herasymyuks/PLFM_RADAR-aeris/9_Firmware/9_2_FPGA/reconstructed/PIN_MAP_FROM_SCHEMATIC.md

# FPGA pin map derived from schematic (XC7A50T-2FTG256I, part U42)

Source: `4_Schematics and Boards Layout/4_6_Schematics/MainBoard/RADAR_Main_Board.sch`. Generated by `tools/gen_xdc_from_schematic.py`. Confidence refers to the net-name-to-RTL-port interpretation only; the pad is exact.

| RTL port | Schematic net | Pad | FPGA pin name | Confidence | Notes |
|---|---|---|---|---|---|
| `clk_100m` | `FPGA_SYS_CLOCK` | `E12` | `IO_L13P_T2_MRCC_15` | MEDIUM | MRCC clock-capable pin; 100 MHz supported by firmware AD9523 OUT6 'FPGA_SYSTEM_CLOCK' /36 (main.cpp:995-996), not by schematic alone; bank 15 VCCO=+3V3_FPGA |
| `clk_120m_dac` | `FPGA_DAC_CLOCK` | `C13` | `IO_L12N_T1_MRCC_15` | MEDIUM | MRCC clock-input pin; 120 MHz supported by firmware AD9523 OUT11 'FPGA_DAC' /30 (main.cpp:1025-1026). RTL output dac_clk has NO board pin (DAC clocked by AD9523 OUT10) — designer to confirm; bank 15 VCCO=+3V3_FPGA |
| `adc_dco_p` | `ADC_DCO_P` | `N14` | `IO_L12P_T1_MRCC_14` | HIGH | bank 14 VCCO=+3V3_FPGA: LVDS_25 input with DIFF_TERM requires 2.5 V VCCO (UG471) — REQUIRES VERIFICATION |
| `adc_dco_n` | `ADC_DCO_N` | `P14` | `IO_L12N_T1_MRCC_14` | HIGH | bank 14 VCCO=+3V3_FPGA: LVDS_25 input with DIFF_TERM requires 2.5 V VCCO (UG471) — REQUIRES VERIFICATION |
| `adc_pwdn` | `ADC_PWRD` | `T5` | `IO_L23N_T3_A02_D18_14` | HIGH | bank 14 VCCO=+3V3_FPGA |
| `dac_sleep` | `DAC_SLEEP` | `A15` | `IO_L9N_T1_DQS_AD3N_15` | HIGH | bank 15 VCCO=+3V3_FPGA |
| `tx_mixer_en` | `MIX_TX_EN` | `C11` | `IO_L11P_T1_SRCC_15` | HIGH | bank 15 VCCO=+3V3_FPGA |
| `rx_mixer_en` | `MIX_RX_EN` | `D11` | `IO_L14N_T2_SRCC_15` | HIGH | bank 15 VCCO=+3V3_FPGA |
| `fpga_rf_switch` | `M3S_VCTRL` | `G15` | `IO_L24N_T3_RS0_15` | MEDIUM | M3SWA2-34DR+ RF switch control net; bank 15 VCCO=+3V3_FPGA |
| `stm32_new_chirp` | `DIG_0` | `F13` | `IO_L16N_T2_A27_15` | MEDIUM | STM32 PD8 toggled as 'New chirp signal to FPGA' (main.cpp:448,459); schematic net DIG_0 = U2.PD8; bank 15 VCCO=+3V3_FPGA |
| `stm32_new_elevation` | `DIG_1` | `E16` | `IO_L17P_T2_A26_15` | MEDIUM | STM32 PD9 toggled 'Notify FPGA of elevation change' (main.cpp:484); DIG_1 = U2.PD9; bank 15 VCCO=+3V3_FPGA |
| `stm32_new_azimuth` | `DIG_2` | `D16` | `IO_L17N_T2_A25_15` | MEDIUM | STM32 PD10 toggled 'new azimuth' (main.cpp:514); DIG_2 = U2.PD10; bank 15 VCCO=+3V3_FPGA |
| `stm32_mixers_enable` | `DIG_3` | `F15` | `IO_L18P_T2_A24_15` | MEDIUM | STM32 PD11 'enable Mixers' (main.cpp:1483,1667,1714); DIG_3 = U2.PD11; bank 15 VCCO=+3V3_FPGA |
| `reset_n` | `DIG_4` | `E15` | `IO_L18N_T2_A23_15` | MEDIUM | STM32 PD12 pulsed low 10 ms as 'RESET FPGA' (main.cpp:1659-1662), active-low matches RTL reset_n; DIG_4 = U2.PD12; bank 15 VCCO=+3V3_FPGA |
| `stm32_sclk_3v3` | `STM32_SCLK1` | `J16` | `IO_L23N_T3_FWE_B_15` | HIGH | shared with STM32 PA5 (SPI1_SCK); bank 15 VCCO=+3V3_FPGA |
| `stm32_mosi_3v3` | `STM32_MOSI1` | `H13` | `IO_L20N_T3_A19_15` | HIGH | shared with STM32 PA7 (SPI1_MOSI); bank 15 VCCO=+3V3_FPGA |
| `stm32_miso_3v3` | `STM32_MISO1` | `G14` | `IO_L21P_T3_DQS_15` | HIGH | shared with STM32 PA6 (SPI1_MISO); bank 15 VCCO=+3V3_FPGA |
| `stm32_sclk_1v8` | `STM32_SCLK_1V8` | `P5` | `IO_L10P_T1_34` | HIGH | bank 34 VCCO=+1V8_FPGA |
| `stm32_mosi_1v8` | `STM32_MOSI_1V8` | `M1` | `IO_L2N_T0_34` | HIGH | bank 34 VCCO=+1V8_FPGA |
| `stm32_miso_1v8` | `STM32_MISO_1V8` | `N3` | `IO_L3P_T0_DQS_34` | HIGH | bank 34 VCCO=+1V8_FPGA |
| `adc_d_p[0]` | `ADC_D0_P` | `P15` | `IO_L8P_T1_D11_14` | HIGH | bank 14 VCCO=+3V3_FPGA: LVDS_25 input with DIFF_TERM requires 2.5 V VCCO (UG471) — REQUIRES VERIFICATION |
| `adc_d_p[1]` | `ADC_D1_P` | `R15` | `IO_L9P_T1_DQS_14` | HIGH | bank 14 VCCO=+3V3_FPGA: LVDS_25 input with DIFF_TERM requires 2.5 V VCCO (UG471) — REQUIRES VERIFICATION |
| `adc_d_p[2]` | `ADC_D2_P` | `T14` | `IO_L10P_T1_D14_14` | HIGH | bank 14 VCCO=+3V3_FPGA: LVDS_25 input with DIFF_TERM requires 2.5 V VCCO (UG471) — REQUIRES VERIFICATION |
| `adc_d_p[3]` | `ADC_D3_P` | `R13` | `IO_L16P_T2_CSI_B_14` | HIGH | bank 14 VCCO=+3V3_FPGA: LVDS_25 input with DIFF_TERM requires 2.5 V VCCO (UG471) — REQUIRES VERIFICATION |
| `adc_d_p[4]` | `ADC_D4_P` | `R10` | `IO_L17P_T2_A14_D30_14` | HIGH | bank 14 VCCO=+3V3_FPGA: LVDS_25 input with DIFF_TERM requires 2.5 V VCCO (UG471) — REQUIRES VERIFICATION |
| `adc_d_p[5]` | `ADC_D5_P` | `T9` | `IO_L22P_T3_A05_D21_14` | HIGH | bank 14 VCCO=+3V3_FPGA: LVDS_25 input with DIFF_TERM requires 2.5 V VCCO (UG471) — REQUIRES VERIFICATION |
| `adc_d_p[6]` | `ADC_D6_P` | `T7` | `IO_L21P_T3_DQS_14` | HIGH | bank 14 VCCO=+3V3_FPGA: LVDS_25 input with DIFF_TERM requires 2.5 V VCCO (UG471) — REQUIRES VERIFICATION |
| `adc_d_p[7]` | `ADC_D7_P` | `R6` | `IO_L24P_T3_A01_D17_14` | HIGH | bank 14 VCCO=+3V3_FPGA: LVDS_25 input with DIFF_TERM requires 2.5 V VCCO (UG471) — REQUIRES VERIFICATION |
| `adc_d_n[0]` | `ADC_D0_N` | `P16` | `IO_L8N_T1_D12_14` | HIGH | bank 14 VCCO=+3V3_FPGA: LVDS_25 input with DIFF_TERM requires 2.5 V VCCO (UG471) — REQUIRES VERIFICATION |
| `adc_d_n[1]` | `ADC_D1_N` | `R16` | `IO_L9N_T1_DQS_D13_14` | HIGH | bank 14 VCCO=+3V3_FPGA: LVDS_25 input with DIFF_TERM requires 2.5 V VCCO (UG471) — REQUIRES VERIFICATION |
| `adc_d_n[2]` | `ADC_D2_N` | `T15` | `IO_L10N_T1_D15_14` | HIGH | bank 14 VCCO=+3V3_FPGA: LVDS_25 input with DIFF_TERM requires 2.5 V VCCO (UG471) — REQUIRES VERIFICATION |
| `adc_d_n[3]` | `ADC_D3_N` | `T13` | `IO_L16N_T2_A15_D31_14` | HIGH | bank 14 VCCO=+3V3_FPGA: LVDS_25 input with DIFF_TERM requires 2.5 V VCCO (UG471) — REQUIRES VERIFICATION |
| `adc_d_n[4]` | `ADC_D4_N` | `R11` | `IO_L17N_T2_A13_D29_14` | HIGH | bank 14 VCCO=+3V3_FPGA: LVDS_25 input with DIFF_TERM requires 2.5 V VCCO (UG471) — REQUIRES VERIFICATION |
| `adc_d_n[5]` | `ADC_D5_N` | `T10` | `IO_L22N_T3_A04_D20_14` | HIGH | bank 14 VCCO=+3V3_FPGA: LVDS_25 input with DIFF_TERM requires 2.5 V VCCO (UG471) — REQUIRES VERIFICATION |
| `adc_d_n[6]` | `ADC_D6_N` | `T8` | `IO_L21N_T3_DQS_A06_D22_14` | HIGH | bank 14 VCCO=+3V3_FPGA: LVDS_25 input with DIFF_TERM requires 2.5 V VCCO (UG471) — REQUIRES VERIFICATION |
| `adc_d_n[7]` | `ADC_D7_N` | `R7` | `IO_L24N_T3_A00_D16_14` | HIGH | bank 14 VCCO=+3V3_FPGA: LVDS_25 input with DIFF_TERM requires 2.5 V VCCO (UG471) — REQUIRES VERIFICATION |
| `dac_data[0]` | `DAC_0` | `A14` | `IO_L7N_T1_AD2N_15` | HIGH | bank 15 VCCO=+3V3_FPGA |
| `dac_data[1]` | `DAC_1` | `A13` | `IO_L7P_T1_AD2P_15` | HIGH | bank 15 VCCO=+3V3_FPGA |
| `dac_data[2]` | `DAC_2` | `A12` | `IO_L5N_T0_AD9N_15` | HIGH | bank 15 VCCO=+3V3_FPGA |
| `dac_data[3]` | `DAC_3` | `B11` | `IO_L4N_T0_15` | HIGH | bank 15 VCCO=+3V3_FPGA |
| `dac_data[4]` | `DAC_4` | `B10` | `IO_L4P_T0_15` | HIGH | bank 15 VCCO=+3V3_FPGA |
| `dac_data[5]` | `DAC_5` | `A10` | `IO_L3N_T0_DQS_AD1N_15` | HIGH | bank 15 VCCO=+3V3_FPGA |
| `dac_data[6]` | `DAC_6` | `A9` | `IO_L2N_T0_AD8N_15` | HIGH | bank 15 VCCO=+3V3_FPGA |
| `dac_data[7]` | `DAC_7` | `A8` | `IO_L2P_T0_AD8P_15` | HIGH | bank 15 VCCO=+3V3_FPGA |
| `stm32_cs_adar1_3v3` | `ADAR_1_CS_3V3` | `F14` | `IO_L21N_T3_DQS_A18_15` | HIGH | shared with STM32 PA0; bank 15 VCCO=+3V3_FPGA |
| `stm32_cs_adar2_3v3` | `ADAR_2_CS_3V3` | `H16` | `IO_L22P_T3_A17_15` | HIGH | shared with STM32 PA1; bank 15 VCCO=+3V3_FPGA |
| `stm32_cs_adar3_3v3` | `ADAR_3_CS_3V3` | `G16` | `IO_L22N_T3_A16_15` | HIGH | shared with STM32 PA2; bank 15 VCCO=+3V3_FPGA |
| `stm32_cs_adar4_3v3` | `ADAR_4_CS_3V3` | `J15` | `IO_L23P_T3_FOE_B_15` | HIGH | shared with STM32 PA3; bank 15 VCCO=+3V3_FPGA |
| `stm32_cs_adar1_1v8` | `ADAR_1_CS_1V8` | `L5` | `IO_0_34` | HIGH | bank 34 VCCO=+1V8_FPGA |
| `stm32_cs_adar2_1v8` | `ADAR_2_CS_1V8` | `L4` | `IO_L1P_T0_34` | HIGH | bank 34 VCCO=+1V8_FPGA |
| `stm32_cs_adar3_1v8` | `ADAR_3_CS_1V8` | `M4` | `IO_L1N_T0_34` | HIGH | bank 34 VCCO=+1V8_FPGA |
| `stm32_cs_adar4_1v8` | `ADAR_4_CS_1V8` | `M2` | `IO_L2P_T0_34` | HIGH | bank 34 VCCO=+1V8_FPGA |
| `adar_tx_load_1` | `ADAR_TX_LOAD_1` | `P3` | `IO_L5N_T0_34` | HIGH | bank 34 VCCO=+1V8_FPGA |
| `adar_tx_load_2` | `ADAR_TX_LOAD_2` | `T4` | `IO_L9P_T1_DQS_34` | HIGH | bank 34 VCCO=+1V8_FPGA |
| `adar_tx_load_3` | `ADAR_TX_LOAD_3` | `R3` | `IO_L8P_T1_34` | HIGH | bank 34 VCCO=+1V8_FPGA |
| `adar_tx_load_4` | `ADAR_TX_LOAD_4` | `R2` | `IO_L7P_T1_34` | HIGH | bank 34 VCCO=+1V8_FPGA |
| `adar_rx_load_1` | `ADAR_RX_LOAD_1` | `M5` | `IO_L6P_T0_34` | HIGH | bank 34 VCCO=+1V8_FPGA |
| `adar_rx_load_2` | `ADAR_RX_LOAD_2` | `T2` | `IO_L8N_T1_34` | HIGH | bank 34 VCCO=+1V8_FPGA |
| `adar_rx_load_3` | `ADAR_RX_LOAD_3` | `R1` | `IO_L7N_T1_34` | HIGH | bank 34 VCCO=+1V8_FPGA |
| `adar_rx_load_4` | `ADAR_RX_LOAD_4` | `N4` | `IO_L6N_T0_VREF_34` | HIGH | bank 34 VCCO=+1V8_FPGA |
| `adar_tr_1` | `ADAR_TR_1` | `N2` | `IO_L3N_T0_DQS_34` | HIGH | bank 34 VCCO=+1V8_FPGA |
| `adar_tr_2` | `ADAR_TR_2` | `N1` | `IO_L4P_T0_34` | HIGH | bank 34 VCCO=+1V8_FPGA |
| `adar_tr_3` | `ADAR_TR_3` | `P1` | `IO_L4N_T0_34` | HIGH | bank 34 VCCO=+1V8_FPGA |
| `adar_tr_4` | `ADAR_TR_4` | `P4` | `IO_L5P_T0_34` | HIGH | bank 34 VCCO=+1V8_FPGA |

## Unresolved RTL ports

| Ports | Reason |
|---|---|
| `dac_clk` | RTL drives a DAC clock output, but the board clocks the AD9708 from AD9523 OUT10 (main.cpp:1019-1020); no FPGA net — **UNRESOLVED — REQUIRES BOARD DESIGN VERIFICATION** |
| `ft601_clk_in` | FT601Q-B-T (U6) is placed in the schematic but has 0 of 77 pins connected; its decoupling parts are parked outside the board outline — **UNRESOLVED — REQUIRES BOARD DESIGN VERIFICATION** |
| `ft601_data[*], ft601_be[*], ft601_txe_n, ft601_rxf_n, ft601_txe, ft601_rxf, ft601_wr_n, ft601_rd_n, ft601_oe_n, ft601_siwu_n, ft601_srb[*], ft601_swb[*], ft601_clk_out` | FT601 not wired on Main Board — **UNRESOLVED — REQUIRES BOARD DESIGN VERIFICATION** |
| `(DIG_5..DIG_7)` | schematic nets DIG_5/6/7 (STM32 PD13/14/15 configured as INPUTS in main.cpp:2313-2317) reach FPGA H11/G12/H12 but no RTL port uses them — **UNRESOLVED — REQUIRES BOARD DESIGN VERIFICATION** |
| `current_elevation[*], current_azimuth[*], current_chirp[*], new_chirp_frame` | no status outputs on the schematic — **UNRESOLVED — REQUIRES BOARD DESIGN VERIFICATION** |
| `dbg_doppler_data[*], dbg_doppler_valid, dbg_doppler_bin[*], dbg_range_bin[*], system_status[*]` | debug outputs; no schematic nets (internal-only in a real build; remove from top or leave unconstrained with -quiet) — **UNRESOLVED — REQUIRES BOARD DESIGN VERIFICATION** |
