herasymyuks/PLFM_RADAR-aeris/engineering/ELECTRICAL/connection_diagrams/FREQUENCY_SYNTHESIZER_connection_report.md

# FREQUENCY_SYNTHESIZER — Component-to-net connection report

Project AERIS-10 · Drawing ID ELEC-CON-FREQUENCY_SYNTHESIZER · Rev A · 2026-10-09 · Status: SOURCE-DERIVED  
Source: `4_Schematics and Boards Layout/4_6_Schematics/FrequencySynthesizerBoard/Clocks_Freq_Synth_board.sch` (EAGLE 9.6.2), `4_Schematics and Boards Layout/4_6_Schematics/FrequencySynthesizerBoard/Clocks_Freq_Synth_board.brd`; generated by `tools/gen_schematic_reports.py`.

## 1. Summary

| Item | Count |
|---|---|
| Sheets | 1 |
| Parts (all) / physical | 318 / 184 |
| Nets | 139 |
| Pin connections | 752 |
| Single-pin nets | 5 |
| Unconnected pins on placed gates | 34 |
| Physical parts without value | 47 |
| Board airwires (unrouted connections, layer 19) | 0 |
| Missing symbol/footprint records | 0 |

## 2. Connector pin-outs

Parts whose package name or prefix identifies a connector (header, SMA, terminal block, USB).

### J1 — 142-0731-211 (1420731211)

| Pad | Pin name | Net | Sheet |
|---|---|---|---|
| 1 | 1 | `N$35` | 1 |
| 2 | 2 | `GND` | 1 |
| 3 | 3 | `GND` | 1 |
| 4 | 4 | `GND` | 1 |
| 5 | 5 | `GND` | 1 |

### J2 — 142-0731-211 (1420731211)

| Pad | Pin name | Net | Sheet |
|---|---|---|---|
| 1 | 1 | `N$51` | 1 |
| 2 | 2 | `GND` | 1 |
| 3 | 3 | `GND` | 1 |
| 4 | 4 | `GND` | 1 |
| 5 | 5 | `GND` | 1 |

### J3 — CJT-T-P-HH-ST-TH1 (CONN_CJT-T-P-XX-ST-TH1_SAI)

| Pad | Pin name | Net | Sheet |
|---|---|---|---|
| 1 | 1 | `AD9523_OUT4_P` | 1 |
| 2 | 2 | `AD9523_OUT4_N` | 1 |

### J4 — CJT-T-P-HH-ST-TH1 (CONN_CJT-T-P-XX-ST-TH1_SAI)

| Pad | Pin name | Net | Sheet |
|---|---|---|---|
| 1 | 1 | `AD9523_OUT5_P` | 1 |
| 2 | 2 | `AD9523_OUT5_N` | 1 |

### J5 — 142-0731-211 (1420731211)

| Pad | Pin name | Net | Sheet |
|---|---|---|---|
| 1 | 1 | `N$64` | 1 |
| 2 | 2 | `GND` | 1 |
| 3 | 3 | `GND` | 1 |
| 4 | 4 | `GND` | 1 |
| 5 | 5 | `GND` | 1 |

### J6 — 142-0731-211 (1420731211)

| Pad | Pin name | Net | Sheet |
|---|---|---|---|
| 1 | 1 | `N$67` | 1 |
| 2 | 2 | `GND` | 1 |
| 3 | 3 | `GND` | 1 |
| 4 | 4 | `GND` | 1 |
| 5 | 5 | `GND` | 1 |

### J7 — 142-0731-211 (1420731211)

| Pad | Pin name | Net | Sheet |
|---|---|---|---|
| 1 | 1 | `AD9523_OUT6+` | 1 |
| 2 | 2 | `GND` | 1 |
| 3 | 3 | `GND` | 1 |
| 4 | 4 | `GND` | 1 |
| 5 | 5 | `GND` | 1 |

### J8 — 142-0731-211 (1420731211)

| Pad | Pin name | Net | Sheet |
|---|---|---|---|
| 1 | 1 | `AD9523_OUT7+` | 1 |
| 2 | 2 | `GND` | 1 |
| 3 | 3 | `GND` | 1 |
| 4 | 4 | `GND` | 1 |
| 5 | 5 | `GND` | 1 |

### J9 — 142-0731-211 (1420731211)

| Pad | Pin name | Net | Sheet |
|---|---|---|---|
| 1 | 1 | `N$37` | 1 |
| 2 | 2 | `GND` | 1 |
| 3 | 3 | `GND` | 1 |
| 4 | 4 | `GND` | 1 |
| 5 | 5 | `GND` | 1 |

### J10 — 142-0731-211 (1420731211)

| Pad | Pin name | Net | Sheet |
|---|---|---|---|
| 1 | 1 | `N$30` | 1 |
| 2 | 2 | `GND` | 1 |
| 3 | 3 | `GND` | 1 |
| 4 | 4 | `GND` | 1 |
| 5 | 5 | `GND` | 1 |

### J11 — 142-0731-211 (1420731211)

| Pad | Pin name | Net | Sheet |
|---|---|---|---|
| 1 | 1 | `N$55` | 1 |
| 2 | 2 | `GND` | 1 |
| 3 | 3 | `GND` | 1 |
| 4 | 4 | `GND` | 1 |
| 5 | 5 | `GND` | 1 |

### J12 — 142-0731-211 (1420731211)

| Pad | Pin name | Net | Sheet |
|---|---|---|---|
| 1 | 1 | `N$59` | 1 |
| 2 | 2 | `GND` | 1 |
| 3 | 3 | `GND` | 1 |
| 4 | 4 | `GND` | 1 |
| 5 | 5 | `GND` | 1 |

### J13 — 142-0731-211 (1420731211)

| Pad | Pin name | Net | Sheet |
|---|---|---|---|
| 1 | 1 | `N$61` | 1 |
| 2 | 2 | `GND` | 1 |
| 3 | 3 | `GND` | 1 |
| 4 | 4 | `GND` | 1 |
| 5 | 5 | `GND` | 1 |

### JP1 — PINHD-2X6 (2X06)

| Pad | Pin name | Net | Sheet |
|---|---|---|---|
| 1 | 1 | `AD9523_PD` | 1 |
| 2 | 2 | `AD9523_REF_SEL` | 1 |
| 3 | 3 | `AD9523_SYNC` | 1 |
| 4 | 4 | `AD9523_RESET` | 1 |
| 5 | 5 | `AD9523_CS` | 1 |
| 6 | 6 | `AD9523_SCLK` | 1 |
| 7 | 7 | `AD9523_SDIO` | 1 |
| 8 | 8 | `AD9523_SDO` | 1 |
| 9 | 9 | `AD9523_STATUS0` | 1 |
| 10 | 10 | `AD9523_STATUS1` | 1 |
| 11 | 11 | `AD9523_EEPROM_SEL` | 1 |
| 12 | 12 | `GND` | 1 |

### JP2 — PINHD-2X7 (2X07)

| Pad | Pin name | Net | Sheet |
|---|---|---|---|
| 1 | 1 | `ADF4382_SDO` | 1 |
| 2 | 2 | `ADF4382_SCLK` | 1 |
| 3 | 3 | `ADF4382_SDIO` | 1 |
| 4 | 4 | `ADF4382_TX_CS` | 1 |
| 5 | 5 | `ADF4382_TX_CE` | 1 |
| 6 | 6 | `ADF4382_TX_DELSTR` | 1 |
| 7 | 7 | `ADF4382_TX_DELADJ` | 1 |
| 8 | 8 | `ADF4382_TX_LKDET` | 1 |
| 9 | 9 | `ADF4382_RX_CS` | 1 |
| 10 | 10 | `ADF4382_RX_CE` | 1 |
| 11 | 11 | `ADF4382_RX_DELSTR` | 1 |
| 12 | 12 | `ADF4382_RX_DELADJ` | 1 |
| 13 | 13 | `ADF4382_RX_LKDET` | 1 |
| 14 | 14 | `GND` | 1 |

### X4 — ECOC-2522-100.000-3HC (SMD5_ECOC-2522_25P4X22_ECS)

| Pad | Pin name | Net | Sheet |
|---|---|---|---|
| 1 | VOLTAGE_CONTROL | `N$1` | 1 |
| 3 | SUPPLY_VOLTAGE | `+3V3_XO` | 1 |
| 4 | OUTPUT | `10MHZ_OUT` | 1 |
| 5 | GROUND | `GND` | 1 |

### X5 — CVHD-950-50.000 (SMD4_CVHD-950_CRX)

| Pad | Pin name | Net | Sheet |
|---|---|---|---|
| 2 | GND | `GND` | 1 |
| 3 | OUT | `100MHZ_OUT` | 1 |
| 4 | VDD | `+3V3_XO` | 1 |

### X6 — CVHD-950-50.000 (SMD4_CVHD-950_CRX)

| Pad | Pin name | Net | Sheet |
|---|---|---|---|
| 1 | VOLT_CONTROL | `N$2` | 1 |
| 2 | GND | `GND` | 1 |
| 3 | OUT | `VCXO_OUT` | 1 |
| 4 | VDD | `+3V3_XO` | 1 |

### X10 — 22-23-2021 (22-23-2021)

| Pad | Pin name | Net | Sheet |
|---|---|---|---|
| 1 | S | `N$69` | 1 |
| 2 | S | `GND` | 1 |

### X11 — 22-23-2021 (22-23-2021)

| Pad | Pin name | Net | Sheet |
|---|---|---|---|
| 1 | S | `N$71` | 1 |
| 2 | S | `GND` | 1 |

### X12 — 22-23-2021 (22-23-2021)

| Pad | Pin name | Net | Sheet |
|---|---|---|---|
| 1 | S | `N$73` | 1 |
| 2 | S | `GND` | 1 |

### X13 — 22-23-2021 (22-23-2021)

| Pad | Pin name | Net | Sheet |
|---|---|---|---|
| 1 | S | `N$75` | 1 |
| 2 | S | `GND` | 1 |

### X14 — 22-23-2021 (22-23-2021)

| Pad | Pin name | Net | Sheet |
|---|---|---|---|
| 1 | S | `N$77` | 1 |
| 2 | S | `GND` | 1 |

### X15 — 22-23-2021 (22-23-2021)

| Pad | Pin name | Net | Sheet |
|---|---|---|---|
| 1 | S | `+5V0_LO` | 1 |
| 2 | S | `GND` | 1 |

## 3. Net fan-out (nets with ≥ 8 connections)

| Net | Connections | Class |
|---|---|---|
| `GND` | 333 | 0 |
| `+3V3_LO_1` | 30 | 0 |
| `+3V3_LO_2` | 30 | 0 |
| `+3V3_CLOCK` | 22 | 0 |
| `+1V8_CLOCK` | 16 | 0 |

## 4. Component-to-net table

Full machine-readable form: `netlists/FREQUENCY_SYNTHESIZER_netlist_by_part.csv`. Physical parts only; pads shown when the device defines a package connection.

| Part | Value | Device / package | Connections (pad:net) |
|---|---|---|---|
| C1 | 10pF | C-EUC0201 / C0201 | 1:`+3V3_LO_2`, 2:`GND` |
| C2 | 0.33µF | C-EUC0201 / C0201 | 1:`N$2`, 2:`GND` |
| C3 | 0.47µf | C-EUC0201 / C0201 | 1:`GND`, 2:`N$3` |
| C4 |  | C-EUC0201 / C0201 | 1:`GND`, 2:`N$5` |
| C5 |  | C-EUC0201 / C0201 | 1:`GND`, 2:`N$6` |
| C6 | 0.33µF | C-EUC0201 / C0201 | 1:`GND`, 2:`N$4` |
| C7 |  | C-EUC0201 / C0201 | 1:`GND`, 2:`N$7` |
| C8 | 1000pF | C-EUC0201 / C0201 | 1:`N$9`, 2:`N$8` |
| C9 | 0.47µF | C-EUC0201 / C0201 | 1:`GND`, 2:`N$10` |
| C10 | 0.47µF | C-EUC0201 / C0201 | 1:`GND`, 2:`N$11` |
| C11 | 1µF | C-EUC0201 / C0201 | 1:`N$15`, 2:`AD9523_OUT0_N` |
| C12 | 1µF | C-EUC0201 / C0201 | 1:`N$16`, 2:`AD9523_OUT0_P` |
| C13 | 1µF | C-EUC0201 / C0201 | 1:`ADF4382_TX_SYNC_N`, 2:`AD9523_OUT9_N` |
| C14 | 1µF | C-EUC0201 / C0201 | 1:`ADF4382_TX_SYNC_P`, 2:`AD9523_OUT9_P` |
| C15 | 10nF | C-EUC0402 / C0402 | 1:`N$63`, 2:`AD9523_OUT6+` |
| C16 | 0.1µF | C-EUC0201 / C0201 | 1:`+3V3_CLOCK`, 2:`GND` |
| C17 | 10nF | C-EUC0402 / C0402 | 1:`N$65`, 2:`N$64` |
| C18 | 0.1µF | C-EUC0201 / C0201 | 1:`+3V3_CLOCK`, 2:`GND` |
| C19 | 10nF | C-EUC0402 / C0402 | 1:`N$68`, 2:`N$67` |
| C20 | 0.1µF | C-EUC0201 / C0201 | 1:`+3V3_CLOCK`, 2:`GND` |
| C21 | 22µF | C-EUC1210 / C1210 | 1:`N$69`, 2:`GND` |
| C22 | 0.1µF | C-EUC0201 / C0201 | 1:`+3V3_CLOCK`, 2:`GND` |
| C23 | 10µF | C-EUC1210 / C1210 | 1:`+3V3_XO`, 2:`GND` |
| C24 | 0.1µF | C-EUC0201 / C0201 | 1:`+3V3_CLOCK`, 2:`GND` |
| C25 | 22µF | C-EUC1210 / C1210 | 1:`N$71`, 2:`GND` |
| C26 | 0.1µF | C-EUC0201 / C0201 | 1:`+3V3_CLOCK`, 2:`GND` |
| C27 | 10µF | C-EUC1210 / C1210 | 1:`+3V3_CLOCK`, 2:`GND` |
| C28 | 0.1µF | C-EUC0201 / C0201 | 1:`+3V3_CLOCK`, 2:`GND` |
| C29 | 22µF | C-EUC1210 / C1210 | 1:`N$73`, 2:`GND` |
| C30 | 0.1µF | C-EUC0201 / C0201 | 1:`+3V3_CLOCK`, 2:`GND` |
| C31 | 10µF | C-EUC1210 / C1210 | 1:`+1V8_CLOCK`, 2:`GND` |
| C32 | 0.1µF | C-EUC0201 / C0201 | 1:`+3V3_CLOCK`, 2:`GND` |
| C33 | 22µF | C-EUC1210 / C1210 | 1:`N$75`, 2:`GND` |
| C34 | 0.1µF | C-EUC0201 / C0201 | 1:`+3V3_CLOCK`, 2:`GND` |
| C35 | 0.1µF | C-EUC0201 / C0201 | 1:`+1V8_CLOCK`, 2:`GND` |
| C36 | 0.1µF | C-EUC0201 / C0201 | 1:`+1V8_CLOCK`, 2:`GND` |
| C37 | 0.1µF | C-EUC0201 / C0201 | 1:`+1V8_CLOCK`, 2:`GND` |
| C38 | 4.7µF | C-EUC0201 / C0201 | 1:`+3V3_LO_1`, 2:`GND` |
| C39 | 4.7µF | C-EUC0201 / C0201 | 1:`+3V3_LO_1`, 2:`GND` |
| C40 | 4.7µF | C-EUC0201 / C0201 | 1:`+3V3_LO_1`, 2:`GND` |
| C41 | 0.1µF | C-EUC0201 / C0201 | 1:`+1V8_CLOCK`, 2:`GND` |
| C42 | 0.1µF | C-EUC0201 / C0201 | 1:`+1V8_CLOCK`, 2:`GND` |
| C43 | 0.1µF | C-EUC0201 / C0201 | 1:`+1V8_CLOCK`, 2:`GND` |
| C44 | 0.1µF | C-EUC0201 / C0201 | 1:`+1V8_CLOCK`, 2:`GND` |
| C45 | 10µF | C-EUC1210 / C1210 | 1:`+3V3_LO_1`, 2:`GND` |
| C46 | 22µF | C-EUC1210 / C1210 | 1:`N$77`, 2:`GND` |
| C47 | 10µF | C-EUC1210 / C1210 | 1:`+3V3_LO_2`, 2:`GND` |
| C48 | 4.7µF | C-EUC0201 / C0201 | 1:`+3V3_LO_1`, 2:`GND` |
| C49 | 4.7µF | C-EUC0201 / C0201 | 1:`+3V3_LO_1`, 2:`GND` |
| C50 | 4.7µF | C-EUC0201 / C0201 | 1:`+3V3_LO_1`, 2:`GND` |
| C51 | 22µF | C-EUC1210 / C1210 | 1:`+5V0_LO`, 2:`GND` |
| C55 | 4.7µF | C-EUC0201 / C0201 | 1:`+3V3_LO_2`, 2:`GND` |
| C56 | 4.7µF | C-EUC0201 / C0201 | 1:`+3V3_LO_2`, 2:`GND` |
| C57 | 4.7µF | C-EUC0201 / C0201 | 1:`+3V3_LO_2`, 2:`GND` |
| C58 | 4.7µF | C-EUC0201 / C0201 | 1:`+3V3_LO_2`, 2:`GND` |
| C59 | 1µF | C-EUC0201 / C0201 | 1:`GND`, 2:`N$20` |
| C60 | 31pF | C-EUC0201 / C0201 | 1:`N$24`, 2:`GND` |
| C61 | 10nF | C-EUC0201 / C0201 | 1:`N$17`, 2:`GND` |
| C62 | 10pF | C-EUC0201 / C0201 | 1:`N$26`, 2:`GND` |
| C63 | 10pF | C-EUC0201 / C0201 | 1:`+3V3_LO_2`, 2:`GND` |
| C64 | 0.1µF | C-EUC0201 / C0201 | 1:`TX_RFOUT_1_N`, 2:`N$31` |
| C65 | 0.1µF | C-EUC0201 / C0201 | 1:`TX_RFOUT_1_P`, 2:`N$28` |
| C66 | 0.1µF | C-EUC0201 / C0201 | 1:`TX_RFOUT_2_N`, 2:`N$33` |
| C67 | 0.1µF | C-EUC0201 / C0201 | 1:`TX_RFOUT_2_P`, 2:`N$32` |
| C68 | 1µF | C-EUC0201 / C0201 | 1:`N$38`, 2:`AD9523_OUT1_N` |
| C69 | 1µF | C-EUC0201 / C0201 | 1:`N$39`, 2:`AD9523_OUT1_P` |
| C70 | 1µF | C-EUC0201 / C0201 | 1:`ADF4382_RX_SYNC_N`, 2:`AD9523_OUT8_N` |
| C71 | 1µF | C-EUC0201 / C0201 | 1:`ADF4382_RX_SYNC_P`, 2:`AD9523_OUT8_P` |
| C72 | 4.7µF | C-EUC0201 / C0201 | 1:`+3V3_LO_1`, 2:`GND` |
| C73 | 4.7µF | C-EUC0201 / C0201 | 1:`+3V3_LO_2`, 2:`GND` |
| C74 | 4.7µF | C-EUC0201 / C0201 | 1:`+3V3_LO_2`, 2:`GND` |
| C75 | 4.7µF | C-EUC0201 / C0201 | 1:`+3V3_LO_2`, 2:`GND` |
| C76 | 4.7µF | C-EUC0201 / C0201 | 1:`+3V3_LO_2`, 2:`GND` |
| C77 | 4.7µF | C-EUC0201 / C0201 | 1:`+3V3_LO_1`, 2:`GND` |
| C78 | 4.7µF | C-EUC0201 / C0201 | 1:`+3V3_LO_1`, 2:`GND` |
| C79 | 4.7µF | C-EUC0201 / C0201 | 1:`+3V3_LO_1`, 2:`GND` |
| C80 | 4.7µF | C-EUC0201 / C0201 | 1:`+3V3_LO_1`, 2:`GND` |
| C81 | 4.7µF | C-EUC0201 / C0201 | 1:`+3V3_LO_1`, 2:`GND` |
| C82 | 1µF | C-EUC0201 / C0201 | 1:`GND`, 2:`N$42` |
| C83 | 31pF | C-EUC0201 / C0201 | 1:`N$47`, 2:`GND` |
| C84 | 10nF | C-EUC0201 / C0201 | 1:`N$43`, 2:`GND` |
| C85 | 10pF | C-EUC0201 / C0201 | 1:`N$49`, 2:`GND` |
| C86 | 10pF | C-EUC0201 / C0201 | 1:`+3V3_LO_2`, 2:`GND` |
| C87 | 0.1µF | C-EUC0201 / C0201 | 1:`RX_RFOUT_1_N`, 2:`N$53` |
| C88 | 0.1µF | C-EUC0201 / C0201 | 1:`RX_RFOUT_1_P`, 2:`N$52` |
| C89 | 10pF | C-EUC0201 / C0201 | 1:`+3V3_LO_2`, 2:`GND` |
| C90 | 0.1µF | C-EUC0201 / C0201 | 1:`RX_RFOUT_2_N`, 2:`N$57` |
| C91 | 0.1µF | C-EUC0201 / C0201 | 1:`RX_RFOUT_2_P`, 2:`N$56` |
| C92 | 0.1µf | C-EUC0201 / C0201 | 1:`N$60`, 2:`N$61` |
| D1 | Green | LED-GREEN-0603-WE / LED-0603 | A:`N$36`, C:`GND` |
| D2 | Green | LED-GREEN-0603-WE / LED-0603 | A:`N$50`, C:`GND` |
| FB1 |  | FBMH1608HL601-T / BEADC1608X90N | 1:`+5V0_LO`, 2:`N$41` |
| FB2 |  | FBMH1608HL601-T / BEADC1608X90N | 1:`+5V0_LO`, 2:`N$19` |
| FB3 |  | FBMH1608HL601-T / BEADC1608X90N | 1:`N$20`, 2:`+5V0_LO` |
| FB4 |  | FBMH1608HL601-T / BEADC1608X90N | 1:`N$42`, 2:`+5V0_LO` |
| IC1 |  | AD9523BCPZ / QFN50P1000X1000X100-73N | 1:`N$3`, 2:`+3V3_CLOCK`, 3:`10MHZ_OUT`, 4:`N$5`, 5:`100MHZ_OUT`, 6:`N$6`, 7:`N$4`, 8:`OSC_CTRL`, 9:`VCXO_OUT`, 10:`N$7`, 11:`N$8`, 12:`N$11`, 13:`+3V3_CLOCK`, 14:`N$10`, 15:`AD9523_PD`, 16:`AD9523_REF_SEL`, 17:`AD9523_SYNC`, 18:`+3V3_CLOCK`, 19:`AD9523_RESET`, 20:`N$14`, 21:`N$12`, 22:`N$13`, 23:`AD9523_SDO`, 24:`N$29`, 27:`+3V3_CLOCK`, 30:`+1V8_CLOCK`, 32:`AD9523_OUT11+`, 33:`+3V3_CLOCK`, 35:`AD9523_OUT10+`, 36:`+1V8_CLOCK`, 37:`AD9523_OUT9_N`, 38:`AD9523_OUT9_P`, 39:`+3V3_CLOCK`, 40:`AD9523_OUT8_N`, 41:`AD9523_OUT8_P`, 42:`+1V8_CLOCK`, 44:`AD9523_OUT7+`, 45:`+3V3_CLOCK`, 47:`N$62`, 48:`+1V8_ … (63 pins, see CSV) |
| J1 |  | 142-0731-211 / 1420731211 | 1:`N$35`, 2:`GND`, 3:`GND`, 4:`GND`, 5:`GND` |
| J2 |  | 142-0731-211 / 1420731211 | 1:`N$51`, 2:`GND`, 3:`GND`, 4:`GND`, 5:`GND` |
| J3 |  | CJT-T-P-HH-ST-TH1 / CONN_CJT-T-P-XX-ST-TH1_SAI | 1:`AD9523_OUT4_P`, 2:`AD9523_OUT4_N` |
| J4 |  | CJT-T-P-HH-ST-TH1 / CONN_CJT-T-P-XX-ST-TH1_SAI | 1:`AD9523_OUT5_P`, 2:`AD9523_OUT5_N` |
| J5 |  | 142-0731-211 / 1420731211 | 1:`N$64`, 2:`GND`, 3:`GND`, 4:`GND`, 5:`GND` |
| J6 |  | 142-0731-211 / 1420731211 | 1:`N$67`, 2:`GND`, 3:`GND`, 4:`GND`, 5:`GND` |
| J7 |  | 142-0731-211 / 1420731211 | 1:`AD9523_OUT6+`, 2:`GND`, 3:`GND`, 4:`GND`, 5:`GND` |
| J8 |  | 142-0731-211 / 1420731211 | 1:`AD9523_OUT7+`, 2:`GND`, 3:`GND`, 4:`GND`, 5:`GND` |
| J9 |  | 142-0731-211 / 1420731211 | 1:`N$37`, 2:`GND`, 3:`GND`, 4:`GND`, 5:`GND` |
| J10 |  | 142-0731-211 / 1420731211 | 1:`N$30`, 2:`GND`, 3:`GND`, 4:`GND`, 5:`GND` |
| J11 |  | 142-0731-211 / 1420731211 | 1:`N$55`, 2:`GND`, 3:`GND`, 4:`GND`, 5:`GND` |
| J12 |  | 142-0731-211 / 1420731211 | 1:`N$59`, 2:`GND`, 3:`GND`, 4:`GND`, 5:`GND` |
| J13 |  | 142-0731-211 / 1420731211 | 1:`N$61`, 2:`GND`, 3:`GND`, 4:`GND`, 5:`GND` |
| JP1 |  | PINHD-2X6 / 2X06 | 1:`AD9523_PD`, 2:`AD9523_REF_SEL`, 3:`AD9523_SYNC`, 4:`AD9523_RESET`, 5:`AD9523_CS`, 6:`AD9523_SCLK`, 7:`AD9523_SDIO`, 8:`AD9523_SDO`, 9:`AD9523_STATUS0`, 10:`AD9523_STATUS1`, 11:`AD9523_EEPROM_SEL`, 12:`GND` |
| JP2 |  | PINHD-2X7 / 2X07 | 1:`ADF4382_SDO`, 2:`ADF4382_SCLK`, 3:`ADF4382_SDIO`, 4:`ADF4382_TX_CS`, 5:`ADF4382_TX_CE`, 6:`ADF4382_TX_DELSTR`, 7:`ADF4382_TX_DELADJ`, 8:`ADF4382_TX_LKDET`, 9:`ADF4382_RX_CS`, 10:`ADF4382_RX_CE`, 11:`ADF4382_RX_DELSTR`, 12:`ADF4382_RX_DELADJ`, 13:`ADF4382_RX_LKDET`, 14:`GND` |
| L1 | 1.3nH | L-USL0201 / L0201 | 1:`+3V3_LO_2`, 2:`TX_RFOUT_2_N` |
| L2 | 1.3nH | L-USL0201 / L0201 | 1:`+3V3_LO_2`, 2:`TX_RFOUT_1_N` |
| L3 | 1.3nH | L-USL0201 / L0201 | 1:`TX_RFOUT_1_P`, 2:`+3V3_LO_2` |
| L4 | 1.3nH | L-USL0201 / L0201 | 1:`TX_RFOUT_2_P`, 2:`+3V3_LO_2` |
| L5 | 1.3nH | L-USL0201 / L0201 | 1:`+3V3_LO_2`, 2:`RX_RFOUT_1_N` |
| L6 | 1.3nH | L-USL0201 / L0201 | 1:`RX_RFOUT_1_P`, 2:`+3V3_LO_2` |
| L7 | 1.3nH | L-USL0201 / L0201 | 1:`+3V3_LO_2`, 2:`RX_RFOUT_2_N` |
| L8 | 1.3nH | L-USL0201 / L0201 | 1:`RX_RFOUT_2_P`, 2:`+3V3_LO_2` |
| L9 |  | L-EUL5650M / L5650M | 1:`+3V3_XO`, 2:`N$69` |
| L10 |  | L-EUL5650M / L5650M | 1:`+3V3_CLOCK`, 2:`N$71` |
| L11 |  | L-EUL5650M / L5650M | 1:`+1V8_CLOCK`, 2:`N$73` |
| L12 |  | L-EUL5650M / L5650M | 1:`+3V3_LO_1`, 2:`N$75` |
| L13 |  | L-EUL5650M / L5650M | 1:`+3V3_LO_2`, 2:`N$77` |
| R1 | 100R | R-EU_R0201 / R0201 | 1:`N$39`, 2:`N$38` |
| R2 | 1k | R-EU_R0201 / R0201 | 1:`N$1`, 2:`+3V3_XO` |
| R3 | 1k | R-EU_R0201 / R0201 | 1:`GND`, 2:`N$1` |
| R4 | 1k | R-EU_R0201 / R0201 | 1:`N$2`, 2:`OSC_CTRL` |
| R5 | 0R | R-EU_R0201 / R0201 | 1:`N$9`, 2:`N$10` |
| R6 | 0.65k | R-EU_R0201 / R0201 | 1:`AD9523_SCLK`, 2:`N$12` |
| R7 | 1k | R-EU_R0201 / R0201 | 1:`N$12`, 2:`GND` |
| R8 | 0.65k | R-EU_R0201 / R0201 | 1:`AD9523_SDIO`, 2:`N$13` |
| R9 | 1k | R-EU_R0201 / R0201 | 1:`N$13`, 2:`GND` |
| R10 | 0.65k | R-EU_R0201 / R0201 | 1:`AD9523_CS`, 2:`N$14` |
| R11 | 1k | R-EU_R0201 / R0201 | 1:`N$14`, 2:`GND` |
| R12 | 100R | R-EU_R0201 / R0201 | 1:`N$16`, 2:`N$15` |
| R13 | 100R | R-EU_R0201 / R0201 | 1:`ADF4382_TX_SYNC_P`, 2:`ADF4382_TX_SYNC_N` |
| R14 | 0R | R-EU_R0201 / R0201 | 1:`N$18`, 2:`N$19` |
| R15 | 0R | R-EU_R0201 / R0201 | 1:`N$22`, 2:`N$23` |
| R16 | 931R | R-EU_R0201 / R0201 | 1:`N$24`, 2:`N$23` |
| R17 | 30R | R-EU_R0201 / R0201 | 1:`N$25`, 2:`N$24` |
| R18 | 330R | R-EU_R0201 / R0201 | 1:`N$25`, 2:`N$17` |
| R19 | 0R | R-EU_R0201 / R0201 | 1:`N$21`, 2:`N$25` |
| R20 | 0R | R-EU_R0201 / R0201 | 1:`N$26`, 2:`N$21` |
| R21 | 500R | R-EU_R0201 / R0201 | 1:`N$36`, 2:`ADF4382_TX_LKDET` |
| R22 | 200k | R-EU_R0201 / R0201 | 1:`GND`, 2:`ADF4382_TX_DELADJ` |
| R23 | 200k | R-EU_R0201 / R0201 | 1:`GND`, 2:`ADF4382_TX_DELSTR` |
| R24 | 200k | R-EU_R0201 / R0201 | 1:`ADF4382_TX_CS`, 2:`+3V3_LO_1` |
| R25 | 200k | R-EU_R0201 / R0201 | 1:`ADF4382_TX_CE`, 2:`+3V3_LO_1` |
| R26 | 100R | R-EU_R0201 / R0201 | 1:`ADF4382_RX_SYNC_P`, 2:`ADF4382_RX_SYNC_N` |
| R27 | 0R | R-EU_R0201 / R0201 | 1:`N$40`, 2:`N$41` |
| R28 | 0R | R-EU_R0201 / R0201 | 1:`N$45`, 2:`N$46` |
| R29 | 931R | R-EU_R0201 / R0201 | 1:`N$47`, 2:`N$46` |
| R30 | 30R | R-EU_R0201 / R0201 | 1:`N$48`, 2:`N$47` |
| R31 | 330R | R-EU_R0201 / R0201 | 1:`N$48`, 2:`N$43` |
| R32 | 0R | R-EU_R0201 / R0201 | 1:`N$44`, 2:`N$48` |
| R33 | 0R | R-EU_R0201 / R0201 | 1:`N$49`, 2:`N$44` |
| R34 | 500R | R-EU_R0201 / R0201 | 1:`N$50`, 2:`ADF4382_RX_LKDET` |
| R35 | 200k | R-EU_R0201 / R0201 | 1:`GND`, 2:`ADF4382_RX_DELADJ` |
| R36 | 200k | R-EU_R0201 / R0201 | 1:`GND`, 2:`ADF4382_RX_DELSTR` |
| R37 | 200k | R-EU_R0201 / R0201 | 1:`ADF4382_RX_CS`, 2:`+3V3_LO_1` |
| R38 | 200k | R-EU_R0201 / R0201 | 1:`ADF4382_RX_CE`, 2:`+3V3_LO_1` |
| R39 | 22R | R-EU_R0201 / R0201 | 1:`N$62`, 2:`N$63` |
| R40 | 22R | R-EU_R0201 / R0201 | 1:`AD9523_OUT10+`, 2:`N$65` |
| R41 | 22R | R-EU_R0201 / R0201 | 1:`AD9523_OUT11+`, 2:`N$68` |
| U1 |  | ADF4382ABCCZ / CC-48-10_ADI | 1:`GND`, 2:`GND`, 3:`+3V3_LO_1`, 4:`GND`, 5:`+3V3_LO_2`, 7:`N$22`, 8:`N$19`, 9:`N$18`, 10:`GND`, 11:`+3V3_LO_2`, 12:`GND`, 13:`+3V3_LO_2`, 14:`GND`, 15:`TX_RFOUT_2_N`, 16:`GND`, 17:`TX_RFOUT_2_P`, 18:`GND`, 19:`GND`, 20:`TX_RFOUT_1_N`, 21:`GND`, 22:`TX_RFOUT_1_P`, 23:`GND`, 24:`+3V3_LO_2`, 25:`GND`, 26:`GND`, 27:`ADF4382_TX_LKDET`, 28:`ADF4382_TX_DELADJ`, 29:`ADF4382_TX_DELSTR`, 30:`+3V3_LO_1`, 31:`ADF4382_TX_CE`, 32:`ADF4382_TX_CS`, 33:`ADF4382_SDIO`, 34:`ADF4382_SCLK`, 35:`ADF4382_SDO`, 36:`+3V3_LO_1`, 37:`N$37`, 38:`ADF4382_TX_SYNC_P`, 39:`ADF4382_TX_SYNC_N`, 40:`+3V3_LO_1`, 41:`GND`, 42:`N … (51 pins, see CSV) |
| U2 |  | MTX2-143+ / DQ1225_MNC | 1:`GND`, 2:`N$27`, 3:`GND`, 6:`GND`, 7:`N$28`, 9:`N$31`, 10:`GND`, 13:`GND` |
| U3 |  | MTX2-143+ / DQ1225_MNC | 1:`GND`, 2:`N$34`, 3:`GND`, 6:`GND`, 7:`N$32`, 9:`N$33`, 10:`GND`, 13:`GND` |
| U4 |  | ATS1005-3DB-FD-T05 / SMT_DB-FD-T05_SUS | 1:`N$27`, 2:`N$30`, 3:`GND`, 4:`GND` |
| U5 |  | ATS1005-3DB-FD-T05 / SMT_DB-FD-T05_SUS | 1:`N$34`, 2:`N$35`, 3:`GND`, 4:`GND` |
| U6 |  | ADF4382ABCCZ / CC-48-10_ADI | 1:`GND`, 2:`GND`, 3:`+3V3_LO_1`, 4:`GND`, 5:`+3V3_LO_2`, 7:`N$45`, 8:`N$41`, 9:`N$40`, 10:`GND`, 11:`+3V3_LO_2`, 12:`GND`, 13:`+3V3_LO_2`, 14:`GND`, 15:`RX_RFOUT_2_N`, 16:`GND`, 17:`RX_RFOUT_2_P`, 18:`GND`, 19:`GND`, 20:`RX_RFOUT_1_N`, 21:`GND`, 22:`RX_RFOUT_1_P`, 23:`GND`, 24:`+3V3_LO_2`, 25:`GND`, 26:`GND`, 27:`ADF4382_RX_LKDET`, 28:`ADF4382_RX_DELADJ`, 29:`ADF4382_RX_DELSTR`, 30:`+3V3_LO_1`, 31:`ADF4382_RX_CE`, 32:`ADF4382_RX_CS`, 33:`ADF4382_SDIO`, 34:`ADF4382_SCLK`, 35:`ADF4382_SDO`, 36:`+3V3_LO_1`, 37:`N$51`, 38:`ADF4382_RX_SYNC_P`, 39:`ADF4382_RX_SYNC_N`, 40:`+3V3_LO_1`, 41:`GND`, 42:`N … (51 pins, see CSV) |
| U7 |  | MTX2-143+ / DQ1225_MNC | 1:`GND`, 2:`N$54`, 3:`GND`, 6:`GND`, 7:`N$52`, 9:`N$53`, 10:`GND`, 13:`GND` |
| U8 |  | ATS1005-3DB-FD-T05 / SMT_DB-FD-T05_SUS | 1:`N$54`, 2:`N$55`, 3:`GND`, 4:`GND` |
| U9 |  | MTX2-143+ / DQ1225_MNC | 1:`GND`, 2:`N$58`, 3:`GND`, 6:`GND`, 7:`N$56`, 9:`N$57`, 10:`GND`, 13:`GND` |
| U10 |  | ATS1005-3DB-FD-T05 / SMT_DB-FD-T05_SUS | 1:`N$58`, 2:`N$59`, 3:`GND`, 4:`GND` |
| X4 |  | ECOC-2522-100.000-3HC / SMD5_ECOC-2522_25P4X22_ECS | 1:`N$1`, 3:`+3V3_XO`, 4:`10MHZ_OUT`, 5:`GND` |
| X5 |  | CVHD-950-50.000 / SMD4_CVHD-950_CRX | 2:`GND`, 3:`100MHZ_OUT`, 4:`+3V3_XO` |
| X6 |  | CVHD-950-50.000 / SMD4_CVHD-950_CRX | 1:`N$2`, 2:`GND`, 3:`VCXO_OUT`, 4:`+3V3_XO` |
| X10 |  | 22-23-2021 / 22-23-2021 | 1:`N$69`, 2:`GND` |
| X11 |  | 22-23-2021 / 22-23-2021 | 1:`N$71`, 2:`GND` |
| X12 |  | 22-23-2021 / 22-23-2021 | 1:`N$73`, 2:`GND` |
| X13 |  | 22-23-2021 / 22-23-2021 | 1:`N$75`, 2:`GND` |
| X14 |  | 22-23-2021 / 22-23-2021 | 1:`N$77`, 2:`GND` |
| X15 |  | 22-23-2021 / 22-23-2021 | 1:`+5V0_LO`, 2:`GND` |
