herasymyuks/PLFM_RADAR-aeris/engineering/ELECTRICAL/connection_diagrams/MAIN_BOARD_connection_report.md

# MAIN_BOARD — Component-to-net connection report

Project AERIS-10 · Drawing ID ELEC-CON-MAIN_BOARD · Rev A · 2026-10-09 · Status: SOURCE-DERIVED  
Source: `4_Schematics and Boards Layout/4_6_Schematics/MainBoard/RADAR_Main_Board.sch` (EAGLE 7.4.0), `4_Schematics and Boards Layout/4_6_Schematics/MainBoard/RADAR_Main_Board.brd`; generated by `tools/gen_schematic_reports.py`.

## 1. Summary

| Item | Count |
|---|---|
| Sheets | 4 |
| Parts (all) / physical | 1955 / 776 |
| Nets | 625 |
| Pin connections | 4456 |
| Single-pin nets | 3 |
| Unconnected pins on placed gates | 280 |
| Physical parts without value | 244 |
| Board airwires (unrouted connections, layer 19) | 2390 |
| Missing symbol/footprint records | 0 |

## 2. Connector pin-outs

Parts whose package name or prefix identifies a connector (header, SMA, terminal block, USB).

### J1 — 142-0731-211 (1420731211)

| Pad | Pin name | Net | Sheet |
|---|---|---|---|
| 1 | 1 | `FPGA_SYS_CLOCK` | 2 |
| 2 | 2 | `GND` | 2 |
| 3 | 3 | `GND` | 2 |
| 4 | 4 | `GND` | 2 |
| 5 | 5 | `GND` | 2 |

### J18 — 142-0731-211 (1420731211)

| Pad | Pin name | Net | Sheet |
|---|---|---|---|
| 1 | 1 | `FPGA_DAC_CLOCK` | 2 |
| 2 | 2 | `GND` | 2 |
| 3 | 3 | `GND` | 2 |
| 4 | 4 | `GND` | 2 |
| 5 | 5 | `GND` | 2 |

### J19 — CJT-T-P-HH-ST-TH1 (CJTTPHHSTTH1)

| Pad | Pin name | Net | Sheet |
|---|---|---|---|
| 1 | 1 | `FPGA_ADC_CLOCK_P` | 2 |
| 2 | 2 | `FPGA_ADC_CLOCK_N` | 2 |
| MH1 | MH1 | `GND` | 2 |
| MH2 | MH2 | `GND` | 2 |
| MH3 | MH3 | `GND` | 2 |
| MH4 | MH4 | `GND` | 2 |

### J20 — 142-0731-211 (1420731211)

| Pad | Pin name | Net | Sheet |
|---|---|---|---|
| 1 | 1 | `DAC_CLOCK` | 3 |
| 2 | 2 | `GND` | 3 |
| 3 | 3 | `GND` | 3 |
| 4 | 4 | `GND` | 3 |
| 5 | 5 | `GND` | 3 |

### J21 — CJT-T-P-HH-ST-TH1 (CJTTPHHSTTH1)

| Pad | Pin name | Net | Sheet |
|---|---|---|---|
| 1 | 1 | `N$2_P` | 3 |
| 2 | 2 | `N$2_N` | 3 |
| MH1 | MH1 | `GND` | 3 |
| MH2 | MH2 | `GND` | 3 |
| MH3 | MH3 | `GND` | 3 |
| MH4 | MH4 | `GND` | 3 |

### J22 — 142-0731-211 (1420731211)

| Pad | Pin name | Net | Sheet |
|---|---|---|---|
| 1 | 1 | `N$24` | 3 |
| 2 | 2 | `GND` | 3 |
| 3 | 3 | `GND` | 3 |
| 4 | 4 | `GND` | 3 |
| 5 | 5 | `GND` | 3 |

### J23 — 142-0731-211 (1420731211)

| Pad | Pin name | Net | Sheet |
|---|---|---|---|
| 1 | 1 | `N$23` | 3 |
| 2 | 2 | `GND` | 3 |
| 3 | 3 | `GND` | 3 |
| 4 | 4 | `GND` | 3 |
| 5 | 5 | `GND` | 3 |

### J24 — 142-0731-211 (1420731211)

| Pad | Pin name | Net | Sheet |
|---|---|---|---|
| 1 | 1 | `N$129` | 3 |
| 2 | 2 | `GND` | 3 |
| 3 | 3 | `GND` | 3 |
| 4 | 4 | `GND` | 3 |
| 5 | 5 | `GND` | 3 |

### J25 — 142-0731-211 (1420731211)

| Pad | Pin name | Net | Sheet |
|---|---|---|---|
| 1 | 1 | `N$128` | 3 |
| 2 | 2 | `GND` | 3 |
| 3 | 3 | `GND` | 3 |
| 4 | 4 | `GND` | 3 |
| 5 | 5 | `GND` | 3 |

### J26 — 142-0731-211 (1420731211)

| Pad | Pin name | Net | Sheet |
|---|---|---|---|
| 1 | 1 | `N$134` | 3 |
| 2 | 2 | `GND` | 3 |
| 3 | 3 | `GND` | 3 |
| 4 | 4 | `GND` | 3 |
| 5 | 5 | `GND` | 3 |

### J27 — 142-0731-211 (1420731211)

| Pad | Pin name | Net | Sheet |
|---|---|---|---|
| 1 | 1 | `N$133` | 3 |
| 2 | 2 | `GND` | 3 |
| 3 | 3 | `GND` | 3 |
| 4 | 4 | `GND` | 3 |
| 5 | 5 | `GND` | 3 |

### J28 — 142-0731-211 (1420731211)

| Pad | Pin name | Net | Sheet |
|---|---|---|---|
| 1 | 1 | `N$139` | 3 |
| 2 | 2 | `GND` | 3 |
| 3 | 3 | `GND` | 3 |
| 4 | 4 | `GND` | 3 |
| 5 | 5 | `GND` | 3 |

### J29 — 142-0731-211 (1420731211)

| Pad | Pin name | Net | Sheet |
|---|---|---|---|
| 1 | 1 | `N$138` | 3 |
| 2 | 2 | `GND` | 3 |
| 3 | 3 | `GND` | 3 |
| 4 | 4 | `GND` | 3 |
| 5 | 5 | `GND` | 3 |

### J30 — 142-0731-211 (1420731211)

| Pad | Pin name | Net | Sheet |
|---|---|---|---|
| 1 | 1 | `N$144` | 3 |
| 2 | 2 | `GND` | 3 |
| 3 | 3 | `GND` | 3 |
| 4 | 4 | `GND` | 3 |
| 5 | 5 | `GND` | 3 |

### J31 — 142-0731-211 (1420731211)

| Pad | Pin name | Net | Sheet |
|---|---|---|---|
| 1 | 1 | `N$143` | 3 |
| 2 | 2 | `GND` | 3 |
| 3 | 3 | `GND` | 3 |
| 4 | 4 | `GND` | 3 |
| 5 | 5 | `GND` | 3 |

### J32 — 142-0731-211 (1420731211)

| Pad | Pin name | Net | Sheet |
|---|---|---|---|
| 1 | 1 | `N$149` | 3 |
| 2 | 2 | `GND` | 3 |
| 3 | 3 | `GND` | 3 |
| 4 | 4 | `GND` | 3 |
| 5 | 5 | `GND` | 3 |

### J33 — 142-0731-211 (1420731211)

| Pad | Pin name | Net | Sheet |
|---|---|---|---|
| 1 | 1 | `N$148` | 3 |
| 2 | 2 | `GND` | 3 |
| 3 | 3 | `GND` | 3 |
| 4 | 4 | `GND` | 3 |
| 5 | 5 | `GND` | 3 |

### J34 — 142-0731-211 (1420731211)

| Pad | Pin name | Net | Sheet |
|---|---|---|---|
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
| 2 | 2 | `GND` | 3 |
| 3 | 3 | `GND` | 3 |
| 4 | 4 | `GND` | 3 |
| 5 | 5 | `GND` | 3 |

### J55 — 142-0731-211 (1420731211)

| Pad | Pin name | Net | Sheet |
|---|---|---|---|
| 1 | 1 | `N$203` | 3 |
| 2 | 2 | `GND` | 3 |
| 3 | 3 | `GND` | 3 |
| 4 | 4 | `GND` | 3 |
| 5 | 5 | `GND` | 3 |

### JP1 — PINHD-2X6 (2X06)

| Pad | Pin name | Net | Sheet |
|---|---|---|---|
| 1 | 1 | `AD9523_PD` | 2 |
| 2 | 2 | `AD9523_REF_SEL` | 2 |
| 3 | 3 | `AD9523_SYNC` | 2 |
| 4 | 4 | `AD9523_RESET` | 2 |
| 5 | 5 | `AD9523_CS` | 2 |
| 6 | 6 | `STM32_SCLK4` | 2 |
| 7 | 7 | `STM32_MOSI4` | 2 |
| 8 | 8 | `STM32_MISO4` | 2 |
| 9 | 9 | `AD9523_STATUS0` | 2 |
| 10 | 10 | `AD9523_STATUS1` | 2 |
| 11 | 11 | `AD9523_EEPROM_SEL` | 2 |
| 12 | 12 | `GND` | 2 |

### JP2 — PINHD-1X6 (1X06)

| Pad | Pin name | Net | Sheet |
|---|---|---|---|
| 1 | 1 | `+3V3` | 2 |
| 2 | 2 | `STM32_SWCLK` | 2 |
| 3 | 3 | `GND` | 2 |
| 4 | 4 | `STM32_SWDIO` | 2 |
| 5 | 5 | `STM32_NRST` | 2 |
| 6 | 6 | `STM32_SWO` | 2 |

### JP3 — PINHD-2X4 (2X04)

| Pad | Pin name | Net | Sheet |
|---|---|---|---|
| 1 | 1 | `N$32` | 2 |
| 2 | 2 | `+3V3_FPGA` | 2 |
| 3 | 3 | `N$33` | 2 |
| 5 | 5 | `N$34` | 2 |
| 7 | 7 | `N$36` | 2 |
| 8 | 8 | `GND` | 2 |

### JP4 — PINHD-1X3 (1X03)

| Pad | Pin name | Net | Sheet |
|---|---|---|---|
| 1 | 1 | `EN/DIS_COOLING` | 2 |
| 3 | 3 | `GND` | 2 |

### JP5 — PINHD-1X3 (1X03)

| Pad | Pin name | Net | Sheet |
|---|---|---|---|
| 1 | 1 | `+3V3_AN4_F` | 4 |
| 2 | 2 | `N$295` | 4 |
| 3 | 3 | `GND` | 4 |

### JP6 — PINHD-1X3 (1X03)

| Pad | Pin name | Net | Sheet |
|---|---|---|---|
| 1 | 1 | `+3V3_AN4_F` | 4 |
| 2 | 2 | `N$296` | 4 |
| 3 | 3 | `GND` | 4 |

### JP7 — PINHD-1X8 (1X08)

| Pad | Pin name | Net | Sheet |
|---|---|---|---|
| 2 | 2 | `+3V3` | 2 |
| 3 | 3 | `GND` | 2 |
| 4 | 4 | `STM32_SCL3` | 2 |
| 5 | 5 | `STM32_SDA3` | 2 |
| 6 | 6 | `MAG_DRDY` | 2 |
| 7 | 7 | `ACC_INT` | 2 |
| 8 | 8 | `GYR_INT` | 2 |

### JP8 — PINHD-1X4 (1X04)

| Pad | Pin name | Net | Sheet |
|---|---|---|---|
| 1 | 1 | `+3V3` | 2 |
| 2 | 2 | `STM32_TX5` | 2 |
| 3 | 3 | `STM32_RX5` | 2 |
| 4 | 4 | `GND` | 2 |

### JP9 — PINHD-1X4 (1X04)

| Pad | Pin name | Net | Sheet |
|---|---|---|---|
| 1 | 1 | `GND` | 2 |
| 2 | 2 | `STEPPER_CW+` | 2 |
| 3 | 3 | `GND` | 2 |
| 4 | 4 | `STEPPER_CLK+` | 2 |

### JP10 — PINHD-1X3 (1X03)

| Pad | Pin name | Net | Sheet |
|---|---|---|---|
| 1 | 1 | `EN/DIS_RFPA_VDD` | 2 |
| 3 | 3 | `GND` | 2 |

### JP11 — PINHD-1X3 (1X03)

| Pad | Pin name | Net | Sheet |
|---|---|---|---|
| 1 | 1 | `+3V3_AN4_F` | 4 |
| 2 | 2 | `N$306` | 4 |
| 3 | 3 | `GND` | 4 |

### JP12 — PINHD-1X3 (1X03)

| Pad | Pin name | Net | Sheet |
|---|---|---|---|
| 1 | 1 | `+3V3_AN4_F` | 4 |
| 2 | 2 | `N$298` | 4 |
| 3 | 3 | `GND` | 4 |

### JP13 — PINHD-2X7 (2X07)

| Pad | Pin name | Net | Sheet |
|---|---|---|---|
| 1 | 1 | `STM32_MISO4` | 2 |
| 2 | 2 | `STM32_SCLK4` | 2 |
| 3 | 3 | `STM32_MOSI4` | 2 |
| 4 | 4 | `ADF4382_TX_CS` | 2 |
| 5 | 5 | `ADF4382_TX_CE` | 2 |
| 6 | 6 | `ADF4382_TX_DELSTR` | 2 |
| 7 | 7 | `ADF4382_TX_DELADJ` | 2 |
| 8 | 8 | `ADF4382_TX_LKDET` | 2 |
| 9 | 9 | `ADF4382_RX_CS` | 2 |
| 10 | 10 | `ADF4382_RX_CE` | 2 |
| 11 | 11 | `ADF4382_RX_DELSTR` | 2 |
| 12 | 12 | `ADF4382_RX_DELADJ` | 2 |
| 13 | 13 | `ADF4382_RX_LKDET` | 2 |
| 14 | 14 | `GND` | 2 |

### JP14 — PINHD-1X3 (1X03)

| Pad | Pin name | Net | Sheet |
|---|---|---|---|
| 1 | 1 | `+3V3_AN4_F` | 4 |
| 2 | 2 | `N$299` | 4 |
| 3 | 3 | `GND` | 4 |

### JP15 — PINHD-1X3 (1X03)

| Pad | Pin name | Net | Sheet |
|---|---|---|---|
| 1 | 1 | `+3V3_AN4_F` | 4 |
| 2 | 2 | `N$307` | 4 |
| 3 | 3 | `GND` | 4 |

### JP16 — PINHD-1X3 (1X03)

| Pad | Pin name | Net | Sheet |
|---|---|---|---|
| 1 | 1 | `+3V3_AN4_F` | 4 |
| 2 | 2 | `N$301` | 4 |
| 3 | 3 | `GND` | 4 |

### JP17 — PINHD-1X3 (1X03)

| Pad | Pin name | Net | Sheet |
|---|---|---|---|
| 1 | 1 | `STM32_TX3` | 2 |
| 2 | 2 | `STM32_RX3` | 2 |
| 3 | 3 | `GND` | 2 |

### JP18 — PINHD-1X4 (1X04)

| Pad | Pin name | Net | Sheet |
|---|---|---|---|
| 1 | 1 | `STM32_SDA3` | 2 |
| 2 | 2 | `STM32_SCL3` | 2 |
| 3 | 3 | `GND` | 2 |
| 4 | 4 | `+3V3` | 2 |

### JP19 — PINHD-1X3 (1X03)

| Pad | Pin name | Net | Sheet |
|---|---|---|---|
| 1 | 1 | `+3V3_AN4_F` | 4 |
| 2 | 2 | `N$297` | 4 |
| 3 | 3 | `GND` | 4 |

### JP20 — PINHD-1X2 (1X02)

| Pad | Pin name | Net | Sheet |
|---|---|---|---|
| 1 | 1 | `FPGA_CLOCK_TEST` | 2 |
| 2 | 2 | `GND` | 2 |

### SV1 — MA10-2 (MA10-2)

| Pad | Pin name | Net | Sheet |
|---|---|---|---|
| 1 | 1 | `EN_+1V0_FPGA` | 2 |
| 2 | 2 | `EN_+5V0_PA2` | 2 |
| 3 | 3 | `EN_+1V8_FPGA` | 2 |
| 4 | 4 | `EN_+5V0_PA3` | 2 |
| 5 | 5 | `EN_+3V3_FPGA` | 2 |
| 6 | 6 | `EN_+5V5_PA` | 2 |
| 7 | 7 | `EN_+5V0_ADAR` | 2 |
| 8 | 8 | `EN_+1V8_CLOCK` | 2 |
| 9 | 9 | `EN_+3V3_ADAR12` | 2 |
| 10 | 10 | `EN_+3V3_CLOCK` | 2 |
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
### X_7 — 22-23-2021 (22-23-2021)

| Pad | Pin name | Net | Sheet |
|---|---|---|---|
| 1 | S | `VG_1` | 4 |
| 2 | S | `GND` | 4 |

### X_8 — 22-23-2021 (22-23-2021)

| Pad | Pin name | Net | Sheet |
|---|---|---|---|
| 1 | S | `VG_3` | 4 |
| 2 | S | `GND` | 4 |

### X_9 — 22-23-2021 (22-23-2021)

| Pad | Pin name | Net | Sheet |
|---|---|---|---|
| 1 | S | `VG_14` | 4 |
| 2 | S | `GND` | 4 |

### X_10 — 22-23-2021 (22-23-2021)

| Pad | Pin name | Net | Sheet |
|---|---|---|---|
| 1 | S | `VG_16` | 4 |
| 2 | S | `GND` | 4 |

### X_11 — 22-23-2021 (22-23-2021)

| Pad | Pin name | Net | Sheet |
|---|---|---|---|
| 1 | S | `VG_6` | 4 |
| 2 | S | `GND` | 4 |

### X_12 — 22-23-2021 (22-23-2021)

| Pad | Pin name | Net | Sheet |
|---|---|---|---|
| 1 | S | `VG_8` | 4 |
| 2 | S | `GND` | 4 |

### X_13 — 22-23-2021 (22-23-2021)

| Pad | Pin name | Net | Sheet |
|---|---|---|---|
| 1 | S | `VG_12` | 4 |
| 2 | S | `GND` | 4 |

### X_14 — 22-23-2021 (22-23-2021)

| Pad | Pin name | Net | Sheet |
|---|---|---|---|
| 1 | S | `VG_10` | 4 |
| 2 | S | `GND` | 4 |

### X_15 — 22-23-2021 (22-23-2021)

| Pad | Pin name | Net | Sheet |
|---|---|---|---|
| 1 | S | `VG_4` | 4 |
| 2 | S | `GND` | 4 |

### X_16 — 22-23-2021 (22-23-2021)

| Pad | Pin name | Net | Sheet |
|---|---|---|---|
| 1 | S | `VG_2` | 4 |
| 2 | S | `GND` | 4 |

## 3. Net fan-out (nets with ≥ 8 connections)

| Net | Connections | Class |
|---|---|---|
| `GND` | 2517 | 0 |
| `+3V4` | 70 | 0 |
| `-3V4` | 70 | 0 |
| `+3V3_FPGA` | 49 | 0 |
| `+3V3` | 40 | 0 |
| `+1V8_CLOCK_F` | 29 | 0 |
| `+3V3_AN4_F` | 26 | 0 |
| `+1V8_FPGA` | 19 | 0 |
| `+3V3_AN3_F` | 18 | 0 |
| `M3S_VCTRL` | 18 | 0 |
| `+3V3_ADTR` | 17 | 0 |
| `+3V3_AN5_F` | 17 | 0 |
| `+3V3_AN6_F` | 17 | 0 |
| `+3V3_VDD_SW` | 17 | 0 |
| `-3V3_SW` | 17 | 0 |
| `+3V3_AN` | 13 | 0 |
| `+3V3_ADAR4_F` | 9 | 0 |
| `+3V3_ADAR2_F` | 8 | 0 |
| `+3V3_ADAR3_F` | 8 | 0 |

## 4. Component-to-net table

Full machine-readable form: `netlists/MAIN_BOARD_netlist_by_part.csv`. Physical parts only; pads shown when the device defines a package connection.

| Part | Value | Device / package | Connections (pad:net) |
|---|---|---|---|
| ADAR1_ |  | ADAR1000ACCZN / CC-88-1_ADI | 89:`GND`, A1:`DET3_1`, A2:`GND`, A4:`PA_BIAS4_1`, A5:`PA_BIAS3_1`, A6:`GND`, A7:`RF_IO_1`, A8:`GND`, A9:`PA_BIAS2_1`, A10:`PA_BIAS1_1`, A11:`LNA_BIAS_1`, A12:`GND`, A13:`GND`, B1:`GND`, B2:`GND`, B3:`N$39`, B5:`TR_SW_POS_1`, B6:`GND`, B7:`GND`, B8:`GND`, B9:`GND`, B10:`GND`, B11:`-5V0_ADAR12`, B12:`GND`, B13:`GND`, C1:`TX3_1`, C2:`GND`, C12:`GND`, C13:`RX2_1`, D1:`GND`, D2:`GND`, D12:`GND`, D13:`GND`, E1:`RX3_1`, E2:`GND`, E12:`GND`, E13:`TX2_1`, F1:`GND`, F2:`GND`, F12:`GND`, F13:`GND`, G1:`DET4_1`, G2:`GND`, G12:`GND`, G13:`DET2_1`, H1:`GND`, H2:`GND`, H12:`GND`, H13:`GND`, J1:`TX4_1`, J2:`G … (87 pins, see CSV) |
| ADAR2_ |  | ADAR1000ACCZN / CC-88-1_ADI | 89:`GND`, A1:`DET3_2`, A2:`GND`, A4:`PA_BIAS4_2`, A5:`PA_BIAS3_2`, A6:`GND`, A7:`RF_IO_2`, A8:`GND`, A9:`PA_BIAS2_2`, A10:`PA_BIAS1_2`, A11:`LNA_BIAS_2`, A12:`GND`, A13:`GND`, B1:`GND`, B2:`GND`, B3:`N$40`, B5:`TR_SW_POS_2`, B6:`GND`, B7:`GND`, B8:`GND`, B9:`GND`, B10:`GND`, B11:`-5V0_ADAR12`, B12:`GND`, B13:`GND`, C1:`TX3_2`, C2:`GND`, C12:`GND`, C13:`RX2_2`, D1:`GND`, D2:`GND`, D12:`GND`, D13:`GND`, E1:`RX3_2`, E2:`GND`, E12:`GND`, E13:`TX2_2`, F1:`GND`, F2:`GND`, F12:`GND`, F13:`GND`, G1:`DET4_2`, G2:`GND`, G12:`GND`, G13:`DET2_2`, H1:`GND`, H2:`GND`, H12:`GND`, H13:`GND`, J1:`TX4_2`, J2:`G … (87 pins, see CSV) |
| ADAR3_ |  | ADAR1000ACCZN / CC-88-1_ADI | 89:`GND`, A1:`DET3_3`, A2:`GND`, A4:`PA_BIAS4_3`, A5:`PA_BIAS3_3`, A6:`GND`, A7:`RF_IO_3`, A8:`GND`, A9:`PA_BIAS2_3`, A10:`PA_BIAS1_3`, A11:`LNA_BIAS_3`, A12:`GND`, A13:`GND`, B1:`GND`, B2:`GND`, B3:`N$57`, B5:`TR_SW_POS_3`, B6:`GND`, B7:`GND`, B8:`GND`, B9:`GND`, B10:`GND`, B11:`-5V0_ADAR34`, B12:`GND`, B13:`GND`, C1:`TX3_3`, C2:`GND`, C12:`GND`, C13:`RX2_3`, D1:`GND`, D2:`GND`, D12:`GND`, D13:`GND`, E1:`RX3_3`, E2:`GND`, E12:`GND`, E13:`TX2_3`, F1:`GND`, F2:`GND`, F12:`GND`, F13:`GND`, G1:`DET4_3`, G2:`GND`, G12:`GND`, G13:`DET2_3`, H1:`GND`, H2:`GND`, H12:`GND`, H13:`GND`, J1:`TX4_3`, J2:`G … (87 pins, see CSV) |
| ADAR4_ |  | ADAR1000ACCZN / CC-88-1_ADI | 89:`GND`, A1:`DET3_4`, A2:`GND`, A4:`PA_BIAS4_4`, A5:`PA_BIAS3_4`, A6:`GND`, A7:`RF_IO_4`, A8:`GND`, A9:`PA_BIAS2_4`, A10:`PA_BIAS1_4`, A11:`LNA_BIAS_4`, A12:`GND`, A13:`GND`, B1:`GND`, B2:`GND`, B3:`N$64`, B5:`TR_SW_POS_4`, B6:`GND`, B7:`GND`, B8:`GND`, B9:`GND`, B10:`GND`, B11:`-5V0_ADAR34`, B12:`GND`, B13:`GND`, C1:`TX3_4`, C2:`GND`, C12:`GND`, C13:`RX2_4`, D1:`GND`, D2:`GND`, D12:`GND`, D13:`GND`, E1:`RX3_4`, E2:`GND`, E12:`GND`, E13:`TX2_4`, F1:`GND`, F2:`GND`, F12:`GND`, F13:`GND`, G1:`DET4_4`, G2:`GND`, G12:`GND`, G13:`DET2_4`, H1:`GND`, H2:`GND`, H12:`GND`, H13:`GND`, J1:`TX4_4`, J2:`G … (87 pins, see CSV) |
| ADTR1107_1 |  | ADTR1107ACCZ / CC-24-8_ADI | 1:`GND`, 2:`RX2_1`, 3:`GND`, 4:`GND`, 5:`TX2_1`, 6:`GND`, 7:`PA_BIAS2_1`, 8:`+5V0_PA_1`, 9:`GND`, 10:`GND`, 11:`GND`, 12:`DET2_1`, 13:`GND`, 14:`GND`, 15:`GND`, 16:`GND`, 17:`ANT2_1`, 18:`GND`, 19:`+3V3_VDD_SW`, 20:`TR_SW_POS_1`, 21:`-3V3_SW`, 22:`GND`, 23:`LNA_BIAS_1`, 24:`+3V3_ADTR`, 25:`GND` |
| ADTR1107_2 |  | ADTR1107ACCZ / CC-24-8_ADI | 1:`GND`, 2:`RX3_1`, 3:`GND`, 4:`GND`, 5:`TX3_1`, 6:`GND`, 7:`PA_BIAS3_1`, 8:`+5V0_PA_1`, 9:`GND`, 10:`GND`, 11:`GND`, 12:`DET3_1`, 13:`GND`, 14:`GND`, 15:`GND`, 16:`GND`, 17:`ANT3_1`, 18:`GND`, 19:`+3V3_VDD_SW`, 20:`TR_SW_POS_1`, 21:`-3V3_SW`, 22:`GND`, 23:`LNA_BIAS_1`, 24:`+3V3_ADTR`, 25:`GND` |
| ADTR1107_3 |  | ADTR1107ACCZ / CC-24-8_ADI | 1:`GND`, 2:`RX1_1`, 3:`GND`, 4:`GND`, 5:`TX1_1`, 6:`GND`, 7:`PA_BIAS1_1`, 8:`+5V0_PA_1`, 9:`GND`, 10:`GND`, 11:`GND`, 12:`DET1_1`, 13:`GND`, 14:`GND`, 15:`GND`, 16:`GND`, 17:`ANT1_1`, 18:`GND`, 19:`+3V3_VDD_SW`, 20:`TR_SW_POS_1`, 21:`-3V3_SW`, 22:`GND`, 23:`LNA_BIAS_1`, 24:`+3V3_ADTR`, 25:`GND` |
| ADTR1107_4 |  | ADTR1107ACCZ / CC-24-8_ADI | 1:`GND`, 2:`RX4_1`, 3:`GND`, 4:`GND`, 5:`TX4_1`, 6:`GND`, 7:`PA_BIAS4_1`, 8:`+5V0_PA_1`, 9:`GND`, 10:`GND`, 11:`GND`, 12:`DET4_1`, 13:`GND`, 14:`GND`, 15:`GND`, 16:`GND`, 17:`ANT4_1`, 18:`GND`, 19:`+3V3_VDD_SW`, 20:`TR_SW_POS_1`, 21:`-3V3_SW`, 22:`GND`, 23:`LNA_BIAS_1`, 24:`+3V3_ADTR`, 25:`GND` |
| ADTR1107_5 |  | ADTR1107ACCZ / CC-24-8_ADI | 1:`GND`, 2:`RX2_2`, 3:`GND`, 4:`GND`, 5:`TX2_2`, 6:`GND`, 7:`PA_BIAS2_2`, 8:`+5V0_PA_2`, 9:`GND`, 10:`GND`, 11:`GND`, 12:`DET2_2`, 13:`GND`, 14:`GND`, 15:`GND`, 16:`GND`, 17:`ANT2_2`, 18:`GND`, 19:`+3V3_VDD_SW`, 20:`TR_SW_POS_2`, 21:`-3V3_SW`, 22:`GND`, 23:`LNA_BIAS_2`, 24:`+3V3_ADTR`, 25:`GND` |
| ADTR1107_6 |  | ADTR1107ACCZ / CC-24-8_ADI | 1:`GND`, 2:`RX3_2`, 3:`GND`, 4:`GND`, 5:`TX3_2`, 6:`GND`, 7:`PA_BIAS3_2`, 8:`+5V0_PA_2`, 9:`GND`, 10:`GND`, 11:`GND`, 12:`DET3_2`, 13:`GND`, 14:`GND`, 15:`GND`, 16:`GND`, 17:`ANT3_2`, 18:`GND`, 19:`+3V3_VDD_SW`, 20:`TR_SW_POS_2`, 21:`-3V3_SW`, 22:`GND`, 23:`LNA_BIAS_2`, 24:`+3V3_ADTR`, 25:`GND` |
| ADTR1107_7 |  | ADTR1107ACCZ / CC-24-8_ADI | 1:`GND`, 2:`RX1_2`, 3:`GND`, 4:`GND`, 5:`TX1_2`, 6:`GND`, 7:`PA_BIAS1_2`, 8:`+5V0_PA_1`, 9:`GND`, 10:`GND`, 11:`GND`, 12:`DET1_2`, 13:`GND`, 14:`GND`, 15:`GND`, 16:`GND`, 17:`ANT1_2`, 18:`GND`, 19:`+3V3_VDD_SW`, 20:`TR_SW_POS_2`, 21:`-3V3_SW`, 22:`GND`, 23:`LNA_BIAS_2`, 24:`+3V3_ADTR`, 25:`GND` |
| ADTR1107_8 |  | ADTR1107ACCZ / CC-24-8_ADI | 1:`GND`, 2:`RX4_2`, 3:`GND`, 4:`GND`, 5:`TX4_2`, 6:`GND`, 7:`PA_BIAS4_2`, 8:`+5V0_PA_2`, 9:`GND`, 10:`GND`, 11:`GND`, 12:`DET4_2`, 13:`GND`, 14:`GND`, 15:`GND`, 16:`GND`, 17:`ANT4_2`, 18:`GND`, 19:`+3V3_VDD_SW`, 20:`TR_SW_POS_2`, 21:`-3V3_SW`, 22:`GND`, 23:`LNA_BIAS_2`, 24:`+3V3_ADTR`, 25:`GND` |
| ADTR1107_9 |  | ADTR1107ACCZ / CC-24-8_ADI | 1:`GND`, 2:`RX4_3`, 3:`GND`, 4:`GND`, 5:`TX4_3`, 6:`GND`, 7:`PA_BIAS4_3`, 8:`+5V0_PA_3`, 9:`GND`, 10:`GND`, 11:`GND`, 12:`DET4_3`, 13:`GND`, 14:`GND`, 15:`GND`, 16:`GND`, 17:`ANT4_3`, 18:`GND`, 19:`+3V3_VDD_SW`, 20:`TR_SW_POS_3`, 21:`-3V3_SW`, 22:`GND`, 23:`LNA_BIAS_3`, 24:`+3V3_ADTR`, 25:`GND` |
| ADTR1107_10 |  | ADTR1107ACCZ / CC-24-8_ADI | 1:`GND`, 2:`RX1_3`, 3:`GND`, 4:`GND`, 5:`TX1_3`, 6:`GND`, 7:`PA_BIAS1_3`, 8:`+5V0_PA_2`, 9:`GND`, 10:`GND`, 11:`GND`, 12:`DET1_3`, 13:`GND`, 14:`GND`, 15:`GND`, 16:`GND`, 17:`ANT1_3`, 18:`GND`, 19:`+3V3_VDD_SW`, 20:`TR_SW_POS_3`, 21:`-3V3_SW`, 22:`GND`, 23:`LNA_BIAS_3`, 24:`+3V3_ADTR`, 25:`GND` |
| ADTR1107_11 |  | ADTR1107ACCZ / CC-24-8_ADI | 1:`GND`, 2:`RX3_3`, 3:`GND`, 4:`GND`, 5:`TX3_3`, 6:`GND`, 7:`PA_BIAS3_3`, 8:`+5V0_PA_3`, 9:`GND`, 10:`GND`, 11:`GND`, 12:`DET3_3`, 13:`GND`, 14:`GND`, 15:`GND`, 16:`GND`, 17:`ANT3_3`, 18:`GND`, 19:`+3V3_VDD_SW`, 20:`TR_SW_POS_3`, 21:`-3V3_SW`, 22:`GND`, 23:`LNA_BIAS_3`, 24:`+3V3_ADTR`, 25:`GND` |
| ADTR1107_12 |  | ADTR1107ACCZ / CC-24-8_ADI | 1:`GND`, 2:`RX2_3`, 3:`GND`, 4:`GND`, 5:`TX2_3`, 6:`GND`, 7:`PA_BIAS2_3`, 8:`+5V0_PA_2`, 9:`GND`, 10:`GND`, 11:`GND`, 12:`DET2_3`, 13:`GND`, 14:`GND`, 15:`GND`, 16:`GND`, 17:`ANT2_3`, 18:`GND`, 19:`+3V3_VDD_SW`, 20:`TR_SW_POS_3`, 21:`-3V3_SW`, 22:`GND`, 23:`LNA_BIAS_3`, 24:`+3V3_ADTR`, 25:`GND` |
| ADTR1107_13 |  | ADTR1107ACCZ / CC-24-8_ADI | 1:`GND`, 2:`RX4_4`, 3:`GND`, 4:`GND`, 5:`TX4_4`, 6:`GND`, 7:`PA_BIAS4_4`, 8:`+5V0_PA_3`, 9:`GND`, 10:`GND`, 11:`GND`, 12:`DET4_4`, 13:`GND`, 14:`GND`, 15:`GND`, 16:`GND`, 17:`ANT4_4`, 18:`GND`, 19:`+3V3_VDD_SW`, 20:`TR_SW_POS_4`, 21:`-3V3_SW`, 22:`GND`, 23:`LNA_BIAS_4`, 24:`+3V3_ADTR`, 25:`GND` |
| ADTR1107_14 |  | ADTR1107ACCZ / CC-24-8_ADI | 1:`GND`, 2:`RX1_4`, 3:`GND`, 4:`GND`, 5:`TX1_4`, 6:`GND`, 7:`PA_BIAS1_4`, 8:`+5V0_PA_3`, 9:`GND`, 10:`GND`, 11:`GND`, 12:`DET1_4`, 13:`GND`, 14:`GND`, 15:`GND`, 16:`GND`, 17:`ANT1_4`, 18:`GND`, 19:`+3V3_VDD_SW`, 20:`TR_SW_POS_4`, 21:`-3V3_SW`, 22:`GND`, 23:`LNA_BIAS_4`, 24:`+3V3_ADTR`, 25:`GND` |
| ADTR1107_15 |  | ADTR1107ACCZ / CC-24-8_ADI | 1:`GND`, 2:`RX3_4`, 3:`GND`, 4:`GND`, 5:`TX3_4`, 6:`GND`, 7:`PA_BIAS3_4`, 8:`+5V0_PA_3`, 9:`GND`, 10:`GND`, 11:`GND`, 12:`DET3_4`, 13:`GND`, 14:`GND`, 15:`GND`, 16:`GND`, 17:`ANT3_4`, 18:`GND`, 19:`+3V3_VDD_SW`, 20:`TR_SW_POS_4`, 21:`-3V3_SW`, 22:`GND`, 23:`LNA_BIAS_4`, 24:`+3V3_ADTR`, 25:`GND` |
| ADTR1107_16 |  | ADTR1107ACCZ / CC-24-8_ADI | 1:`GND`, 2:`RX2_4`, 3:`GND`, 4:`GND`, 5:`TX2_4`, 6:`GND`, 7:`PA_BIAS2_4`, 8:`+5V0_PA_3`, 9:`GND`, 10:`GND`, 11:`GND`, 12:`DET2_4`, 13:`GND`, 14:`GND`, 15:`GND`, 16:`GND`, 17:`ANT2_4`, 18:`GND`, 19:`+3V3_VDD_SW`, 20:`TR_SW_POS_4`, 21:`-3V3_SW`, 22:`GND`, 23:`LNA_BIAS_4`, 24:`+3V3_ADTR`, 25:`GND` |
| C1 | 0.1uF | CC0201 / C0201 | 1:`ADC_CLK_IN_P`, 2:`N$2_P` |
| C2 | 0.1uF | CC0201 / C0201 | 1:`ADC_CLK_IN_N`, 2:`N$2_N` |
| C3 | 2.7pF | C-EUC0402 / C0402 | 1:`N$4`, 2:`N$43` |
| C4 | 0.1uF | CC0201 / C0201 | 1:`GND`, 2:`+1V8_CLOCK_F` |
| C5 | 0.1uF | CC0201 / C0201 | 1:`GND`, 2:`+1V8_CLOCK_F` |
| C6 | 0.1uF | CC0201 / C0201 | 1:`GND`, 2:`+1V8_CLOCK_F` |
| C7 | 0.1uF | CC0201 / C0201 | 1:`GND`, 2:`+1V8_CLOCK_F` |
| C8 | 0.1uF | CC0201 / C0201 | 1:`GND`, 2:`+1V8_CLOCK_F` |
| C9 | 0.1uF | CC0201 / C0201 | 1:`GND`, 2:`+1V8_CLOCK_F` |
| C10 | 0.1uF | CC0201 / C0201 | 1:`GND`, 2:`+1V8_CLOCK_F` |
| C11 | 0.1uF | CC0201 / C0201 | 1:`GND`, 2:`+1V8_CLOCK_F` |
| C12 | 0.1uF | CC0201 / C0201 | 1:`GND`, 2:`+1V8_CLOCK_F` |
| C13 | 0.1uF | CC0201 / C0201 | 1:`GND`, 2:`+1V8_CLOCK_F` |
| C14 | 0.1uF | CC0201 / C0201 | 1:`GND`, 2:`+1V8_CLOCK_F` |
| C15 | 0.1uF | CC0201 / C0201 | 1:`GND`, 2:`+1V8_FPGA` |
| C16 | 0.1uF | CC0201 / C0201 | 1:`GND`, 2:`+1V8_FPGA` |
| C17 | 47uF | CC0201 / C0201 | 1:`GND`, 2:`+3V3_FPGA` |
| C18 | 2.7pF | CC0201 / C0201 | 1:`STM32_OSC_32_N`, 2:`GND` |
| C19 | 2.7pF | CC0201 / C0201 | 1:`STM32_OSC_32_P`, 2:`GND` |
| C20 | 4.3pF | CC0201 / C0201 | 1:`STM32_OSC_N`, 2:`GND` |
| C21 | 4.3pF | CC0201 / C0201 | 1:`STM32_OSC_P`, 2:`GND` |
| C22 | 2.2uF | CC0201 / C0201 | 1:`N$8`, 2:`GND` |
| C23 | 2.2uF | CC0201 / C0201 | 1:`N$7`, 2:`GND` |
| C24 | 100nF | CC0201 / C0201 | 1:`N$9`, 2:`GND` |
| C25 | 100nF | CC0201 / C0201 | 1:`+3V3`, 2:`GND` |
| C26 | 100nF | CC0201 / C0201 | 1:`+3V3`, 2:`GND` |
| C27 | 100nF | CC0201 / C0201 | 1:`+3V3`, 2:`GND` |
| C28 | 100nF | CC0201 / C0201 | 1:`+3V3`, 2:`GND` |
| C29 | 100nF | CC0201 / C0201 | 1:`+3V3`, 2:`GND` |
| C30 | 100nF | CC0201 / C0201 | 1:`+3V3`, 2:`GND` |
| C31 | 47nF | CC0201 / C0201 | 1:`+3V3`, 2:`GND` |
| C32 | 100nF | CC0201 / C0201 | 1:`+3V3`, 2:`GND` |
| C33 | 100nF | CC0201 / C0201 | 1:`+3V3`, 2:`GND` |
| C34 | 100nF | CC0201 / C0201 | 1:`+3V3`, 2:`GND` |
| C35 | 100nF | CC0201 / C0201 | 1:`+3V3`, 2:`GND` |
| C36 | 0.1uF | CC0201 / C0201 | 1:`GND`, 2:`+1V8_FPGA` |
| C37 | 10uF | CC0201 / C0201 | 1:`+3V3_FPGA`, 2:`GND` |
| C38 | 0.1uF | CC0201 / C0201 | 1:`N$37`, 2:`GND` |
| C39 | 0.1uF | CC0201 / C0201 | 1:`N$96`, 2:`DAC_AVDD` |
| C40 | 10uF | CC0201 / C0201 | 1:`+3V3_AN`, 2:`GND` |
| C41 | 0.1uF | CC0201 / C0201 | 1:`+3V3_FPGA`, 2:`GND` |
| C42 | 0.1uF | CC0201 / C0201 | 1:`+3V3_AN`, 2:`GND` |
| C43 | 0.2pF | C-EUC0201 / C0201 | 1:`N$15`, 2:`N$5` |
| C44 | 0.1uF | CC0201 / C0201 | 1:`N$56`, 2:`ADC_IF_IN_P` |
| C45 | 0.1uF | CC0201 / C0201 | 1:`N$65`, 2:`ADC_IF_IN_N` |
| C46 | 0.1uF | CC0201 / C0201 | 1:`GND`, 2:`N$67` |
| C47 | 0.1uF | CC0201 / C0201 | 1:`GND`, 2:`N$51` |
| C48 | 0.1µF | C-EUC0402 / C0402 | 1:`AMP_IF_IN_N`, 2:`N$73` |
| C49 | 0.1µF | C-EUC0402 / C0402 | 1:`N$78`, 2:`AMP_IF_IN_P` |
| C50 | 100nF | CC0201 / C0201 | 1:`GND`, 2:`+3V3_FPGA` |
| C51 | 0.1uF | CC0201 / C0201 | 1:`N$104`, 2:`AMP_IF_IN_P` |
| C52 | 0.1uF | CC0201 / C0201 | 1:`N$105`, 2:`AMP_IF_IN_N` |
| C53 | 0.1uF | CC0201 / C0201 | 1:`GND`, 2:`N$110` |
| C54 | 0.6pF | C-EUC0201 / C0201 | 1:`N$86`, 2:`N$85` |
| C55 | 47uF | CC0201 / C0201 | 1:`GND`, 2:`+3V3_FPGA` |
| C56 | 0.1uF | CC0201 / C0201 | 1:`GND`, 2:`N$102` |
| C57 | 0.1µF | C-EUC0402 / C0402 | 1:`AMP_IN_N`, 2:`N$111` |
| C58 | 0.1µF | C-EUC0402 / C0402 | 1:`N$112`, 2:`AMP_IN_P` |
| C59 | 32.8pF | CC0201 / C0201 | 1:`DAC_IOUT_F_P`, 2:`DAC_IOUT_F_N` |
| C60 | 103pF | CC0201 / C0201 | 1:`N$300`, 2:`N$305` |
| C61 | 7.8pF | CC0201 / C0201 | 1:`N$58`, 2:`N$300` |
| C62 | 7.8pF | CC0201 / C0201 | 1:`N$62`, 2:`N$305` |
| C63 | 103pF | CC0201 / C0201 | 1:`N$113`, 2:`N$125` |
| C64 | 25pF | CC0201 / C0201 | 1:`N$71`, 2:`N$113` |
| C65 | 25pF | CC0201 / C0201 | 1:`N$82`, 2:`N$125` |
| C66 | 100pF | CC0201 / C0201 | 1:`-3V4`, 2:`GND` |
| C67 | 0.1uF | CC0201 / C0201 | 1:`-3V4`, 2:`GND` |
| C68 | 100pF | CC0201 / C0201 | 1:`+3V4`, 2:`GND` |
| C69 | 0.1uF | CC0201 / C0201 | 1:`+3V4`, 2:`GND` |
| C70 | 1pF | CC0201 / C0201 | 1:`N$128`, 2:`N$74` |
| C71 | 1pF | CC0201 / C0201 | 1:`N$127`, 2:`N$129` |
| C72 | 1pF | CC0201 / C0201 | 1:`N$100`, 2:`ANT1_1` |
| C73 | 100pF | CC0201 / C0201 | 1:`-3V4`, 2:`GND` |
| C74 | 0.1uF | CC0201 / C0201 | 1:`-3V4`, 2:`GND` |
| C75 | 10µF | C-EUC0805 / C0805 | 1:`+3V3_AN3_F`, 2:`GND` |
| C76 | 100nF | C-EUC0402 / C0402 | 1:`+3V3_AN3_F`, 2:`GND` |
| C77 | 10µF | C-EUC0805 / C0805 | 1:`+3V3_AN4_F`, 2:`GND` |
| C78 | 100nF | C-EUC0402 / C0402 | 1:`+3V3_AN4_F`, 2:`GND` |
| C79 | 100pF | CC0201 / C0201 | 1:`-3V4`, 2:`GND` |
| C80 | 0.1uF | CC0201 / C0201 | 1:`-3V4`, 2:`GND` |
| C81 | 100pF | CC0201 / C0201 | 1:`+3V4`, 2:`GND` |
| C82 | 0.1uF | CC0201 / C0201 | 1:`+3V4`, 2:`GND` |
| C83 | 1pF | CC0201 / C0201 | 1:`RF_TX_FIL`, 2:`N$21` |
| C84 | 1pF | CC0201 / C0201 | 1:`N$38`, 2:`RF_RX_FIL` |
| C85 | 1pF | CC0201 / C0201 | 1:`N$26`, 2:`RF_IO` |
| C86 | 1uF | CC0201 / C0201 | 1:`N$45`, 2:`GND` |
| C87 | 1uF | CC0201 / C0201 | 1:`N$42`, 2:`GND` |
| C88 | 1uF | CC0201 / C0201 | 1:`N$77`, 2:`GND` |
| C89 | 1uF | CC0201 / C0201 | 1:`N$76`, 2:`GND` |
| C90 | 1uF | CC0201 / C0201 | 1:`N$79`, 2:`GND` |
| C91 | 1uF | CC0201 / C0201 | 1:`N$66`, 2:`GND` |
| C92 | 1uF | CC0201 / C0201 | 1:`N$46`, 2:`GND` |
| C93 | 1uF | CC0201 / C0201 | 1:`N$53`, 2:`GND` |
| C94 | 1uF | CC0201 / C0201 | 1:`N$60`, 2:`GND` |
| C95 | 1uF | CC0201 / C0201 | 1:`N$59`, 2:`GND` |
| C96 | 1uF | CC0201 / C0201 | 1:`N$61`, 2:`GND` |
| C97 | 1uF | CC0201 / C0201 | 1:`N$63`, 2:`GND` |
| C98 | 1uF | CC0201 / C0201 | 1:`N$69`, 2:`GND` |
| C99 | 1uF | CC0201 / C0201 | 1:`N$68`, 2:`GND` |
| C100 | 1uF | CC0201 / C0201 | 1:`N$70`, 2:`GND` |
| C101 | 1uF | CC0201 / C0201 | 1:`N$75`, 2:`GND` |
| C102 | 10nF | CC0201 / C0201 | 1:`PA_BIAS2_1`, 2:`GND` |
| C103 | 10nF | CC0201 / C0201 | 1:`PA_BIAS1_1`, 2:`GND` |
| C104 | 10nF | CC0201 / C0201 | 1:`PA_BIAS4_1`, 2:`GND` |
| C105 | 10nF | CC0201 / C0201 | 1:`PA_BIAS3_1`, 2:`GND` |
| C106 | 10nF | CC0201 / C0201 | 1:`PA_BIAS2_2`, 2:`GND` |
| C107 | 10nF | CC0201 / C0201 | 1:`PA_BIAS1_2`, 2:`GND` |
| C108 | 4.7uF | CC0201 / C0201 | 1:`GND`, 2:`+3V3_FPGA` |
| C109 | 4.7uF | CC0201 / C0201 | 1:`GND`, 2:`+3V3_FPGA` |
| C110 | 0.47uF | CC0201 / C0201 | 1:`GND`, 2:`+3V3_FPGA` |
| C111 | 0.47uF | CC0201 / C0201 | 1:`GND`, 2:`+3V3_FPGA` |
| C112 | 0.47uF | CC0201 / C0201 | 1:`GND`, 2:`+3V3_FPGA` |
| C113 | 0.47uF | CC0201 / C0201 | 1:`GND`, 2:`+3V3_FPGA` |
| C114 | 10nF | CC0201 / C0201 | 1:`PA_BIAS3_2`, 2:`GND` |
| C115 | 10nF | CC0201 / C0201 | 1:`PA_BIAS4_2`, 2:`GND` |
| C116 | 10nF | CC0201 / C0201 | 1:`PA_BIAS1_3`, 2:`GND` |
| C117 | 10nF | CC0201 / C0201 | 1:`PA_BIAS2_3`, 2:`GND` |
| C118 | 10nF | CC0201 / C0201 | 1:`PA_BIAS3_3`, 2:`GND` |
| C119 | 10nF | CC0201 / C0201 | 1:`PA_BIAS4_3`, 2:`GND` |
| C120 | 10nF | CC0201 / C0201 | 1:`PA_BIAS1_4`, 2:`GND` |
| C121 | 10nF | CC0201 / C0201 | 1:`PA_BIAS2_4`, 2:`GND` |
| C122 | 10nF | CC0201 / C0201 | 1:`PA_BIAS3_4`, 2:`GND` |
| C123 | 10nF | CC0201 / C0201 | 1:`PA_BIAS4_4`, 2:`GND` |
| C124 | 100pF | CC0201 / C0201 | 1:`+3V4`, 2:`GND` |
| C125 | 0.1uF | CC0201 / C0201 | 1:`+3V4`, 2:`GND` |
| C126 | 1pF | CC0201 / C0201 | 1:`N$133`, 2:`N$130` |
| C127 | 32.8pF | CC0201 / C0201 | 1:`DAC_IOUT_P`, 2:`DAC_IOUT_N` |
| C128 | 1pF | CC0201 / C0201 | 1:`N$132`, 2:`N$134` |
| C129 | 1pF | CC0201 / C0201 | 1:`N$131`, 2:`ANT2_1` |
| C130 | 100pF | CC0201 / C0201 | 1:`-3V4`, 2:`GND` |
| C131 | 0.1uF | CC0201 / C0201 | 1:`-3V4`, 2:`GND` |
| C132 | 100pF | CC0201 / C0201 | 1:`+3V4`, 2:`GND` |
| C133 | 0.1uF | CC0201 / C0201 | 1:`+3V4`, 2:`GND` |
| C134 | 1pF | CC0201 / C0201 | 1:`N$138`, 2:`N$135` |
| C135 | 1pF | CC0201 / C0201 | 1:`N$137`, 2:`N$139` |
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
| C273 | 4.7nF | CC0201 / C0201 | 1:`GND`, 2:`N$245` |
| C274 | 18pF | CC0201 / C0201 | 1:`N$72`, 2:`N$24` |
| C275 | 4.7nF | CC0201 / C0201 | 1:`GND`, 2:`N$250` |
| C276 | 1µF | CC0201 / C0201 | 1:`N$252`, 2:`GND` |
| C277 | 0.1µF | CC0201 / C0201 | 1:`N$251`, 2:`GND` |
| C278 | 0.1µF | CC0201 / C0201 | 1:`N$253`, 2:`GND` |
| C279 | 100nF | CC0201 / C0201 | 1:`+3V3`, 2:`GND` |
| C280 | 4.7nF | CC0201 / C0201 | 1:`GND`, 2:`N$259` |
| C281 | 100nF | CC0201 / C0201 | 1:`+3V3`, 2:`GND` |
| C282 | 4.7nF | CC0201 / C0201 | 1:`GND`, 2:`N$265` |
| C283 | 22µF | C-EUC1206 / C1206 | 1:`+3V3_AN`, 2:`GND` |
| C284 | 4.7nF | CC0201 / C0201 | 1:`GND`, 2:`N$269` |
| C285 | 47uF | CC0201 / C0201 | 1:`GND`, 2:`+1V8_FPGA` |
| C286 | 4.7nF | CC0201 / C0201 | 1:`GND`, 2:`N$273` |
| C287 | 4.7uF | CC0201 / C0201 | 1:`GND`, 2:`+1V8_FPGA` |
| C288 | 4.7nF | CC0201 / C0201 | 1:`GND`, 2:`N$277` |
| C289 | 4.7uF | CC0201 / C0201 | 1:`GND`, 2:`+1V8_FPGA` |
| C290 | 4.7nF | CC0201 / C0201 | 1:`GND`, 2:`N$281` |
| C291 | 0.47uF | CC0201 / C0201 | 1:`GND`, 2:`+1V8_FPGA` |
| C292 | 4.7nF | CC0201 / C0201 | 1:`GND`, 2:`N$285` |
| C293 | 0.1uF | CC0201 / C0201 | 1:`GND`, 2:`+1V8_CLOCK_F` |
| C294 | 4.7nF | CC0201 / C0201 | 1:`GND`, 2:`N$289` |
| C295 | 0.1µF | CC0201 / C0201 | 1:`N$290`, 2:`GND` |
| C296 | 1µF | CC0201 / C0201 | 1:`N$291`, 2:`GND` |
| C297 | 0.1µF | CC0201 / C0201 | 1:`N$292`, 2:`GND` |
| C298 | 100nF | CC0201 / C0201 | 1:`+3V3_AN4_F`, 2:`GND` |
| C299 | 0.1µF | CC0201 / C0201 | 1:`N$302`, 2:`GND` |
| C300 | 1µF | CC0201 / C0201 | 1:`N$303`, 2:`GND` |
| C301 | 0.1µF | CC0201 / C0201 | 1:`N$304`, 2:`GND` |
| C302 | 100nF | CC0201 / C0201 | 1:`+3V3_AN4_F`, 2:`GND` |
| C303 | 100nF | CC0201 / C0201 | 1:`+3V3_AN4_F`, 2:`GND` |
| C304 | 100nF | CC0201 / C0201 | 1:`+3V3_AN4_F`, 2:`GND` |
| C305 | 100nF | CC0201 / C0201 | 1:`+3V3_AN4_F`, 2:`GND` |
| C306 | 100nF | CC0201 / C0201 | 1:`+3V3_AN4_F`, 2:`GND` |
| C307 | 100nF | CC0201 / C0201 | 1:`+3V3_AN4_F`, 2:`GND` |
| C308 | 22pF | CC0201 / C0201 | 1:`DAC_IOUT_N`, 2:`GND` |
| C309 | 22pF | CC0201 / C0201 | 1:`DAC_IOUT_P`, 2:`GND` |
| C310 | 100nF | CC0201 / C0201 | 1:`+3V3_AN4_F`, 2:`GND` |
| C311 | 22µF | C-EUC1206 / C1206 | 1:`+1V8_CLOCK`, 2:`GND` |
| C312 | 10µF | C-EUC0805 / C0805 | 1:`+1V8_CLOCK_F`, 2:`GND` |
| C313 | 100nF | C-EUC0402 / C0402 | 1:`+1V8_CLOCK_F`, 2:`GND` |
| C314 | 1nF | C-EUC0402 / C0402 | 1:`+1V8_CLOCK_F`, 2:`GND` |
| C315 | 22µF | C-EUC1206 / C1206 | 1:`+3V3_ADAR12`, 2:`GND` |
| C316 | 10µF | C-EUC0805 / C0805 | 1:`+3V3_ADAR1_F`, 2:`GND` |
| C317 | 100nF | C-EUC0402 / C0402 | 1:`+3V3_ADAR1_F`, 2:`GND` |
| C318 | 1nF | C-EUC0402 / C0402 | 1:`+3V3_ADAR1_F`, 2:`GND` |
| C319 | 10µF | C-EUC0805 / C0805 | 1:`+3V3_ADAR2_F`, 2:`GND` |
| C320 | 100nF | C-EUC0402 / C0402 | 1:`+3V3_ADAR2_F`, 2:`GND` |
| C321 | 1nF | C-EUC0402 / C0402 | 1:`+3V3_ADAR2_F`, 2:`GND` |
| C322 | 22µF | C-EUC1206 / C1206 | 1:`+3V3_ADAR34`, 2:`GND` |
| C323 | 10µF | C-EUC0805 / C0805 | 1:`+3V3_ADAR3_F`, 2:`GND` |
| C324 | 100nF | C-EUC0402 / C0402 | 1:`+3V3_ADAR3_F`, 2:`GND` |
| C325 | 1nF | C-EUC0402 / C0402 | 1:`+3V3_ADAR3_F`, 2:`GND` |
| C326 | 10µF | C-EUC0805 / C0805 | 1:`+3V3_ADAR4_F`, 2:`GND` |
| C327 | 100nF | C-EUC0402 / C0402 | 1:`+3V3_ADAR4_F`, 2:`GND` |
| C328 | 1nF | C-EUC0402 / C0402 | 1:`+3V3_ADAR4_F`, 2:`GND` |
| C329 | 22µF | C-EUC1206 / C1206 | 1:`+3V3_AN`, 2:`GND` |
| C330 | 10µF | C-EUC0805 / C0805 | 1:`+3V3_AN1_F`, 2:`GND` |
| C331 | 100nF | C-EUC0402 / C0402 | 1:`+3V3_AN1_F`, 2:`GND` |
| C332 | 1nF | C-EUC0402 / C0402 | 1:`+3V3_AN1_F`, 2:`GND` |
| C333 | 10µF | C-EUC0805 / C0805 | 1:`+3V3_AN2_F`, 2:`GND` |
| C334 | 100nF | C-EUC0402 / C0402 | 1:`+3V3_AN2_F`, 2:`GND` |
| C335 | 1nF | C-EUC0402 / C0402 | 1:`+3V3_AN2_F`, 2:`GND` |
| C336 | 10µF | C-EUC0805 / C0805 | 1:`+3V3_AN3_F`, 2:`GND` |
| C337 | 100nF | C-EUC0402 / C0402 | 1:`+3V3_AN3_F`, 2:`GND` |
| C338 | 10µF | C-EUC0805 / C0805 | 1:`+3V3_AN4_F`, 2:`GND` |
| C339 | 100nF | C-EUC0402 / C0402 | 1:`+3V3_AN4_F`, 2:`GND` |
| C340 | 10µF | C-EUC0805 / C0805 | 1:`+3V3_AN4_F`, 2:`GND` |
| C341 | 100nF | C-EUC0402 / C0402 | 1:`+3V3_AN4_F`, 2:`GND` |
| C342 | 100nF | C-EUC0402 / C0402 | 1:`+3V3_AN5_F`, 2:`GND` |
| C343 | 100nF | C-EUC0402 / C0402 | 1:`+3V3_AN5_F`, 2:`GND` |
| C344 | 100nF | C-EUC0402 / C0402 | 1:`+3V3_AN5_F`, 2:`GND` |
| C345 | 100nF | C-EUC0402 / C0402 | 1:`+3V3_AN5_F`, 2:`GND` |
| C346 | 100nF | C-EUC0402 / C0402 | 1:`+3V3_AN6_F`, 2:`GND` |
| C347 | 100nF | C-EUC0402 / C0402 | 1:`+3V3_AN6_F`, 2:`GND` |
| C348 | 100nF | C-EUC0402 / C0402 | 1:`+3V3_AN6_F`, 2:`GND` |
| C349 | 100nF | C-EUC0402 / C0402 | 1:`+3V3_AN6_F`, 2:`GND` |
| C350 | 100nF | C-EUC0402 / C0402 | 1:`+3V3_AN6_F`, 2:`GND` |
| C351 | 100nF | C-EUC0402 / C0402 | 1:`+3V3_AN6_F`, 2:`GND` |
| D2 | Blue | LED-BLUE0603 / LED-0603 | A:`N$95`, C:`GND` |
| D3 | Blue | LED-BLUE0603 / LED-0603 | A:`N$92`, C:`GND` |
| D4 | Blue | LED-BLUE0603 / LED-0603 | A:`N$97`, C:`GND` |
| D5 | Blue | LED-BLUE0603 / LED-0603 | A:`N$98`, C:`GND` |
| J1 |  | 142-0731-211 / 1420731211 | 1:`FPGA_SYS_CLOCK`, 2:`GND`, 3:`GND`, 4:`GND`, 5:`GND` |
| J18 |  | 142-0731-211 / 1420731211 | 1:`FPGA_DAC_CLOCK`, 2:`GND`, 3:`GND`, 4:`GND`, 5:`GND` |
| J19 |  | CJT-T-P-HH-ST-TH1 / CJTTPHHSTTH1 | 1:`FPGA_ADC_CLOCK_P`, 2:`FPGA_ADC_CLOCK_N`, MH1:`GND`, MH2:`GND`, MH3:`GND`, MH4:`GND` |
| J20 |  | 142-0731-211 / 1420731211 | 1:`DAC_CLOCK`, 2:`GND`, 3:`GND`, 4:`GND`, 5:`GND` |
| J21 |  | CJT-T-P-HH-ST-TH1 / CJTTPHHSTTH1 | 1:`N$2_P`, 2:`N$2_N`, MH1:`GND`, MH2:`GND`, MH3:`GND`, MH4:`GND` |
| J22 |  | 142-0731-211 / 1420731211 | 1:`N$24`, 2:`GND`, 3:`GND`, 4:`GND`, 5:`GND` |
| J23 |  | 142-0731-211 / 1420731211 | 1:`N$23`, 2:`GND`, 3:`GND`, 4:`GND`, 5:`GND` |
| J24 |  | 142-0731-211 / 1420731211 | 1:`N$129`, 2:`GND`, 3:`GND`, 4:`GND`, 5:`GND` |
| J25 |  | 142-0731-211 / 1420731211 | 1:`N$128`, 2:`GND`, 3:`GND`, 4:`GND`, 5:`GND` |
| J26 |  | 142-0731-211 / 1420731211 | 1:`N$134`, 2:`GND`, 3:`GND`, 4:`GND`, 5:`GND` |
| J27 |  | 142-0731-211 / 1420731211 | 1:`N$133`, 2:`GND`, 3:`GND`, 4:`GND`, 5:`GND` |
| J28 |  | 142-0731-211 / 1420731211 | 1:`N$139`, 2:`GND`, 3:`GND`, 4:`GND`, 5:`GND` |
| J29 |  | 142-0731-211 / 1420731211 | 1:`N$138`, 2:`GND`, 3:`GND`, 4:`GND`, 5:`GND` |
| J30 |  | 142-0731-211 / 1420731211 | 1:`N$144`, 2:`GND`, 3:`GND`, 4:`GND`, 5:`GND` |
| J31 |  | 142-0731-211 / 1420731211 | 1:`N$143`, 2:`GND`, 3:`GND`, 4:`GND`, 5:`GND` |
| J32 |  | 142-0731-211 / 1420731211 | 1:`N$149`, 2:`GND`, 3:`GND`, 4:`GND`, 5:`GND` |
| J33 |  | 142-0731-211 / 1420731211 | 1:`N$148`, 2:`GND`, 3:`GND`, 4:`GND`, 5:`GND` |
| J34 |  | 142-0731-211 / 1420731211 | 1:`N$154`, 2:`GND`, 3:`GND`, 4:`GND`, 5:`GND` |
| J35 |  | 142-0731-211 / 1420731211 | 1:`N$153`, 2:`GND`, 3:`GND`, 4:`GND`, 5:`GND` |
| J36 |  | 142-0731-211 / 1420731211 | 1:`N$159`, 2:`GND`, 3:`GND`, 4:`GND`, 5:`GND` |
| J37 |  | 142-0731-211 / 1420731211 | 1:`N$158`, 2:`GND`, 3:`GND`, 4:`GND`, 5:`GND` |
| J38 |  | 142-0731-211 / 1420731211 | 1:`N$164`, 2:`GND`, 3:`GND`, 4:`GND`, 5:`GND` |
| J39 |  | 142-0731-211 / 1420731211 | 1:`N$163`, 2:`GND`, 3:`GND`, 4:`GND`, 5:`GND` |
| J40 |  | 142-0731-211 / 1420731211 | 1:`N$169`, 2:`GND`, 3:`GND`, 4:`GND`, 5:`GND` |
| J41 |  | 142-0731-211 / 1420731211 | 1:`N$168`, 2:`GND`, 3:`GND`, 4:`GND`, 5:`GND` |
| J42 |  | 142-0731-211 / 1420731211 | 1:`N$174`, 2:`GND`, 3:`GND`, 4:`GND`, 5:`GND` |
| J43 |  | 142-0731-211 / 1420731211 | 1:`N$173`, 2:`GND`, 3:`GND`, 4:`GND`, 5:`GND` |
| J44 |  | 142-0731-211 / 1420731211 | 1:`N$179`, 2:`GND`, 3:`GND`, 4:`GND`, 5:`GND` |
| J45 |  | 142-0731-211 / 1420731211 | 1:`N$178`, 2:`GND`, 3:`GND`, 4:`GND`, 5:`GND` |
| J46 |  | 142-0731-211 / 1420731211 | 1:`N$184`, 2:`GND`, 3:`GND`, 4:`GND`, 5:`GND` |
| J47 |  | 142-0731-211 / 1420731211 | 1:`N$183`, 2:`GND`, 3:`GND`, 4:`GND`, 5:`GND` |
| J48 |  | 142-0731-211 / 1420731211 | 1:`N$189`, 2:`GND`, 3:`GND`, 4:`GND`, 5:`GND` |
| J49 |  | 142-0731-211 / 1420731211 | 1:`N$188`, 2:`GND`, 3:`GND`, 4:`GND`, 5:`GND` |
| J50 |  | 142-0731-211 / 1420731211 | 1:`N$194`, 2:`GND`, 3:`GND`, 4:`GND`, 5:`GND` |
| J51 |  | 142-0731-211 / 1420731211 | 1:`N$193`, 2:`GND`, 3:`GND`, 4:`GND`, 5:`GND` |
| J52 |  | 142-0731-211 / 1420731211 | 1:`N$199`, 2:`GND`, 3:`GND`, 4:`GND`, 5:`GND` |
| J53 |  | 142-0731-211 / 1420731211 | 1:`N$198`, 2:`GND`, 3:`GND`, 4:`GND`, 5:`GND` |
| J54 |  | 142-0731-211 / 1420731211 | 1:`N$204`, 2:`GND`, 3:`GND`, 4:`GND`, 5:`GND` |
| J55 |  | 142-0731-211 / 1420731211 | 1:`N$203`, 2:`GND`, 3:`GND`, 4:`GND`, 5:`GND` |
| JP1 |  | PINHD-2X6 / 2X06 | 1:`AD9523_PD`, 2:`AD9523_REF_SEL`, 3:`AD9523_SYNC`, 4:`AD9523_RESET`, 5:`AD9523_CS`, 6:`STM32_SCLK4`, 7:`STM32_MOSI4`, 8:`STM32_MISO4`, 9:`AD9523_STATUS0`, 10:`AD9523_STATUS1`, 11:`AD9523_EEPROM_SEL`, 12:`GND` |
| JP2 |  | PINHD-1X6 / 1X06 | 1:`+3V3`, 2:`STM32_SWCLK`, 3:`GND`, 4:`STM32_SWDIO`, 5:`STM32_NRST`, 6:`STM32_SWO` |
| JP3 |  | PINHD-2X4 / 2X04 | 1:`N$32`, 2:`+3V3_FPGA`, 3:`N$33`, 5:`N$34`, 7:`N$36`, 8:`GND` |
| JP4 |  | PINHD-1X3 / 1X03 | 1:`EN/DIS_COOLING`, 3:`GND` |
| JP5 |  | PINHD-1X3 / 1X03 | 1:`+3V3_AN4_F`, 2:`N$295`, 3:`GND` |
| JP6 |  | PINHD-1X3 / 1X03 | 1:`+3V3_AN4_F`, 2:`N$296`, 3:`GND` |
| JP7 |  | PINHD-1X8 / 1X08 | 2:`+3V3`, 3:`GND`, 4:`STM32_SCL3`, 5:`STM32_SDA3`, 6:`MAG_DRDY`, 7:`ACC_INT`, 8:`GYR_INT` |
| JP8 |  | PINHD-1X4 / 1X04 | 1:`+3V3`, 2:`STM32_TX5`, 3:`STM32_RX5`, 4:`GND` |
| JP9 |  | PINHD-1X4 / 1X04 | 1:`GND`, 2:`STEPPER_CW+`, 3:`GND`, 4:`STEPPER_CLK+` |
| JP10 |  | PINHD-1X3 / 1X03 | 1:`EN/DIS_RFPA_VDD`, 3:`GND` |
| JP11 |  | PINHD-1X3 / 1X03 | 1:`+3V3_AN4_F`, 2:`N$306`, 3:`GND` |
| JP12 |  | PINHD-1X3 / 1X03 | 1:`+3V3_AN4_F`, 2:`N$298`, 3:`GND` |
| JP13 |  | PINHD-2X7 / 2X07 | 1:`STM32_MISO4`, 2:`STM32_SCLK4`, 3:`STM32_MOSI4`, 4:`ADF4382_TX_CS`, 5:`ADF4382_TX_CE`, 6:`ADF4382_TX_DELSTR`, 7:`ADF4382_TX_DELADJ`, 8:`ADF4382_TX_LKDET`, 9:`ADF4382_RX_CS`, 10:`ADF4382_RX_CE`, 11:`ADF4382_RX_DELSTR`, 12:`ADF4382_RX_DELADJ`, 13:`ADF4382_RX_LKDET`, 14:`GND` |
| JP14 |  | PINHD-1X3 / 1X03 | 1:`+3V3_AN4_F`, 2:`N$299`, 3:`GND` |
| JP15 |  | PINHD-1X3 / 1X03 | 1:`+3V3_AN4_F`, 2:`N$307`, 3:`GND` |
| JP16 |  | PINHD-1X3 / 1X03 | 1:`+3V3_AN4_F`, 2:`N$301`, 3:`GND` |
| JP17 |  | PINHD-1X3 / 1X03 | 1:`STM32_TX3`, 2:`STM32_RX3`, 3:`GND` |
| JP18 |  | PINHD-1X4 / 1X04 | 1:`STM32_SDA3`, 2:`STM32_SCL3`, 3:`GND`, 4:`+3V3` |
| JP19 |  | PINHD-1X3 / 1X03 | 1:`+3V3_AN4_F`, 2:`N$297`, 3:`GND` |
| JP20 |  | PINHD-1X2 / 1X02 | 1:`FPGA_CLOCK_TEST`, 2:`GND` |
| L1 |  | L-EUL5650M / L5650M | 1:`+1V8_CLOCK`, 2:`+1V8_CLOCK_F` |
| L2 | 12nH | LL0201 / L0201 | 1:`N$305`, 2:`N$300` |
| L3 | 159nH | LL0201 / L0201 | 1:`N$113`, 2:`N$58` |
| L4 | 159nH | LL0201 / L0201 | 1:`N$125`, 2:`N$62` |
| L5 |  | BLM15H / 0402 | 1:`N$9`, 2:`+3V3` |
| L6 |  | BLM15H / 0402 | 1:`DAC_AVDD`, 2:`+3V3_AN` |
| L7 |  | BLM15H / 0402 | 1:`DAC_ACOM`, 2:`GND` |
| L8 | 12nH | LL0201 / L0201 | 1:`N$125`, 2:`N$113` |
| L9 | 50nH | LL0201 / L0201 | 1:`AMP_IN_P`, 2:`N$71` |
| L10 | 50nH | LL0201 / L0201 | 1:`AMP_IN_N`, 2:`N$82` |
| L11 |  | L-EUL5650M / L5650M | 1:`+3V3_ADAR12`, 2:`+3V3_ADAR1_F` |
| L12 |  | L-EUL5650M / L5650M | 1:`+3V3_ADAR12`, 2:`+3V3_ADAR2_F` |
| L13 |  | L-EUL5650M / L5650M | 1:`+3V3_ADAR34`, 2:`+3V3_ADAR3_F` |
| L14 |  | L-EUL5650M / L5650M | 1:`+3V3_ADAR34`, 2:`+3V3_ADAR4_F` |
| L15 |  | L-EUL5650M / L5650M | 1:`+3V3_AN`, 2:`+3V3_AN1_F` |
| L16 |  | L-EUL5650M / L5650M | 1:`+3V3_AN`, 2:`+3V3_AN2_F` |
| L17 |  | L-EUL5650M / L5650M | 1:`+3V3_AN`, 2:`+3V3_AN3_F` |
| L18 |  | L-EUL5650M / L5650M | 1:`+3V3_AN`, 2:`+3V3_AN4_F` |
| L19 |  | L-EUL5650M / L5650M | 1:`+3V3_FPGA`, 2:`+3V3_FT` |
| L21 |  | L-EUL5650M / L5650M | 1:`+3V3_AN`, 2:`+3V3_AN5_F` |
| L22 | 107.3nH | LL0201 / L0201 | 1:`DAC_IOUT_P`, 2:`N$99` |
| L23 |  | L-EUL5650M / L5650M | 1:`+3V3_AN`, 2:`+3V3_AN6_F` |
| L24 | 50nH | LL0201 / L0201 | 1:`N$300`, 2:`N$308` |
| L25 | 107.3nH | LL0201 / L0201 | 1:`DAC_IOUT_N`, 2:`N$101` |
| L26 | 107.3nH | LL0201 / L0201 | 1:`N$99`, 2:`DAC_IOUT_F_P` |
| L27 | 107.3nH | LL0201 / L0201 | 1:`N$101`, 2:`DAC_IOUT_F_N` |
| L28 | 50nH | LL0201 / L0201 | 1:`N$305`, 2:`N$309` |
| OPA_1 |  | OPA4703EA/250 / PW14 | 1:`VG_15`, 2:`N$254`, 3:`GND`, 4:`+5V5_PA`, 5:`GND`, 6:`N$256`, 7:`VG_13`, 8:`VG_11`, 9:`N$260`, 10:`GND`, 11:`-5V5_PA`, 12:`GND`, 13:`N$263`, 14:`VG_9` |
| OPA_2 |  | OPA4703EA/250 / PW14 | 1:`VG_7`, 2:`N$222`, 3:`GND`, 4:`+5V5_PA`, 5:`GND`, 6:`N$224`, 7:`VG_5`, 8:`VG_3`, 9:`N$228`, 10:`GND`, 11:`-5V5_PA`, 12:`GND`, 13:`N$231`, 14:`VG_1` |
| OPA_3 |  | OPA4703EA/250 / PW14 | 1:`VG_14`, 2:`N$238`, 3:`GND`, 4:`+5V5_PA`, 5:`GND`, 6:`N$240`, 7:`VG_16`, 8:`VG_10`, 9:`N$244`, 10:`GND`, 11:`-5V5_PA`, 12:`GND`, 13:`N$247`, 14:`VG_12` |
| OPA_4 |  | OPA4703EA/250 / PW14 | 1:`VG_6`, 2:`N$206`, 3:`GND`, 4:`+5V5_PA`, 5:`GND`, 6:`N$208`, 7:`VG_8`, 8:`VG_2`, 9:`N$213`, 10:`GND`, 11:`-5V5_PA`, 12:`GND`, 13:`N$216`, 14:`VG_4` |
| R1 | 24R | R-EU_R0402 / R0402 | 1:`N$4`, 2:`ADC_IF_IN_N` |
| R2 | 100R | RR0201 / R0201 | 1:`ADC_D0_N`, 2:`ADC_D0_P` |
| R3 | 100R | RR0201 / R0201 | 1:`ADC_D1_N`, 2:`ADC_D1_P` |
| R4 | 100R | RR0201 / R0201 | 1:`FPGA_ADC_CLOCK_N`, 2:`FPGA_ADC_CLOCK_P` |
| R5 | 100R | RR0201 / R0201 | 1:`ADC_D3_N`, 2:`ADC_D3_P` |
| R6 | 100R | RR0201 / R0201 | 1:`ADC_D2_N`, 2:`ADC_D2_P` |
| R7 | 100R | RR0201 / R0201 | 1:`ADC_D4_N`, 2:`ADC_D4_P` |
| R8 | 100R | RR0201 / R0201 | 1:`ADC_D6_N`, 2:`ADC_D6_P` |
| R9 | 100R | RR0201 / R0201 | 1:`ADC_D5_N`, 2:`ADC_D5_P` |
| R10 | 100R | RR0201 / R0201 | 1:`ADC_D7_N`, 2:`ADC_D7_P` |
| R11 | 100R | RR0201 / R0201 | 1:`ADC_OR_N`, 2:`ADC_OR_P` |
| R12 | 100R | RR0201 / R0201 | 1:`ADC_DCO_N`, 2:`ADC_DCO_P` |
| R13 | 24R | R-EU_R0402 / R0402 | 1:`N$43`, 2:`ADC_IF_IN_P` |
| R14 | 115R | R-EU_R0201 / R0201 | 1:`N$35`, 2:`N$48` |
| R15 | 4.3k | R-EU_R0201 / R0201 | 1:`N$15`, 2:`N$5` |
| R16 | 200R | RR0201 / R0201 | 1:`N$67`, 2:`ADC_IF_IN_P` |
| R17 | 200R | RR0201 / R0201 | 1:`ADC_IF_IN_N`, 2:`N$67` |
| R18 | 0R | RR0201 / R0201 | 1:`N$78`, 2:`N$50` |
| R19 | 0R | RR0201 / R0201 | 1:`N$49`, 2:`N$73` |
| R20 | 200R | RR0201 / R0201 | 1:`N$110`, 2:`AMP_IF_IN_P` |
| R21 | 200R | RR0201 / R0201 | 1:`AMP_IF_IN_N`, 2:`N$110` |
| R22 | 56R | R-EU_R0201 / R0201 | 1:`N$87`, 2:`N$88` |
| R23 | 22R | RR0201 / R0201 | 1:`DAC_7`, 2:`N$10` |
| R24 | 22R | RR0201 / R0201 | 1:`DAC_6`, 2:`N$11` |
| R25 | 22R | RR0201 / R0201 | 1:`DAC_5`, 2:`N$12` |
| R26 | 22R | RR0201 / R0201 | 1:`DAC_4`, 2:`N$13` |
| R27 | 22R | RR0201 / R0201 | 1:`DAC_3`, 2:`N$14` |
| R28 | 22R | RR0201 / R0201 | 1:`DAC_2`, 2:`N$16` |
| R29 | 22R | RR0201 / R0201 | 1:`DAC_1`, 2:`N$18` |
| R30 | 22R | RR0201 / R0201 | 1:`DAC_0`, 2:`N$19` |
| R31 | 50R | RR0201 / R0201 | 1:`GND`, 2:`DAC_CLOCK` |
| R32 | 4.3k | R-EU_R0201 / R0201 | 1:`N$86`, 2:`N$85` |
| R33 | 3k2 | RR0201 / R0201 | 1:`N$22`, 2:`GND` |
| R34 | 0R | RR0201 / R0201 | 1:`N$112`, 2:`N$103` |
| R35 | 0R | RR0201 / R0201 | 1:`N$89`, 2:`N$111` |
| R36 | 830R | R-EU_R0402 / R0402 | 1:`N$41`, 2:`ADC_PWRD` |
| R37 | 1k | R-EU_R0402 / R0402 | 1:`GND`, 2:`N$41` |
| R38 | 20k | R-EU_R0402 / R0402 | 1:`GND`, 2:`N$17` |
| R39 | 10k | RR0201 / R0201 | 1:`DAC_2_VG_CLR`, 2:`+3V3_AN3_F` |
| R40 | 10k | RR0201 / R0201 | 1:`DAC_1_VG_CLR`, 2:`+3V3_AN3_F` |
| R41 | 1k | RR0201 / R0201 | 1:`GND`, 2:`N$221` |
| R42 | 4.7k | RR0201 / R0201 | 1:`+3V3_AN3_F`, 2:`DAC_1_VG_LDAC` |
| R43 | 1k | RR0201 / R0201 | 1:`GND`, 2:`N$205` |
| R44 | 4.7k | RR0201 / R0201 | 1:`+3V3_AN3_F`, 2:`DAC_2_VG_LDAC` |
| R45 | 4.7k | RR0201 / R0201 | 1:`N$39`, 2:`GND` |
| R46 | 4.7k | RR0201 / R0201 | 1:`GND`, 2:`ADAR_TX_LOAD_1` |
| R47 | 4.7k | RR0201 / R0201 | 1:`GND`, 2:`ADAR_RX_LOAD_1` |
| R48 | 4.7k | RR0201 / R0201 | 1:`N$40`, 2:`GND` |
| R49 | 22R | RR0201 / R0201 | 1:`FPGA_TMS`, 2:`N$32` |
| R50 | 4.7k | RR0201 / R0201 | 1:`FPGA_FLASH_NRST`, 2:`+3V3_FPGA` |
| R51 | 22R | RR0201 / R0201 | 1:`N$25`, 2:`FPGA_FLASH_CLK` |
| R52 | 4.7k | RR0201 / R0201 | 1:`FPGA_FLASH_NCS`, 2:`+3V3_FPGA` |
| R53 | 4.7k | RR0201 / R0201 | 1:`FPGA_FLASH_DQ2`, 2:`+3V3_FPGA` |
| R54 | 4.7k | RR0201 / R0201 | 1:`+3V3_FPGA`, 2:`FPGA_FLASH_DQ3` |
| R55 | 1k | RR0201 / R0201 | 1:`N$80`, 2:`GND` |
| R56 | 1k | RR0201 / R0201 | 1:`N$81`, 2:`GND` |
| R57 | 1k | RR0201 / R0201 | 1:`N$84`, 2:`GND` |
| R58 | 1k | RR0201 / R0201 | 1:`N$83`, 2:`GND` |
| R59 | 1k | RR0201 / R0201 | 1:`N$222`, 2:`DAC_VOUT_VG_7` |
| R60 | 33R | RR0201 / R0201 |  |
| R61 | 33R | RR0201 / R0201 |  |
| R62 | 22R | RR0201 / R0201 | 1:`FPGA_TCK`, 2:`N$33` |
| R63 | 22R | RR0201 / R0201 | 1:`FPGA_TDO`, 2:`N$34` |
| R64 | 22R | RR0201 / R0201 | 1:`FPGA_TDI`, 2:`N$36` |
| R65 | 4.7k | RR0201 / R0201 | 1:`FPGA_TDI`, 2:`+3V3_FPGA` |
| R66 | 4.7k | RR0201 / R0201 | 1:`FPGA_TDO`, 2:`+3V3_FPGA` |
| R67 | 4.7k | RR0201 / R0201 | 1:`FPGA_TCK`, 2:`+3V3_FPGA` |
| R68 | 4.7k | RR0201 / R0201 | 1:`FPGA_TMS`, 2:`+3V3_FPGA` |
| R69 | 4.7k | RR0201 / R0201 | 1:`FPGA_PUDC_B`, 2:`+3V3_FPGA` |
| R70 | 4.7k | RR0201 / R0201 | 1:`GND`, 2:`ADAR_TX_LOAD_2` |
| R71 | 4.7k | RR0201 / R0201 | 1:`GND`, 2:`ADAR_RX_LOAD_2` |
| R72 | 4.7k | RR0201 / R0201 | 1:`N$57`, 2:`GND` |
| R73 | 4.7k | RR0201 / R0201 | 1:`GND`, 2:`ADAR_TX_LOAD_3` |
| R74 | 4.7k | RR0201 / R0201 | 1:`GND`, 2:`ADAR_RX_LOAD_3` |
| R75 | 4.7k | RR0201 / R0201 | 1:`N$64`, 2:`GND` |
| R76 | 4.7k | RR0201 / R0201 | 1:`GND`, 2:`ADAR_TX_LOAD_4` |
| R77 | 4.7k | RR0201 / R0201 | 1:`GND`, 2:`ADAR_RX_LOAD_4` |
| R78 | 840R | RR0201 / R0201 | 1:`+3V3_ADAR2_F`, 2:`N$80` |
| R79 | 840R | RR0201 / R0201 | 1:`+3V3_ADAR3_F`, 2:`N$81` |
| R80 | 840R | RR0201 / R0201 | 1:`+3V3_ADAR4_F`, 2:`N$84` |
| R81 | 840R | RR0201 / R0201 | 1:`+3V3_ADAR4_F`, 2:`N$83` |
| R82 | 1k | RR0201 / R0201 | 1:`N$224`, 2:`DAC_VOUT_VG_5` |
| R83 | 33R | RR0201 / R0201 |  |
| R84 | 33R | RR0201 / R0201 |  |
| R85 | 1k | RR0201 / R0201 | 1:`N$206`, 2:`DAC_VOUT_VG_6` |
| R86 | 1k | RR0201 / R0201 | 1:`N$208`, 2:`DAC_VOUT_VG_8` |
| R87 | 1k | RR0201 / R0201 | 1:`DAC_VOUT_VG_2`, 2:`N$213` |
| R88 | 1k | RR0201 / R0201 | 1:`DAC_VOUT_VG_4`, 2:`N$216` |
| R89 | 2.443k | RR0201 / R0201 | 1:`N$206`, 2:`VG_6` |
| R90 | 2.443k | RR0201 / R0201 | 1:`N$208`, 2:`VG_8` |
| R91 | 2.443k | RR0201 / R0201 | 1:`VG_2`, 2:`N$213` |
| R92 | 2.443k | RR0201 / R0201 | 1:`VG_4`, 2:`N$216` |
| R93 | 1k | RR0201 / R0201 | 1:`DAC_VOUT_VG_3`, 2:`N$228` |
| R94 | 1k | RR0201 / R0201 | 1:`DAC_VOUT_VG_1`, 2:`N$231` |
| R95 | 2.443k | RR0201 / R0201 | 1:`N$222`, 2:`VG_7` |
| R96 | 2.443k | RR0201 / R0201 | 1:`N$224`, 2:`VG_5` |
| R97 | 2.443k | RR0201 / R0201 | 1:`VG_3`, 2:`N$228` |
| R98 | 2.443k | RR0201 / R0201 | 1:`VG_1`, 2:`N$231` |
| R99 | 1k | RR0201 / R0201 | 1:`N$238`, 2:`DAC_VOUT_VG_14` |
| R100 | 1k | RR0201 / R0201 | 1:`N$240`, 2:`DAC_VOUT_VG_16` |
| R101 | 1k | RR0201 / R0201 | 1:`DAC_VOUT_VG_10`, 2:`N$244` |
| R102 | 1k | RR0201 / R0201 | 1:`DAC_VOUT_VG_12`, 2:`N$247` |
| R103 | 2.443k | RR0201 / R0201 | 1:`N$238`, 2:`VG_14` |
| R104 | 2.443k | RR0201 / R0201 | 1:`N$240`, 2:`VG_16` |
| R105 | 2.443k | RR0201 / R0201 | 1:`VG_10`, 2:`N$244` |
| R106 | 2.443k | RR0201 / R0201 | 1:`VG_12`, 2:`N$247` |
| R107 | 1k | RR0201 / R0201 | 1:`N$254`, 2:`DAC_VOUT_VG_15` |
| R108 | 1k | RR0201 / R0201 | 1:`N$256`, 2:`DAC_VOUT_VG_13` |
| R109 | 1k | RR0201 / R0201 | 1:`DAC_VOUT_VG_11`, 2:`N$260` |
| R110 | 500R | RR0201 / R0201 | 1:`N$98`, 2:`N$52` |
| R111 | 10k | RR0201 / R0201 | 1:`STM32_NRST`, 2:`+3V3` |
| R112 | 500R | RR0201 / R0201 | 1:`N$97`, 2:`N$91` |
| R113 | 500R | RR0201 / R0201 | 1:`N$95`, 2:`N$93` |
| R114 | 500R | RR0201 / R0201 | 1:`N$92`, 2:`N$94` |
| R115 | 50R | RR0201 / R0201 | 1:`GND`, 2:`DAC_IOUT_N` |
| R116 | 50R | RR0201 / R0201 | 1:`GND`, 2:`DAC_IOUT_P` |
| R117 | 4.7k | RR0201 / R0201 | 1:`GND`, 2:`DAC_SLEEP` |
| R118 | 1k | RR0201 / R0201 | 1:`DAC_VOUT_VG_9`, 2:`N$263` |
| R119 | 2.443k | RR0201 / R0201 | 1:`N$254`, 2:`VG_15` |
| R120 | 2.443k | RR0201 / R0201 | 1:`N$256`, 2:`VG_13` |
| R121 | 2.443k | RR0201 / R0201 | 1:`VG_11`, 2:`N$260` |
| R122 | 2.443k | RR0201 / R0201 | 1:`VG_9`, 2:`N$263` |
| R123 | 10k | RR0201 / R0201 | 1:`N$1`, 2:`+3V3_AN3_F` |
| R124 | 1k | RR0201 / R0201 | 1:`N$211`, 2:`N$210` |
| R125 | 1k | RR0201 / R0201 | 1:`N$217`, 2:`N$215` |
| R126 | 1k | RR0201 / R0201 | 1:`N$223`, 2:`N$220` |
| R127 | 1k | RR0201 / R0201 | 1:`N$229`, 2:`N$227` |
| R128 | 1k | RR0201 / R0201 | 1:`N$234`, 2:`N$233` |
| R129 | 1k | RR0201 / R0201 | 1:`N$239`, 2:`N$237` |
| R130 | 1k | RR0201 / R0201 | 1:`N$245`, 2:`N$243` |
| R131 | 1k | RR0201 / R0201 | 1:`N$250`, 2:`N$249` |
| R132 | 5R | RR0201 / R0201 | 1:`+3V3_AN4_F`, 2:`N$252` |
| R133 | 1k | RR0201 / R0201 | 1:`N$259`, 2:`N$258` |
| R134 | 1k | RR0201 / R0201 | 1:`N$265`, 2:`N$264` |
| R135 | 1k | RR0201 / R0201 | 1:`N$269`, 2:`N$268` |
| R136 | 1k | RR0201 / R0201 | 1:`N$273`, 2:`N$272` |
| R137 | 1k | RR0201 / R0201 | 1:`N$277`, 2:`N$276` |
| R138 | 1k | RR0201 / R0201 | 1:`+3V3_FPGA`, 2:`N$106` |
| R139 | 1k | RR0201 / R0201 | 1:`GND`, 2:`N$107` |
| R140 | 1k | RR0201 / R0201 | 1:`GND`, 2:`N$108` |
| R141 | 4.7k | RR0201 / R0201 | 1:`+3V3_FPGA`, 2:`N$109` |
| R142 | 4.7k | RR0201 / R0201 | 1:`+3V3_FPGA`, 2:`N$114` |
| R143 | 4.7k | RR0201 / R0201 | 1:`N$116`, 2:`+3V3_FPGA` |
| R144 | 1k | RR0201 / R0201 | 1:`N$115`, 2:`+3V3_FPGA` |
| R145 | 33R | RR0201 / R0201 |  |
| R146 | 33R | RR0201 / R0201 |  |
| R147 | 1k | RR0201 / R0201 | 1:`N$281`, 2:`N$280` |
| R148 | 1k | RR0201 / R0201 | 1:`N$285`, 2:`N$284` |
| R149 | 1k | RR0201 / R0201 | 1:`N$289`, 2:`N$288` |
| R150 | 5R | RR0201 / R0201 | 1:`+3V3_AN4_F`, 2:`N$291` |
| R151 | 10k | RR0201 / R0201 | 1:`N$293`, 2:`N$291` |
| R152 | 5R | RR0201 / R0201 | 1:`+3V3_AN4_F`, 2:`N$303` |
| R153 | 10k | RR0201 / R0201 | 1:`N$294`, 2:`N$303` |
| R154 | 22.1k | RR0201 / R0201 | 1:`+1V8_FPGA`, 2:`ADAR_1_CS_1V8` |
| R155 | 22.1k | RR0201 / R0201 | 1:`+1V8_FPGA`, 2:`ADAR_2_CS_1V8` |
| R156 | 22.1k | RR0201 / R0201 | 1:`+1V8_FPGA`, 2:`ADAR_3_CS_1V8` |
| R157 | 22.1k | RR0201 / R0201 | 1:`+1V8_FPGA`, 2:`ADAR_4_CS_1V8` |
| R158 | 22.1k | RR0201 / R0201 | 1:`GND`, 2:`ADAR_TR_1` |
| R159 | 22.1k | RR0201 / R0201 | 1:`GND`, 2:`ADAR_TR_2` |
| R160 | 22.1k | RR0201 / R0201 | 1:`GND`, 2:`ADAR_TR_3` |
| R161 | 22.1k | RR0201 / R0201 | 1:`GND`, 2:`ADAR_TR_4` |
| R162 | 22.1k | RR0201 / R0201 | 1:`GND`, 2:`STM32_SCLK_1V8` |
| R163 | 22.1k | RR0201 / R0201 | 1:`GND`, 2:`STM32_MOSI_1V8` |
| R164 | 22.1k | RR0201 / R0201 | 1:`GND`, 2:`STM32_MISO_1V8` |
| R165 | 25R | RR0201 / R0201 | 1:`AMP_IN_N`, 2:`GND` |
| R166 | 25R | RR0201 / R0201 | 1:`AMP_IN_P`, 2:`GND` |
| R167 | 1k | RR0201 / R0201 | 1:`+3V3`, 2:`STM32_SCL3` |
| R168 | 1k | RR0201 / R0201 | 1:`+3V3`, 2:`STM32_SDA3` |
| R169 | 1k | RR0201 / R0201 | 1:`+3V3`, 2:`STM32_SDA1` |
| R170 | 1k | RR0201 / R0201 | 1:`+3V3`, 2:`STM32_SCL1` |
| R171 | 1k | RR0201 / R0201 | 1:`+3V3`, 2:`STM32_SDA2` |
| R172 | 1k | RR0201 / R0201 | 1:`+3V3`, 2:`STM32_SCL2` |
| R173 | 100R | RR0201 / R0201 | 1:`ADC_CLK_IN_P`, 2:`ADC_CLK_IN_N` |
| RF_SW_1 |  | M3SWA2-34DR+ / 16_QFN | 1:`GND`, 2:`GND`, 3:`N$130`, 4:`GND`, 5:`-3V4`, 6:`M3S_VCTRL`, 7:`GND`, 8:`+3V4`, 9:`GND`, 10:`N$132`, 11:`GND`, 12:`GND`, 13:`GND`, 14:`GND`, 15:`N$131`, 16:`GND`, 17:`GND` |
| RF_SW_2 |  | M3SWA2-34DR+ / 16_QFN | 1:`GND`, 2:`GND`, 3:`N$135`, 4:`GND`, 5:`-3V4`, 6:`M3S_VCTRL`, 7:`GND`, 8:`+3V4`, 9:`GND`, 10:`N$137`, 11:`GND`, 12:`GND`, 13:`GND`, 14:`GND`, 15:`N$136`, 16:`GND`, 17:`GND` |
| RF_SW_3 |  | M3SWA2-34DR+ / 16_QFN | 1:`GND`, 2:`GND`, 3:`N$74`, 4:`GND`, 5:`-3V4`, 6:`M3S_VCTRL`, 7:`GND`, 8:`+3V4`, 9:`GND`, 10:`N$127`, 11:`GND`, 12:`GND`, 13:`GND`, 14:`GND`, 15:`N$100`, 16:`GND`, 17:`GND` |
| RF_SW_4 |  | M3SWA2-34DR+ / 16_QFN | 1:`GND`, 2:`GND`, 3:`N$140`, 4:`GND`, 5:`-3V4`, 6:`M3S_VCTRL`, 7:`GND`, 8:`+3V4`, 9:`GND`, 10:`N$142`, 11:`GND`, 12:`GND`, 13:`GND`, 14:`GND`, 15:`N$141`, 16:`GND`, 17:`GND` |
| RF_SW_5 |  | M3SWA2-34DR+ / 16_QFN | 1:`GND`, 2:`GND`, 3:`N$150`, 4:`GND`, 5:`-3V4`, 6:`M3S_VCTRL`, 7:`GND`, 8:`+3V4`, 9:`GND`, 10:`N$152`, 11:`GND`, 12:`GND`, 13:`GND`, 14:`GND`, 15:`N$151`, 16:`GND`, 17:`GND` |
| RF_SW_6 |  | M3SWA2-34DR+ / 16_QFN | 1:`GND`, 2:`GND`, 3:`N$155`, 4:`GND`, 5:`-3V4`, 6:`M3S_VCTRL`, 7:`GND`, 8:`+3V4`, 9:`GND`, 10:`N$157`, 11:`GND`, 12:`GND`, 13:`GND`, 14:`GND`, 15:`N$156`, 16:`GND`, 17:`GND` |
| RF_SW_7 |  | M3SWA2-34DR+ / 16_QFN | 1:`GND`, 2:`GND`, 3:`N$145`, 4:`GND`, 5:`-3V4`, 6:`M3S_VCTRL`, 7:`GND`, 8:`+3V4`, 9:`GND`, 10:`N$147`, 11:`GND`, 12:`GND`, 13:`GND`, 14:`GND`, 15:`N$146`, 16:`GND`, 17:`GND` |
| RF_SW_8 |  | M3SWA2-34DR+ / 16_QFN | 1:`GND`, 2:`GND`, 3:`N$160`, 4:`GND`, 5:`-3V4`, 6:`M3S_VCTRL`, 7:`GND`, 8:`+3V4`, 9:`GND`, 10:`N$162`, 11:`GND`, 12:`GND`, 13:`GND`, 14:`GND`, 15:`N$161`, 16:`GND`, 17:`GND` |
| RF_SW_9 |  | M3SWA2-34DR+ / 16_QFN | 1:`GND`, 2:`GND`, 3:`N$180`, 4:`GND`, 5:`-3V4`, 6:`M3S_VCTRL`, 7:`GND`, 8:`+3V4`, 9:`GND`, 10:`N$182`, 11:`GND`, 12:`GND`, 13:`GND`, 14:`GND`, 15:`N$181`, 16:`GND`, 17:`GND` |
| RF_SW_10 |  | M3SWA2-34DR+ / 16_QFN | 1:`GND`, 2:`GND`, 3:`N$165`, 4:`GND`, 5:`-3V4`, 6:`M3S_VCTRL`, 7:`GND`, 8:`+3V4`, 9:`GND`, 10:`N$167`, 11:`GND`, 12:`GND`, 13:`GND`, 14:`GND`, 15:`N$166`, 16:`GND`, 17:`GND` |
| RF_SW_11 |  | M3SWA2-34DR+ / 16_QFN | 1:`GND`, 2:`GND`, 3:`N$175`, 4:`GND`, 5:`-3V4`, 6:`M3S_VCTRL`, 7:`GND`, 8:`+3V4`, 9:`GND`, 10:`N$177`, 11:`GND`, 12:`GND`, 13:`GND`, 14:`GND`, 15:`N$176`, 16:`GND`, 17:`GND` |
| RF_SW_12 |  | M3SWA2-34DR+ / 16_QFN | 1:`GND`, 2:`GND`, 3:`N$170`, 4:`GND`, 5:`-3V4`, 6:`M3S_VCTRL`, 7:`GND`, 8:`+3V4`, 9:`GND`, 10:`N$172`, 11:`GND`, 12:`GND`, 13:`GND`, 14:`GND`, 15:`N$171`, 16:`GND`, 17:`GND` |
| RF_SW_13 |  | M3SWA2-34DR+ / 16_QFN | 1:`GND`, 2:`GND`, 3:`N$200`, 4:`GND`, 5:`-3V4`, 6:`M3S_VCTRL`, 7:`GND`, 8:`+3V4`, 9:`GND`, 10:`N$202`, 11:`GND`, 12:`GND`, 13:`GND`, 14:`GND`, 15:`N$201`, 16:`GND`, 17:`GND` |
| RF_SW_14 |  | M3SWA2-34DR+ / 16_QFN | 1:`GND`, 2:`GND`, 3:`N$185`, 4:`GND`, 5:`-3V4`, 6:`M3S_VCTRL`, 7:`GND`, 8:`+3V4`, 9:`GND`, 10:`N$187`, 11:`GND`, 12:`GND`, 13:`GND`, 14:`GND`, 15:`N$186`, 16:`GND`, 17:`GND` |
| RF_SW_15 |  | M3SWA2-34DR+ / 16_QFN | 1:`GND`, 2:`GND`, 3:`N$195`, 4:`GND`, 5:`-3V4`, 6:`M3S_VCTRL`, 7:`GND`, 8:`+3V4`, 9:`GND`, 10:`N$197`, 11:`GND`, 12:`GND`, 13:`GND`, 14:`GND`, 15:`N$196`, 16:`GND`, 17:`GND` |
| RF_SW_16 |  | M3SWA2-34DR+ / 16_QFN | 1:`GND`, 2:`GND`, 3:`N$190`, 4:`GND`, 5:`-3V4`, 6:`M3S_VCTRL`, 7:`GND`, 8:`+3V4`, 9:`GND`, 10:`N$192`, 11:`GND`, 12:`GND`, 13:`GND`, 14:`GND`, 15:`N$191`, 16:`GND`, 17:`GND` |
| S1 |  | MOMENTARY-SWITCH-SPST-SMD-4.6X2.8MM / TACTILE_SWITCH_SMD_4.6X2.8MM | 1 2:`GND`, 3 4:`STM32_NRST` |
| SJ1 |  | SJ2W / SJ_2 | 1:`GND`, 2:`N$6`, 3:`+1V8_CLOCK_F` |
| SV1 |  | MA10-2 / MA10-2 | 1:`EN_+1V0_FPGA`, 2:`EN_+5V0_PA2`, 3:`EN_+1V8_FPGA`, 4:`EN_+5V0_PA3`, 5:`EN_+3V3_FPGA`, 6:`EN_+5V5_PA`, 7:`EN_+5V0_ADAR`, 8:`EN_+1V8_CLOCK`, 9:`EN_+3V3_ADAR12`, 10:`EN_+3V3_CLOCK`, 11:`EN_+3V3_ADAR34`, 12:`GND`, 13:`EN_+3V3_ADTR`, 14:`GND`, 15:`EN_+3V3_SW`, 16:`GND`, 17:`EN_+3V3_VDD_SW`, 18:`GND`, 19:`EN_+5V0_PA1`, 20:`GND` |
| U1 |  | AD9484BCPZ-500 / CP_56_5_ADI | 3:`ADC_D0_N`, 4:`ADC_D0_P`, 5:`ADC_D1_N`, 6:`ADC_D1_P`, 7:`+1V8_FPGA`, 8:`GND`, 9:`ADC_D2_N`, 10:`ADC_D2_P`, 11:`ADC_D3_N`, 12:`ADC_D3_P`, 13:`ADC_D4_N`, 14:`ADC_D4_P`, 15:`ADC_D5_N`, 16:`ADC_D5_P`, 17:`ADC_D6_N`, 18:`ADC_D6_P`, 19:`ADC_D7_N`, 20:`ADC_D7_P`, 21:`ADC_OR_N`, 22:`ADC_OR_P`, 23:`GND`, 24:`+1V8_FPGA`, 26:`N$6`, 27:`+1V8_CLOCK_F`, 29:`N$41`, 30:`+1V8_CLOCK_F`, 31:`N$17`, 32:`+1V8_CLOCK_F`, 33:`+1V8_CLOCK_F`, 34:`+1V8_CLOCK_F`, 35:`N$43`, 36:`N$4`, 37:`+1V8_CLOCK_F`, 38:`+1V8_CLOCK_F`, 39:`+1V8_CLOCK_F`, 40:`N$44`, 41:`+1V8_CLOCK_F`, 42:`+1V8_CLOCK_F`, 43:`+1V8_CLOCK_F`, 44:`ADC_CLK_ … (47 pins, see CSV) |
| U2 |  | STM32F746ZGT7 / LQFP-144_STM | 1:`STM32_SCLK4`, 4:`STM32_MISO4`, 5:`STM32_MOSI4`, 6:`+3V3`, 8:`STM32_OSC_32_N`, 9:`STM32_OSC_32_P`, 10:`STM32_SDA2`, 11:`STM32_SCL2`, 13:`AD9523_PD`, 14:`AD9523_REF_SEL`, 15:`AD9523_SYNC`, 16:`GND`, 17:`+3V3`, 18:`AD9523_RESET`, 19:`AD9523_CS`, 20:`AD9523_STATUS0`, 21:`AD9523_STATUS1`, 22:`AD9523_EEPROM_SEL`, 23:`STM32_OSC_N`, 24:`STM32_OSC_P`, 25:`STM32_NRST`, 30:`+3V3`, 31:`GND`, 32:`N$9`, 33:`N$9`, 34:`ADAR_1_CS_3V3`, 35:`ADAR_2_CS_3V3`, 36:`ADAR_3_CS_3V3`, 37:`ADAR_4_CS_3V3`, 38:`GND`, 39:`+3V3`, 41:`STM32_SCLK1`, 42:`STM32_MISO1`, 43:`STM32_MOSI1`, 50:`N$52`, 51:`GND`, 52:`+3V3`, 53:`N$9 … (116 pins, see CSV) |
| U3 |  | AD9708AR / RW_28_ADI | 1:`N$10`, 2:`N$11`, 3:`N$12`, 4:`N$13`, 5:`N$14`, 6:`N$16`, 7:`N$18`, 8:`N$19`, 15:`DAC_SLEEP`, 16:`DAC_AVDD`, 17:`+3V3_FPGA`, 18:`N$22`, 19:`N$96`, 20:`DAC_ACOM`, 21:`DAC_IOUT_N`, 22:`DAC_IOUT_P`, 23:`N$37`, 24:`DAC_AVDD`, 26:`GND`, 27:`+3V3_FPGA`, 28:`DAC_CLOCK` |
| U4 |  | AD8352ACPZ-R7 / CP_16_3_ADI | 1:`N$5`, 2:`N$48`, 3:`N$35`, 4:`N$15`, 5:`N$49`, 6:`GND`, 7:`GND`, 8:`+5V0_0`, 9:`GND`, 10:`N$65`, 11:`N$56`, 12:`GND`, 13:`+5V0_0`, 14:`N$51`, 15:`EN_OPAMP_IF_2`, 16:`N$50`, 17:`GND` |
| U5 |  | LTC5552IUDBTRMPBF / UDB_12_ADI | 1:`GND`, 2:`DAC_IOUT_F_P`, 3:`DAC_IOUT_F_N`, 4:`GND`, 5:`RF_TX`, 6:`GND`, 7:`MIX_TX_EN`, 8:`GND`, 9:`+3V3_AN1_F`, 10:`GND`, 11:`N$20`, 12:`GND` |
| U6 |  | FT601Q-B-T / QFN76_FTD |  |
| U7 |  | DAC5578SRGET / RGE24_2P7X2P7 | 2:`+3V3_AN3_F`, 3:`DAC_VOUT_VG_1`, 4:`DAC_VOUT_VG_3`, 5:`DAC_VOUT_VG_5`, 6:`DAC_VOUT_VG_7`, 8:`+3V3_AN3_F`, 9:`+3V3_AN3_F`, 10:`GND`, 11:`GND`, 12:`DAC_1_VG_CLR`, 13:`DAC_VOUT_VG_8`, 14:`DAC_VOUT_VG_6`, 15:`DAC_VOUT_VG_4`, 16:`DAC_VOUT_VG_2`, 17:`GND`, 19:`STM32_SDA1`, 20:`STM32_SCL1`, 21:`N$221`, 22:`DAC_1_VG_LDAC`, 25:`GND` |
| U8 |  | AD8352ACPZ-R7 / CP_16_3_ADI | 1:`N$85`, 2:`N$88`, 3:`N$87`, 4:`N$86`, 5:`N$89`, 6:`GND`, 7:`GND`, 8:`+5V0_0`, 9:`GND`, 10:`N$105`, 11:`N$104`, 12:`GND`, 13:`+5V0_0`, 14:`N$102`, 15:`EN_OPAMP_IF_1`, 16:`N$103`, 17:`GND` |
| U9 |  | MT25QL01GBBB8E12-0AUT / BGA24_MT25QL_MRN | A4:`FPGA_FLASH_NRST`, B2:`N$25`, B3:`GND`, B4:`+3V3_FPGA`, C2:`FPGA_FLASH_NCS`, C4:`FPGA_FLASH_DQ2`, D2:`FPGA_FLASH_DQ1`, D3:`FPGA_FLASH_DQ0`, D4:`FPGA_FLASH_DQ3` |
| U10 |  | ADS7830IPWR / PW16 | 1:`N$211`, 2:`N$217`, 3:`N$223`, 4:`N$229`, 5:`N$234`, 6:`N$239`, 7:`N$245`, 8:`N$250`, 9:`GND`, 10:`N$251`, 11:`N$253`, 12:`GND`, 13:`GND`, 14:`STM32_SCL2`, 15:`STM32_SDA2`, 16:`N$252` |
| U11 |  | INA241A3IDGKRDGK0008A-MFG / DGK0008A-MFG | 1:`N$209`, 2:`GND`, 3:`GND`, 5:`N$210`, 6:`+3V3_AN5_F`, 7:`GND`, 8:`N$207` |
| U13 |  | LTC5552IUDBTRMPBF / UDB_12_ADI | 1:`GND`, 2:`MIX_RX_P`, 3:`MIX_RX_N`, 4:`GND`, 5:`RF_RX`, 6:`GND`, 7:`MIX_RX_EN`, 8:`GND`, 9:`+3V3_AN2_F`, 10:`GND`, 11:`N$72`, 12:`GND` |
| U14 |  | SZMMSZ5232BT1G / SOD-123_ONS | 1:`+3V4`, 2:`GND` |
| U15 |  | SZMMSZ5232BT1G / SOD-123_ONS | 1:`GND`, 2:`-3V4` |
| U16 |  | EP4RKU+ / DG1677-2_MNC | 1:`GND`, 2:`GND`, 3:`GND`, 4:`GND`, 5:`GND`, 6:`GND`, 7:`GND`, 8:`GND`, 9:`GND`, 10:`RF_IO_2`, 11:`GND`, 12:`GND`, 13:`GND`, 14:`RF_IO_1`, 15:`GND`, 16:`GND`, 17:`GND`, 18:`GND`, 19:`GND`, 20:`GND`, 21:`RF_IO`, 22:`GND`, 23:`GND`, 24:`GND`, 25:`GND`, 26:`GND`, 27:`RF_IO_4`, 28:`GND`, 29:`GND`, 30:`GND`, 31:`RF_IO_3`, 32:`GND`, 33:`GND` |
| U17 |  | SZMMSZ5232BT1G / SOD-123_ONS | 1:`+3V4`, 2:`GND` |
| U37 |  | SZMMSZ5232BT1G / SOD-123_ONS | 1:`GND`, 2:`-3V4` |
| U38 |  | SZMMSZ5232BT1G / SOD-123_ONS | 1:`+3V4`, 2:`GND` |
| U39 |  | SZMMSZ5232BT1G / SOD-123_ONS | 1:`GND`, 2:`-3V4` |
| U40 |  | SZMMSZ5232BT1G / SOD-123_ONS | 1:`+3V4`, 2:`GND` |
| U41 |  | SZMMSZ5232BT1G / SOD-123_ONS | 1:`GND`, 2:`-3V4` |
| U42 |  | XC7A50T-2FTG256I / BGA256C100P16X16_1700X1700X155 | A1 A11 B8 C5 C15 D2 D12 E9 F6 F10 F16 G3 G9 G13 H6 J9 J11 K4 K6 K14 L1 L11 M8 N5 N15 P2 P12 R9 T6 T16:`GND`, A6 B3 D7 E4 F1 J2:`+3V3_FPGA`, A8:`DAC_7`, A9:`DAC_6`, A10:`DAC_5`, A12:`DAC_2`, A13:`DAC_1`, A14:`DAC_0`, A15:`DAC_SLEEP`, A16 B13 C10 E14 H15 J12:`+3V3_FPGA`, B10:`DAC_4`, B11:`DAC_3`, C11:`MIX_TX_EN`, C13:`FPGA_DAC_CLOCK`, D11:`MIX_RX_EN`, D16:`DIG_2`, E7:`N$114`, E8:`FPGA_FLASH_CLK`, E10 F11:`+1V0_FPGA`, E12:`FPGA_SYS_CLOCK`, E15:`DIG_4`, E16:`DIG_1`, F7 F9 G6 H9 J6 K9 L8:`+1V0_FPGA`, F8:`+1V8_FPGA`, F13:`DIG_0`, F14:`ADAR_1_CS_3V3`, F15:`DIG_3`, G7:`GND`, G8:`+1V8_FPGA`, G10 J10 K1 … (109 pins, see CSV) |
| U43 |  | SZMMSZ5232BT1G / SOD-123_ONS | 1:`+3V4`, 2:`GND` |
| U44 |  | SZMMSZ5232BT1G / SOD-123_ONS | 1:`GND`, 2:`-3V4` |
| U45 |  | SZMMSZ5232BT1G / SOD-123_ONS | 1:`+3V4`, 2:`GND` |
| U46 |  | SZMMSZ5232BT1G / SOD-123_ONS | 1:`GND`, 2:`-3V4` |
| U47 |  | SZMMSZ5232BT1G / SOD-123_ONS | 1:`+3V4`, 2:`GND` |
| U48 |  | SZMMSZ5232BT1G / SOD-123_ONS | 1:`GND`, 2:`-3V4` |
| U49 |  | SZMMSZ5232BT1G / SOD-123_ONS | 1:`+3V4`, 2:`GND` |
| U50 |  | SZMMSZ5232BT1G / SOD-123_ONS | 1:`GND`, 2:`-3V4` |
| U51 |  | SZMMSZ5232BT1G / SOD-123_ONS | 1:`+3V4`, 2:`GND` |
| U52 |  | SZMMSZ5232BT1G / SOD-123_ONS | 1:`GND`, 2:`-3V4` |
| U53 |  | SZMMSZ5232BT1G / SOD-123_ONS | 1:`+3V4`, 2:`GND` |
| U54 |  | SZMMSZ5232BT1G / SOD-123_ONS | 1:`GND`, 2:`-3V4` |
| U55 |  | SZMMSZ5232BT1G / SOD-123_ONS | 1:`+3V4`, 2:`GND` |
| U56 |  | SZMMSZ5232BT1G / SOD-123_ONS | 1:`GND`, 2:`-3V4` |
| U57 |  | SZMMSZ5232BT1G / SOD-123_ONS | 1:`+3V4`, 2:`GND` |
| U58 |  | SZMMSZ5232BT1G / SOD-123_ONS | 1:`GND`, 2:`-3V4` |
| U59 |  | SZMMSZ5232BT1G / SOD-123_ONS | 1:`+3V4`, 2:`GND` |
| U60 |  | SZMMSZ5232BT1G / SOD-123_ONS | 1:`GND`, 2:`-3V4` |
| U61 |  | SZMMSZ5232BT1G / SOD-123_ONS | 1:`+3V4`, 2:`GND` |
| U62 |  | SZMMSZ5232BT1G / SOD-123_ONS | 1:`GND`, 2:`-3V4` |
| U63 |  | SZMMSZ5232BT1G / SOD-123_ONS | 1:`+3V4`, 2:`GND` |
| U64 |  | SZMMSZ5232BT1G / SOD-123_ONS | 1:`GND`, 2:`-3V4` |
| U65 |  | SZMMSZ5232BT1G / SOD-123_ONS | 1:`+3V4`, 2:`GND` |
| U66 |  | SZMMSZ5232BT1G / SOD-123_ONS | 1:`GND`, 2:`-3V4` |
| U67 |  | SZMMSZ5232BT1G / SOD-123_ONS | 1:`+3V4`, 2:`GND` |
| U68 |  | SZMMSZ5232BT1G / SOD-123_ONS | 1:`GND`, 2:`-3V4` |
| U69 |  | DAC5578SRGET / RGE24_2P7X2P7 | 2:`+3V3_AN3_F`, 3:`DAC_VOUT_VG_9`, 4:`DAC_VOUT_VG_11`, 5:`DAC_VOUT_VG_13`, 6:`DAC_VOUT_VG_15`, 8:`+3V3_AN3_F`, 9:`+3V3_AN3_F`, 10:`GND`, 11:`N$1`, 12:`DAC_2_VG_CLR`, 13:`DAC_VOUT_VG_16`, 14:`DAC_VOUT_VG_14`, 15:`DAC_VOUT_VG_12`, 16:`DAC_VOUT_VG_10`, 17:`GND`, 19:`STM32_SDA1`, 20:`STM32_SCL1`, 21:`N$205`, 22:`DAC_2_VG_LDAC`, 25:`GND` |
| U73 |  | INA241A3IDGKRDGK0008A-MFG / DGK0008A-MFG | 1:`N$214`, 2:`GND`, 3:`GND`, 5:`N$215`, 6:`+3V3_AN5_F`, 7:`GND`, 8:`N$212` |
| U74 |  | INA241A3IDGKRDGK0008A-MFG / DGK0008A-MFG | 1:`N$219`, 2:`GND`, 3:`GND`, 5:`N$220`, 6:`+3V3_AN5_F`, 7:`GND`, 8:`N$218` |
| U75 |  | INA241A3IDGKRDGK0008A-MFG / DGK0008A-MFG | 1:`N$226`, 2:`GND`, 3:`GND`, 5:`N$227`, 6:`+3V3_AN5_F`, 7:`GND`, 8:`N$225` |
| U76 |  | INA241A3IDGKRDGK0008A-MFG / DGK0008A-MFG | 1:`N$232`, 2:`GND`, 3:`GND`, 5:`N$233`, 6:`+3V3_AN5_F`, 7:`GND`, 8:`N$230` |
| U77 |  | INA241A3IDGKRDGK0008A-MFG / DGK0008A-MFG | 1:`N$236`, 2:`GND`, 3:`GND`, 5:`N$237`, 6:`+3V3_AN5_F`, 7:`GND`, 8:`N$235` |
| U78 |  | INA241A3IDGKRDGK0008A-MFG / DGK0008A-MFG | 1:`N$242`, 2:`GND`, 3:`GND`, 5:`N$243`, 6:`+3V3_AN5_F`, 7:`GND`, 8:`N$241` |
| U79 |  | INA241A3IDGKRDGK0008A-MFG / DGK0008A-MFG | 1:`N$248`, 2:`GND`, 3:`GND`, 5:`N$249`, 6:`+3V3_AN5_F`, 7:`GND`, 8:`N$246` |
| U80 |  | INA241A3IDGKRDGK0008A-MFG / DGK0008A-MFG | 1:`N$257`, 2:`GND`, 3:`GND`, 5:`N$258`, 6:`+3V3_AN6_F`, 7:`GND`, 8:`N$255` |
| U81 |  | INA241A3IDGKRDGK0008A-MFG / DGK0008A-MFG | 1:`N$262`, 2:`GND`, 3:`GND`, 5:`N$264`, 6:`+3V3_AN6_F`, 7:`GND`, 8:`N$261` |
| U82 |  | INA241A3IDGKRDGK0008A-MFG / DGK0008A-MFG | 1:`N$267`, 2:`GND`, 3:`GND`, 5:`N$268`, 6:`+3V3_AN6_F`, 7:`GND`, 8:`N$266` |
| U83 |  | INA241A3IDGKRDGK0008A-MFG / DGK0008A-MFG | 1:`N$271`, 2:`GND`, 3:`GND`, 5:`N$272`, 6:`+3V3_AN6_F`, 7:`GND`, 8:`N$270` |
| U84 |  | INA241A3IDGKRDGK0008A-MFG / DGK0008A-MFG | 1:`N$275`, 2:`GND`, 3:`GND`, 5:`N$276`, 6:`+3V3_AN6_F`, 7:`GND`, 8:`N$274` |
| U85 |  | INA241A3IDGKRDGK0008A-MFG / DGK0008A-MFG | 1:`N$279`, 2:`GND`, 3:`GND`, 5:`N$280`, 6:`+3V3_AN6_F`, 7:`GND`, 8:`N$278` |
| U86 |  | INA241A3IDGKRDGK0008A-MFG / DGK0008A-MFG | 1:`N$283`, 2:`GND`, 3:`GND`, 5:`N$284`, 6:`+3V3_AN6_F`, 7:`GND`, 8:`N$282` |
| U87 |  | INA241A3IDGKRDGK0008A-MFG / DGK0008A-MFG | 1:`N$287`, 2:`GND`, 3:`GND`, 5:`N$288`, 6:`+3V3_AN6_F`, 7:`GND`, 8:`N$286` |
| U88 |  | ADS7830IPWR / PW16 | 1:`N$259`, 2:`N$265`, 3:`N$269`, 4:`N$273`, 5:`N$277`, 6:`N$281`, 7:`N$285`, 8:`N$289`, 9:`GND`, 10:`N$290`, 11:`N$292`, 12:`GND`, 13:`N$293`, 14:`STM32_SCL2`, 15:`STM32_SDA2`, 16:`N$291` |
| U89 |  | ADS7830IPWR / PW16 | 1:`N$297`, 2:`N$299`, 3:`N$307`, 4:`N$295`, 5:`N$296`, 6:`N$306`, 7:`N$298`, 8:`N$301`, 9:`GND`, 10:`N$302`, 11:`N$304`, 12:`N$294`, 13:`GND`, 14:`STM32_SCL2`, 15:`STM32_SDA2`, 16:`N$303` |
| U$1 |  | M3SWA2-34DR+ / 16_QFN | 1:`GND`, 2:`GND`, 3:`N$21`, 4:`GND`, 5:`-3V4`, 6:`M3S_VCTRL`, 7:`GND`, 8:`+3V4`, 9:`GND`, 10:`N$38`, 11:`GND`, 12:`GND`, 13:`GND`, 14:`GND`, 15:`N$26`, 16:`GND`, 17:`GND` |
| U$2 |  | BPF2 / BPF2 | P$1:`RF_TX_FIL`, P$2:`RF_TX` |
| U$3 |  | BPF2 / BPF2 | P$1:`RF_RX`, P$2:`RF_RX_FIL` |
| X1 |  | 22-23-2021 / 22-23-2021 | 1:`+3V4`, 2:`GND` |
| X3 |  | 22-23-2031 / 22-23-2031 | 1:`N$207`, 2:`N$209`, 3:`GND` |
| X4 |  | 22-23-2021 / 22-23-2021 | 1:`+3V3_ADTR`, 2:`GND` |
| X5 |  | 22-23-2021 / 22-23-2021 | 1:`+5V0_PA_2`, 2:`GND` |
| X6 |  | 22-23-2021 / 22-23-2021 | 1:`-3V3_SW`, 2:`GND` |
| X7 |  | 22-23-2021 / 22-23-2021 | 1:`+5V0_PA_3`, 2:`GND` |
| X8 |  | 22-23-2021 / 22-23-2021 | 1:`+1V0_FPGA`, 2:`GND` |
| X9 |  | 22-23-2021 / 22-23-2021 | 1:`+3V3_AN`, 2:`GND` |
| X10 |  | 22-23-2021 / 22-23-2021 | 1:`+1V8_FPGA`, 2:`GND` |
| X11 |  | 22-23-2021 / 22-23-2021 | 1:`-3V4`, 2:`GND` |
| X12 |  | 22-23-2021 / 22-23-2021 | 1:`+3V3_VDD_SW`, 2:`GND` |
| X13 |  | 22-23-2021 / 22-23-2021 | 1:`-5V0_ADAR12`, 2:`GND` |
| X14 |  | 22-23-2021 / 22-23-2021 | 1:`+5V0_PA_1`, 2:`GND` |
| X15 |  | 22-23-2021 / 22-23-2021 | 1:`-5V0_ADAR34`, 2:`GND` |
| X16 |  | 22-23-2021 / 22-23-2021 | 1:`+3V3_FPGA`, 2:`GND` |
| X17 |  | 22-23-2021 / 22-23-2021 | 1:`+1V8_CLOCK`, 2:`GND` |
| X18 |  | 22-23-2021 / 22-23-2021 | 1:`+5V0_0`, 2:`GND` |
| X19 |  | 22-23-2021 / 22-23-2021 | 1:`-5V5_PA`, 2:`GND` |
| X20 |  | 22-23-2021 / 22-23-2021 | 1:`+3V3_ADAR12`, 2:`GND` |
| X21 |  | 22-23-2021 / 22-23-2021 | 1:`+3V3_ADAR34`, 2:`GND` |
| X22 |  | 22-23-2021 / 22-23-2021 | 1:`-3V4`, 2:`GND` |
| X24 |  | 22-23-2021 / 22-23-2021 | 1:`+3V3`, 2:`GND` |
| X38 |  | 22-23-2031 / 22-23-2031 | 1:`N$212`, 2:`N$214`, 3:`GND` |
| X39 |  | 22-23-2031 / 22-23-2031 | 1:`N$218`, 2:`N$219`, 3:`GND` |
| X40 |  | 22-23-2031 / 22-23-2031 | 1:`N$225`, 2:`N$226`, 3:`GND` |
| X41 |  | 22-23-2031 / 22-23-2031 | 1:`N$230`, 2:`N$232`, 3:`GND` |
| X42 |  | 22-23-2031 / 22-23-2031 | 1:`N$235`, 2:`N$236`, 3:`GND` |
| X43 |  | 22-23-2031 / 22-23-2031 | 1:`N$241`, 2:`N$242`, 3:`GND` |
| X44 |  | 22-23-2031 / 22-23-2031 | 1:`N$246`, 2:`N$248`, 3:`GND` |
| X45 |  | 22-23-2031 / 22-23-2031 | 1:`N$255`, 2:`N$257`, 3:`GND` |
| X46 |  | 22-23-2031 / 22-23-2031 | 1:`N$261`, 2:`N$262`, 3:`GND` |
| X47 |  | 22-23-2031 / 22-23-2031 | 1:`N$266`, 2:`N$267`, 3:`GND` |
| X48 |  | 22-23-2031 / 22-23-2031 | 1:`N$270`, 2:`N$271`, 3:`GND` |
| X49 |  | 22-23-2031 / 22-23-2031 | 1:`N$274`, 2:`N$275`, 3:`GND` |
| X50 |  | 22-23-2031 / 22-23-2031 | 1:`N$278`, 2:`N$279`, 3:`GND` |
| X51 |  | 22-23-2031 / 22-23-2031 | 1:`N$282`, 2:`N$283`, 3:`GND` |
| X52 |  | 22-23-2031 / 22-23-2031 | 1:`N$286`, 2:`N$287`, 3:`GND` |
| X53 |  | MINI-USB-32005-201 / 32005-201 | 2:`STM32_USB_FS_D_N`, 3:`STM32_USB_FS_D_P`, 4:`STM32_USB_FS_ID`, 5:`GND` |
| X54 |  | 22-23-2021 / 22-23-2021 | 1:`+3V4`, 2:`GND` |
| X55 |  | 22-23-2021 / 22-23-2021 | 1:`+5V5_PA`, 2:`GND` |
| X56 |  | 22-23-2021 / 22-23-2021 | 1:`+3V3_AN`, 2:`GND` |
| XTAL1 |  | NX3225GD-8MHZ-STD-CRA-3 / XTAL_NX3225GD-8MHZ-STD-CRA-3_N | 1:`STM32_OSC_P`, 2:`STM32_OSC_N` |
| XTAL3 | NX3215SA-32.768KHz | NX3225GD-8MHZ-STD-CRA-3 / XTAL_NX3225GD-8MHZ-STD-CRA-3_N | 1:`STM32_OSC_32_P`, 2:`STM32_OSC_32_N` |
| X_1 |  | 22-23-2021 / 22-23-2021 | 1:`VG_15`, 2:`GND` |
| X_2 |  | 22-23-2021 / 22-23-2021 | 1:`VG_13`, 2:`GND` |
| X_3 |  | 22-23-2021 / 22-23-2021 | 1:`VG_7`, 2:`GND` |
| X_4 |  | 22-23-2021 / 22-23-2021 | 1:`VG_5`, 2:`GND` |
| X_5 |  | 22-23-2021 / 22-23-2021 | 1:`VG_9`, 2:`GND` |
| X_6 |  | 22-23-2021 / 22-23-2021 | 1:`VG_11`, 2:`GND` |
| X_7 |  | 22-23-2021 / 22-23-2021 | 1:`VG_1`, 2:`GND` |
| X_8 |  | 22-23-2021 / 22-23-2021 | 1:`VG_3`, 2:`GND` |
| X_9 |  | 22-23-2021 / 22-23-2021 | 1:`VG_14`, 2:`GND` |
| X_10 |  | 22-23-2021 / 22-23-2021 | 1:`VG_16`, 2:`GND` |
| X_11 |  | 22-23-2021 / 22-23-2021 | 1:`VG_6`, 2:`GND` |
| X_12 |  | 22-23-2021 / 22-23-2021 | 1:`VG_8`, 2:`GND` |
| X_13 |  | 22-23-2021 / 22-23-2021 | 1:`VG_12`, 2:`GND` |
| X_14 |  | 22-23-2021 / 22-23-2021 | 1:`VG_10`, 2:`GND` |
| X_15 |  | 22-23-2021 / 22-23-2021 | 1:`VG_4`, 2:`GND` |
| X_16 |  | 22-23-2021 / 22-23-2021 | 1:`VG_2`, 2:`GND` |
