herasymyuks/PLFM_RADAR-aeris/engineering/ELECTRICAL/connection_diagrams/POWER_SUPPLY_connection_report.md

# POWER_SUPPLY — Component-to-net connection report

Project AERIS-10 · Drawing ID ELEC-CON-POWER_SUPPLY · Rev A · 2026-10-09 · Status: SOURCE-DERIVED  
Source: `4_Schematics and Boards Layout/4_6_Schematics/PowerBoard/PowerBoard.sch` (EAGLE 9.6.2), `4_Schematics and Boards Layout/4_6_Schematics/PowerBoard/PowerBoard.brd`; generated by `tools/gen_schematic_reports.py`.

## 1. Summary

| Item | Count |
|---|---|
| Sheets | 1 |
| Parts (all) / physical | 562 / 312 |
| Nets | 156 |
| Pin connections | 1061 |
| Single-pin nets | 0 |
| Unconnected pins on placed gates | 24 |
| Physical parts without value | 80 |
| Board airwires (unrouted connections, layer 19) | 309 |
| Missing symbol/footprint records | 0 |

## 2. Connector pin-outs

Parts whose package name or prefix identifies a connector (header, SMA, terminal block, USB).

### SV1 — MA10-2 (MA10-2)

| Pad | Pin name | Net | Sheet |
|---|---|---|---|
| 1 | 1 | `EN_+1V0_FPGA` | 1 |
| 2 | 2 | `EN_+5V0_PA2` | 1 |
| 3 | 3 | `EN_+1V8_FPGA` | 1 |
| 4 | 4 | `EN_+5V0_PA3` | 1 |
| 5 | 5 | `EN_+3V3_FPGA` | 1 |
| 6 | 6 | `EN_+5V5_PA` | 1 |
| 7 | 7 | `EN_+5V0_ADAR` | 1 |
| 8 | 8 | `EN_+1V8_CLOCK` | 1 |
| 9 | 9 | `EN_+3V3_ADAR12` | 1 |
| 10 | 10 | `EN_+3V3_CLOCK` | 1 |
| 11 | 11 | `EN_+3V3_ADAR34` | 1 |
| 12 | 12 | `GND` | 1 |
| 13 | 13 | `EN_+3V3_ADTR` | 1 |
| 14 | 14 | `GND` | 1 |
| 15 | 15 | `EN_+3V3_SW` | 1 |
| 16 | 16 | `GND` | 1 |
| 17 | 17 | `EN_+3V3_VDD_SW` | 1 |
| 18 | 18 | `GND` | 1 |
| 19 | 19 | `EN_+5V0_PA1` | 1 |
| 20 | 20 | `GND` | 1 |

### X1 — AK300/2 (AK300/2)

| Pad | Pin name | Net | Sheet |
|---|---|---|---|
| 1 | KL | `VIN` | 1 |
| 2 | KL | `GND` | 1 |

### X2 — 22-23-2021 (22-23-2021)

| Pad | Pin name | Net | Sheet |
|---|---|---|---|
| 1 | S | `+5V0_1` | 1 |
| 2 | S | `GND` | 1 |

### X3 — 22-23-2021 (22-23-2021)

| Pad | Pin name | Net | Sheet |
|---|---|---|---|
| 1 | S | `+5V5_PA` | 1 |
| 2 | S | `GND` | 1 |

### X4 — 22-23-2021 (22-23-2021)

| Pad | Pin name | Net | Sheet |
|---|---|---|---|
| 1 | S | `+1V0_FPGA` | 1 |
| 2 | S | `GND` | 1 |

### X5 — 22-23-2021 (22-23-2021)

| Pad | Pin name | Net | Sheet |
|---|---|---|---|
| 1 | S | `+1V8_FPGA` | 1 |
| 2 | S | `GND` | 1 |

### X6 — 22-23-2021 (22-23-2021)

| Pad | Pin name | Net | Sheet |
|---|---|---|---|
| 1 | S | `+5V0_LO` | 1 |
| 2 | S | `GND` | 1 |

### X7 — 22-23-2021 (22-23-2021)

| Pad | Pin name | Net | Sheet |
|---|---|---|---|
| 1 | S | `+3V3_LO_2` | 1 |
| 2 | S | `GND` | 1 |

### X8 — 22-23-2021 (22-23-2021)

| Pad | Pin name | Net | Sheet |
|---|---|---|---|
| 1 | S | `+3V3_LO_1` | 1 |
| 2 | S | `GND` | 1 |

### X9 — 22-23-2021 (22-23-2021)

| Pad | Pin name | Net | Sheet |
|---|---|---|---|
| 1 | S | `+5V0_2` | 1 |
| 2 | S | `GND` | 1 |

### X10 — 22-23-2021 (22-23-2021)

| Pad | Pin name | Net | Sheet |
|---|---|---|---|
| 1 | S | `+1V8_CLOCK` | 1 |
| 2 | S | `GND` | 1 |

### X11 — 22-23-2021 (22-23-2021)

| Pad | Pin name | Net | Sheet |
|---|---|---|---|
| 1 | S | `+3V3_CLOCK` | 1 |
| 2 | S | `GND` | 1 |

### X12 — 22-23-2021 (22-23-2021)

| Pad | Pin name | Net | Sheet |
|---|---|---|---|
| 1 | S | `+3V3_AN` | 1 |
| 2 | S | `GND` | 1 |

### X13 — 22-23-2021 (22-23-2021)

| Pad | Pin name | Net | Sheet |
|---|---|---|---|
| 1 | S | `+5V0_ADAR` | 1 |
| 2 | S | `GND` | 1 |

### X14 — 22-23-2021 (22-23-2021)

| Pad | Pin name | Net | Sheet |
|---|---|---|---|
| 1 | S | `+3V3_ADAR_12` | 1 |
| 2 | S | `GND` | 1 |

### X15 — 22-23-2021 (22-23-2021)

| Pad | Pin name | Net | Sheet |
|---|---|---|---|
| 1 | S | `+3V3_ADAR_34` | 1 |
| 2 | S | `GND` | 1 |

### X16 — 22-23-2021 (22-23-2021)

| Pad | Pin name | Net | Sheet |
|---|---|---|---|
| 1 | S | `+3V3` | 1 |
| 2 | S | `GND` | 1 |

### X17 — 22-23-2021 (22-23-2021)

| Pad | Pin name | Net | Sheet |
|---|---|---|---|
| 1 | S | `+5V0_3` | 1 |
| 2 | S | `GND` | 1 |

### X18 — 22-23-2021 (22-23-2021)

| Pad | Pin name | Net | Sheet |
|---|---|---|---|
| 1 | S | `-3V3_SW` | 1 |
| 2 | S | `GND` | 1 |

### X19 — 22-23-2021 (22-23-2021)

| Pad | Pin name | Net | Sheet |
|---|---|---|---|
| 1 | S | `-5V5_PA` | 1 |
| 2 | S | `GND` | 1 |

### X20 — 22-23-2021 (22-23-2021)

| Pad | Pin name | Net | Sheet |
|---|---|---|---|
| 1 | S | `-5V0_ADAR34` | 1 |
| 2 | S | `GND` | 1 |

### X21 — 22-23-2021 (22-23-2021)

| Pad | Pin name | Net | Sheet |
|---|---|---|---|
| 1 | S | `-5V0_ADAR12` | 1 |
| 2 | S | `GND` | 1 |

### X22 — 22-23-2021 (22-23-2021)

| Pad | Pin name | Net | Sheet |
|---|---|---|---|
| 1 | S | `+5V0_0` | 1 |
| 2 | S | `GND` | 1 |

### X23 — 22-23-2021 (22-23-2021)

| Pad | Pin name | Net | Sheet |
|---|---|---|---|
| 1 | S | `+3V4` | 1 |
| 2 | S | `GND` | 1 |

### X24 — 22-23-2021 (22-23-2021)

| Pad | Pin name | Net | Sheet |
|---|---|---|---|
| 1 | S | `-3V4` | 1 |
| 2 | S | `GND` | 1 |

### X25 — 22-23-2021 (22-23-2021)

| Pad | Pin name | Net | Sheet |
|---|---|---|---|
| 1 | S | `+5V0_4` | 1 |
| 2 | S | `GND` | 1 |

### X26 — 22-23-2021 (22-23-2021)

| Pad | Pin name | Net | Sheet |
|---|---|---|---|
| 1 | S | `+5V0_ADTR` | 1 |
| 2 | S | `GND` | 1 |

### X27 — 22-23-2021 (22-23-2021)

| Pad | Pin name | Net | Sheet |
|---|---|---|---|
| 1 | S | `+3V3_FPGA` | 1 |
| 2 | S | `GND` | 1 |

### X28 — 22-23-2021 (22-23-2021)

| Pad | Pin name | Net | Sheet |
|---|---|---|---|
| 1 | S | `+5V0_5` | 1 |
| 2 | S | `GND` | 1 |

### X29 — 22-23-2021 (22-23-2021)

| Pad | Pin name | Net | Sheet |
|---|---|---|---|
| 1 | S | `+3V3_SW` | 1 |
| 2 | S | `GND` | 1 |

### X30 — 22-23-2021 (22-23-2021)

| Pad | Pin name | Net | Sheet |
|---|---|---|---|
| 1 | S | `+3V3_VDD_SW` | 1 |
| 2 | S | `GND` | 1 |

### X31 — 22-23-2021 (22-23-2021)

| Pad | Pin name | Net | Sheet |
|---|---|---|---|
| 1 | S | `+5V0_PA_1` | 1 |
| 2 | S | `GND` | 1 |

### X32 — 22-23-2021 (22-23-2021)

| Pad | Pin name | Net | Sheet |
|---|---|---|---|
| 1 | S | `+5V0_PA_2` | 1 |
| 2 | S | `GND` | 1 |

### X33 — 22-23-2021 (22-23-2021)

| Pad | Pin name | Net | Sheet |
|---|---|---|---|
| 1 | S | `+5V0_PA_3` | 1 |
| 2 | S | `GND` | 1 |

### X34 — 22-23-2021 (22-23-2021)

| Pad | Pin name | Net | Sheet |
|---|---|---|---|
| 1 | S | `+3V3_ADTR` | 1 |
| 2 | S | `GND` | 1 |

### X35 — 22-23-2021 (22-23-2021)

| Pad | Pin name | Net | Sheet |
|---|---|---|---|
| 1 | S | `+3V3_XO` | 1 |
| 2 | S | `GND` | 1 |

## 3. Net fan-out (nets with ≥ 8 connections)

| Net | Connections | Class |
|---|---|---|
| `GND` | 502 | 0 |
| `VIN` | 76 | 0 |
| `+5V0_5` | 10 | 0 |
| `+5V0_ADTR` | 9 | 0 |
| `+5V0_0` | 8 | 0 |
| `+5V0_3` | 8 | 0 |
| `+5V0_4` | 8 | 0 |

## 4. Component-to-net table

Full machine-readable form: `netlists/POWER_SUPPLY_netlist_by_part.csv`. Physical parts only; pads shown when the device defines a package connection.

| Part | Value | Device / package | Connections (pad:net) |
|---|---|---|---|
| C1 | 0.1µF | C-EUC0805 / C0805 | 1:`N$2`, 2:`N$1` |
| C2 | 22µF | C-EUC0603 / C0603 | 1:`+1V0_FPGA`, 2:`GND` |
| C3 | 22µF | C-EUC0603 / C0603 | 1:`+1V0_FPGA`, 2:`GND` |
| C4 | 10µF | C-EUC0805 / C0805 | 1:`VIN`, 2:`GND` |
| C5 | 10µF | C-EUC0805 / C0805 | 1:`VIN`, 2:`GND` |
| C6 | 0.1µF | C-EUC0805 / C0805 | 1:`N$5`, 2:`N$3` |
| C7 | 22µF | C-EUC0603 / C0603 | 1:`+1V8_FPGA`, 2:`GND` |
| C8 | 22µF | C-EUC0603 / C0603 | 1:`+1V8_FPGA`, 2:`GND` |
| C9 | 10µF | C-EUC0805 / C0805 | 1:`VIN`, 2:`GND` |
| C10 | 10µF | C-EUC0805 / C0805 | 1:`VIN`, 2:`GND` |
| C11 | 22µF | C-EUC0603 / C0603 | 1:`+1V8_FPGA`, 2:`GND` |
| C12 | 0.1µF | C-EUC0805 / C0805 | 1:`N$8`, 2:`N$7` |
| C13 | 22µF | C-EUC0603 / C0603 | 1:`+3V3`, 2:`GND` |
| C14 | 22µF | C-EUC0603 / C0603 | 1:`+3V3`, 2:`GND` |
| C15 | 10µF | C-EUC0805 / C0805 | 1:`VIN`, 2:`GND` |
| C16 | 10µF | C-EUC0805 / C0805 | 1:`VIN`, 2:`GND` |
| C17 | 22µF | C-EUC0603 / C0603 | 1:`+3V3`, 2:`GND` |
| C18 | 0.1µF | C-EUC0805 / C0805 | 1:`N$11`, 2:`N$10` |
| C19 | 22µF | C-EUC0603 / C0603 | 1:`+3V3_FPGA`, 2:`GND` |
| C20 | 22µF | C-EUC0603 / C0603 | 1:`+3V3_FPGA`, 2:`GND` |
| C21 | 10µF | C-EUC0805 / C0805 | 1:`VIN`, 2:`GND` |
| C22 | 10µF | C-EUC0805 / C0805 | 1:`VIN`, 2:`GND` |
| C23 | 22µF | C-EUC0603 / C0603 | 1:`+3V3_FPGA`, 2:`GND` |
| C24 | 10µF | C-EUC0805 / C0805 | 1:`GND`, 2:`N$13` |
| C25 | 10µF | C-EUC0805 / C0805 | 1:`GND`, 2:`+3V3_AN` |
| C26 | 1µF | C-EUC0805 / C0805 | 1:`GND`, 2:`N$15` |
| C27 | 1µF | C-EUC0805 / C0805 | 1:`GND`, 2:`N$27` |
| C28 | 10µF | C-EUC0805 / C0805 | 1:`GND`, 2:`+5V0_0` |
| C29 | 0.1µF | C-EUC0805 / C0805 | 1:`N$64`, 2:`N$26` |
| C30 | 0.1µF | C-EUC0805 / C0805 | 1:`N$17`, 2:`N$16` |
| C31 | 22µF | C-EUC0603 / C0603 | 1:`+3V3_ADAR_12`, 2:`GND` |
| C32 | 22µF | C-EUC0603 / C0603 | 1:`+3V3_ADAR_12`, 2:`GND` |
| C33 | 10µF | C-EUC0805 / C0805 | 1:`VIN`, 2:`GND` |
| C34 | 10µF | C-EUC0805 / C0805 | 1:`VIN`, 2:`GND` |
| C35 | 22µF | C-EUC0603 / C0603 | 1:`+3V3_ADAR_12`, 2:`GND` |
| C36 | 0.1µF | C-EUC0805 / C0805 | 1:`N$20`, 2:`N$19` |
| C37 | 22µF | C-EUC0603 / C0603 | 1:`+3V3_ADAR_34`, 2:`GND` |
| C38 | 22µF | C-EUC0603 / C0603 | 1:`+3V3_ADAR_34`, 2:`GND` |
| C39 | 10µF | C-EUC0805 / C0805 | 1:`VIN`, 2:`GND` |
| C40 | 10µF | C-EUC0805 / C0805 | 1:`VIN`, 2:`GND` |
| C41 | 22µF | C-EUC0603 / C0603 | 1:`+3V3_ADAR_34`, 2:`GND` |
| C42 | 0.1µF | C-EUC0805 / C0805 | 1:`N$23`, 2:`N$22` |
| C43 | 22µF | C-EUC0603 / C0603 | 1:`+3V3_VDD_SW`, 2:`GND` |
| C44 | 22µF | C-EUC0603 / C0603 | 1:`+3V3_VDD_SW`, 2:`GND` |
| C45 | 10µF | C-EUC0805 / C0805 | 1:`VIN`, 2:`GND` |
| C46 | 10µF | C-EUC0805 / C0805 | 1:`VIN`, 2:`GND` |
| C47 | 22µF | C-EUC0603 / C0603 | 1:`+3V3_VDD_SW`, 2:`GND` |
| C48 | 22µF | C-EUC0603 / C0603 | 1:`+5V0_1`, 2:`GND` |
| C49 | 22µF | C-EUC0603 / C0603 | 1:`+5V0_1`, 2:`GND` |
| C50 | 10µF | C-EUC0805 / C0805 | 1:`VIN`, 2:`GND` |
| C51 | 10µF | C-EUC0805 / C0805 | 1:`VIN`, 2:`GND` |
| C52 | 10µF | C-EUC0805 / C0805 | 1:`GND`, 2:`N$66` |
| C53 | 10µF | C-EUC0805 / C0805 | 1:`GND`, 2:`+3V3_CLOCK` |
| C54 | 0.1µF | C-EUC0805 / C0805 | 1:`N$29`, 2:`N$28` |
| C55 | 22µF | C-EUC0603 / C0603 | 1:`+3V3_SW`, 2:`GND` |
| C56 | 22µF | C-EUC0603 / C0603 | 1:`+3V3_SW`, 2:`GND` |
| C57 | 10µF | C-EUC0805 / C0805 | 1:`VIN`, 2:`GND` |
| C58 | 10µF | C-EUC0805 / C0805 | 1:`VIN`, 2:`GND` |
| C59 | 22µF | C-EUC0603 / C0603 | 1:`+3V3_SW`, 2:`GND` |
| C60 | 0.1µF | C-EUC0805 / C0805 | 1:`N$32`, 2:`N$31` |
| C61 | 22µF | C-EUC0603 / C0603 | 1:`+3V4`, 2:`GND` |
| C62 | 22µF | C-EUC0603 / C0603 | 1:`+3V4`, 2:`GND` |
| C63 | 10µF | C-EUC0805 / C0805 | 1:`VIN`, 2:`GND` |
| C64 | 10µF | C-EUC0805 / C0805 | 1:`VIN`, 2:`GND` |
| C65 | 22µF | C-EUC0603 / C0603 | 1:`+3V4`, 2:`GND` |
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
| C138 | 10µF | C-EUC0805 / C0805 | 1:`GND`, 2:`+5V0_4` |
| C139 | 10µF | C-EUC0805 / C0805 | 1:`GND`, 2:`N$14` |
| C140 | 10µF | C-EUC0805 / C0805 | 1:`GND`, 2:`+5V0_LO` |
| C141 | 1µF | C-EUC0805 / C0805 | 1:`GND`, 2:`N$62` |
| C142 | 1µF | C-EUC0805 / C0805 | 1:`GND`, 2:`N$67` |
| C143 | 10µF | C-EUC0805 / C0805 | 1:`GND`, 2:`VIN` |
| C144 | 0.1µF | C-EUC0805 / C0805 | 1:`N$72`, 2:`N$71` |
| C145 | 22µF | C-EUC0603 / C0603 | 1:`+5V0_ADTR`, 2:`GND` |
| C146 | 22µF | C-EUC0603 / C0603 | 1:`+5V0_ADTR`, 2:`GND` |
| C147 | 10µF | C-EUC0805 / C0805 | 1:`VIN`, 2:`GND` |
| C148 | 10µF | C-EUC0805 / C0805 | 1:`VIN`, 2:`GND` |
| C149 | 22µF | C-EUC0603 / C0603 | 1:`+3V3_ADTR`, 2:`GND` |
| C150 | 10nF | C-EUC0603 / C0603 | 1:`N$82`, 2:`N$91` |
| C151 | 10µF | C-EUC0603 / C0603 | 1:`N$92`, 2:`GND` |
| C152 | 10nF | C-EUC0603 / C0603 | 1:`N$101`, 2:`GND` |
| C153 | 10µF | C-EUC0603 / C0603 | 1:`+5V0_ADTR`, 2:`GND` |
| C154 | 0.1µF | C-EUC0805 / C0805 | 1:`N$87`, 2:`N$81` |
| C155 | 22µF | C-EUC0603 / C0603 | 1:`+5V0_5`, 2:`GND` |
| C156 | 22µF | C-EUC0603 / C0603 | 1:`+5V0_5`, 2:`GND` |
| C157 | 10µF | C-EUC0805 / C0805 | 1:`VIN`, 2:`GND` |
| C158 | 10µF | C-EUC0805 / C0805 | 1:`VIN`, 2:`GND` |
| C159 | 22µF | C-EUC0603 / C0603 | 1:`+3V3_XO`, 2:`GND` |
| C160 | 10nF | C-EUC0603 / C0603 | 1:`N$102`, 2:`N$103` |
| C161 | 10µF | C-EUC0603 / C0603 | 1:`N$104`, 2:`GND` |
| C162 | 10nF | C-EUC0603 / C0603 | 1:`N$105`, 2:`GND` |
| C163 | 10µF | C-EUC0603 / C0603 | 1:`+5V0_5`, 2:`GND` |
| R1 | 3.09k | R-EU_M0805 / M0805 | 1:`N$4`, 2:`+1V0_FPGA` |
| R2 | 10k | R-EU_M0805 / M0805 | 1:`GND`, 2:`N$4` |
| R3 | 13.7k | R-EU_M0805 / M0805 | 1:`N$6`, 2:`+1V8_FPGA` |
| R4 | 10k | R-EU_M0805 / M0805 | 1:`GND`, 2:`N$6` |
| R5 | 32.2k | R-EU_M0805 / M0805 | 1:`N$9`, 2:`+3V3` |
| R6 | 10k | R-EU_M0805 / M0805 | 1:`GND`, 2:`N$9` |
| R7 | 32.2k | R-EU_M0805 / M0805 | 1:`N$12`, 2:`+3V3_FPGA` |
| R8 | 10k | R-EU_M0805 / M0805 | 1:`GND`, 2:`N$12` |
| R9 | 12k | R-EU_M0805 / M0805 | 1:`N$25`, 2:`N$27` |
| R10 | 10k | R-EU_M0805 / M0805 | 1:`GND`, 2:`N$25` |
| R11 | 32.2k | R-EU_M0805 / M0805 | 1:`N$18`, 2:`+3V3_ADAR_12` |
| R12 | 10k | R-EU_M0805 / M0805 | 1:`GND`, 2:`N$18` |
| R13 | 32.2k | R-EU_M0805 / M0805 | 1:`N$21`, 2:`+3V3_ADAR_34` |
| R14 | 10k | R-EU_M0805 / M0805 | 1:`GND`, 2:`N$21` |
| R15 | 32.2k | R-EU_M0805 / M0805 | 1:`N$24`, 2:`+3V3_VDD_SW` |
| R16 | 10k | R-EU_M0805 / M0805 | 1:`GND`, 2:`N$24` |
| R17 | 56.2k | R-EU_M0805 / M0805 | 1:`N$65`, 2:`+5V0_1` |
| R18 | 10k | R-EU_M0805 / M0805 | 1:`GND`, 2:`N$65` |
| R19 | 32.2k | R-EU_M0805 / M0805 | 1:`N$30`, 2:`+3V3_SW` |
| R20 | 10k | R-EU_M0805 / M0805 | 1:`GND`, 2:`N$30` |
| R21 | 34.8k | R-EU_M0805 / M0805 | 1:`N$33`, 2:`+3V4` |
| R22 | 10k | R-EU_M0805 / M0805 | 1:`GND`, 2:`N$33` |
| R23 | 56.2k | R-EU_M0805 / M0805 | 1:`N$36`, 2:`+5V0_0` |
| R24 | 10k | R-EU_M0805 / M0805 | 1:`GND`, 2:`N$36` |
| R25 | 56.2k | R-EU_M0805 / M0805 | 1:`N$39`, 2:`+5V0_ADAR` |
| R26 | 10k | R-EU_M0805 / M0805 | 1:`GND`, 2:`N$39` |
| R27 | 56.2k | R-EU_M0805 / M0805 | 1:`N$42`, 2:`+5V0_PA_1` |
| R28 | 10k | R-EU_M0805 / M0805 | 1:`GND`, 2:`N$42` |
| R29 | 56.2k | R-EU_M0805 / M0805 | 1:`N$45`, 2:`+5V0_PA_2` |
| R30 | 10k | R-EU_M0805 / M0805 | 1:`GND`, 2:`N$45` |
| R31 | 56.2k | R-EU_M0805 / M0805 | 1:`N$48`, 2:`+5V0_PA_3` |
| R32 | 10k | R-EU_M0805 / M0805 | 1:`GND`, 2:`N$48` |
| R33 | 61.9k | R-EU_M0805 / M0805 | 1:`N$51`, 2:`+5V5_PA` |
| R34 | 10k | R-EU_M0805 / M0805 | 1:`GND`, 2:`N$51` |
| R35 | 12k | R-EU_M0805 / M0805 | 1:`N$69`, 2:`N$70` |
| R36 | 10k | R-EU_M0805 / M0805 | 1:`GND`, 2:`N$69` |
| R37 | 56.2k | R-EU_M0805 / M0805 | 1:`N$75`, 2:`+5V0_2` |
| R38 | 10k | R-EU_M0805 / M0805 | 1:`GND`, 2:`N$75` |
| R39 | 2k | R-EU_M0805 / M0805 | 1:`N$79`, 2:`N$80` |
| R40 | 10k | R-EU_M0805 / M0805 | 1:`GND`, 2:`N$79` |
| R41 | 56.2k | R-EU_M0805 / M0805 | 1:`N$85`, 2:`+5V0_3` |
| R42 | 10k | R-EU_M0805 / M0805 | 1:`GND`, 2:`N$85` |
| R43 | 12k | R-EU_M0805 / M0805 | 1:`N$89`, 2:`N$90` |
| R44 | 10k | R-EU_M0805 / M0805 | 1:`GND`, 2:`N$89` |
| R45 | 56.2k | R-EU_M0805 / M0805 | 1:`N$95`, 2:`+5V0_4` |
| R46 | 10k | R-EU_M0805 / M0805 | 1:`GND`, 2:`N$95` |
| R47 | 12k | R-EU_M0805 / M0805 | 1:`N$99`, 2:`N$100` |
| R48 | 10k | R-EU_M0805 / M0805 | 1:`GND`, 2:`N$99` |
| R49 | 23.4k | R-EU_M0805 / M0805 | 1:`N$63`, 2:`N$67` |
| R50 | 10k | R-EU_M0805 / M0805 | 1:`GND`, 2:`N$63` |
| R51 | 56.2k | R-EU_M0805 / M0805 | 1:`N$77`, 2:`+5V0_ADTR` |
| R52 | 10k | R-EU_M0805 / M0805 | 1:`GND`, 2:`N$77` |
| R53 | 35.7k | R-EU_M0805 / M0805 | 1:`N$91`, 2:`+3V3_ADTR` |
| R54 | 11.5k | R-EU_M0805 / M0805 | 1:`GND`, 2:`N$91` |
| R55 | 56.2k | R-EU_M0805 / M0805 | 1:`N$97`, 2:`+5V0_5` |
| R56 | 10k | R-EU_M0805 / M0805 | 1:`GND`, 2:`N$97` |
| R57 | 35.7k | R-EU_M0805 / M0805 | 1:`N$103`, 2:`+3V3_XO` |
| R58 | 11.5k | R-EU_M0805 / M0805 | 1:`GND`, 2:`N$103` |
| SV1 |  | MA10-2 / MA10-2 | 1:`EN_+1V0_FPGA`, 2:`EN_+5V0_PA2`, 3:`EN_+1V8_FPGA`, 4:`EN_+5V0_PA3`, 5:`EN_+3V3_FPGA`, 6:`EN_+5V5_PA`, 7:`EN_+5V0_ADAR`, 8:`EN_+1V8_CLOCK`, 9:`EN_+3V3_ADAR12`, 10:`EN_+3V3_CLOCK`, 11:`EN_+3V3_ADAR34`, 12:`GND`, 13:`EN_+3V3_ADTR`, 14:`GND`, 15:`EN_+3V3_SW`, 16:`GND`, 17:`EN_+3V3_VDD_SW`, 18:`GND`, 19:`EN_+5V0_PA1`, 20:`GND` |
| U1 |  | TPS562208DDCT / DDC0006A_N | 1:`GND`, 2:`N$1`, 3:`VIN`, 4:`N$4`, 5:`EN_+1V0_FPGA`, 6:`N$2` |
| U2 |  | TPS562208DDCT / DDC0006A_N | 1:`GND`, 2:`N$3`, 3:`VIN`, 4:`N$6`, 5:`EN_+1V8_FPGA`, 6:`N$5` |
| U3 |  | TPS562208DDCT / DDC0006A_N | 1:`GND`, 2:`N$7`, 3:`VIN`, 4:`N$9`, 5:`VIN`, 6:`N$8` |
| U4 |  | TPS562208DDCT / DDC0006A_N | 1:`GND`, 2:`N$10`, 3:`VIN`, 4:`N$12`, 5:`EN_+3V3_FPGA`, 6:`N$11` |
| U5 |  | ADM7151ACPZ-04-R7 / CP_8_11_ADI | 1:`N$13`, 2:`+3V3_AN`, 3:`N$15`, 4:`GND`, 5:`N$25`, 6:`N$27`, 7:`+5V0_0`, 8:`+5V0_0`, 9:`GND` |
| U6 |  | TPS562208DDCT / DDC0006A_N | 1:`GND`, 2:`N$16`, 3:`VIN`, 4:`N$18`, 5:`EN_+3V3_ADAR12`, 6:`N$17` |
| U7 |  | TPS562208DDCT / DDC0006A_N | 1:`GND`, 2:`N$19`, 3:`VIN`, 4:`N$21`, 5:`EN_+3V3_ADAR34`, 6:`N$20` |
| U8 |  | TPS562208DDCT / DDC0006A_N | 1:`GND`, 2:`N$22`, 3:`VIN`, 4:`N$24`, 5:`EN_+3V3_VDD_SW`, 6:`N$23` |
| U9 |  | TPS562208DDCT / DDC0006A_N | 1:`GND`, 2:`N$26`, 3:`VIN`, 4:`N$65`, 5:`VIN`, 6:`N$64` |
| U10 |  | TPS562208DDCT / DDC0006A_N | 1:`GND`, 2:`N$28`, 3:`VIN`, 4:`N$30`, 5:`EN_+3V3_SW`, 6:`N$29` |
| U11 |  | TPS562208DDCT / DDC0006A_N | 1:`GND`, 2:`N$31`, 3:`VIN`, 4:`N$33`, 5:`VIN`, 6:`N$32` |
| U12 |  | TPS562208DDCT / DDC0006A_N | 1:`GND`, 2:`N$34`, 3:`VIN`, 4:`N$36`, 5:`VIN`, 6:`N$35` |
| U13 |  | TPS562208DDCT / DDC0006A_N | 1:`GND`, 2:`N$37`, 3:`VIN`, 4:`N$39`, 5:`EN_+5V0_ADAR`, 6:`N$38` |
| U14 |  | TPS562208DDCT / DDC0006A_N | 1:`GND`, 2:`N$40`, 3:`VIN`, 4:`N$42`, 5:`EN_+5V0_PA1`, 6:`N$41` |
| U15 |  | TPS562208DDCT / DDC0006A_N | 1:`GND`, 2:`N$43`, 3:`VIN`, 4:`N$45`, 5:`EN_+5V0_PA2`, 6:`N$44` |
| U16 |  | TPS562208DDCT / DDC0006A_N | 1:`GND`, 2:`N$46`, 3:`VIN`, 4:`N$48`, 5:`EN_+5V0_PA3`, 6:`N$47` |
| U17 |  | TPS562208DDCT / DDC0006A_N | 1:`GND`, 2:`N$49`, 3:`VIN`, 4:`N$51`, 5:`EN_+5V5_PA`, 6:`N$50` |
| U18 |  | LM2662MX/NOPB / M08A | 2:`N$54`, 3:`GND`, 4:`N$55`, 5:`-3V3_SW`, 6:`GND`, 8:`+3V3_SW` |
| U19 |  | LM2662MX/NOPB / M08A | 2:`N$52`, 3:`GND`, 4:`N$53`, 5:`-3V4`, 6:`GND`, 8:`+3V4` |
| U20 |  | LM2662MX/NOPB / M08A | 2:`N$56`, 3:`GND`, 4:`N$57`, 5:`-5V0_ADAR12`, 6:`GND`, 8:`+5V0_ADAR` |
| U21 |  | LM2662MX/NOPB / M08A | 2:`N$58`, 3:`GND`, 4:`N$59`, 5:`-5V0_ADAR34`, 6:`GND`, 8:`+5V0_ADAR` |
| U22 |  | LM2662MX/NOPB / M08A | 2:`N$60`, 3:`GND`, 4:`N$61`, 5:`-5V5_PA`, 6:`GND`, 8:`+5V5_PA` |
| U23 |  | ADM7151ACPZ-04-R7 / CP_8_11_ADI | 1:`N$66`, 2:`+3V3_CLOCK`, 3:`N$68`, 4:`GND`, 5:`N$69`, 6:`N$70`, 7:`EN_+3V3_CLOCK`, 8:`+5V0_1`, 9:`GND` |
| U24 |  | TPS562208DDCT / DDC0006A_N | 1:`GND`, 2:`N$73`, 3:`VIN`, 4:`N$75`, 5:`VIN`, 6:`N$74` |
| U25 |  | ADM7151ACPZ-04-R7 / CP_8_11_ADI | 1:`N$76`, 2:`+1V8_CLOCK`, 3:`N$78`, 4:`GND`, 5:`N$79`, 6:`N$80`, 7:`EN_+1V8_CLOCK`, 8:`+5V0_2`, 9:`GND` |
| U26 |  | TPS562208DDCT / DDC0006A_N | 1:`GND`, 2:`N$83`, 3:`VIN`, 4:`N$85`, 5:`VIN`, 6:`N$84` |
| U27 |  | ADM7151ACPZ-04-R7 / CP_8_11_ADI | 1:`N$86`, 2:`+3V3_LO_1`, 3:`N$88`, 4:`GND`, 5:`N$89`, 6:`N$90`, 7:`+5V0_3`, 8:`+5V0_3`, 9:`GND` |
| U28 |  | TPS562208DDCT / DDC0006A_N | 1:`GND`, 2:`N$93`, 3:`VIN`, 4:`N$95`, 5:`VIN`, 6:`N$94` |
| U29 |  | ADM7151ACPZ-04-R7 / CP_8_11_ADI | 1:`N$96`, 2:`+3V3_LO_2`, 3:`N$98`, 4:`GND`, 5:`N$99`, 6:`N$100`, 7:`+5V0_4`, 8:`+5V0_4`, 9:`GND` |
| U30 |  | ADM7151ACPZ-04-R7 / CP_8_11_ADI | 1:`N$14`, 2:`+5V0_LO`, 3:`N$62`, 4:`GND`, 5:`N$63`, 6:`N$67`, 7:`VIN`, 8:`VIN`, 9:`GND` |
| U31 |  | TPS562208DDCT / DDC0006A_N | 1:`GND`, 2:`N$71`, 3:`VIN`, 4:`N$77`, 5:`VIN`, 6:`N$72` |
| U32 |  | TPS7A8300RGRR / RGR20_2P05X2P05_TEX | 1:`+3V3_ADTR`, 2:`N$82`, 3:`N$91`, 8:`GND`, 12:`N$92`, 13:`N$101`, 14:`EN_+3V3_ADTR`, 15:`+5V0_ADTR`, 16:`+5V0_ADTR`, 17:`+5V0_ADTR`, 18:`GND`, 19:`+3V3_ADTR`, 20:`+3V3_ADTR`, 21:`GND` |
| U33 |  | TPS562208DDCT / DDC0006A_N | 1:`GND`, 2:`N$81`, 3:`VIN`, 4:`N$97`, 5:`VIN`, 6:`N$87` |
| U34 |  | TPS7A8300RGRR / RGR20_2P05X2P05_TEX | 1:`+3V3_XO`, 2:`N$102`, 3:`N$103`, 8:`GND`, 12:`N$104`, 13:`N$105`, 14:`+5V0_5`, 15:`+5V0_5`, 16:`+5V0_5`, 17:`+5V0_5`, 18:`GND`, 19:`+3V3_XO`, 20:`+3V3_XO`, 21:`GND` |
| U$1 | 2.2µH | POWER_INDUCTOR / IND_VLP8040T-1R0N_TDK | 1:`+1V0_FPGA`, 2:`N$1` |
| U$2 | 2.2µH | POWER_INDUCTOR / IND_VLP8040T-1R0N_TDK | 1:`+1V8_FPGA`, 2:`N$3` |
| U$3 | 3.3µH | POWER_INDUCTOR / IND_VLP8040T-1R0N_TDK | 1:`+3V3`, 2:`N$7` |
| U$4 | 3.3µH | POWER_INDUCTOR / IND_VLP8040T-1R0N_TDK | 1:`+3V3_FPGA`, 2:`N$10` |
| U$5 | 3.3µH | POWER_INDUCTOR / IND_VLP8040T-1R0N_TDK | 1:`+5V0_1`, 2:`N$26` |
| U$6 | 3.3µH | POWER_INDUCTOR / IND_VLP8040T-1R0N_TDK | 1:`+3V3_ADAR_12`, 2:`N$16` |
| U$7 | 3.3µH | POWER_INDUCTOR / IND_VLP8040T-1R0N_TDK | 1:`+3V3_ADAR_34`, 2:`N$19` |
| U$8 | 3.3µH | POWER_INDUCTOR / IND_VLP8040T-1R0N_TDK | 1:`+3V3_VDD_SW`, 2:`N$22` |
| U$9 | 3.3µH | POWER_INDUCTOR / IND_VLP8040T-1R0N_TDK | 1:`+5V0_2`, 2:`N$73` |
| U$10 | 3.3µH | POWER_INDUCTOR / IND_VLP8040T-1R0N_TDK | 1:`+3V3_SW`, 2:`N$28` |
| U$11 | 3.3µH | POWER_INDUCTOR / IND_VLP8040T-1R0N_TDK | 1:`+3V4`, 2:`N$31` |
| U$12 | 3.3µH | POWER_INDUCTOR / IND_VLP8040T-1R0N_TDK | 1:`+5V0_0`, 2:`N$34` |
| U$13 | 3.3µH | POWER_INDUCTOR / IND_VLP8040T-1R0N_TDK | 1:`+5V0_ADAR`, 2:`N$37` |
| U$14 | 3.3µH | POWER_INDUCTOR / IND_VLP8040T-1R0N_TDK | 1:`+5V0_PA_1`, 2:`N$40` |
| U$15 | 3.3µH | POWER_INDUCTOR / IND_VLP8040T-1R0N_TDK | 1:`+5V0_PA_2`, 2:`N$43` |
| U$16 | 3.3µH | POWER_INDUCTOR / IND_VLP8040T-1R0N_TDK | 1:`+5V0_PA_3`, 2:`N$46` |
| U$17 | 3.3µH | POWER_INDUCTOR / IND_VLP8040T-1R0N_TDK | 1:`+5V5_PA`, 2:`N$49` |
| U$18 | 3.3µH | POWER_INDUCTOR / IND_VLP8040T-1R0N_TDK | 1:`+5V0_3`, 2:`N$83` |
| U$19 | 3.3µH | POWER_INDUCTOR / IND_VLP8040T-1R0N_TDK | 1:`+5V0_4`, 2:`N$93` |
| U$20 | 3.3µH | POWER_INDUCTOR / IND_VLP8040T-1R0N_TDK | 1:`+5V0_ADTR`, 2:`N$71` |
| U$21 | 3.3µH | POWER_INDUCTOR / IND_VLP8040T-1R0N_TDK | 1:`+5V0_5`, 2:`N$81` |
| X1 |  | AK300/2 / AK300/2 | 1:`VIN`, 2:`GND` |
| X2 |  | 22-23-2021 / 22-23-2021 | 1:`+5V0_1`, 2:`GND` |
| X3 |  | 22-23-2021 / 22-23-2021 | 1:`+5V5_PA`, 2:`GND` |
| X4 |  | 22-23-2021 / 22-23-2021 | 1:`+1V0_FPGA`, 2:`GND` |
| X5 |  | 22-23-2021 / 22-23-2021 | 1:`+1V8_FPGA`, 2:`GND` |
| X6 |  | 22-23-2021 / 22-23-2021 | 1:`+5V0_LO`, 2:`GND` |
| X7 |  | 22-23-2021 / 22-23-2021 | 1:`+3V3_LO_2`, 2:`GND` |
| X8 |  | 22-23-2021 / 22-23-2021 | 1:`+3V3_LO_1`, 2:`GND` |
| X9 |  | 22-23-2021 / 22-23-2021 | 1:`+5V0_2`, 2:`GND` |
| X10 |  | 22-23-2021 / 22-23-2021 | 1:`+1V8_CLOCK`, 2:`GND` |
| X11 |  | 22-23-2021 / 22-23-2021 | 1:`+3V3_CLOCK`, 2:`GND` |
| X12 |  | 22-23-2021 / 22-23-2021 | 1:`+3V3_AN`, 2:`GND` |
| X13 |  | 22-23-2021 / 22-23-2021 | 1:`+5V0_ADAR`, 2:`GND` |
| X14 |  | 22-23-2021 / 22-23-2021 | 1:`+3V3_ADAR_12`, 2:`GND` |
| X15 |  | 22-23-2021 / 22-23-2021 | 1:`+3V3_ADAR_34`, 2:`GND` |
| X16 |  | 22-23-2021 / 22-23-2021 | 1:`+3V3`, 2:`GND` |
| X17 |  | 22-23-2021 / 22-23-2021 | 1:`+5V0_3`, 2:`GND` |
| X18 |  | 22-23-2021 / 22-23-2021 | 1:`-3V3_SW`, 2:`GND` |
| X19 |  | 22-23-2021 / 22-23-2021 | 1:`-5V5_PA`, 2:`GND` |
| X20 |  | 22-23-2021 / 22-23-2021 | 1:`-5V0_ADAR34`, 2:`GND` |
| X21 |  | 22-23-2021 / 22-23-2021 | 1:`-5V0_ADAR12`, 2:`GND` |
| X22 |  | 22-23-2021 / 22-23-2021 | 1:`+5V0_0`, 2:`GND` |
| X23 |  | 22-23-2021 / 22-23-2021 | 1:`+3V4`, 2:`GND` |
| X24 |  | 22-23-2021 / 22-23-2021 | 1:`-3V4`, 2:`GND` |
| X25 |  | 22-23-2021 / 22-23-2021 | 1:`+5V0_4`, 2:`GND` |
| X26 |  | 22-23-2021 / 22-23-2021 | 1:`+5V0_ADTR`, 2:`GND` |
| X27 |  | 22-23-2021 / 22-23-2021 | 1:`+3V3_FPGA`, 2:`GND` |
| X28 |  | 22-23-2021 / 22-23-2021 | 1:`+5V0_5`, 2:`GND` |
| X29 |  | 22-23-2021 / 22-23-2021 | 1:`+3V3_SW`, 2:`GND` |
| X30 |  | 22-23-2021 / 22-23-2021 | 1:`+3V3_VDD_SW`, 2:`GND` |
| X31 |  | 22-23-2021 / 22-23-2021 | 1:`+5V0_PA_1`, 2:`GND` |
| X32 |  | 22-23-2021 / 22-23-2021 | 1:`+5V0_PA_2`, 2:`GND` |
| X33 |  | 22-23-2021 / 22-23-2021 | 1:`+5V0_PA_3`, 2:`GND` |
| X34 |  | 22-23-2021 / 22-23-2021 | 1:`+3V3_ADTR`, 2:`GND` |
| X35 |  | 22-23-2021 / 22-23-2021 | 1:`+3V3_XO`, 2:`GND` |
