herasymyuks/PLFM_RADAR-aeris/engineering/ELECTRICAL/connection_diagrams/RF_PA_connection_report.md

# RF_PA — Component-to-net connection report

Project AERIS-10 · Drawing ID ELEC-CON-RF_PA · Rev A · 2026-10-09 · Status: SOURCE-DERIVED  
Source: `4_Schematics and Boards Layout/4_6_Schematics/PowerAmplifierBoard/RF_PA.sch` (EAGLE 9.6.2), `4_Schematics and Boards Layout/4_6_Schematics/PowerAmplifierBoard/RF_PA.brd`; generated by `tools/gen_schematic_reports.py`.

## 1. Summary

| Item | Count |
|---|---|
| Sheets | 1 |
| Parts (all) / physical | 43 / 25 |
| Nets | 15 |
| Pin connections | 78 |
| Single-pin nets | 0 |
| Unconnected pins on placed gates | 0 |
| Physical parts without value | 6 |
| Board airwires (unrouted connections, layer 19) | 0 |
| Missing symbol/footprint records | 0 |

## 2. Connector pin-outs

Parts whose package name or prefix identifies a connector (header, SMA, terminal block, USB).

### J1 — 142-0731-211 (1420731211)

| Pad | Pin name | Net | Sheet |
|---|---|---|---|
| 1 | 1 | `N$2` | 1 |
| 2 | 2 | `GND` | 1 |
| 3 | 3 | `GND` | 1 |
| 4 | 4 | `GND` | 1 |
| 5 | 5 | `GND` | 1 |

### J2 — 142-0731-211 (1420731211)

| Pad | Pin name | Net | Sheet |
|---|---|---|---|
| 1 | 1 | `N$8` | 1 |
| 2 | 2 | `GND` | 1 |
| 3 | 3 | `GND` | 1 |
| 4 | 4 | `GND` | 1 |
| 5 | 5 | `GND` | 1 |

### X2 — 22-23-2021 (22-23-2021)

| Pad | Pin name | Net | Sheet |
|---|---|---|---|
| 1 | S | `VG` | 1 |
| 2 | S | `GND` | 1 |

### X3 — 22-23-2031 (22-23-2031)

| Pad | Pin name | Net | Sheet |
|---|---|---|---|
| 1 | S | `VD` | 1 |
| 2 | S | `VIN_M` | 1 |
| 3 | S | `GND` | 1 |

## 3. Net fan-out (nets with ≥ 8 connections)

| Net | Connections | Class |
|---|---|---|
| `GND` | 38 | 0 |
| `VIN_M` | 10 | 0 |

## 4. Component-to-net table

Full machine-readable form: `netlists/RF_PA_netlist_by_part.csv`. Physical parts only; pads shown when the device defines a package connection.

| Part | Value | Device / package | Connections (pad:net) |
|---|---|---|---|
| 22V |  | AK300/2 / AK300/2 | 1:`VD`, 2:`GND` |
| C1 | 10µF | C-EUC1206 / C1206 | 1:`GND`, 2:`N$3` |
| C2 | 0.1µF | C-EUC0402 / C0402 | 1:`GND`, 2:`N$4` |
| C3 | 0.1µF | C-EUC0402 / C0402 | 1:`GND`, 2:`N$1` |
| C4 | 10µF | C-EUC1206 / C1206 | 1:`GND`, 2:`N$5` |
| C5 | 10µF | C-EUC1206 / C1206 | 1:`N$10`, 2:`GND` |
| C6 | 0.1µF | C-EUC0402 / C0402 | 1:`GND`, 2:`N$6` |
| C7 | 0.1µF | C-EUC0402 / C0402 | 1:`GND`, 2:`N$7` |
| C8 | 0.1µF | C-EUC0402 / C0402 | 1:`N$11`, 2:`GND` |
| C9 | 0.1µF | C-EUC0402 / C0402 | 1:`N$12`, 2:`GND` |
| J1 |  | 142-0731-211 / 1420731211 | 1:`N$2`, 2:`GND`, 3:`GND`, 4:`GND`, 5:`GND` |
| J2 |  | 142-0731-211 / 1420731211 | 1:`N$8`, 2:`GND`, 3:`GND`, 4:`GND`, 5:`GND` |
| R1 | 10R | R-EU_R0402 / R0402 | 1:`N$3`, 2:`VG` |
| R2 | 0R | R-EU_R0402 / R0402 | 1:`N$4`, 2:`VG` |
| R3 | 0R | R-EU_R0402 / R0402 | 1:`N$1`, 2:`VG` |
| R4 | 10R | R-EU_R0402 / R0402 | 1:`N$5`, 2:`VIN_M` |
| R5 | 0R | R-EU_R0402 / R0402 | 1:`N$7`, 2:`VIN_M` |
| R6 | 0R | R-EU_R0603 / R0603 | 1:`N$6`, 2:`VIN_M` |
| R7 | 0R | R-EU_R0402 / R0402 | 1:`VIN_M`, 2:`N$10` |
| R8 | 0R | R-EU_R0402 / R0402 | 1:`VIN_M`, 2:`N$11` |
| R9 | 0R | R-EU_R0402 / R0402 | 1:`VIN_M`, 2:`N$12` |
| R10 | 5mR | WSL2816R1000FEH / WSL2816_VIS | 1:`VIN_M`, 2:`VD` |
| U$1 |  | QPA2962_B / QPA2962_B | GND:`GND`, RFIN:`N$2`, RFOUT:`N$8`, VD1:`VIN_M`, VD2:`VIN_M`, VG:`VG` |
| X2 |  | 22-23-2021 / 22-23-2021 | 1:`VG`, 2:`GND` |
| X3 |  | 22-23-2031 / 22-23-2031 | 1:`VD`, 2:`VIN_M`, 3:`GND` |
