herasymyuks/PLFM_RADAR-aeris/beta/pcb/MAIN_BOARD_REVB/reports/DRC_report.txt

** Drc report for MAIN_BOARD_REVB.kicad_pcb **
** Created on 2026-10-09T16:15:37 **
** Report includes: Errors, Warnings, Exclusions **

** Found 1071 DRC violations **
[shorting_items]: Items shorting two nets (nets GND and )
    Local override; error
    @(47.6000 mm, -20.4500 mm): Track [GND] on F.Cu, length 0.2500 mm
    @(47.5626 mm, -20.6526 mm): PTH pad V [<no net>] of U69
[hole_clearance]: Hole clearance violation (board setup constraints hole clearance 0 mm; actual < 0)
    Rule: board setup constraints hole; error
    @(47.6000 mm, -20.4500 mm): Track [GND] on F.Cu, length 0.2500 mm
    @(47.5626 mm, -20.6526 mm): PTH pad V [<no net>] of U69
[shorting_items]: Items shorting two nets (nets  and GND)
    Local override; error
    @(48.3500 mm, -21.4400 mm): PTH pad V_4 [<no net>] of U69
    @(48.3500 mm, -21.4400 mm): Track [GND] on F.Cu, length 0.7534 mm
[hole_clearance]: Hole clearance violation (board setup constraints hole clearance 0 mm; actual < 0)
    Rule: board setup constraints hole; error
    @(48.3500 mm, -21.4400 mm): Track [GND] on F.Cu, length 0.7534 mm
    @(48.3500 mm, -21.4400 mm): PTH pad V_4 [<no net>] of U69
[shorting_items]: Items shorting two nets (nets  and GND)
    Local override; error
    @(49.1374 mm, -21.4400 mm): PTH pad V_7 [<no net>] of U69
    @(48.3500 mm, -21.4400 mm): Track [GND] on F.Cu, length 0.7534 mm
[hole_clearance]: Hole clearance violation (board setup constraints hole clearance 0 mm; actual < 0)
    Rule: board setup constraints hole; error
    @(48.3500 mm, -21.4400 mm): Track [GND] on F.Cu, length 0.7534 mm
    @(49.1374 mm, -21.4400 mm): PTH pad V_7 [<no net>] of U69
[shorting_items]: Items shorting two nets (nets  and GND)
    Local override; error
    @(47.8726 mm, -49.7526 mm): PTH pad V [<no net>] of U7
    @(47.9331 mm, -49.9831 mm): Track (arc) [GND] on F.Cu, length 0.0367 mm
[hole_clearance]: Hole clearance violation (board setup constraints hole clearance 0 mm; actual < 0)
    Rule: board setup constraints hole; error
    @(47.9331 mm, -49.9831 mm): Track (arc) [GND] on F.Cu, length 0.0367 mm
    @(47.8726 mm, -49.7526 mm): PTH pad V [<no net>] of U7
[hole_clearance]: Hole clearance violation (board setup constraints hole clearance 0 mm; actual < 0)
    Rule: board setup constraints hole; error
    @(47.6000 mm, -20.7241 mm): Track (arc) [GND] on F.Cu, length 0.0190 mm
    @(47.5626 mm, -20.6526 mm): PTH pad V [<no net>] of U69
[shorting_items]: Items shorting two nets (nets STM32_SCLK_1V8 and GND)
    Local override; error
    @(148.7500 mm, -213.0000 mm): Track [STM32_SCLK_1V8] on B.Cu, length 34.0000 mm
    @(148.0321 mm, -197.2400 mm): PTH pad 3 [GND] of J26
[shorting_items]: Items shorting two nets (nets GND and STEPPER_CLK+)
    Local override; error
    @(58.7200 mm, -75.9100 mm): PTH pad 3 [GND] of JP9
    @(59.7500 mm, -74.5000 mm): Track [STEPPER_CLK+] on In7.Cu, length 2.7500 mm
[shorting_items]: Items shorting two nets (nets STEPPER_CLK+ and EN/DIS_RFPA_VDD)
    Local override; error
    @(59.7500 mm, -77.2500 mm): Track [STEPPER_CLK+] on In7.Cu, length 14.4957 mm
    @(64.9200 mm, -80.9500 mm): PTH pad 1 [EN/DIS_RFPA_VDD] of JP10
[clearance]: Clearance violation ( clearance 0.1000 mm; actual 0.0775 mm)
    Local override; error
    @(58.7200 mm, -80.9900 mm): PTH pad 1 [GND] of JP9
    @(58.7500 mm, -79.0000 mm): Track [STEPPER_CW+] on In7.Cu, length 15.9099 mm
[clearance]: Clearance violation ( clearance 0.1000 mm; actual 0.0994 mm)
    Local override; error
    @(226.0000 mm, -142.0000 mm): Pad 89 [GND] of ADAR3_0 on F.Cu
    @(227.2500 mm, -140.1000 mm): Via [N$59] on F.Cu - B.Cu
[shorting_items]: Items shorting two nets (nets VG_4 and STM32_SCL1)
    Local override; error
    @(54.2300 mm, -59.5000 mm): PTH pad 1 [VG_4] of X_15
    @(50.5000 mm, -57.2500 mm): Track [STM32_SCL1] on In7.Cu, length 21.9203 mm
[shorting_items]: Items shorting two nets (nets STM32_SCL1 and )
    Local override; error
    @(66.0000 mm, -78.0000 mm): Track [STM32_SCL1] on In7.Cu, length 13.0815 mm
    @(64.9200 mm, -78.4100 mm): PTH pad 2 [<no net>] of JP10
[shorting_items]: Items shorting two nets (nets STM32_SCL1 and EN/DIS_COOLING)
    Local override; error
    @(66.0000 mm, -78.0000 mm): Track [STM32_SCL1] on In7.Cu, length 13.0815 mm
    @(70.4700 mm, -80.8800 mm): PTH pad 1 [EN/DIS_COOLING] of JP4
[shorting_items]: Items shorting two nets (nets STM32_SCL1 and )
    Local override; error
    @(66.0000 mm, -72.7500 mm): Track [STM32_SCL1] on In7.Cu, length 5.2500 mm
    @(64.9200 mm, -78.4100 mm): PTH pad 2 [<no net>] of JP10
[shorting_items]: Items shorting two nets (nets GND and STM32_SCL1)
    Local override; error
    @(64.9200 mm, -75.8700 mm): PTH pad 3 [GND] of JP10
    @(66.0000 mm, -72.7500 mm): Track [STM32_SCL1] on In7.Cu, length 5.2500 mm
[shorting_items]: Items shorting two nets (nets <no net> and RF_TX)
    Local override; error
    @(82.9585 mm, -211.9254 mm): Polygon [<no net>] of U$2 on F.Cu
    @(82.4900 mm, -213.0575 mm): Track [RF_TX] on F.Cu, length 1.0389 mm
[clearance]: Clearance violation ( clearance 0.1000 mm; actual 0.0000 mm)
    Local override; error
    @(82.3364 mm, -212.0186 mm): Track (arc) [RF_TX] on F.Cu, length 0.1207 mm
    @(82.9585 mm, -211.9254 mm): Polygon [<no net>] of U$2 on F.Cu
[shorting_items]: Items shorting two nets (nets STM32_RX5 and STM32_TX5)
    Local override; error
    @(49.7200 mm, -87.0200 mm): PTH pad 3 [STM32_RX5] of JP8
    @(48.2500 mm, -88.2500 mm): Track [STM32_TX5] on In5.Cu, length 17.2500 mm
[shorting_items]: Items shorting two nets (nets GND and STM32_TX5)
    Local override; error
    @(52.2600 mm, -87.0200 mm): PTH pad 4 [GND] of JP8
    @(48.2500 mm, -88.2500 mm): Track [STM32_TX5] on In5.Cu, length 17.2500 mm
[shorting_items]: Items shorting two nets (nets GND and STM32_RX5)
    Local override; error
    @(52.2600 mm, -87.0200 mm): PTH pad 4 [GND] of JP8
    @(50.5000 mm, -88.0000 mm): Track [STM32_RX5] on In5.Cu, length 16.2500 mm
[shorting_items]: Items shorting two nets (nets <no net> and RF_TX_FIL)
    Local override; error
    @(101.3735 mm, -211.9254 mm): Polygon [<no net>] of U$2 on F.Cu
    @(101.1000 mm, -211.9100 mm): Track (arc) [RF_TX_FIL] on F.Cu, length 0.3770 mm
[shorting_items]: Items shorting two nets (nets STM32_SDA3 and GYR_INT)
    Local override; error
    @(46.0000 mm, -95.2500 mm): Track [STM32_SDA3] on In5.Cu, length 16.2500 mm
    @(52.4100 mm, -94.1200 mm): PTH pad 8 [GYR_INT] of JP7
[shorting_items]: Items shorting two nets (nets MAG_DRDY and STM32_SDA3)
    Local override; error
    @(47.3300 mm, -94.1200 mm): PTH pad 6 [MAG_DRDY] of JP7
    @(46.0000 mm, -95.2500 mm): Track [STM32_SDA3] on In5.Cu, length 16.2500 mm
[shorting_items]: Items shorting two nets (nets ACC_INT and STM32_SDA3)
    Local override; error
    @(49.8700 mm, -94.1200 mm): PTH pad 7 [ACC_INT] of JP7
    @(46.0000 mm, -95.2500 mm): Track [STM32_SDA3] on In5.Cu, length 16.2500 mm
[shorting_items]: Items shorting two nets (nets GND and STM32_SCLK_1V8)
    Local override; error
    @(142.7501 mm, -233.4278 mm): PTH pad 3 [GND] of J25
    @(149.5000 mm, -227.7500 mm): Track [STM32_SCLK_1V8] on In7.Cu, length 9.1924 mm
[shorting_items]: Items shorting two nets (nets GND and STM32_SCLK_1V8)
    Local override; error
    @(142.7501 mm, -233.4278 mm): PTH pad 3 [GND] of J25
    @(143.0000 mm, -234.2500 mm): Track [STM32_SCLK_1V8] on In7.Cu, length 19.0000 mm
[shorting_items]: Items shorting two nets (nets GND and STM32_MISO_1V8)
    Local override; error
    @(218.6500 mm, -233.4179 mm): PTH pad 3 [GND] of J33
    @(218.5000 mm, -234.2500 mm): Track [STM32_MISO_1V8] on In7.Cu, length 5.3033 mm
[hole_clearance]: Hole clearance violation (board setup constraints hole clearance 0 mm; actual < 0)
    Rule: board setup constraints hole; error
    @(218.5000 mm, -234.2500 mm): Track [STM32_MISO_1V8] on In7.Cu, length 5.3033 mm
    @(218.6500 mm, -233.4179 mm): PTH pad 3 [GND] of J33
[shorting_items]: Items shorting two nets (nets STM32_MISO_1V8 and GND)
    Local override; error
    @(162.2500 mm, -234.2500 mm): Track [STM32_MISO_1V8] on In7.Cu, length 56.2500 mm
    @(218.6500 mm, -233.4179 mm): PTH pad 3 [GND] of J33
[clearance]: Clearance violation ( clearance 0.1000 mm; actual 0.0994 mm)
    Local override; error
    @(150.0000 mm, -218.0000 mm): Pad 89 [GND] of ADAR1_0 on F.Cu
    @(151.5500 mm, -219.9000 mm): Via [STM32_MISO_1V8] on F.Cu - B.Cu
[shorting_items]: Items shorting two nets (nets STM32_MOSI_1V8 and GND)
    Local override; error
    @(140.5000 mm, -185.0000 mm): Track [STM32_MOSI_1V8] on B.Cu, length 22.2500 mm
    @(140.8479 mm, -197.2400 mm): PTH pad 5 [GND] of J26
[hole_clearance]: Hole clearance violation (board setup constraints hole clearance 0 mm; actual < 0)
    Rule: board setup constraints hole; error
    @(140.5000 mm, -185.0000 mm): Track [STM32_MOSI_1V8] on B.Cu, length 22.2500 mm
    @(140.8479 mm, -197.2400 mm): PTH pad 5 [GND] of J26
[clearance]: Clearance violation ( clearance 0.1000 mm; actual 0.0994 mm)
    Local override; error
    @(150.0000 mm, -218.0000 mm): Pad 89 [GND] of ADAR1_0 on F.Cu
    @(151.0500 mm, -219.9000 mm): Via [STM32_MOSI_1V8] on F.Cu - B.Cu
[shorting_items]: Items shorting two nets (nets GND and FPGA_FLASH_NRST)
    Local override; error
    @(63.4100 mm, -125.3800 mm): PTH pad 3 [GND] of JP17
    @(72.2000 mm, -114.8500 mm): Track [FPGA_FLASH_NRST] on In7.Cu, length 12.8693 mm
[shorting_items]: Items shorting two nets (nets GND and FPGA_FLASH_NRST)
    Local override; error
    @(63.4100 mm, -125.3800 mm): PTH pad 3 [GND] of JP17
    @(63.1000 mm, -123.9500 mm): Track [FPGA_FLASH_NRST] on In7.Cu, length 0.3000 mm
[clearance]: Clearance violation ( clearance 0.1000 mm; actual 0.0917 mm)
    Local override; error
    @(63.4100 mm, -125.3800 mm): PTH pad 3 [GND] of JP17
    @(62.8000 mm, -123.9500 mm): Track [FPGA_FLASH_NRST] on In7.Cu, length 0.6364 mm
[clearance]: Clearance violation ( clearance 0.1000 mm; actual 0.0994 mm)
    Local override; error
    @(150.0000 mm, -218.0000 mm): Pad 89 [GND] of ADAR1_0 on F.Cu
    @(152.0500 mm, -219.9000 mm): Via [ADAR_1_CS_1V8] on F.Cu - B.Cu
[shorting_items]: Items shorting two nets (nets GND and ADAR_3_CS_3V3)
    Local override; error
    @(63.4100 mm, -125.3800 mm): PTH pad 3 [GND] of JP17
    @(72.2500 mm, -126.5000 mm): Track [ADAR_3_CS_3V3] on In7.Cu, length 10.0000 mm
[shorting_items]: Items shorting two nets (nets ADAR_3_CS_3V3 and STM32_TX3)
    Local override; error
    @(72.2500 mm, -126.5000 mm): Track [ADAR_3_CS_3V3] on In7.Cu, length 10.0000 mm
    @(68.4900 mm, -125.3800 mm): PTH pad 1 [STM32_TX3] of JP17
[shorting_items]: Items shorting two nets (nets ADAR_3_CS_3V3 and STM32_RX3)
    Local override; error
    @(72.2500 mm, -126.5000 mm): Track [ADAR_3_CS_3V3] on In7.Cu, length 10.0000 mm
    @(65.9500 mm, -125.3800 mm): PTH pad 2 [STM32_RX3] of JP17
[shorting_items]: Items shorting two nets (nets +1V0_FPGA and ADAR_1_CS_3V3)
    Local override; error
    @(5.9700 mm, -173.6100 mm): PTH pad 1 [+1V0_FPGA] of X8
    @(7.5000 mm, -190.0000 mm): Track [ADAR_1_CS_3V3] on In5.Cu, length 39.5000 mm
[shorting_items]: Items shorting two nets (nets GND and ADAR_1_CS_3V3)
    Local override; error
    @(5.9700 mm, -171.0700 mm): PTH pad 2 [GND] of X8
    @(7.5000 mm, -190.0000 mm): Track [ADAR_1_CS_3V3] on In5.Cu, length 39.5000 mm
[clearance]: Clearance violation ( clearance 0.1000 mm; actual 0.0000 mm)
    Local override; error
    @(101.1350 mm, -147.0700 mm): Track [RF_RX_FIL] on F.Cu, length 0.2334 mm
    @(100.6215 mm, -147.0547 mm): Polygon [<no net>] of U$3 on F.Cu
[clearance]: Clearance violation ( clearance 0.1000 mm; actual 0.0000 mm)
    Local override; error
    @(101.6350 mm, -147.0700 mm): Track (arc) [RF_RX_FIL] on F.Cu, length 0.7854 mm
    @(100.6215 mm, -147.0547 mm): Polygon [<no net>] of U$3 on F.Cu
[shorting_items]: Items shorting two nets (nets <no net> and RF_RX)
    Local override; error
    @(82.2065 mm, -147.0547 mm): Polygon [<no net>] of U$3 on F.Cu
    @(82.7600 mm, -145.5025 mm): Track [RF_RX] on F.Cu, length 1.5328 mm
[shorting_items]: Items shorting two nets (nets <no net> and RF_RX)
    Local override; error
    @(82.2065 mm, -147.0547 mm): Polygon [<no net>] of U$3 on F.Cu
    @(82.7200 mm, -147.0700 mm): Track [RF_RX] on F.Cu, length 0.0491 mm
[clearance]: Clearance violation ( clearance 0.1000 mm; actual 0.0671 mm)
    Local override; error
    @(222.5000 mm, -231.0000 mm): Track [ADAR_2_CS_1V8] on In7.Cu, length 15.9099 mm
    @(215.0579 mm, -237.0100 mm): PTH pad 2 [GND] of J33
[shorting_items]: Items shorting two nets (nets ADAR_2_CS_1V8 and GND)
    Local override; error
    @(211.2500 mm, -242.2500 mm): Track [ADAR_2_CS_1V8] on In7.Cu, length 111.7500 mm
    @(155.5300 mm, -242.2321 mm): PTH pad 4 [GND] of J30
[hole_clearance]: Hole clearance violation (board setup constraints hole clearance 0 mm; actual < 0)
    Rule: board setup constraints hole; error
    @(211.2500 mm, -242.2500 mm): Track [ADAR_2_CS_1V8] on In7.Cu, length 111.7500 mm
    @(155.5300 mm, -242.2321 mm): PTH pad 4 [GND] of J30
[clearance]: Clearance violation ( clearance 0.1000 mm; actual 0.0671 mm)
    Local override; error
    @(222.5000 mm, -231.0000 mm): Track [ADAR_2_CS_1V8] on In7.Cu, length 15.9099 mm
    @(218.6500 mm, -233.4179 mm): PTH pad 3 [GND] of J33
[shorting_items]: Items shorting two nets (nets GND and EN_+5V0_PA2)
    Local override; error
    @(63.4100 mm, -125.3800 mm): PTH pad 3 [GND] of JP17
    @(60.0000 mm, -127.2500 mm): Track [EN_+5V0_PA2] on In5.Cu, length 18.3848 mm
[shorting_items]: Items shorting two nets (nets GND and M3S_VCTRL)
    Local override; error
    @(232.0000 mm, -235.5179 mm): PTH pad 3 [GND] of J38
    @(230.4419 mm, -236.2804 mm): Track [M3S_VCTRL] on In5.Cu, length 6.2777 mm
[shorting_items]: Items shorting two nets (nets M3S_VCTRL and GND)
    Local override; error
    @(161.2500 mm, -235.2500 mm): Track [M3S_VCTRL] on In5.Cu, length 26.7500 mm
    @(155.5300 mm, -235.0479 mm): PTH pad 2 [GND] of J30
[hole_clearance]: Hole clearance violation (board setup constraints hole clearance 0 mm; actual < 0)
    Rule: board setup constraints hole; error
    @(161.2500 mm, -235.2500 mm): Track [M3S_VCTRL] on In5.Cu, length 26.7500 mm
    @(155.5300 mm, -235.0479 mm): PTH pad 2 [GND] of J30
[shorting_items]: Items shorting two nets (nets GND and M3S_VCTRL)
    Local override; error
    @(208.7421 mm, -223.4100 mm): PTH pad 4 [GND] of J32
    @(209.0000 mm, -229.7500 mm): Track [M3S_VCTRL] on B.Cu, length 27.7500 mm
[hole_clearance]: Hole clearance violation (board setup constraints hole clearance 0 mm; actual < 0)
    Rule: board setup constraints hole; error
    @(209.0000 mm, -229.7500 mm): Track [M3S_VCTRL] on B.Cu, length 27.7500 mm
    @(208.7421 mm, -223.4100 mm): PTH pad 4 [GND] of J32
[shorting_items]: Items shorting two nets (nets  and GND)
    Local override; error
    @(48.3500 mm, -22.2274 mm): PTH pad V_5 [<no net>] of U69
    @(49.4605 mm, -21.4400 mm): Track (arc) [GND] on F.Cu, length 0.8722 mm
[clearance]: Clearance violation ( clearance 0.1000 mm; actual 0.0831 mm)
    Local override; error
    @(49.1374 mm, -22.2274 mm): PTH pad V_8 [<no net>] of U69
    @(49.4605 mm, -21.4400 mm): Track (arc) [GND] on F.Cu, length 0.8722 mm
[clearance]: Clearance violation ( clearance 0.1000 mm; actual 0.0443 mm)
    Local override; error
    @(48.3500 mm, -21.4400 mm): PTH pad V_4 [<no net>] of U69
    @(48.2293 mm, -21.3193 mm): Track (arc) [GND] on F.Cu, length 0.1341 mm
[shorting_items]: Items shorting two nets (nets  and GND)
    Local override; error
    @(48.3500 mm, -21.4400 mm): PTH pad V_4 [<no net>] of U69
    @(49.4605 mm, -21.4400 mm): Track (arc) [GND] on F.Cu, length 0.8722 mm
[hole_clearance]: Hole clearance violation (board setup constraints hole clearance 0 mm; actual < 0)
    Rule: board setup constraints hole; error
    @(48.2293 mm, -21.3193 mm): Track (arc) [GND] on F.Cu, length 0.1341 mm
    @(48.3500 mm, -21.4400 mm): PTH pad V_4 [<no net>] of U69
[hole_clearance]: Hole clearance violation (board setup constraints hole clearance 0 mm; actual < 0)
    Rule: board setup constraints hole; error
    @(49.4605 mm, -21.4400 mm): Track (arc) [GND] on F.Cu, length 0.8722 mm
    @(48.3500 mm, -21.4400 mm): PTH pad V_4 [<no net>] of U69
[shorting_items]: Items shorting two nets (nets  and GND)
    Local override; error
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
    @(89.6140 mm, -146.9990 mm): Polygon [<no net>] of U$3 on F.Cu
[clearance]: Clearance violation ( clearance 0.1000 mm; actual 0.0000 mm)
    Local override; error
    @(82.7200 mm, -147.0700 mm): Pad P$1 [RF_RX] of U$3 on F.Cu
    @(82.2065 mm, -147.0547 mm): Polygon [<no net>] of U$3 on F.Cu
[clearance]: Clearance violation ( clearance 0.1000 mm; actual 0.0000 mm)
    Local override; error
    @(101.1350 mm, -147.0700 mm): Pad P$2 [RF_RX_FIL] of U$3 on F.Cu
    @(100.6215 mm, -147.0547 mm): Polygon [<no net>] of U$3 on F.Cu
[clearance]: Clearance violation ( clearance 0.1000 mm; actual 0.0000 mm)
    Local override; error
    @(82.4450 mm, -211.9100 mm): Pad P$2 [RF_TX] of U$2 on F.Cu
    @(82.9585 mm, -211.9254 mm): Polygon [<no net>] of U$2 on F.Cu
[shorting_items]: Items shorting two nets (nets <no net> and RF_TX_FIL)
    Local override; error
    @(101.3735 mm, -211.9254 mm): Polygon [<no net>] of U$2 on F.Cu
    @(100.8600 mm, -211.9100 mm): Pad P$1 [RF_TX_FIL] of U$2 on F.Cu
[courtyards_overlap]: Courtyards overlap
    Rule: board setup constraints courtyard; error
    @(22.5000 mm, -199.6000 mm): Footprint Y_FT
    @(25.2000 mm, -199.2000 mm): Footprint C_XO
[courtyards_overlap]: Courtyards overlap
    Rule: board setup constraints courtyard; error
    @(22.5000 mm, -199.6000 mm): Footprint Y_FT
    @(19.6000 mm, -198.7500 mm): Footprint C_XI
[copper_edge_clearance]: Board edge clearance violation (board setup constraints edge clearance 0.2000 mm; actual 0.1196 mm)
    Rule: board setup constraints edge; error
    @(8.3600 mm, -204.4000 mm): NPTH pad of J_USB3
    @(8.4024 mm, -205.2070 mm): Track [USB_CC2] on In1.Cu, length 2.1695 mm
[track_width]: Track width (board setup constraints min width 0.1000 mm; actual 0.0750 mm)
    Rule: netclass 'Default'; error
    @(26.2482 mm, -205.2488 mm): Track [GND] on F.Cu, length 0.2096 mm
[track_width]: Track width (board setup constraints min width 0.1000 mm; actual 0.0750 mm)
    Rule: netclass 'Default'; error
    @(11.9155 mm, -205.8005 mm): Track [GND] on F.Cu, length 0.2821 mm
[track_width]: Track width (board setup constraints min width 0.1000 mm; actual 0.0750 mm)
    Rule: netclass 'Default'; error
    @(11.1157 mm, -205.8005 mm): Track [GND] on F.Cu, length 0.7998 mm
[track_width]: Track width (board setup constraints min width 0.1000 mm; actual 0.0750 mm)
    Rule: netclass 'Default'; error
    @(26.2482 mm, -205.9204 mm): Track [GND] on F.Cu, length 0.6716 mm
[track_width]: Track width (board setup constraints min width 0.1000 mm; actual 0.0750 mm)
    Rule: netclass 'Default'; error
    @(26.1000 mm, -204.5550 mm): Track [GND] on F.Cu, length 0.5456 mm
[track_width]: Track width (board setup constraints min width 0.1000 mm; actual 0.0750 mm)
    Rule: netclass 'Default'; error
    @(30.5044 mm, -211.3132 mm): Track [+3V3_FT] on F.Cu, length 0.1348 mm
[track_width]: Track width (board setup constraints min width 0.1000 mm; actual 0.0750 mm)
    Rule: netclass 'Default'; error
    @(30.9635 mm, -209.4982 mm): Track [+3V3_FT] on F.Cu, length 0.1377 mm
[track_width]: Track width (board setup constraints min width 0.1000 mm; actual 0.0750 mm)
    Rule: netclass 'Default'; error
    @(30.5044 mm, -211.4549 mm): Track [+3V3_FT] on F.Cu, length 0.1417 mm
[track_width]: Track width (board setup constraints min width 0.1000 mm; actual 0.0750 mm)
    Rule: netclass 'Default'; error
    @(31.1012 mm, -209.4982 mm): Track [+3V3_FT] on F.Cu, length 0.1389 mm
[track_width]: Track width (board setup constraints min width 0.1000 mm; actual 0.0750 mm)
    Rule: netclass 'Default'; error
    @(31.7450 mm, -209.4000 mm): Track [+3V3_FT] on F.Cu, length 0.5456 mm
[track_width]: Track width (board setup constraints min width 0.1000 mm; actual 0.0750 mm)
    Rule: netclass 'Default'; error
    @(9.6548 mm, -208.8995 mm): Track [USB_CC1] on F.Cu, length 0.4853 mm
[track_width]: Track width (board setup constraints min width 0.1000 mm; actual 0.0750 mm)
    Rule: netclass 'Default'; error
    @(9.1695 mm, -208.8995 mm): Track [USB_CC1] on F.Cu, length 0.2114 mm
[track_width]: Track width (board setup constraints min width 0.1000 mm; actual 0.0750 mm)
    Rule: netclass 'Default'; error
    @(7.1705 mm, -207.3505 mm): Track [USB_CC2] on F.Cu, length 0.2114 mm
[track_width]: Track width (board setup constraints min width 0.1000 mm; actual 0.0750 mm)
    Rule: netclass 'Default'; error
    @(6.7510 mm, -207.3505 mm): Track [USB_CC2] on F.Cu, length 0.4195 mm
[solder_mask_bridge]: Front solder mask aperture bridges items with different nets
    Rule: board setup solder mask min width; error
    @(48.6128 mm, -21.7872 mm): Track [GND] on F.Cu, length 0.5696 mm
    @(49.1374 mm, -22.2274 mm): PTH pad V_8 [<no net>] of U69
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
[silk_over_copper]: Silkscreen clipped by solder mask
    Local override; warning
    @(79.0850 mm, -89.4350 mm): Reference field of R169
    @(77.6600 mm, -91.5112 mm): Pad 133 [STM32_SWO] of U2 on F.Cu
[silk_over_copper]: Silkscreen clipped by solder mask
    Local override; warning
    @(79.0850 mm, -89.4350 mm): Reference field of R169
    @(78.1600 mm, -91.5112 mm): Pad 134 [DAC_1_VG_CLR] of U2 on F.Cu
[silk_over_copper]: Silkscreen clipped by solder mask
    Local override; warning
    @(79.0850 mm, -89.4350 mm): Reference field of R169
    @(78.6600 mm, -91.5112 mm): Pad 135 [DAC_1_VG_LDAC] of U2 on F.Cu
[silk_over_copper]: Silkscreen clipped by solder mask
    Local override; warning
    @(69.8350 mm, -82.1500 mm): Segment of JP4 on F.Silkscreen
    @(70.4700 mm, -80.8800 mm): PTH pad 1 [EN/DIS_COOLING] of JP4
[silk_over_copper]: Silkscreen clipped by solder mask
    Local override; warning
    @(64.2850 mm, -82.2200 mm): Segment of JP10 on F.Silkscreen
    @(64.9200 mm, -80.9500 mm): PTH pad 1 [EN/DIS_RFPA_VDD] of JP10
[silk_over_copper]: Silkscreen clipped by solder mask
    Local override; warning
    @(66.1900 mm, -81.5850 mm): Segment of JP10 on F.Silkscreen
    @(64.9200 mm, -80.9500 mm): PTH pad 1 [EN/DIS_RFPA_VDD] of JP10
[silk_over_copper]: Silkscreen clipped by solder mask
    Local override; warning
    @(62.7150 mm, -93.9350 mm): Reference field of C22
    @(61.3537 mm, -93.4941 mm): Pad 1 [+3V3] of C34 on F.Cu
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
