herasymyuks/PLFM_RADAR-aeris/beta/pcb/FREQUENCY_SYNTHESIZER/exports/3d/FREQUENCY_SYNTHESIZER_render_bottom.png

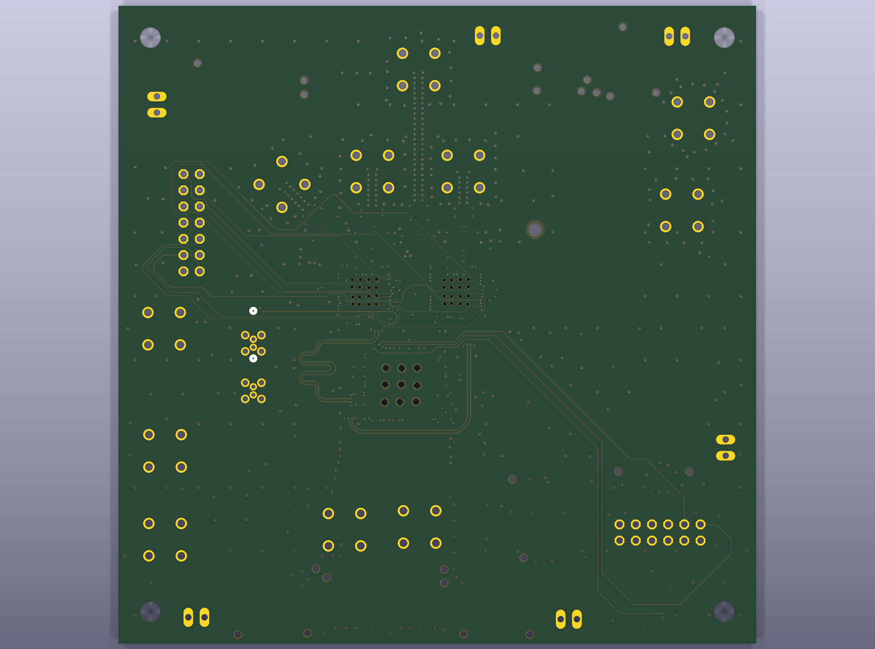
beta/pcb/FREQUENCY_SYNTHESIZER/exports/3d/FREQUENCY_SYNTHESIZER_render_bottom.png
