herasymyuks/PLFM_RADAR-aeris/beta/pcb/FREQUENCY_SYNTHESIZER/exports/3d/FREQUENCY_SYNTHESIZER_render_top.png

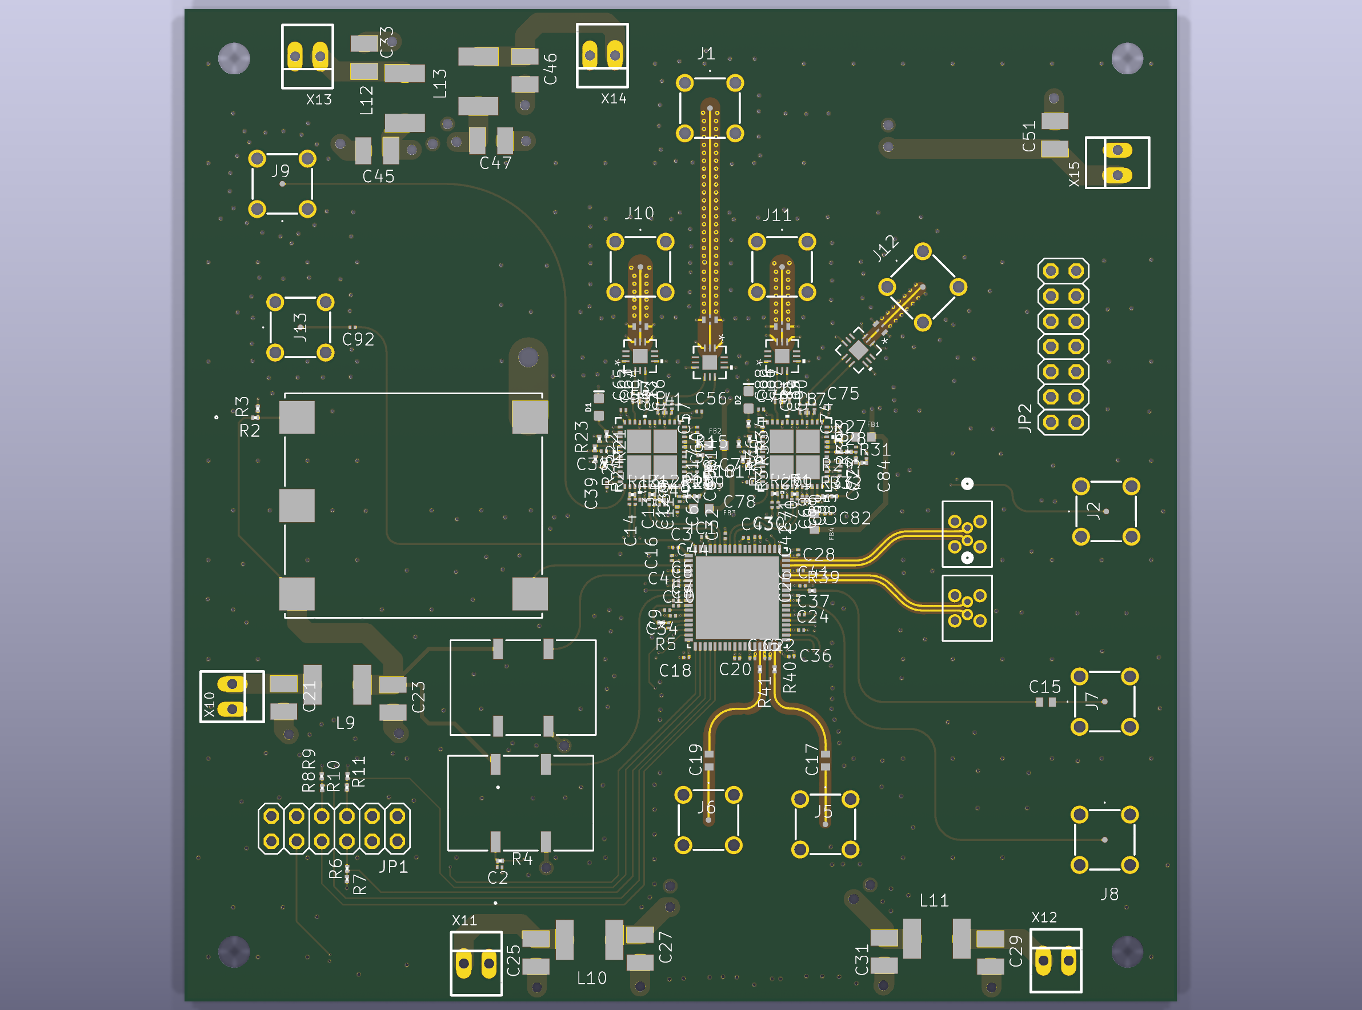
beta/pcb/FREQUENCY_SYNTHESIZER/exports/3d/FREQUENCY_SYNTHESIZER_render_top.png
