herasymyuks/PLFM_RADAR-aeris/beta/pcb/MAIN_BOARD_REVB/exports/3d/MAIN_BOARD_REVB_render_bottom.png

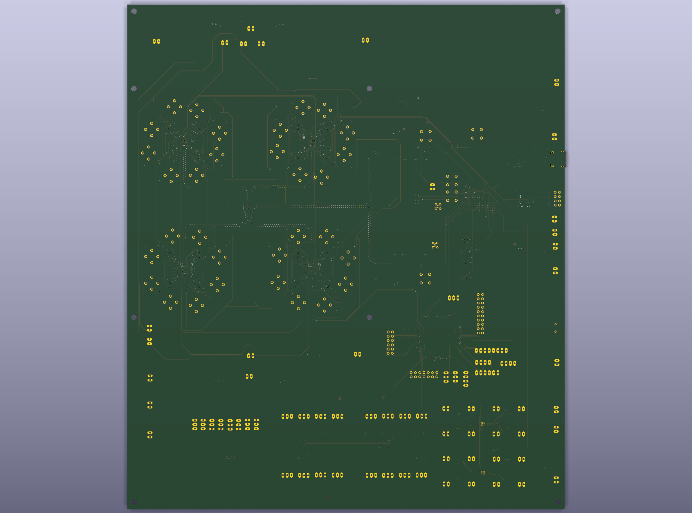
beta/pcb/MAIN_BOARD_REVB/exports/3d/MAIN_BOARD_REVB_render_bottom.png
