herasymyuks/PLFM_RADAR-aeris/beta/pcb/POWER_SUPPLY/exports/3d/POWER_SUPPLY_render_bottom.png

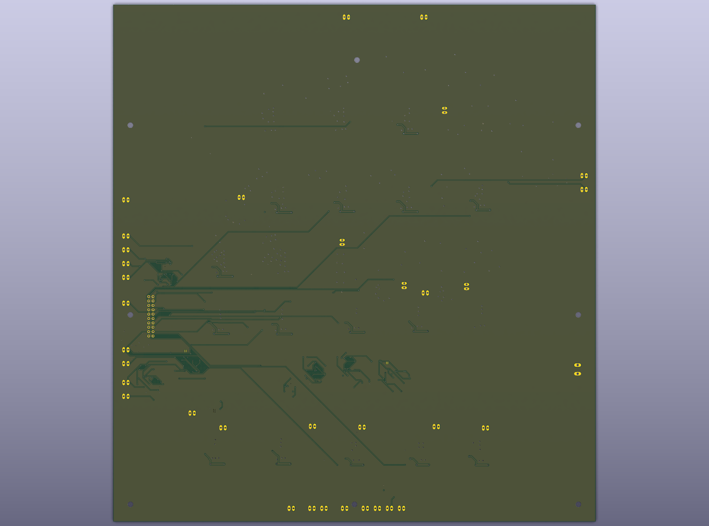
beta/pcb/POWER_SUPPLY/exports/3d/POWER_SUPPLY_render_bottom.png
