herasymyuks/PLFM_RADAR-aeris/beta/pcb/RF_PA/exports/3d/RF_PA_render_bottom.png

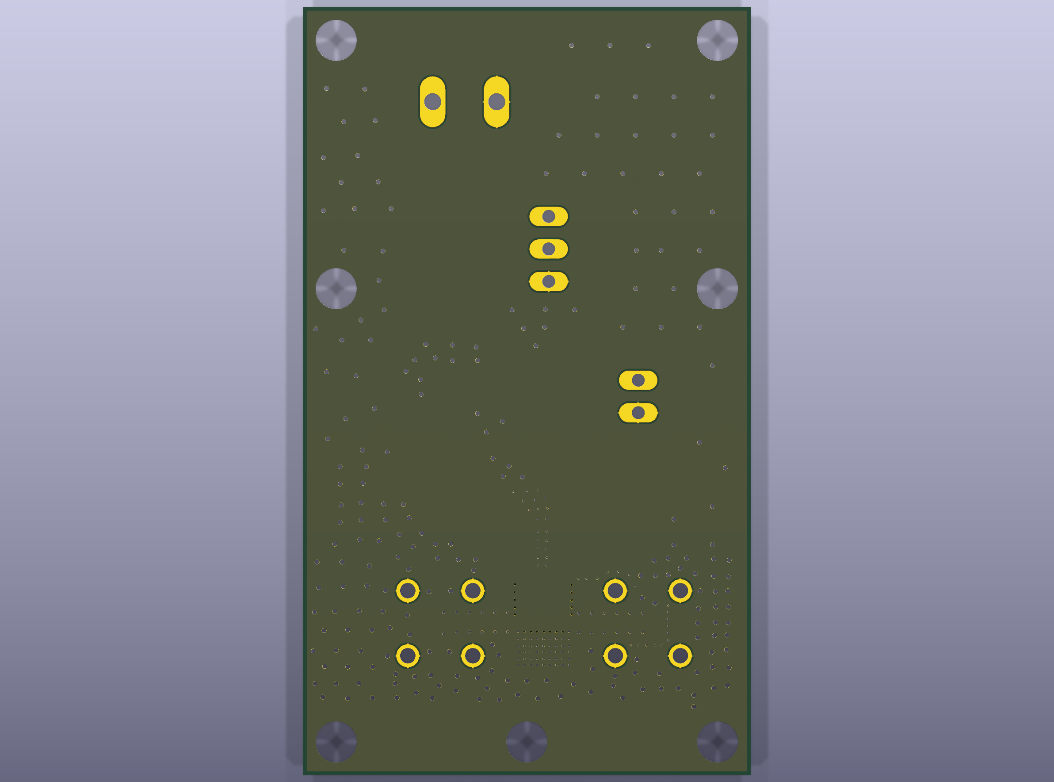
beta/pcb/RF_PA/exports/3d/RF_PA_render_bottom.png
