herasymyuks/PLFM_RADAR-aeris/engineering/ASSEMBLY/EXPLODED_VIEWS/aeris10_exploded_conceptual.png

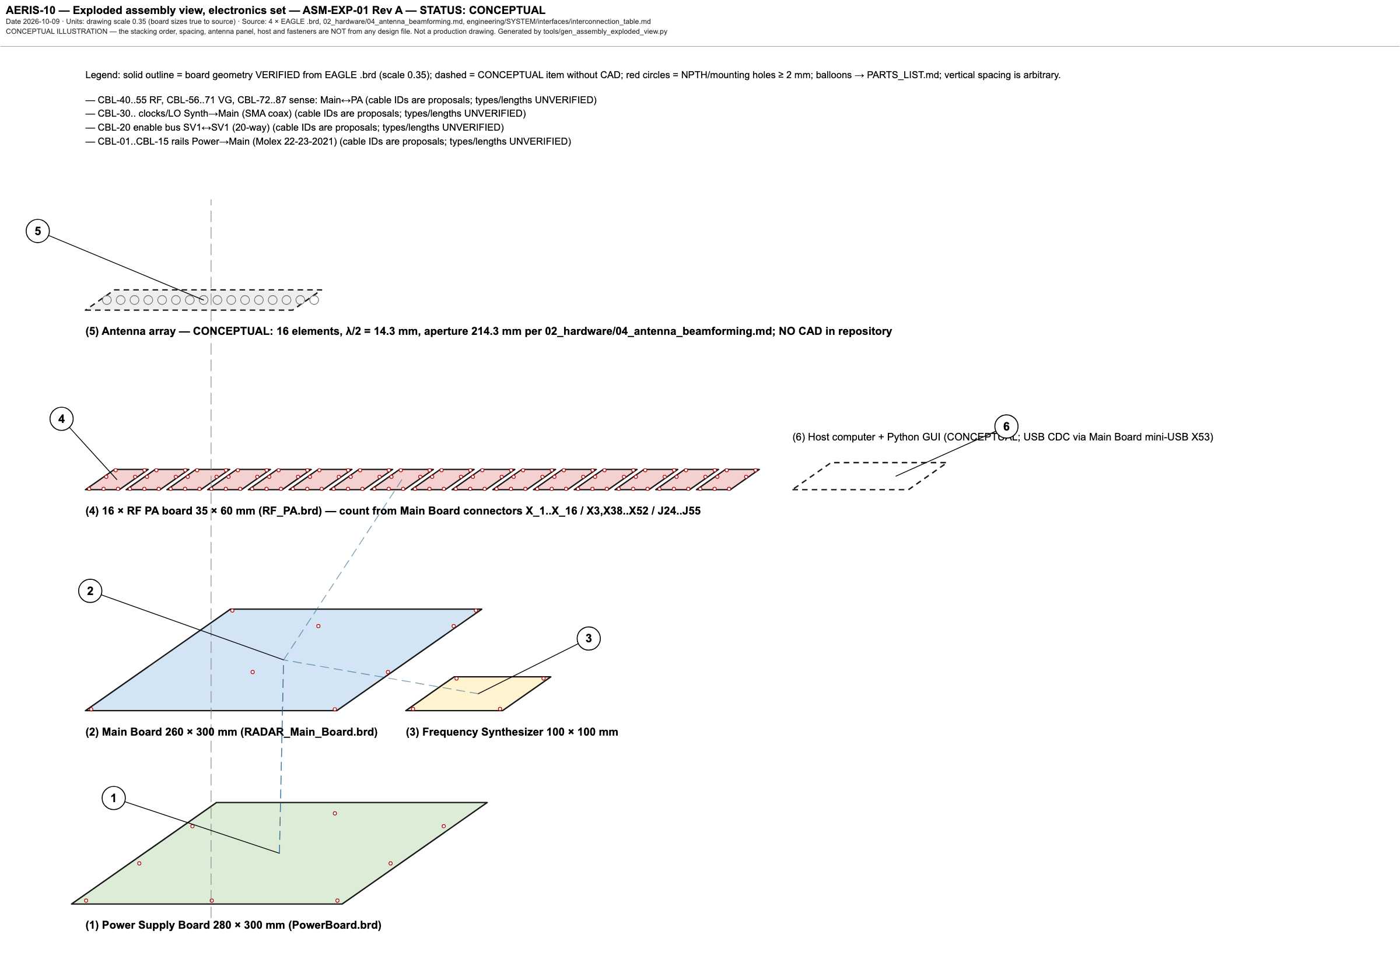
engineering/ASSEMBLY/EXPLODED_VIEWS/aeris10_exploded_conceptual.png
