herasymyuks/PLFM_RADAR-aeris/engineering/DESIGN/ANTENNA/aeris10_patch_array_layout.png

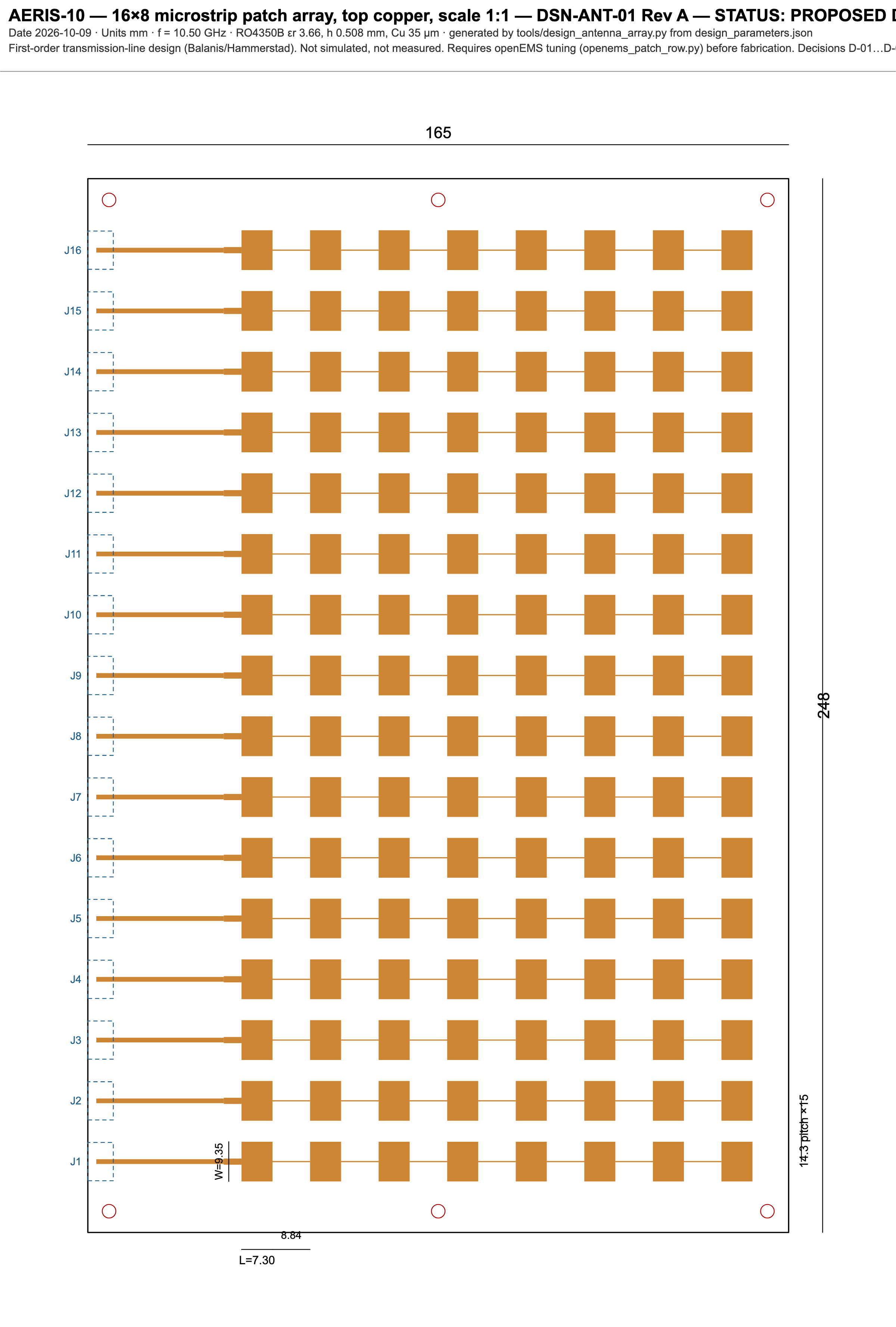
engineering/DESIGN/ANTENNA/aeris10_patch_array_layout.png
