herasymyuks/PLFM_RADAR-aeris/engineering/DESIGN/ANTENNA/kicad_exports/aeris10_patch_array_render_top.png

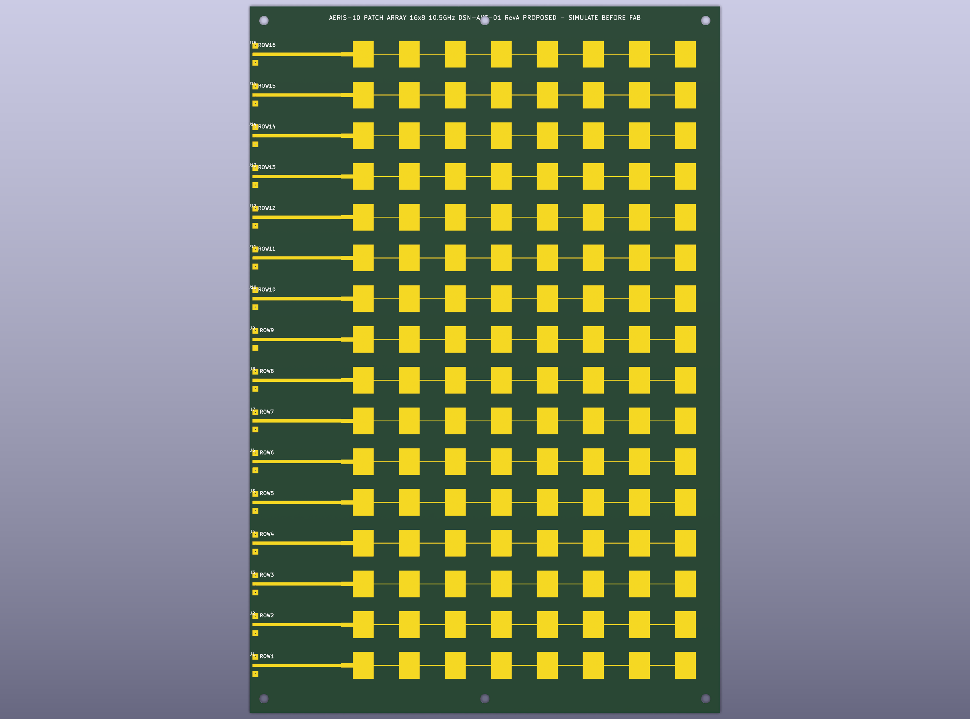
engineering/DESIGN/ANTENNA/kicad_exports/aeris10_patch_array_render_top.png
