herasymyuks/PLFM_RADAR-aeris/engineering/DESIGN/ANTENNA/simulation/s11_row.png

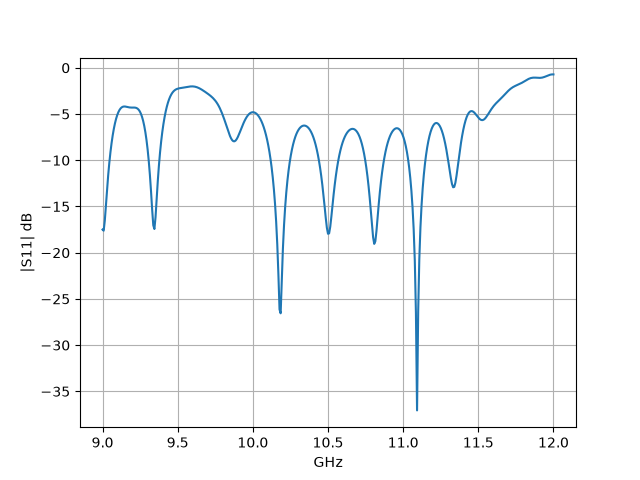
engineering/DESIGN/ANTENNA/simulation/s11_row.png
