herasymyuks/PLFM_RADAR-aeris/engineering/DESIGN/ELECTRICAL/PA_SUPPLY_22V/DSN-PSU-01_block_schematic.png

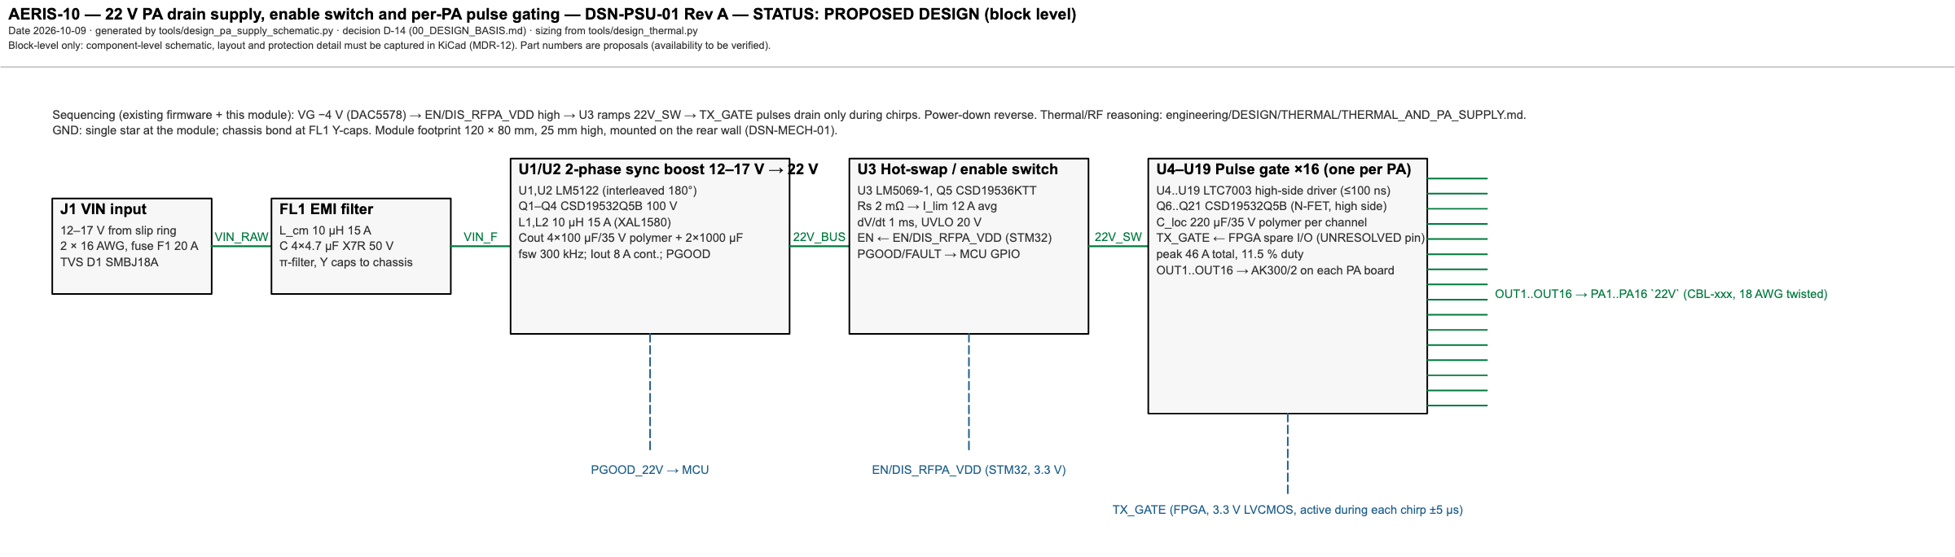
engineering/DESIGN/ELECTRICAL/PA_SUPPLY_22V/DSN-PSU-01_block_schematic.png
