herasymyuks/PLFM_RADAR-aeris/engineering/DESIGN/MECHANICAL/CAD/aeris10_head_xray_iso.png

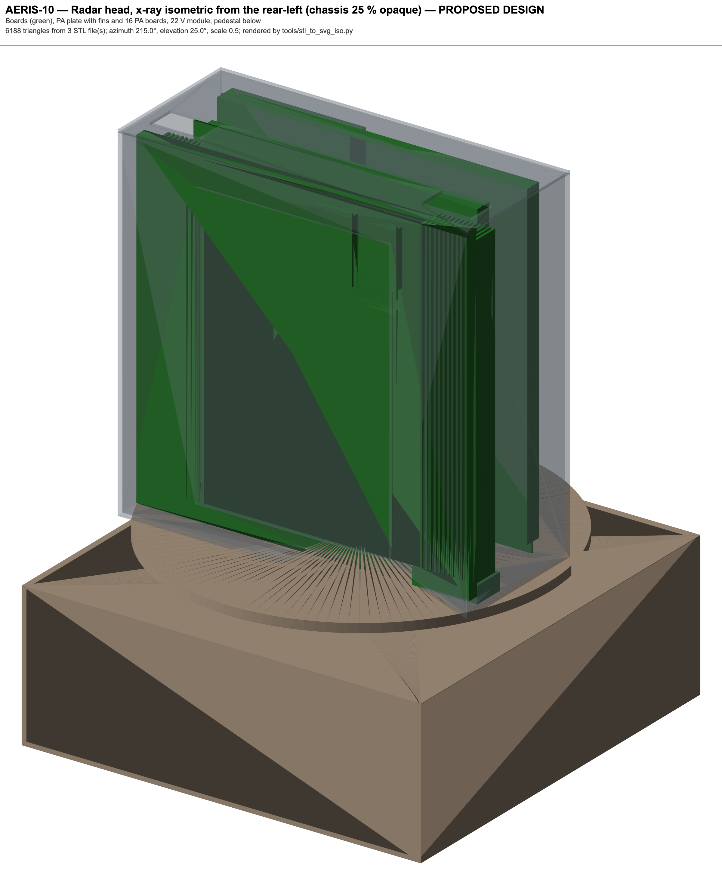
engineering/DESIGN/MECHANICAL/CAD/aeris10_head_xray_iso.png
