herasymyuks/PLFM_RADAR-aeris/engineering/DESIGN/MECHANICAL/CAD/detail/aeris10_detail_iso_rear.png

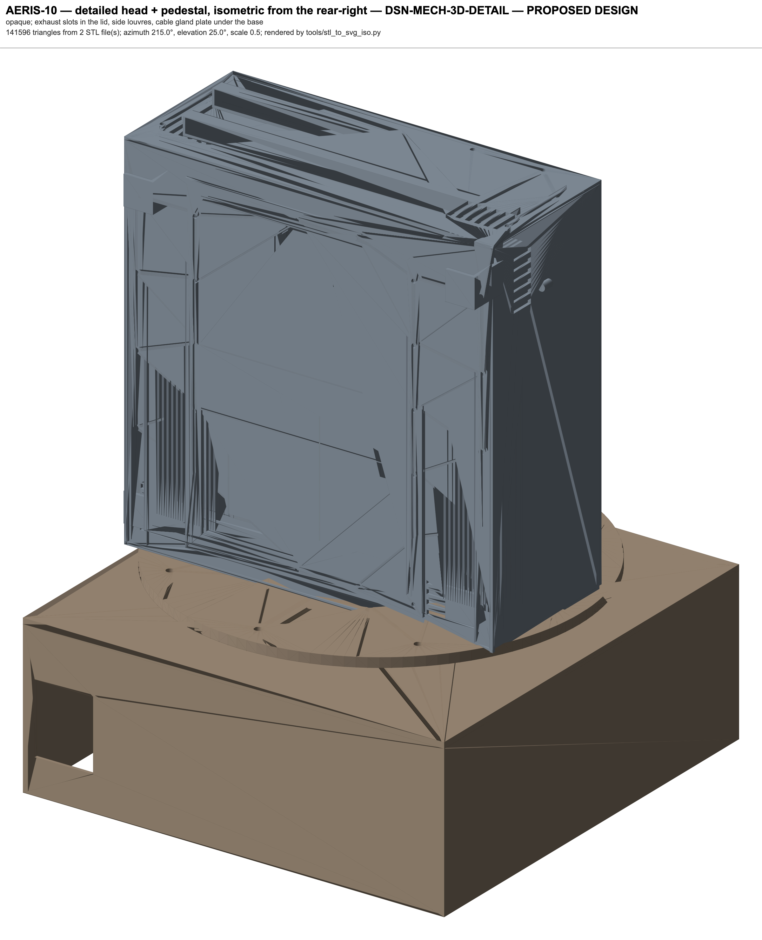
engineering/DESIGN/MECHANICAL/CAD/detail/aeris10_detail_iso_rear.png
