herasymyuks/PLFM_RADAR-aeris/engineering/DESIGN/MECHANICAL/CAD/detail/aeris10_detail_xray_front_iso.png

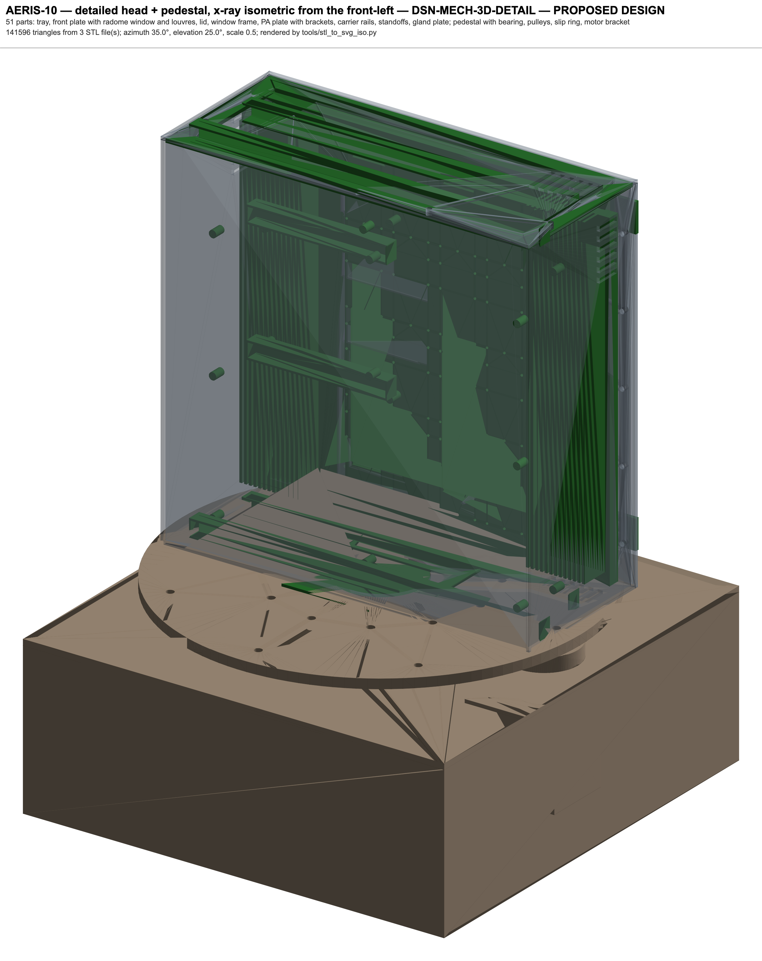
engineering/DESIGN/MECHANICAL/CAD/detail/aeris10_detail_xray_front_iso.png
