herasymyuks/PLFM_RADAR-aeris/engineering/DESIGN/MECHANICAL/drawings/png/DSN-MECH-01_head_plan_section.png

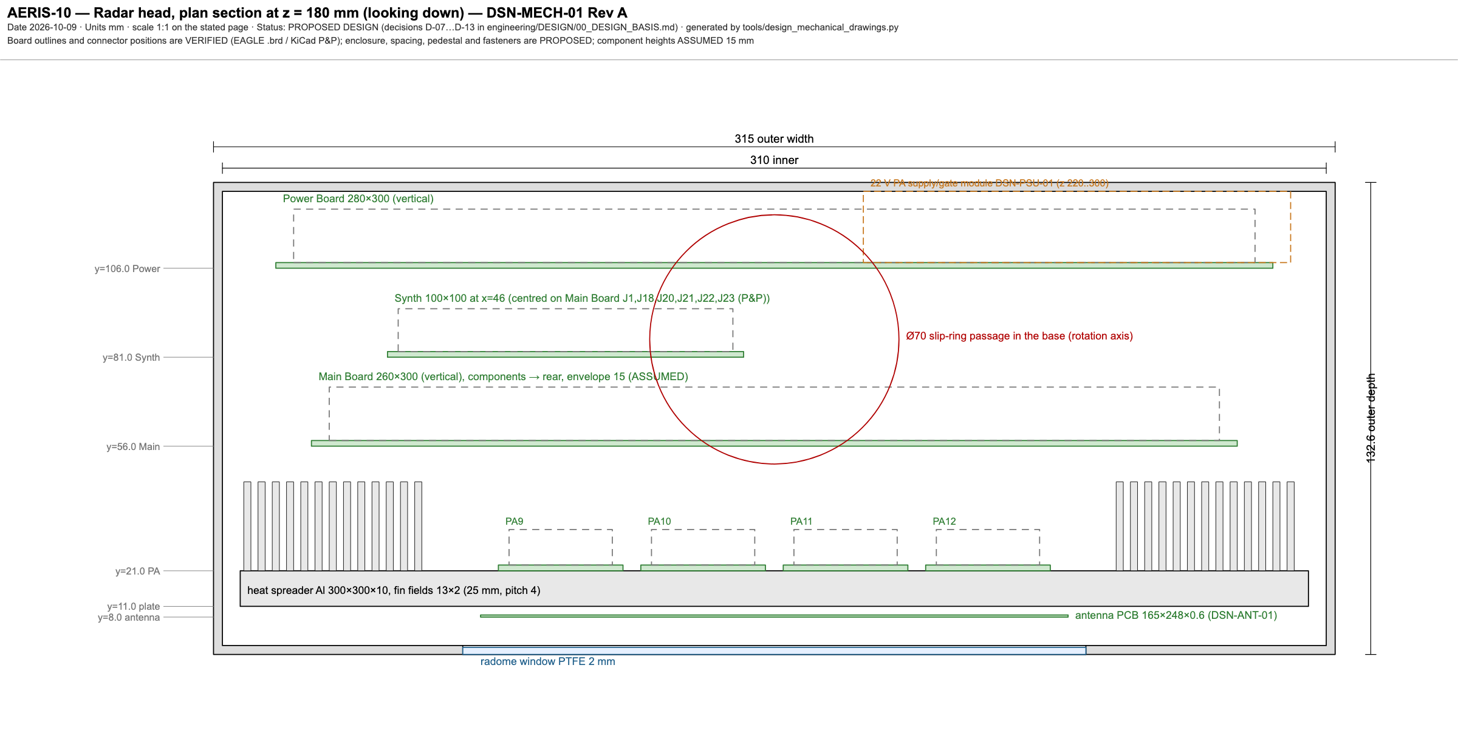
engineering/DESIGN/MECHANICAL/drawings/png/DSN-MECH-01_head_plan_section.png
