herasymyuks/PLFM_RADAR-aeris/engineering/DESIGN/MECHANICAL/drawings/png/DSN-MECH-02_head_front_elevation.png

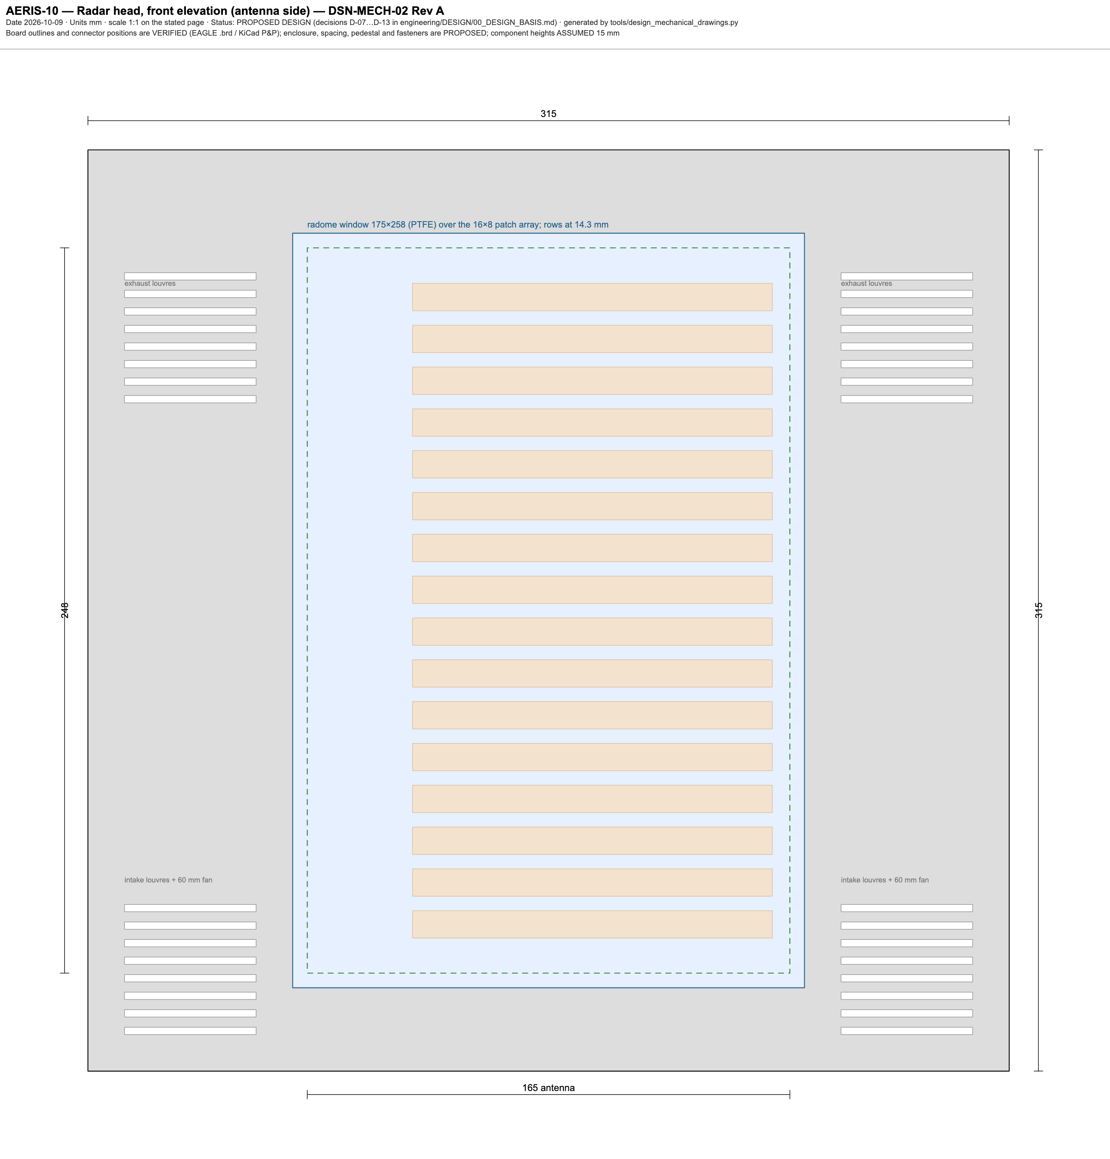
engineering/DESIGN/MECHANICAL/drawings/png/DSN-MECH-02_head_front_elevation.png
