herasymyuks/PLFM_RADAR-aeris/engineering/DESIGN/MECHANICAL/drawings/png/DSN-MECH-03_head_side_section.png

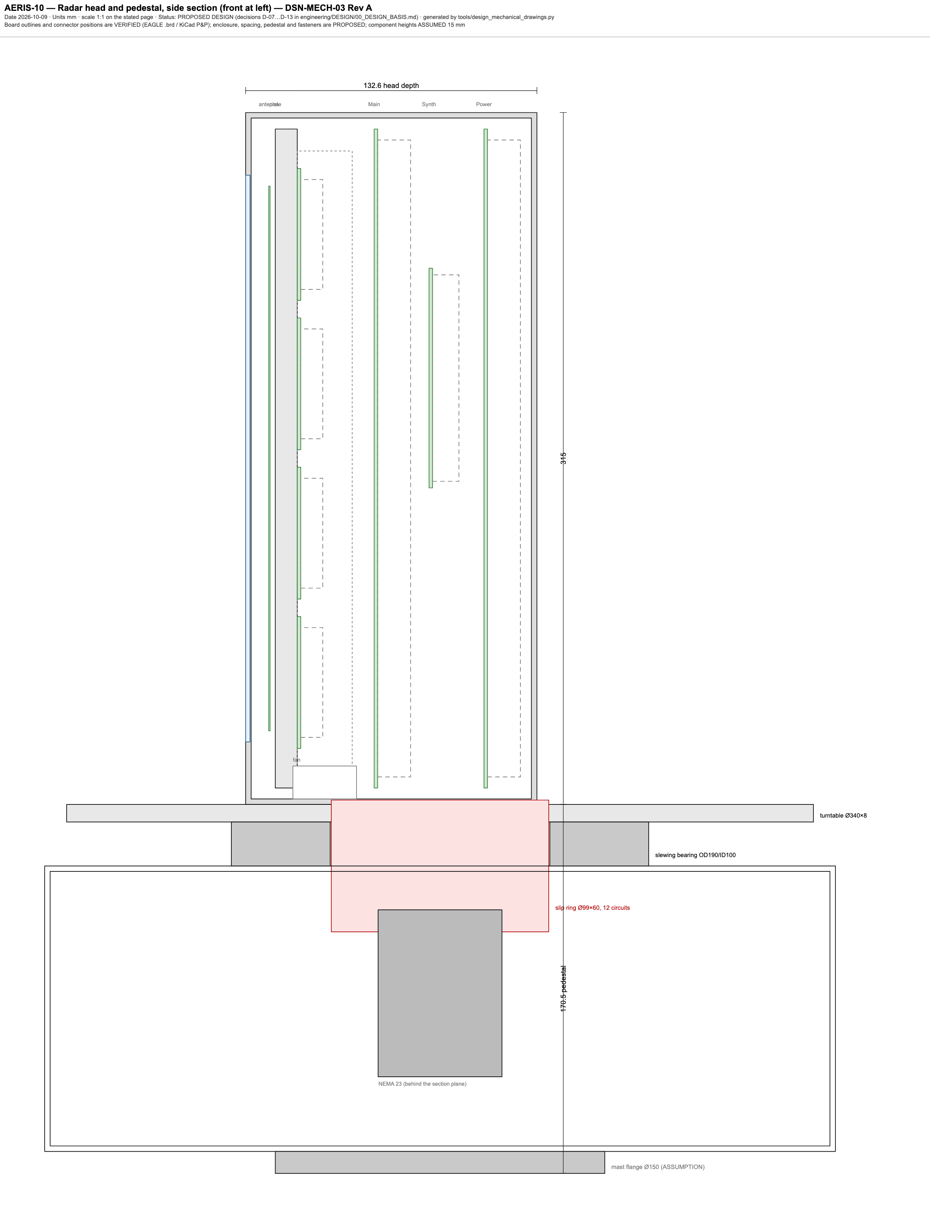
engineering/DESIGN/MECHANICAL/drawings/png/DSN-MECH-03_head_side_section.png
