herasymyuks/PLFM_RADAR-aeris/engineering/DESIGN/MECHANICAL/drawings/png/DSN-MECH-04_internal_layout_rear.png

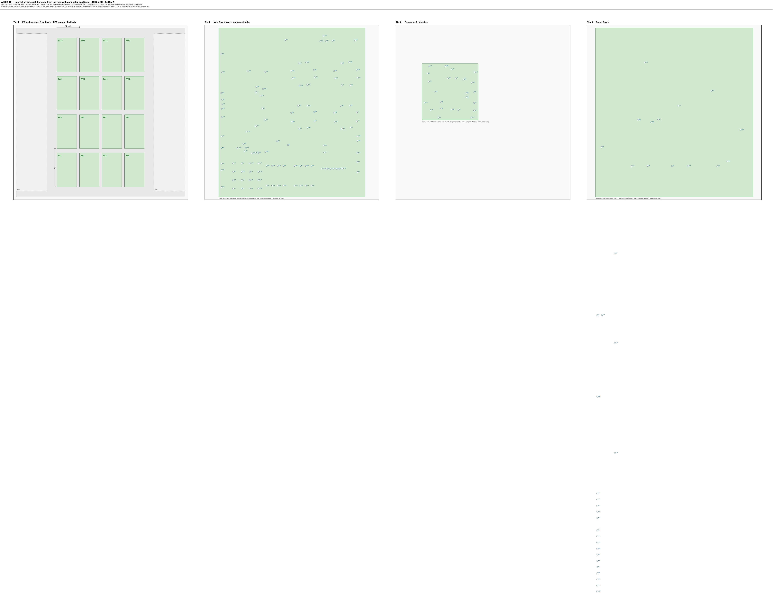
engineering/DESIGN/MECHANICAL/drawings/png/DSN-MECH-04_internal_layout_rear.png
