herasymyuks/PLFM_RADAR-aeris/engineering/DESIGN/MECHANICAL/drawings/png/DSN-MECH-05_pedestal_plan.png

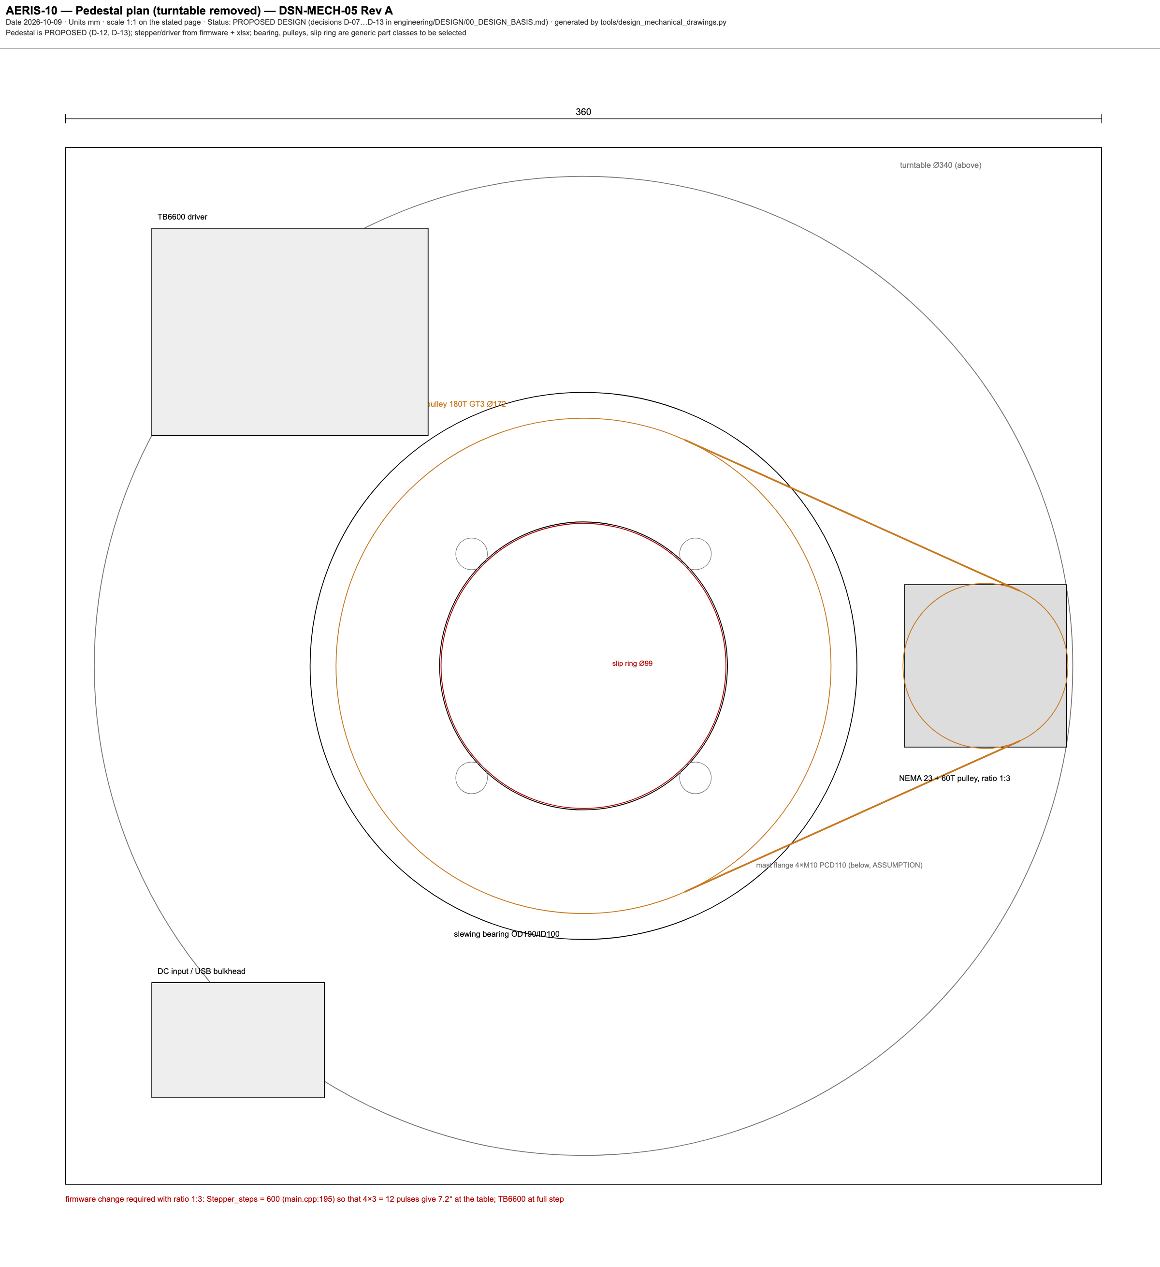
engineering/DESIGN/MECHANICAL/drawings/png/DSN-MECH-05_pedestal_plan.png
