herasymyuks/PLFM_RADAR-aeris/engineering/DESIGN/MECHANICAL/drawings/png/DSN-MECH-06_sheet_metal_flat_patterns.png

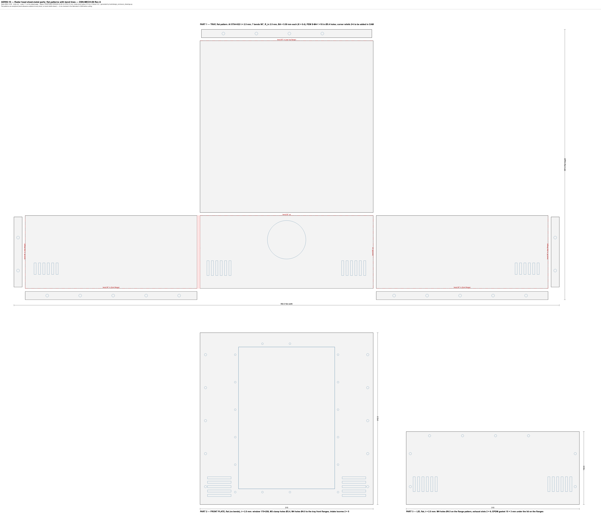
engineering/DESIGN/MECHANICAL/drawings/png/DSN-MECH-06_sheet_metal_flat_patterns.png
