herasymyuks/PLFM_RADAR-aeris/engineering/ELECTRICAL/power_distribution/power_distribution.png

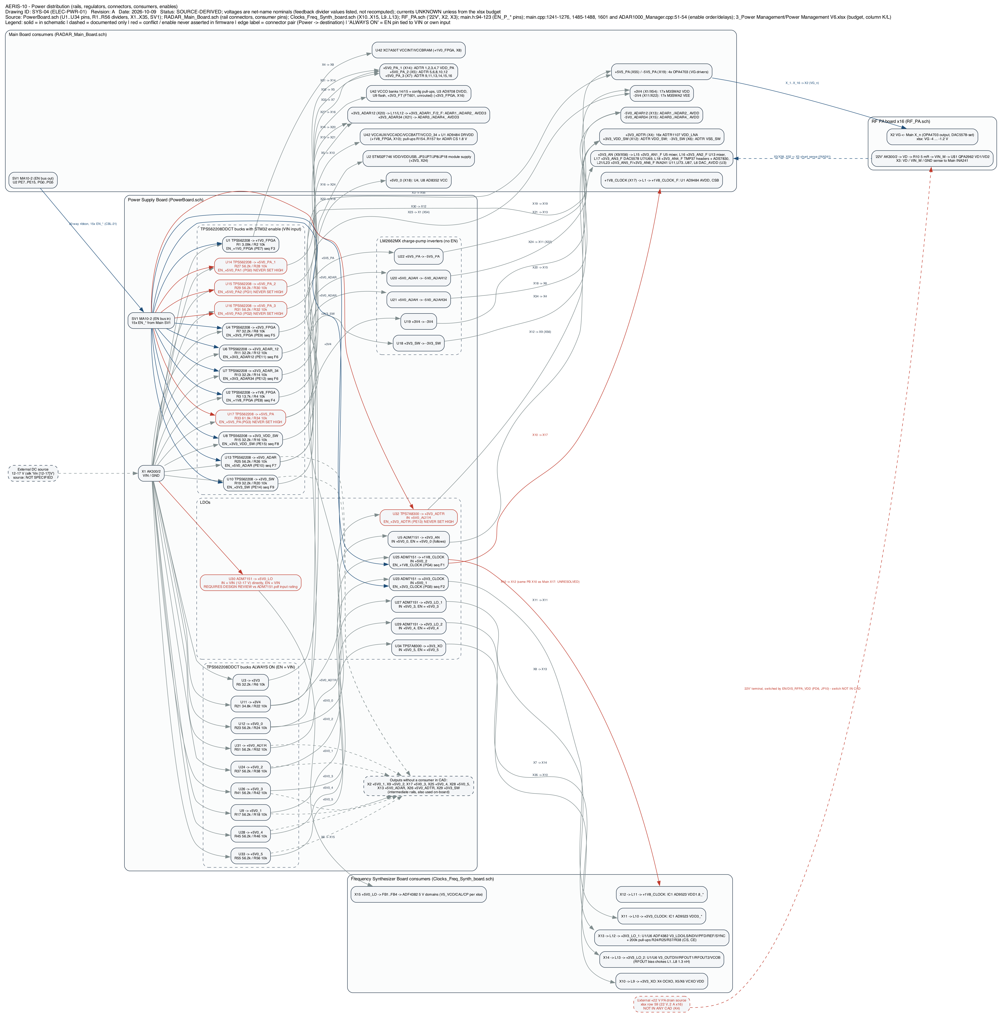
engineering/ELECTRICAL/power_distribution/power_distribution.png
