herasymyuks/PLFM_RADAR-aeris/engineering/ELECTRICAL/schematics/FREQUENCY_SYNTHESIZER/png/FREQUENCY_SYNTHESIZER_schematic_sheet1.png

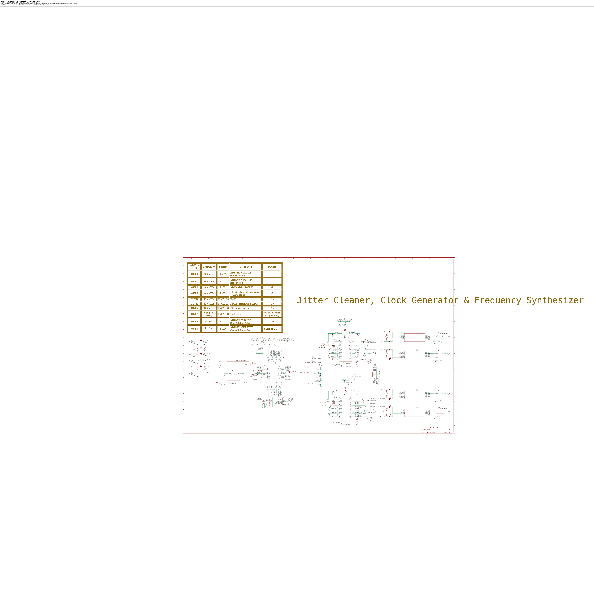
engineering/ELECTRICAL/schematics/FREQUENCY_SYNTHESIZER/png/FREQUENCY_SYNTHESIZER_schematic_sheet1.png
