herasymyuks/PLFM_RADAR-aeris/engineering/ELECTRICAL/schematics/MAIN_BOARD/png/MAIN_BOARD_schematic_sheet3.png

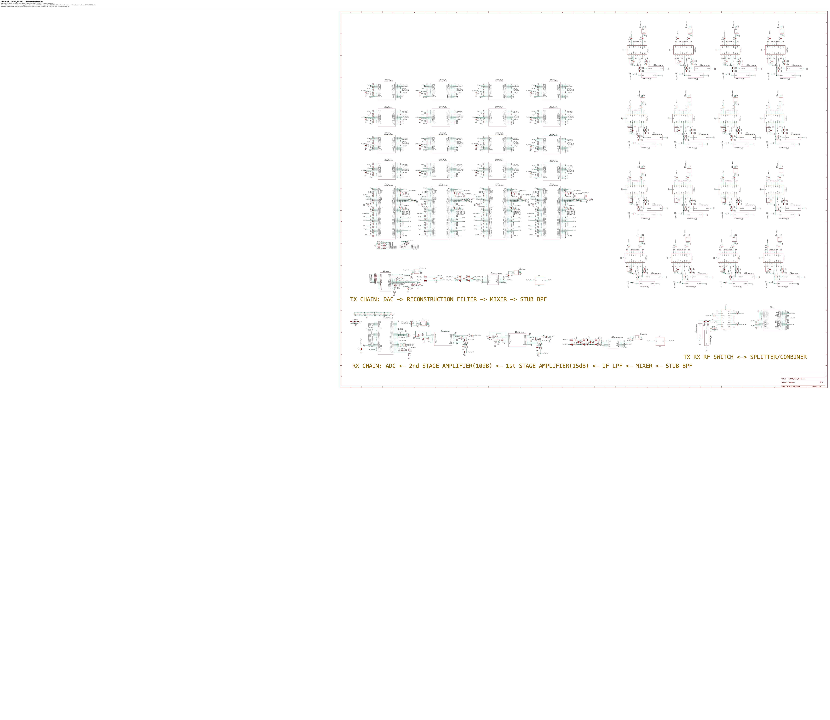
engineering/ELECTRICAL/schematics/MAIN_BOARD/png/MAIN_BOARD_schematic_sheet3.png
