herasymyuks/PLFM_RADAR-aeris/engineering/ELECTRICAL/schematics/POWER_SUPPLY/png/POWER_SUPPLY_schematic_sheet1.png

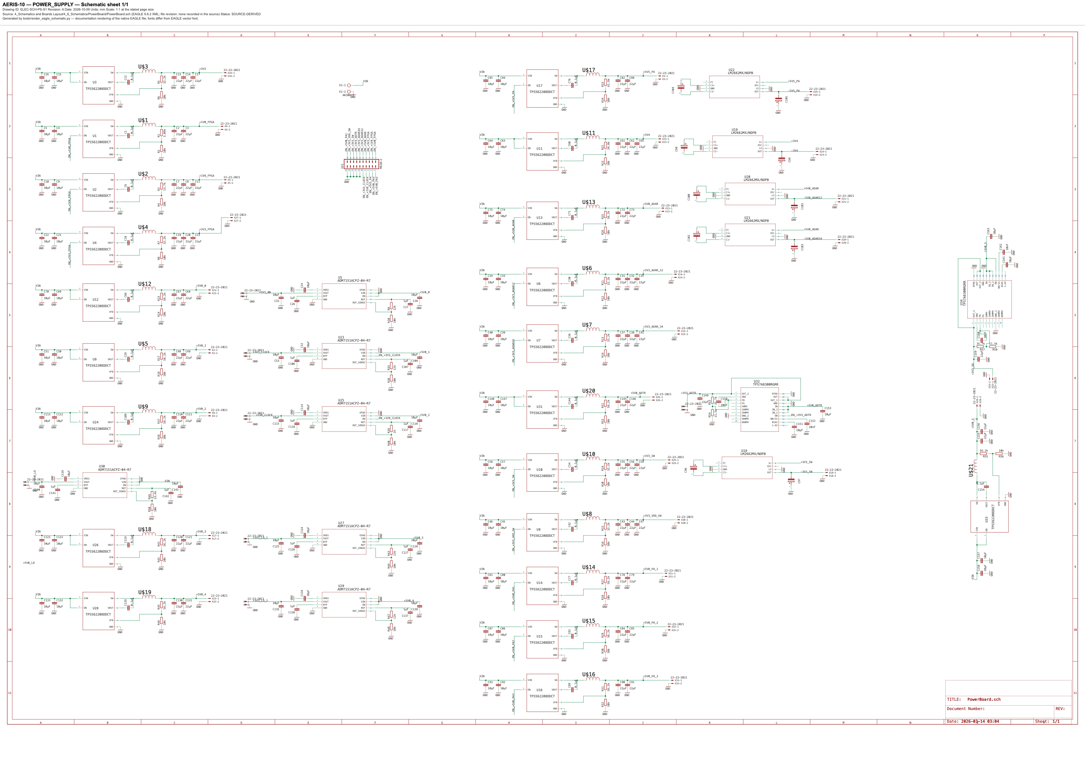
engineering/ELECTRICAL/schematics/POWER_SUPPLY/png/POWER_SUPPLY_schematic_sheet1.png
