herasymyuks/PLFM_RADAR-aeris/engineering/ELECTRICAL/schematics/RF_PA/png/RF_PA_schematic_sheet1.png

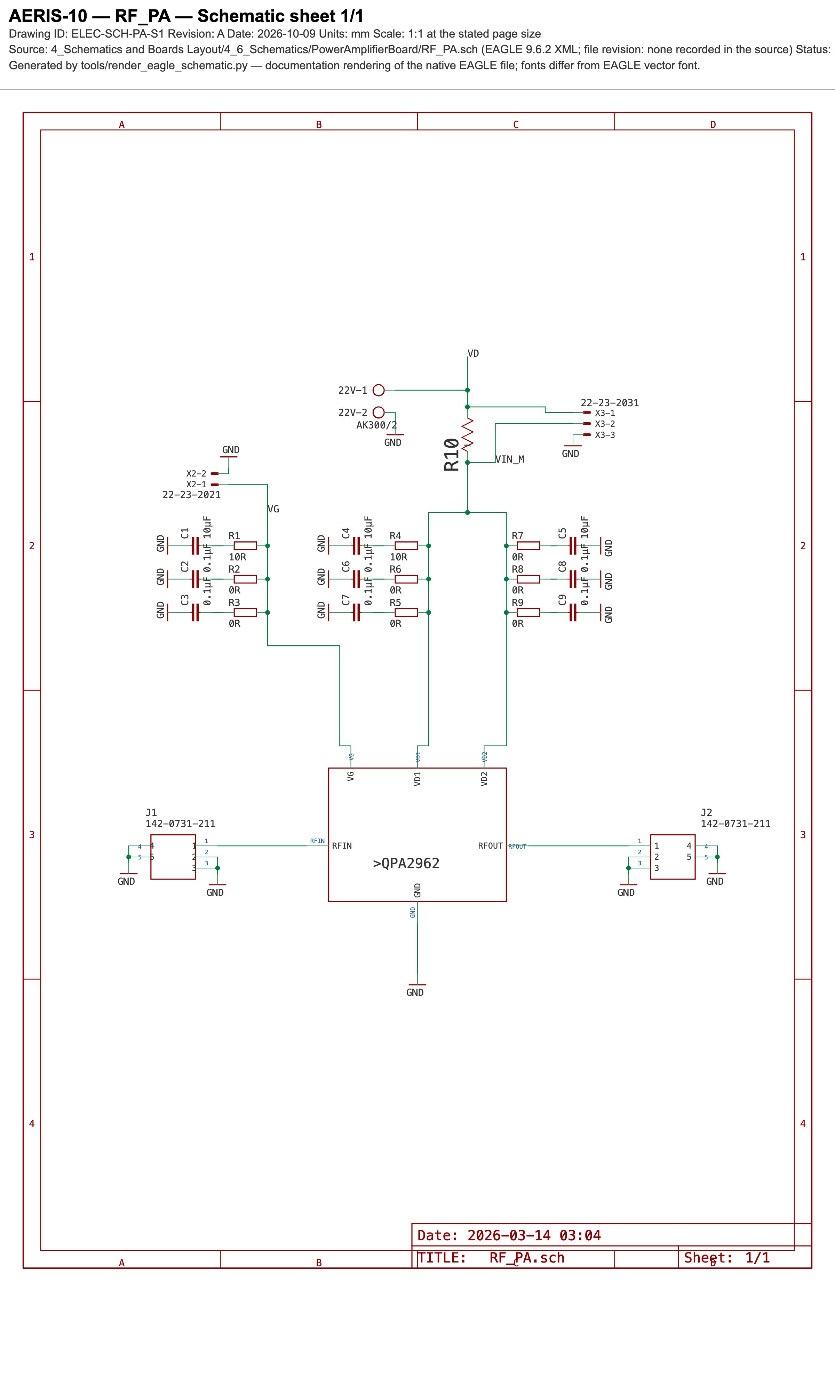
engineering/ELECTRICAL/schematics/RF_PA/png/RF_PA_schematic_sheet1.png
