herasymyuks/PLFM_RADAR-aeris/engineering/MECHANICAL/CAD/pcb_set_plan_view.png

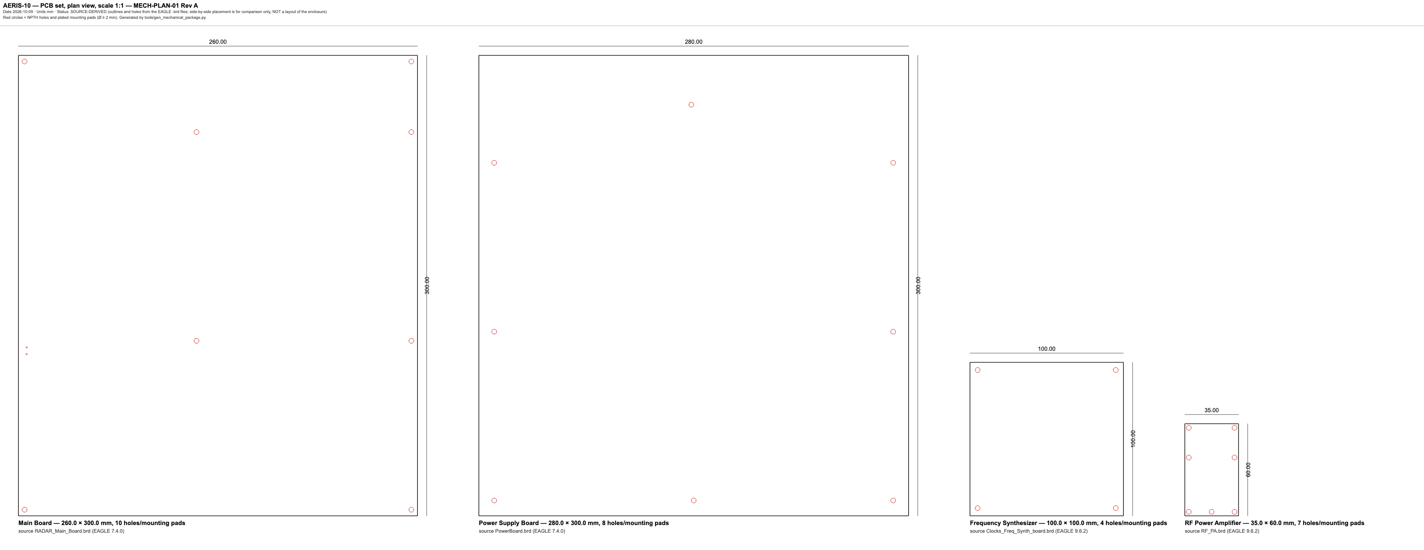
engineering/MECHANICAL/CAD/pcb_set_plan_view.png
