herasymyuks/PLFM_RADAR-aeris/engineering/SOFTWARE_DIAGRAMS/DATA_FLOW/end_to_end_data_flow.png

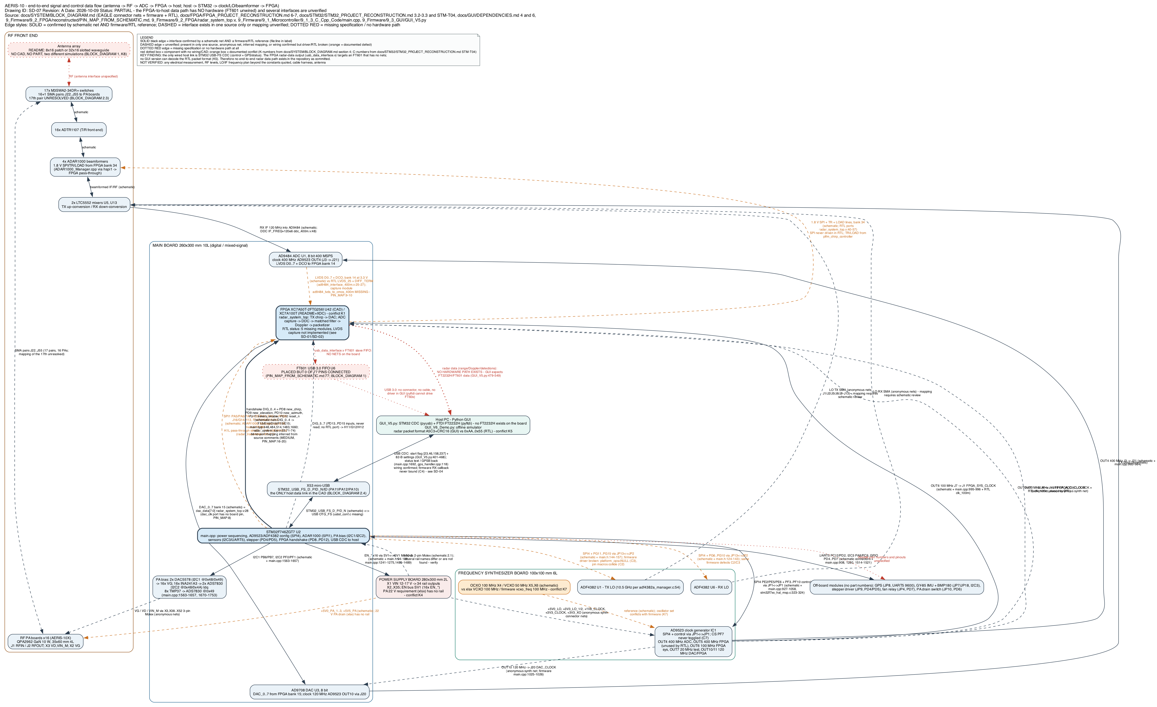
engineering/SOFTWARE_DIAGRAMS/DATA_FLOW/end_to_end_data_flow.png
