herasymyuks/PLFM_RADAR-aeris/engineering/SOFTWARE_DIAGRAMS/FPGA/fpga_data_pipeline.png

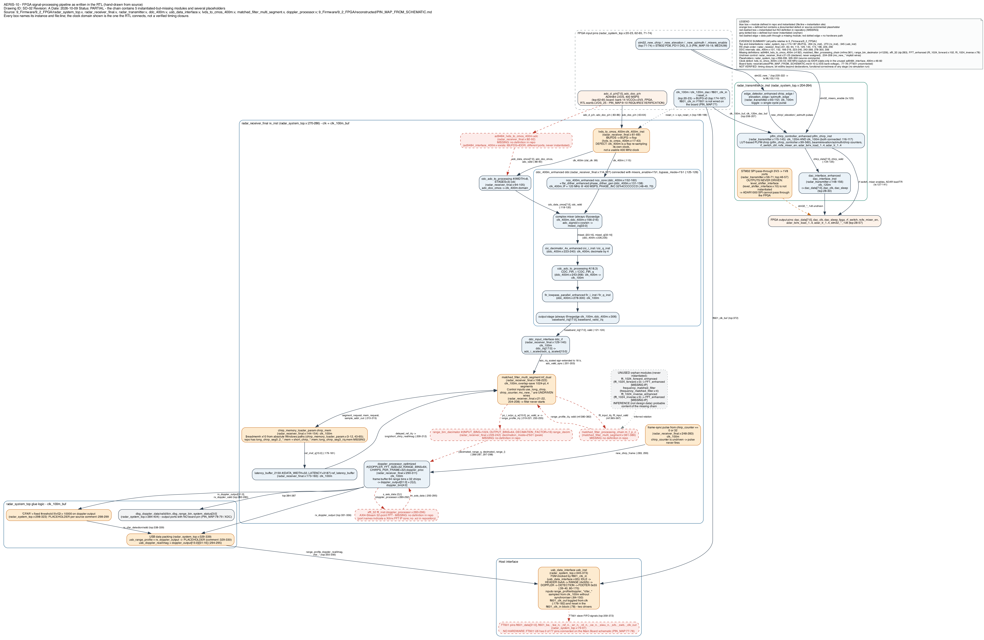
engineering/SOFTWARE_DIAGRAMS/FPGA/fpga_data_pipeline.png
