herasymyuks/PLFM_RADAR-aeris/engineering/SOFTWARE_DIAGRAMS/FPGA/fpga_module_hierarchy.png

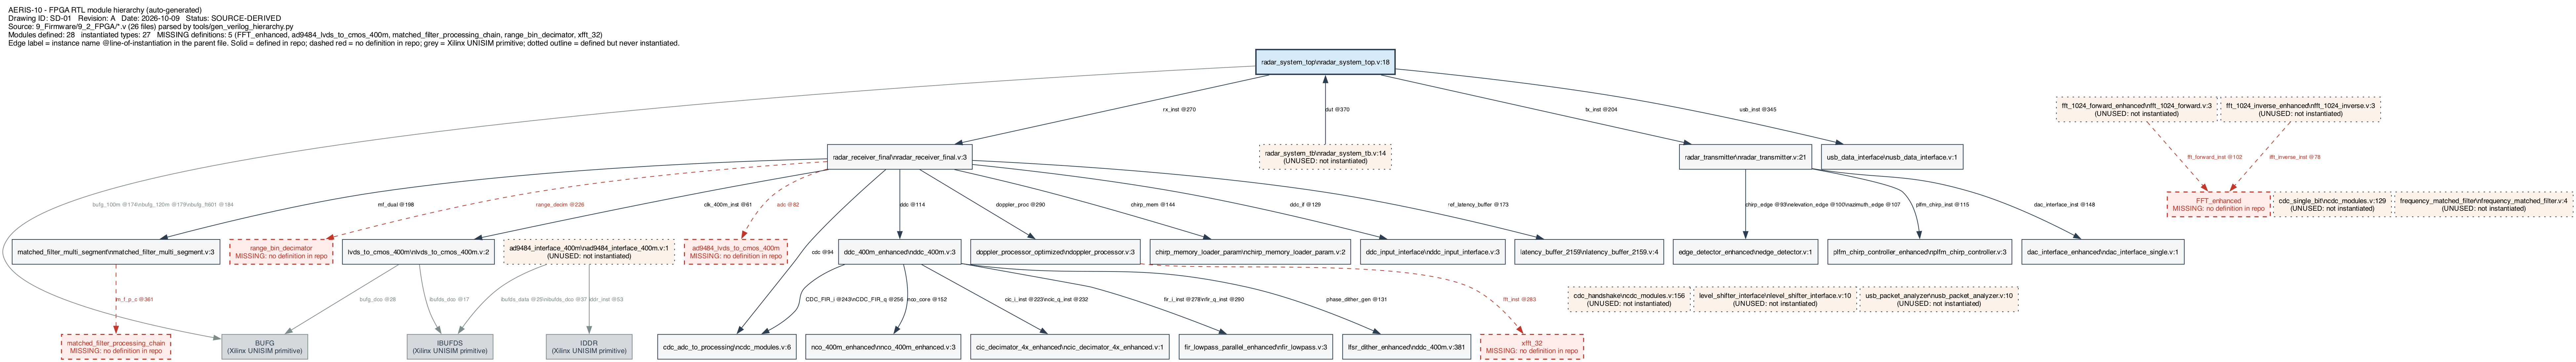
engineering/SOFTWARE_DIAGRAMS/FPGA/fpga_module_hierarchy.png
