herasymyuks/PLFM_RADAR-aeris/engineering/SOFTWARE_DIAGRAMS/PYTHON/python_gui_architecture.png

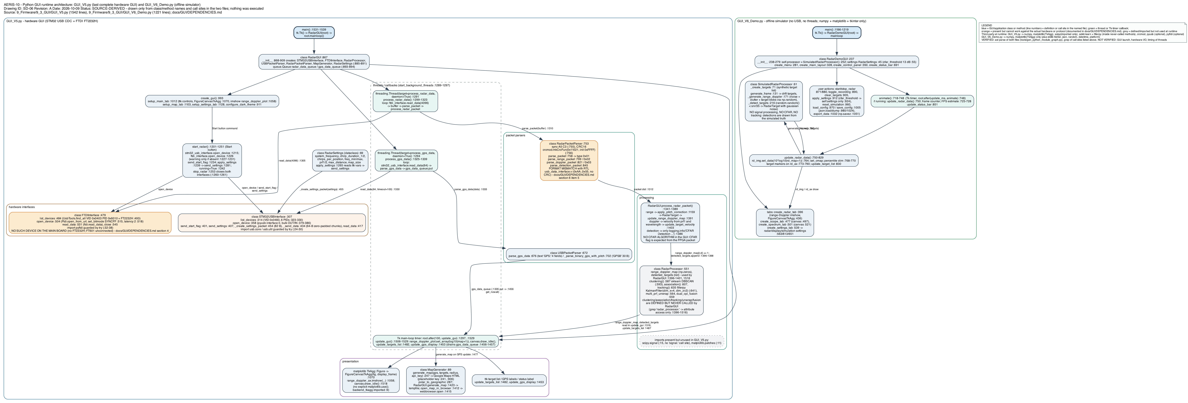
engineering/SOFTWARE_DIAGRAMS/PYTHON/python_gui_architecture.png
