herasymyuks/PLFM_RADAR-aeris/engineering/SOFTWARE_DIAGRAMS/STM32/stm32_firmware_architecture.png

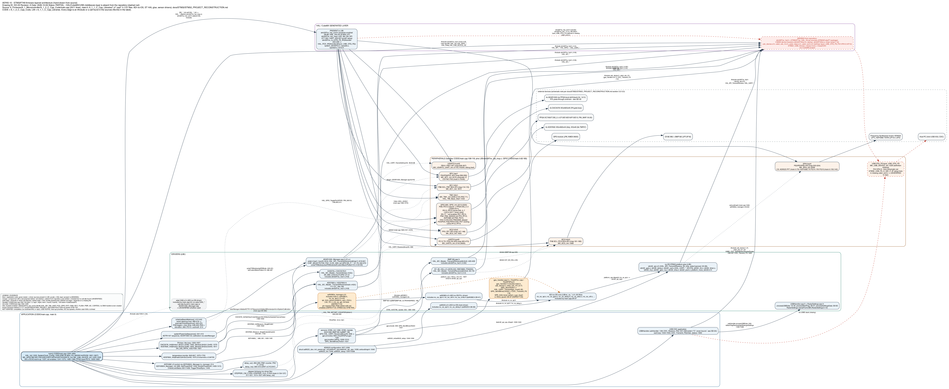
engineering/SOFTWARE_DIAGRAMS/STM32/stm32_firmware_architecture.png
