herasymyuks/PLFM_RADAR-aeris/engineering/SOFTWARE_DIAGRAMS/STM32/stm32_usb_cdc_flow.png

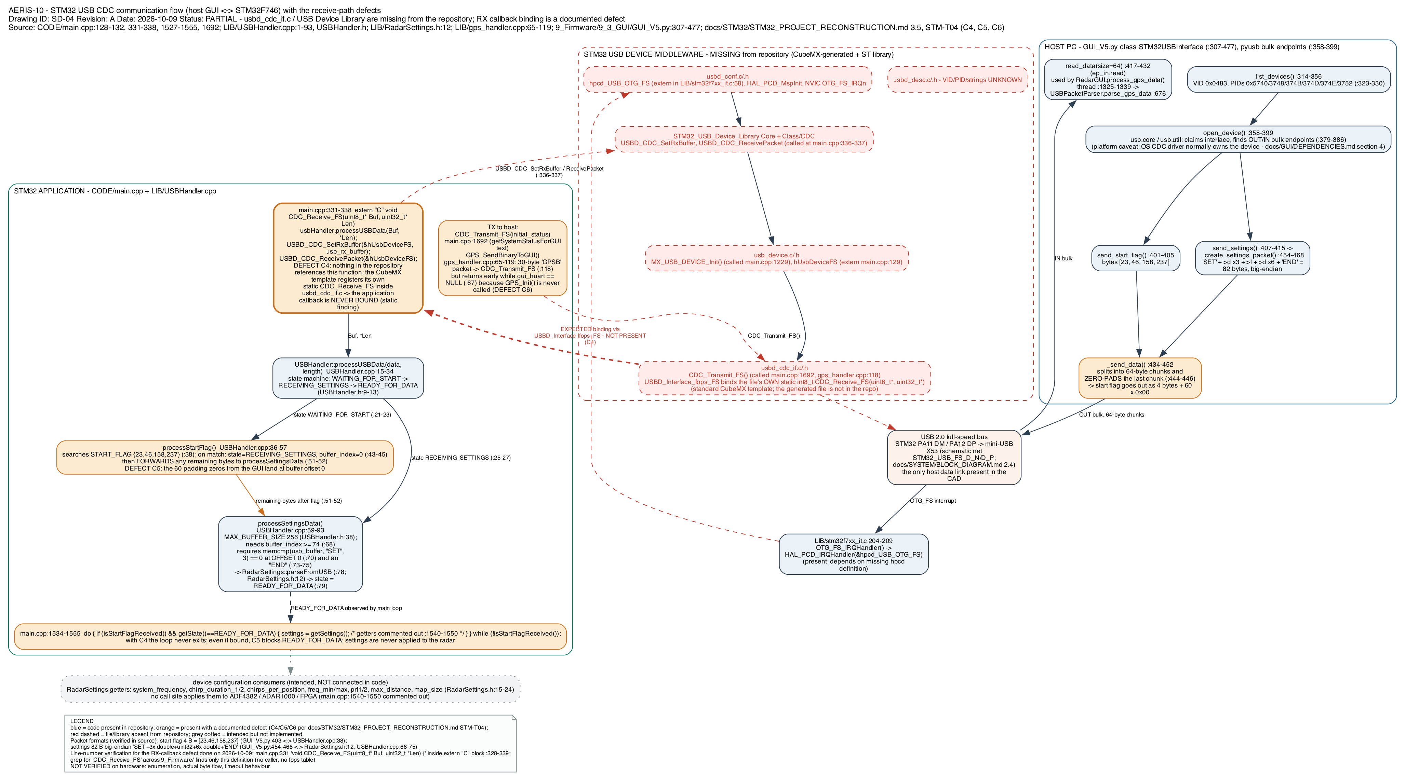
engineering/SOFTWARE_DIAGRAMS/STM32/stm32_usb_cdc_flow.png
