herasymyuks/PLFM_RADAR-aeris/engineering/SYSTEM/block_diagrams/system_block_diagram.png

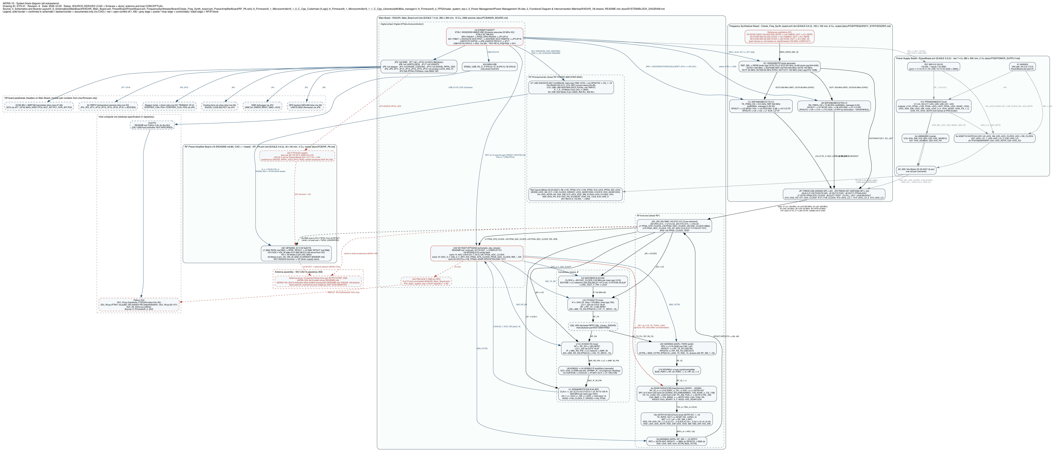
engineering/SYSTEM/block_diagrams/system_block_diagram.png
