herasymyuks/PLFM_RADAR-aeris/engineering/SYSTEM/data_flow/signal_and_data_flow.png

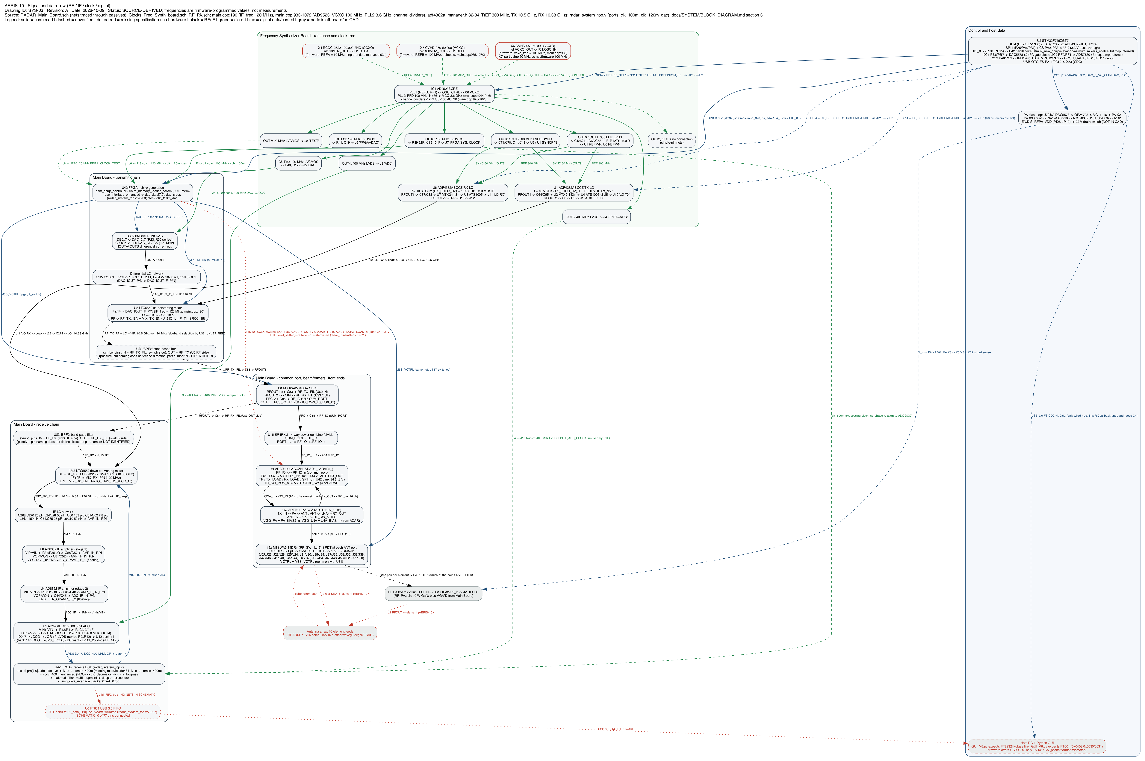
engineering/SYSTEM/data_flow/signal_and_data_flow.png
