herasymyuks/PLFM_RADAR-aeris/engineering/SYSTEM/interfaces/hardware_interconnection.png

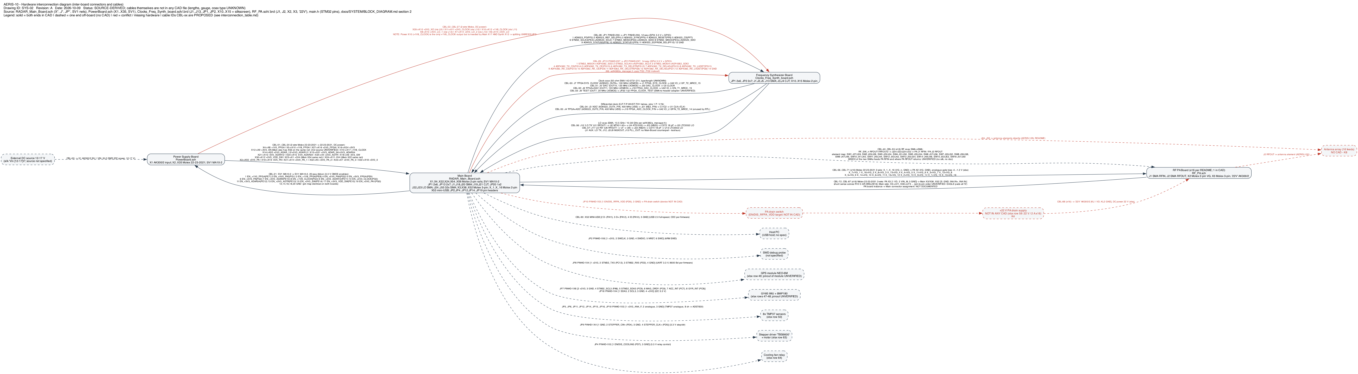
engineering/SYSTEM/interfaces/hardware_interconnection.png
