herasymyuks/PLFM_RADAR-aeris/docs/BOM/BOM_POWER_SUPPLY.md

# BOM extracted from `PowerBoard.sch`

Physical parts: **312** references in **28** line items. Lines with an explicit MPN attribute: **0**. Every other `mpn_candidate` is the EAGLE deviceset name and is **UNVERIFIED**. Values missing in the schematic appear empty.

| # | Qty | Value | Deviceset | Package | MPN candidate | Status | References |
|---|---:|---|---|---|---|---|---|
| 1 | 34 |  | 22-23-2021 | 22-23-2021 | 22-23-2021 | UNVERIFIED | X10 X11 X12 X13 X14 X15 X16 X17 X18 X19 X2 X20 X21 X22 X23 X24 X25 X26 X27 X28 X29 X3 X... |
| 2 | 6 |  | ADM7151ACPZ-04-R7 | CP_8_11_ADI | ADM7151ACPZ-04-R7 | UNVERIFIED | U23 U25 U27 U29 U30 U5 |
| 3 | 1 |  | AK300/2 | AK300/2 | AK300/2 | UNVERIFIED | X1 |
| 4 | 21 | 0.1µF | C-EU | C0805 | C-EU | generic | C1 C109 C119 C12 C129 C144 C154 C18 C29 C30 C36 C42 C54 C6 C60 C66 C71 C76 C77 C83 C89 |
| 5 | 4 | 10nF | C-EU | C0603 | C-EU | generic | C150 C152 C160 C162 |
| 6 | 60 | 10µF | C-EU | C0805 | C-EU | generic | C10 C108 C112 C113 C114 C115 C118 C122 C123 C124 C125 C128 C132 C133 C134 C135 C138 C13... |
| 7 | 4 | 10µF | C-EU | C0603 | C-EU | generic | C151 C153 C161 C163 |
| 8 | 12 | 1µF | C-EU | C0805 | C-EU | generic | C106 C107 C116 C117 C126 C127 C136 C137 C141 C142 C26 C27 |
| 9 | 52 | 22µF | C-EU | C0603 | C-EU | generic | C11 C110 C111 C120 C121 C13 C130 C131 C14 C145 C146 C149 C155 C156 C159 C17 C19 C2 C20 ... |
| 10 | 5 |  | LM2662MX/NOPB | M08A | LM2662MX/NOPB | UNVERIFIED | U18 U19 U20 U21 U22 |
| 11 | 1 |  | MA10-2 | MA10-2 | MA10-2 | UNVERIFIED | SV1 |
| 12 | 2 | 2.2µH | POWER_INDUCTOR | IND_VLP8040T-1R0N_TDK | POWER_INDUCTOR | UNVERIFIED | U$1 U$2 |
| 13 | 19 | 3.3µH | POWER_INDUCTOR | IND_VLP8040T-1R0N_TDK | POWER_INDUCTOR | UNVERIFIED | U$10 U$11 U$12 U$13 U$14 U$15 U$16 U$17 U$18 U$19 U$20 U$21 U$3 U$4 U$5 U$6 U$7 U$8 U$9 |
| 14 | 27 | 10k | R-EU_ | M0805 | R-EU_ | generic | R10 R12 R14 R16 R18 R2 R20 R22 R24 R26 R28 R30 R32 R34 R36 R38 R4 R40 R42 R44 R46 R48 R... |
| 15 | 2 | 11.5k | R-EU_ | M0805 | R-EU_ | generic | R54 R58 |
| 16 | 4 | 12k | R-EU_ | M0805 | R-EU_ | generic | R35 R43 R47 R9 |
| 17 | 1 | 13.7k | R-EU_ | M0805 | R-EU_ | generic | R3 |
| 18 | 1 | 23.4k | R-EU_ | M0805 | R-EU_ | generic | R49 |
| 19 | 1 | 2k | R-EU_ | M0805 | R-EU_ | generic | R39 |
| 20 | 1 | 3.09k | R-EU_ | M0805 | R-EU_ | generic | R1 |
| 21 | 6 | 32.2k | R-EU_ | M0805 | R-EU_ | generic | R11 R13 R15 R19 R5 R7 |
| 22 | 1 | 34.8k | R-EU_ | M0805 | R-EU_ | generic | R21 |
| 23 | 2 | 35.7k | R-EU_ | M0805 | R-EU_ | generic | R53 R57 |
| 24 | 11 | 56.2k | R-EU_ | M0805 | R-EU_ | generic | R17 R23 R25 R27 R29 R31 R37 R41 R45 R51 R55 |
| 25 | 1 | 61.9k | R-EU_ | M0805 | R-EU_ | generic | R33 |
| 26 | 10 |  | T521W476M020ATE045 | T521W | T521W476M020ATE045 | UNVERIFIED | C100 C101 C102 C103 C104 C105 C96 C97 C98 C99 |
| 27 | 21 |  | TPS562208DDCT | DDC0006A_N | TPS562208DDCT | UNVERIFIED | U1 U10 U11 U12 U13 U14 U15 U16 U17 U2 U24 U26 U28 U3 U31 U33 U4 U6 U7 U8 U9 |
| 28 | 2 |  | TPS7A8300RGRR | RGR20_2P05X2P05_TEX | TPS7A8300RGRR | UNVERIFIED | U32 U34 |
