herasymyuks/PLFM_RADAR-aeris/docs/BOM/BOM_RF_PA.md

# BOM extracted from `RF_PA.sch`

Physical parts: **25** references in **11** line items. Lines with an explicit MPN attribute: **0**. Every other `mpn_candidate` is the EAGLE deviceset name and is **UNVERIFIED**. Values missing in the schematic appear empty.

| # | Qty | Value | Deviceset | Package | MPN candidate | Status | References |
|---|---:|---|---|---|---|---|---|
| 1 | 2 |  | 142-0731-211 | 1420731211 | 142-0731-211 | UNVERIFIED | J1 J2 |
| 2 | 1 |  | 22-23-2021 | 22-23-2021 | 22-23-2021 | UNVERIFIED | X2 |
| 3 | 1 |  | 22-23-2031 | 22-23-2031 | 22-23-2031 | UNVERIFIED | X3 |
| 4 | 1 |  | AK300/2 | AK300/2 | AK300/2 | UNVERIFIED | 22V |
| 5 | 6 | 0.1µF | C-EU | C0402 | C-EU | generic | C2 C3 C6 C7 C8 C9 |
| 6 | 3 | 10µF | C-EU | C1206 | C-EU | generic | C1 C4 C5 |
| 7 | 1 |  | QPA2962_B | QPA2962_B | QPA2962_B | UNVERIFIED | U$1 |
| 8 | 6 | 0R | R-EU_ | R0402 | R-EU_ | generic | R2 R3 R5 R7 R8 R9 |
| 9 | 1 | 0R | R-EU_ | R0603 | R-EU_ | generic | R6 |
| 10 | 2 | 10R | R-EU_ | R0402 | R-EU_ | generic | R1 R4 |
| 11 | 1 | 5mR | WSL2816R1000FEH | WSL2816_VIS | WSL2816R1000FEH | UNVERIFIED | R10 |
