herasymyuks/PLFM_RADAR-aeris/docs/BOM/BOM_RF_PA.csv

item | qty | value | deviceset | device | package | library | mpn_attribute | manufacturer_attribute | mpn_candidate | mpn_status | references
1 | 2 |  | 142-0731-211 |  | 1420731211 | 142-0731-211 |  |  | 142-0731-211 | UNVERIFIED (deviceset name) | J1 J2
2 | 1 |  | 22-23-2021 |  | 22-23-2021 | con-molex |  |  | 22-23-2021 | UNVERIFIED (deviceset name) | X2
3 | 1 |  | 22-23-2031 |  | 22-23-2031 | con-molex |  |  | 22-23-2031 | UNVERIFIED (deviceset name) | X3
4 | 1 |  | AK300/2 |  | AK300/2 | con-ptr500 |  |  | AK300/2 | UNVERIFIED (deviceset name) | 22V
5 | 6 | 0.1µF | C-EU | C0402 | C0402 | rcl |  |  | C-EU | GENERIC — value/package only | C2 C3 C6 C7 C8 C9
6 | 3 | 10µF | C-EU | C1206 | C1206 | rcl |  |  | C-EU | GENERIC — value/package only | C1 C4 C5
7 | 1 |  | QPA2962_B |  | QPA2962_B | My_Library_RADAR |  |  | QPA2962_B | UNVERIFIED (deviceset name) | U$1
8 | 6 | 0R | R-EU_ | R0402 | R0402 | rcl |  |  | R-EU_ | GENERIC — value/package only | R2 R3 R5 R7 R8 R9
9 | 1 | 0R | R-EU_ | R0603 | R0603 | rcl |  |  | R-EU_ | GENERIC — value/package only | R6
10 | 2 | 10R | R-EU_ | R0402 | R0402 | rcl |  |  | R-EU_ | GENERIC — value/package only | R1 R4
11 | 1 | 5mR | WSL2816R1000FEH |  | WSL2816_VIS | My_Library_RADAR |  |  | WSL2816R1000FEH | UNVERIFIED (deviceset name) | R10
