herasymyuks/PLFM_RADAR-aeris/docs/BOM/BOM_FREQUENCY_SYNTHESIZER.md

# BOM extracted from `Clocks_Freq_Synth_board.sch`

Physical parts: **184** references in **40** line items. Lines with an explicit MPN attribute: **0**. Every other `mpn_candidate` is the EAGLE deviceset name and is **UNVERIFIED**. Values missing in the schematic appear empty.

| # | Qty | Value | Deviceset | Package | MPN candidate | Status | References |
|---|---:|---|---|---|---|---|---|
| 1 | 11 |  | 142-0731-211 | 1420731211 | 142-0731-211 | UNVERIFIED | J1 J10 J11 J12 J13 J2 J5 J6 J7 J8 J9 |
| 2 | 6 |  | 22-23-2021 | 22-23-2021 | 22-23-2021 | UNVERIFIED | X10 X11 X12 X13 X14 X15 |
| 3 | 1 |  | AD9523BCPZ | QFN50P1000X1000X100-73N | AD9523BCPZ | UNVERIFIED | IC1 |
| 4 | 2 |  | ADF4382ABCCZ | CC-48-10_ADI | ADF4382ABCCZ | UNVERIFIED | U1 U6 |
| 5 | 4 |  | ATS1005-3DB-FD-T05 | SMT_DB-FD-T05_SUS | ATS1005-3DB-FD-T05 | UNVERIFIED | U10 U4 U5 U8 |
| 6 | 3 |  | C-EU | C0201 | C-EU | generic | C4 C5 C7 |
| 7 | 25 | 0.1µF | C-EU | C0201 | C-EU | generic | C16 C18 C20 C22 C24 C26 C28 C30 C32 C34 C35 C36 C37 C41 C42 C43 C44 C64 C65 C66 C67 C87... |
| 8 | 1 | 0.1µf | C-EU | C0201 | C-EU | generic | C92 |
| 9 | 2 | 0.33µF | C-EU | C0201 | C-EU | generic | C2 C6 |
| 10 | 2 | 0.47µF | C-EU | C0201 | C-EU | generic | C10 C9 |
| 11 | 1 | 0.47µf | C-EU | C0201 | C-EU | generic | C3 |
| 12 | 1 | 1000pF | C-EU | C0201 | C-EU | generic | C8 |
| 13 | 3 | 10nF | C-EU | C0402 | C-EU | generic | C15 C17 C19 |
| 14 | 2 | 10nF | C-EU | C0201 | C-EU | generic | C61 C84 |
| 15 | 6 | 10pF | C-EU | C0201 | C-EU | generic | C1 C62 C63 C85 C86 C89 |
| 16 | 5 | 10µF | C-EU | C1210 | C-EU | generic | C23 C27 C31 C45 C47 |
| 17 | 10 | 1µF | C-EU | C0201 | C-EU | generic | C11 C12 C13 C14 C59 C68 C69 C70 C71 C82 |
| 18 | 6 | 22µF | C-EU | C1210 | C-EU | generic | C21 C25 C29 C33 C46 C51 |
| 19 | 2 | 31pF | C-EU | C0201 | C-EU | generic | C60 C83 |
| 20 | 20 | 4.7µF | C-EU | C0201 | C-EU | generic | C38 C39 C40 C48 C49 C50 C55 C56 C57 C58 C72 C73 C74 C75 C76 C77 C78 C79 C80 C81 |
| 21 | 2 |  | CJT-T-P-HH-ST-TH1 | CONN_CJT-T-P-XX-ST-TH1_SAI | CJT-T-P-HH-ST-TH1 | UNVERIFIED | J3 J4 |
| 22 | 2 |  | CVHD-950-50.000 | SMD4_CVHD-950_CRX | CVHD-950-50.000 | UNVERIFIED | X5 X6 |
| 23 | 1 |  | ECOC-2522-100.000-3HC | SMD5_ECOC-2522_25P4X22_ECS | ECOC-2522-100.000-3HC | UNVERIFIED | X4 |
| 24 | 4 |  | FBMH1608HL601-T | BEADC1608X90N | FBMH1608HL601-T | UNVERIFIED | FB1 FB2 FB3 FB4 |
| 25 | 5 |  | L-EU | L5650M | L-EU | generic | L10 L11 L12 L13 L9 |
| 26 | 8 | 1.3nH | L-US | L0201 | L-US | UNVERIFIED | L1 L2 L3 L4 L5 L6 L7 L8 |
| 27 | 2 | Green | LED-GREEN | LED-0603 | LED-GREEN | UNVERIFIED | D1 D2 |
| 28 | 4 |  | MTX2-143+ | DQ1225_MNC | MTX2-143+ | UNVERIFIED | U2 U3 U7 U9 |
| 29 | 1 |  | PINHD-2X6 | 2X06 | PINHD-2X6 | UNVERIFIED | JP1 |
| 30 | 1 |  | PINHD-2X7 | 2X07 | PINHD-2X7 | UNVERIFIED | JP2 |
| 31 | 3 | 0.65k | R-EU_ | R0201 | R-EU_ | generic | R10 R6 R8 |
| 32 | 9 | 0R | R-EU_ | R0201 | R-EU_ | generic | R14 R15 R19 R20 R27 R28 R32 R33 R5 |
| 33 | 4 | 100R | R-EU_ | R0201 | R-EU_ | generic | R1 R12 R13 R26 |
| 34 | 6 | 1k | R-EU_ | R0201 | R-EU_ | generic | R11 R2 R3 R4 R7 R9 |
| 35 | 8 | 200k | R-EU_ | R0201 | R-EU_ | generic | R22 R23 R24 R25 R35 R36 R37 R38 |
| 36 | 3 | 22R | R-EU_ | R0201 | R-EU_ | generic | R39 R40 R41 |
| 37 | 2 | 30R | R-EU_ | R0201 | R-EU_ | generic | R17 R30 |
| 38 | 2 | 330R | R-EU_ | R0201 | R-EU_ | generic | R18 R31 |
| 39 | 2 | 500R | R-EU_ | R0201 | R-EU_ | generic | R21 R34 |
| 40 | 2 | 931R | R-EU_ | R0201 | R-EU_ | generic | R16 R29 |
