herasymyuks/PLFM_RADAR-aeris/engineering/DESIGN/ANTENNA/kicad_exports/aeris10_patch_array.step

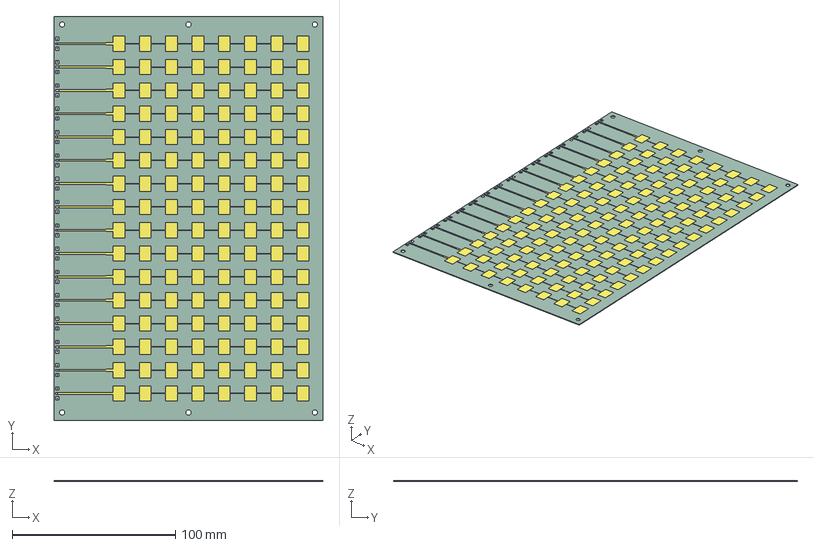
[picture p56: CAD file, 2026-10-09]
engineering/DESIGN/ANTENNA/kicad_exports/aeris10_patch_array.step
165.0 x 248.0 x 0.588 mm
aeris10_patch_array_copper
aeris10_patch_array_pad
aeris10_patch_array_PCB
