herasymyuks/PLFM_RADAR-aeris/engineering/DESIGN/MECHANICAL/CAD/aeris10_head_shell.stl

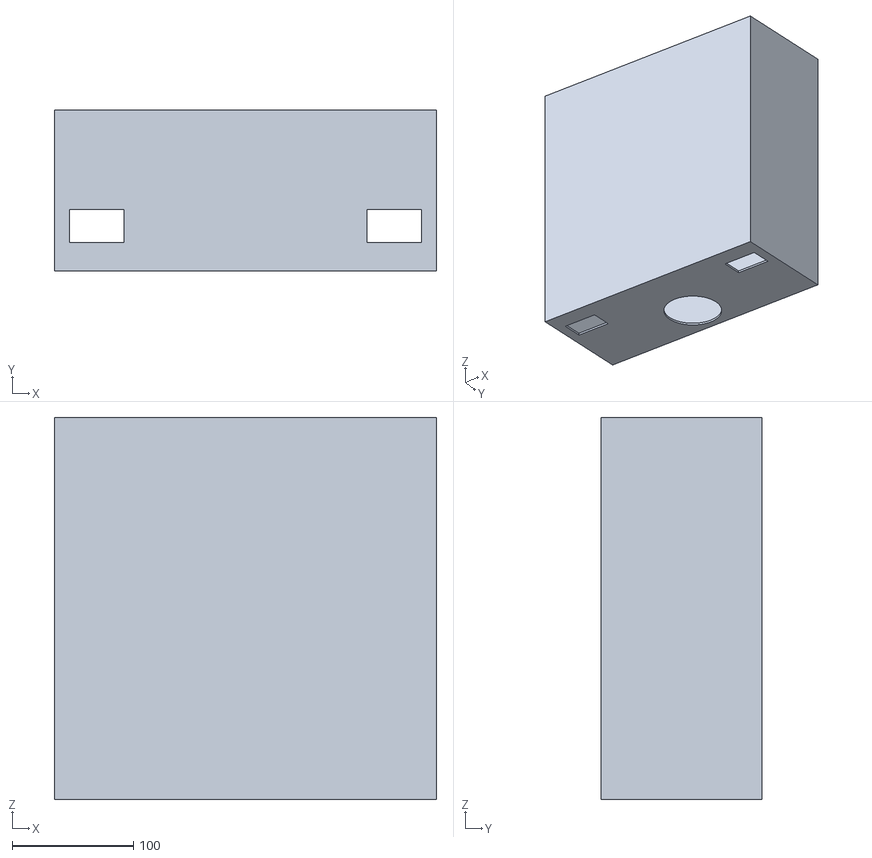
[picture p57: CAD file, 2026-10-09]
engineering/DESIGN/MECHANICAL/CAD/aeris10_head_shell.stl
315.0 x 132.6 x 315.0
