herasymyuks/PLFM_RADAR-aeris/engineering/DESIGN/MECHANICAL/CAD/detail/aeris10_pedestal_detail.step

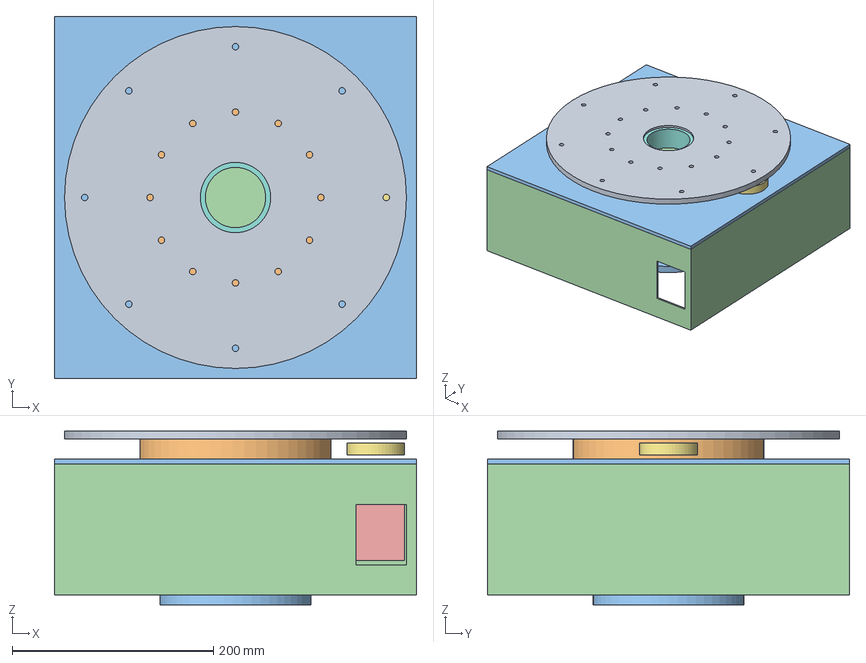
[picture p58: CAD file, 2026-10-09]
engineering/DESIGN/MECHANICAL/CAD/detail/aeris10_pedestal_detail.step
360.0 x 360.0 x 173.0 mm
Turntable plate Ø340×8 Al, 8×M6 to the head base, 12×M6 to the bearing outer ring
Slewing bearing OD190/ID100×20 (4-point contact, e.g. igus PRT-04-100 class)
Ring pulley GT3 180T Ø172 Al (machined/3D-printed), clamped under the turntable
Pedestal top plate 360×360×5 Al, 12×M6 to the bearing inner ring, bore Ø90
Pedestal housing 360×360×125 folded 2.5 mm Al (4 bends), open top, connector panel cut-out
Stepper NEMA 23 76 mm
Motor bracket 80×80×3 Al with slotted belt-tension holes
Motor pulley GT3 60T Ø57, bore 6.35
Through-bore slip ring Ø99×60, bore 60, 12 circuits (4×10 A, 4×10 A, 4 signal)
Slip-ring stator bracket 140×140×3 Al
Stepper driver TB6600 on DIN rail
Mast flange Ø150×10 steel, 4×M10 PCD 110 (ASSUMPTION — mast interface undefined)
