herasymyuks/PLFM_RADAR-aeris/engineering/MECHANICAL/DXF/POWER_SUPPLY_outline_holes_eagle.dxf

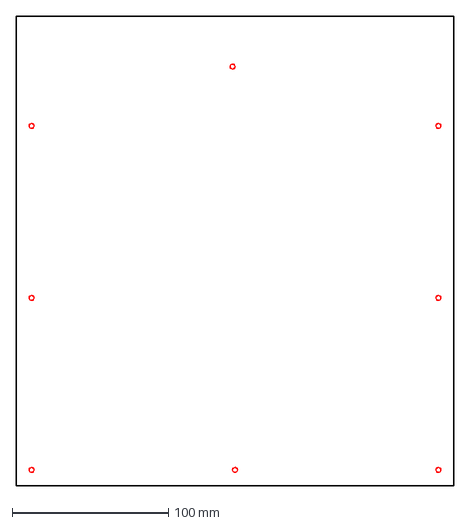
[picture p59: CAD file, 2026-10-09]
engineering/MECHANICAL/DXF/POWER_SUPPLY_outline_holes_eagle.dxf
280.0 x 300.0 mm
