herasymyuks/PLFM_RADAR-aeris/beta/pcb/FREQUENCY_SYNTHESIZER/exports/mechanical/FREQUENCY_SYNTHESIZER_top_fab.dxf

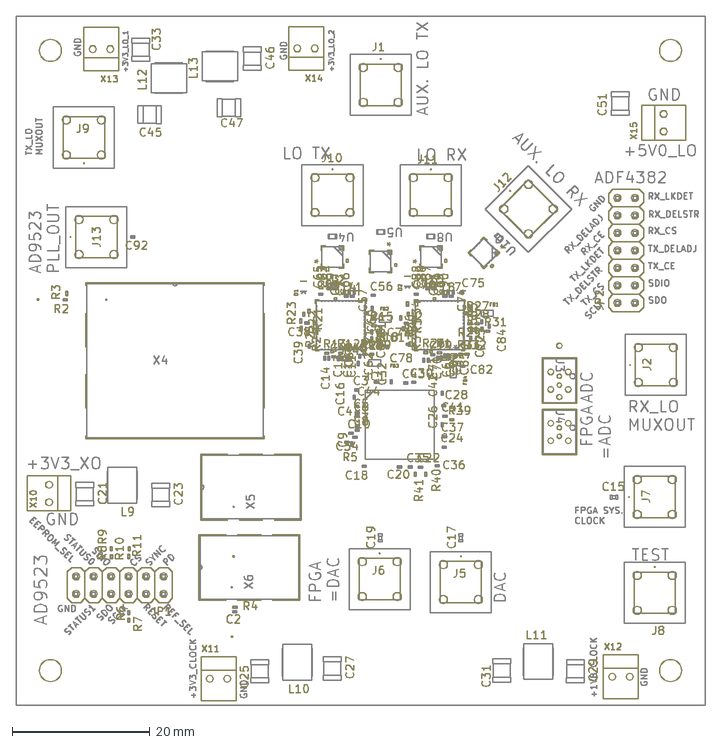
[picture p60: CAD file, 2026-10-09]
beta/pcb/FREQUENCY_SYNTHESIZER/exports/mechanical/FREQUENCY_SYNTHESIZER_top_fab.dxf
100.0 x 100.0 mm
