herasymyuks/PLFM_RADAR-aeris/beta/pcb/RF_PA/exports/mechanical/RF_PA_outline.dxf

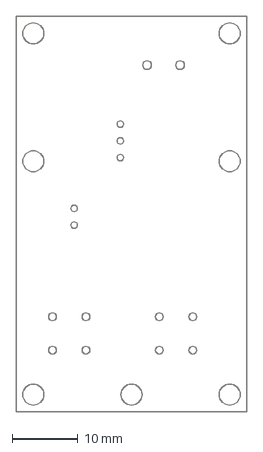
[picture p62: CAD file, 2026-10-09]
beta/pcb/RF_PA/exports/mechanical/RF_PA_outline.dxf
35.0 x 60.0 mm
