herasymyuks/PLFM_RADAR-aeris/engineering/DESIGN/MECHANICAL/CAD/aeris10_pedestal_only.step

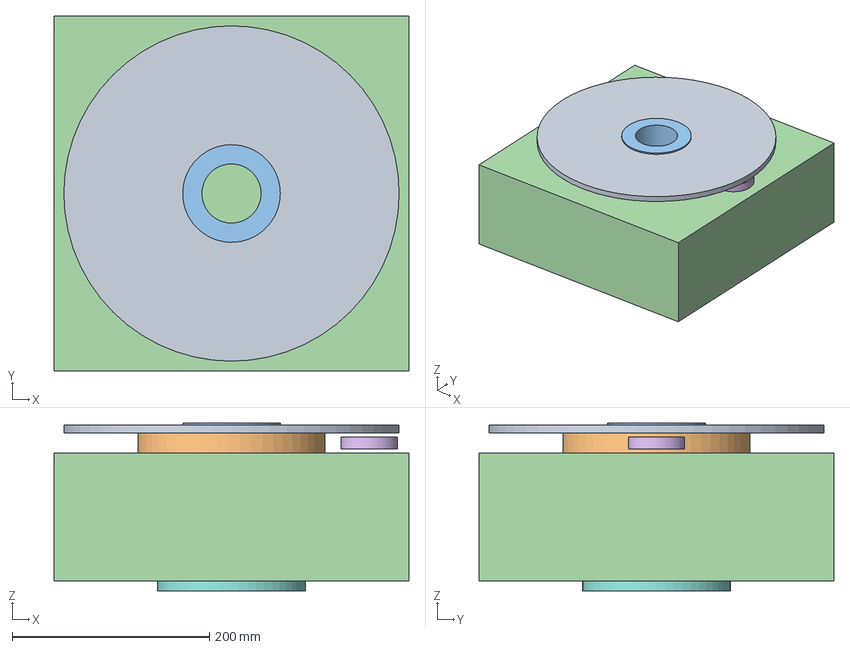
[picture p63: CAD file, 2026-10-09]
engineering/DESIGN/MECHANICAL/CAD/aeris10_pedestal_only.step
360.0 x 360.0 x 170.0 mm
Turntable plate Ø340x8 Al (bolted to the head base)
Slewing bearing OD190/ID100x20 (steel)
Ring pulley GT3 180T Ø172.0 (Al, on the turntable)
Through-bore slip ring Ø99x60, 12 circuits
Pedestal housing 360x360x130 (2.5 mm Al)
Stepper NEMA 23 (56.4x56.4x76)
Motor pulley GT3 60T
Stepper driver TB6600 (96x72x36)
Mast flange Ø150x10, 4xM10 PCD110 (ASSUMPTION)
