herasymyuks/PLFM_RADAR-aeris/engineering/DESIGN/MECHANICAL/CAD/detail/aeris10_enclosure_detail.step

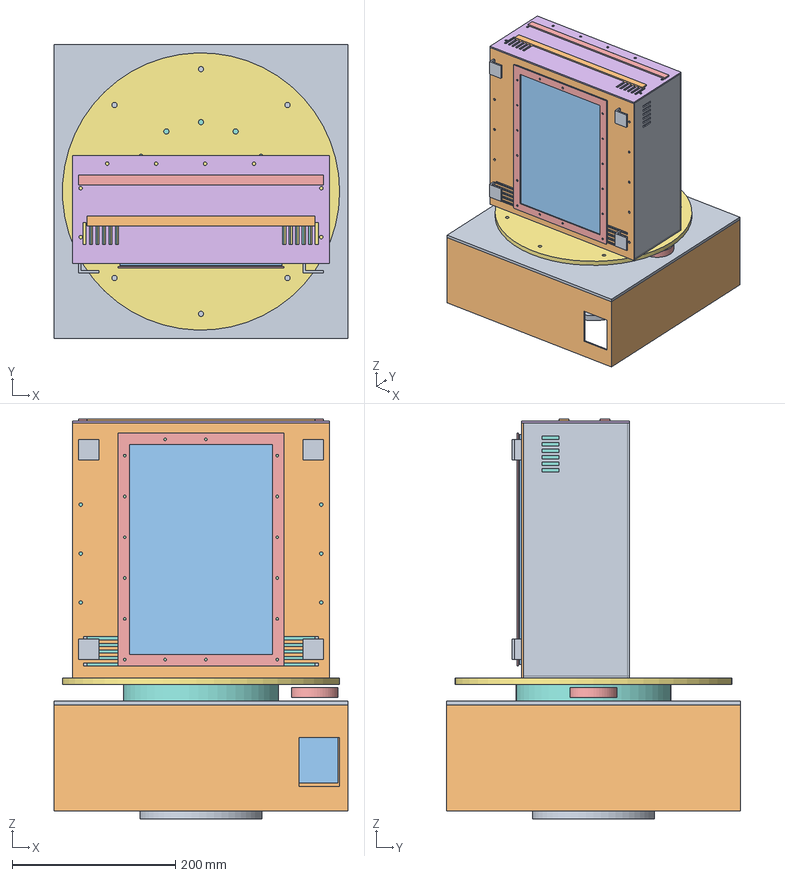
[picture p64: CAD file, 2026-10-09]
engineering/DESIGN/MECHANICAL/CAD/detail/aeris10_enclosure_detail.step
360.0 x 360.0 x 490.5 mm
Tray — base + sides + rear, 2.5 mm Al 5754, 3 bends R2.5, flanges 15 mm with M4 PEM nuts
Front plate 2.5 mm Al with radome window opening and intake louvres
Radome window PTFE 2 mm (outside the front plate)
Window gasket EPDM 1.5 mm (ring 10 mm)
Window clamp frame 2 mm Al, 14 mm wide
Lid 2.5 mm Al with exhaust slots
Lid gasket EPDM 3 mm self-adhesive, 15 mm wide on the flanges
PA heat spreader 300×300×10 Al 6061, machined fin fields, M3 tapped (16×7 PA + 6 antenna)
Plate bracket L 25×25×3 Al at x=5 z=20
Plate bracket L 25×25×3 Al at x=5 z=265.0
Plate bracket L 25×25×3 Al at x=280 z=20
Plate bracket L 25×25×3 Al at x=280 z=265.0
Main Board carrier rail bottom U15×12×1.5 Al, 280 mm
Main Board carrier rail top U15×12×1.5 Al, 280 mm
Main Board standoff M3×10 hex at (4,4)
Main Board standoff M3×10 hex at (256,4)
Main Board standoff M3×10 hex at (116,114)
Main Board standoff M3×10 hex at (256,114)
Main Board standoff M3×10 hex at (116,250)
Main Board standoff M3×10 hex at (256,250)
Main Board standoff M3×10 hex at (4,296)
Main Board standoff M3×10 hex at (256,296)
Synth carrier rail bottom U15×12×1.5 Al, 120 mm
Synth carrier rail top U15×12×1.5 Al, 120 mm
Synth standoff M3×10 hex at (5,5)
Synth standoff M3×10 hex at (95,5)
Synth standoff M3×10 hex at (5,95)
Synth standoff M3×10 hex at (95,95)
Power Board carrier rail bottom U15×12×1.5 Al, 300 mm
Power Board carrier rail top U15×12×1.5 Al, 300 mm
Power Board standoff M3×10 hex at (10,10)
Power Board standoff M3×10 hex at (140,10)
Power Board standoff M3×10 hex at (270,10)
Power Board standoff M3×10 hex at (10,120)
Power Board standoff M3×10 hex at (270,120)
Power Board standoff M3×10 hex at (10,230)
Power Board standoff M3×10 hex at (270,230)
Power Board standoff M3×10 hex at (138,268)
Cable-entry gland plate 100×100×2 Al under the base (M32 + M20 glands)
Turntable plate Ø340×8 Al, 8×M6 to the head base, 12×M6 to the bearing outer ring
Slewing bearing OD190/ID100×20 (4-point contact, e.g. igus PRT-04-100 class)
Ring pulley GT3 180T Ø172 Al (machined/3D-printed), clamped under the turntable
Pedestal top plate 360×360×5 Al, 12×M6 to the bearing inner ring, bore Ø90
Pedestal housing 360×360×125 folded 2.5 mm Al (4 bends), open top, connector panel cut-out
Stepper NEMA 23 76 mm
Motor bracket 80×80×3 Al with slotted belt-tension holes
Motor pulley GT3 60T Ø57, bore 6.35
Through-bore slip ring Ø99×60, bore 60, 12 circuits (4×10 A, 4×10 A, 4 signal)
Slip-ring stator bracket 140×140×3 Al
Stepper driver TB6600 on DIN rail
Mast flange Ø150×10 steel, 4×M10 PCD 110 (ASSUMPTION — mast interface undefined)
