herasymyuks/PLFM_RADAR-aeris/engineering/MECHANICAL/DXF/FREQUENCY_SYNTHESIZER_outline_holes_eagle.dxf

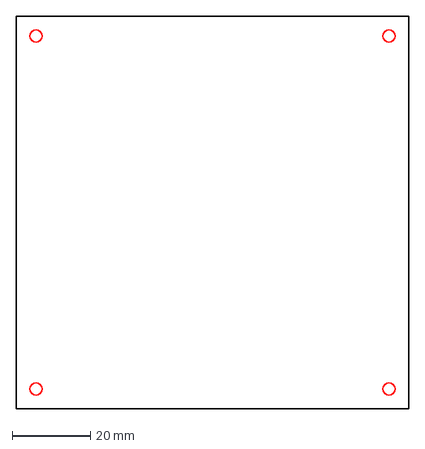
[picture p65: CAD file, 2026-10-09]
engineering/MECHANICAL/DXF/FREQUENCY_SYNTHESIZER_outline_holes_eagle.dxf
100.0 x 100.0 mm
