herasymyuks/PLFM_RADAR-aeris/beta/pcb/POWER_SUPPLY/exports/mechanical/POWER_SUPPLY_top_fab.dxf

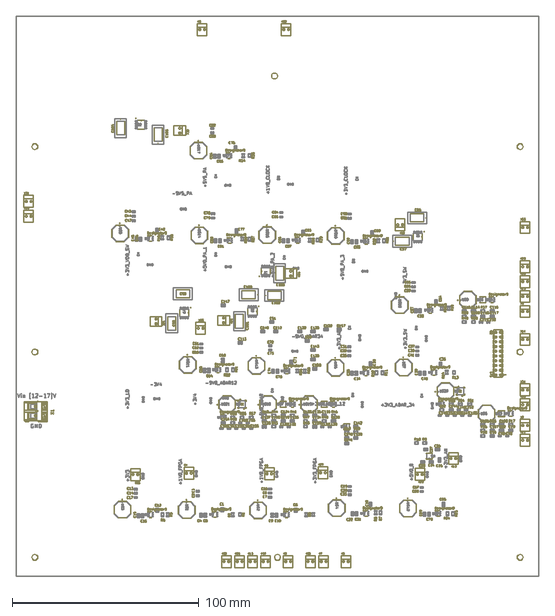
[picture p67: CAD file, 2026-10-09]
beta/pcb/POWER_SUPPLY/exports/mechanical/POWER_SUPPLY_top_fab.dxf
280.0 x 300.0 mm
