herasymyuks/PLFM_RADAR-aeris/beta/pcb/RF_PA/exports/mechanical/RF_PA_top_fab.dxf

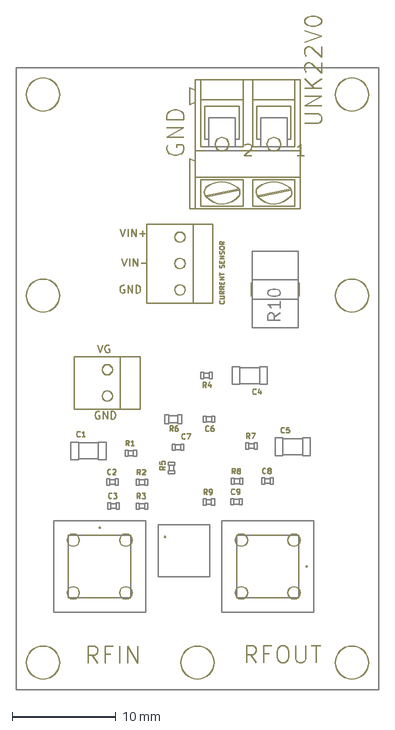
[picture p68: CAD file, 2026-10-09]
beta/pcb/RF_PA/exports/mechanical/RF_PA_top_fab.dxf
35.0 x 64.9 mm
