herasymyuks/PLFM_RADAR-aeris/engineering/DESIGN/MECHANICAL/CAD/aeris10_head_only.step

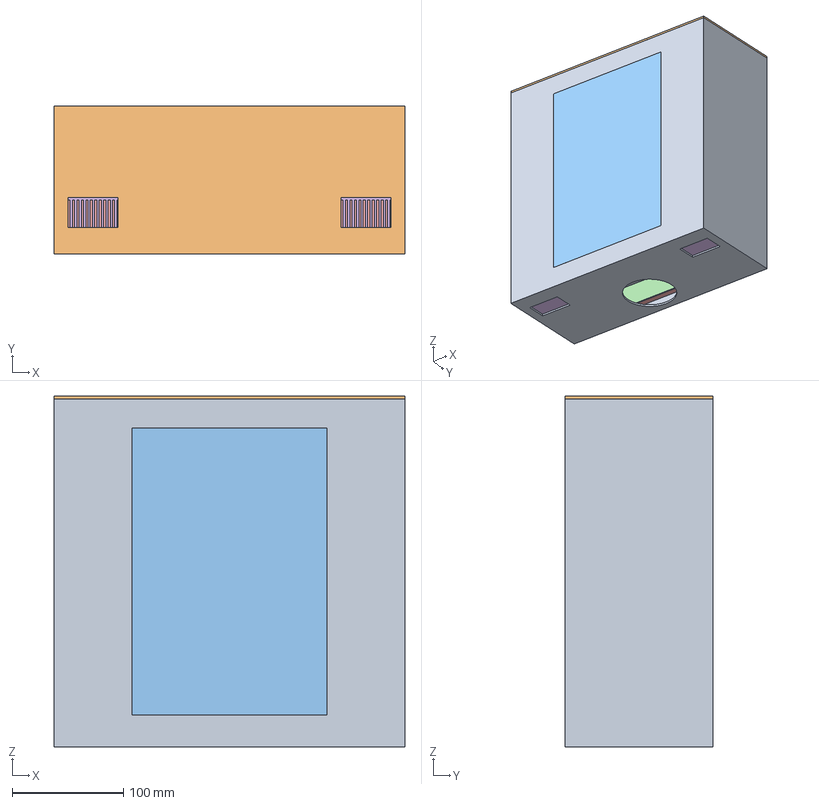
[picture p69: CAD file, 2026-10-09]
engineering/DESIGN/MECHANICAL/CAD/aeris10_head_only.step
315.0 x 132.6 x 315.0 mm
Chassis (2.5 mm Al, folded)
Lid (2.5 mm Al)
Radome window (PTFE 2 mm)
Antenna panel PCB 16x8 patches (RO4350B 0.508 + Cu)
PA heat spreader 300x300x10 Al with 2 fin fields
RF PA board PA1 (35x60)
PA1 component envelope
RF PA board PA2 (35x60)
PA2 component envelope
RF PA board PA3 (35x60)
PA3 component envelope
RF PA board PA4 (35x60)
PA4 component envelope
RF PA board PA5 (35x60)
PA5 component envelope
RF PA board PA6 (35x60)
PA6 component envelope
RF PA board PA7 (35x60)
PA7 component envelope
RF PA board PA8 (35x60)
PA8 component envelope
RF PA board PA9 (35x60)
PA9 component envelope
RF PA board PA10 (35x60)
PA10 component envelope
RF PA board PA11 (35x60)
PA11 component envelope
RF PA board PA12 (35x60)
PA12 component envelope
RF PA board PA13 (35x60)
PA13 component envelope
RF PA board PA14 (35x60)
PA14 component envelope
RF PA board PA15 (35x60)
PA15 component envelope
RF PA board PA16 (35x60)
PA16 component envelope
Main Board (260x300, vertical)
Main Board component envelope (15 mm, ASSUMED)
Frequency Synthesizer (100x100, vertical)
Synth component envelope
Power Board (280x300, vertical)
Power Board component envelope (15 mm, ASSUMED)
Fan 60x60x15 (duct intake)
Fan 60x60x15 (duct intake)001
22 V PA supply + gate module (DSN-PSU-01, 120x80)
