herasymyuks/PLFM_RADAR-aeris/engineering/DESIGN/MECHANICAL/CAD/aeris10_orthographic.dxf

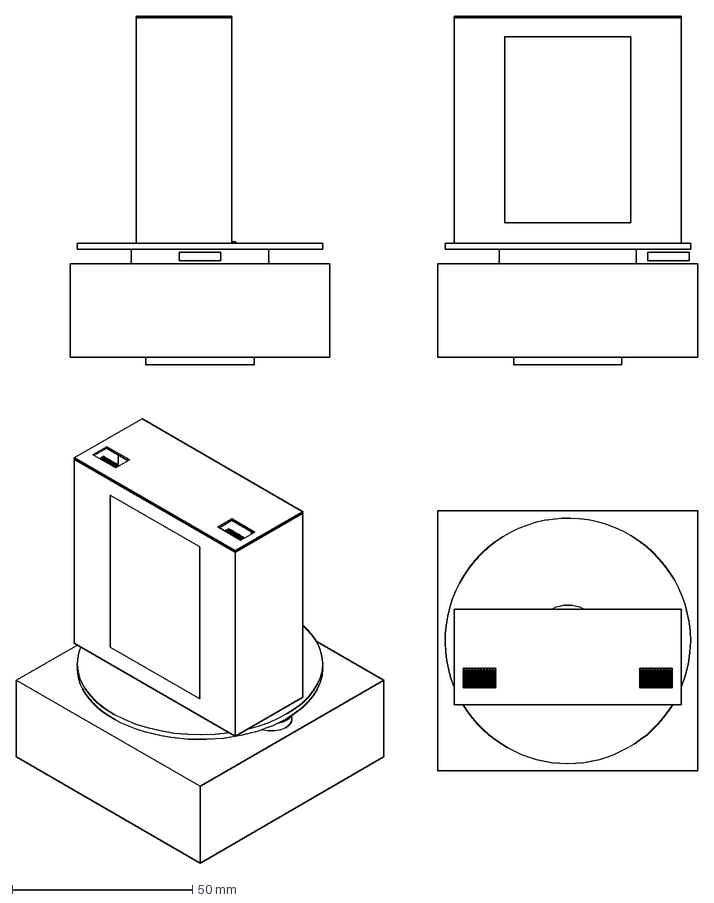
[picture p71: CAD file, 2026-10-09]
engineering/DESIGN/MECHANICAL/CAD/aeris10_orthographic.dxf
188.8 x 234.7 mm
