herasymyuks/PLFM_RADAR-aeris/engineering/DESIGN/MECHANICAL/CAD/detail/aeris10_head_shell_detail.stl

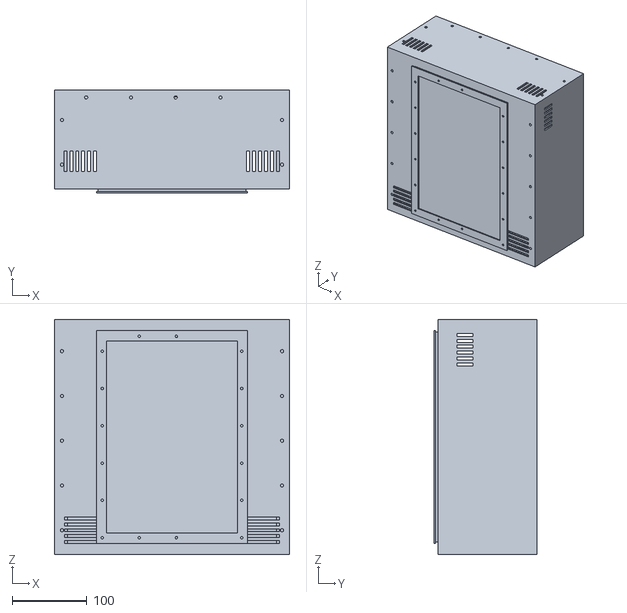
[picture p72: CAD file, 2026-10-09]
engineering/DESIGN/MECHANICAL/CAD/detail/aeris10_head_shell_detail.stl
315.0 x 138.1 x 315.0
