herasymyuks/PLFM_RADAR-aeris/engineering/MECHANICAL/DXF/POWER_SUPPLY_outline_kicad.dxf

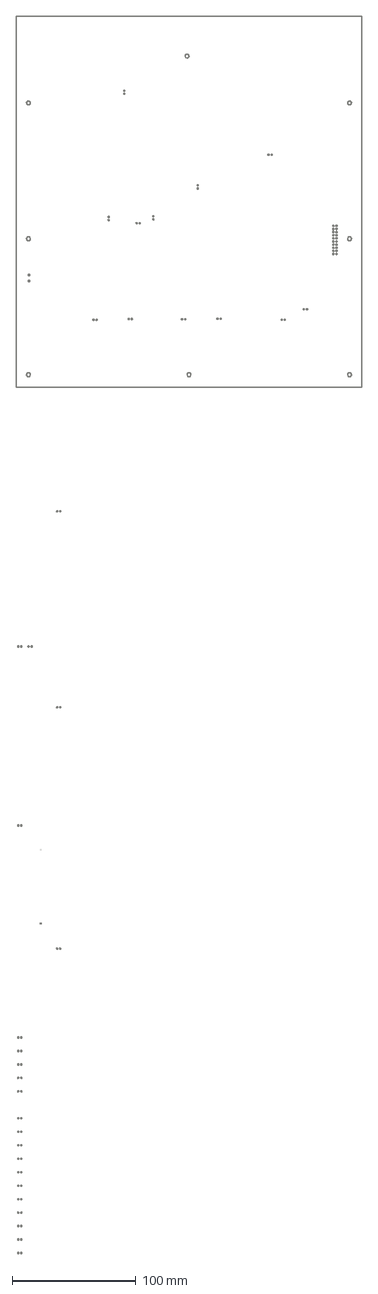
[picture p73: CAD file, 2026-10-09]
engineering/MECHANICAL/DXF/POWER_SUPPLY_outline_kicad.dxf
280.0 x 1001.5 mm
