herasymyuks/PLFM_RADAR-aeris/engineering/DESIGN/MECHANICAL/CAD/detail/aeris10_head_internals_detail.stl

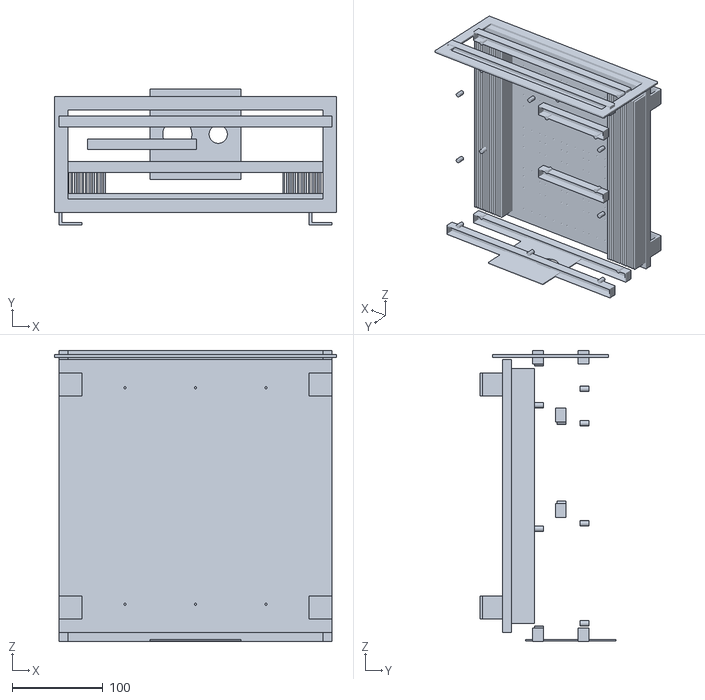
[picture p74: CAD file, 2026-10-09]
engineering/DESIGN/MECHANICAL/CAD/detail/aeris10_head_internals_detail.stl
310.0 x 150.0 x 320.0
