herasymyuks/PLFM_RADAR-aeris/engineering/DESIGN/MECHANICAL/CAD/detail/parts/Power_Board_carrier_rail_top_U15_12_1_5_.step

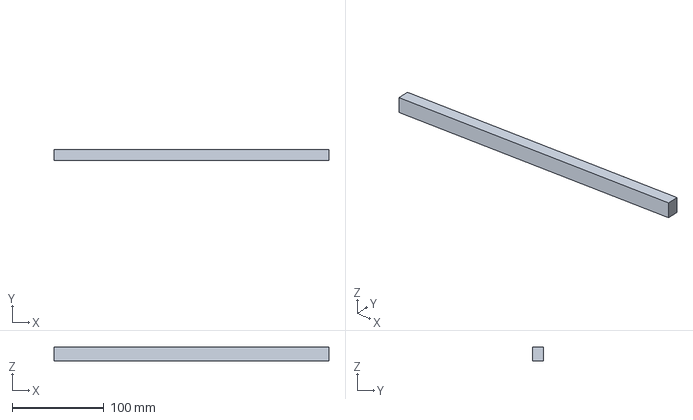
[picture p75: CAD file, 2026-10-09]
engineering/DESIGN/MECHANICAL/CAD/detail/parts/Power_Board_carrier_rail_top_U15_12_1_5_.step
300.0 x 12.0 x 15.0 mm
