herasymyuks/PLFM_RADAR-aeris/engineering/MECHANICAL/DXF/RF_PA_outline_holes_eagle.dxf

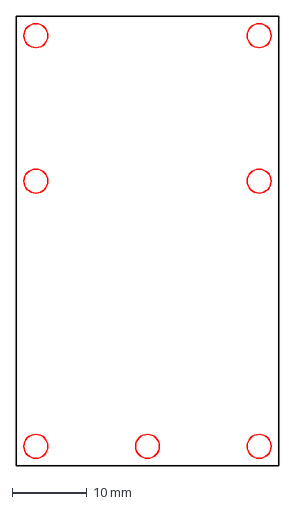
[picture p76: CAD file, 2026-10-09]
engineering/MECHANICAL/DXF/RF_PA_outline_holes_eagle.dxf
35.0 x 60.0 mm
