herasymyuks/PLFM_RADAR-aeris/engineering/DESIGN/MECHANICAL/CAD/detail/parts/Pedestal_top_plate_360_360_5_Al__12_M6_t.step

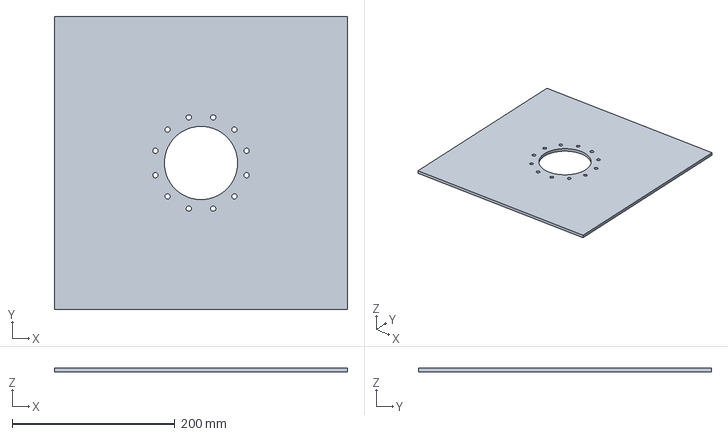
[picture p78: CAD file, 2026-10-09]
engineering/DESIGN/MECHANICAL/CAD/detail/parts/Pedestal_top_plate_360_360_5_Al__12_M6_t.step
360.0 x 360.0 x 5.00 mm
