herasymyuks/PLFM_RADAR-aeris/engineering/DESIGN/MECHANICAL/CAD/aeris10_head_internals.stl

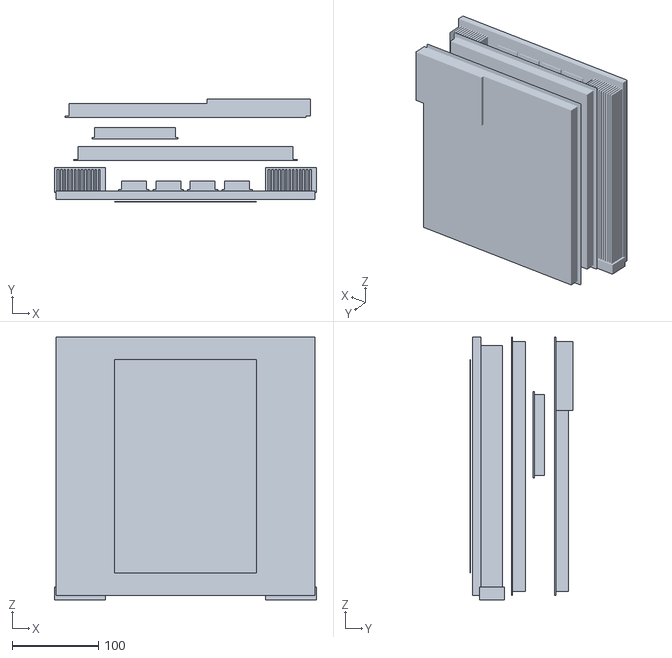
[picture p79: CAD file, 2026-10-09]
engineering/DESIGN/MECHANICAL/CAD/aeris10_head_internals.stl
304.0 x 119.6 x 305.0
