herasymyuks/PLFM_RADAR-aeris/engineering/DESIGN/MECHANICAL/CAD/detail/parts/Mast_flange_Ø150_10_steel__4_M10_PCD_110.step

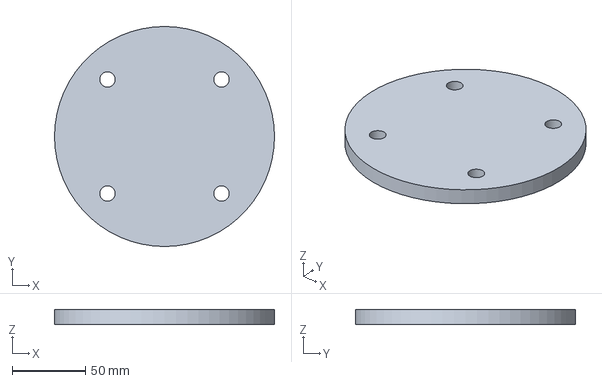
[picture p80: CAD file, 2026-10-09]
engineering/DESIGN/MECHANICAL/CAD/detail/parts/Mast_flange_Ø150_10_steel__4_M10_PCD_110.step
150.0 x 150.0 x 10.0 mm
