herasymyuks/PLFM_RADAR-aeris/engineering/DESIGN/MECHANICAL/CAD/detail/parts/Slip_ring_stator_bracket_140_140_3_Al.step

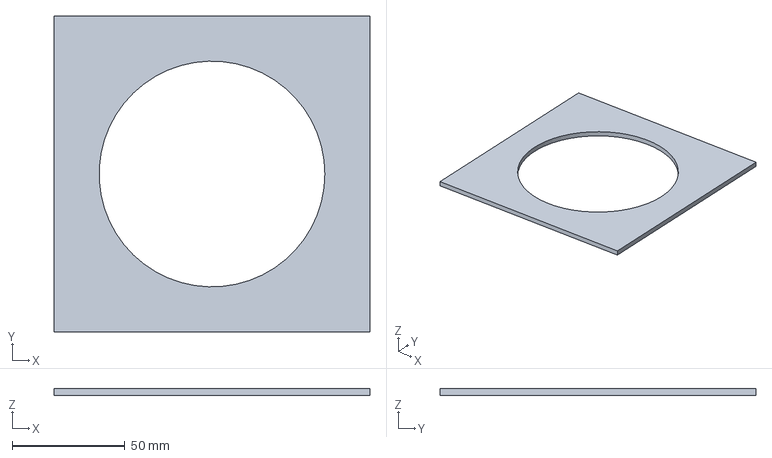
[picture p81: CAD file, 2026-10-09]
engineering/DESIGN/MECHANICAL/CAD/detail/parts/Slip_ring_stator_bracket_140_140_3_Al.step
140.0 x 140.0 x 3.00 mm
