herasymyuks/PLFM_RADAR-aeris/engineering/DESIGN/MECHANICAL/CAD/detail/parts/Stepper_NEMA_23_76_mm.step

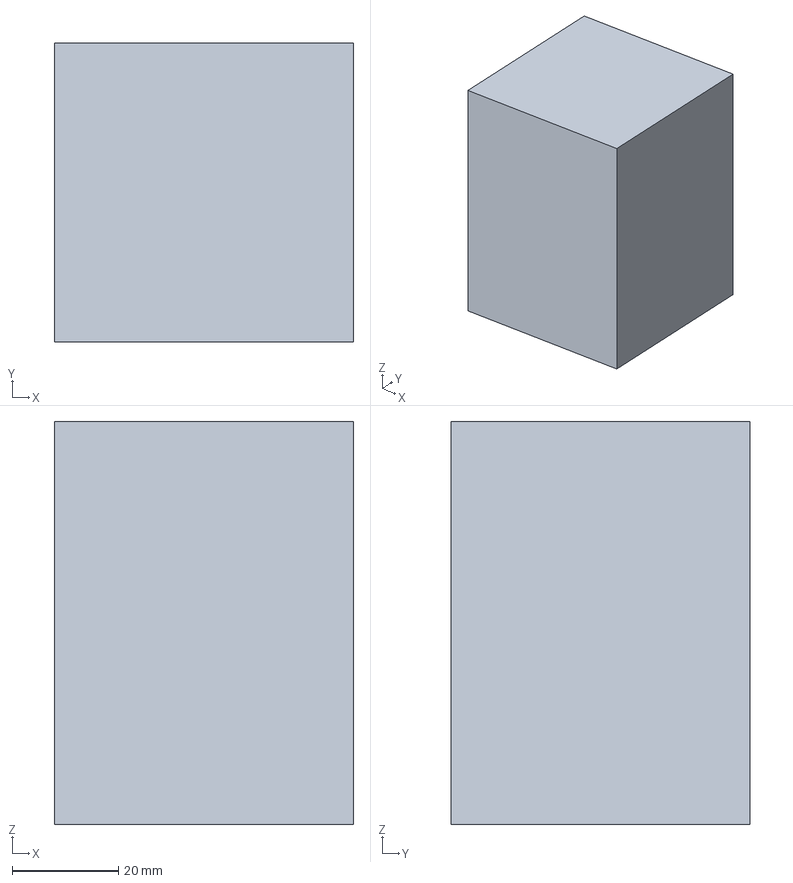
[picture p82: CAD file, 2026-10-09]
engineering/DESIGN/MECHANICAL/CAD/detail/parts/Stepper_NEMA_23_76_mm.step
56.4 x 56.4 x 76.0 mm
