herasymyuks/PLFM_RADAR-aeris/engineering/DESIGN/MECHANICAL/CAD/detail/parts/Motor_pulley_GT3_60T_Ø57__bore_6_35.step

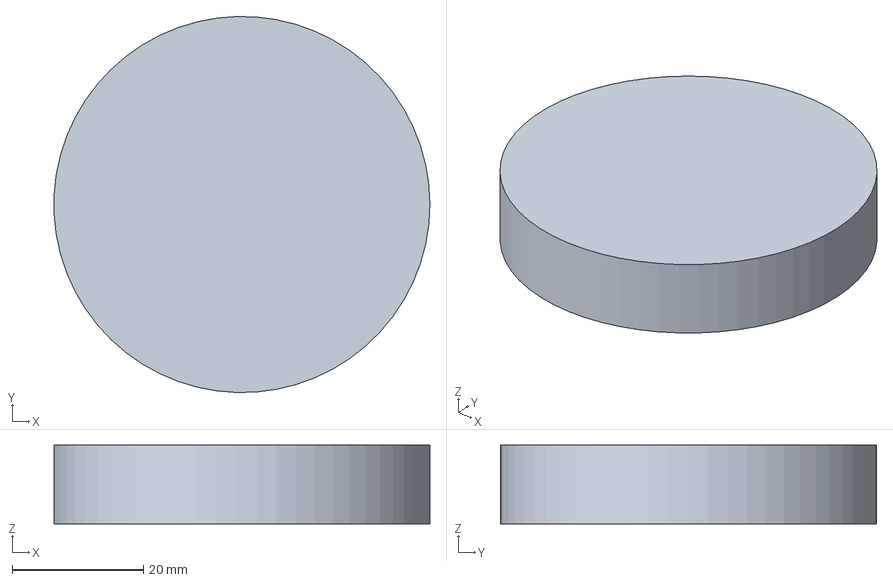
[picture p83: CAD file, 2026-10-09]
engineering/DESIGN/MECHANICAL/CAD/detail/parts/Motor_pulley_GT3_60T_Ø57__bore_6_35.step
57.3 x 57.3 x 12.0 mm
