herasymyuks/PLFM_RADAR-aeris/engineering/DESIGN/MECHANICAL/CAD/detail/parts/Plate_bracket_L_25_25_3_Al_at_x_280_z_20.step

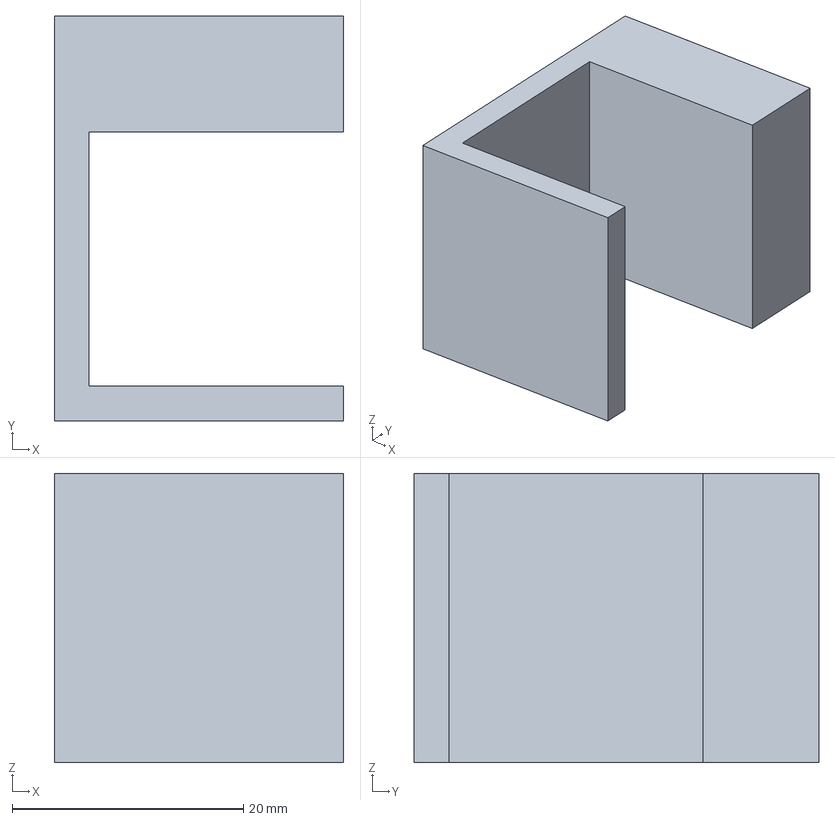
[picture p84: CAD file, 2026-10-09]
engineering/DESIGN/MECHANICAL/CAD/detail/parts/Plate_bracket_L_25_25_3_Al_at_x_280_z_20.step
25.0 x 35.0 x 25.0 mm
