herasymyuks/PLFM_RADAR-aeris/engineering/DESIGN/MECHANICAL/CAD/detail/parts/Through_bore_slip_ring_Ø99_60__bore_60__.step

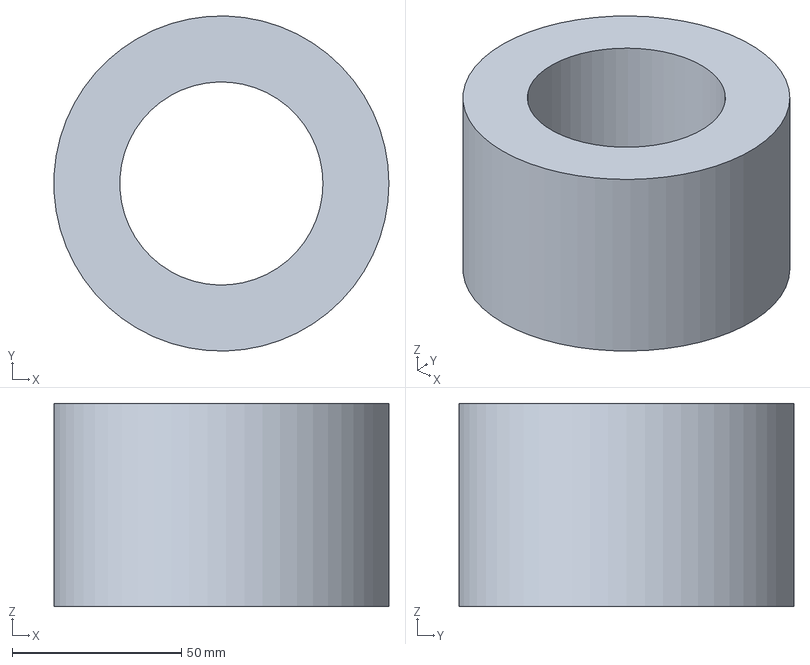
[picture p85: CAD file, 2026-10-09]
engineering/DESIGN/MECHANICAL/CAD/detail/parts/Through_bore_slip_ring_Ø99_60__bore_60__.step
98.9 x 99.0 x 60.0 mm
