herasymyuks/PLFM_RADAR-aeris/engineering/DESIGN/MECHANICAL/CAD/detail/parts/Slewing_bearing_OD190_ID100_20__4_point_.step

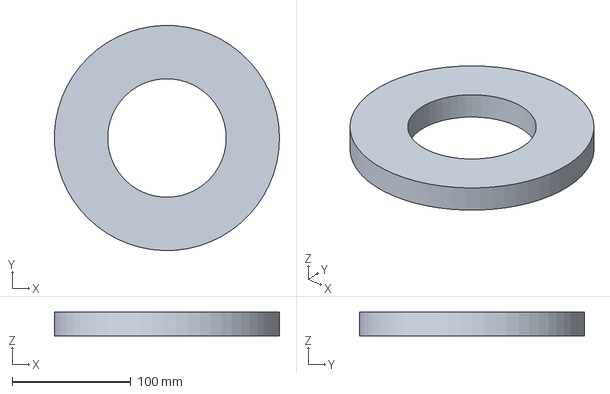
[picture p86: CAD file, 2026-10-09]
engineering/DESIGN/MECHANICAL/CAD/detail/parts/Slewing_bearing_OD190_ID100_20__4_point_.step
189.9 x 189.9 x 20.0 mm
