herasymyuks/PLFM_RADAR-aeris/engineering/DESIGN/MECHANICAL/CAD/detail/parts/Lid_gasket_EPDM_3_mm_self_adhesive__15_m.step

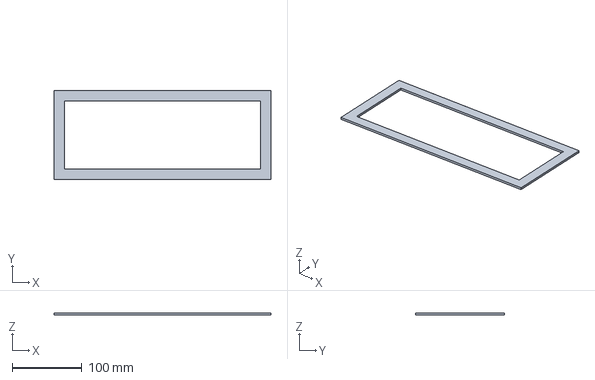
[picture p87: CAD file, 2026-10-09]
engineering/DESIGN/MECHANICAL/CAD/detail/parts/Lid_gasket_EPDM_3_mm_self_adhesive__15_m.step
310.0 x 127.6 x 3.00 mm
