herasymyuks/PLFM_RADAR-aeris/engineering/DESIGN/MECHANICAL/CAD/detail/parts/PA_heat_spreader_300_300_10_Al_6061__mac.step

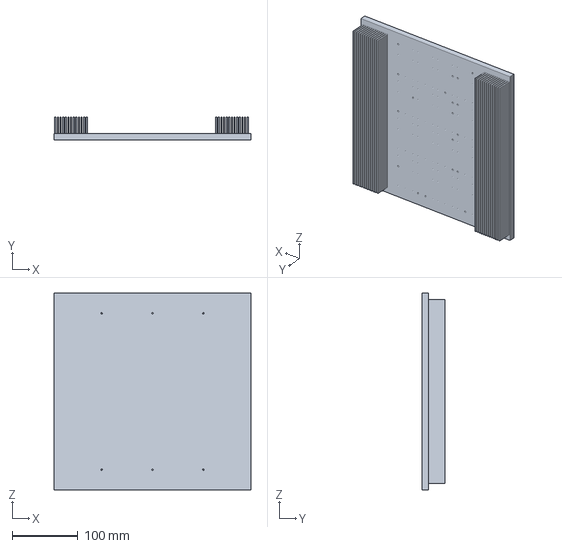
[picture p88: CAD file, 2026-10-09]
engineering/DESIGN/MECHANICAL/CAD/detail/parts/PA_heat_spreader_300_300_10_Al_6061__mac.step
300.0 x 35.0 x 300.0 mm
