herasymyuks/PLFM_RADAR-aeris/engineering/DESIGN/MECHANICAL/CAD/detail/parts/Window_gasket_EPDM_1_5_mm__ring_10_mm_.step

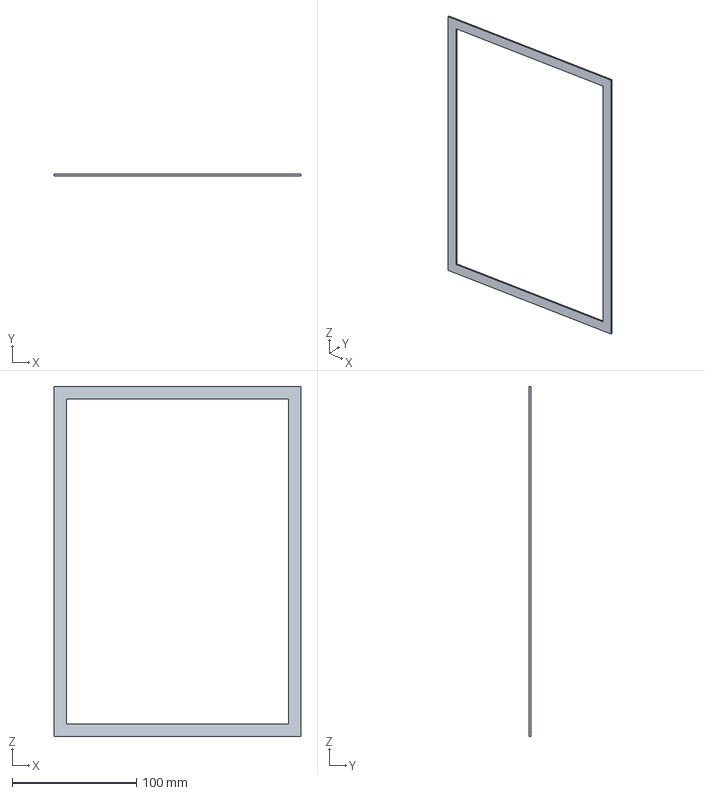
[picture p89: CAD file, 2026-10-09]
engineering/DESIGN/MECHANICAL/CAD/detail/parts/Window_gasket_EPDM_1_5_mm__ring_10_mm_.step
199.0 x 1.50 x 282.0 mm
