herasymyuks/PLFM_RADAR-aeris/engineering/DESIGN/MECHANICAL/CAD/detail/parts/Front_plate_2_5_mm_Al_with_radome_window.step

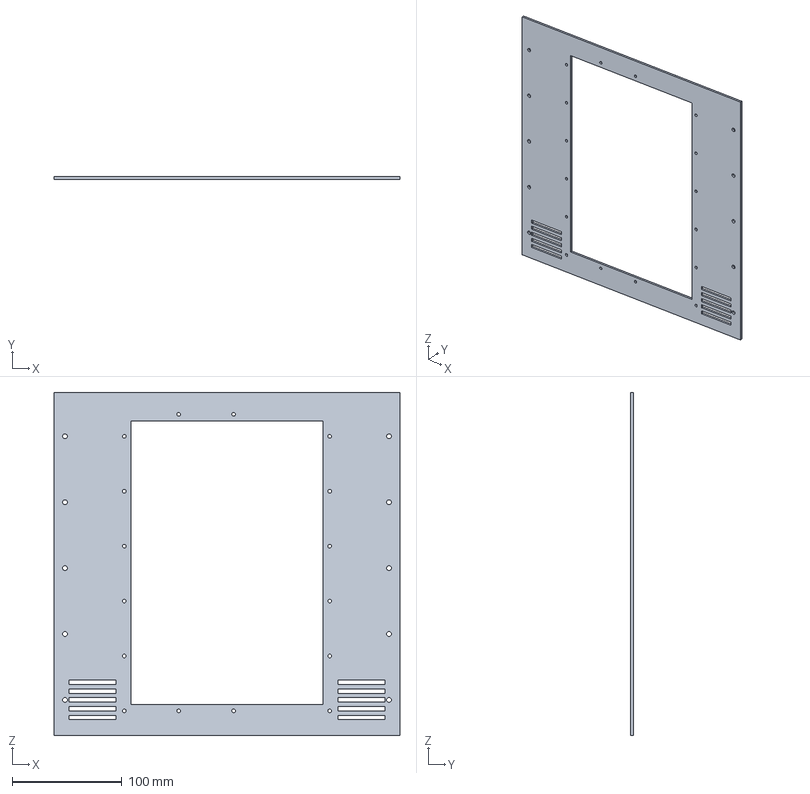
[picture p90: CAD file, 2026-10-09]
engineering/DESIGN/MECHANICAL/CAD/detail/parts/Front_plate_2_5_mm_Al_with_radome_window.step
315.0 x 2.50 x 312.5 mm
