herasymyuks/PLFM_RADAR-aeris/engineering/DESIGN/MECHANICAL/CAD/detail/parts/Window_clamp_frame_2_mm_Al__14_mm_wide.step

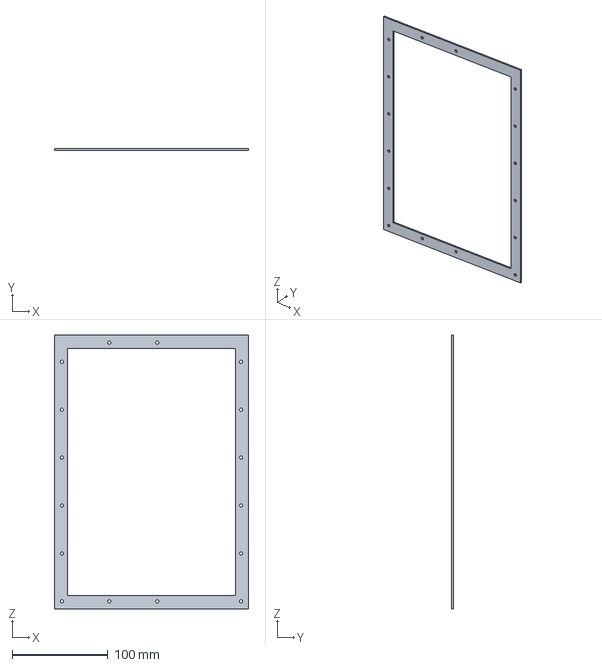
[picture p91: CAD file, 2026-10-09]
engineering/DESIGN/MECHANICAL/CAD/detail/parts/Window_clamp_frame_2_mm_Al__14_mm_wide.step
203.0 x 2.00 x 286.0 mm
