herasymyuks/PLFM_RADAR-aeris/engineering/DESIGN/MECHANICAL/CAD/detail/parts/Turntable_plate_Ø340_8_Al__8_M6_to_the_h.step

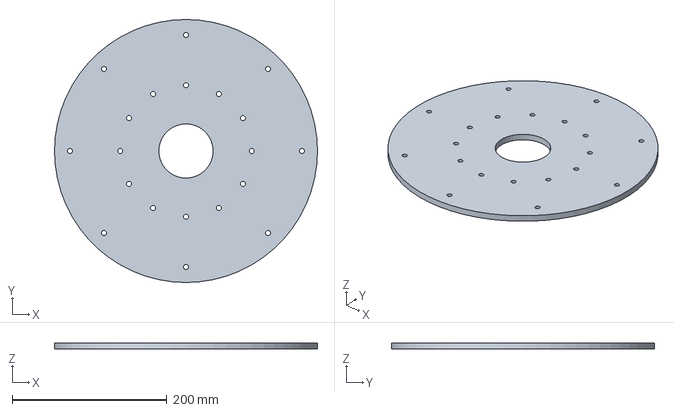
[picture p92: CAD file, 2026-10-09]
engineering/DESIGN/MECHANICAL/CAD/detail/parts/Turntable_plate_Ø340_8_Al__8_M6_to_the_h.step
340.0 x 340.0 x 8.00 mm
