herasymyuks/PLFM_RADAR-aeris/engineering/DESIGN/MECHANICAL/CAD/detail/parts/Synth_carrier_rail_bottom_U15_12_1_5_Al_.step

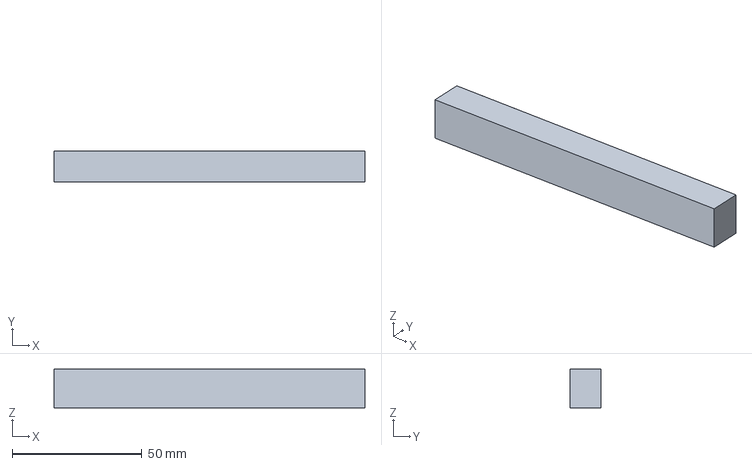
[picture p93: CAD file, 2026-10-09]
engineering/DESIGN/MECHANICAL/CAD/detail/parts/Synth_carrier_rail_bottom_U15_12_1_5_Al_.step
120.0 x 12.0 x 15.0 mm
