herasymyuks/PLFM_RADAR-aeris/engineering/DESIGN/MECHANICAL/CAD/detail/parts/Radome_window_PTFE_2_mm__outside_the_fro.step

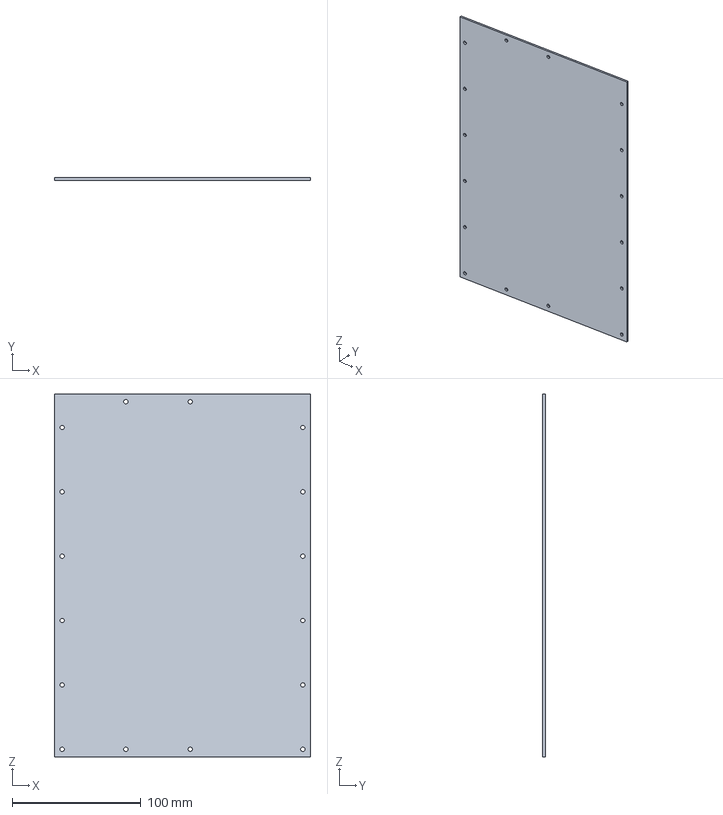
[picture p94: CAD file, 2026-10-09]
engineering/DESIGN/MECHANICAL/CAD/detail/parts/Radome_window_PTFE_2_mm__outside_the_fro.step
199.0 x 2.00 x 282.0 mm
