herasymyuks/PLFM_RADAR-aeris/engineering/DESIGN/MECHANICAL/CAD/detail/parts/Tray___base___sides___rear__2_5_mm_Al_57.step

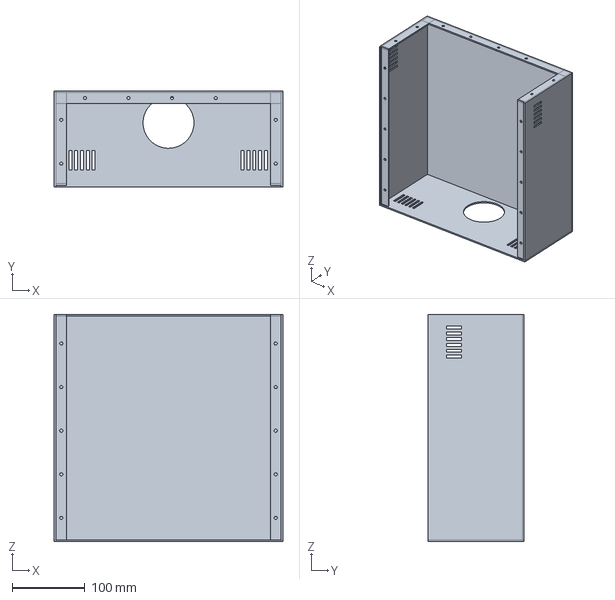
[picture p95: CAD file, 2026-10-09]
engineering/DESIGN/MECHANICAL/CAD/detail/parts/Tray___base___sides___rear__2_5_mm_Al_57.step
315.0 x 132.6 x 312.5 mm
