herasymyuks/PLFM_RADAR-aeris/engineering/DESIGN/MECHANICAL/CAD/detail/parts/Motor_bracket_80_80_3_Al_with_slotted_be.step

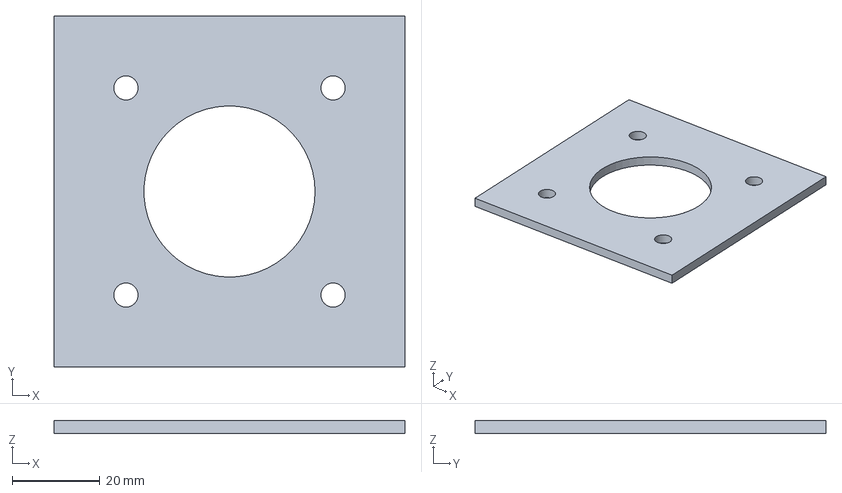
[picture p96: CAD file, 2026-10-09]
engineering/DESIGN/MECHANICAL/CAD/detail/parts/Motor_bracket_80_80_3_Al_with_slotted_be.step
80.0 x 80.0 x 3.00 mm
