herasymyuks/PLFM_RADAR-aeris/engineering/DESIGN/MECHANICAL/CAD/detail/parts/Lid_2_5_mm_Al_with_exhaust_slots.step

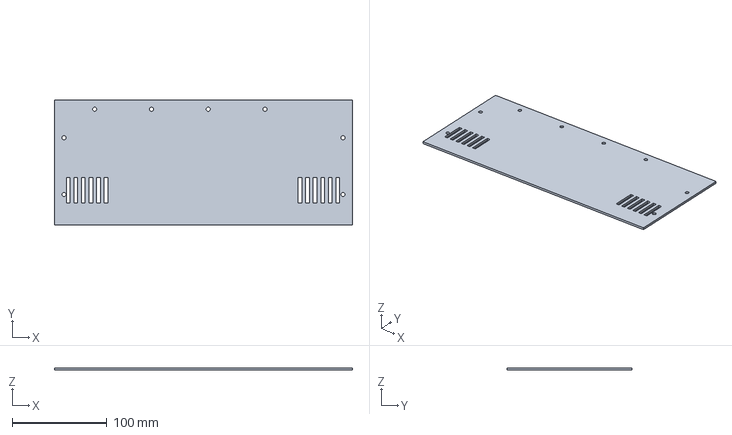
[picture p97: CAD file, 2026-10-09]
engineering/DESIGN/MECHANICAL/CAD/detail/parts/Lid_2_5_mm_Al_with_exhaust_slots.step
315.0 x 132.6 x 2.50 mm
