herasymyuks/PLFM_RADAR-aeris/engineering/DESIGN/MECHANICAL/CAD/detail/parts/Pedestal_housing_360_360_125_folded_2_5_.step

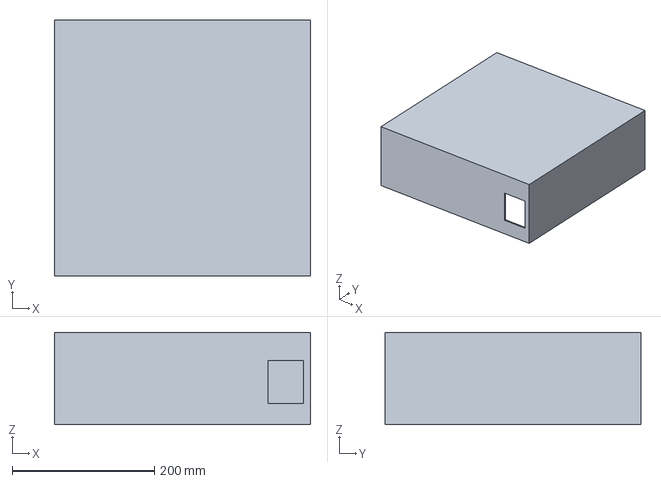
[picture p98: CAD file, 2026-10-09]
engineering/DESIGN/MECHANICAL/CAD/detail/parts/Pedestal_housing_360_360_125_folded_2_5_.step
360.0 x 360.0 x 130.0 mm
