herasymyuks/PLFM_RADAR-aeris/engineering/DESIGN/MECHANICAL/CAD/detail/parts/Stepper_driver_TB6600_on_DIN_rail.step

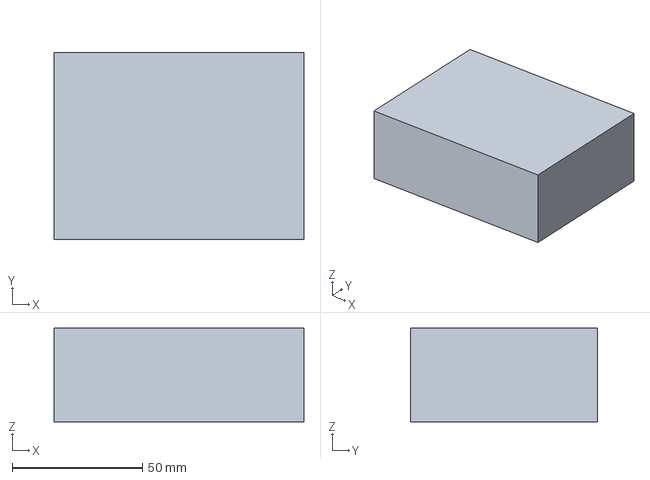
[picture p99: CAD file, 2026-10-09]
engineering/DESIGN/MECHANICAL/CAD/detail/parts/Stepper_driver_TB6600_on_DIN_rail.step
96.0 x 72.0 x 36.0 mm
