herasymyuks/PLFM_RADAR-aeris/engineering/DESIGN/MECHANICAL/CAD/detail/parts/Cable_entry_gland_plate_100_100_2_Al_und.step

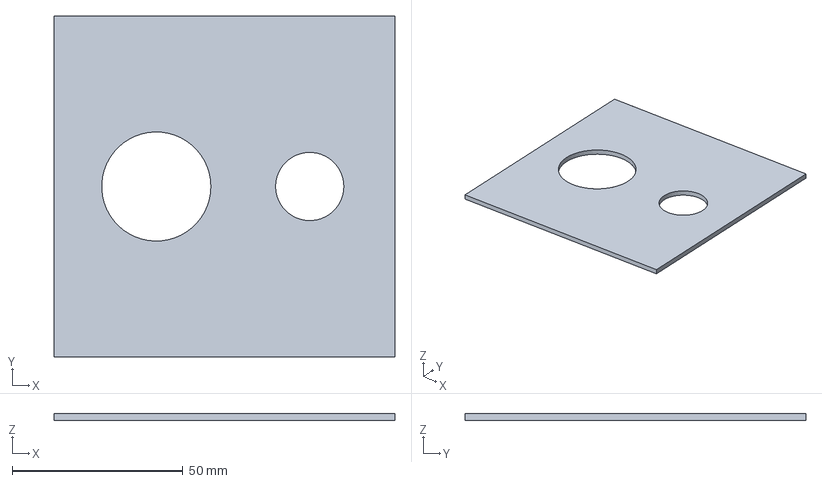
[picture p100: CAD file, 2026-10-09]
engineering/DESIGN/MECHANICAL/CAD/detail/parts/Cable_entry_gland_plate_100_100_2_Al_und.step
100.0 x 100.0 x 2.00 mm
