herasymyuks/PLFM_RADAR-aeris/manual/FIGURE_LOG.md

# Figure log

Generated 2026-10-09 by `tools/gen_figure_log.py` — 69 figures, 0 missing files. Status is taken from the caption text; origin from the drawing register / path.

| # | Ch. | Caption (start) | Path | kB | Status | Origin |
|---|---|---|---|---|---|---|
| 1 | 01 | F1.1 — System block diagram SYS-01, all subsystems with status legend — SOURCE-DERIVED; antenna, host PC, 22 V supply and off-board modules  | `engineering/SYSTEM/block_diagrams/system_block_diagram.png` | 2290 | SOURCE-DERIVED | SYS-01 |
| 2 | 01 | F1.2 — Original functional block diagram RADAR_V6, draw.io 29.6.1 export — ORIGINAL PROJECT FILE, upstream authorship, not dimensioned (sour | `2_Functional Diagram & Interconnection Matrices/RADAR_V6.jpg` | 182 | ORIGINAL PROJECT FILE | original project file |
| 3 | 01 | F1.3 — Prototype antenna array photograph — ORIGINAL PROJECT FILE, undimensioned, not used for any dimension in this manual (source: 8_Utils | `8_Utils/Antenna_Array.jpg` | 88 | ORIGINAL PROJECT FILE | original project file |
| 4 | 01 | F1.3b — Prototype electronics photograph — ORIGINAL PROJECT FILE, undimensioned, not used for any dimension in this manual (source: 8_Utils/ | `8_Utils/0044.jpg` | 122 | ORIGINAL PROJECT FILE | original project file |
| 5 | 02 | F2.1 — Signal and data flow SYS-03: reference and clock tree, TX chain, RX chain, control paths; solid = confirmed, dashed = unverified, dot | `engineering/SYSTEM/data_flow/signal_and_data_flow.png` | 1699 | SOURCE-DERIVED | SYS-03 |
| 6 | 02 | F2.2 — FPGA signal-processing pipeline as written in the original RTL (SD-02): blue = defined and instantiated, orange = documented defect o | `engineering/SOFTWARE_DIAGRAMS/FPGA/fpga_data_pipeline.png` | 1475 | PARTIAL | SD-02 |
| 7 | 02 | F2.3 — End-to-end signal and control data flow SD-07: antenna → RF → ADC → FPGA → host and host → STM32 → clock/LO/beamformer → FPGA; solid  | `engineering/SOFTWARE_DIAGRAMS/DATA_FLOW/end_to_end_data_flow.png` | 1476 | PARTIAL | SD-07 |
| 8 | 03 | F3.1 — Hardware interconnection diagram SYS-02: one node per board/module, one edge per connector/cable with connector IDs, pin numbers wher | `engineering/SYSTEM/interfaces/hardware_interconnection.png` | 1084 | SOURCE-DERIVED | SYS-02 |
| 9 | 03 | F3.2 — Power distribution diagram ELEC-PWR-01 / SYS-04: every Power Board rail with regulator, feedback divider, source rail, enable net and | `engineering/ELECTRICAL/power_distribution/power_distribution.png` | 2159 | SOURCE-DERIVED | ELEC-PWR-01 |
| 10 | 04 | F4.1 — Main Board schematic sheet 1 "POWER SUPPLIES": 189 parts, 33 nets (status: SOURCE-DERIVED; source: engineering/ELECTRICAL/schematics/ | `engineering/ELECTRICAL/schematics/MAIN_BOARD/png/MAIN_BOARD_schematic_sheet1.png` | 278 | SOURCE-DERIVED | generated (unregistered) |
| 11 | 04 | F4.2 — Main Board schematic sheet 2 "Digital (FPGA+microcontroller)": 196 parts, 181 nets (status: SOURCE-DERIVED; source: engineering/ELECT | `engineering/ELECTRICAL/schematics/MAIN_BOARD/png/MAIN_BOARD_schematic_sheet2.png` | 815 | SOURCE-DERIVED | generated (unregistered) |
| 12 | 04 | F4.3 — Main Board schematic sheet 3 "RF": 1 304 parts, 356 nets — ADAR1000 ×4, ADTR1107 ×16, mixers, switches, 32 element SMAs (status: SOUR | `engineering/ELECTRICAL/schematics/MAIN_BOARD/png/MAIN_BOARD_schematic_sheet3.png` | 1627 | SOURCE-DERIVED | generated (unregistered) |
| 13 | 04 | F4.4 — Main Board schematic sheet 4 "RF POWER AMPLIFIER BIAS": DAC5578 ×2, OPA4703 ×4, INA241A3 ×16, VG outputs X_1…X_16, sense inputs X3/X3 | `engineering/ELECTRICAL/schematics/MAIN_BOARD/png/MAIN_BOARD_schematic_sheet4.png` | 659 | SOURCE-DERIVED | generated (unregistered) |
| 14 | 04 | F4.5a — Main Board top composite (F.Cu + F.SilkS + Edge.Cuts) of the KiCad conversion of RADAR_Main_Board.brd, 260 × 300 mm (status: SOURCE- | `manual/figures/MAIN_BOARD_top_composite.png` | 1286 | SOURCE-DERIVED | rendered for the manual |
| 15 | 04 | F4.5b — Main Board bottom composite, mirrored (B.Cu + B.SilkS + Edge.Cuts) (status: SOURCE-DERIVED; source: engineering/PCB/MAIN_BOARD/svg/M | `manual/figures/MAIN_BOARD_bottom_composite_mirrored.png` | 517 | SOURCE-DERIVED | rendered for the manual |
| 16 | 04 | F4.6a — Main Board 3-D render, top, KiCad conversion; no component models (STEP is board-only) (status: SOURCE-DERIVED; source: engineering/ | `engineering/PCB/MAIN_BOARD/3d/MAIN_BOARD_render_top.png` | 843 | SOURCE-DERIVED | generated (unregistered) |
| 17 | 04 | F4.6b — Main Board BETA board, isometric render after the +3V3_FT cluster placement and routing (status: BETA; source: beta/pcb/MAIN_BOARD/e | `beta/pcb/MAIN_BOARD/exports/3d/MAIN_BOARD_render_isometric.png` | 1873 | BETA | generated (unregistered) |
| 18 | 04 | F4.7 — Main Board rev. B proposal, isometric render: USB-C receptacle J_USB3 on the left edge next to U6 (FT601), ESD arrays, crystal and de | `beta/pcb/MAIN_BOARD_REVB/exports/3d/MAIN_BOARD_REVB_render_isometric.png` | 1883 | BETA | generated (unregistered) |
| 19 | 05 | F5.1 — Power Board schematic, single sheet: 21 × TPS562208 buck stages, 6 × ADM7151 and 2 × TPS7A8300 LDOs, 5 × LM2662 inverters, 34 rail ou | `engineering/ELECTRICAL/schematics/POWER_SUPPLY/png/POWER_SUPPLY_schematic_sheet1.png` | 682 | SOURCE-DERIVED | generated (unregistered) |
| 20 | 05 | F5.2a — Power Board top composite (F.Cu + F.SilkS + Edge.Cuts) of the KiCad conversion of PowerBoard.brd, 280 × 300 mm; 132 parts parked out | `manual/figures/POWER_SUPPLY_top_composite.png` | 337 | SOURCE-DERIVED | rendered for the manual |
| 21 | 05 | F5.2b — Power Board bottom composite, mirrored (B.Cu + B.SilkS + Edge.Cuts) (status: SOURCE-DERIVED; source: engineering/PCB/POWER_SUPPLY/sv | `manual/figures/POWER_SUPPLY_bottom_composite_mirrored.png` | 123 | SOURCE-DERIVED | rendered for the manual |
| 22 | 05 | F5.3a — Power Board 3-D render, top, KiCad conversion of the source layout (unplaced parts outside the outline) (status: SOURCE-DERIVED; sou | `engineering/PCB/POWER_SUPPLY/3d/POWER_SUPPLY_render_top.png` | 334 | SOURCE-DERIVED | generated (unregistered) |
| 23 | 05 | F5.3b — Power Board BETA board after scripted placement, two Freerouting passes, bridges and GND stitching; 89 connections still open (statu | `beta/pcb/POWER_SUPPLY/exports/3d/POWER_SUPPLY_render_isometric.png` | 1607 | BETA | generated (unregistered) |
| 24 | 06 | F6.1 — Frequency Synthesizer schematic, single sheet: AD9523 clock generator, 2 × ADF4382 LO synthesizers, OCXO/VCXO, 11 SMA outputs, contro | `engineering/ELECTRICAL/schematics/FREQUENCY_SYNTHESIZER/png/FREQUENCY_SYNTHESIZER_schematic_sheet1.png` | 1074 | SOURCE-DERIVED | generated (unregistered) |
| 25 | 06 | F6.2a — Frequency Synthesizer top composite (F.Cu + F.SilkS + Edge.Cuts), 100 × 100 mm (status: SOURCE-DERIVED; source: engineering/PCB/FREQ | `manual/figures/FREQUENCY_SYNTHESIZER_top_composite.png` | 726 | SOURCE-DERIVED | rendered for the manual |
| 26 | 06 | F6.2b — Frequency Synthesizer bottom composite, mirrored (B.Cu + B.SilkS + Edge.Cuts); the AD9523_OUT8/9 pairs run on B.Cu (status: SOURCE-D | `manual/figures/FREQUENCY_SYNTHESIZER_bottom_composite_mirrored.png` | 444 | SOURCE-DERIVED | rendered for the manual |
| 27 | 06 | F6.3a — Frequency Synthesizer 3-D render, top, KiCad conversion; no component models (status: SOURCE-DERIVED; source: engineering/PCB/FREQUE | `engineering/PCB/FREQUENCY_SYNTHESIZER/3d/FREQUENCY_SYNTHESIZER_render_top.png` | 744 | SOURCE-DERIVED | generated (unregistered) |
| 28 | 06 | F6.3b — Frequency Synthesizer BETA board, isometric render (silkscreen nudged, copper identical to the source) (status: BETA; source: beta/p | `beta/pcb/FREQUENCY_SYNTHESIZER/exports/3d/FREQUENCY_SYNTHESIZER_render_isometric.png` | 1884 | BETA | generated (unregistered) |
| 29 | 07 | F7.1 — RF PA schematic, single sheet: QPA2962, SMA in/out, VG and VD/VIN_M decoupling, 5 mΩ sense shunt, 22 V terminal (status: SOURCE-DERIV | `engineering/ELECTRICAL/schematics/RF_PA/png/RF_PA_schematic_sheet1.png` | 244 | SOURCE-DERIVED | generated (unregistered) |
| 30 | 07 | F7.2a — RF PA top composite (F.Cu + F.SilkS + Edge.Cuts), 35 × 60 mm: 0.204 mm RF microstrips J1 → U$1 → J2 and the thermal-via field under  | `manual/figures/RF_PA_top_composite.png` | 482 | SOURCE-DERIVED | rendered for the manual |
| 31 | 07 | F7.2b — RF PA bottom composite, mirrored (B.Cu + B.SilkS + Edge.Cuts) (status: SOURCE-DERIVED; source: engineering/PCB/RF_PA/svg/RF_PA_botto | `manual/figures/RF_PA_bottom_composite_mirrored.png` | 299 | SOURCE-DERIVED | rendered for the manual |
| 32 | 07 | F7.3a — RF PA 3-D render, top, KiCad conversion; no component models (status: SOURCE-DERIVED; source: engineering/PCB/RF_PA/3d/RF_PA_render_ | `engineering/PCB/RF_PA/3d/RF_PA_render_top.png` | 415 | SOURCE-DERIVED | generated (unregistered) |
| 33 | 07 | F7.3b — RF PA BETA board, isometric render (GND strap and paddle polygon net added, RF copper unchanged) (status: BETA; source: beta/pcb/RF_ | `beta/pcb/RF_PA/exports/3d/RF_PA_render_isometric.png` | 1275 | BETA | generated (unregistered) |
| 34 | 08 | F8.1 — DSN-ANT-01 panel layout drawing: 16 rows × 8 patches, feed network, 2.92 mm connector positions, 165 × 248 mm outline with title bloc | `engineering/DESIGN/ANTENNA/aeris10_patch_array_layout.png` | 167 | PROPOSED DESIGN | generated (unregistered) |
| 35 | 08 | F8.2 — DSN-ANT-01 KiCad 3-D render of the patch panel, top side (status: PROPOSED DESIGN; source: engineering/DESIGN/ANTENNA/kicad_exports/a | `engineering/DESIGN/ANTENNA/kicad_exports/aeris10_patch_array_render_top.png` | 292 | PROPOSED DESIGN | DSN-ANT-01 |
| 36 | 08 | F8.3 — One-row |S11| vs frequency from openEMS (L_SCALE 1.0): comb of narrow resonances, −18.0 dB at 10.5 GHz, ≈ 128 MHz contiguous −10 dB b | `engineering/DESIGN/ANTENNA/simulation/s11_row.png` | 30 | PROPOSED DESIGN | DSN-ANT-01-SIM |
| 37 | 08 | F8.4 — Three-row mutual coupling S12/S32 and centre-row S22 vs frequency, 9–12 GHz, from openEMS (status: PROPOSED DESIGN (simulated); sourc | `manual/figures/antenna_coupling_3rows.png` | 224 | PROPOSED DESIGN | rendered for the manual |
| 38 | 09 | F9.2 — Main Board rev. B isometric render with the FT601 cluster and USB-C receptacle placed at the left board edge; the 32-bit FIFO bus is  | `beta/pcb/MAIN_BOARD_REVB/exports/3d/MAIN_BOARD_REVB_render_isometric.png` | 1883 | BETA | generated (unregistered) |
| 39 | 09 | F9.1 — DSN-PSU-01 block schematic: 2-phase synchronous boost 12–17 V → 22 V, LM5069 hot-swap enable from EN/DIS_RFPA_VDD, 16 high-side pulse | `engineering/DESIGN/ELECTRICAL/PA_SUPPLY_22V/DSN-PSU-01_block_schematic.png` | 160 | PROPOSED DESIGN | generated (unregistered) |
| 40 | 10 | F10.10a — Plan view of the four PCB outlines with holes, scale 1:1 on the native SVG, placement for comparison only (MECH-PLAN-01) — SOURCE- | `engineering/MECHANICAL/CAD/pcb_set_plan_view.png` | 87 | SOURCE-DERIVED | MECH-PLAN-01 |
| 41 | 10 | F10.10b — Conceptual exploded view of the electronics set; board outlines are verified, the vertical arrangement, spacing, antenna panel and | `engineering/ASSEMBLY/EXPLODED_VIEWS/aeris10_exploded_conceptual.png` | 242 | CONCEPTUAL | ASM-EXP-01 |
| 42 | 10 | F10.1 — Head plan section at mid height (X–Y), DSN-MECH-01 Rev A, scale 1:1 on the native SVG — PROPOSED DESIGN, D-07…D-13 (source: engineer | `engineering/DESIGN/MECHANICAL/drawings/png/DSN-MECH-01_head_plan_section.png` | 165 | PROPOSED DESIGN | DSN-MECH-01 |
| 43 | 10 | F10.2 — Head front elevation (X–Z) with radome window and intake ducts, DSN-MECH-02 Rev A — PROPOSED DESIGN, D-07…D-13 (source: engineering/ | `engineering/DESIGN/MECHANICAL/drawings/png/DSN-MECH-02_head_front_elevation.png` | 102 | PROPOSED DESIGN | DSN-MECH-02 |
| 44 | 10 | F10.3 — Head side section including the pedestal, DSN-MECH-03 Rev A — PROPOSED DESIGN, D-07…D-13 (source: engineering/DESIGN/MECHANICAL/draw | `engineering/DESIGN/MECHANICAL/drawings/png/DSN-MECH-03_head_side_section.png` | 126 | PROPOSED DESIGN | DSN-MECH-03 |
| 45 | 10 | F10.4 — Internal layout, each tier seen from the rear, with connector positions: tier 1 PA heat spreader with PA1…PA16 and fin fields, tier  | `engineering/DESIGN/MECHANICAL/drawings/png/DSN-MECH-04_internal_layout_rear.png` | 252 | PROPOSED DESIGN | DSN-MECH-04 |
| 46 | 10 | F10.5 — Pedestal plan: turntable, slewing bearing, ring pulley, NEMA 23 with motor bracket, slip ring, DSN-MECH-05 Rev A — PROPOSED DESIGN,  | `engineering/DESIGN/MECHANICAL/drawings/png/DSN-MECH-05_pedestal_plan.png` | 297 | PROPOSED DESIGN | DSN-MECH-05 |
| 47 | 10 | F10.6 — Sheet-metal flat patterns with bend lines for the tray, front plate and lid (2.5 mm Al 5754), DSN-MECH-06 Rev A; bend allowance per  | `engineering/DESIGN/MECHANICAL/drawings/png/DSN-MECH-06_sheet_metal_flat_patterns.png` | 184 | PROPOSED DESIGN | DSN-MECH-06 |
| 48 | 10 | F10.7 — Assembly section with fastener balloons (balloon numbers = part # of the mechanical parts list), DSN-MECH-07 Rev A — PROPOSED DESIGN | `engineering/DESIGN/MECHANICAL/drawings/png/DSN-MECH-07_assembly_section_fasteners.png` | 393 | PROPOSED DESIGN | DSN-MECH-07 |
| 49 | 10 | F10.8a — Detail model, X-ray front isometric: tray, front plate with window, PA plate, carrier rails, boards — PROPOSED DESIGN, DSN-MECH-3D- | `engineering/DESIGN/MECHANICAL/CAD/detail/aeris10_detail_xray_front_iso.png` | 1383 | PROPOSED DESIGN | DSN-MECH-3D-DETAIL |
| 50 | 10 | F10.8b — Detail model, rear isometric: lid, rear wall, pedestal housing, motor bracket — PROPOSED DESIGN, DSN-MECH-3D-DETAIL (source: engine | `engineering/DESIGN/MECHANICAL/CAD/detail/aeris10_detail_iso_rear.png` | 1092 | PROPOSED DESIGN | DSN-MECH-3D-DETAIL |
| 51 | 10 | F10.8c — Parametric head model, X-ray isometric with board envelopes (component heights ASSUMED 15 mm top / 4 mm bottom, D-07) — PROPOSED DE | `engineering/DESIGN/MECHANICAL/CAD/aeris10_head_xray_iso.png` | 770 | PROPOSED DESIGN | DSN-MECH-3D |
| 52 | 10 | F10.9a — PA heat-spreader temperature map, case B (drain gated per chirp, 4.24 W per PA): T min 55.3 °C … max 64.3 °C at 45 °C ambient; whit | `manual/figures/thermal_map_B-gated-drain.png` | 141 | PROPOSED DESIGN | rendered for the manual |
| 53 | 10 | F10.9b — PA heat-spreader temperature map, case A (continuous drain bias, 37.0 W per PA): plate max 213 °C, PA base > 287 °C — shown only to | `manual/figures/thermal_map_A-continuous-bias.png` | 143 | PROPOSED DESIGN | rendered for the manual |
| 54 | 11 | F11.1 — FPGA RTL module hierarchy of the original 9_Firmware/9_2_FPGA (SD-01): 19 defined, 5 missing, 3 primitives, 9 unused — SOURCE-DERIVE | `engineering/SOFTWARE_DIAGRAMS/FPGA/fpga_module_hierarchy.png` | 552 | SOURCE-DERIVED | SD-01 |
| 55 | 11 | F11.2 — FPGA signal-processing pipeline as written in the original RTL (SD-02) — PARTIAL; 5 instantiated-but-missing modules, placeholders a | `engineering/SOFTWARE_DIAGRAMS/FPGA/fpga_data_pipeline.png` | 1475 | PARTIAL | SD-02 |
| 56 | 11 | F11.1b — FPGA RTL module hierarchy of beta/fpga/rtl: 43 defined, 2 missing (the deliberate FFT IP placeholders), 0 primitives (UNISIM stand- | `manual/figures/fpga_beta/fpga_module_hierarchy.png` | 646 | SOURCE-DERIVED | SD-01 |
| 57 | 12 | F12.1 — STM32 firmware architecture: main.cpp application sequence, driver families, peripheral handles; dashed red = HAL/CMSIS/startup/link | `engineering/SOFTWARE_DIAGRAMS/STM32/stm32_firmware_architecture.png` | 2750 | PARTIAL | SD-03 |
| 58 | 12 | F12.2 — USB CDC flow host ↔ STM32 as found in the original sources: start flag, zero-padding defect C5, settings packet, unbound receive cal | `engineering/SOFTWARE_DIAGRAMS/STM32/stm32_usb_cdc_flow.png` | 873 | PARTIAL | SD-04 |
| 59 | 13 | F13.1 — Python GUI modules: imports and definitions of the nine upstream scripts, classified stdlib / third-party / local (SD-05; auto-gener | `engineering/SOFTWARE_DIAGRAMS/PYTHON/python_gui_modules.png` | 1566 | SOURCE-DERIVED | SD-05 |
| 60 | 13 | F13.2 — Python GUI runtime architecture as found in GUI_V5.py / GUI_V6_Demo.py: threads, queues, parsers, processor, Tk timer; clustering/tr | `engineering/SOFTWARE_DIAGRAMS/PYTHON/python_gui_architecture.png` | 1269 | SOURCE-DERIVED | SD-06 |
| 61 | 13 | F13.3 — Demo-mode plot area of the beta GUI after 5 simulated bridge frames: left range-Doppler map (dB) with CFAR detections (red circles), | `manual/figures/gui_demo_plots.png` | 78 | BETA | rendered for the manual |
| 62 | 15 | F15.1 — Conceptual exploded view of the electronics set used as the orientation reference for phases A–C; board outlines verified from the . | `engineering/ASSEMBLY/EXPLODED_VIEWS/aeris10_exploded_conceptual.png` | 242 | CONCEPTUAL | ASM-EXP-01 |
| 63 | 15 | F15.2 — Main Board, top assembly drawing (component placement, references), page 1 of engineering/PCB/MAIN_BOARD/drawings/MAIN_BOARD_assembl | `manual/figures/MAIN_BOARD_assembly_top-1.png` | 158 | PARTIAL | rendered for the manual |
| 64 | 15 | F15.3 — Power Supply Board, top assembly drawing, page 1; layout state PARTIAL (309 airwires in the EAGLE source) — SOURCE-DERIVED / PARTIAL | `manual/figures/POWER_SUPPLY_assembly_top-1.png` | 35 | PARTIAL | rendered for the manual |
| 65 | 15 | F15.4 — Frequency Synthesizer Board, top assembly drawing, page 1 — SOURCE-DERIVED (source: engineering/PCB/FREQUENCY_SYNTHESIZER/drawings/F | `manual/figures/FREQUENCY_SYNTHESIZER_assembly_top-1.png` | 173 | SOURCE-DERIVED | rendered for the manual |
| 66 | 15 | F15.5 — RF PA board, top assembly drawing, page 1 (one of 16 identical boards) — SOURCE-DERIVED (source: engineering/PCB/RF_PA/drawings/RF_P | `manual/figures/RF_PA_assembly_top-1.png` | 58 | SOURCE-DERIVED | rendered for the manual |
| 67 | 15 | F15.6 — Assembly section with fastener balloons: balloon number = part # of the mechanical parts list; defines which fastener goes where in  | `engineering/DESIGN/MECHANICAL/drawings/png/DSN-MECH-07_assembly_section_fasteners.png` | 393 | PROPOSED DESIGN | DSN-MECH-07 |
| 68 | 15 | F15.7 — Sheet-metal flat patterns (tray, front plate, lid) that the fabricator folds before Step 15.5; bend lines and allowance per the gene | `engineering/DESIGN/MECHANICAL/drawings/png/DSN-MECH-06_sheet_metal_flat_patterns.png` | 184 | PROPOSED DESIGN | DSN-MECH-06 |
| 69 | 15 | F15.8 — Internal layout per tier, rear view, with every connector reference (J, X, JP, SV) at its P&P position — the routing reference for S | `engineering/DESIGN/MECHANICAL/drawings/png/DSN-MECH-04_internal_layout_rear.png` | 252 | PROPOSED DESIGN | DSN-MECH-04 |

## By status

| Status | Figures |
|---|---|
| BETA | 7 |
| CONCEPTUAL | 2 |
| ORIGINAL PROJECT FILE | 3 |
| PARTIAL | 7 |
| PROPOSED DESIGN | 20 |
| SOURCE-DERIVED | 30 |
