herasymyuks/PLFM_RADAR-aeris/manual/ASSET_INDEX.md

# Manual asset index

Generated 2026-10-09 by `tools/gen_manual_asset_index.py` — 225 candidate figures. Use the register ID/status to caption each figure honestly (SOURCE-DERIVED / PARTIAL / CONCEPTUAL / PROPOSED DESIGN / BETA / original project file). Per-layer PCB plots, drill maps and thermal maps are omitted here but exist under `engineering/PCB/<BOARD>/svg|drawings|drill` and `engineering/DESIGN/CALCS`.

| Path | Type | kB | Register ID | Status | Proposed caption |
|---|---|---|---|---|---|
| `4_Schematics and Boards Layout/4_4_Board Stack-up/Stack_Hybrid.png` | png | 58 | — | source file | Stack Hybrid |
| `5_Simulations/E_plane_Kaiser25dB_like.png` | png | 56 | — | source file | E plane Kaiser25dB like |
| `5_Simulations/E_plane_cut.png` | png | 63 | — | source file | E plane cut |
| `5_Simulations/Fencing/via_fence_setup_pitch.png` | png | 87 | — | source file | via fence setup pitch |
| `5_Simulations/Fencing/via_fence_setup_pitch_offset.png` | png | 93 | — | source file | via fence setup pitch offset |
| `5_Simulations/H_plane_Kaiser25dB_like.png` | png | 60 | — | source file | H plane Kaiser25dB like |
| `5_Simulations/H_plane_cut.png` | png | 60 | — | source file | H plane cut |
| `5_Simulations/Heatmap_Kaiser25dB_like.png` | png | 78 | — | source file | Heatmap Kaiser25dB like |
| `5_Simulations/Sim_BPF_Te_100um/Sim_BPF_Te_100um.pdf` | pdf | 2 | — | source file | Sim BPF Te 100um |
| `5_Simulations/array_pattern_heatmap.png` | png | 77 | — | source file | array pattern heatmap |
| `8_Utils/0044.jpg` | jpg | 122 | — | source file | 0044 |
| `8_Utils/3fb1dabf-2c6d-4b5d-b471-48bc461ce914.jpg` | jpg | 262 | — | source file | 3fb1dabf 2c6d 4b5d b471 48bc461ce914 |
| `8_Utils/Antenna_Array.jpg` | jpg | 88 | — | source file | Antenna Array |
| `8_Utils/GUI.jpg` | jpg | 99 | — | source file | GUI |
| `8_Utils/RADAR_V6.jpg` | jpg | 182 | — | source file | RADAR V6 |
| `8_Utils/b79a6fe3-5abf-473d-b3e2-178e6a9cf4da - Copie.jpg` | jpg | 149 | — | source file | b79a6fe3 5abf 473d b3e2 178e6a9cf4da Copie |
| `beta/pcb/FREQUENCY_SYNTHESIZER/exports/3d/FREQUENCY_SYNTHESIZER_render_bottom.png` | png | 464 | — | GENERATED (unregistered) | FREQUENCY SYNTHESIZER render bottom |
| `beta/pcb/FREQUENCY_SYNTHESIZER/exports/3d/FREQUENCY_SYNTHESIZER_render_isometric.png` | png | 1881 | — | GENERATED (unregistered) | FREQUENCY SYNTHESIZER render isometric |
| `beta/pcb/FREQUENCY_SYNTHESIZER/exports/3d/FREQUENCY_SYNTHESIZER_render_top.png` | png | 751 | — | GENERATED (unregistered) | FREQUENCY SYNTHESIZER render top |
| `beta/pcb/FREQUENCY_SYNTHESIZER/exports/drawings/FREQUENCY_SYNTHESIZER_assembly_bottom_mirrored.pdf` | pdf | 135 | — | GENERATED (unregistered) | FREQUENCY SYNTHESIZER assembly bottom mirrored |
| `beta/pcb/FREQUENCY_SYNTHESIZER/exports/drawings/FREQUENCY_SYNTHESIZER_assembly_top.pdf` | pdf | 301 | — | GENERATED (unregistered) | FREQUENCY SYNTHESIZER assembly top |
| `beta/pcb/FREQUENCY_SYNTHESIZER/exports/drawings/FREQUENCY_SYNTHESIZER_bottom_layer_mirrored.pdf` | pdf | 214 | — | GENERATED (unregistered) | FREQUENCY SYNTHESIZER bottom layer mirrored |
| `beta/pcb/FREQUENCY_SYNTHESIZER/exports/drawings/FREQUENCY_SYNTHESIZER_outline.pdf` | pdf | 145 | — | GENERATED (unregistered) | FREQUENCY SYNTHESIZER outline |
| `beta/pcb/FREQUENCY_SYNTHESIZER/exports/drawings/FREQUENCY_SYNTHESIZER_top_layer.pdf` | pdf | 280 | — | GENERATED (unregistered) | FREQUENCY SYNTHESIZER top layer |
| `beta/pcb/FREQUENCY_SYNTHESIZER/exports/svg/FREQUENCY_SYNTHESIZER-B_Cu.svg` | svg | 157 | — | GENERATED (unregistered) | FREQUENCY SYNTHESIZER B Cu |
| `beta/pcb/FREQUENCY_SYNTHESIZER/exports/svg/FREQUENCY_SYNTHESIZER-F_Cu.svg` | svg | 324 | — | GENERATED (unregistered) | FREQUENCY SYNTHESIZER F Cu |
| `beta/pcb/FREQUENCY_SYNTHESIZER/exports/svg/FREQUENCY_SYNTHESIZER_bottom_composite_mirrored.svg` | svg | 156 | — | GENERATED (unregistered) | FREQUENCY SYNTHESIZER bottom composite mirrored |
| `beta/pcb/FREQUENCY_SYNTHESIZER/exports/svg/FREQUENCY_SYNTHESIZER_top_composite.svg` | svg | 667 | — | GENERATED (unregistered) | FREQUENCY SYNTHESIZER top composite |
| `beta/pcb/MAIN_BOARD/exports/3d/MAIN_BOARD_render_bottom.png` | png | 431 | — | GENERATED (unregistered) | MAIN BOARD render bottom |
| `beta/pcb/MAIN_BOARD/exports/3d/MAIN_BOARD_render_isometric.png` | png | 1874 | — | GENERATED (unregistered) | MAIN BOARD render isometric |
| `beta/pcb/MAIN_BOARD/exports/3d/MAIN_BOARD_render_top.png` | png | 845 | — | GENERATED (unregistered) | MAIN BOARD render top |
| `beta/pcb/MAIN_BOARD/exports/drawings/MAIN_BOARD_assembly_bottom_mirrored.pdf` | pdf | 503 | — | GENERATED (unregistered) | MAIN BOARD assembly bottom mirrored |
| `beta/pcb/MAIN_BOARD/exports/drawings/MAIN_BOARD_assembly_top.pdf` | pdf | 1020 | — | GENERATED (unregistered) | MAIN BOARD assembly top |
| `beta/pcb/MAIN_BOARD/exports/drawings/MAIN_BOARD_bottom_layer_mirrored.pdf` | pdf | 785 | — | GENERATED (unregistered) | MAIN BOARD bottom layer mirrored |
| `beta/pcb/MAIN_BOARD/exports/drawings/MAIN_BOARD_outline.pdf` | pdf | 495 | — | GENERATED (unregistered) | MAIN BOARD outline |
| `beta/pcb/MAIN_BOARD/exports/drawings/MAIN_BOARD_top_layer.pdf` | pdf | 1175 | — | GENERATED (unregistered) | MAIN BOARD top layer |
| `beta/pcb/MAIN_BOARD/exports/svg/MAIN_BOARD-B_Cu.svg` | svg | 514 | — | GENERATED (unregistered) | MAIN BOARD B Cu |
| `beta/pcb/MAIN_BOARD/exports/svg/MAIN_BOARD-F_Cu.svg` | svg | 1815 | — | GENERATED (unregistered) | MAIN BOARD F Cu |
| `beta/pcb/MAIN_BOARD/exports/svg/MAIN_BOARD_bottom_composite_mirrored.svg` | svg | 526 | — | GENERATED (unregistered) | MAIN BOARD bottom composite mirrored |
| `beta/pcb/MAIN_BOARD/exports/svg/MAIN_BOARD_top_composite.svg` | svg | 3772 | — | GENERATED (unregistered) | MAIN BOARD top composite |
| `beta/pcb/POWER_SUPPLY/exports/3d/POWER_SUPPLY_render_bottom.png` | png | 292 | — | GENERATED (unregistered) | POWER SUPPLY render bottom |
| `beta/pcb/POWER_SUPPLY/exports/3d/POWER_SUPPLY_render_isometric.png` | png | 1608 | — | GENERATED (unregistered) | POWER SUPPLY render isometric |
| `beta/pcb/POWER_SUPPLY/exports/3d/POWER_SUPPLY_render_top.png` | png | 489 | — | GENERATED (unregistered) | POWER SUPPLY render top |
| `beta/pcb/POWER_SUPPLY/exports/drawings/POWER_SUPPLY_assembly_bottom_mirrored.pdf` | pdf | 211 | — | GENERATED (unregistered) | POWER SUPPLY assembly bottom mirrored |
| `beta/pcb/POWER_SUPPLY/exports/drawings/POWER_SUPPLY_assembly_top.pdf` | pdf | 379 | — | GENERATED (unregistered) | POWER SUPPLY assembly top |
| `beta/pcb/POWER_SUPPLY/exports/drawings/POWER_SUPPLY_bottom_layer_mirrored.pdf` | pdf | 416 | — | GENERATED (unregistered) | POWER SUPPLY bottom layer mirrored |
| `beta/pcb/POWER_SUPPLY/exports/drawings/POWER_SUPPLY_outline.pdf` | pdf | 209 | — | GENERATED (unregistered) | POWER SUPPLY outline |
| `beta/pcb/POWER_SUPPLY/exports/drawings/POWER_SUPPLY_top_layer.pdf` | pdf | 536 | — | GENERATED (unregistered) | POWER SUPPLY top layer |
| `beta/pcb/POWER_SUPPLY/exports/svg/POWER_SUPPLY-B_Cu.svg` | svg | 843 | — | GENERATED (unregistered) | POWER SUPPLY B Cu |
| `beta/pcb/POWER_SUPPLY/exports/svg/POWER_SUPPLY-F_Cu.svg` | svg | 1384 | — | GENERATED (unregistered) | POWER SUPPLY F Cu |
| `beta/pcb/POWER_SUPPLY/exports/svg/POWER_SUPPLY_bottom_composite_mirrored.svg` | svg | 826 | — | GENERATED (unregistered) | POWER SUPPLY bottom composite mirrored |
| `beta/pcb/POWER_SUPPLY/exports/svg/POWER_SUPPLY_top_composite.svg` | svg | 2156 | — | GENERATED (unregistered) | POWER SUPPLY top composite |
| `beta/pcb/RF_PA/exports/3d/RF_PA_render_bottom.png` | png | 280 | — | GENERATED (unregistered) | RF PA render bottom |
| `beta/pcb/RF_PA/exports/3d/RF_PA_render_isometric.png` | png | 1274 | — | GENERATED (unregistered) | RF PA render isometric |
| `beta/pcb/RF_PA/exports/3d/RF_PA_render_top.png` | png | 413 | — | GENERATED (unregistered) | RF PA render top |
| `beta/pcb/RF_PA/exports/drawings/RF_PA_assembly_bottom_mirrored.pdf` | pdf | 46 | — | GENERATED (unregistered) | RF PA assembly bottom mirrored |
| `beta/pcb/RF_PA/exports/drawings/RF_PA_assembly_top.pdf` | pdf | 103 | — | GENERATED (unregistered) | RF PA assembly top |
| `beta/pcb/RF_PA/exports/drawings/RF_PA_bottom_layer_mirrored.pdf` | pdf | 82 | — | GENERATED (unregistered) | RF PA bottom layer mirrored |
| `beta/pcb/RF_PA/exports/drawings/RF_PA_outline.pdf` | pdf | 53 | — | GENERATED (unregistered) | RF PA outline |
| `beta/pcb/RF_PA/exports/drawings/RF_PA_top_layer.pdf` | pdf | 115 | — | GENERATED (unregistered) | RF PA top layer |
| `beta/pcb/RF_PA/exports/svg/RF_PA-B_Cu.svg` | svg | 98 | — | GENERATED (unregistered) | RF PA B Cu |
| `beta/pcb/RF_PA/exports/svg/RF_PA-F_Cu.svg` | svg | 119 | — | GENERATED (unregistered) | RF PA F Cu |
| `beta/pcb/RF_PA/exports/svg/RF_PA_bottom_composite_mirrored.svg` | svg | 99 | — | GENERATED (unregistered) | RF PA bottom composite mirrored |
| `beta/pcb/RF_PA/exports/svg/RF_PA_top_composite.svg` | svg | 173 | — | GENERATED (unregistered) | RF PA top composite |
| `docs/MECHANICAL/drawings/FREQUENCY_SYNTHESIZER_outline.svg` | svg | 2 | — | GENERATED (unregistered) | FREQUENCY SYNTHESIZER outline |
| `docs/MECHANICAL/drawings/MAIN_BOARD_outline.svg` | svg | 4 | — | GENERATED (unregistered) | MAIN BOARD outline |
| `docs/MECHANICAL/drawings/POWER_SUPPLY_outline.svg` | svg | 2 | — | GENERATED (unregistered) | POWER SUPPLY outline |
| `docs/MECHANICAL/drawings/RF_PA_outline.svg` | svg | 3 | — | GENERATED (unregistered) | RF PA outline |
| `engineering/ASSEMBLY/EXPLODED_VIEWS/aeris10_exploded_conceptual.pdf` | pdf | 191 | ASM-EXP-01 | CONCEPTUAL | aeris10 exploded conceptual |
| `engineering/ASSEMBLY/EXPLODED_VIEWS/aeris10_exploded_conceptual.png` | png | 242 | ASM-EXP-01 | CONCEPTUAL | aeris10 exploded conceptual |
| `engineering/ASSEMBLY/EXPLODED_VIEWS/aeris10_exploded_conceptual.svg` | svg | 26 | ASM-EXP-01 | CONCEPTUAL | aeris10 exploded conceptual |
| `engineering/DESIGN/ANTENNA/aeris10_patch_array_layout.pdf` | pdf | 90 | DSN-ANT-01 | PROPOSED DESIGN | aeris10 patch array layout |
| `engineering/DESIGN/ANTENNA/aeris10_patch_array_layout.png` | png | 167 | — | GENERATED (unregistered) | aeris10 patch array layout |
| `engineering/DESIGN/ANTENNA/aeris10_patch_array_layout.svg` | svg | 55 | DSN-ANT-01 | PROPOSED DESIGN | aeris10 patch array layout |
| `engineering/DESIGN/ANTENNA/kicad_exports/aeris10_patch_array_render_top.png` | png | 292 | DSN-ANT-01 | PROPOSED DESIGN | aeris10 patch array render top |
| `engineering/DESIGN/ANTENNA/kicad_exports/aeris10_patch_array_top.pdf` | pdf | 82 | DSN-ANT-01 | PROPOSED DESIGN | aeris10 patch array top |
| `engineering/DESIGN/ANTENNA/simulation/s11_row.png` | png | 30 | DSN-ANT-01-SIM | PROPOSED DESIGN | s11 row |
| `engineering/DESIGN/ELECTRICAL/PA_SUPPLY_22V/DSN-PSU-01_block_schematic.pdf` | pdf | 103 | DSN-PSU-01 | PROPOSED DESIGN | DSN PSU 01 block schematic |
| `engineering/DESIGN/ELECTRICAL/PA_SUPPLY_22V/DSN-PSU-01_block_schematic.png` | png | 160 | — | GENERATED (unregistered) | DSN PSU 01 block schematic |
| `engineering/DESIGN/ELECTRICAL/PA_SUPPLY_22V/DSN-PSU-01_block_schematic.svg` | svg | 13 | DSN-PSU-01 | PROPOSED DESIGN | DSN PSU 01 block schematic |
| `engineering/DESIGN/MECHANICAL/CAD/aeris10_head_pedestal_iso.pdf` | pdf | 202 | — | GENERATED (unregistered) | aeris10 head pedestal iso |
| `engineering/DESIGN/MECHANICAL/CAD/aeris10_head_pedestal_iso.png` | png | 659 | — | GENERATED (unregistered) | aeris10 head pedestal iso |
| `engineering/DESIGN/MECHANICAL/CAD/aeris10_head_pedestal_iso.svg` | svg | 954 | DSN-MECH-3D | PROPOSED DESIGN | aeris10 head pedestal iso |
| `engineering/DESIGN/MECHANICAL/CAD/aeris10_head_xray_iso.pdf` | pdf | 465 | — | GENERATED (unregistered) | aeris10 head xray iso |
| `engineering/DESIGN/MECHANICAL/CAD/aeris10_head_xray_iso.png` | png | 770 | DSN-MECH-3D | PROPOSED DESIGN | aeris10 head xray iso |
| `engineering/DESIGN/MECHANICAL/CAD/aeris10_head_xray_iso.svg` | svg | 959 | DSN-MECH-3D | PROPOSED DESIGN | aeris10 head xray iso |
| `engineering/DESIGN/MECHANICAL/CAD/detail/aeris10_detail_iso_rear.png` | png | 1092 | DSN-MECH-3D-DETAIL | PROPOSED DESIGN | aeris10 detail iso rear |
| `engineering/DESIGN/MECHANICAL/CAD/detail/aeris10_detail_iso_rear.svg` | svg | 22045 | — | GENERATED (unregistered) | aeris10 detail iso rear |
| `engineering/DESIGN/MECHANICAL/CAD/detail/aeris10_detail_isometrics.pdf` | pdf | 26228 | DSN-MECH-3D-DETAIL | PROPOSED DESIGN | aeris10 detail isometrics |
| `engineering/DESIGN/MECHANICAL/CAD/detail/aeris10_detail_xray_front_iso.png` | png | 1383 | DSN-MECH-3D-DETAIL | PROPOSED DESIGN | aeris10 detail xray front iso |
| `engineering/DESIGN/MECHANICAL/CAD/detail/aeris10_detail_xray_front_iso.svg` | svg | 21752 | — | GENERATED (unregistered) | aeris10 detail xray front iso |
| `engineering/DESIGN/MECHANICAL/drawings/DSN-MECH-01-05_head_pedestal_drawings.pdf` | pdf | 328 | DSN-MECH-05 | PROPOSED DESIGN | DSN MECH 01 05 head pedestal drawings |
| `engineering/DESIGN/MECHANICAL/drawings/DSN-MECH-01_head_plan_section.svg` | svg | 14 | DSN-MECH-01 | PROPOSED DESIGN | DSN MECH 01 head plan section |
| `engineering/DESIGN/MECHANICAL/drawings/DSN-MECH-02_head_front_elevation.svg` | svg | 11 | DSN-MECH-02 | PROPOSED DESIGN | DSN MECH 02 head front elevation |
| `engineering/DESIGN/MECHANICAL/drawings/DSN-MECH-03_head_side_section.svg` | svg | 9 | DSN-MECH-03 | PROPOSED DESIGN | DSN MECH 03 head side section |
| `engineering/DESIGN/MECHANICAL/drawings/DSN-MECH-04_internal_layout_rear.svg` | svg | 70 | DSN-MECH-04 | PROPOSED DESIGN | DSN MECH 04 internal layout rear |
| `engineering/DESIGN/MECHANICAL/drawings/DSN-MECH-05_pedestal_plan.svg` | svg | 5 | DSN-MECH-05 | PROPOSED DESIGN | DSN MECH 05 pedestal plan |
| `engineering/DESIGN/MECHANICAL/drawings/DSN-MECH-06-07_enclosure_detail.pdf` | pdf | 207 | DSN-MECH-06 | PROPOSED DESIGN | DSN MECH 06 07 enclosure detail |
| `engineering/DESIGN/MECHANICAL/drawings/DSN-MECH-06_sheet_metal_flat_patterns.svg` | svg | 23 | DSN-MECH-06 | PROPOSED DESIGN | DSN MECH 06 sheet metal flat patterns |
| `engineering/DESIGN/MECHANICAL/drawings/DSN-MECH-07_assembly_section_fasteners.svg` | svg | 22 | DSN-MECH-07 | PROPOSED DESIGN | DSN MECH 07 assembly section fasteners |
| `engineering/DESIGN/MECHANICAL/drawings/png/DSN-MECH-01_head_plan_section.png` | png | 165 | DSN-MECH-01 | PROPOSED DESIGN | DSN MECH 01 head plan section |
| `engineering/DESIGN/MECHANICAL/drawings/png/DSN-MECH-02_head_front_elevation.png` | png | 102 | DSN-MECH-02 | PROPOSED DESIGN | DSN MECH 02 head front elevation |
| `engineering/DESIGN/MECHANICAL/drawings/png/DSN-MECH-03_head_side_section.png` | png | 126 | DSN-MECH-03 | PROPOSED DESIGN | DSN MECH 03 head side section |
| `engineering/DESIGN/MECHANICAL/drawings/png/DSN-MECH-04_internal_layout_rear.png` | png | 252 | DSN-MECH-04 | PROPOSED DESIGN | DSN MECH 04 internal layout rear |
| `engineering/DESIGN/MECHANICAL/drawings/png/DSN-MECH-05_pedestal_plan.png` | png | 297 | DSN-MECH-05 | PROPOSED DESIGN | DSN MECH 05 pedestal plan |
| `engineering/DESIGN/MECHANICAL/drawings/png/DSN-MECH-06_sheet_metal_flat_patterns.png` | png | 184 | DSN-MECH-06 | PROPOSED DESIGN | DSN MECH 06 sheet metal flat patterns |
| `engineering/DESIGN/MECHANICAL/drawings/png/DSN-MECH-07_assembly_section_fasteners.png` | png | 393 | DSN-MECH-07 | PROPOSED DESIGN | DSN MECH 07 assembly section fasteners |
| `engineering/ELECTRICAL/power_distribution/power_distribution.dot` | dot | 11 | ELEC-PWR-01 | SOURCE-DERIVED | power distribution |
| `engineering/ELECTRICAL/power_distribution/power_distribution.pdf` | pdf | 107 | ELEC-PWR-01 | SOURCE-DERIVED | power distribution |
| `engineering/ELECTRICAL/power_distribution/power_distribution.png` | png | 2159 | ELEC-PWR-01 | SOURCE-DERIVED | power distribution |
| `engineering/ELECTRICAL/power_distribution/power_distribution.svg` | svg | 95 | ELEC-PWR-01 | SOURCE-DERIVED | power distribution |
| `engineering/ELECTRICAL/schematics/FREQUENCY_SYNTHESIZER/FREQUENCY_SYNTHESIZER_schematic.pdf` | pdf | 252 | — | GENERATED (unregistered) | FREQUENCY SYNTHESIZER schematic |
| `engineering/ELECTRICAL/schematics/FREQUENCY_SYNTHESIZER/png/FREQUENCY_SYNTHESIZER_schematic_sheet1.png` | png | 1074 | — | GENERATED (unregistered) | FREQUENCY SYNTHESIZER schematic sheet1 |
| `engineering/ELECTRICAL/schematics/FREQUENCY_SYNTHESIZER/svg/FREQUENCY_SYNTHESIZER_schematic_sheet1.svg` | svg | 2397 | — | GENERATED (unregistered) | FREQUENCY SYNTHESIZER schematic sheet1 |
| `engineering/ELECTRICAL/schematics/MAIN_BOARD/MAIN_BOARD_schematic.pdf` | pdf | 531 | — | GENERATED (unregistered) | MAIN BOARD schematic |
| `engineering/ELECTRICAL/schematics/MAIN_BOARD/png/MAIN_BOARD_schematic_sheet1.png` | png | 278 | — | GENERATED (unregistered) | MAIN BOARD schematic sheet1 |
| `engineering/ELECTRICAL/schematics/MAIN_BOARD/png/MAIN_BOARD_schematic_sheet2.png` | png | 815 | — | GENERATED (unregistered) | MAIN BOARD schematic sheet2 |
| `engineering/ELECTRICAL/schematics/MAIN_BOARD/png/MAIN_BOARD_schematic_sheet3.png` | png | 1627 | — | GENERATED (unregistered) | MAIN BOARD schematic sheet3 |
| `engineering/ELECTRICAL/schematics/MAIN_BOARD/png/MAIN_BOARD_schematic_sheet4.png` | png | 659 | — | GENERATED (unregistered) | MAIN BOARD schematic sheet4 |
| `engineering/ELECTRICAL/schematics/MAIN_BOARD/svg/MAIN_BOARD_schematic_sheet1.svg` | svg | 189 | — | GENERATED (unregistered) | MAIN BOARD schematic sheet1 |
| `engineering/ELECTRICAL/schematics/MAIN_BOARD/svg/MAIN_BOARD_schematic_sheet2.svg` | svg | 783 | — | GENERATED (unregistered) | MAIN BOARD schematic sheet2 |
| `engineering/ELECTRICAL/schematics/MAIN_BOARD/svg/MAIN_BOARD_schematic_sheet3.svg` | svg | 2391 | — | GENERATED (unregistered) | MAIN BOARD schematic sheet3 |
| `engineering/ELECTRICAL/schematics/MAIN_BOARD/svg/MAIN_BOARD_schematic_sheet4.svg` | svg | 644 | — | GENERATED (unregistered) | MAIN BOARD schematic sheet4 |
| `engineering/ELECTRICAL/schematics/POWER_SUPPLY/POWER_SUPPLY_schematic.pdf` | pdf | 213 | — | GENERATED (unregistered) | POWER SUPPLY schematic |
| `engineering/ELECTRICAL/schematics/POWER_SUPPLY/png/POWER_SUPPLY_schematic_sheet1.png` | png | 682 | — | GENERATED (unregistered) | POWER SUPPLY schematic sheet1 |
| `engineering/ELECTRICAL/schematics/POWER_SUPPLY/svg/POWER_SUPPLY_schematic_sheet1.svg` | svg | 941 | — | GENERATED (unregistered) | POWER SUPPLY schematic sheet1 |
| `engineering/ELECTRICAL/schematics/RF_PA/RF_PA_schematic.pdf` | pdf | 90 | — | GENERATED (unregistered) | RF PA schematic |
| `engineering/ELECTRICAL/schematics/RF_PA/png/RF_PA_schematic_sheet1.png` | png | 244 | — | GENERATED (unregistered) | RF PA schematic sheet1 |
| `engineering/ELECTRICAL/schematics/RF_PA/svg/RF_PA_schematic_sheet1.svg` | svg | 69 | — | GENERATED (unregistered) | RF PA schematic sheet1 |
| `engineering/MECHANICAL/CAD/pcb_set_plan_view.png` | png | 87 | MECH-PLAN-01 | SOURCE-DERIVED | pcb set plan view |
| `engineering/MECHANICAL/CAD/pcb_set_plan_view.svg` | svg | 10 | MECH-PLAN-01 | SOURCE-DERIVED | pcb set plan view |
| `engineering/MECHANICAL/PDF/FREQUENCY_SYNTHESIZER_outline.pdf` | pdf | 145 | — | GENERATED (unregistered) | FREQUENCY SYNTHESIZER outline |
| `engineering/MECHANICAL/PDF/MAIN_BOARD_outline.pdf` | pdf | 495 | — | GENERATED (unregistered) | MAIN BOARD outline |
| `engineering/MECHANICAL/PDF/POWER_SUPPLY_outline.pdf` | pdf | 209 | — | GENERATED (unregistered) | POWER SUPPLY outline |
| `engineering/MECHANICAL/PDF/RF_PA_outline.pdf` | pdf | 53 | — | GENERATED (unregistered) | RF PA outline |
| `engineering/MECHANICAL/PDF/pcb_set_plan_view.pdf` | pdf | 93 | MECH-PLAN-01 | SOURCE-DERIVED | pcb set plan view |
| `engineering/PCB/FREQUENCY_SYNTHESIZER/3d/FREQUENCY_SYNTHESIZER_render_bottom.png` | png | 464 | — | GENERATED (unregistered) | FREQUENCY SYNTHESIZER render bottom |
| `engineering/PCB/FREQUENCY_SYNTHESIZER/3d/FREQUENCY_SYNTHESIZER_render_isometric.png` | png | 1878 | — | GENERATED (unregistered) | FREQUENCY SYNTHESIZER render isometric |
| `engineering/PCB/FREQUENCY_SYNTHESIZER/3d/FREQUENCY_SYNTHESIZER_render_top.png` | png | 744 | — | GENERATED (unregistered) | FREQUENCY SYNTHESIZER render top |
| `engineering/PCB/FREQUENCY_SYNTHESIZER/drawings/FREQUENCY_SYNTHESIZER_assembly_bottom_mirrored.pdf` | pdf | 135 | — | GENERATED (unregistered) | FREQUENCY SYNTHESIZER assembly bottom mirrored |
| `engineering/PCB/FREQUENCY_SYNTHESIZER/drawings/FREQUENCY_SYNTHESIZER_assembly_top.pdf` | pdf | 301 | — | GENERATED (unregistered) | FREQUENCY SYNTHESIZER assembly top |
| `engineering/PCB/FREQUENCY_SYNTHESIZER/drawings/FREQUENCY_SYNTHESIZER_bottom_layer_mirrored.pdf` | pdf | 214 | — | GENERATED (unregistered) | FREQUENCY SYNTHESIZER bottom layer mirrored |
| `engineering/PCB/FREQUENCY_SYNTHESIZER/drawings/FREQUENCY_SYNTHESIZER_outline.pdf` | pdf | 145 | — | GENERATED (unregistered) | FREQUENCY SYNTHESIZER outline |
| `engineering/PCB/FREQUENCY_SYNTHESIZER/drawings/FREQUENCY_SYNTHESIZER_top_layer.pdf` | pdf | 280 | — | GENERATED (unregistered) | FREQUENCY SYNTHESIZER top layer |
| `engineering/PCB/FREQUENCY_SYNTHESIZER/svg/FREQUENCY_SYNTHESIZER-B_Cu.svg` | svg | 157 | — | GENERATED (unregistered) | FREQUENCY SYNTHESIZER B Cu |
| `engineering/PCB/FREQUENCY_SYNTHESIZER/svg/FREQUENCY_SYNTHESIZER-F_Cu.svg` | svg | 324 | — | GENERATED (unregistered) | FREQUENCY SYNTHESIZER F Cu |
| `engineering/PCB/FREQUENCY_SYNTHESIZER/svg/FREQUENCY_SYNTHESIZER_bottom_composite_mirrored.svg` | svg | 156 | — | GENERATED (unregistered) | FREQUENCY SYNTHESIZER bottom composite mirrored |
| `engineering/PCB/FREQUENCY_SYNTHESIZER/svg/FREQUENCY_SYNTHESIZER_top_composite.svg` | svg | 667 | — | GENERATED (unregistered) | FREQUENCY SYNTHESIZER top composite |
| `engineering/PCB/MAIN_BOARD/3d/MAIN_BOARD_render_bottom.png` | png | 430 | — | GENERATED (unregistered) | MAIN BOARD render bottom |
| `engineering/PCB/MAIN_BOARD/3d/MAIN_BOARD_render_isometric.png` | png | 1871 | — | GENERATED (unregistered) | MAIN BOARD render isometric |
| `engineering/PCB/MAIN_BOARD/3d/MAIN_BOARD_render_top.png` | png | 843 | — | GENERATED (unregistered) | MAIN BOARD render top |
| `engineering/PCB/MAIN_BOARD/drawings/MAIN_BOARD_assembly_bottom_mirrored.pdf` | pdf | 503 | — | GENERATED (unregistered) | MAIN BOARD assembly bottom mirrored |
| `engineering/PCB/MAIN_BOARD/drawings/MAIN_BOARD_assembly_top.pdf` | pdf | 1020 | — | GENERATED (unregistered) | MAIN BOARD assembly top |
| `engineering/PCB/MAIN_BOARD/drawings/MAIN_BOARD_bottom_layer_mirrored.pdf` | pdf | 785 | — | GENERATED (unregistered) | MAIN BOARD bottom layer mirrored |
| `engineering/PCB/MAIN_BOARD/drawings/MAIN_BOARD_outline.pdf` | pdf | 495 | — | GENERATED (unregistered) | MAIN BOARD outline |
| `engineering/PCB/MAIN_BOARD/drawings/MAIN_BOARD_top_layer.pdf` | pdf | 1175 | — | GENERATED (unregistered) | MAIN BOARD top layer |
| `engineering/PCB/MAIN_BOARD/svg/MAIN_BOARD-B_Cu.svg` | svg | 514 | — | GENERATED (unregistered) | MAIN BOARD B Cu |
| `engineering/PCB/MAIN_BOARD/svg/MAIN_BOARD-F_Cu.svg` | svg | 1812 | — | GENERATED (unregistered) | MAIN BOARD F Cu |
| `engineering/PCB/MAIN_BOARD/svg/MAIN_BOARD_bottom_composite_mirrored.svg` | svg | 525 | — | GENERATED (unregistered) | MAIN BOARD bottom composite mirrored |
| `engineering/PCB/MAIN_BOARD/svg/MAIN_BOARD_top_composite.svg` | svg | 3770 | — | GENERATED (unregistered) | MAIN BOARD top composite |
| `engineering/PCB/POWER_SUPPLY/3d/POWER_SUPPLY_render_bottom.png` | png | 218 | — | GENERATED (unregistered) | POWER SUPPLY render bottom |
| `engineering/PCB/POWER_SUPPLY/3d/POWER_SUPPLY_render_isometric.png` | png | 1408 | — | GENERATED (unregistered) | POWER SUPPLY render isometric |
| `engineering/PCB/POWER_SUPPLY/3d/POWER_SUPPLY_render_top.png` | png | 334 | — | GENERATED (unregistered) | POWER SUPPLY render top |
| `engineering/PCB/POWER_SUPPLY/drawings/POWER_SUPPLY_assembly_bottom_mirrored.pdf` | pdf | 209 | — | GENERATED (unregistered) | POWER SUPPLY assembly bottom mirrored |
| `engineering/PCB/POWER_SUPPLY/drawings/POWER_SUPPLY_assembly_top.pdf` | pdf | 382 | — | GENERATED (unregistered) | POWER SUPPLY assembly top |
| `engineering/PCB/POWER_SUPPLY/drawings/POWER_SUPPLY_bottom_layer_mirrored.pdf` | pdf | 245 | — | GENERATED (unregistered) | POWER SUPPLY bottom layer mirrored |
| `engineering/PCB/POWER_SUPPLY/drawings/POWER_SUPPLY_outline.pdf` | pdf | 209 | — | GENERATED (unregistered) | POWER SUPPLY outline |
| `engineering/PCB/POWER_SUPPLY/drawings/POWER_SUPPLY_top_layer.pdf` | pdf | 367 | — | GENERATED (unregistered) | POWER SUPPLY top layer |
| `engineering/PCB/POWER_SUPPLY/svg/POWER_SUPPLY-B_Cu.svg` | svg | 227 | — | GENERATED (unregistered) | POWER SUPPLY B Cu |
| `engineering/PCB/POWER_SUPPLY/svg/POWER_SUPPLY-F_Cu.svg` | svg | 671 | — | GENERATED (unregistered) | POWER SUPPLY F Cu |
| `engineering/PCB/POWER_SUPPLY/svg/POWER_SUPPLY_bottom_composite_mirrored.svg` | svg | 226 | — | GENERATED (unregistered) | POWER SUPPLY bottom composite mirrored |
| `engineering/PCB/POWER_SUPPLY/svg/POWER_SUPPLY_top_composite.svg` | svg | 1430 | — | GENERATED (unregistered) | POWER SUPPLY top composite |
| `engineering/PCB/RF_PA/3d/RF_PA_render_bottom.png` | png | 280 | — | GENERATED (unregistered) | RF PA render bottom |
| `engineering/PCB/RF_PA/3d/RF_PA_render_isometric.png` | png | 1278 | — | GENERATED (unregistered) | RF PA render isometric |
| `engineering/PCB/RF_PA/3d/RF_PA_render_top.png` | png | 415 | — | GENERATED (unregistered) | RF PA render top |
| `engineering/PCB/RF_PA/drawings/RF_PA_assembly_bottom_mirrored.pdf` | pdf | 46 | — | GENERATED (unregistered) | RF PA assembly bottom mirrored |
| `engineering/PCB/RF_PA/drawings/RF_PA_assembly_top.pdf` | pdf | 103 | — | GENERATED (unregistered) | RF PA assembly top |
| `engineering/PCB/RF_PA/drawings/RF_PA_bottom_layer_mirrored.pdf` | pdf | 82 | — | GENERATED (unregistered) | RF PA bottom layer mirrored |
| `engineering/PCB/RF_PA/drawings/RF_PA_outline.pdf` | pdf | 53 | — | GENERATED (unregistered) | RF PA outline |
| `engineering/PCB/RF_PA/drawings/RF_PA_top_layer.pdf` | pdf | 116 | — | GENERATED (unregistered) | RF PA top layer |
| `engineering/PCB/RF_PA/svg/RF_PA-B_Cu.svg` | svg | 98 | — | GENERATED (unregistered) | RF PA B Cu |
| `engineering/PCB/RF_PA/svg/RF_PA-F_Cu.svg` | svg | 119 | — | GENERATED (unregistered) | RF PA F Cu |
| `engineering/PCB/RF_PA/svg/RF_PA_bottom_composite_mirrored.svg` | svg | 99 | — | GENERATED (unregistered) | RF PA bottom composite mirrored |
| `engineering/PCB/RF_PA/svg/RF_PA_top_composite.svg` | svg | 173 | — | GENERATED (unregistered) | RF PA top composite |
| `engineering/SOFTWARE_DIAGRAMS/DATA_FLOW/end_to_end_data_flow.dot` | dot | 11 | SD-07 | PARTIAL | end to end data flow |
| `engineering/SOFTWARE_DIAGRAMS/DATA_FLOW/end_to_end_data_flow.pdf` | pdf | 95 | SD-07 | PARTIAL | end to end data flow |
| `engineering/SOFTWARE_DIAGRAMS/DATA_FLOW/end_to_end_data_flow.png` | png | 1476 | SD-07 | PARTIAL | end to end data flow |
| `engineering/SOFTWARE_DIAGRAMS/DATA_FLOW/end_to_end_data_flow.svg` | svg | 58 | SD-07 | PARTIAL | end to end data flow |
| `engineering/SOFTWARE_DIAGRAMS/FPGA/fpga_data_pipeline.dot` | dot | 13 | SD-02 | PARTIAL | fpga data pipeline |
| `engineering/SOFTWARE_DIAGRAMS/FPGA/fpga_data_pipeline.pdf` | pdf | 99 | SD-02 | PARTIAL | fpga data pipeline |
| `engineering/SOFTWARE_DIAGRAMS/FPGA/fpga_data_pipeline.png` | png | 1475 | SD-02 | PARTIAL | fpga data pipeline |
| `engineering/SOFTWARE_DIAGRAMS/FPGA/fpga_data_pipeline.svg` | svg | 71 | SD-02 | PARTIAL | fpga data pipeline |
| `engineering/SOFTWARE_DIAGRAMS/FPGA/fpga_module_hierarchy.dot` | dot | 8 | SD-01 | SOURCE-DERIVED | fpga module hierarchy |
| `engineering/SOFTWARE_DIAGRAMS/FPGA/fpga_module_hierarchy.pdf` | pdf | 63 | SD-01 | SOURCE-DERIVED | fpga module hierarchy |
| `engineering/SOFTWARE_DIAGRAMS/FPGA/fpga_module_hierarchy.png` | png | 552 | SD-01 | SOURCE-DERIVED | fpga module hierarchy |
| `engineering/SOFTWARE_DIAGRAMS/FPGA/fpga_module_hierarchy.svg` | svg | 35 | SD-01 | SOURCE-DERIVED | fpga module hierarchy |
| `engineering/SOFTWARE_DIAGRAMS/PYTHON/python_gui_architecture.dot` | dot | 10 | SD-06 | SOURCE-DERIVED | python gui architecture |
| `engineering/SOFTWARE_DIAGRAMS/PYTHON/python_gui_architecture.pdf` | pdf | 92 | SD-06 | SOURCE-DERIVED | python gui architecture |
| `engineering/SOFTWARE_DIAGRAMS/PYTHON/python_gui_architecture.png` | png | 1269 | SD-06 | SOURCE-DERIVED | python gui architecture |
| `engineering/SOFTWARE_DIAGRAMS/PYTHON/python_gui_architecture.svg` | svg | 56 | SD-06 | SOURCE-DERIVED | python gui architecture |
| `engineering/SOFTWARE_DIAGRAMS/PYTHON/python_gui_modules.dot` | dot | 9 | SD-05 | SOURCE-DERIVED | python gui modules |
| `engineering/SOFTWARE_DIAGRAMS/PYTHON/python_gui_modules.pdf` | pdf | 58 | SD-05 | SOURCE-DERIVED | python gui modules |
| `engineering/SOFTWARE_DIAGRAMS/PYTHON/python_gui_modules.png` | png | 1566 | SD-05 | SOURCE-DERIVED | python gui modules |
| `engineering/SOFTWARE_DIAGRAMS/PYTHON/python_gui_modules.svg` | svg | 51 | SD-05 | SOURCE-DERIVED | python gui modules |
| `engineering/SOFTWARE_DIAGRAMS/STM32/stm32_firmware_architecture.dot` | dot | 14 | SD-03 | PARTIAL | stm32 firmware architecture |
| `engineering/SOFTWARE_DIAGRAMS/STM32/stm32_firmware_architecture.pdf` | pdf | 106 | SD-03 | PARTIAL | stm32 firmware architecture |
| `engineering/SOFTWARE_DIAGRAMS/STM32/stm32_firmware_architecture.png` | png | 2750 | SD-03 | PARTIAL | stm32 firmware architecture |
| `engineering/SOFTWARE_DIAGRAMS/STM32/stm32_firmware_architecture.svg` | svg | 96 | SD-03 | PARTIAL | stm32 firmware architecture |
| `engineering/SOFTWARE_DIAGRAMS/STM32/stm32_usb_cdc_flow.dot` | dot | 7 | SD-04 | PARTIAL | stm32 usb cdc flow |
| `engineering/SOFTWARE_DIAGRAMS/STM32/stm32_usb_cdc_flow.pdf` | pdf | 92 | SD-04 | PARTIAL | stm32 usb cdc flow |
| `engineering/SOFTWARE_DIAGRAMS/STM32/stm32_usb_cdc_flow.png` | png | 873 | SD-04 | PARTIAL | stm32 usb cdc flow |
| `engineering/SOFTWARE_DIAGRAMS/STM32/stm32_usb_cdc_flow.svg` | svg | 40 | SD-04 | PARTIAL | stm32 usb cdc flow |
| `engineering/SYSTEM/block_diagrams/system_block_diagram.dot` | dot | 17 | SYS-01 | SOURCE-DERIVED | system block diagram |
| `engineering/SYSTEM/block_diagrams/system_block_diagram.mmd` | mmd | 7 | SYS-01 | SOURCE-DERIVED | system block diagram |
| `engineering/SYSTEM/block_diagrams/system_block_diagram.pdf` | pdf | 111 | SYS-01 | SOURCE-DERIVED | system block diagram |
| `engineering/SYSTEM/block_diagrams/system_block_diagram.png` | png | 2290 | SYS-01 | SOURCE-DERIVED | system block diagram |
| `engineering/SYSTEM/block_diagrams/system_block_diagram.svg` | svg | 93 | SYS-01 | SOURCE-DERIVED | system block diagram |
| `engineering/SYSTEM/data_flow/signal_and_data_flow.dot` | dot | 13 | SYS-03 | SOURCE-DERIVED | signal and data flow |
| `engineering/SYSTEM/data_flow/signal_and_data_flow.pdf` | pdf | 98 | SYS-03 | SOURCE-DERIVED | signal and data flow |
| `engineering/SYSTEM/data_flow/signal_and_data_flow.png` | png | 1699 | SYS-03 | SOURCE-DERIVED | signal and data flow |
| `engineering/SYSTEM/data_flow/signal_and_data_flow.svg` | svg | 77 | SYS-03 | SOURCE-DERIVED | signal and data flow |
| `engineering/SYSTEM/interfaces/hardware_interconnection.dot` | dot | 9 | SYS-02 | SOURCE-DERIVED | hardware interconnection |
| `engineering/SYSTEM/interfaces/hardware_interconnection.pdf` | pdf | 76 | SYS-02 | SOURCE-DERIVED | hardware interconnection |
| `engineering/SYSTEM/interfaces/hardware_interconnection.png` | png | 1084 | SYS-02 | SOURCE-DERIVED | hardware interconnection |
| `engineering/SYSTEM/interfaces/hardware_interconnection.svg` | svg | 38 | SYS-02 | SOURCE-DERIVED | hardware interconnection |
