herasymyuks/PLFM_RADAR-aeris/manual/chapters/05_power_supply_board.md

# 5. Power Supply Board (PowerBoard)

**Chapter status summary:** schematic — SOURCE-DERIVED (EAGLE 9.6.2 schematic rendered); connector inventory — SOURCE-DERIVED; layout — PARTIAL in the source (309 airwires, 132 of 312 parts parked outside the outline, sch/brd version mismatch) and BETA in `beta/pcb/POWER_SUPPLY/` (308 → 89 unconnected, placement by script not reviewed); layer plots and renders — SOURCE-DERIVED / BETA; stack-up — PARTIAL (2-layer, 1.5 mm core from the DRU) with a PROPOSED fabrication note; BOM — PARTIAL (0 MPN in the source). The 22 V PA drain supply does not exist on this board (K4) — see chapter 9. Nothing is hardware-verified. Compiled by Antidrone Ukraine · antidrone.cc.

**Sources:** `docs/PCB/POWER_SUPPLY.md`; `engineering/ELECTRICAL/connection_diagrams/POWER_SUPPLY_connection_report.md` §1–2; `engineering/ELECTRICAL/schematics/POWER_SUPPLY/`; `engineering/PCB/POWER_SUPPLY/README.md`, `STACKUP.md`; `beta/pcb/POWER_SUPPLY/README.md`, `UNROUTED.md`, `FAB_NOTES.md`, `BOM_POWER_SUPPLY_beta.csv`; `engineering/VALIDATION/UNRESOLVED_GEOMETRY.md` (G-10).

## 5.1 Role and key parts

The Power Board converts the single DC input `Vin [12-17] V` (silkscreen label; source: `docs/PCB/POWER_SUPPLY.md` §1) into the 24 rails consumed by the Main Board and the Frequency Synthesizer, each rail leaving the board on its own 2-pin Molex KK connector, and receives the 15-line enable bus from the STM32 on the 20-way header SV1. Board: **280 × 300 mm, 2 copper layers**, EAGLE schematic 9.6.2 / board 7.4.0 (version mismatch), 312 physical parts, 156 nets, 346 vias, DRU `PCBWay_2L_100um-Track` with a 1.5 mm core (source: `docs/PCB/POWER_SUPPLY.md` §1).

Key ICs (deviceset names, MPN UNVERIFIED; source: `docs/PCB/POWER_SUPPLY.md` §1):

| Function | Part | Qty | Note |
|---|---|---|---|
| Buck regulators | TPS562208DDCT | 21 | datasheet folder contains TPS562201 instead — datasheet to be added |
| LDO | ADM7151ACPZ-04-R7 | 6 | |
| LDO | TPS7A8300RGRR | 2 | feedback-select pins without net (24 unconnected pins, see §5.3) |
| Inverters | LM2662MX/NOPB | 5 | datasheet folder has LM2663 |
| Tantalum capacitors | T521W476M020ATE045 | 10 | |
| Rail outputs | Molex 22-23-2021 | 34 | |
| DC input | AK300/2 (X1) | 1 | `VIN`, `GND` |
| Not on the board | MAX20029 | — | datasheet present, part absent |

Rails present as silkscreen labels (layer 51; source: `docs/PCB/POWER_SUPPLY.md` §1): `+5V5_PA, -5V5_PA, +1V8_CLOCK, +3V3_CLOCK, +3V3_VDD_SW, +5V0_PA_1/2/3, -3V3_SW, +3V3_SW, +3V3_ADTR, -5V0_ADAR12, -5V0_ADAR34, +3V4, -3V4, +3V3_LO, +5V0_ADAR, +3V3_ADAR_12, +3V3_ADAR_34, +5V0_0, +1V8_FPGA, +1V0_FPGA, +3V3, +3V3_FPGA, +3V3_AN`, 12 × `EN`. The 16 `EN_*` nets match the STM32 enable GPIOs PE7…PE15, PG0…PG5 (same source). The design input for rail currents is `3_Power Management/Power Management V6.xlsx` (sheet `Feuil1`); it budgets 16 × QPA2962 at +22 V / 2 A, a rail this board does not have — K4 (source: `docs/PCB/POWER_SUPPLY.md` §2; `docs/SYSTEM/BLOCK_DIAGRAM.md`).

Schematic summary (source: `engineering/ELECTRICAL/connection_diagrams/POWER_SUPPLY_connection_report.md` §1):

| Item | Count |
|---|---|
| Sheets | 1 |
| Parts (all) / physical | 562 / 312 |
| Nets | 156 |
| Pin connections | 1061 |
| Single-pin nets | 0 |
| Unconnected pins on placed gates | 24 |
| Physical parts without value | 80 |
| Board airwires (unrouted connections, layer 19) | 309 |
| Missing symbol/footprint records | 0 |
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
