herasymyuks/PLFM_RADAR-aeris/manual/chapters/06_frequency_synthesizer.md

# 6. Frequency Synthesizer Board (Clocks_Freq_Synth_board)

**Chapter status summary:** schematic — SOURCE-DERIVED (EAGLE 9.6.2 rendered); connector inventory — SOURCE-DERIVED; layout — complete in the source (0 airwires, 0 approved DRC) and SOURCE-DERIVED in the KiCad conversion; BETA copy with silkscreen clean-up only (copper untouched); layer plots and renders — SOURCE-DERIVED / BETA; stack-up — PARTIAL with three contradictory sources (DRU, `Stack_Hybrid.png`, PCBWay impedance note) and a PROPOSED fabrication note; pick-and-place — ORIGINAL PROJECT FILE (the only production artefact the upstream project delivered); BOM — PARTIAL (0 MPN; oscillator part-number conflict K7). Nothing is hardware-verified. Compiled by Antidrone Ukraine · antidrone.cc.
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
