herasymyuks/PLFM_RADAR-aeris/engineering/DESIGN/MECHANICAL/drawings/png/DSN-MECH-07_assembly_section_fasteners.png

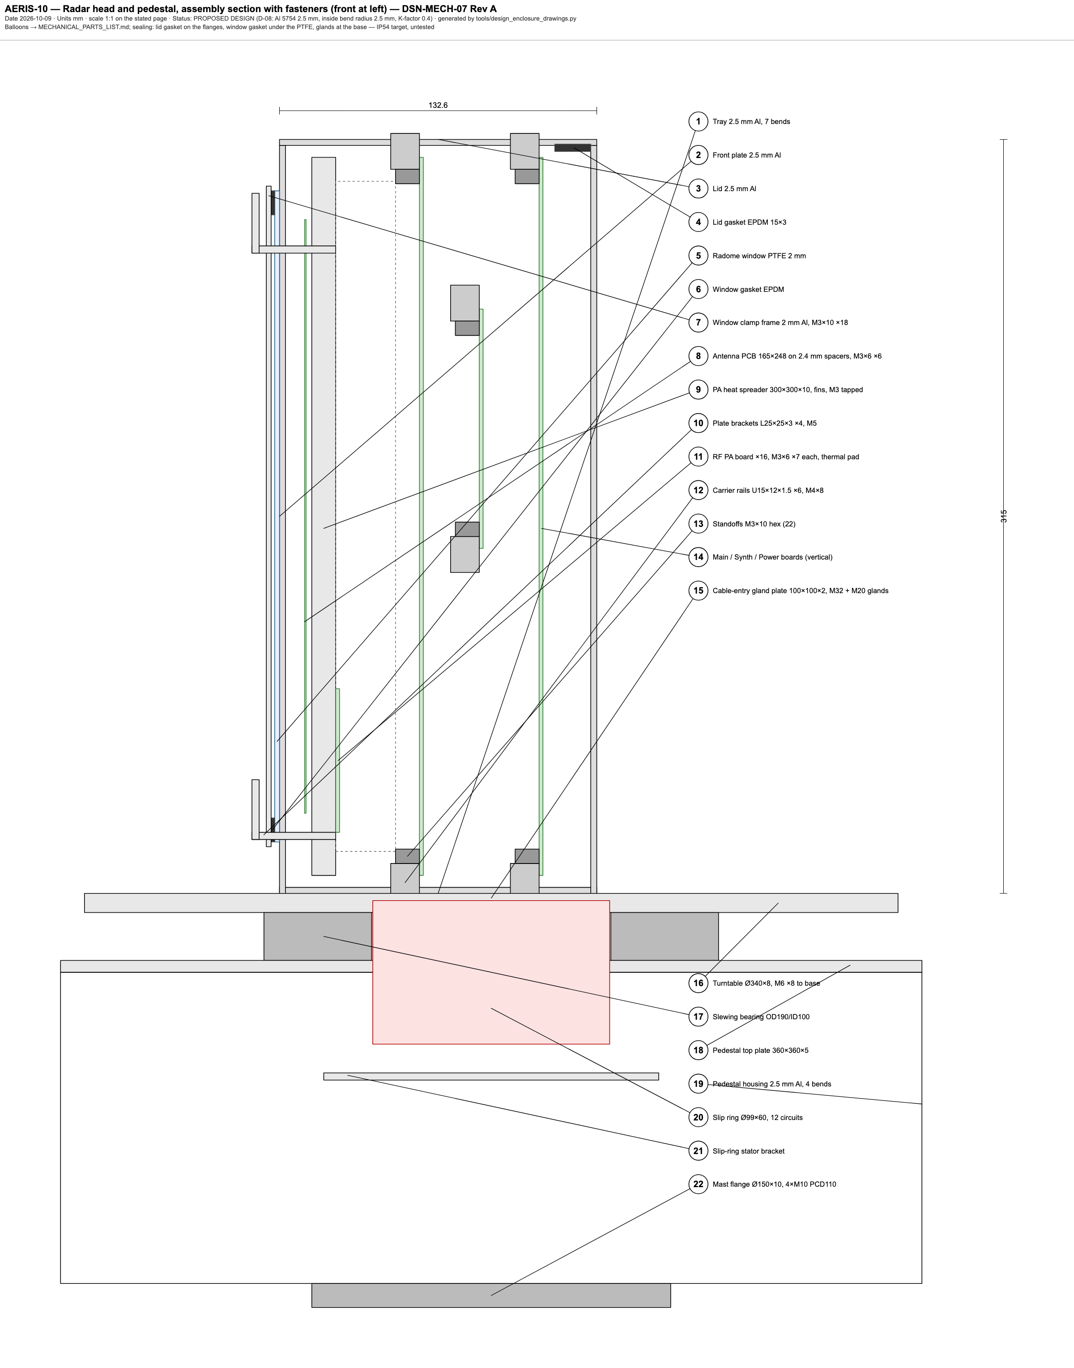
engineering/DESIGN/MECHANICAL/drawings/png/DSN-MECH-07_assembly_section_fasteners.png
