herasymyuks/PLFM_RADAR-aeris/manual/figures/POWER_SUPPLY_assembly_top-1.png

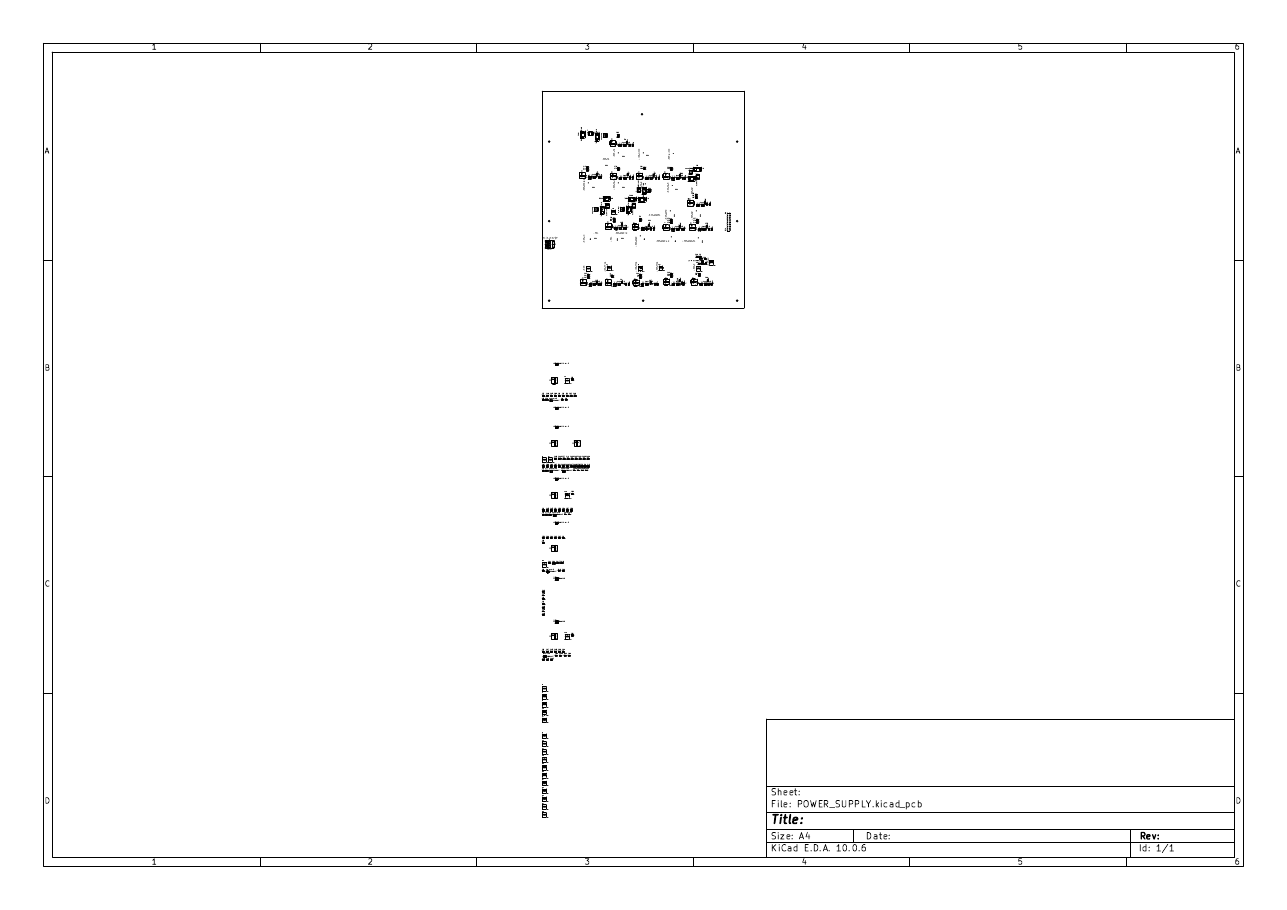
manual/figures/POWER_SUPPLY_assembly_top-1.png
