herasymyuks/PLFM_RADAR-aeris/manual/figures/RF_PA_assembly_top-1.png

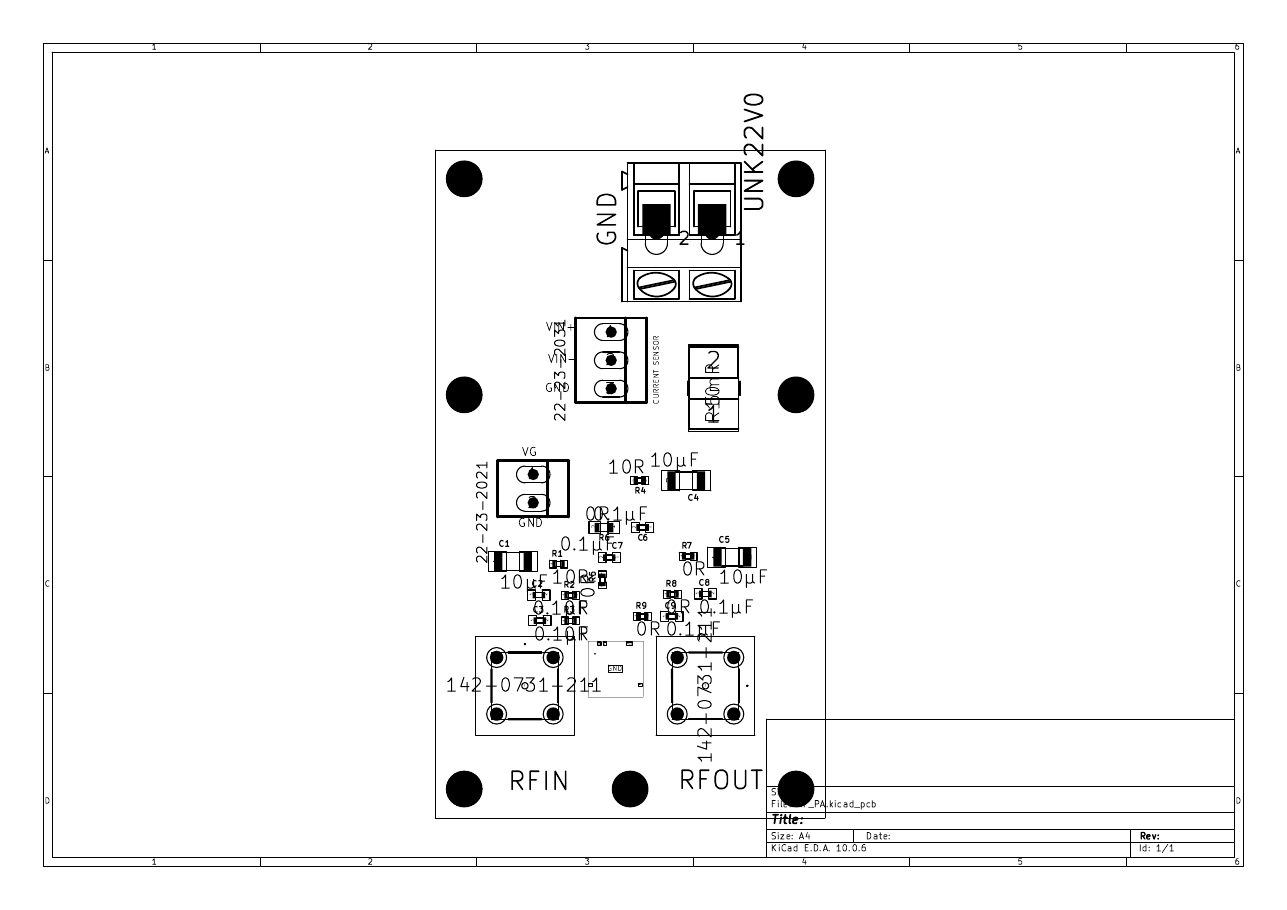
manual/figures/RF_PA_assembly_top-1.png
