herasymyuks/PLFM_RADAR-aeris/manual/figures/thermal_map_A-continuous-bias.png

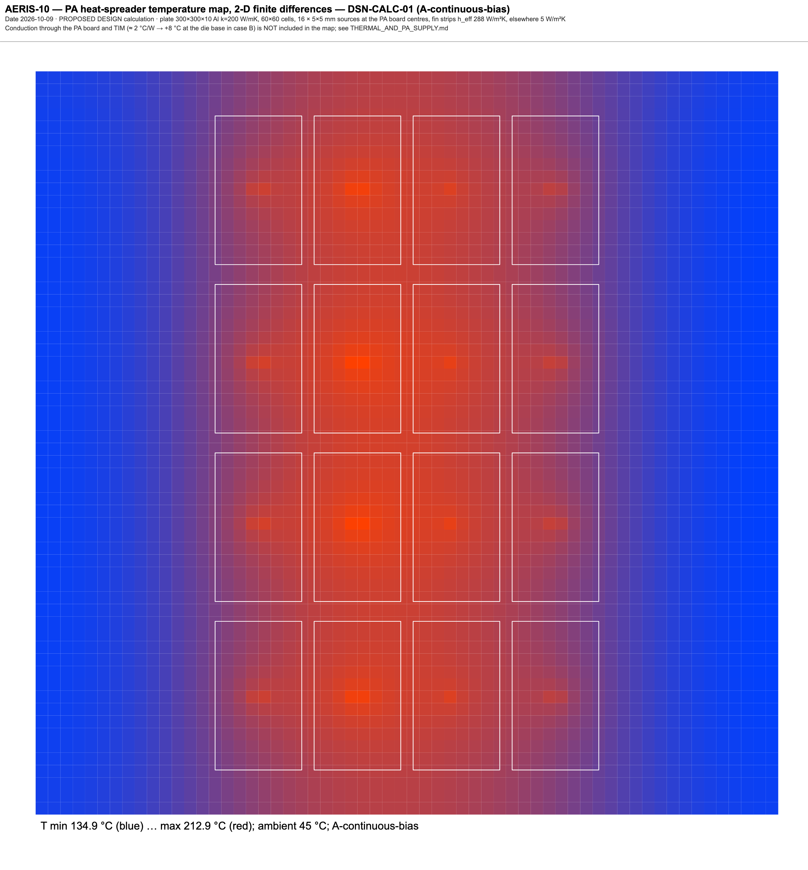
manual/figures/thermal_map_A-continuous-bias.png
