herasymyuks/PLFM_RADAR-aeris/engineering/DESIGN/MECHANICAL/drawings/DSN-MECH-06-07_enclosure_detail.pdf

AERIS-10 — Radar head sheet-metal parts: flat patterns with bend lines — DSN-MECH-06 Rev A
Date 2026-10-09 · Units mm · scale 1:1 on the stated page · Status: PROPOSED DESIGN (D-08: Al 5754 2.5 mm, inside bend radius 2.5 mm, K-factor 0.4) · generated by tools/design_enclosure_drawings.py Flat patterns are analytical (bend allowance added at every bend, no bend reliefs drawn) — to be checked in the fabricator's CAM before cutting

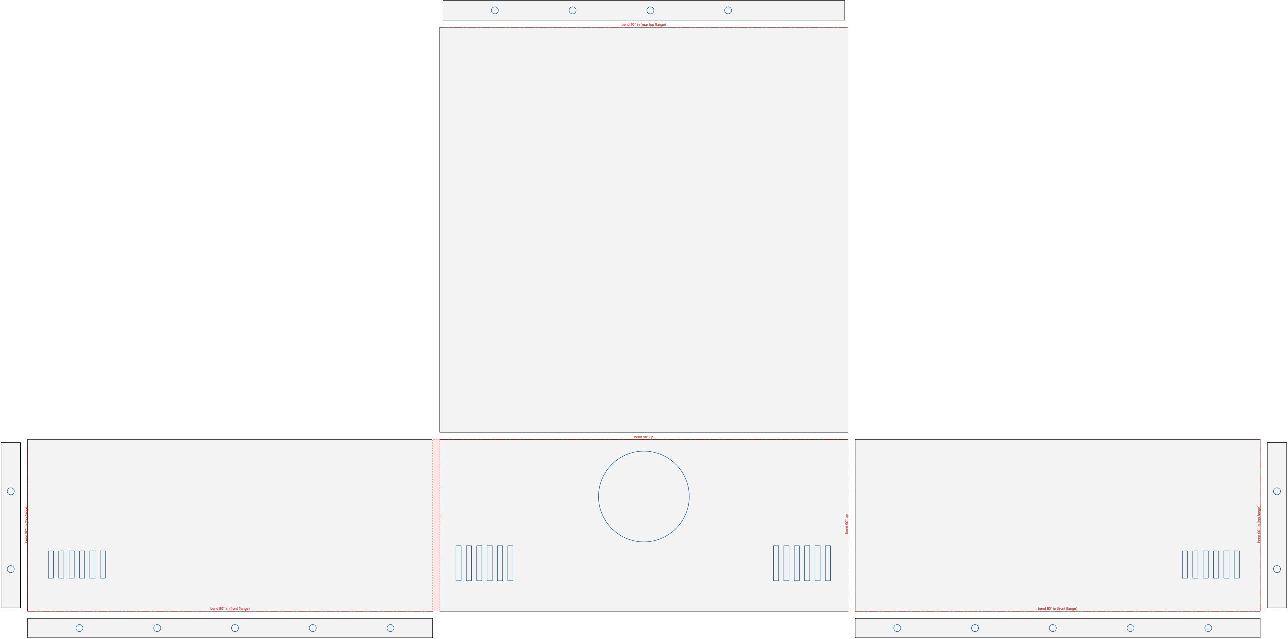
[picture p131: figure]
bend 90° up; bend 90° in (top flange); bend 90° in (rear top flange); bend 90° in (front flange)

992.0 flat width

491.6 flat height

PART 1 — TRAY, flat pattern. Al 5754-H22 t = 2.5 mm; 7 bends 90°, R_in 2.5 mm, BA = 5.50 mm each (K = 0.4); PEM S-M4-1 ×18 in Ø5.4 holes; corner reliefs 2×t to be added in CAM

312.5

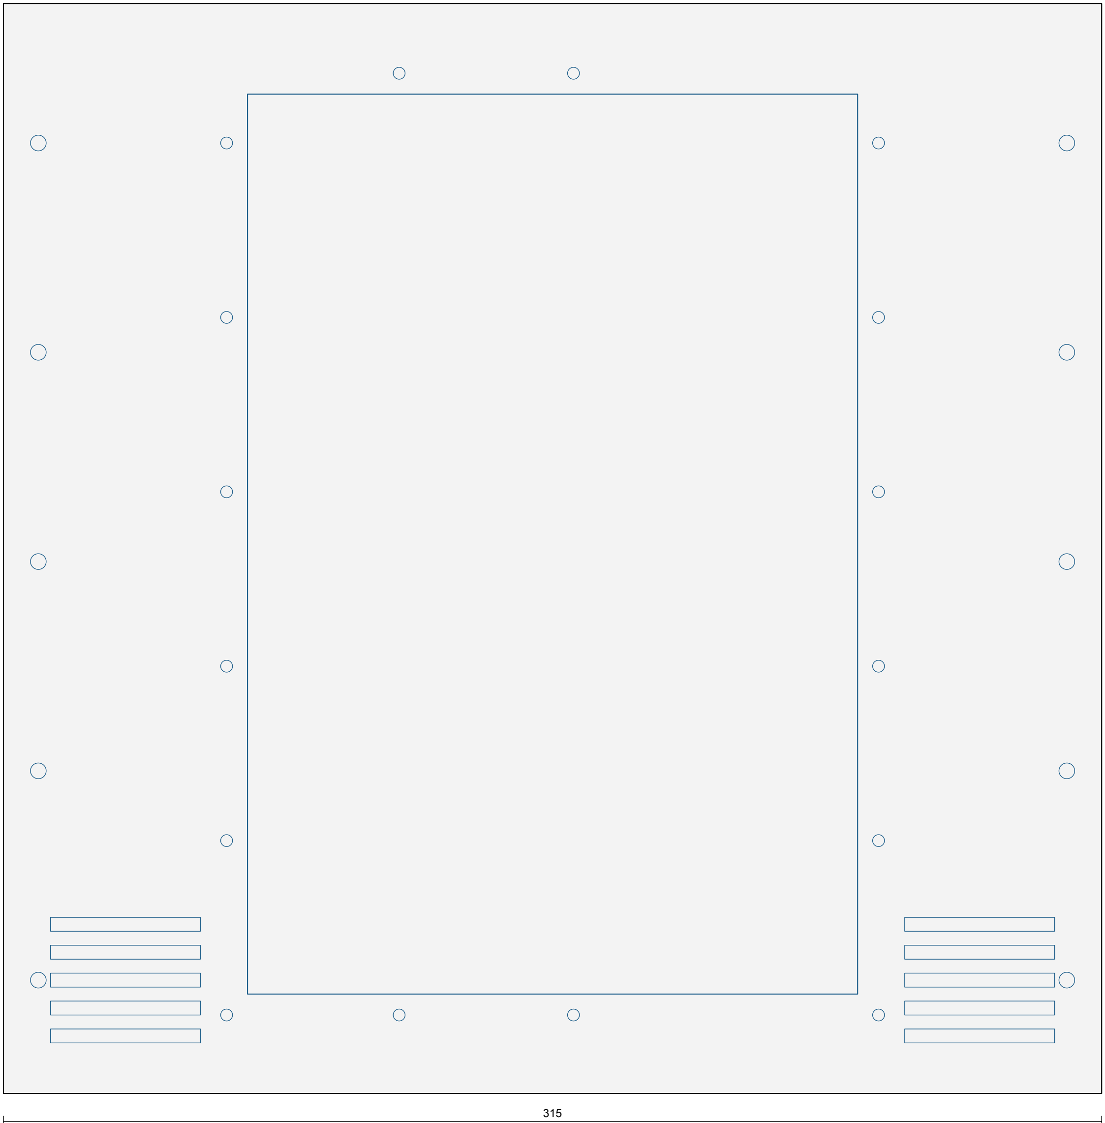
[picture p132: figure]

PART 2 — FRONT PLATE, flat (no bends), t = 2.5 mm: window 175×258, M3 clamp holes Ø3.4, M4 holes Ø4.5 to the tray front flanges, intake louvres 2 × 5

315

132.6

PART 3 — LID, flat, t = 2.5 mm: M4 holes Ø4.5 on the flange pattern, exhaust slots 2 × 6; EPDM gasket 15 × 3 mm under the lid on the flanges

AERIS-10 — Radar head and pedestal, assembly section with fasteners (front at left) — DSN-MECH-07 Rev A

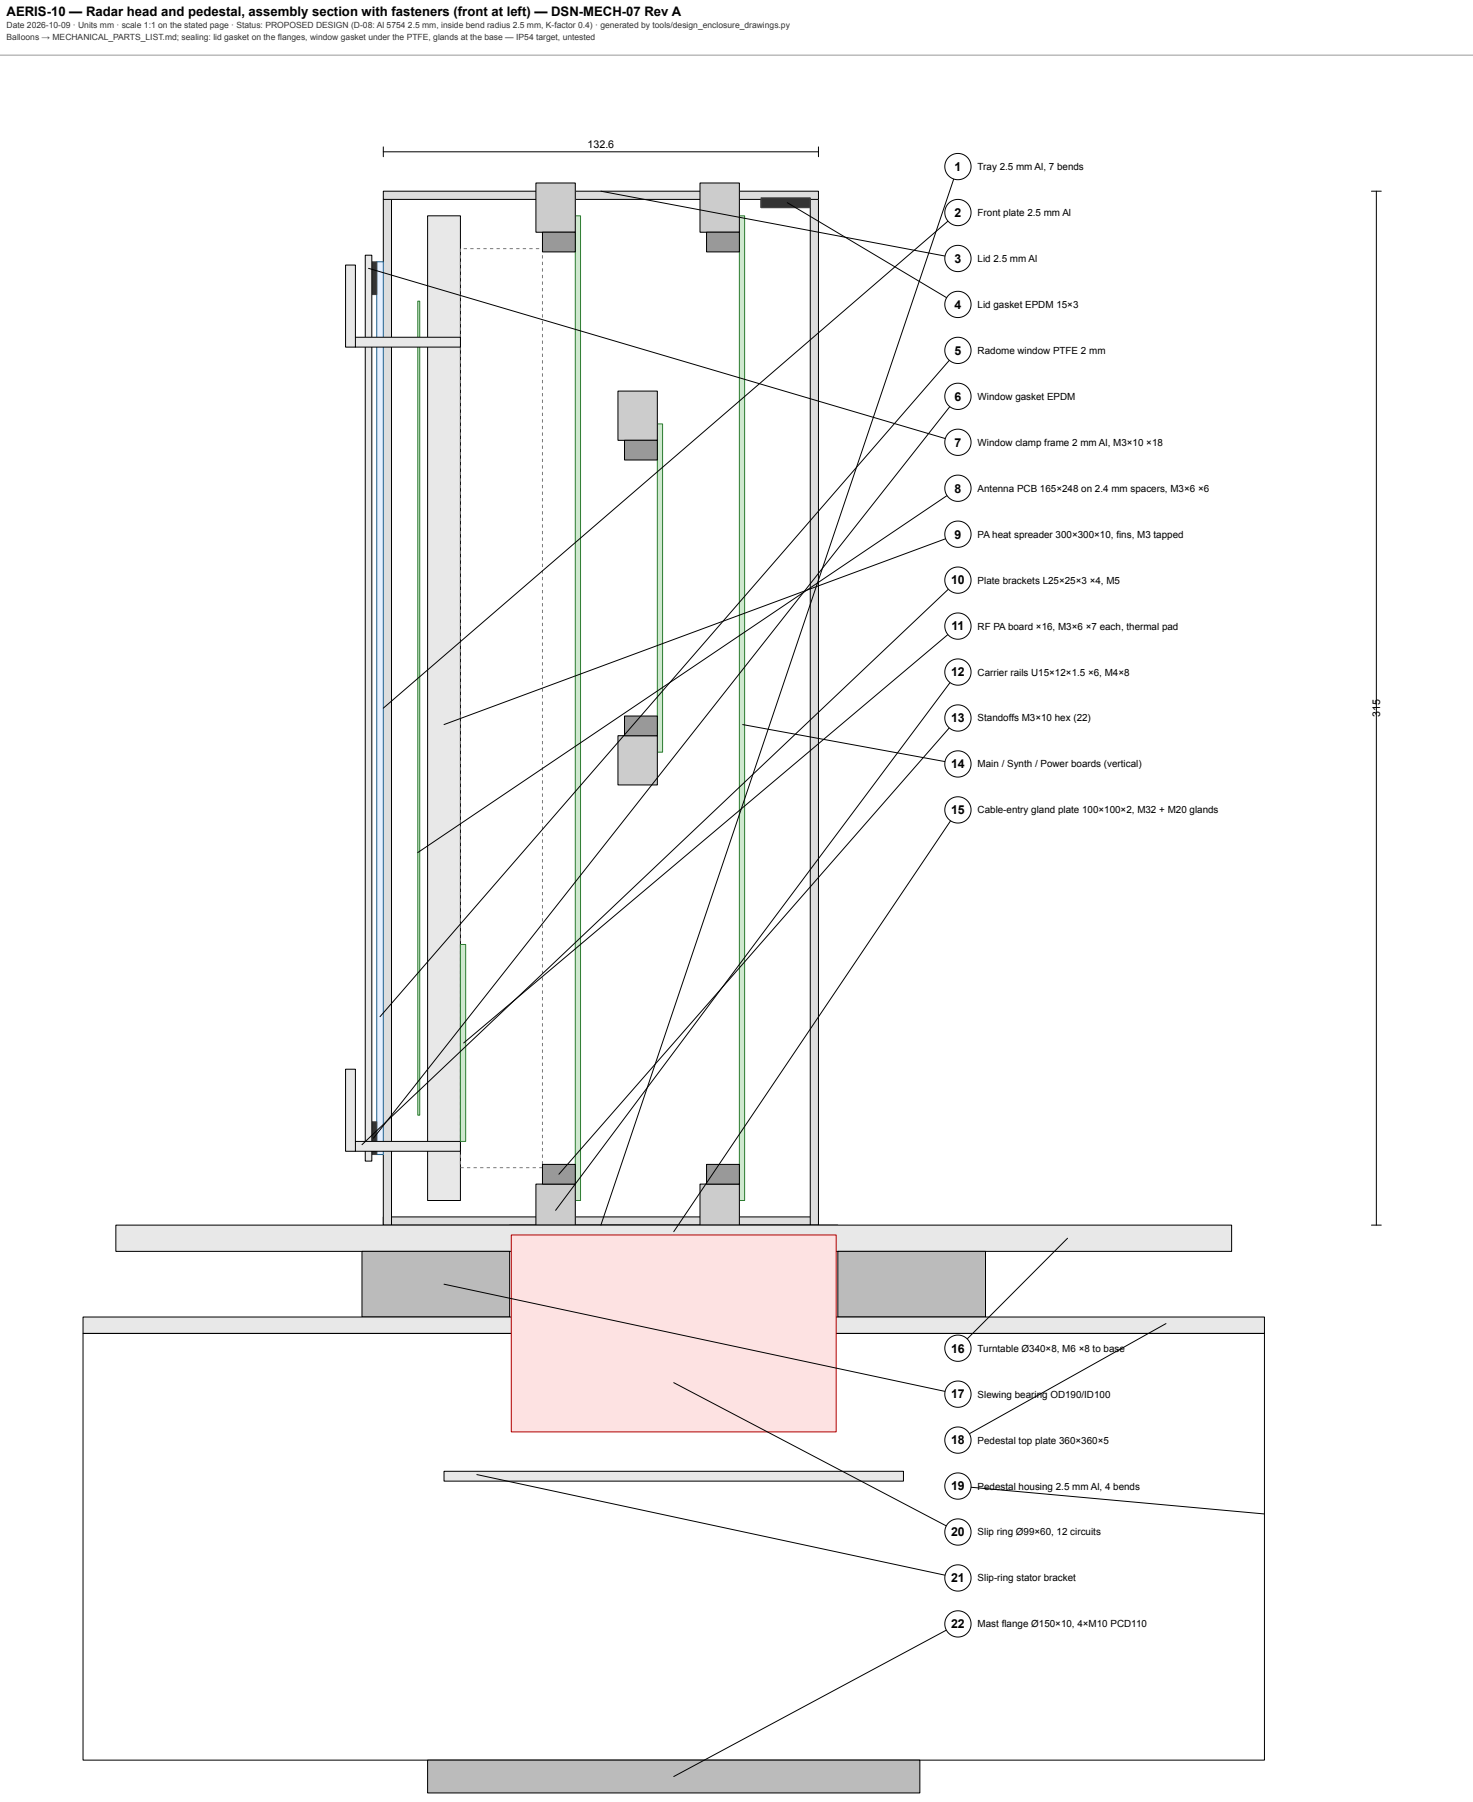
[picture p133: page 2]
10 Plate brackets L25×25×3 ×4, M5; 12 Carrier rails U15×12×1.5 ×6, M4×8; 13 Standoffs M3×10 hex (22); 17 Slewing bearing OD190/ID100; 22 Mast flange Ø150×10, 4×M10 PCD110

Date 2026-10-09 · Units mm · scale 1:1 on the stated page · Status: PROPOSED DESIGN (D-08: Al 5754 2.5 mm, inside bend radius 2.5 mm, K-factor 0.4) · generated by tools/design_enclosure_drawings.py
Balloons → MECHANICAL_PARTS_LIST.md; sealing: lid gasket on the flanges, window gasket under the PTFE, glands at the base — IP54 target, untested

1 Tray 2.5 mm Al, 7 bends

2 Front plate 2.5 mm Al

3 Lid 2.5 mm Al

4 Lid gasket EPDM 15×3

5 Radome window PTFE 2 mm

6 Window gasket EPDM

7 Window clamp frame 2 mm Al, M3×10 ×18

8 Antenna PCB 165×248 on 2.4 mm spacers, M3×6 ×6

9 PA heat spreader 300×300×10, fins, M3 tapped

11 RF PA board ×16, M3×6 ×7 each, thermal pad

14 Main / Synth / Power boards (vertical)

15 Cable-entry gland plate 100×100×2, M32 + M20 glands

16 Turntable Ø340×8, M6 ×8 to base

18 Pedestal top plate 360×360×5

19 Pedestal housing 2.5 mm Al, 4 bends

20 Slip ring Ø99×60, 12 circuits

21 Slip-ring stator bracket
