herasymyuks/PLFM_RADAR-aeris/engineering/DESIGN/ANTENNA/kicad_exports/aeris10_patch_array_top.pdf

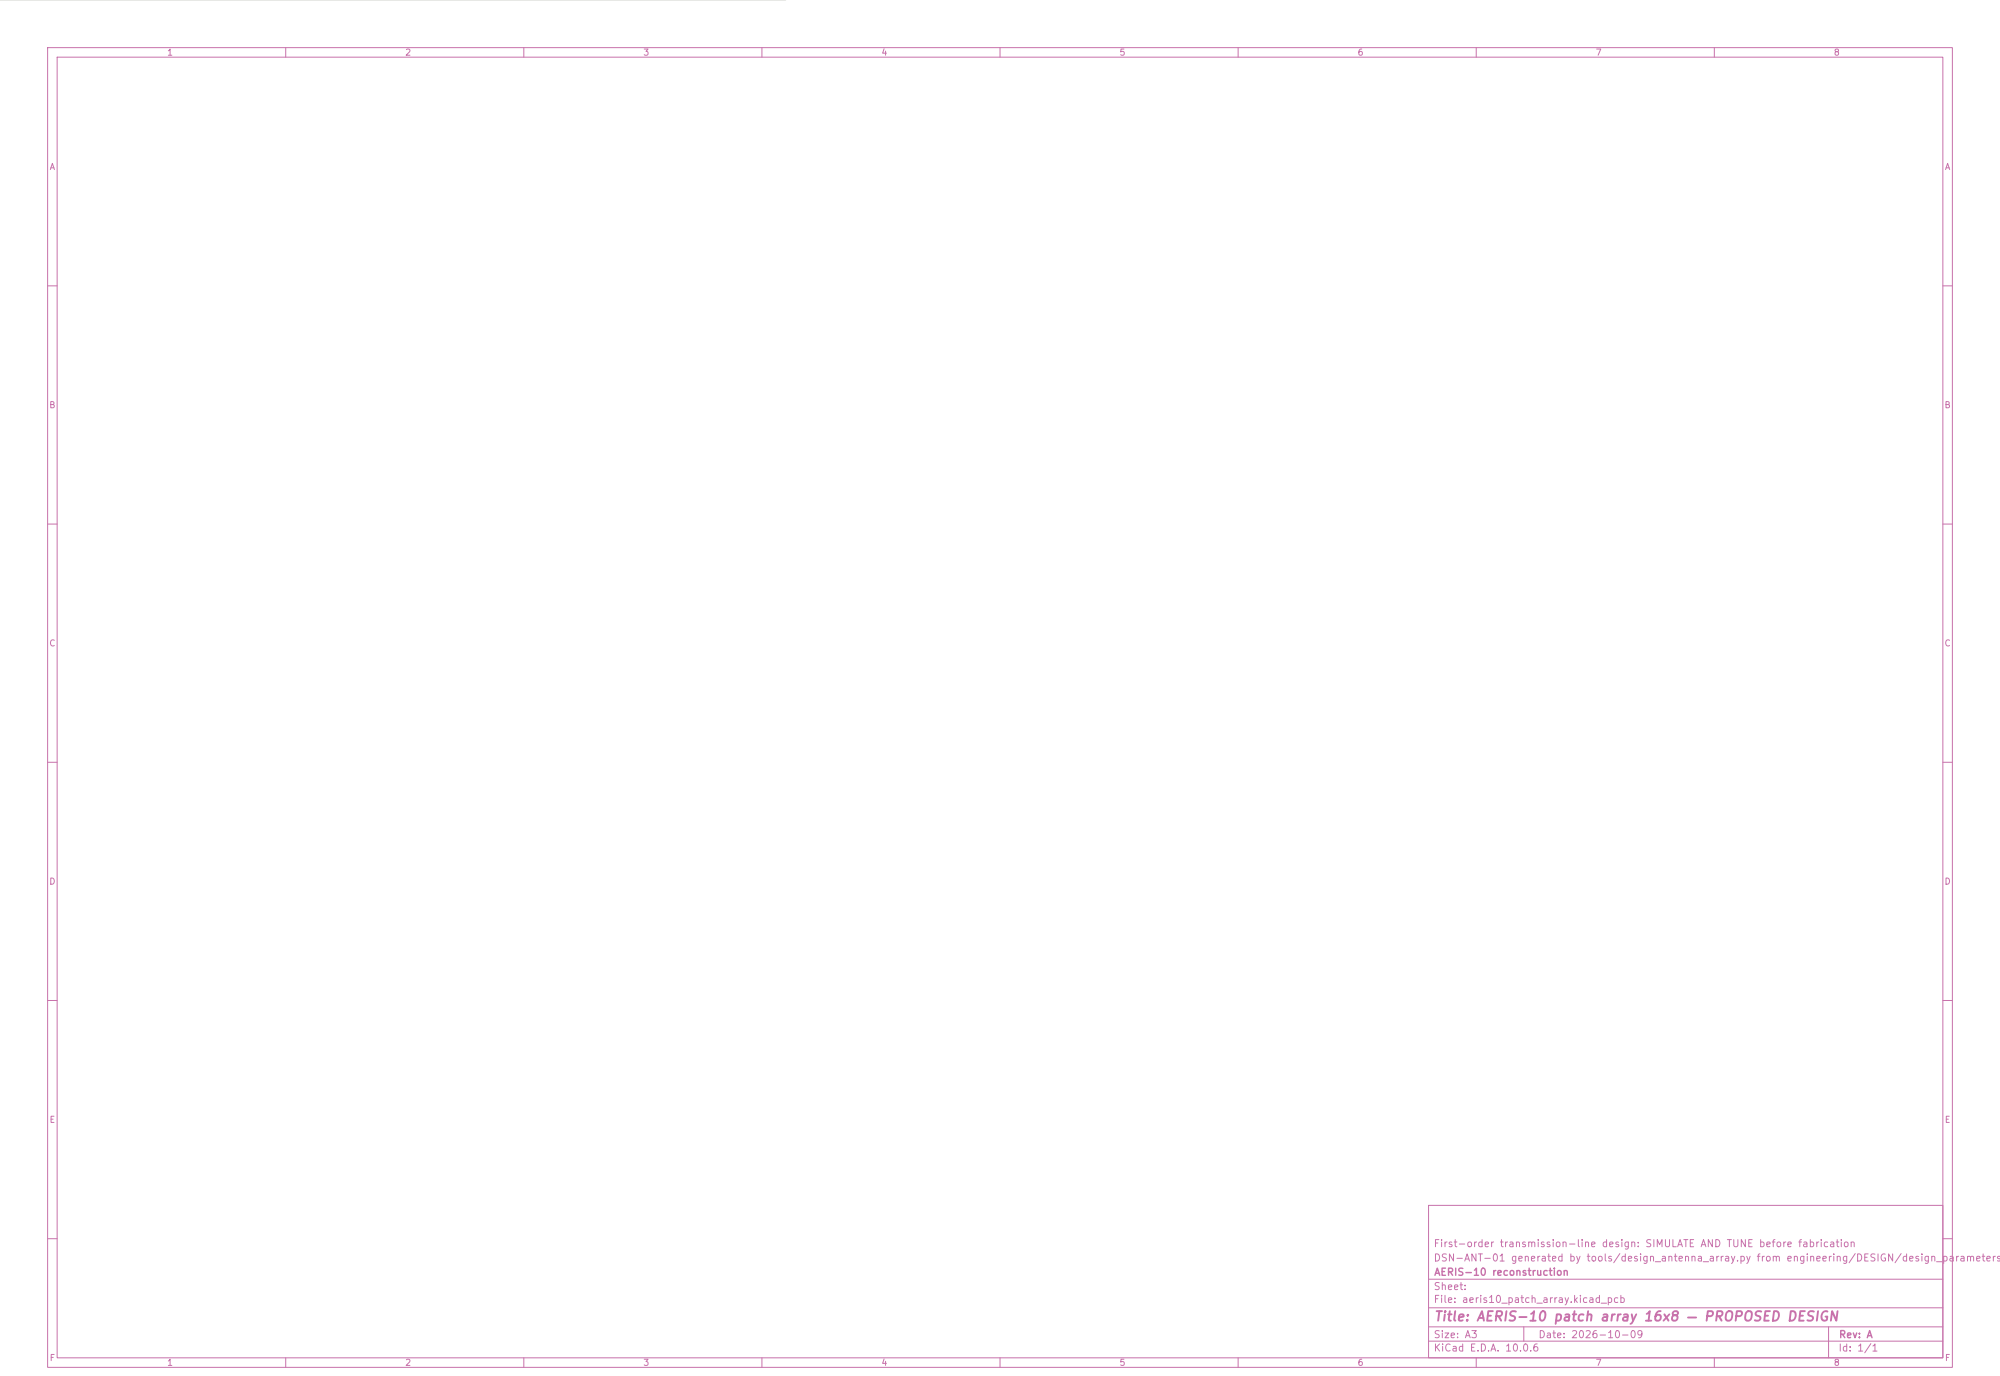
[picture p134: page 1]

First-order transmission-line design: SIMULATE AND TUNE before fabrication
DSN-ANT-01 generated by tools/design_antenna_array.py from engineering/DESIGN/design_parameters.json
AERIS-10 reconstruction
Sheet:
File: aeris10_patch_array.kicad_pcb
Title: AERIS-10 patch array 16x8 — PROPOSED DESIGN

Size: A3 | Rev: A | F Date: 2026-10-09
KiCad E.D.A. 10.0.6 | Id: 1/1
