herasymyuks/PLFM_RADAR-aeris/engineering/DESIGN/MECHANICAL/CAD/aeris10_head_pedestal_iso.pdf

AERIS-10 — Radar head on pedestal, isometric (FreeCAD model DSN-MECH-3D) — PROPOSED DESIGN

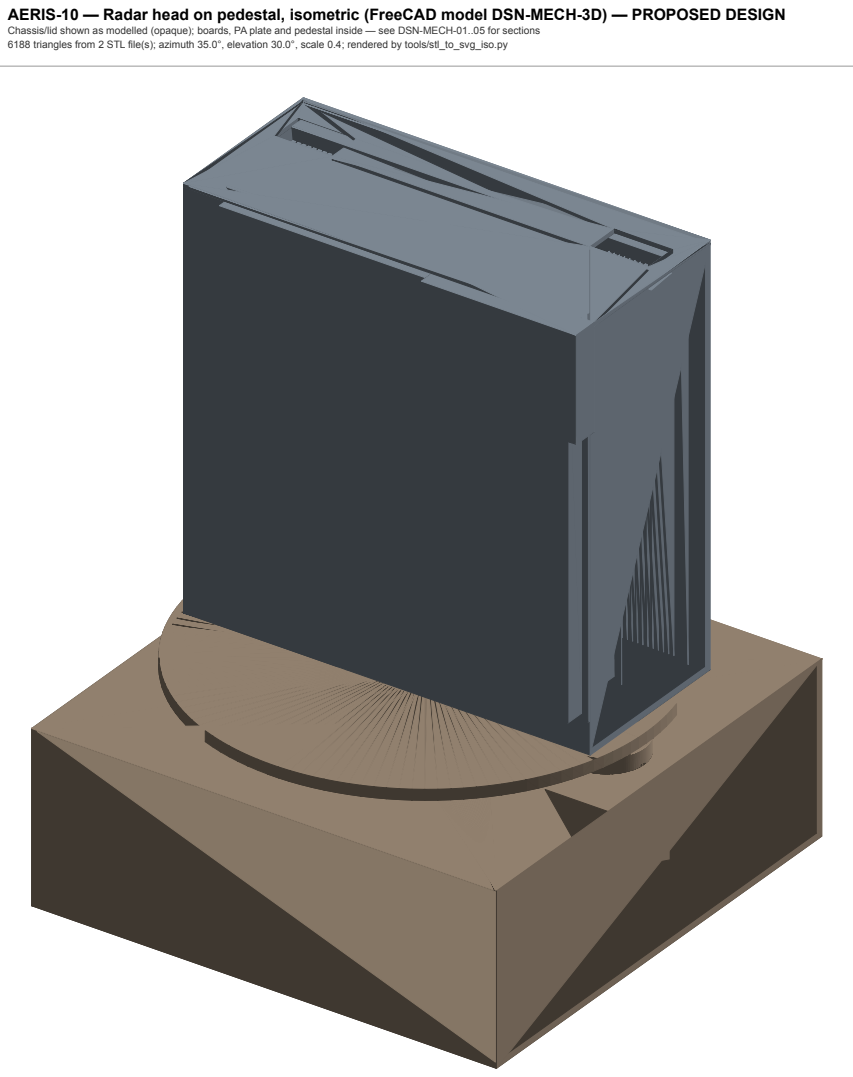
[picture p135: page 1]

Chassis/lid shown as modelled (opaque); boards, PA plate and pedestal inside — see DSN-MECH-01..05 for sections
6188 triangles from 2 STL file(s); azimuth 35.0°, elevation 30.0°, scale 0.4; rendered by tools/stl_to_svg_iso.py
