herasymyuks/PLFM_RADAR-aeris/engineering/DESIGN/MECHANICAL/CAD/aeris10_head_xray_iso.pdf

AERIS-10 — Radar head, x-ray isometric from the rear-left (chassis 25 % opaque) — PROPOSED DESIGN

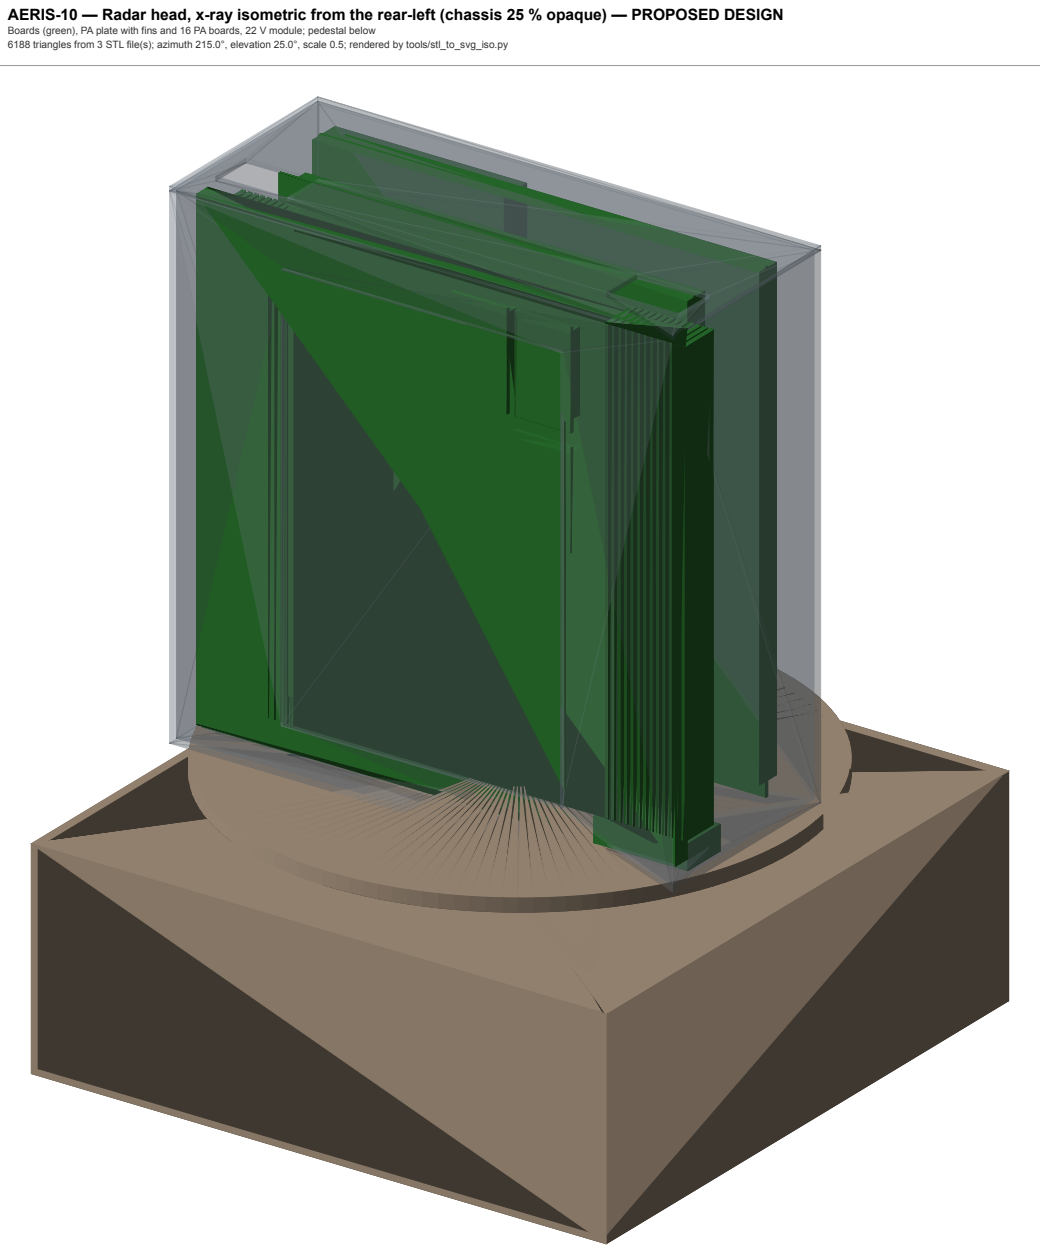
[picture p136: page 1]

Boards (green), PA plate with fins and 16 PA boards, 22 V module; pedestal below
6188 triangles from 3 STL file(s); azimuth 215.0°, elevation 25.0°, scale 0.5; rendered by tools/stl_to_svg_iso.py
