herasymyuks/PLFM_RADAR-aeris/engineering/DESIGN/MECHANICAL/drawings/DSN-MECH-01-05_head_pedestal_drawings.pdf

## AERIS-10 — Radar head, plan section at z = 180 mm (looking down) — DSN-MECH-01 Rev A

## 315 outer width

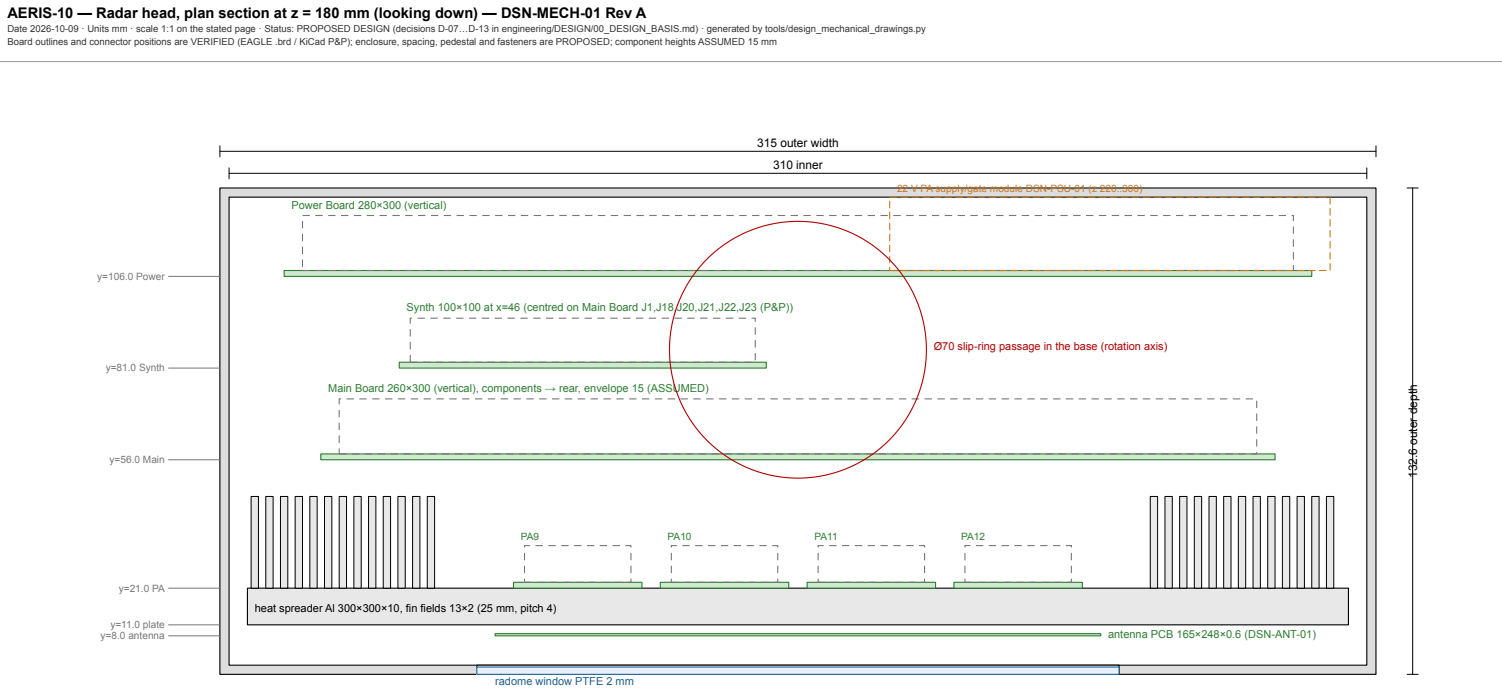
[picture p137: page 1]
310 inner; 132.6 outer depth; y=8.0 antenna; y=11.0 plate; y=56.0 Main; y=81.0 Synth; y=106.0 Power

Date 2026-10-09 · Units mm · scale 1:1 on the stated page · Status: PROPOSED DESIGN (decisions D-07…D-13 in engineering/DESIGN/00_DESIGN_BASIS.md) · generated by tools/design_mechanical_drawings.py
Board outlines and connector positions are VERIFIED (EAGLE .brd / KiCad P&P); enclosure, spacing, pedestal and fasteners are PROPOSED; component heights ASSUMED 15 mm

22 V PA supply/gate module DSN-PSU-01 (z 220..300)

Power Board 280×300 (vertical)

Synth 100×100 at x=46 (centred on Main Board J1,J18,J20,J21,J22,J23 (P&P))

Ø70 slip-ring passage in the base (rotation axis)

Main Board 260×300 (vertical), components → rear, envelope 15 (ASSUMED)

heat spreader Al 300×300×10, fin fields 13×2 (25 mm, pitch 4)

antenna PCB 165×248×0.6 (DSN-ANT-01)

radome window PTFE 2 mm

## AERIS-10 — Radar head, front elevation (antenna side) — DSN-MECH-02 Rev A

315

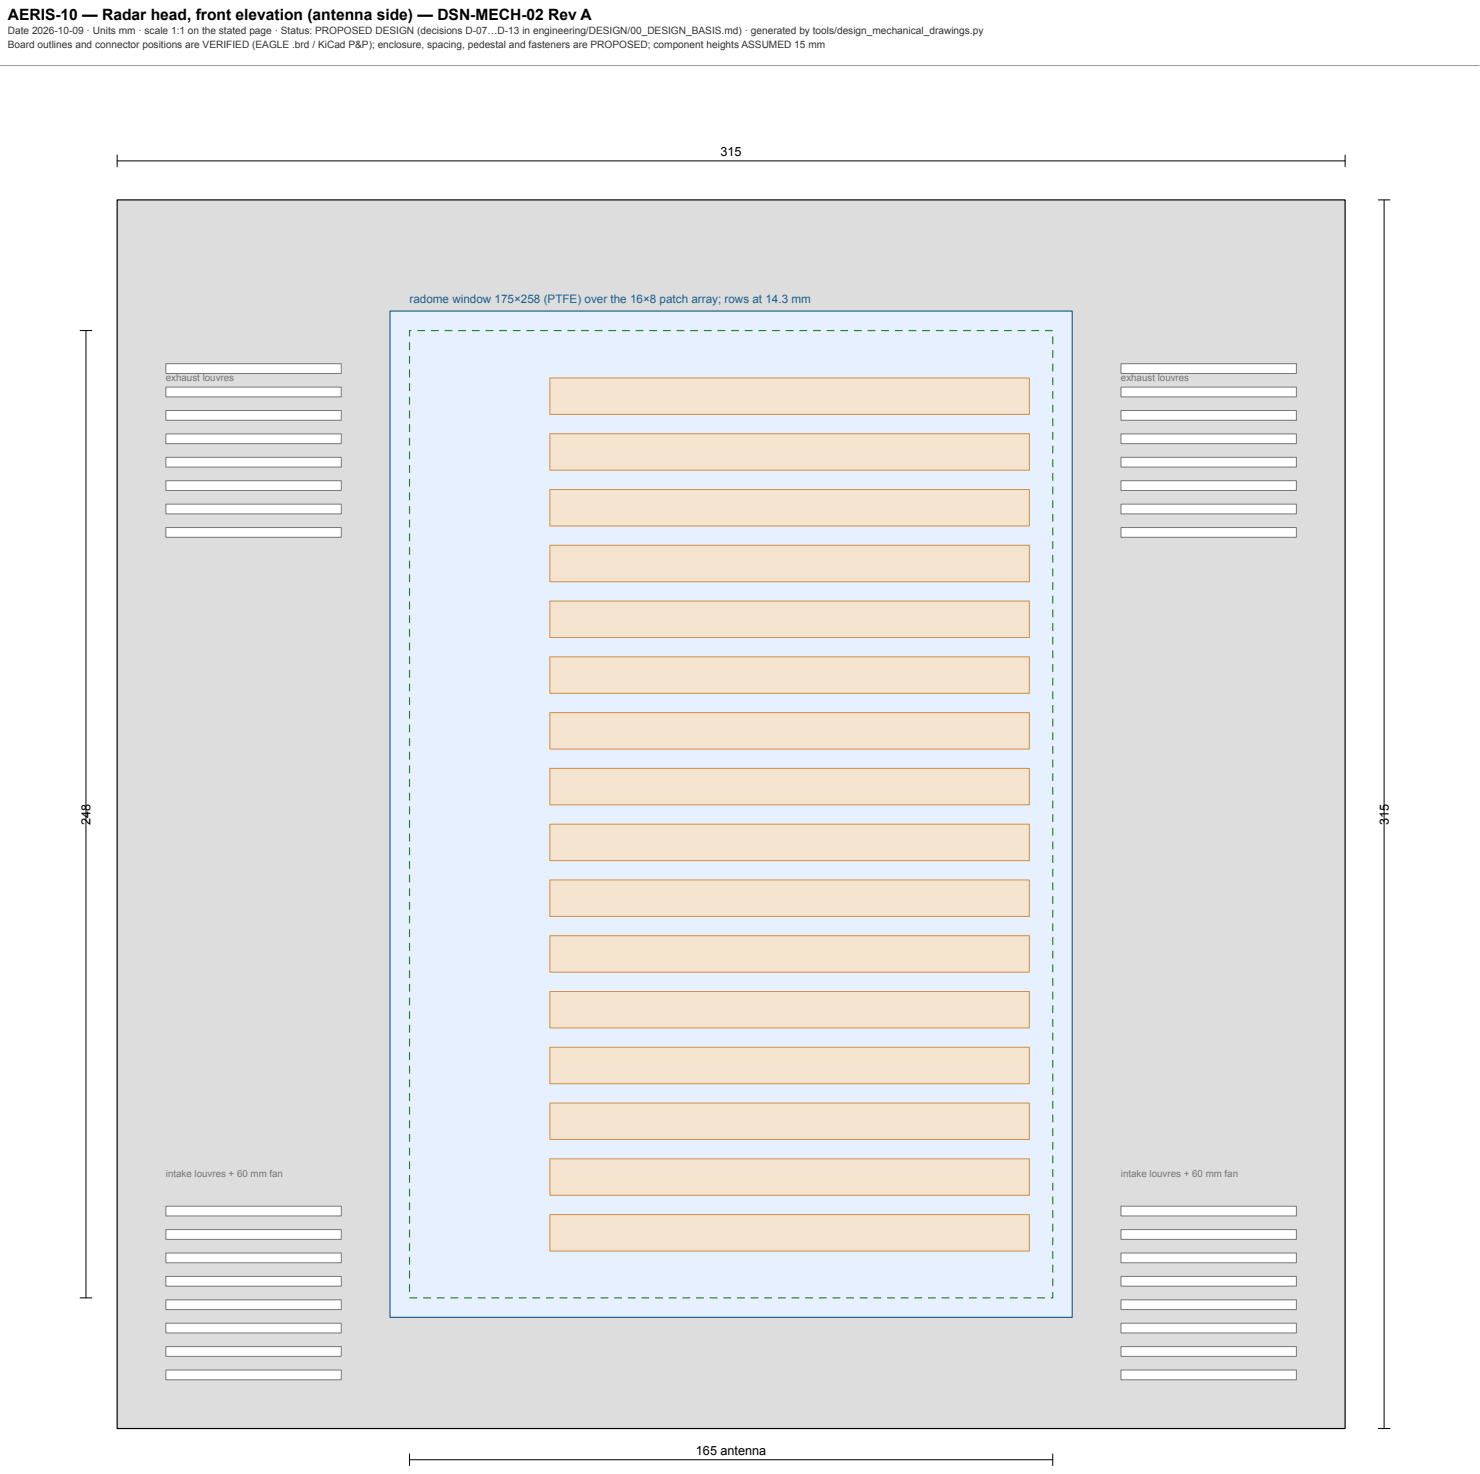
[picture p138: page 2]
exhaust louvres; 165 antenna

radome window 175×258 (PTFE) over the 16×8 patch array; rows at 14.3 mm

intake louvres + 60 mm fan

## AERIS-10 — Radar head and pedestal, side section (front at left) — DSN-MECH-03 Rev A

## 132.6 head depth

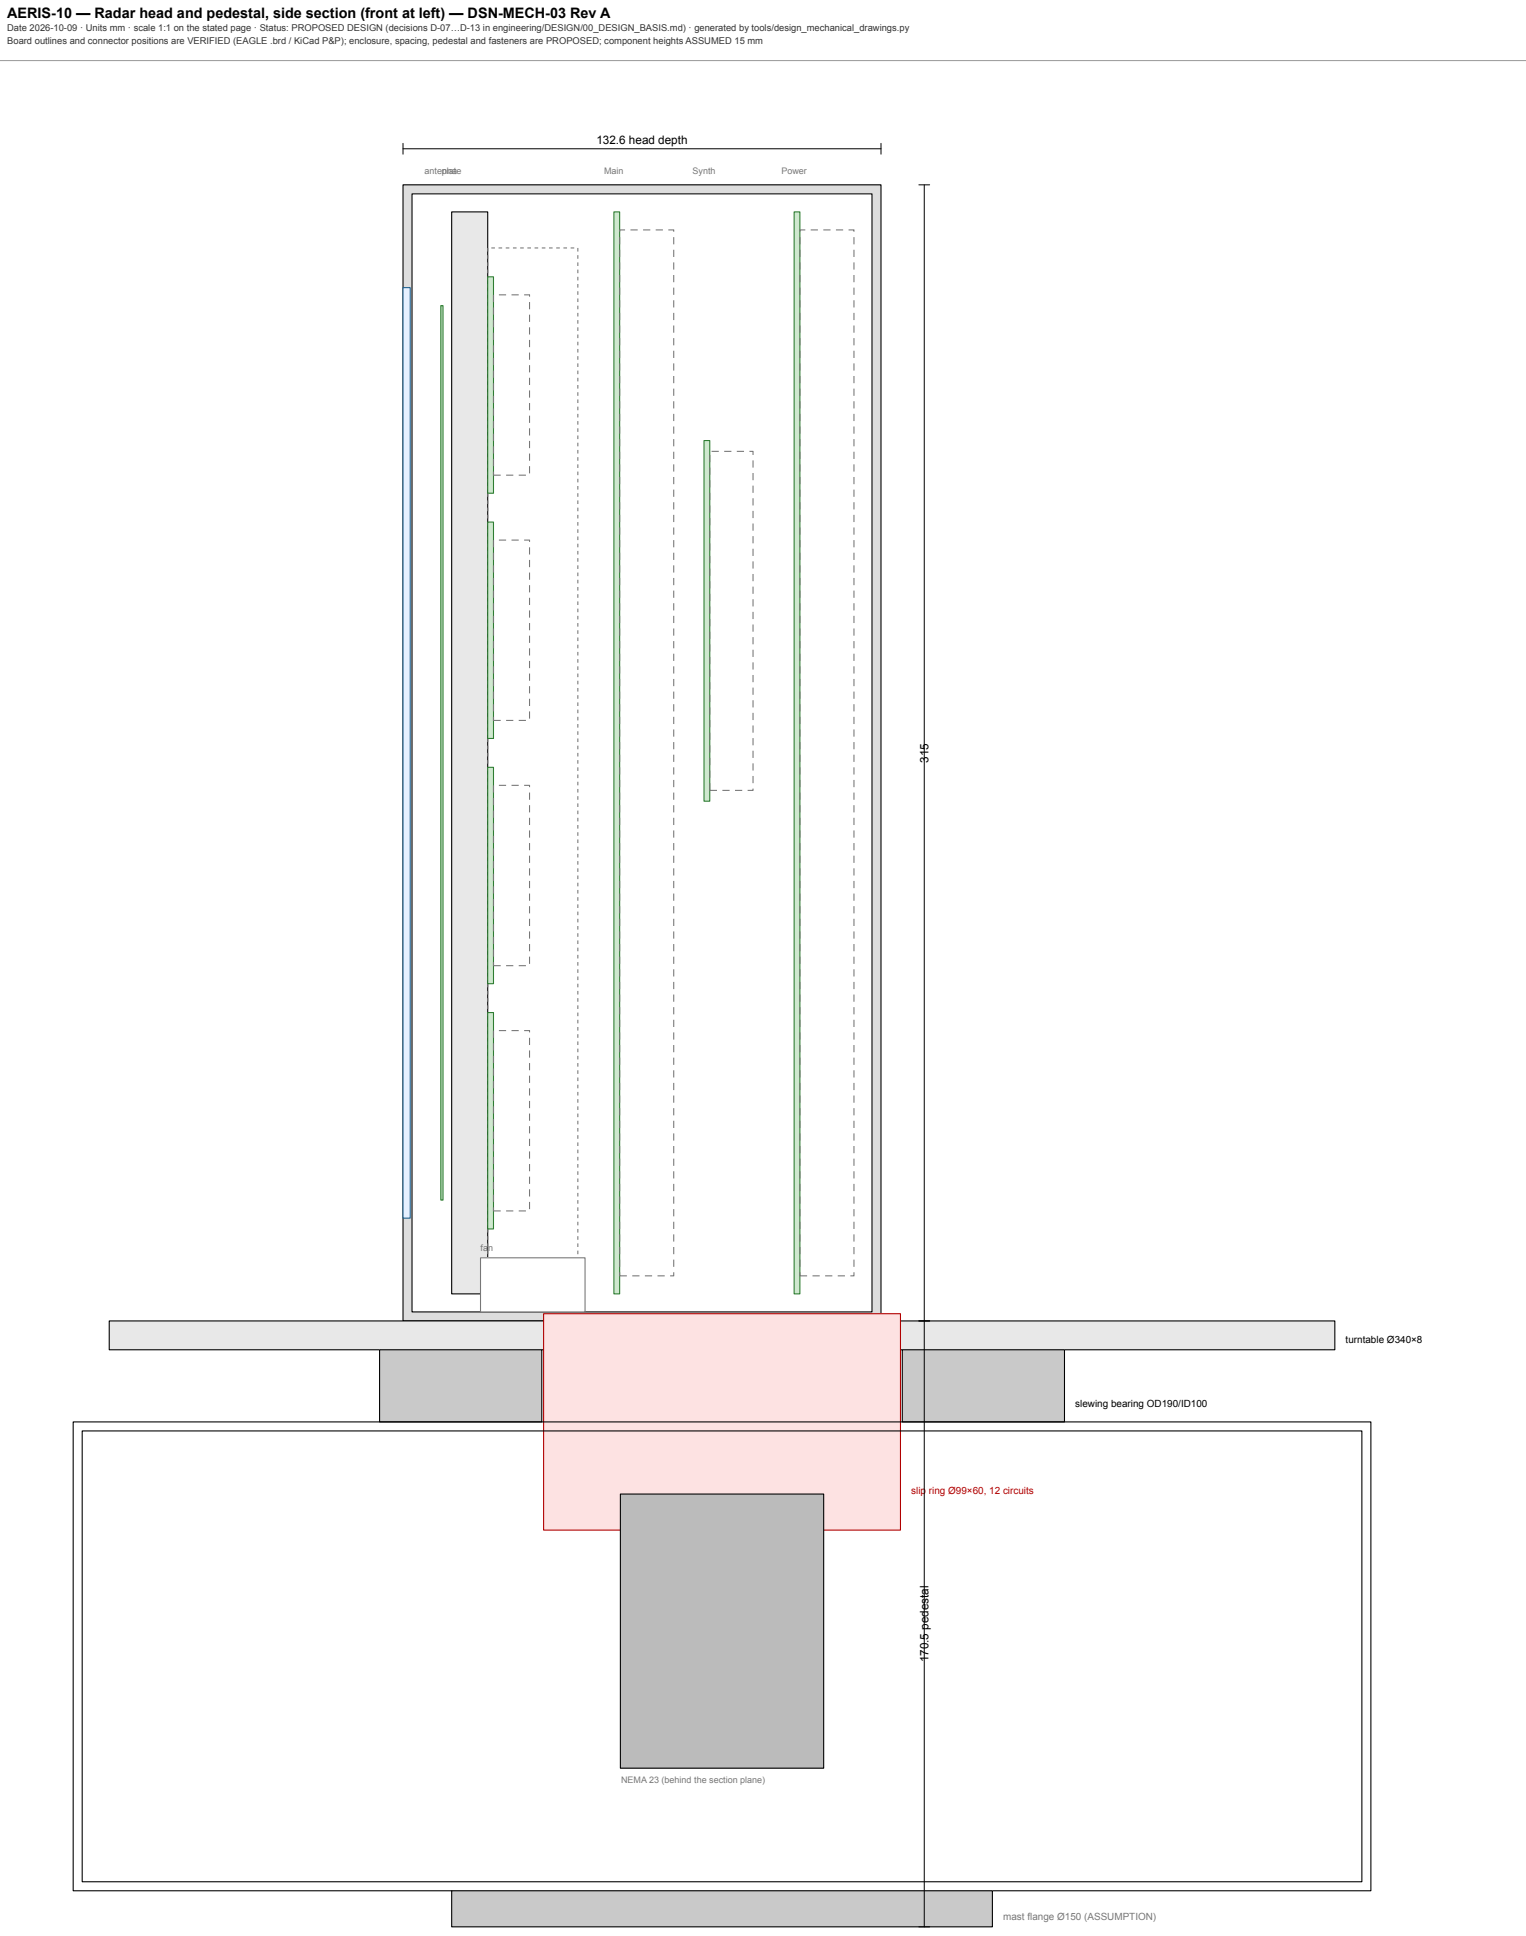
[picture p139: page 3]
fan; turntable Ø340×8; slewing bearing OD190/ID100; 315 170.5 pedestal; antepnlnaate; Main; Synth; Power

slip ring Ø99×60, 12 circuits

NEMA 23 (behind the section plane)

mast flange Ø150 (ASSUMPTION)

AERIS-10 — Internal layout, each tier seen from the rear, with connector positions — DSN-MECH-04 Rev A

Board outlines and connector positions are VERIFIED (EAGLE .brd / KiCad P&P); enclosure, spacing, pedestal and fasteners are PROPOSED; component heights ASSUMED 15 mm · connector refs: J/X/JP/SV from the P&P files

## Tier 1 — PA heat spreader (rear face): 16 PA boards + fin fields

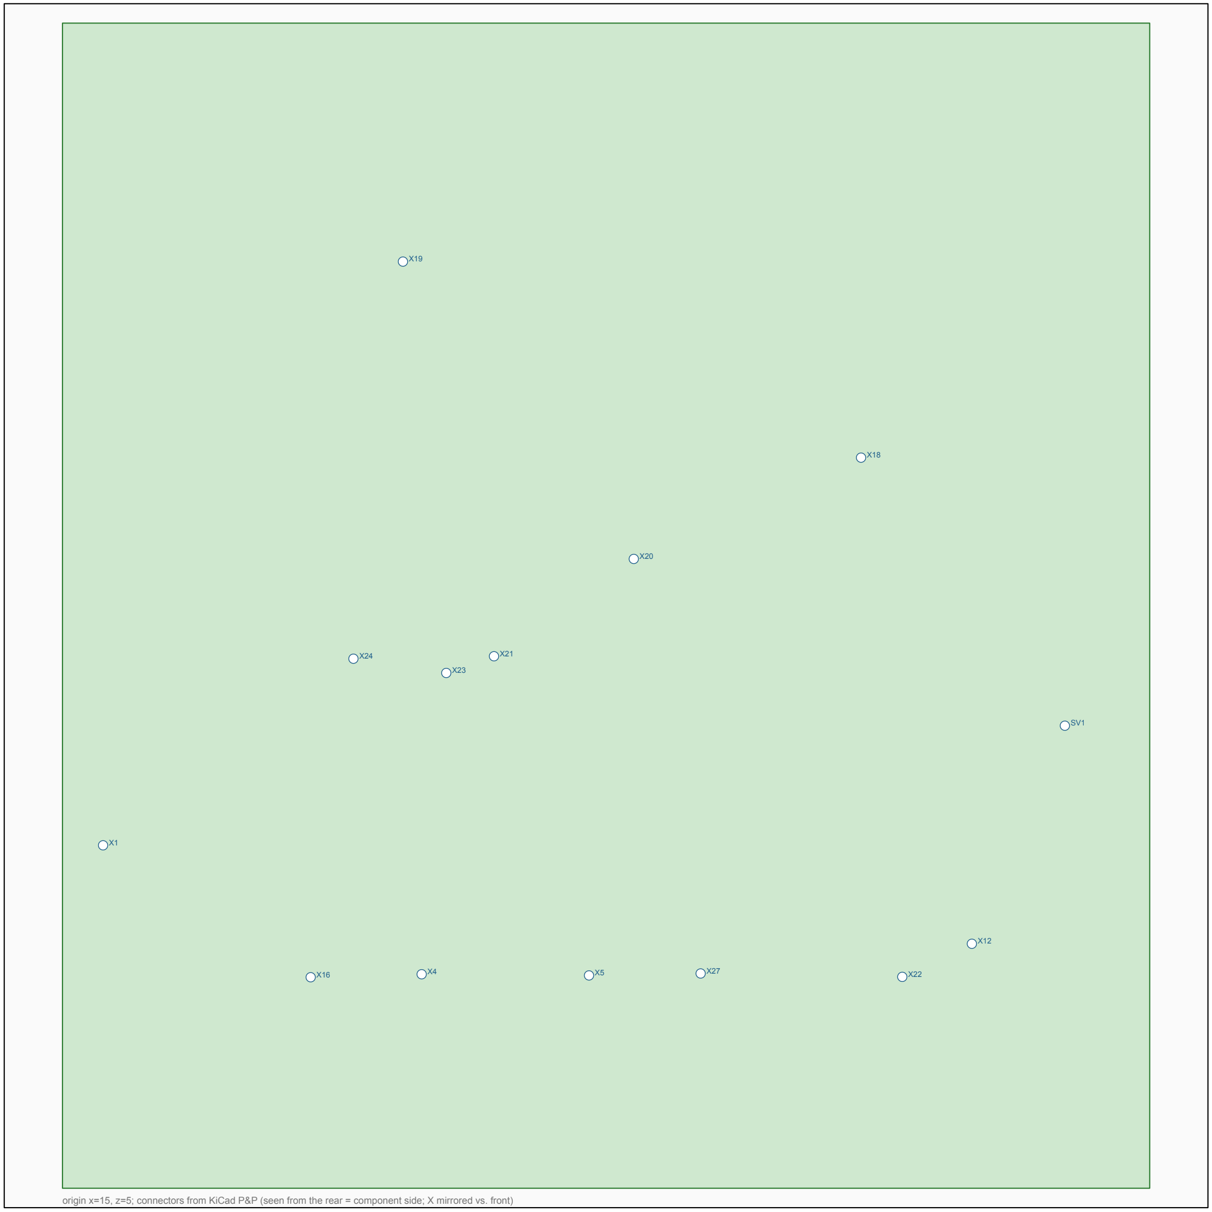
[picture p140: figure]

fins | fins
PA1 | PA2 | PA3 | PA4
PA5 | PA6 | PA7 | PA8
PA9 | PA10 | PA11 | PA12
PA13 | PA14 | PA15 | PA16

## 40 pitch

68

## Tier 2 — Main Board (rear = component side)

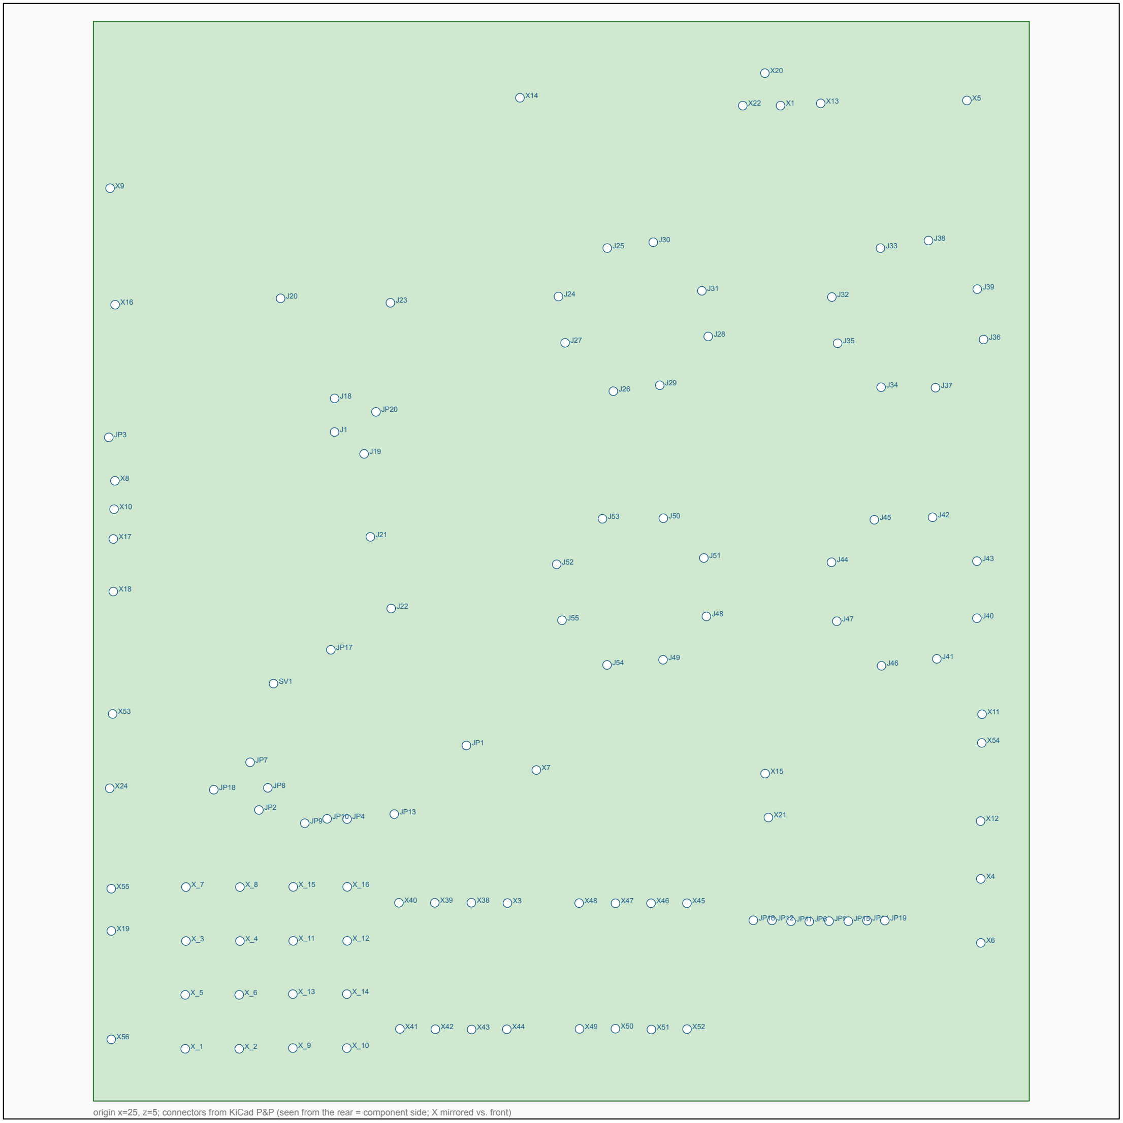
[picture p141: figure]

origin x=25, z=5; connectors from KiCad P&P (seen from the rear = component side; X mirrored vs. front)

## Tier 3 — Frequency Synthesizer

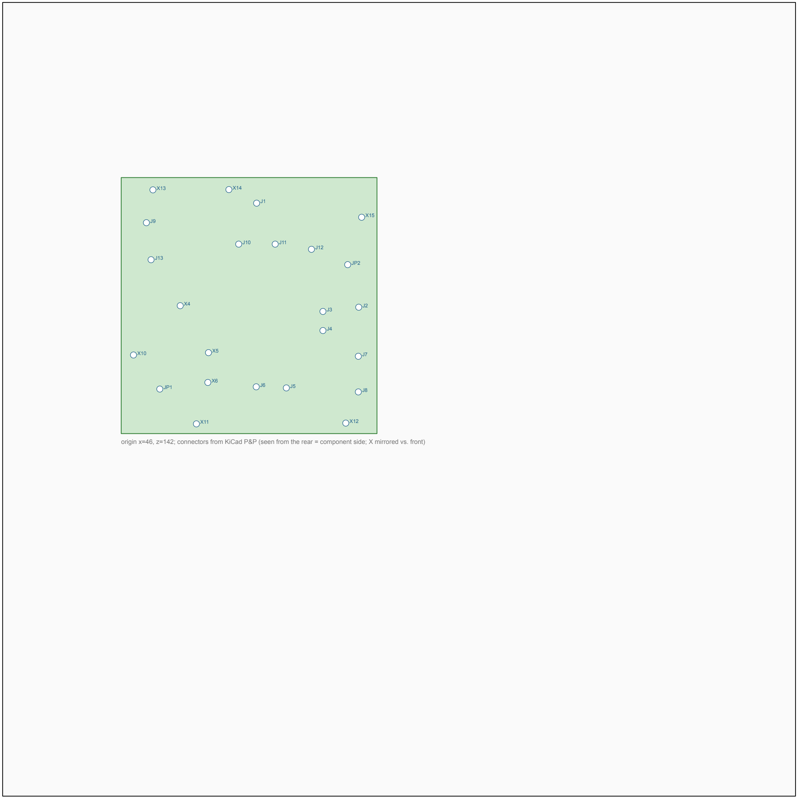
[picture p142: figure]

origin x=46, z=142; connectors from KiCad P&P (seen from the rear = component side; X mirrored vs. front)

## Tier 4 — Power Board

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
origin x=15, z=5; connectors from KiCad P&P (seen from the rear = component side; X mirrored vs. front)

## AERIS-10 — Pedestal plan (turntable removed) — DSN-MECH-05 Rev A

Pedestal is PROPOSED (D-12, D-13); stepper/driver from firmware + xlsx; bearing, pulleys, slip ring are generic part classes to be selected

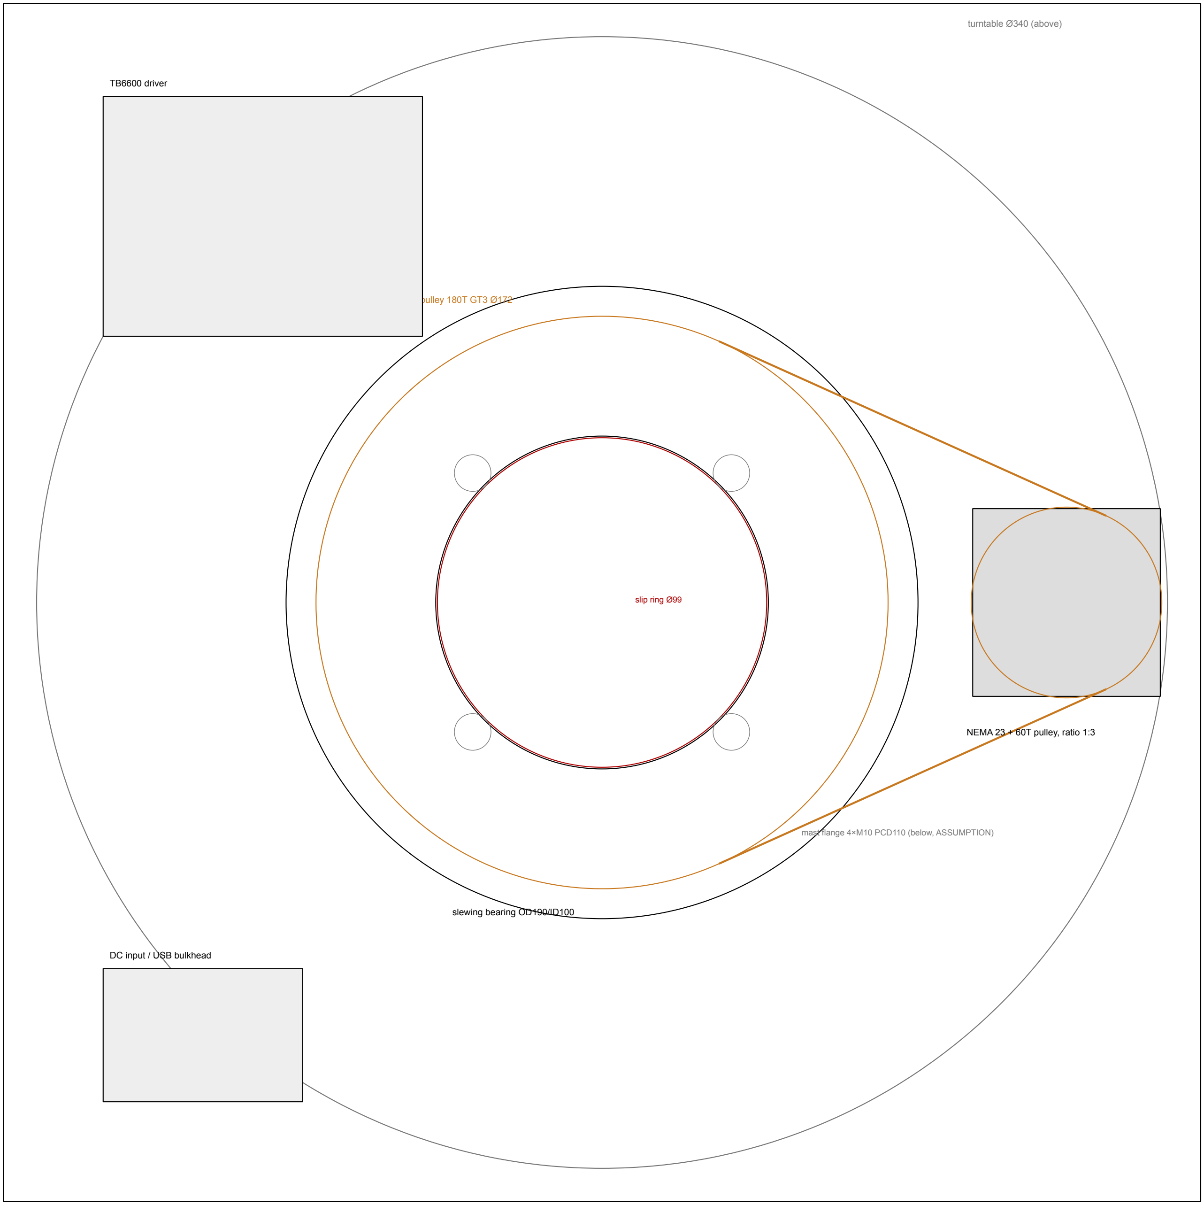
[picture p143: figure]
turntable Ø340 (above); ring pulley 180T GT3 Ø172; NEMA 23 + 60T pulley, ratio 1:3; slewing bearing OD190/ID100; slip ring Ø99; TB6600 driver; DC input / USB bulkhead

mast flange 4×M10 PCD110 (below, ASSUMPTION)

360

firmware change required with ratio 1:3: Stepper_steps = 600 (main.cpp:195) so that 4×3 = 12 pulses give 7.2° at the table; TB6600 at full step
