herasymyuks/PLFM_RADAR-aeris/engineering/ELECTRICAL/schematics/FREQUENCY_SYNTHESIZER/FREQUENCY_SYNTHESIZER_schematic.pdf

## AERIS-10 — FREQUENCY_SYNTHESIZER — Schematic sheet 1/1

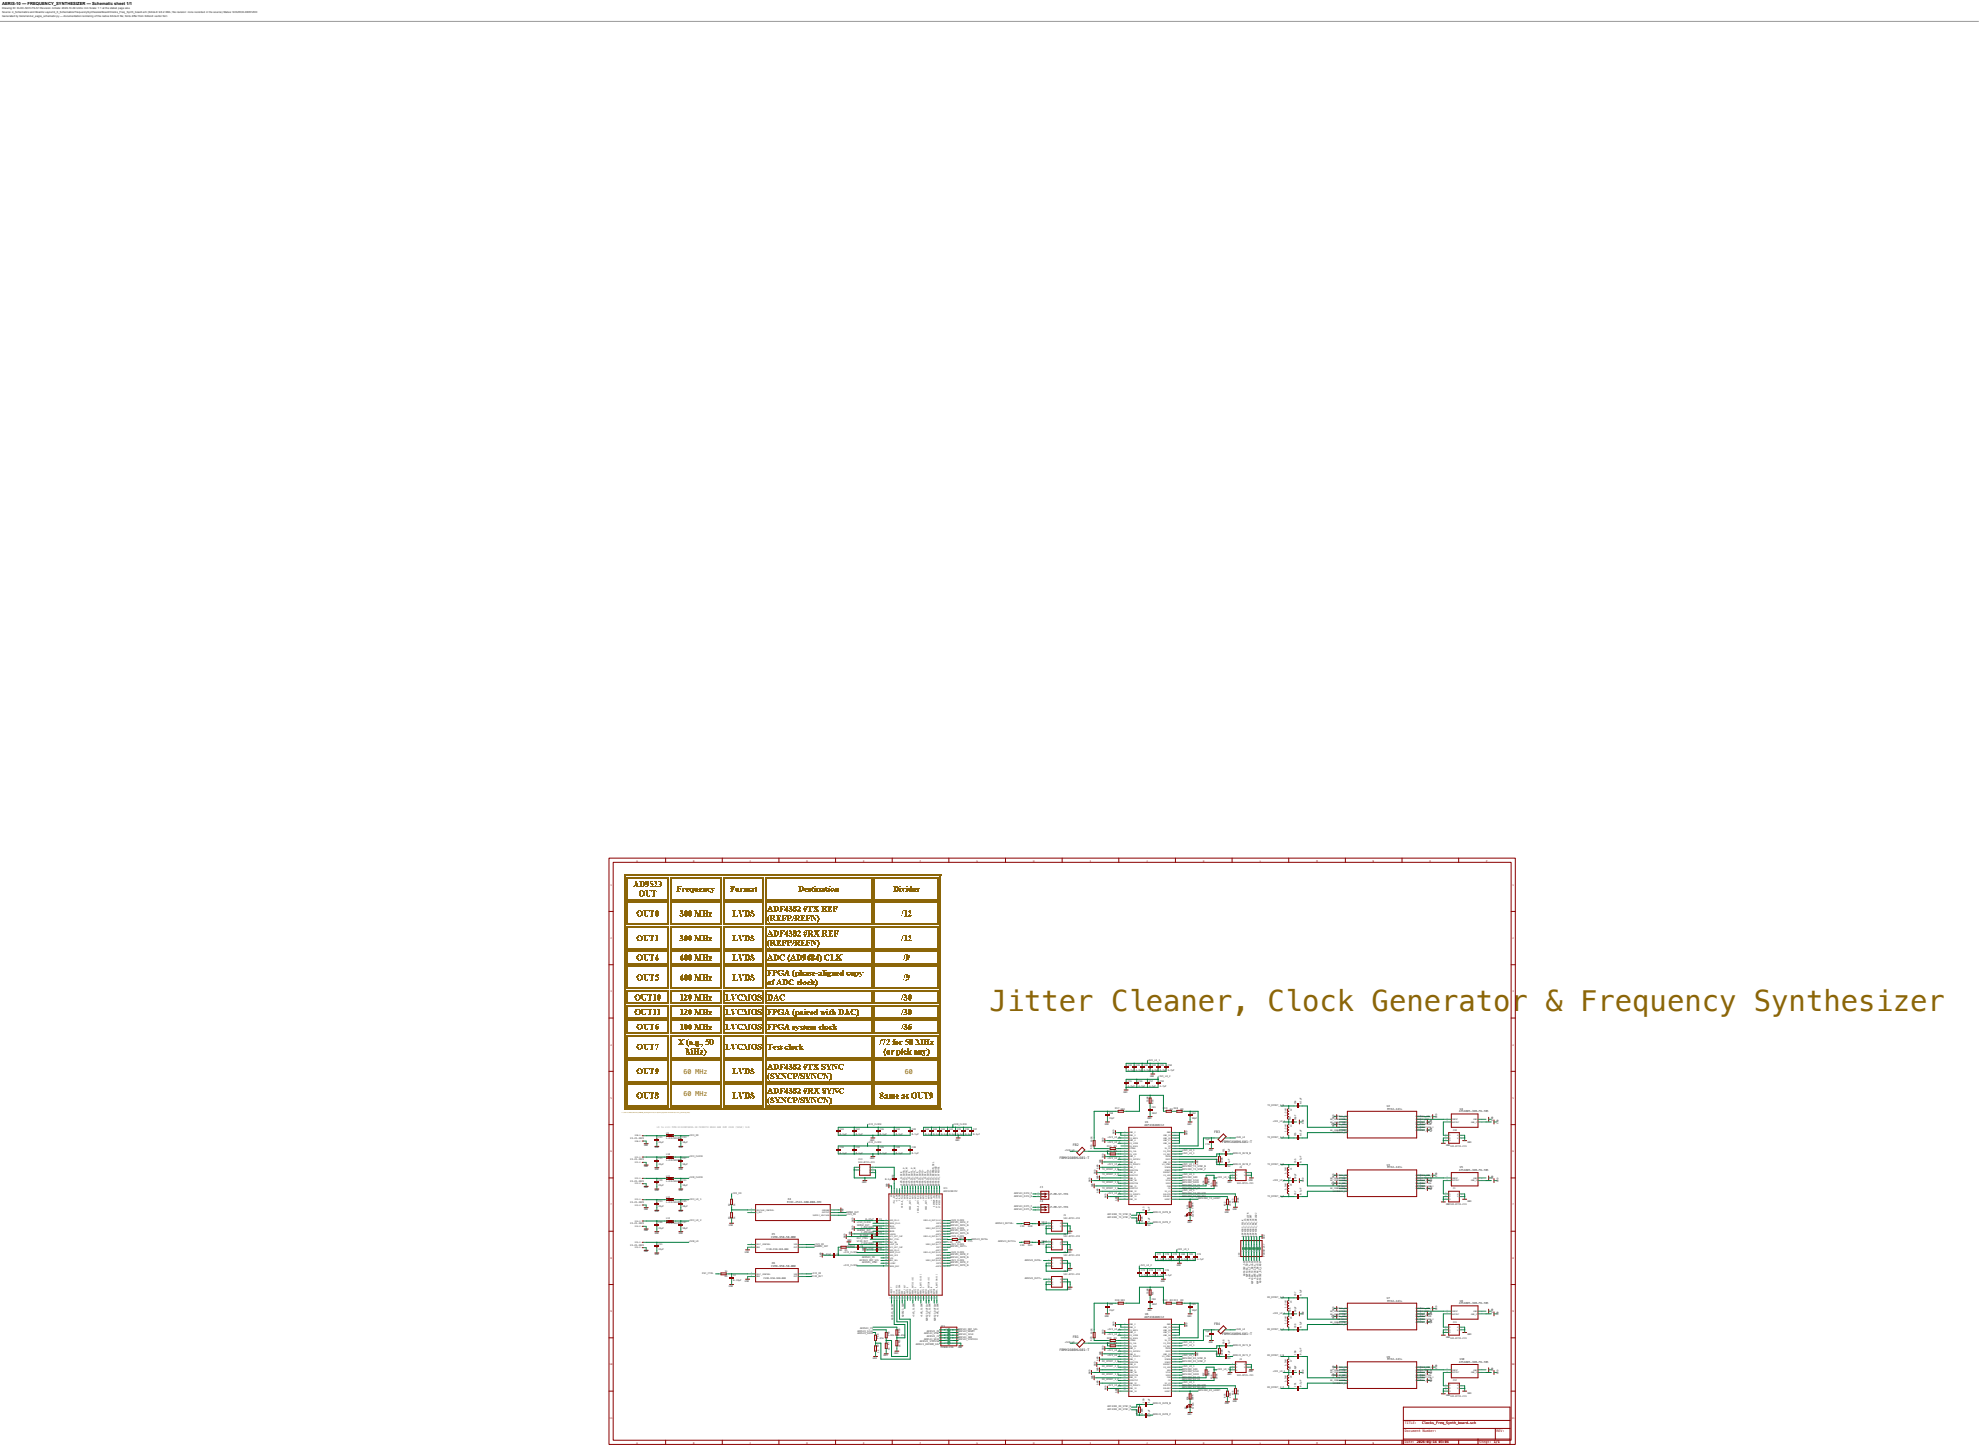
[picture p144: page 1]

Drawing ID: ELEC-SCH-FS-S1 Revision: A Date: 2026-10-09 Units: mm Scale: 1:1 at the stated page size
Source: 4_Schematics and Boards Layout/4_6_Schematics/FrequencySynthesizerBoard/Clocks_Freq_Synth_board.sch (EAGLE 9.6.2 XML; file revision: none recorded in the source) Status: SOURCE-DERIVED
Generated by tools/render_eagle_schematic.py — documentation rendering of the native EAGLE file; fonts differ from EAGLE vector font.

Jitter Cleaner, Clock Generator & Frequency Synthesizer

C:/Users/ASUS/Desktop/RADAR_V5/EagleFiles/FrequencySynthesizerBoard/clock_planning.bmp

L9 to L13: MPN HI2220P601R-10 FERRITE BEAD 600 OHM 2220 (5650) 1LN
