herasymyuks/PLFM_RADAR-aeris/engineering/ELECTRICAL/schematics/MAIN_BOARD/MAIN_BOARD_schematic.pdf

# AERIS-10 — MAIN_BOARD — Schematic sheet 1/4

Drawing ID: ELEC-SCH-MB-S1 Revision: A Date: 2026-10-09 Units: mm Scale: 1:1 at the stated page size

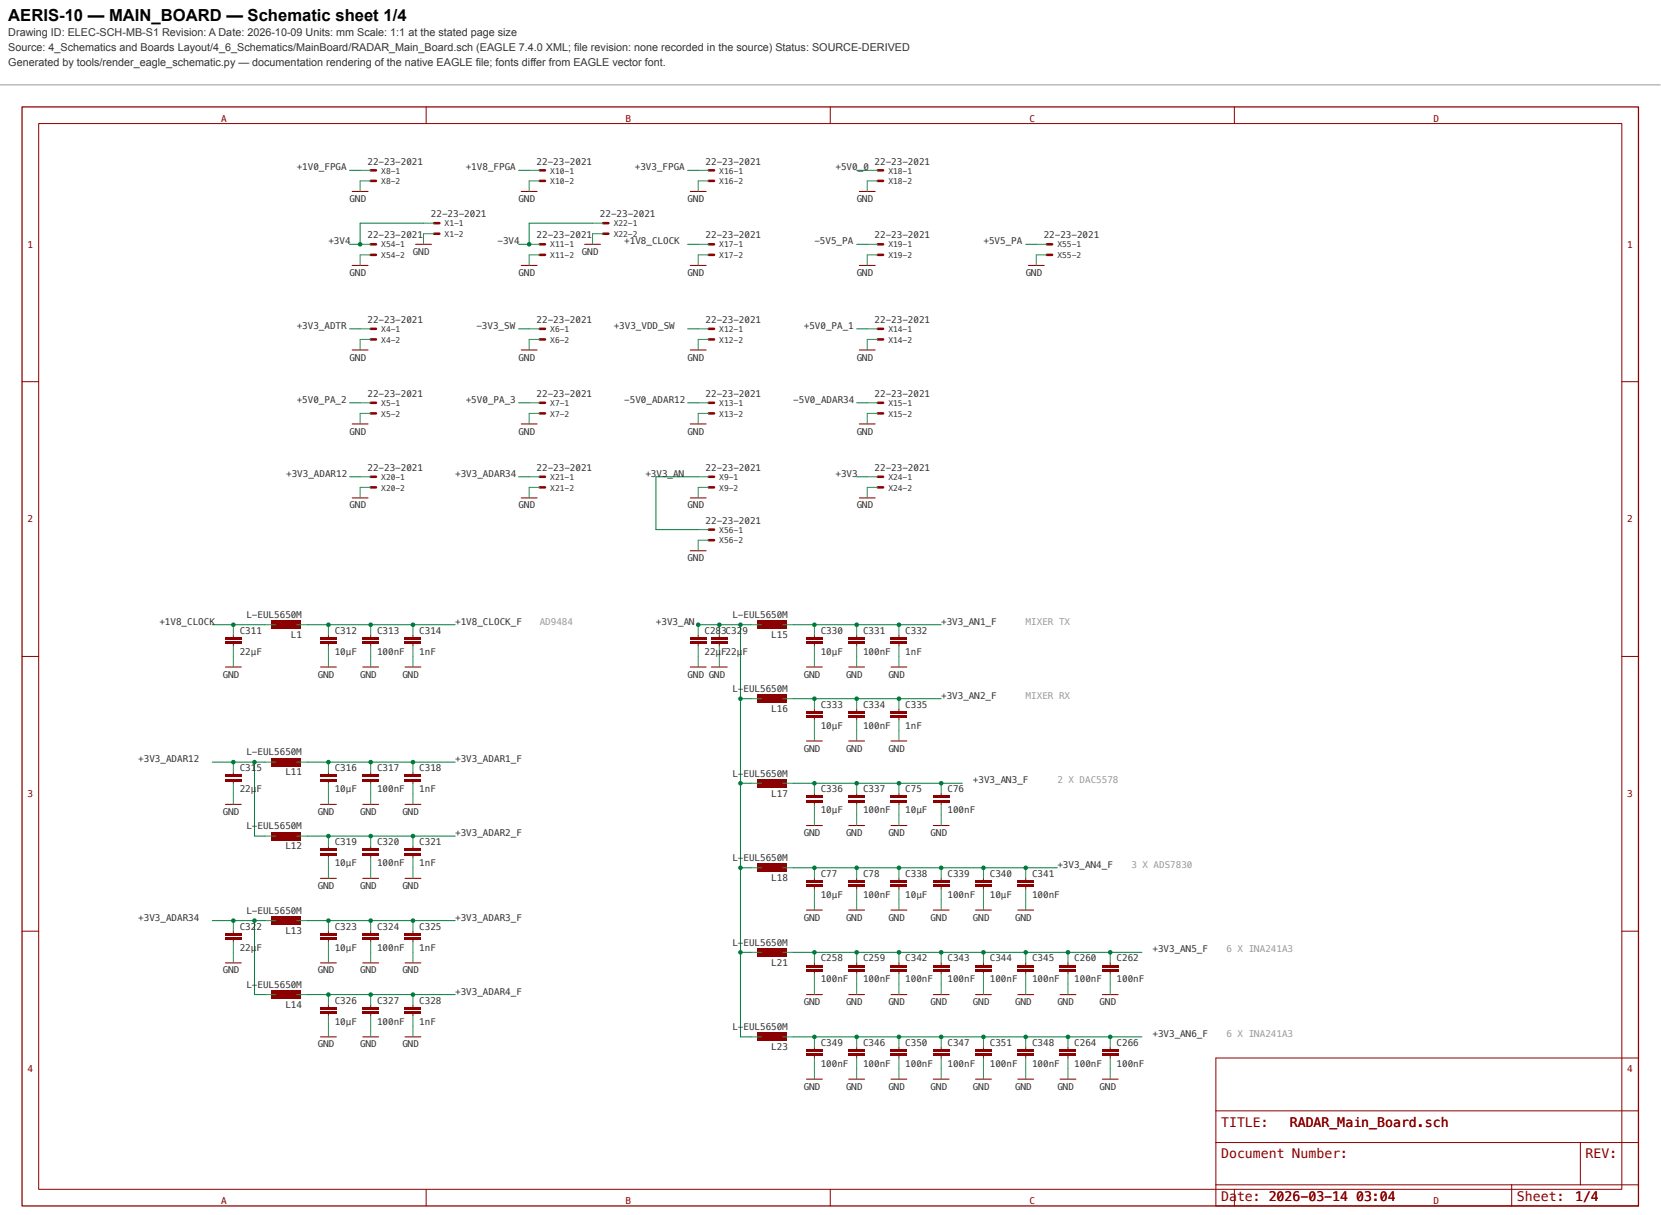
[picture p145: page 1]

Source: 4_Schematics and Boards Layout/4_6_Schematics/MainBoard/RADAR_Main_Board.sch (EAGLE 7.4.0 XML; file revision: none recorded in the source) Status: SOURCE-DERIVED
Generated by tools/render_eagle_schematic.py — documentation rendering of the native EAGLE file; fonts differ from EAGLE vector font.

Document Number: | REV:

Date: 2026-03-14 03:04 | | Sheet: 1/4

# AERIS-10 — MAIN_BOARD — Schematic sheet 2/4

Drawing ID: ELEC-SCH-MB-S2 Revision: A Date: 2026-10-09 Units: mm Scale: 1:1 at the stated page size

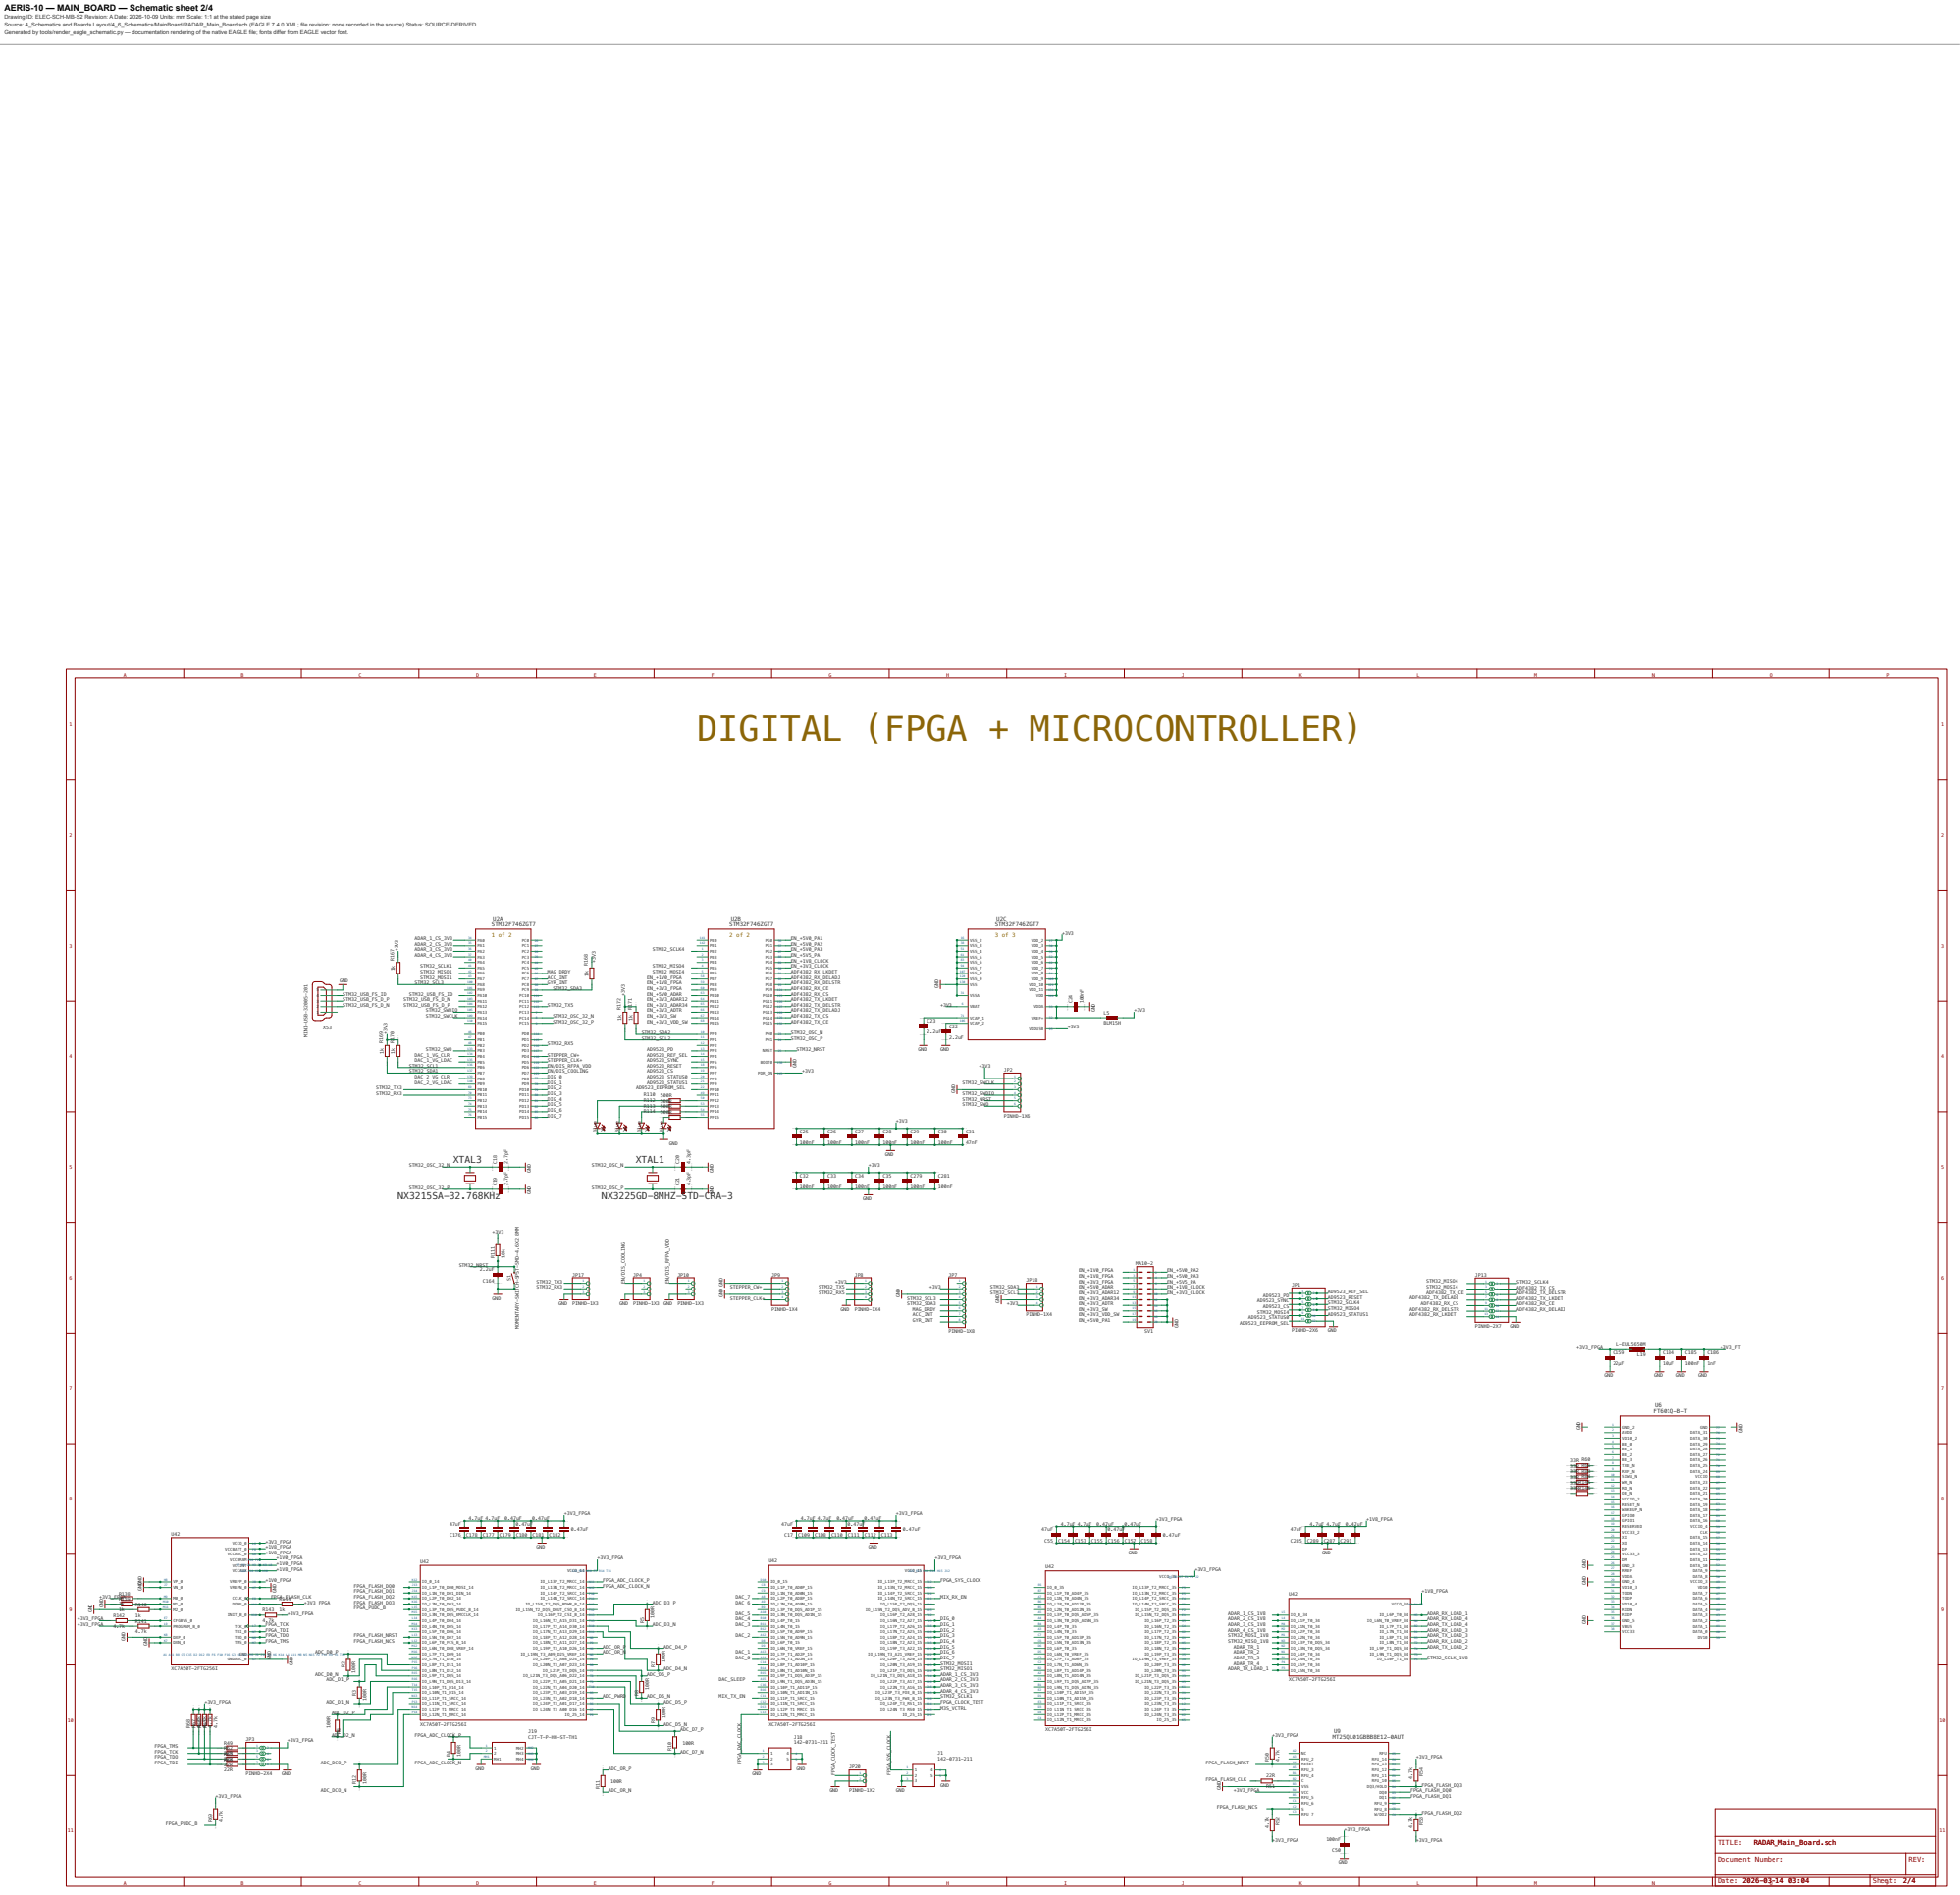
[picture p146: page 2]

MOMENTARY-SWITCH-SPST-SMD-4.6X2.8MM

SpiceOrder 1 SpiceOrder 2

Document Number: | REV:

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
## win

## g ID: E

S

S

3

R

e

## visio

n: A

a

t

e: 2

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
## nit

s: m

m

S

c

## ale: 1:1

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
## siz

e
S

o

u

r

c

e: 4

_

S

c

h

e

m

a

## tic

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
## tic

s

/

## ain

o

a

r

d

/

R

R_

## ain

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
7.4.0

X

## L; file

r

e

## visio

n: n

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
## d in

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
s: S

U

R

## RIV

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
## ols

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
## gle

_

s

c

h

e

m

a

## tic.p

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
## tio

n

r

e

n

d

e

## rin

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
## tiv

e

## file; fo

n

t

s

## diff

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
t. T

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
10 10

11 11

12 12

13 13

14 14

15 15

16 16

17 | 17 Date: 2026-03-14 03:04 | Sheet: 3/4REV: TITLE: Document Number: RADAR_Main_Board.sch 2026-03-14 03:04 | 3/4 RADAR_Main_Board.sch GND_2 ¹ | IF+ ² | IF ³ | GND_3 ⁴ | RF ⁵ | GND_4 ⁶ | EN | 7 GND_5 | 8 VCC | 9 GND_6 | 10 LO | 11 GND | 12 U5 | GND_2 ¹ | IF+ ² | IF ³ | GND_3 ⁴ | RF ⁵ | GND_4 ⁶ | EN | 7 GND_5 | 8 VCC | 9 GND_6 | 10 LO | 11 GND | 12 U13 | NC ¹ | GND ² | RFOUT1 ³ | GND2 ⁴ | VEE ⁵ | VCTRL ⁶ | GND3 ⁷ | VDD ⁸ | GND4 | 9 RFOUT2 | 10 GND5 | 11 NC2 | 12 NC3 | 13 GND6 | 14 RFC | 15 GND7 | 16 EP ¹⁷ U$1 CATHODE ¹ ANODE 2 | U14 CATHODE 1 ANODE ² U15 | C79 | C80 | C81 | C82 C83 | C84 C85 | NOT_USED ¹ | NOT_USED_2 ² | NOT_USED_3 ³ | NOT_USED_4 ⁴ | NOT_USED_5 ⁵ | NOT_USED_6 ⁶ | NOT_USED_7 ⁷ | NOT_USED_8 ⁸ | GROUND_2 ⁹ | PORT_2 ¹⁰ | GROUND_3 ¹¹ | NOT_USED_9 ¹² | GROUND_4 ¹³ | PORT_1 ¹⁴ | GROUND_5 ¹⁵ | NOT_USED_10 ¹⁶ | NOT_USED_11 | 17 NOT_USED_12 | 18 NOT_USED_13 | 19 GROUND_6 | 20 SUM_PORT | 21 GROUND_7 | 22 NOT_USED_14 | 23 NOT_USED_15 | 24 NOT_USED_16 | 25 GROUND_8 | 26 PORT_4 | 27 GROUND_9 | 28 NOT_USED_17 | 29 GROUND_10 | 30 PORT_3 | 31 GROUND_11 | 32 GROUND | 33 U16 DET3 A1 | GND_2 A2 | TR_SW_NEG A3 | PA_BIAS4 A4 | PA_BIAS3 A5 | GND_3 A6 | RF_IO A7 | GND_4 A8 | PA_BIAS2 A9 | PA_BIAS1 A10 | LNA_BIAS A11 | GND_5 A12 | GND_6 A13 | GND_7 B1 | GND_8 B2 | PA_ON B3 | TR_POL B4 | TR_SW_POS B5 | GND_9 B6 | GND_10 B7 | GND_11 B8 | GND_12 B9 | GND_13 B10 | AVDD B11 | GND_14 B12 | GND_15 B13 | TX3 C1 | GND_16 C2 | GND_17 C12 | RX2 C13 | GND_18 D1 | GND_19 D2 | GND_20 D12 | GND_21 D13 | RX3 E1 | GND_22 E2 | GND_23 E12 | TX2 E13 | GND_24 F1 | GND_25 F2 | GND_26 F12 | GND_27 F13 | DET4 G1 | GND_28 G2 | GND_29 | G12 DET2 | G13 GND_30 | H1 GND_31 | H2 GND_32 | H12 GND_33 | H13 TX4 | J1 GND_34 | J2 GND_35 | J12 RX1 | J13 GND_36 | K1 GND_37 | K2 GND_38 | K12 GND_39 | K13 RX4 | L1 GND_40 | L2 GND_41 | L12 TX1 | L13 GND_42 | M1 GND_43 | M2 CSB | M3 SDO | M4 SDIO | M5 SCLK | M6 GND_44 | M7 CREG1 | M8 CREG2 | M9 AVDD3_2 | M10 AVDD3_3 | M11 GND_45 | M12 GND_46 | M13 GND_47 | N1 RX_LOAD | N2 TX_LOAD | N3 ADDR0 | N4 ADDR1 | N5 TR | N6 GND_48 | N7 GND_49 | N8 CREG4 | N9 CREG3 | N10 AVDD3 | N11 GND_50 | N12 DET1 | N13 GND | 89 ADAR1_ R45 | C8C | 889 C90 | C91 | R46 | R47 | DET3 A1 | GND_2 A2 | TR_SW_NEG A3 | PA_BIAS4 A4 | PA_BIAS3 A5 | GND_3 A6 | RF_IO A7 | GND_4 A8 | PA_BIAS2 A9 | PA_BIAS1 A10 | LNA_BIAS A11 | GND_5 A12 | GND_6 A13 | GND_7 B1 | GND_8 B2 | PA_ON B3 | TR_POL B4 | TR_SW_POS B5 | GND_9 B6 | GND_10 B7 | GND_11 B8 | GND_12 B9 | GND_13 B10 | AVDD B11 | GND_14 B12 | GND_15 B13 | TX3 C1 | GND_16 C2 | GND_17 C12 | RX2 C13 | GND_18 D1 | GND_19 D2 | GND_20 D12 | GND_21 D13 | RX3 E1 | GND_22 E2 | GND_23 E12 | TX2 E13 | GND_24 F1 | GND_25 F2 | GND_26 F12 | GND_27 F13 | DET4 G1 | GND_28 G2 | GND_29 | G12 DET2 | G13 GND_30 | H1 GND_31 | H2 GND_32 | H12 GND_33 | H13 TX4 | J1 GND_34 | J2 GND_35 | J12 RX1 | J13 GND_36 | K1 GND_37 | K2 GND_38 | K12 GND_39 | K13 RX4 | L1 GND_40 | L2 GND_41 | L12 TX1 | L13 GND_42 | M1 GND_43 | M2 CSB | M3 SDO | M4 SDIO | M5 SCLK | M6 GND_44 | M7 CREG1 | M8 CREG2 | M9 AVDD3_2 | M10 AVDD3_3 | M11 GND_45 | M12 GND_46 | M13 GND_47 | N1 RX_LOAD | N2 TX_LOAD | N3 ADDR0 | N4 ADDR1 | N5 TR | N6 GND_48 | N7 GND_49 | N8 CREG4 | N9 CREG3 | N10 AVDD3 | N11 GND_50 | N12 DET1 | N13 GND | 89 ADAR2_ R48 | C8C | 687 C92 | C93 | R70 | R71 | DET3 A1 | GND_2 A2 | TR_SW_NEG A3 | PA_BIAS4 A4 | PA_BIAS3 A5 | GND_3 A6 | RF_IO A7 | GND_4 A8 | PA_BIAS2 A9 | PA_BIAS1 A10 | LNA_BIAS A11 | GND_5 A12 | GND_6 A13 | GND_7 B1 | GND_8 B2 | PA_ON B3 | TR_POL B4 | TR_SW_POS B5 | GND_9 B6 | GND_10 B7 | GND_11 B8 | GND_12 B9 | GND_13 B10 | AVDD B11 | GND_14 B12 | GND_15 B13 | TX3 C1 | GND_16 C2 | GND_17 C12 | RX2 C13 | GND_18 D1 | GND_19 D2 | GND_20 D12 | GND_21 D13 | RX3 E1 | GND_22 E2 | GND_23 E12 | TX2 E13 | GND_24 F1 | GND_25 F2 | GND_26 F12 | GND_27 F13 | DET4 G1 | GND_28 G2 | GND_29 | G12 DET2 | G13 GND_30 | H1 GND_31 | H2 GND_32 | H12 GND_33 | H13 TX4 | J1 GND_34 | J2 GND_35 | J12 RX1 | J13 GND_36 | K1 GND_37 | K2 GND_38 | K12 GND_39 | K13 RX4 | L1 GND_40 | L2 GND_41 | L12 TX1 | L13 GND_42 | M1 GND_43 | M2 CSB | M3 SDO | M4 SDIO | M5 SCLK | M6 GND_44 | M7 CREG1 | M8 CREG2 | M9 AVDD3_2 | M10 AVDD3_3 | M11 GND_45 | M12 GND_46 | M13 GND_47 | N1 RX_LOAD | N2 TX_LOAD | N3 ADDR0 | N4 ADDR1 | N5 TR | N6 GND_48 | N7 GND_49 | N8 CREG4 | N9 CREG3 | N10 AVDD3 | N11 GND_50 | N12 DET1 | N13 GND | 89 ADAR3_ R72 | C9C | 495 C96 | C97 | R73 | R74 | DET3 A1 | GND_2 A2 | TR_SW_NEG A3 | PA_BIAS4 A4 | PA_BIAS3 A5 | GND_3 A6 | RF_IO A7 | GND_4 A8 | PA_BIAS2 A9 | PA_BIAS1 A10 | LNA_BIAS A11 | GND_5 A12 | GND_6 A13 | GND_7 B1 | GND_8 B2 | PA_ON B3 | TR_POL B4 | TR_SW_POS B5 | GND_9 B6 | GND_10 B7 | GND_11 B8 | GND_12 B9 | GND_13 B10 | AVDD B11 | GND_14 B12 | GND_15 B13 | TX3 C1 | GND_16 C2 | GND_17 C12 | RX2 C13 | GND_18 D1 | GND_19 D2 | GND_20 D12 | GND_21 D13 | RX3 E1 | GND_22 E2 | GND_23 E12 | TX2 E13 | GND_24 F1 | GND_25 F2 | GND_26 F12 | GND_27 F13 | DET4 G1 | GND_28 G2 | GND_29 | G12 DET2 | G13 GND_30 | H1 GND_31 | H2 GND_32 | H12 GND_33 | H13 TX4 | J1 GND_34 | J2 GND_35 | J12 RX1 | J13 GND_36 | K1 GND_37 | K2 GND_38 | K12 GND_39 | K13 RX4 | L1 GND_40 | L2 GND_41 | L12 TX1 | L13 GND_42 | M1 GND_43 | M2 CSB | M3 SDO | M4 SDIO | M5 SCLK | M6 GND_44 | M7 CREG1 | M8 CREG2 | M9 AVDD3_2 | M10 AVDD3_3 | M11 GND_45 | M12 GND_46 | M13 GND_47 | N1 RX_LOAD | N2 TX_LOAD | N3 ADDR0 | N4 ADDR1 | N5 TR | N6 GND_48 | N7 GND_49 | N8 CREG4 | N9 CREG3 | N10 AVDD3 | N11 GND_50 | N12 DET1 | N13 GND | 89 ADAR4_ R75 | C9C | 899 C100 | C101 | R76 | R77 R78 | R79 | R80 R81 GND_2 ¹ | RX_OUT ² | GND_3 ³ | GND_4 ⁴ | TX_IN ⁵ | GND_5 ⁶ | VGG_PA ⁷ | VDD_PA ⁸ | NIC_2 ⁹ | NIC ¹⁰ | GND_6 ¹¹ | CPLR_OUT ¹² | GND_7 | 13 GND_8 | 14 GND_9 | 15 GND_10 | 16 ANT | 17 GND_11 | 18 VDD_SW | 19 CTRL_SW | 20 VSS_SW | 21 GND_12 | 22 VGG_LNA | 23 VDD_LNA | 24 GND | 25 ADTR1107_1 C102 | GND_2 ¹ | RX_OUT ² | GND_3 ³ | GND_4 ⁴ | TX_IN ⁵ | GND_5 ⁶ | VGG_PA ⁷ | VDD_PA ⁸ | NIC_2 ⁹ | NIC ¹⁰ | GND_6 ¹¹ | CPLR_OUT ¹² | GND_7 | 13 GND_8 | 14 GND_9 | 15 GND_10 | 16 ANT | 17 GND_11 | 18 VDD_SW | 19 CTRL_SW | 20 VSS_SW | 21 GND_12 | 22 VGG_LNA | 23 VDD_LNA | 24 GND | 25 ADTR1107_3 C103 | GND_2 ¹ | RX_OUT ² | GND_3 ³ | GND_4 ⁴ | TX_IN ⁵ | GND_5 ⁶ | VGG_PA ⁷ | VDD_PA ⁸ | NIC_2 ⁹ | NIC ¹⁰ | GND_6 ¹¹ | CPLR_OUT ¹² | GND_7 | 13 GND_8 | 14 GND_9 | 15 GND_10 | 16 ANT | 17 GND_11 | 18 VDD_SW | 19 CTRL_SW | 20 VSS_SW | 21 GND_12 | 22 VGG_LNA | 23 VDD_LNA | 24 GND | 25 ADTR1107_4 C104 | GND_2 ¹ | RX_OUT ² | GND_3 ³ | GND_4 ⁴ | TX_IN ⁵ | GND_5 ⁶ | VGG_PA ⁷ | VDD_PA ⁸ | NIC_2 ⁹ | NIC ¹⁰ | GND_6 ¹¹ | CPLR_OUT ¹² | GND_7 | 13 GND_8 | 14 GND_9 | 15 GND_10 | 16 ANT | 17 GND_11 | 18 VDD_SW | 19 CTRL_SW | 20 VSS_SW | 21 GND_12 | 22 VGG_LNA | 23 VDD_LNA | 24 GND | 25 ADTR1107_2 C105 | GND_2 ¹ | RX_OUT ² | GND_3 ³ | GND_4 ⁴ | TX_IN ⁵ | GND_5 ⁶ | VGG_PA ⁷ | VDD_PA ⁸ | NIC_2 ⁹ | NIC ¹⁰ | GND_6 ¹¹ | CPLR_OUT ¹² | GND_7 | 13 GND_8 | 14 GND_9 | 15 GND_10 | 16 ANT | 17 GND_11 | 18 VDD_SW | 19 CTRL_SW | 20 VSS_SW | 21 GND_12 | 22 VGG_LNA | 23 VDD_LNA | 24 GND | 25 ADTR1107_7 C107 | GND_2 ¹ | RX_OUT ² | GND_3 ³ | GND_4 ⁴ | TX_IN ⁵ | GND_5 ⁶ | VGG_PA ⁷ | VDD_PA ⁸ | NIC_2 ⁹ | NIC ¹⁰ | GND_6 ¹¹ | CPLR_OUT ¹² | GND_7 | 13 GND_8 | 14 GND_9 | 15 GND_10 | 16 ANT | 17 GND_11 | 18 VDD_SW | 19 CTRL_SW | 20 VSS_SW | 21 GND_12 | 22 VGG_LNA | 23 VDD_LNA | 24 GND | 25 ADTR1107_5 C106 | GND_2 ¹ | RX_OUT ² | GND_3 ³ | GND_4 ⁴ | TX_IN ⁵ | GND_5 ⁶ | VGG_PA ⁷ | VDD_PA ⁸ | NIC_2 ⁹ | NIC ¹⁰ | GND_6 ¹¹ | CPLR_OUT ¹² | GND_7 | 13 GND_8 | 14 GND_9 | 15 GND_10 | 16 ANT | 17 GND_11 | 18 VDD_SW | 19 CTRL_SW | 20 VSS_SW | 21 GND_12 | 22 VGG_LNA | 23 VDD_LNA | 24 GND | 25 ADTR1107_6 C114 | GND_2 ¹ | RX_OUT ² | GND_3 ³ | GND_4 ⁴ | TX_IN ⁵ | GND_5 ⁶ | VGG_PA ⁷ | VDD_PA ⁸ | NIC_2 ⁹ | NIC ¹⁰ | GND_6 ¹¹ | CPLR_OUT ¹² | GND_7 | 13 GND_8 | 14 GND_9 | 15 GND_10 | 16 ANT | 17 GND_11 | 18 VDD_SW | 19 CTRL_SW | 20 VSS_SW | 21 GND_12 | 22 VGG_LNA | 23 VDD_LNA | 24 GND | 25 ADTR1107_8 C115 | GND_2 ¹ | RX_OUT ² | GND_3 ³ | GND_4 ⁴ | TX_IN ⁵ | GND_5 ⁶ | VGG_PA ⁷ | VDD_PA ⁸ | NIC_2 ⁹ | NIC ¹⁰ | GND_6 ¹¹ | CPLR_OUT ¹² | GND_7 | 13 GND_8 | 14 GND_9 | 15 GND_10 | 16 ANT | 17 GND_11 | 18 VDD_SW | 19 CTRL_SW | 20 VSS_SW | 21 GND_12 | 22 VGG_LNA | 23 VDD_LNA | 24 GND | 25 ADTR1107_10 C116 | GND_2 ¹ | RX_OUT ² | GND_3 ³ | GND_4 ⁴ | TX_IN ⁵ | GND_5 ⁶ | VGG_PA ⁷ | VDD_PA ⁸ | NIC_2 ⁹ | NIC ¹⁰ | GND_6 ¹¹ | CPLR_OUT ¹² | GND_7 | 13 GND_8 | 14 GND_9 | 15 GND_10 | 16 ANT | 17 GND_11 | 18 VDD_SW | 19 CTRL_SW | 20 VSS_SW | 21 GND_12 | 22 VGG_LNA | 23 VDD_LNA | 24 GND | 25 ADTR1107_12 C117 | GND_2 ¹ | RX_OUT ² | GND_3 ³ | GND_4 ⁴ | TX_IN ⁵ | GND_5 ⁶ | VGG_PA ⁷ | VDD_PA ⁸ | NIC_2 ⁹ | NIC ¹⁰ | GND_6 ¹¹ | CPLR_OUT ¹² | GND_7 | 13 GND_8 | 14 GND_9 | 15 GND_10 | 16 ANT | 17 GND_11 | 18 VDD_SW | 19 CTRL_SW | 20 VSS_SW | 21 GND_12 | 22 VGG_LNA | 23 VDD_LNA | 24 GND | 25 ADTR1107_11 C118 | GND_2 ¹ | RX_OUT ² | GND_3 ³ | GND_4 ⁴ | TX_IN ⁵ | GND_5 ⁶ | VGG_PA ⁷ | VDD_PA ⁸ | NIC_2 ⁹ | NIC ¹⁰ | GND_6 ¹¹ | CPLR_OUT ¹² | GND_7 | 13 GND_8 | 14 GND_9 | 15 GND_10 | 16 ANT | 17 GND_11 | 18 VDD_SW | 19 CTRL_SW | 20 VSS_SW | 21 GND_12 | 22 VGG_LNA | 23 VDD_LNA | 24 GND | 25 ADTR1107_9 C119 | GND_2 ¹ | RX_OUT ² | GND_3 ³ | GND_4 ⁴ | TX_IN ⁵ | GND_5 ⁶ | VGG_PA ⁷ | VDD_PA ⁸ | NIC_2 ⁹ | NIC ¹⁰ | GND_6 ¹¹ | CPLR_OUT ¹² | GND_7 | 13 GND_8 | 14 GND_9 | 15 GND_10 | 16 ANT | 17 GND_11 | 18 VDD_SW | 19 CTRL_SW | 20 VSS_SW | 21 GND_12 | 22 VGG_LNA | 23 VDD_LNA | 24 GND | 25 ADTR1107_14 C120 | GND_2 ¹ | RX_OUT ² | GND_3 ³ | GND_4 ⁴ | TX_IN ⁵ | GND_5 ⁶ | VGG_PA ⁷ | VDD_PA ⁸ | NIC_2 ⁹ | NIC ¹⁰ | GND_6 ¹¹ | CPLR_OUT ¹² | GND_7 | 13 GND_8 | 14 GND_9 | 15 GND_10 | 16 ANT | 17 GND_11 | 18 VDD_SW | 19 CTRL_SW | 20 VSS_SW | 21 GND_12 | 22 VGG_LNA | 23 VDD_LNA | 24 GND | 25 ADTR1107_16 C121 | GND_2 ¹ | RX_OUT ² | GND_3 ³ | GND_4 ⁴ | TX_IN ⁵ | GND_5 ⁶ | VGG_PA ⁷ | VDD_PA ⁸ | NIC_2 ⁹ | NIC ¹⁰ | GND_6 ¹¹ | CPLR_OUT ¹² | GND_7 | 13 GND_8 | 14 GND_9 | 15 GND_10 | 16 ANT | 17 GND_11 | 18 VDD_SW | 19 CTRL_SW | 20 VSS_SW | 21 GND_12 | 22 VGG_LNA | 23 VDD_LNA | 24 GND | 25 ADTR1107_15 C122 | GND_2 ¹ | RX_OUT ² | GND_3 ³ | GND_4 ⁴ | TX_IN ⁵ | GND_5 ⁶ | VGG_PA ⁷ | VDD_PA ⁸ | NIC_2 ⁹ | NIC ¹⁰ | GND_6 ¹¹ | CPLR_OUT ¹² | GND_7 | 13 GND_8 | 14 GND_9 | 15 GND_10 | 16 ANT | 17 GND_11 | 18 VDD_SW | 19 CTRL_SW | 20 VSS_SW | 21 GND_12 | 22 VGG_LNA | 23 VDD_LNA | 24 GND | 25 ADTR1107_13 C123 R55 | R56 | R57 R58 IN P$1 | OUT | P$2 U$2 | IN P$1 | OUT | P$2 U$3 L22 C127 L25 | C141 L26 L27 DB7 ¹ | DB6 ² | DB5 ³ | DB4 ⁴ | DB3 ⁵ | DB2 ⁶ | DB1 ⁷ | DB0 ⁸ | NC_2 ⁹ | NC_3 ¹⁰ | NC_4 ¹¹ | NC_5 ¹² | NC_6 ¹³ | NC_7 ¹⁴ | SLEEP | 15 REFLO | 16 REFIO | 17 FSADJ | 18 COMP1 | 19 ACOM | 20 IOUTB | 21 IOUTA | 22 COMP2 | 23 AVDD | 24 NC | 25 DCOM | 26 DVDD | 27 CLOCK | 28 U3 R23 R24 R25 R26 R27 R28 R29 R30 | R33 | C37 C38 C39 | L6L7 | C40 | C42 C41 R115 | R116 R117 | R31 DNC_2 ¹ | DNC_3 ² | D0- ³ | D0+ ⁴ | D1- ⁵ | D1+ ⁶ | DRVDD_2 ⁷ | DRGND_2 ⁸ | D2- ⁹ | D2+ ¹⁰ | D3- ¹¹ | D3+ ¹² | D4- ¹³ | D4+ ¹⁴ | D5- ¹⁵ | D5+ ¹⁶ | D6- ¹⁷ | D6+ ¹⁸ | D7- ¹⁹ | D7+ ²⁰ | OR- ²¹ | OR+ ²² | DRGND_3 ²³ | DRVDD_3 ²⁴ | SDIO ²⁵ | SCLK/DFS ²⁶ | CSB ²⁷ | DNC_4 ²⁸ | PWDN | 29 AVDD_2 | 30 VREF | 31 AVDD_3 | 32 AVDD_4 | 33 AVDD_5 | 34 VIN+ | 35 VIN- | 36 AVDD_6 | 37 AVDD_7 | 38 AVDD_8 | 39 CML | 40 AVDD_9 | 41 AVDD_10 | 42 AVDD_11 | 43 CLK+ | 44 CLK- | 45 AVDD | 46 DRVDD | 47 DRGND | 48 DCO- | 49 DCO+ | 50 DNC_5 | 51 DNC_6 | 52 DNC_7 | 53 DNC_8 | 54 DNC_9 | 55 DNC | 56 EPAD | 57 U1 | 1 ¹ | 2 ² | 3 ³ | 4 | 4 5 | 5J201 ¹ | 2 ² | MH1 MH1 | MH2 | MH2 MH3 | MH3 MH4 | MH4 J21 | RDP ¹ | RGP ² | RGN ³ | RDN ⁴ | VIN ⁵ | GND_2 ⁶ | GND_3 ⁷ | VCC_2 ⁸ | GND_4 | 9 VON | 10 VOP | 11 GND | 12 VCC | 13 VCM | 14 ENB | 15 VIP | 16 EPAD | 17 U4 | 1 ¹ | 2 ² | 3 ³ | 4 | 4 5 | 5J22 ¹ ¹ | 2 ² | 3 ³ | 4 | 4 5 | 5J23 C1 C2 3 1 | 2 SJ1 | R1R13 C3 C14 | C4 | C5 | C6 | C7 | C8 | C9 | C10 | C11 | C12 | C13 C15 | C16 | C36 | R16 R17 C44 C45 C46 R14 R15 C43 | C47 | R18 C | R19 ⁴⁸ | C49 | RDP ¹ | RGP ² | RGN ³ | RDN ⁴ | VIN ⁵ | GND_2 ⁶ | GND_3 ⁷ | VCC_2 ⁸ | GND_4 | 9 VON | 10 VOP | 11 GND | 12 VCC | 13 VCM | 14 ENB | 15 VIP | 16 EPAD | 17 U8 | R20 R21 C51 C52 C53 R22 R32 C54 | C56 | R34 C | R35 ⁵⁷ | C58 | C60 L2 C61 C62 L3L4 C63 L8 C64 C65 L9 L10 C59 R36 R37 R38 | 1 1 | 2 2 | 3 3 4 ⁴ 5 ⁵J24 NC 1 | GND 2 | RFOUT1 3 | GND2 4 | VEE 5 | VCTRL 6 | GND3 7 | VDD 8 GND4 ⁹ RFOUT2 ¹⁰ GND5 ¹¹ NC2 ¹² NC3 ¹³ GND6 ¹⁴ RFC ¹⁵ GND7 ¹⁶ EP ¹⁷ | RF_SW_3 CATHODE ¹ | ANODE | 2 U17 ANODE | CATHODE | 1 2 | U37 C66 C67 | C68 C69 C70 C72 | C71 1 1 2 2 3 3 | 4 ⁴ 5 ⁵ J25 | 1 1 | 2 2 | 3 3 4 ⁴ 5 ⁵J26 NC 1 | GND 2 | RFOUT1 3 | GND2 4 | VEE 5 | VCTRL 6 | GND3 7 | VDD 8 GND4 ⁹ RFOUT2 ¹⁰ GND5 ¹¹ NC2 ¹² NC3 ¹³ GND6 ¹⁴ RFC ¹⁵ GND7 ¹⁶ EP ¹⁷ | RF_SW_1 CATHODE ¹ | ANODE | 2 U38 ANODE | CATHODE | 1 2 | U39 C73 C74 | C124 C125 C126 C129 | C128 1 1 2 2 3 3 | 4 ⁴ 5 ⁵ J27 | 1 1 | 2 2 | 3 3 4 ⁴ 5 ⁵J28 NC 1 | GND 2 | RFOUT1 3 | GND2 4 | VEE 5 | VCTRL 6 | GND3 7 | VDD 8 GND4 ⁹ RFOUT2 ¹⁰ GND5 ¹¹ NC2 ¹² NC3 ¹³ GND6 ¹⁴ RFC ¹⁵ GND7 ¹⁶ EP ¹⁷ | RF_SW_2 | CATHODE ¹ | ANODE | 2 U40 ANODE | CATHODE | 1 2 | U41 C130 C131 | C132 C133 C134 C136 | C135 1 1 2 2 3 3 | 4 ⁴ 5 ⁵ J29 | 1 1 | 2 2 | 3 3 4 ⁴ 5 ⁵J30 NC 1 | GND 2 | RFOUT1 3 | GND2 4 | VEE 5 | VCTRL 6 | GND3 7 | VDD 8 GND4 ⁹ RFOUT2 ¹⁰ GND5 ¹¹ NC2 ¹² NC3 ¹³ GND6 ¹⁴ RFC ¹⁵ GND7 ¹⁶ EP ¹⁷ | RF_SW_4 CATHODE ¹ | ANODE | 2 U43 ANODE | CATHODE | 1 2 | U44 C137 C138 | C139 C140 C142 C144 | C143 1 1 2 2 3 3 | 4 ⁴ 5 ⁵ J31 ¹ ¹ | 2 2 | 3 3 4 ⁴ 5 ⁵J32 NC 1 | GND 2 | RFOUT1 3 | GND2 4 | VEE 5 | VCTRL 6 | GND3 7 | VDD 8 GND4 ⁹ RFOUT2 ¹⁰ GND5 ¹¹ NC2 ¹² NC3 ¹³ GND6 ¹⁴ RFC ¹⁵ GND7 ¹⁶ EP ¹⁷ | RF_SW_7 CATHODE ¹ | ANODE | 2 U45 ANODE | CATHODE | 1 2 | U46 C145 C146 | C147 C148 C149 C151 | C150 1 1 2 2 3 3 | 4 ⁴ 5 ⁵ J33 | 1 1 | 2 2 | 3 3 4 ⁴ 5 ⁵J34 NC 1 | GND 2 | RFOUT1 3 | GND2 4 | VEE 5 | VCTRL 6 | GND3 7 | VDD 8 GND4 ⁹ RFOUT2 ¹⁰ GND5 ¹¹ NC2 ¹² NC3 ¹³ GND6 ¹⁴ RFC ¹⁵ GND7 ¹⁶ EP ¹⁷ | RF_SW_5 | CATHODE ¹ | ANODE | 2 U47 ANODE | CATHODE | 1 2 | U48 C152 C160 | C161 C162 C163 C166 | C165 1 1 2 2 3 3 | 4 ⁴ 5 ⁵ J35 | 1 1 | 2 2 | 3 3 4 ⁴ 5 ⁵J36 NC 1 | GND 2 | RFOUT1 3 | GND2 4 | VEE 5 | VCTRL 6 | GND3 7 | VDD 8 GND4 ⁹ RFOUT2 ¹⁰ GND5 ¹¹ NC2 ¹² NC3 ¹³ GND6 ¹⁴ RFC ¹⁵ GND7 ¹⁶ EP ¹⁷ | RF_SW_6 CATHODE ¹ | ANODE | 2 U49 ANODE | CATHODE | 1 2 | U50 C167 C168 | C169 C170 C171 C173 | C172 1 1 2 2 3 3 | 4 ⁴ 5 ⁵ J37 | 1 1 | 2 2 | 3 3 4 ⁴ 5 ⁵J38 NC 1 | GND 2 | RFOUT1 3 | GND2 4 | VEE 5 | VCTRL 6 | GND3 7 | VDD 8 GND4 ⁹ RFOUT2 ¹⁰ GND5 ¹¹ NC2 ¹² NC3 ¹³ GND6 ¹⁴ RFC ¹⁵ GND7 ¹⁶ EP ¹⁷ | RF_SW_8 CATHODE ¹ | ANODE | 2 U51 ANODE | CATHODE | 1 2 | U52 C174 C175 | C183 C196 C197 C199 | C198 1 1 2 2 3 3 | 4 ⁴ 5 ⁵ J39 ¹ ¹ | 2 2 | 3 3 4 ⁴ 5 ⁵J40 NC 1 | GND 2 | RFOUT1 3 | GND2 4 | VEE 5 | VCTRL 6 | GND3 7 | VDD 8 GND4 ⁹ RFOUT2 ¹⁰ GND5 ¹¹ NC2 ¹² NC3 ¹³ GND6 ¹⁴ RFC ¹⁵ GND7 ¹⁶ EP ¹⁷ | RF_SW_10 CATHODE ¹ | ANODE | 2 U53 ANODE | CATHODE | 1 2 | U54 C200 C201 | C202 C203 C204 C206 | C205 1 1 2 2 3 3 | 4 ⁴ 5 ⁵ J41 | 1 1 | 2 2 | 3 3 4 ⁴ 5 ⁵J42 NC 1 | GND 2 | RFOUT1 3 | GND2 4 | VEE 5 | VCTRL 6 | GND3 7 | VDD 8 GND4 ⁹ RFOUT2 ¹⁰ GND5 ¹¹ NC2 ¹² NC3 ¹³ GND6 ¹⁴ RFC ¹⁵ GND7 ¹⁶ EP ¹⁷ | RF_SW_12 | CATHODE ¹ | ANODE | 2 U55 ANODE | CATHODE | 1 2 | U56 C207 C208 | C209 C210 C211 C213 | C212 1 1 2 2 3 3 | 4 ⁴ 5 ⁵ J43 | 1 1 | 2 2 | 3 3 4 ⁴ 5 ⁵J44 NC 1 | GND 2 | RFOUT1 3 | GND2 4 | VEE 5 | VCTRL 6 | GND3 7 | VDD 8 GND4 ⁹ RFOUT2 ¹⁰ GND5 ¹¹ NC2 ¹² NC3 ¹³ GND6 ¹⁴ RFC ¹⁵ GND7 ¹⁶ EP ¹⁷ | RF_SW_11 CATHODE ¹ | ANODE | 2 U57 ANODE | CATHODE | 1 2 | U58 C214 C215 | C216 C217 C218 C220 | C219 1 1 2 2 3 3 | 4 ⁴ 5 ⁵ J45 | 1 1 | 2 2 | 3 3 4 ⁴ 5 ⁵J46 NC 1 | GND 2 | RFOUT1 3 | GND2 4 | VEE 5 | VCTRL 6 | GND3 7 | VDD 8 GND4 ⁹ RFOUT2 ¹⁰ GND5 ¹¹ NC2 ¹² NC3 ¹³ GND6 ¹⁴ RFC ¹⁵ GND7 ¹⁶ EP ¹⁷ | RF_SW_9 CATHODE ¹ | ANODE | 2 U59 ANODE | CATHODE | 1 2 | U60 C221 C222 | C223 C224 C225 C227 | C226 1 1 2 2 3 3 | 4 ⁴ 5 ⁵ J47 ¹ ¹ | 2 2 | 3 3 4 ⁴ 5 ⁵J48 NC 1 | GND 2 | RFOUT1 3 | GND2 4 | VEE 5 | VCTRL 6 | GND3 7 | VDD 8 GND4 ⁹ RFOUT2 ¹⁰ GND5 ¹¹ NC2 ¹² NC3 ¹³ GND6 ¹⁴ RFC ¹⁵ GND7 ¹⁶ EP ¹⁷ | RF_SW_14 CATHODE ¹ | ANODE | 2 U61 ANODE | CATHODE | 1 2 | U62 C228 C229 | C230 C231 C232 C234 | C233 1 1 2 2 3 3 | 4 ⁴ 5 ⁵ J49 | 1 1 | 2 2 | 3 3 4 ⁴ 5 ⁵J50 NC 1 | GND 2 | RFOUT1 3 | GND2 4 | VEE 5 | VCTRL 6 | GND3 7 | VDD 8 GND4 ⁹ RFOUT2 ¹⁰ GND5 ¹¹ NC2 ¹² NC3 ¹³ GND6 ¹⁴ RFC ¹⁵ GND7 ¹⁶ EP ¹⁷ | RF_SW_16 | CATHODE ¹ | ANODE | 2 U63 ANODE | CATHODE | 1 2 | U64 C235 C236 | C237 C238 C239 C241 | C240 1 1 2 2 3 3 | 4 ⁴ 5 ⁵ J51 | 1 1 | 2 2 | 3 3 4 ⁴ 5 ⁵J52 NC 1 | GND 2 | RFOUT1 3 | GND2 4 | VEE 5 | VCTRL 6 | GND3 7 | VDD 8 GND4 ⁹ RFOUT2 ¹⁰ GND5 ¹¹ NC2 ¹² NC3 ¹³ GND6 ¹⁴ RFC ¹⁵ GND7 ¹⁶ EP ¹⁷ | RF_SW_15 CATHODE ¹ | ANODE | 2 U65 ANODE | CATHODE | 1 2 | U66 C242 C243 | C244 C245 C246 C248 | C247 1 1 2 2 3 3 | 4 ⁴ 5 ⁵ J53 | 1 1 | 2 2 | 3 3 4 ⁴ 5 ⁵J54 NC 1 | GND 2 | RFOUT1 3 | GND2 4 | VEE 5 | VCTRL 6 | GND3 7 | VDD 8 GND4 ⁹ RFOUT2 ¹⁰ GND5 ¹¹ NC2 ¹² NC3 ¹³ GND6 ¹⁴ RFC ¹⁵ GND7 ¹⁶ EP ¹⁷ | RF_SW_13 CATHODE ¹ | ANODE | 2 U67 ANODE | CATHODE | 1 2 | U68 C249 C250 | C251 C252 C253 C255 | C254 1 1 2 2 3 3 | 4 ⁴ 5 ⁵ J55 R154 R155 R156 R157 R158 | R159 R160 | R161 R162 | R163 R164 | R165 | R166 C308 | C309 | C268 C270L24 L28 C272 | C274 R173 C293 +5V0_PA_1 +5V0_PA_1 | +5V0_PA_1 +5V0_PA_1 +5V0_PA_1 | RF_RX | RF_RX MIX_RX_EN DAC_IOUT_F_P DAC_IOUT_F_N RF_TX | RF_TX MIX_TX_EN -3V3_SW -3V3_SW -3V3_SW -3V3_SW | -3V3_SW -3V3_SW -3V3_SW -3V3_SW | -3V3_SW -3V3_SW -3V3_SW -3V3_SW | -3V3_SW -3V3_SW -3V3_SW -3V3_SW | RF_TX_FIL RF_TX_FIL | RF_IO RF_RX_FIL | RF_IO RF_RX_FIL | RF_IO_2 RF_IO_2 | RF_IO_1 RF_IO_1 | RF_IO_3 RF_IO_3 | RF_IO_4 RF_IO_4 TR_SW_POS_1 | TR_SW_POS_1 TR_SW_POS_1 TR_SW_POS_1 TR_SW_POS_1 TX3_1 TX3_1 -5V0_ADAR12 | -5V0_ADAR12 RX2_1 RX2_1 RX3_1 RX3_1 TX2_1 TX2_1 DET4_1 DET4_1 DET3_1 DET3_1 PA_BIAS4_1 PA_BIAS4_1 PA_BIAS3_1 PA_BIAS3_1 | DET2_1 DET2_1 | TX4_1 TX4_1 | RX1_1 RX1_1 | RX4_1 RX4_1 | TX1_1 TX1_1 | STM32_SCLK_1V8 | STM32_SCLK_1V8 | STM32_SCLK_1V8 | STM32_SCLK_1V8 STM32_SCLK_1V8 | STM32_MOSI_1V8 | STM32_MOSI_1V8 | STM32_MOSI_1V8 | STM32_MOSI_1V8 STM32_MOSI_1V8 | STM32_MISO_1V8 | STM32_MISO_1V8 | STM32_MISO_1V8 | STM32_MISO_1V8 STM32_MISO_1V8 | ADAR_1_CS_1V8 ADAR_1_CS_1V8 ADAR_RX_LOAD_1 | ADAR_TR_4 ADAR_TR_4 | ADAR_TX_LOAD_1 DET1_1 DET1_1 PA_BIAS2_1 PA_BIAS2_1 PA_BIAS1_1 PA_BIAS1_1 LNA_BIAS_1 | LNA_BIAS_1 LNA_BIAS_1 LNA_BIAS_1 LNA_BIAS_1 | ADAR_RX_LOAD_2 ADAR_TX_LOAD_2 | ADAR_RX_LOAD_3 ADAR_TX_LOAD_3 | ADAR_RX_LOAD_4 ADAR_TX_LOAD_4 DET3_2 DET3_2 PA_BIAS4_2 PA_BIAS4_2 PA_BIAS3_2 PA_BIAS3_2 PA_BIAS2_2 PA_BIAS2_2 PA_BIAS1_2 PA_BIAS1_2 LNA_BIAS_2 | LNA_BIAS_2 LNA_BIAS_2 LNA_BIAS_2 LNA_BIAS_2 TR_SW_POS_2 | TR_SW_POS_2 TR_SW_POS_2 TR_SW_POS_2 TR_SW_POS_2 TX3_2 TX3_2 RX2_2 RX2_2 RX3_2 RX3_2 TX2_2 TX2_2 DET4_2 DET4_2 | DET2_2 DET2_2 | TX4_2 TX4_2 | RX1_2 RX1_2 | RX4_2 RX4_2 | TX1_2 TX1_2 | ADAR_2_CS_1V8 ADAR_2_CS_1V8 | DET1_2 DET1_2 | DET3_3 DET3_3 PA_BIAS4_3 PA_BIAS4_3 PA_BIAS3_3 PA_BIAS3_3 PA_BIAS2_3 PA_BIAS2_3 PA_BIAS1_3 PA_BIAS1_3 LNA_BIAS_3 | LNA_BIAS_3 LNA_BIAS_3 LNA_BIAS_3 LNA_BIAS_3 TR_SW_POS_3 | TR_SW_POS_3 TR_SW_POS_3 TR_SW_POS_3 TR_SW_POS_3 TX3_3 TX3_3 RX2_3 RX2_3 RX3_3 RX3_3 TX2_3 TX2_3 DET4_3 DET4_3 | DET2_3 DET2_3 | TX4_3 TX4_3 | RX1_3 RX1_3 | RX4_3 RX4_3 | ADAR_3_CS_1V8 ADAR_3_CS_1V8 | DET1_3 DET1_3 | DET3_4 DET3_4 PA_BIAS4_4 PA_BIAS4_4 PA_BIAS3_4 PA_BIAS3_4 PA_BIAS2_4 PA_BIAS2_4 PA_BIAS1_4 PA_BIAS1_4 LNA_BIAS_4 | LNA_BIAS_4 LNA_BIAS_4 LNA_BIAS_4 LNA_BIAS_4 TR_SW_POS_4 | TR_SW_POS_4 TR_SW_POS_4 TR_SW_POS_4 TR_SW_POS_4 TX3_4 TX3_4 RX2_4 RX2_4 RX3_4 RX3_4 TX2_4 TX2_4 DET4_4 DET4_4 | DET2_4 DET2_4 | TX4_4 TX4_4 | RX1_4 RX1_4 | RX4_4 RX4_4 | TX1_4 TX1_4 | ADAR_4_CS_1V8 ADAR_4_CS_1V8 | DET1_4 DET1_4 ANT1_1 | ANT1_1 ANT2_1 | ANT2_1 ANT3_1 | ANT3_1 ANT4_1 | ANT4_1 ANT1_2 | ANT1_2 ANT2_2 | ANT2_2 ANT3_2 | ANT3_2 ANT4_2 | ANT4_2 TX1_3 | TX1_3 ANT1_3 | ANT1_3 ANT2_3 | ANT2_3 ANT3_3 | ANT3_3 ANT4_3 | ANT4_3 ANT1_4 | ANT1_4 ANT2_4 | ANT2_4 ANT3_4 | ANT3_4 ANT4_4 | ANT4_4 +3V3_ADTR +3V3_ADTR +3V3_ADTR +3V3_ADTR | +3V3_ADTR +3V3_ADTR +3V3_ADTR +3V3_ADTR | +3V3_ADTR +3V3_ADTR +3V3_ADTR +3V3_ADTR | +3V3_ADTR +3V3_ADTR +3V3_ADTR +3V3_ADTR ADAR_TR_1 ADAR_TR_1 | ADAR_TR_2 ADAR_TR_2 | ADAR_TR_3 ADAR_TR_3 DAC_7 DAC_6 DAC_5 DAC_4 DAC_3 DAC_2 DAC_1 DAC_0 | DAC_CLOCKDAC_CLOCK DAC_SLEEP DAC_AVDD | DAC_AVDD DAC_AVDD DAC_AVDD | DAC_ACOM DAC_ACOM +3V3_FPGA +3V3_FPGA +1V8_FPGA +1V8_FPGA +1V8_FPGA +1V8_FPGA | +1V8_FPGA | +5V0_0 +5V0_0 | +5V0_0 +5V0_0 | -3V4 ⁻³V4 | -3V4 | -3V4 | -3V4 -3V4 | -3V4 | -3V4 | -3V4 -3V4 | -3V4 | -3V4 | -3V4 -3V4 | -3V4 | -3V4 | -3V4 +3V4 ⁺³V4 | +3V4 | +3V4 | +3V4 +3V4 | +3V4 | +3V4 | +3V4 +3V4 | +3V4 | +3V4 | +3V4 +3V4 | +3V4 | +3V4 | +3V4 -5V0_ADAR34 | -5V0_ADAR34 +3V3_VDD_SW | +3V3_VDD_SW | +3V3_VDD_SW | +3V3_VDD_SW +3V3_VDD_SW | +3V3_VDD_SW | +3V3_VDD_SW | +3V3_VDD_SW +3V3_VDD_SW +3V3_VDD_SW | +3V3_VDD_SW | +3V3_VDD_SW | +3V3_VDD_SW +3V3_VDD_SW | +3V3_VDD_SW | +3V3_VDD_SW +5V0_PA_2 | +5V0_PA_2 +5V0_PA_2 +5V0_PA_2 | +5V0_PA_2 +5V0_PA_3 | +5V0_PA_3 +5V0_PA_3 | +5V0_PA_3 +5V0_PA_3 +5V0_PA_3 ADC_D0_N ADC_D0_P ADC_D1_N ADC_D1_P ADC_D2_N ADC_D2_P ADC_D3_N ADC_D3_P ADC_D4_N ADC_D4_P ADC_D5_N ADC_D5_P ADC_D6_N ADC_D6_P ADC_D7_N ADC_D7_P | ADC_DCO_N ADC_DCO_P | +3V3_AN ADC_CLK_IN_N ADC_CLK_IN_N ADC_CLK_IN_P ADC_CLK_IN_P ADC_OR_N ADC_OR_P +1V8_CLOCK_F | +1V8_CLOCK_F +1V8_CLOCK_F +1V8_CLOCK_F +1V8_CLOCK_F +1V8_CLOCK_F +1V8_CLOCK_F | +1V8_CLOCK_F | ADC_IF_IN_P | ADC_IF_IN_P ADC_IF_IN_N | ADC_IF_IN_N | EN_OPAMP_IF_1 AMP_IN_N | AMP_IN_N AMP_IN_P | AMP_IN_P AMP_IF_IN_P AMP_IF_IN_P | AMP_IF_IN_N AMP_IF_IN_N | EN_OPAMP_IF_2 ADC_PWRD | M3S_VCTRL M3S_VCTRL | M3S_VCTRL | M3S_VCTRL | M3S_VCTRL M3S_VCTRL | M3S_VCTRL | M3S_VCTRL | M3S_VCTRL M3S_VCTRL | M3S_VCTRL | M3S_VCTRL | M3S_VCTRL M3S_VCTRL | M3S_VCTRL | M3S_VCTRL | M3S_VCTRL DAC_IOUT_P | DAC_IOUT_P DAC_IOUT_N | DAC_IOUT_N +3V3_ADAR1_F +3V3_ADAR1_F | +3V3_ADAR2_F +3V3_ADAR2_F +3V3_ADAR2_F | +3V3_ADAR3_F +3V3_ADAR3_F +3V3_ADAR3_F | +3V3_ADAR4_F +3V3_ADAR4_F+3V3_ADAR4_F+3V3_ADAR4_F +3V3_AN1_F | +3V3_AN2_F LTC5552IUDBTRMPBF GND GND GND | GND GND GND | LTC5552IUDBTRMPBF GND GND GND | GND GND GND | M3SWA2-34DR+ GND GND GND GND GND | GND GND GND GND GND GND SZMMSZ5232BT1G SZMMSZ5232BT1G | 100pF 0.1uF GND | GND GND | GND | 100pF 0.1uF GND | GND ¹pF | 1pF 1pF | EP4RKU+ GND GND GND | GND GND | GND GND | GND | GND GND | GND GND | GNG | DND | GNG | DND GND | GNG | DND | GNG | DND ADAR1000ACCZN GND GND GND | GND GND | GND GND | GND GND | GND GND GND | GND GND | GND GND | GND GND | GND GND | GND GND | GND GND | GND | GND GND | GNG | DND | GND GND | GND GND | GNG | DND | GND GND | GND GND | GND GND | GND | GND GND | GNG | DND | GND GND GNG | DND | GND | GND GND GND 4.7k GND | GND | 1u1 | FuF 1uF | 1uF | 4.7k 4.7k GND | GND | GND | ADAR1000ACCZN GND GND GND | GND GND | GND GND | GND GND | GND GND GND | GND GND | GND GND | GND GND | GND GND | GND GND | GND GND | GND | GND GND | GNG | DND | GND GND | GND GND | GNG | DND | GND GND | GND GND | GND GND | GND | GND GND | GNG | DND | GND | GND GNGDND | GND | GND GND GND 4.7k GND | GND | 1u1 | FuF 1uF | 1uF | 4.7k | 4.7k GND | GND | ADAR1000ACCZN GND GND GND | GND GND | GND GND | GND GND | GND GND GND | GND GND | GND GND | GND GND | GND GND | GND GND | GND GND | GND | GND GND | GNG | DND | GND GND | GND GND | GNG | DND | GND GND | GND GND | GND GND | GND | GND GND | GNG | DND | GND | GND GNGDND | GND | GND GND GND 4.7k GND | GND | 1u1 | FuF 1uF | 1uF | 4.7k | 4.7k GND | GND | ADAR1000ACCZN GND GND GND | GND GND | GND GND | GND GND | GND GND GND | GND GND | GND GND | GND GND | GND GND | GND GND | GND GND | GND | GND GND | GNG | DND | GND GND | GND GND | GNG | DND | GND GND | GND GND | GND GND | GND | GND GND | GNG | DND | GND | GND GNGDND | GND | GND GND GND 4.7k GND | GND | 1u1 | FuF 1uF | 1uF | 4.7k | 4.7k GND 840R | 840R | 840R 840R ADTR1107ACCZ GND GND | GND GND GND GND | GND | GND | GNG | DND | GND GND GND GND 10nF GND | ADTR1107ACCZ GND GND | GND GND GND GND | GND | GND | GNG | DND | GND GND GND GND 10nF GND | ADTR1107ACCZ GND GND | GND GND GND GND | GND | GND | GNG | DND | GND GND GND GND 10nF GND | ADTR1107ACCZ GND GND | GND GND GND GND | GND | GND | GNG | DND | GND GND GND GND 10nF GND | ADTR1107ACCZ GND GND | GND GND GND GND | GND | GND | GNG | DND | GND GND GND GND 10nF GND | ADTR1107ACCZ GND GND | GND GND GND GND | GND | GND | GNG | DND | GND GND GND GND 10nF GND | ADTR1107ACCZ GND GND | GND GND GND GND | GND | GND | GNG | DND | GND GND GND GND 10nF GND | ADTR1107ACCZ GND GND | GND GND GND GND | GND | GND | GNG | DND | GND GND GND GND 10nF GND | ADTR1107ACCZ GND GND | GND GND GND GND | GND | GND | GNG | DND | GND GND GND GND 10nF GND | ADTR1107ACCZ GND GND | GND GND GND GND | GND | GND | GNG | DND | GND GND GND GND 10nF GND | ADTR1107ACCZ GND GND | GND GND GND GND | GND | GND | GNG | DND | GND GND GND GND 10nF GND | ADTR1107ACCZ GND GND | GND GND GND GND | GND | GND | GNG | DND | GND GND GND GND 10nF GND | ADTR1107ACCZ GND GND | GND GND GND GND | GND | GND | GNG | DND | GND GND GND GND 10nF GND | ADTR1107ACCZ GND GND | GND GND GND GND | GND | GND | GNG | DND | GND GND GND GND 10nF GND | ADTR1107ACCZ GND GND | GND GND GND GND | GND | GND | GNG | DND | GND GND GND GND 10nF GND | ADTR1107ACCZ GND GND | GND GND GND GND | GND | GND | GNG | DND | GND GND GND GND 10nF GND 1k | GND | 1k | GND | 1k 1k | GNG | DND BPF2 | BPF2 107.3nH 32.8pF 107.3nH | 106pF 107.3nH 107.3nH AD9708AR 22R 22R 22R 22R 22R 22R 22R 22R | 3k2 | 10uF GND ND0.1uF | GND 0.1uF | BLM15H BLM15H | 10uF | 0.1uF GND 0.1uF GND | 50R | 50R GND | GND 4.7k GND | 50R GND AD9484BCPZ-500 | 142-0731-211 CJT-T-P-HH-ST-TH1 | AD8352ACPZ-R7 | 142-0731-211 142-0731-211 GND | GND ⁰.1uF 0.1uF | GND GND GND GND | GND | GND SJ2WGND | 24R 24R 2.7pF 0.1uF 0.1uF 0.1uF 0.1uF 0.1uF 0.1uF 0.1uF 0.1uF 0.1uF 0.1uF 0.1uF 0.1uF 0.1uF 0.1uF | GND GND | GND | GND GND GND | 200R 200R 0.1uF 0.1uF 0.1uF GND ¹¹⁵R 4.30.2pF | k | 0.1uF | GND | 0R 0R 0.1µF | 0.1µF | AD8352ACPZ-R7 GND | GND GND GND | 200R 200R 0.1uF 0.1uF 0.1uF GND ⁵⁶R 4.30.6pF | k | 0.1uF | GND | 0R 0R 0.1µF | 0.1µF | 103pF ¹²nH 7.8pF 7.8pF 159nH 159nH 103pF ¹²nH 25pF 25pF 50nH 50nH 32.8pF | GND GND GND | GND 830R 1k GND 20k | GND | 142-0731-211 | M3SWA2-34DR+ GND | GND GND | GND | GND GND | GND GND GND GND | GND | SZMMSZ5232BT1G SZMMSZ5232BT1G ¹⁰⁰pF 0.1uF | GND GND | GND | GND 100pF 0.1uF | GND GN1pF | D 1pF | 1pF | GND GND 142-0731-211 | GND GND | 142-0731-211 | M3SWA2-34DR+ GND | GND GND | GND | GND GND | GND GND GND GND | GND | SZMMSZ5232BT1G SZMMSZ5232BT1G ¹⁰⁰pF 0.1uF | GND GND | GND | GND 100pF 0.1uF | GND GN1pF | D 1pF | 1pF | GND GND 142-0731-211 | GND GND | 142-0731-211 | M3SWA2-34DR+ GND | GND GND | GND | GND GND | GND GND GND GND | GND | SZMMSZ5232BT1G SZMMSZ5232BT1G ¹⁰⁰pF 0.1uF | GND GND | GND | GND 100pF 0.1uF | GND GN1pF | D 1pF | 1pF | GND GND 142-0731-211 | GND GND | 142-0731-211 | M3SWA2-34DR+ GND | GND GND | GND | GND GND | GND GND GND GND | GND | SZMMSZ5232BT1G SZMMSZ5232BT1G ¹⁰⁰pF 0.1uF | GND GND | GND | GND 100pF 0.1uF | GND GN1pF | D 1pF | 1pF | GND GND 142-0731-211 | GND GND 142-0731-211 | M3SWA2-34DR+ GND | GND GND | GND | GND GND | GND GND GND GND | GND | SZMMSZ5232BT1G SZMMSZ5232BT1G ¹⁰⁰pF 0.1uF | GND GND | GND | GND 100pF 0.1uF | GND GN1pF | D 1pF | 1pF | GND GND 142-0731-211 | GND GND | 142-0731-211 | M3SWA2-34DR+ GND | GND GND | GND | GND GND | GND GND GND GND | GND | SZMMSZ5232BT1G SZMMSZ5232BT1G ¹⁰⁰pF 0.1uF | GND GND | GND | GND 100pF 0.1uF | GND GN1pF | D 1pF | 1pF | GND GND 142-0731-211 | GND GND | 142-0731-211 | M3SWA2-34DR+ GND | GND GND | GND | GND GND | GND GND GND GND | GND | SZMMSZ5232BT1G SZMMSZ5232BT1G ¹⁰⁰pF 0.1uF | GND GND | GND | GND 100pF 0.1uF | GND GN1pF | D 1pF | 1pF | GND GND 142-0731-211 | GND GND | 142-0731-211 | M3SWA2-34DR+ GND | GND GND | GND | GND GND | GND GND GND GND | GND | SZMMSZ5232BT1G SZMMSZ5232BT1G ¹⁰⁰pF 0.1uF | GND GND | GND | GND 100pF 0.1uF | GND GN1pF | D 1pF | 1pF | GND GND 142-0731-211 | GND GND 142-0731-211 | M3SWA2-34DR+ GND | GND GND | GND | GND GND | GND GND GND GND | GND | SZMMSZ5232BT1G SZMMSZ5232BT1G ¹⁰⁰pF 0.1uF | GND GND | GND | GND
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
