herasymyuks/PLFM_RADAR-aeris/engineering/ELECTRICAL/schematics/RF_PA/RF_PA_schematic.pdf

## AERIS-10 — RF_PA — Schematic sheet 1/1

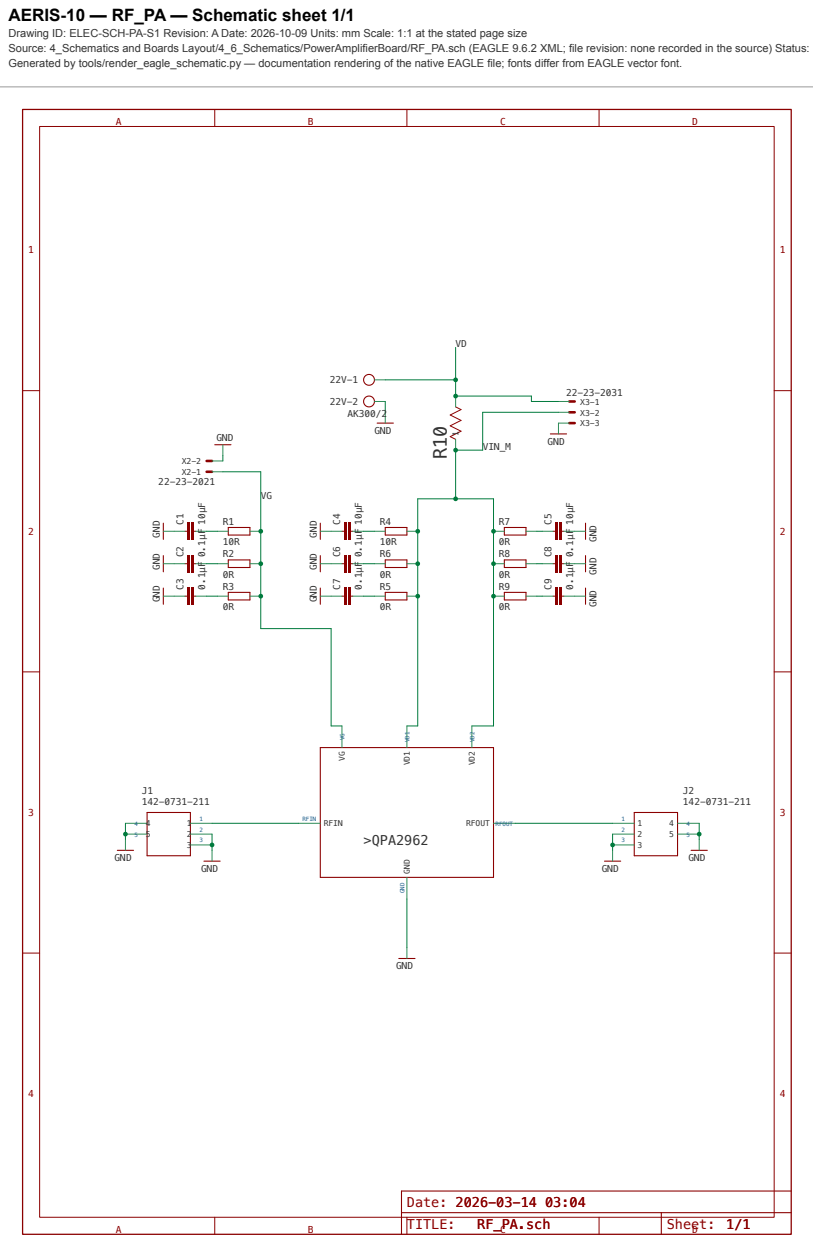
[picture p147: page 1]

Drawing ID: ELEC-SCH-PA-S1 Revision: A Date: 2026-10-09 Units: mm Scale: 1:1 at the stated page size
Source: 4_Schematics and Boards Layout/4_6_Schematics/PowerAmplifierBoard/RF_PA.sch (EAGLE 9.6.2 XML; file revision: none recorded in the source) Status:
Generated by tools/render_eagle_schematic.py — documentation rendering of the native EAGLE file; fonts differ from EAGLE vector font.
