herasymyuks/PLFM_RADAR-aeris/beta/pcb/MAIN_BOARD_REVB/exports/drawings/MAIN_BOARD_REVB_assembly_bottom_mirrored.pdf

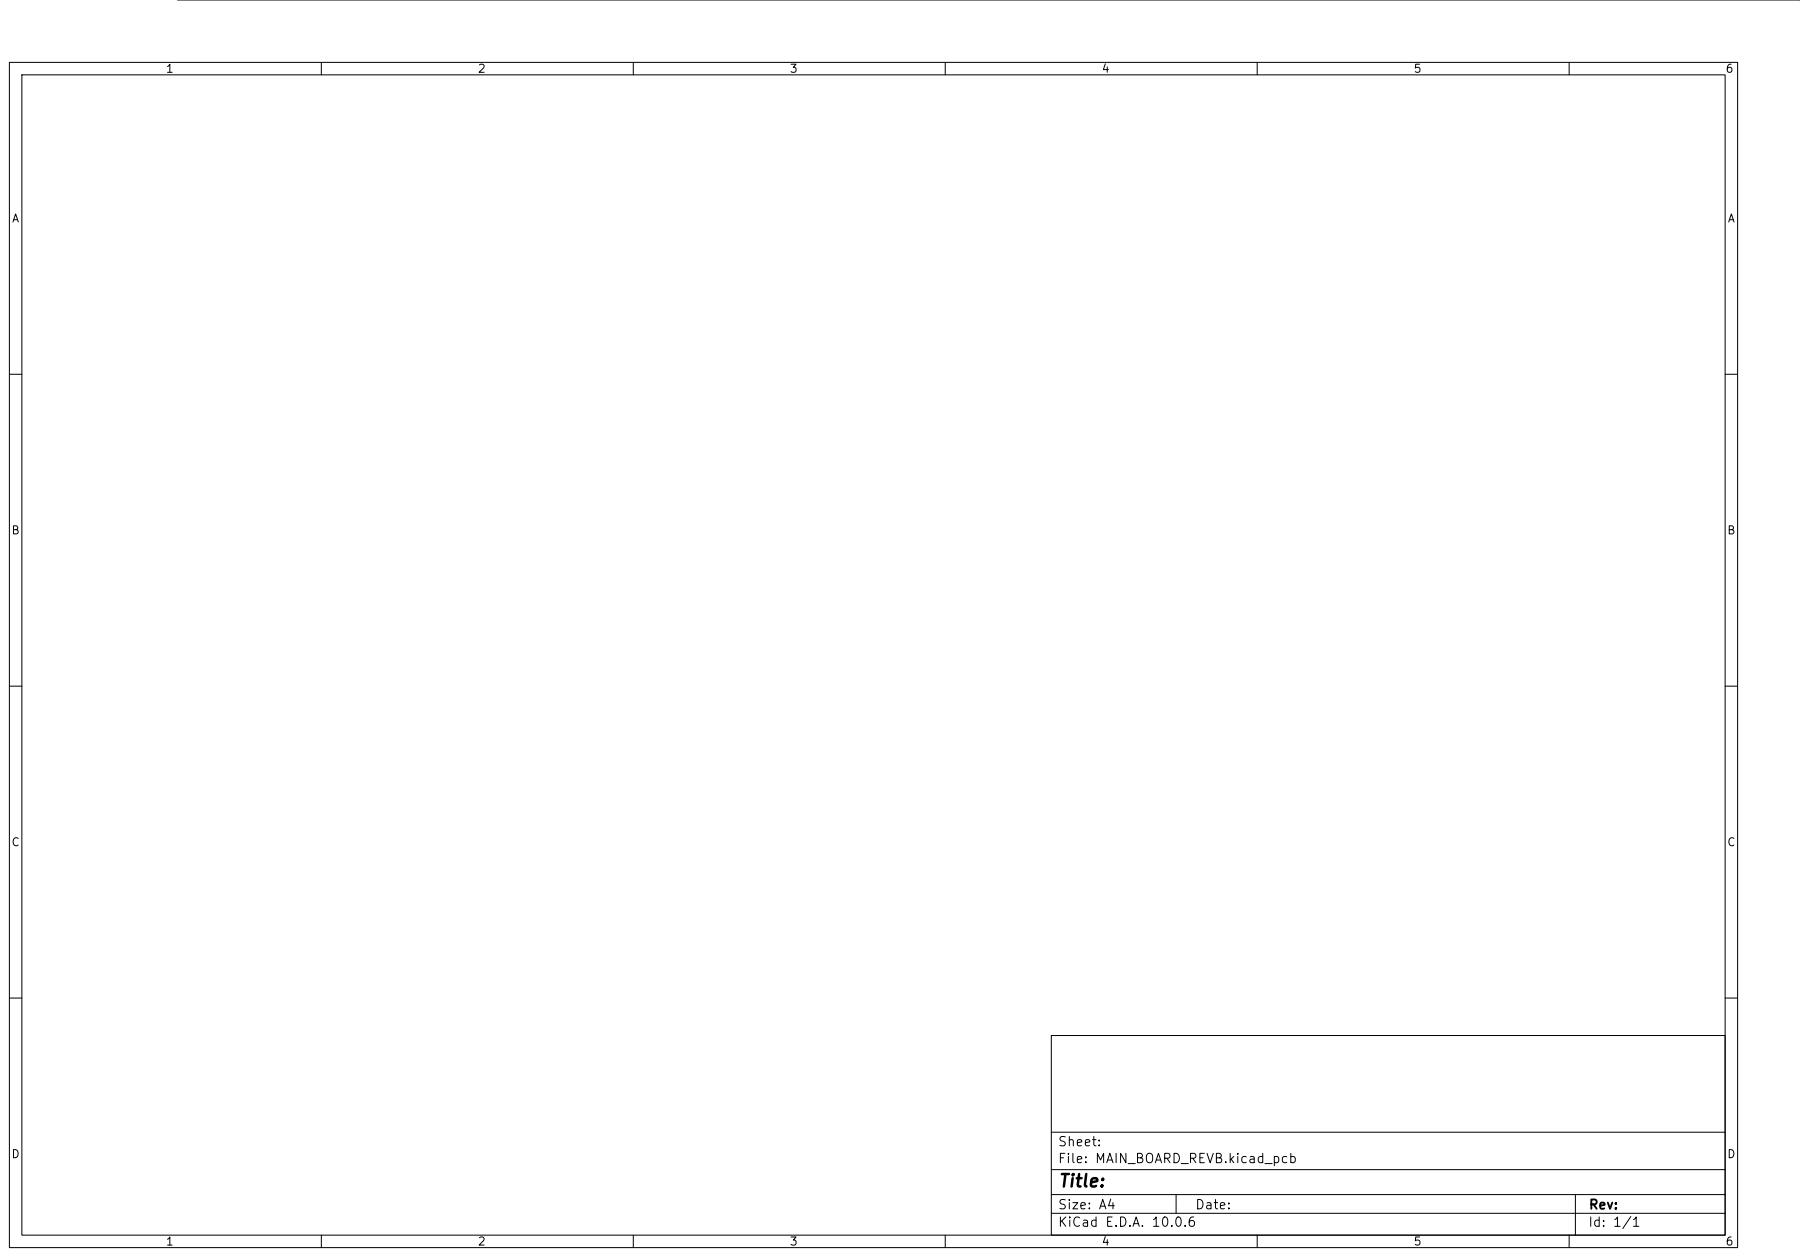
[picture p148: page 1]

Size: A4 | Rev:
KiCad E.D.A. 10.0.6 | Id: 1/1
