herasymyuks/PLFM_RADAR-aeris/beta/pcb/RF_PA/exports/drawings/RF_PA_assembly_bottom_mirrored.pdf

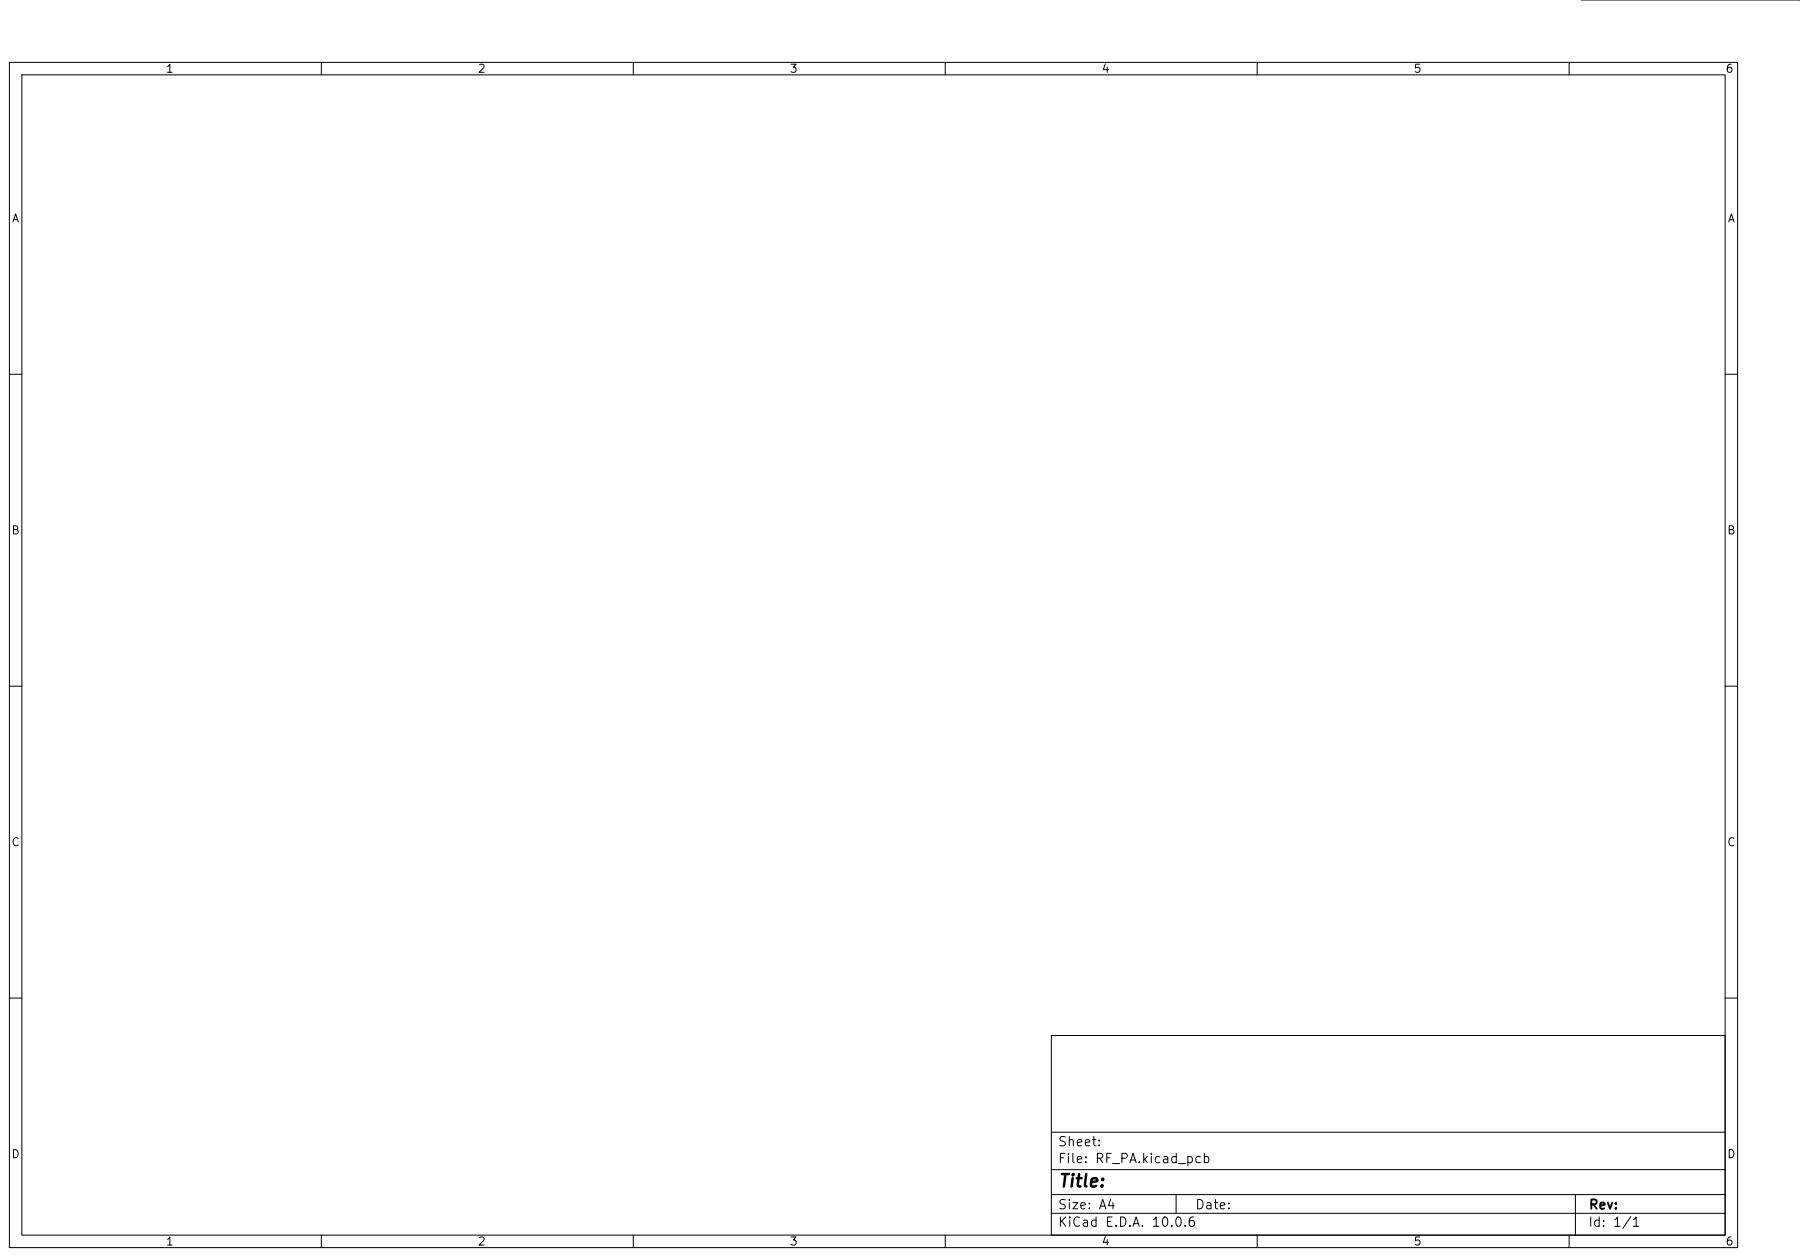
[picture p154: page 1]

Size: A4 | Rev:
KiCad E.D.A. 10.0.6 | Id: 1/1
