herasymyuks/PLFM_RADAR-aeris/beta/pcb/RF_PA/exports/drawings/RF_PA_assembly_top.pdf

Size: A4 | Rev:
KiCad E.D.A. 10.0.6 | Id: 1/1
