herasymyuks/PLFM_RADAR-aeris/engineering/PCB/FREQUENCY_SYNTHESIZER/drawings/FREQUENCY_SYNTHESIZER_bottom_layer_mirrored.pdf

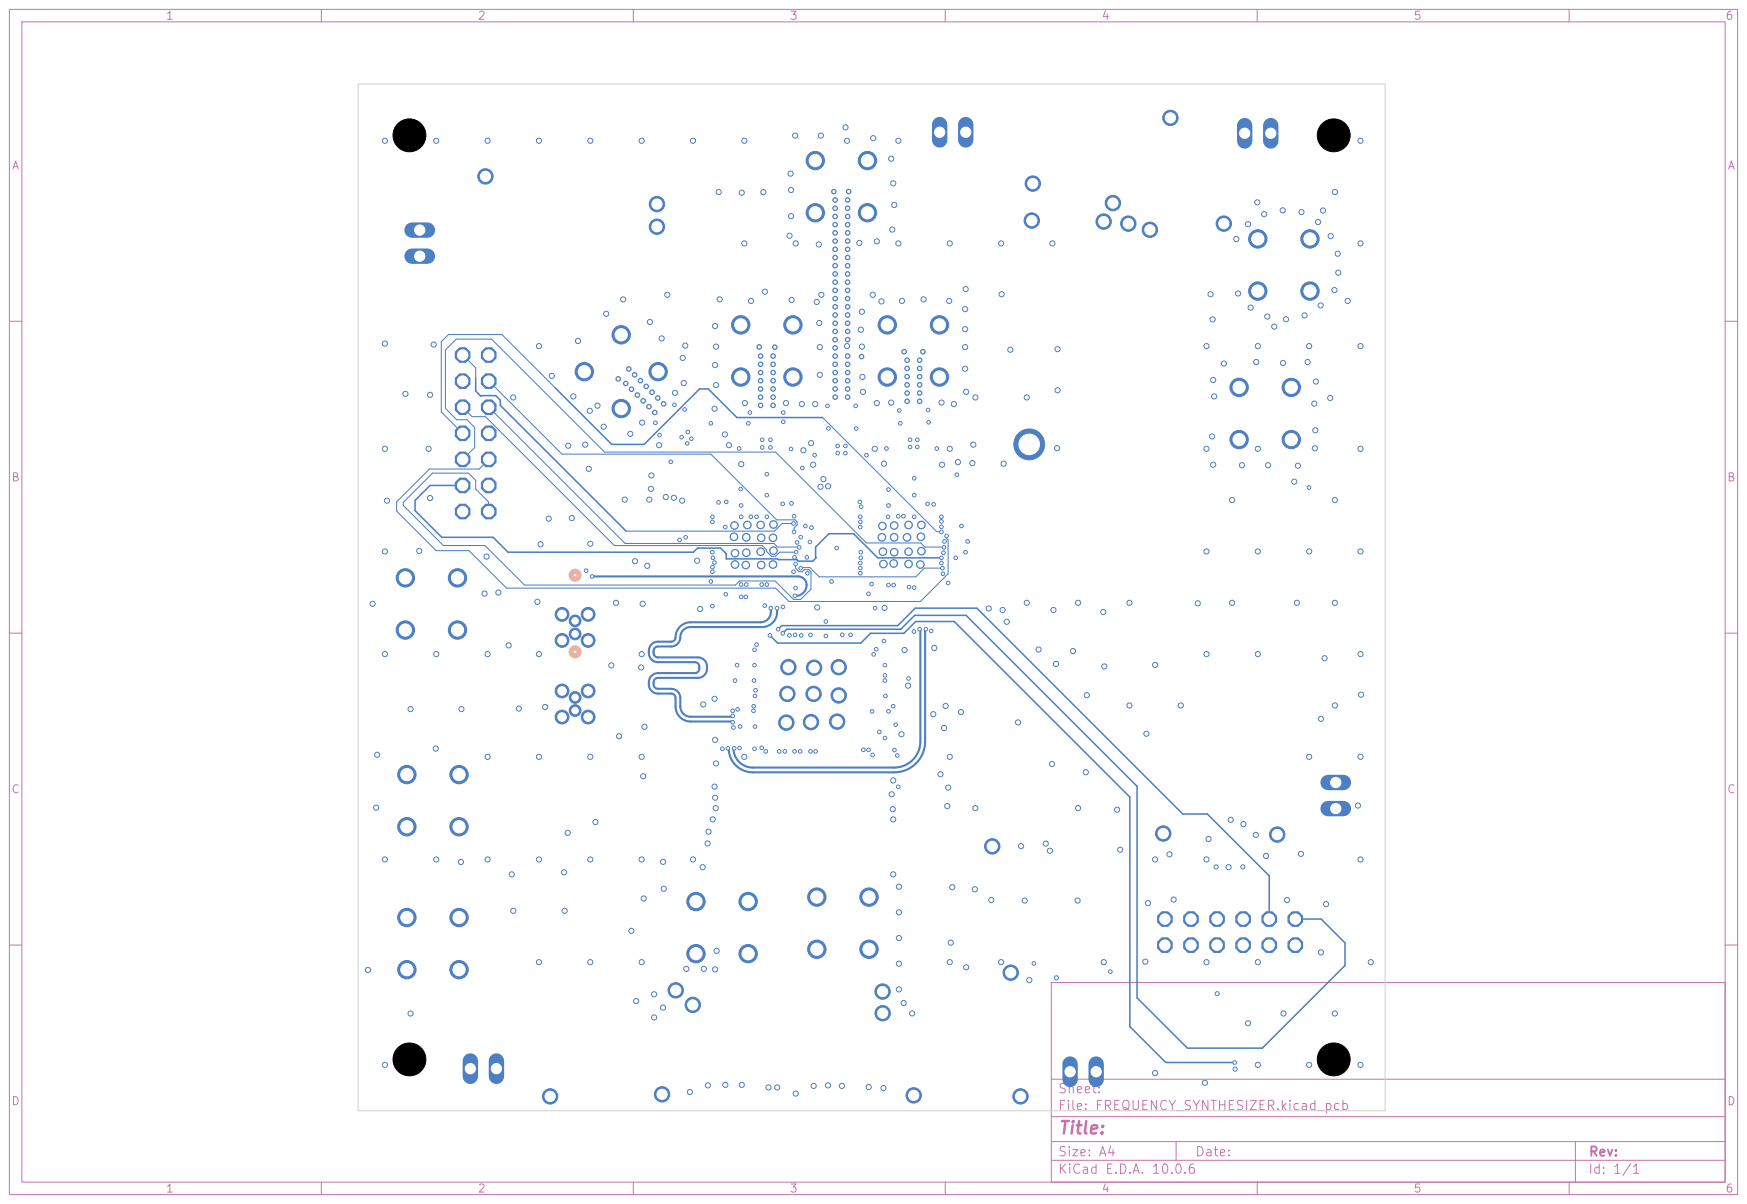
[picture p155: page 1]

Size: A4 | Rev:
KiCad E.D.A. 10.0.6 | Id: 1/1
