herasymyuks/PLFM_RADAR-aeris/engineering/PCB/FREQUENCY_SYNTHESIZER/drawings/FREQUENCY_SYNTHESIZER_copper_layers.pdf

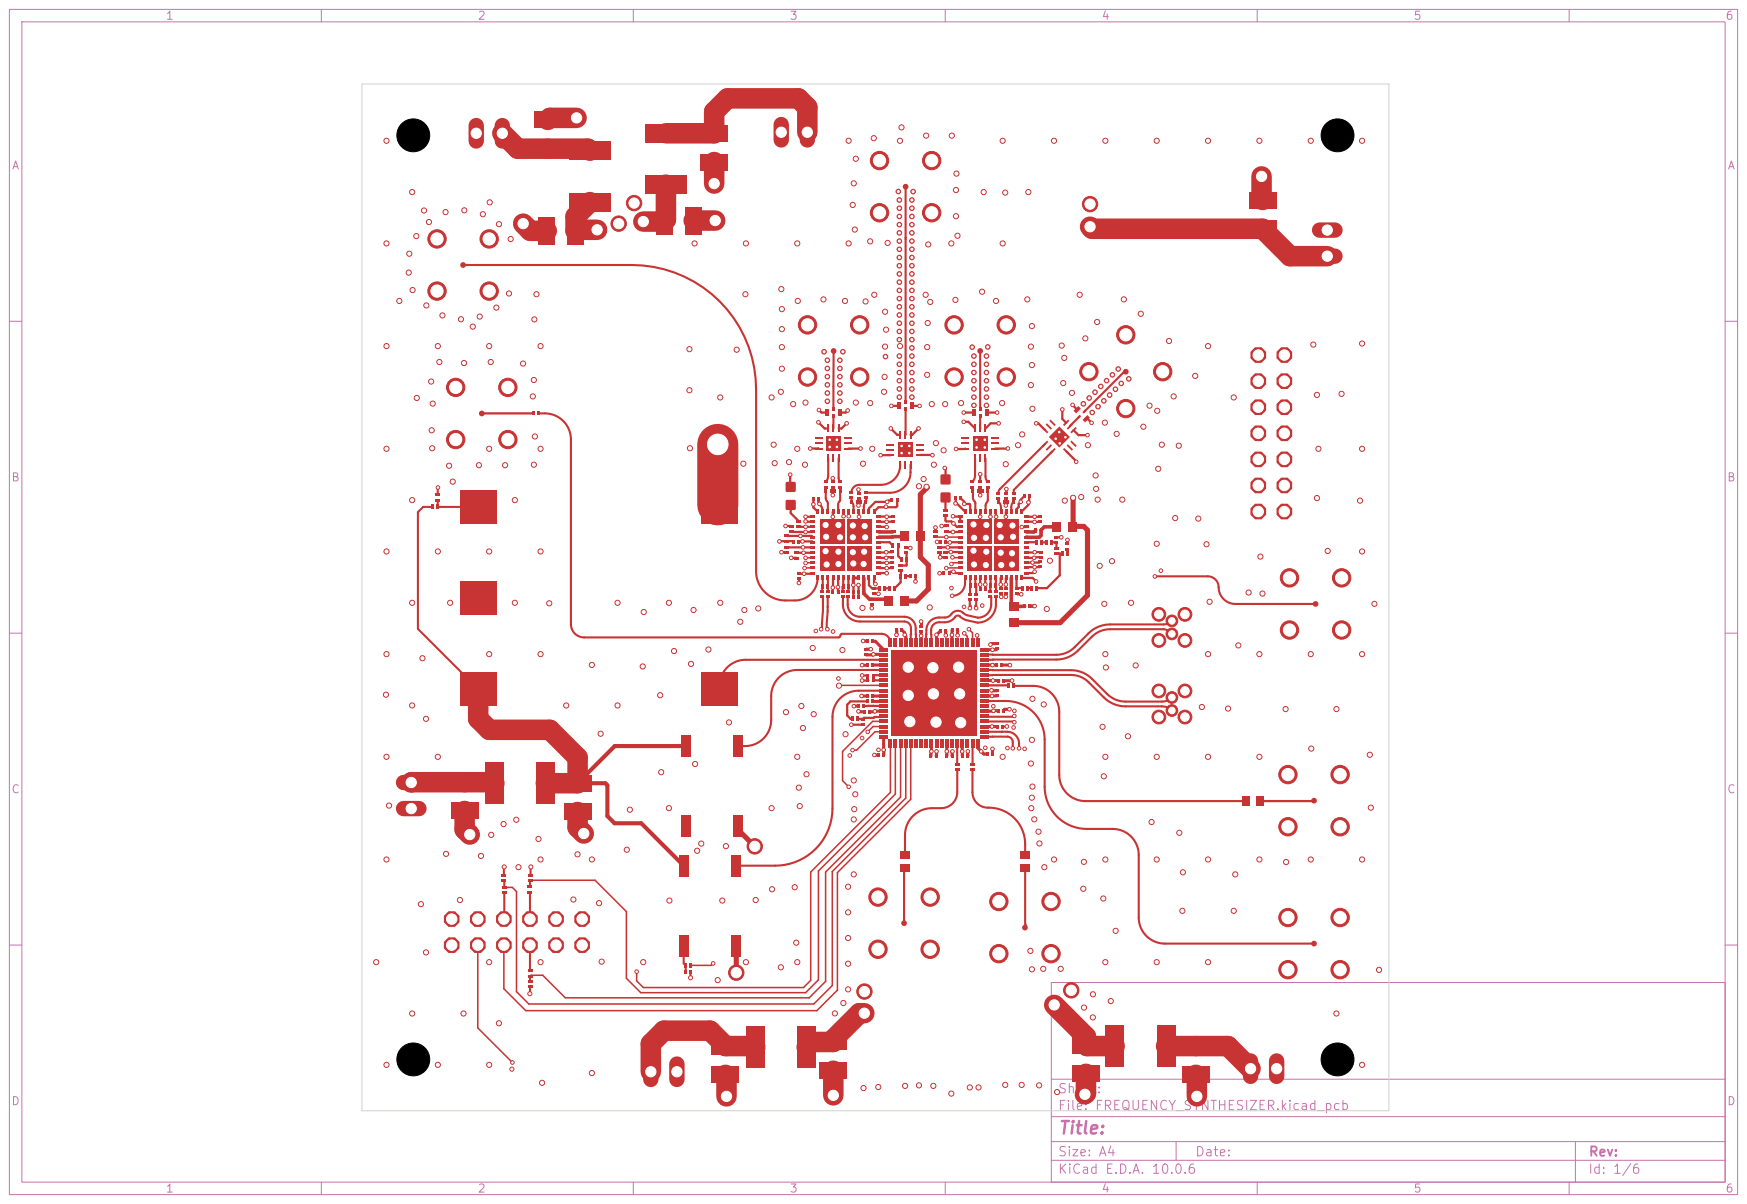
[picture p156: page 1]

Size: A4 | Rev:
KiCad E.D.A. 10.0.6 | Id: 1/6

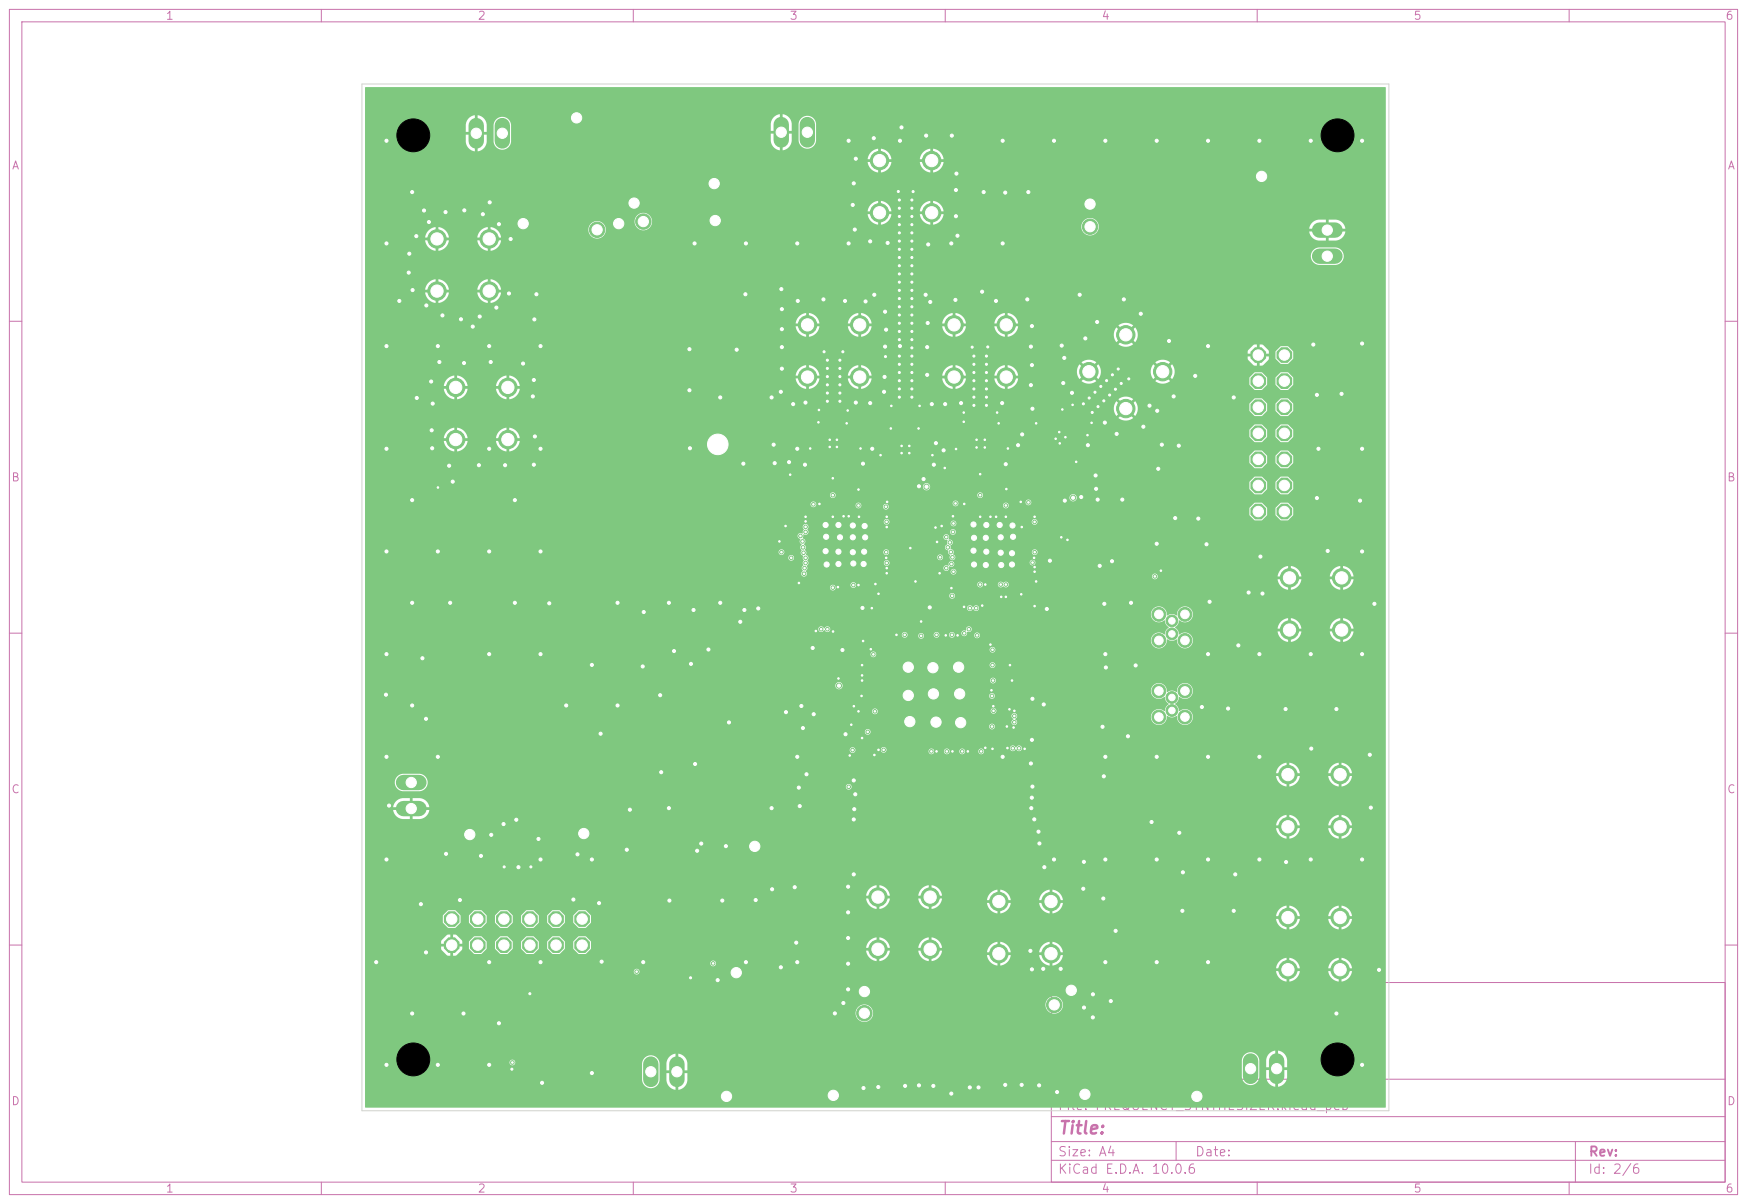
[picture p157: page 2]

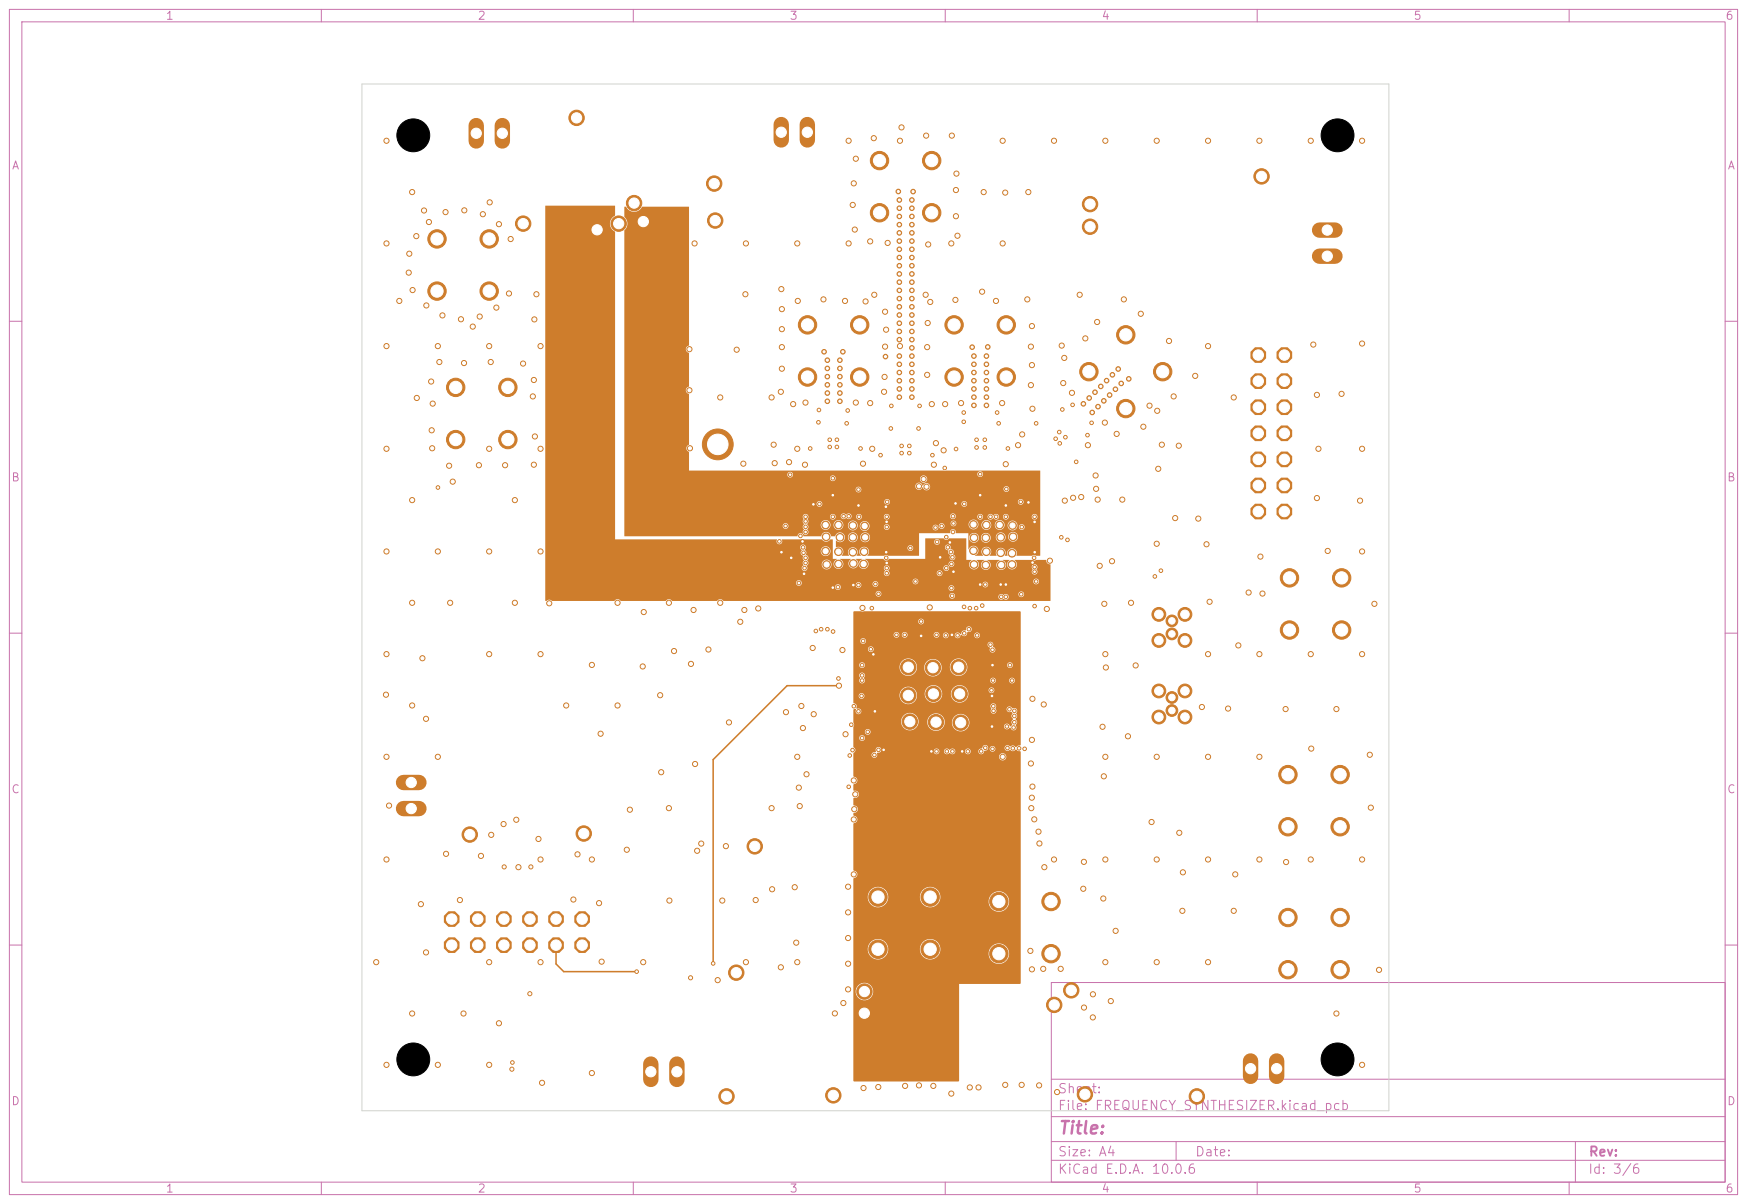
[picture p158: page 3]

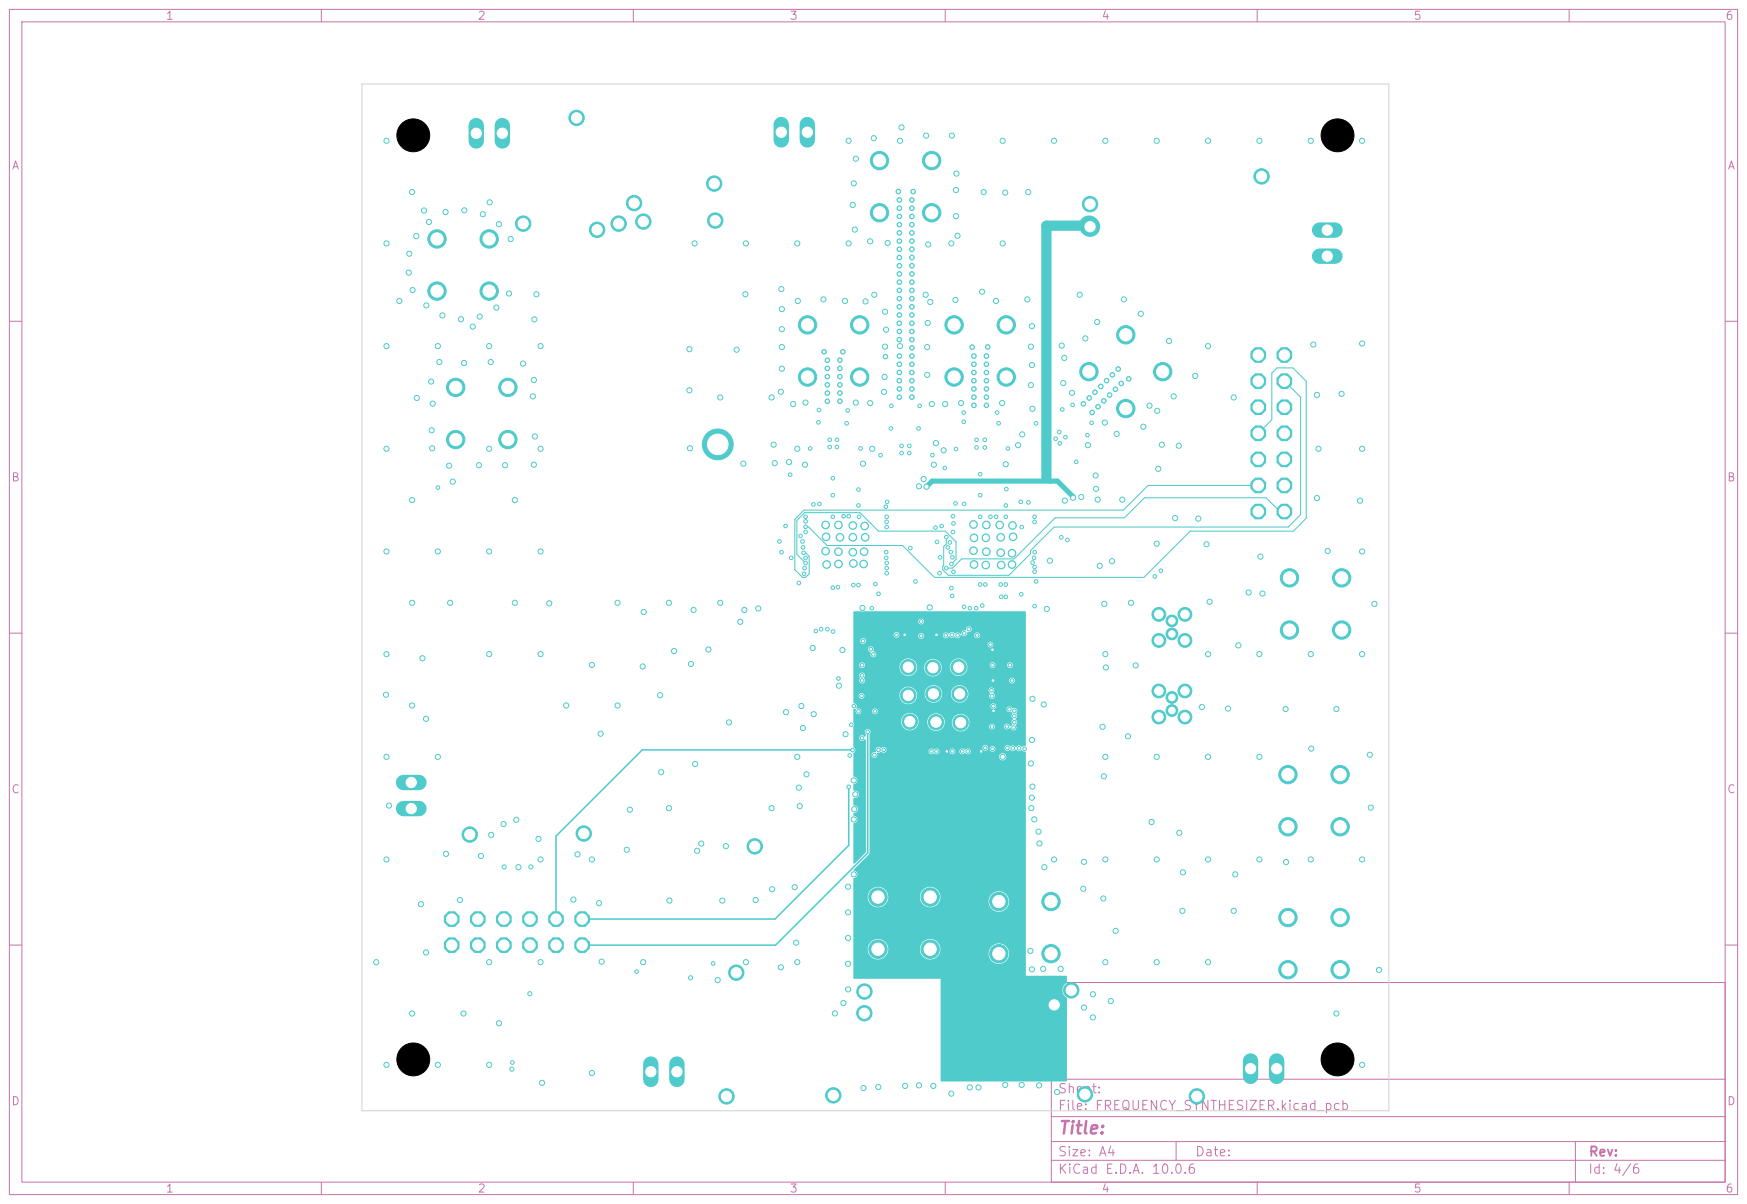
[picture p159: page 4]

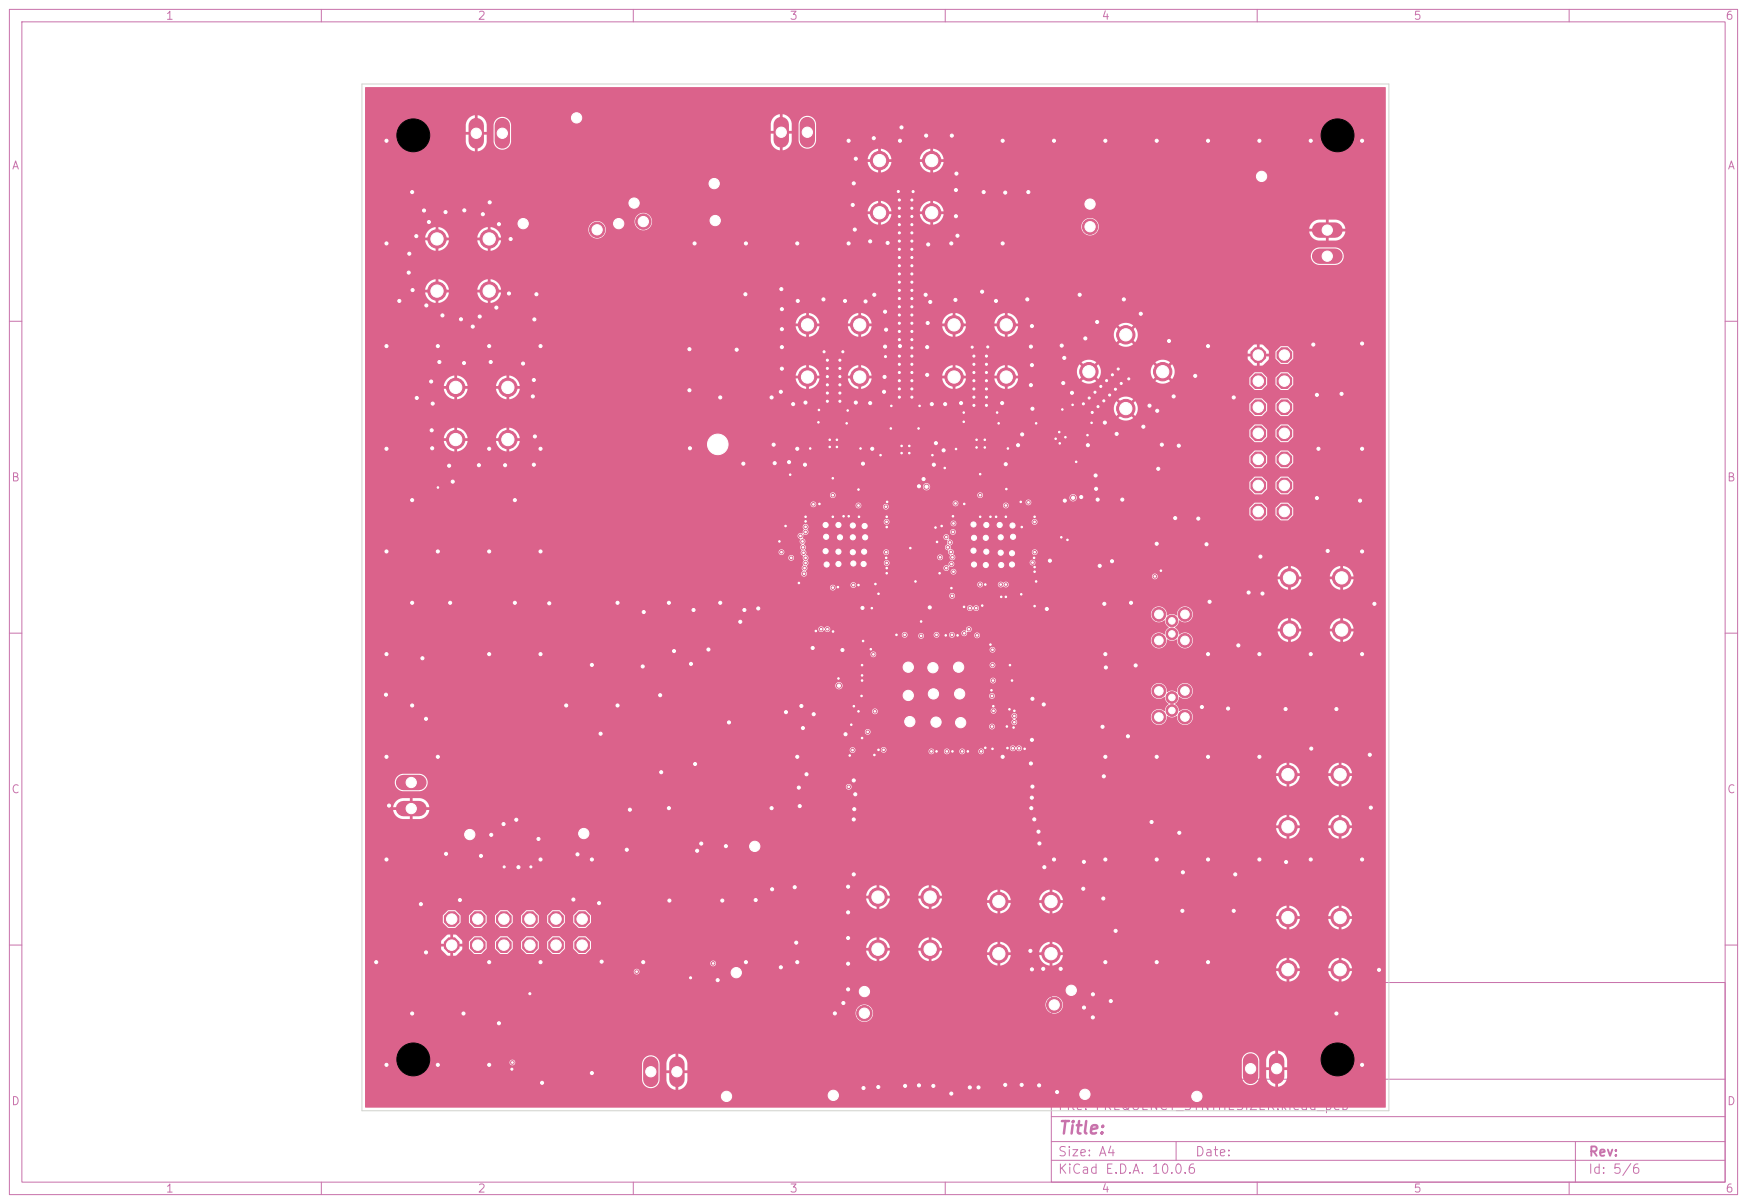
[picture p160: page 5]

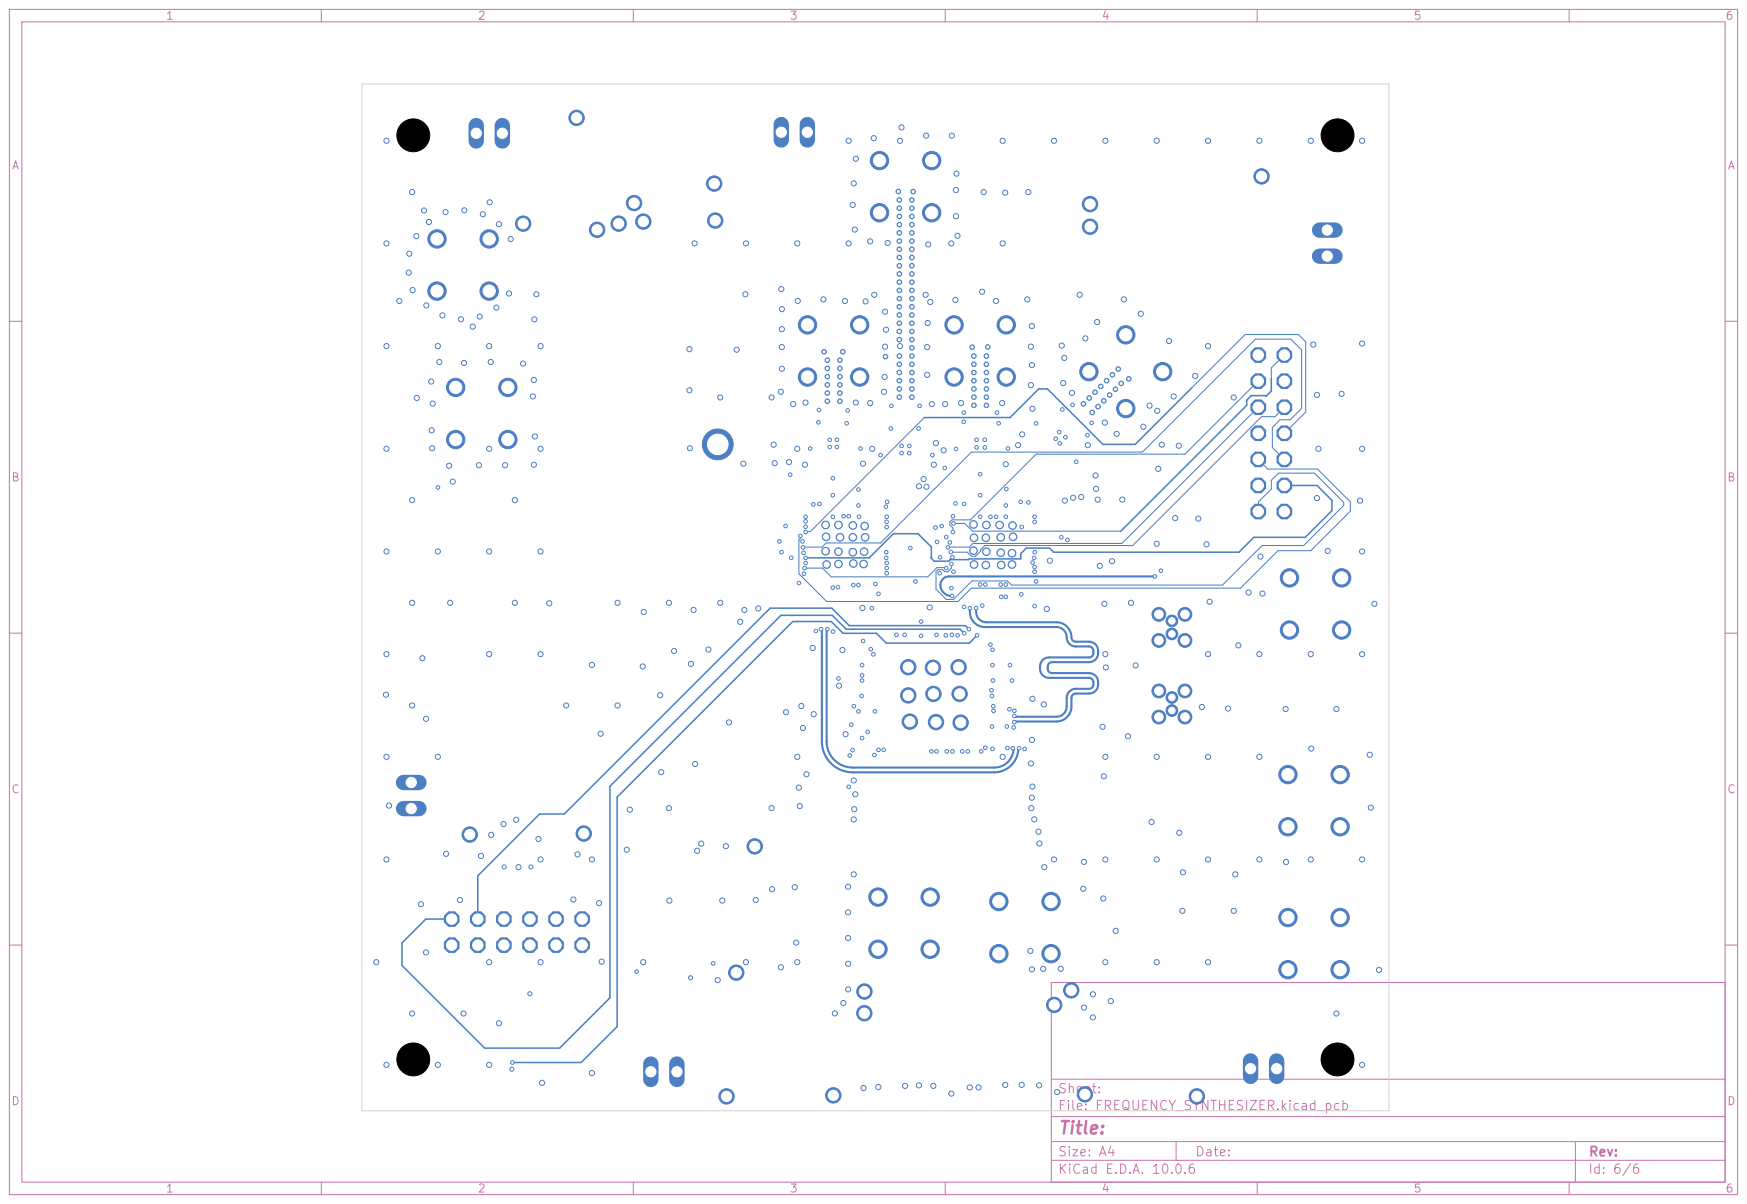
[picture p161: page 6]
