herasymyuks/PLFM_RADAR-aeris/engineering/PCB/FREQUENCY_SYNTHESIZER/drawings/FREQUENCY_SYNTHESIZER_outline.pdf

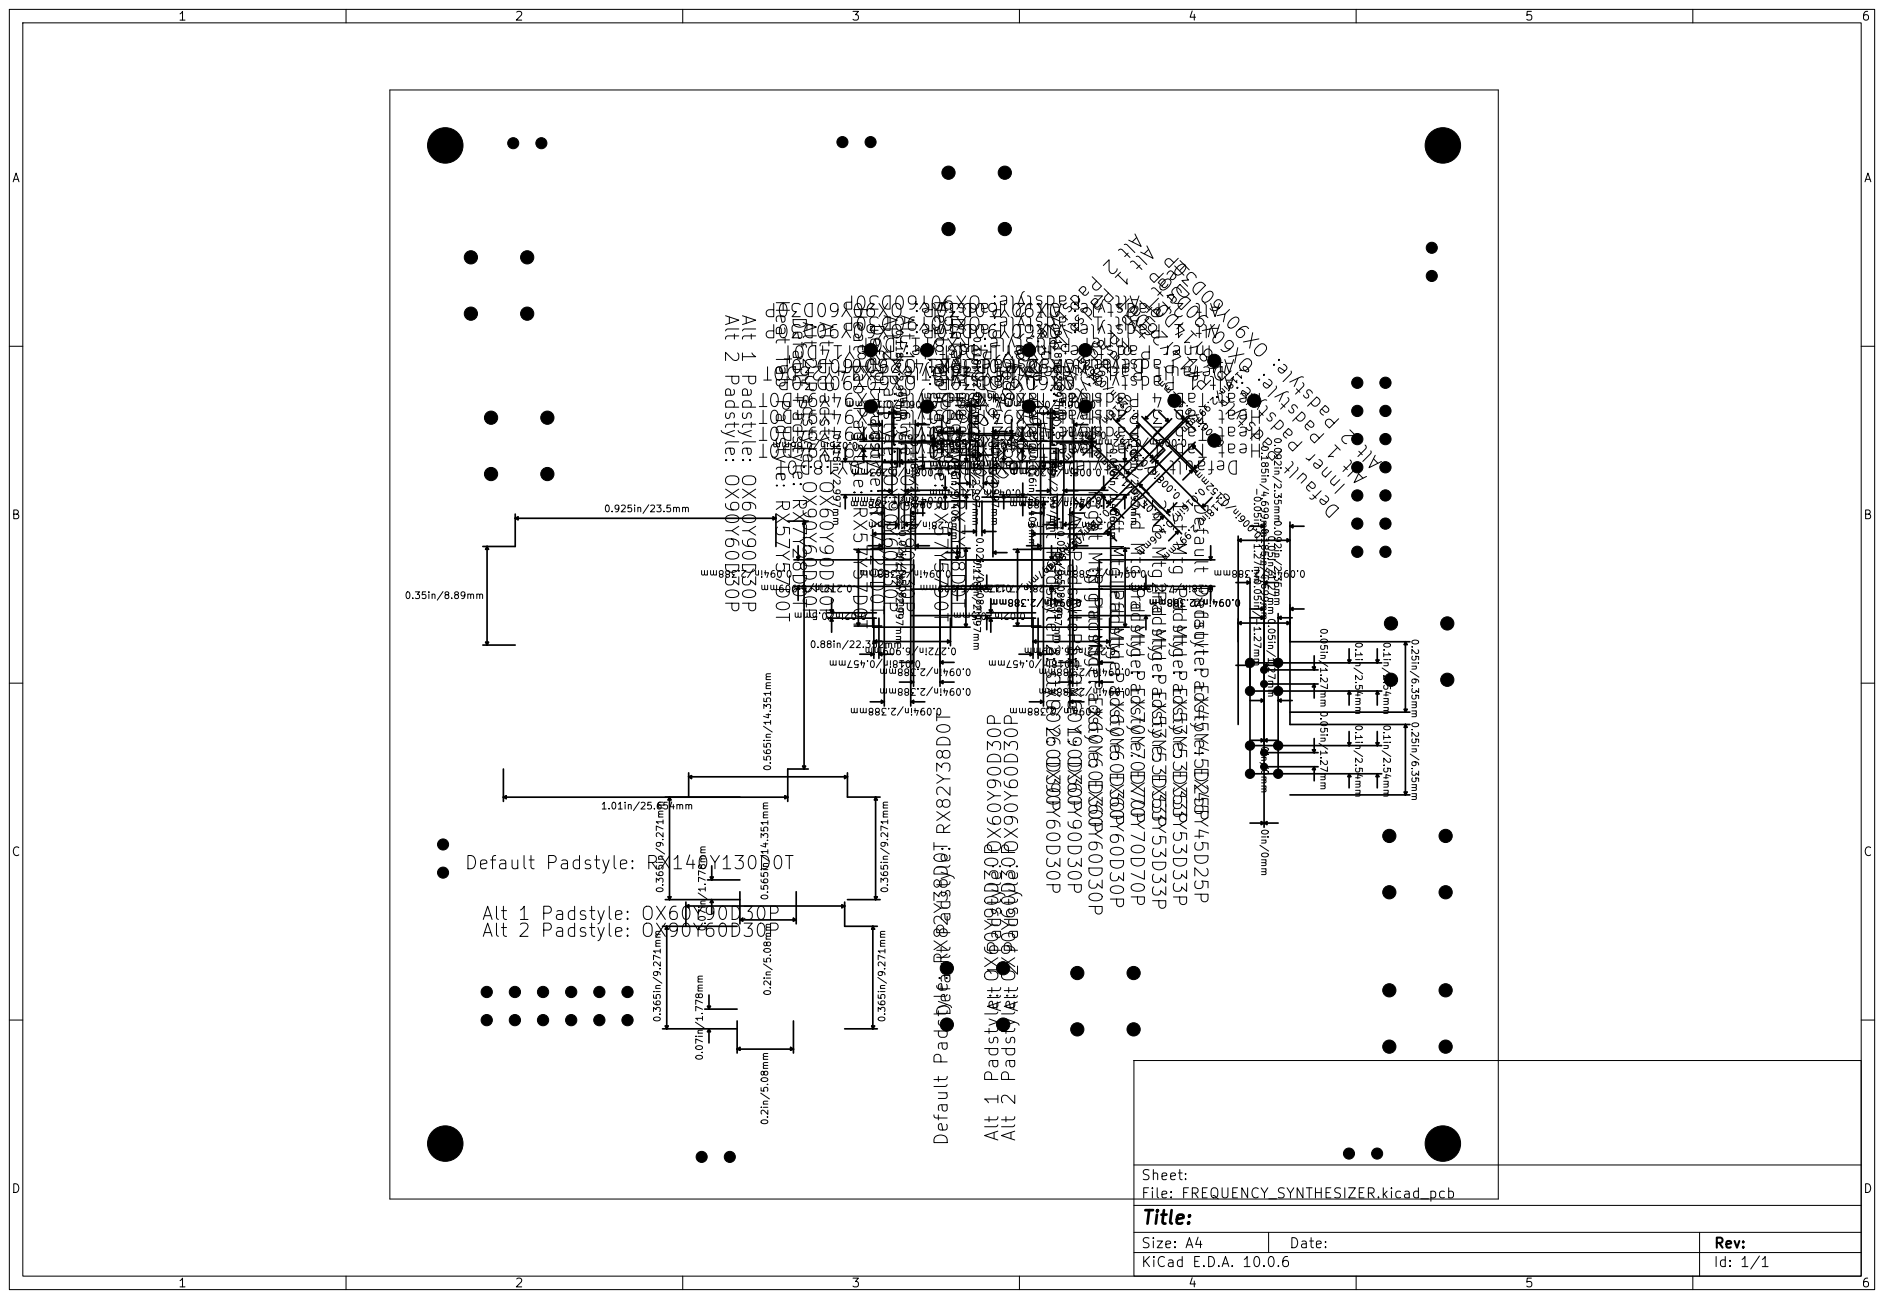
[picture p162: page 1]

RX14Y26D0T Padstyle: Default 0.026in/0.66mm 0.047in/1.194mm 0.008in/0.203mm 0.006in/0.152mm 0.006in/0.152mm Default Padstyle: RX14Y26D0T Inner RX8Y14D0T Alt 1 OX60Y90D30P 2 OX90Y60D30P Alt Padstyle 2: OX90Y60D30P Alt Padstyle 1: OX60Y90D30P Right Mtg Padstyle: EX60Y60D30P Left Mtg Padstyle: EX60Y60D30P 3rd Mtg Padstyle: EX70Y70D70P 2nd Mtg Padstyle: EX53Y53D33P 1st Mtg Padstyle: EX53Y53D33P Default Padstyle: EX45Y45D25P -0.05in/-1.27mm 0.185in/4.699mm 0in/0mm 0.05in/1.27mm 0.092in/2.35mm 0.05in/1.27mm 0.1in/2.54mm 0.1in/2.54mm 0.25in/6.35mm

RX14Y26D0T Padstyle: Default 0.365in/9.271mm 0.07in/1.778mm 0.565in/14.351mm 0.2in/5.08mm 0.365in/9.271mm Default Padstyle: RX82Y38D0T Alt 1 Padstyle: OX60Y90D30P Alt 2 Padstyle: OX90Y60D30P 0.026in/0.66mm

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

0.094in/2.388mm Alt Padstyle 2: OX90Y60D30P Alt Padstyle 1: OX60Y90D30P Right Mtg Padstyle: EX60Y60D30P Left Mtg Padstyle: EX60Y60D30P 3rd Mtg Padstyle: EX70Y70D70P 2nd Mtg Padstyle: EX53Y53D33P 1st Mtg Padstyle: EX53Y53D33P Default Padstyle: EX45Y45D25P -0.05in/-1.27mm 0.185in/4.699mm 0in/0mm 0.05in/1.27mm 0.092in/2.35mm 0.05in/1.27mm 0.1in/2.54mm 0.1in/2.54mm 0.25in/6.35mm

Size: A4 | Rev:
KiCad E.D.A. 10.0.6 | Id: 1/1
