herasymyuks/PLFM_RADAR-aeris/engineering/PCB/FREQUENCY_SYNTHESIZER/drawings/FREQUENCY_SYNTHESIZER_top_layer.pdf

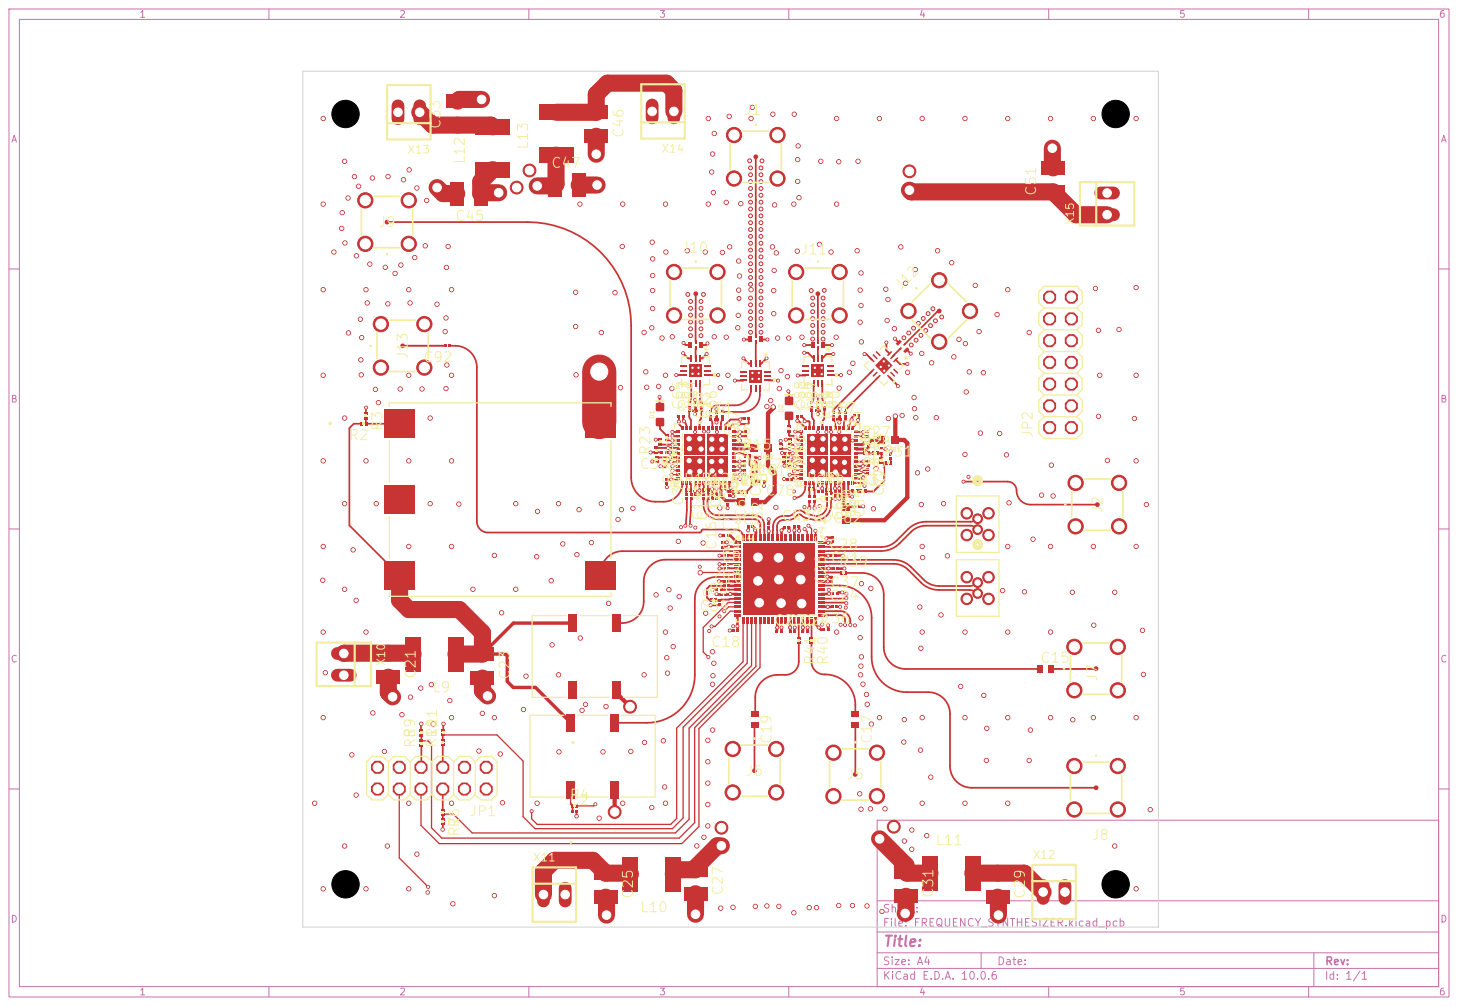
[picture p163: page 1]

Size: A4 | Rev:
KiCad E.D.A. 10.0.6 | Id: 1/1
