herasymyuks/PLFM_RADAR-aeris/engineering/PCB/MAIN_BOARD/drawings/MAIN_BOARD_copper_layers.pdf

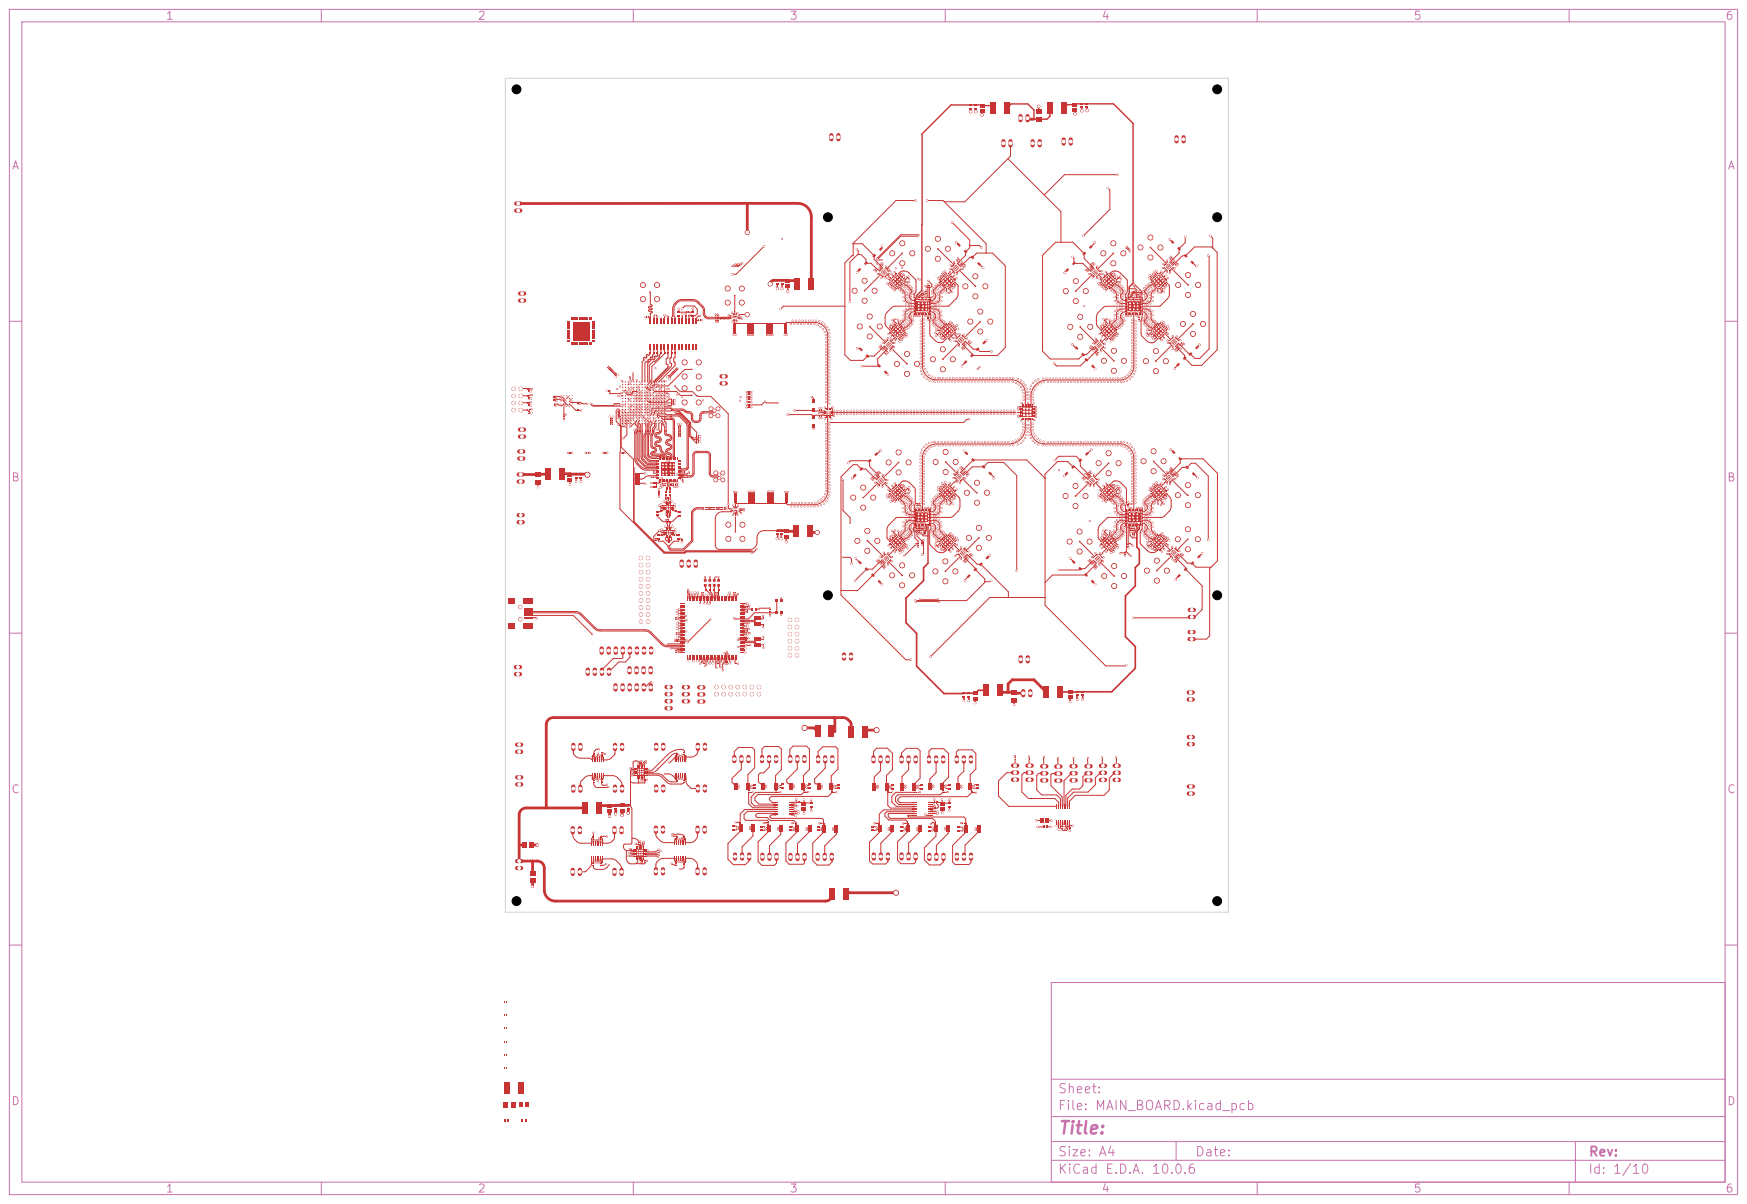
[picture p165: page 1]

Size: A4 | Rev:
KiCad E.D.A. 10.0.6 | Id: 1/10

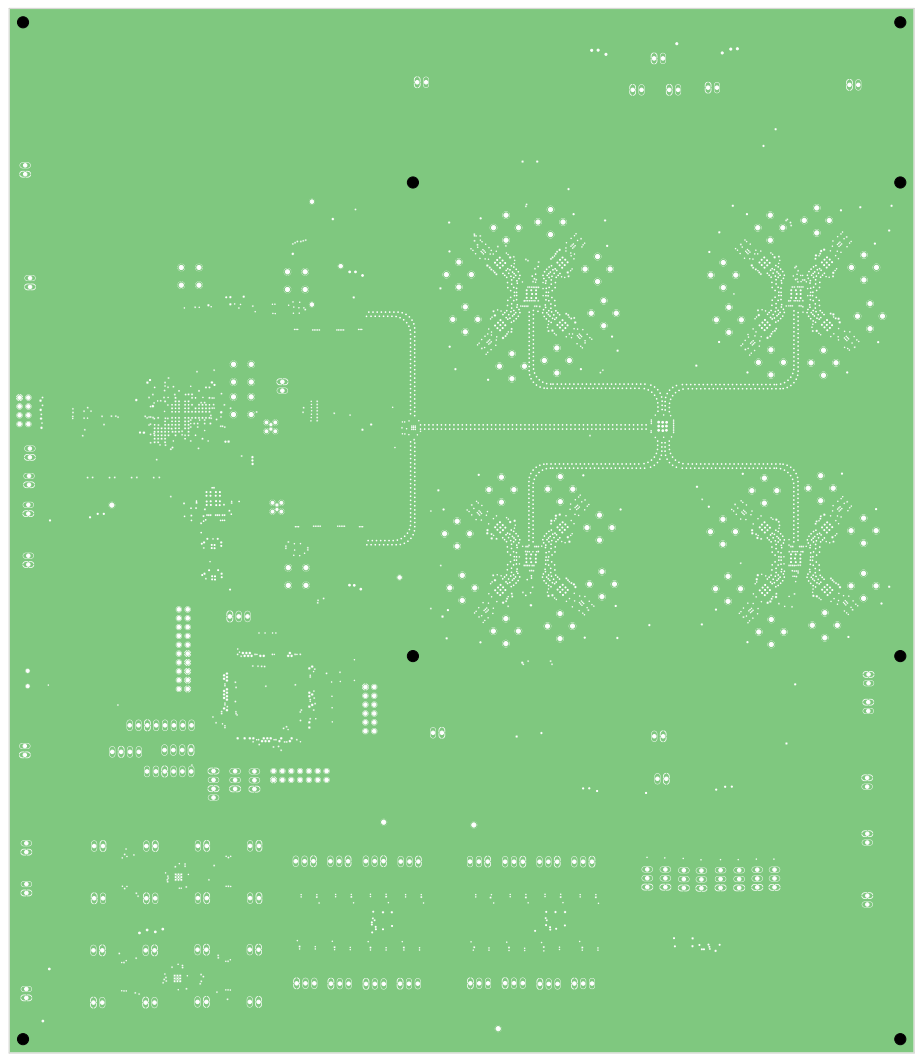
[picture p166: page 2]

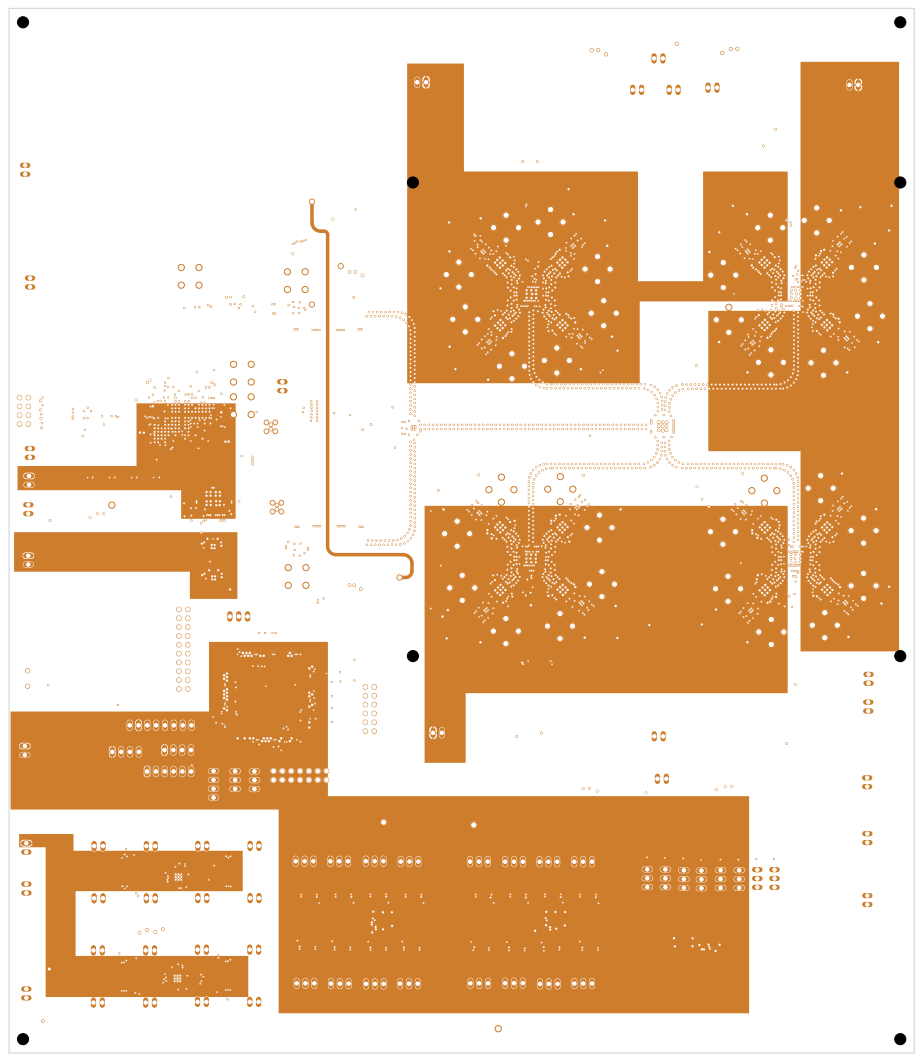
[picture p167: page 3]

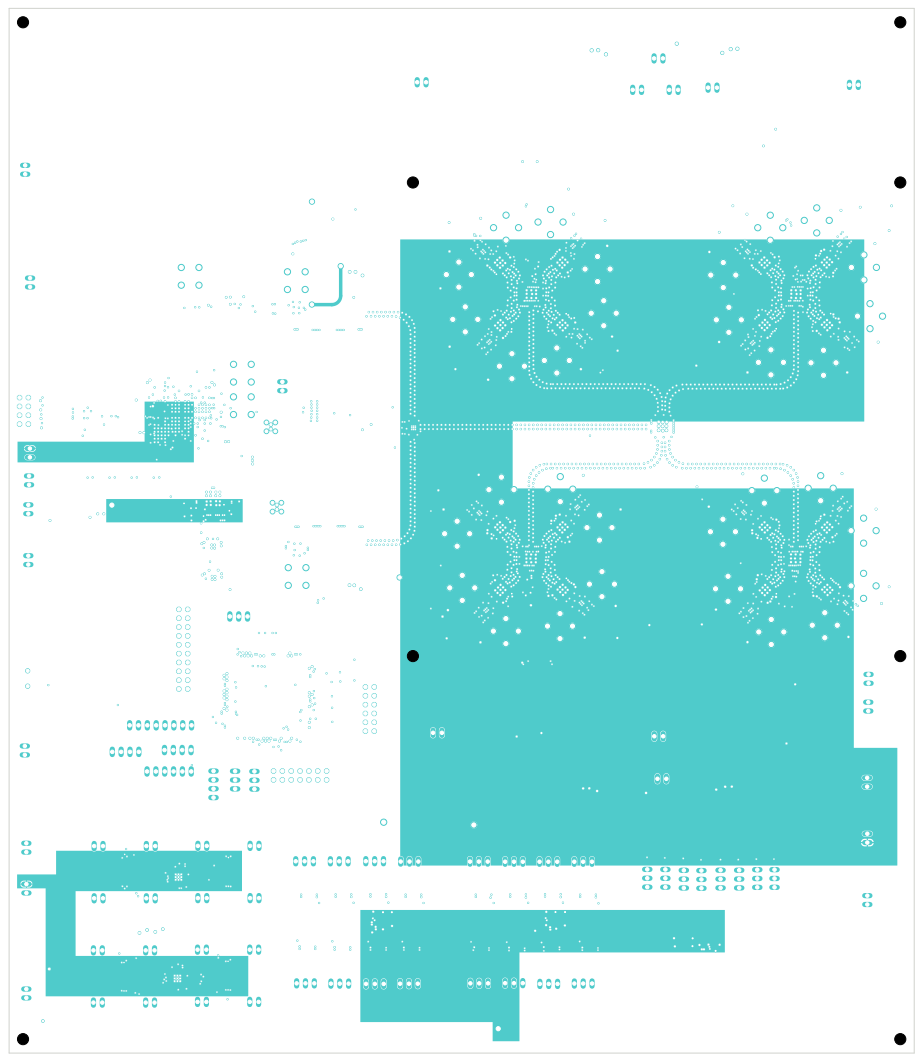
[picture p168: page 4]

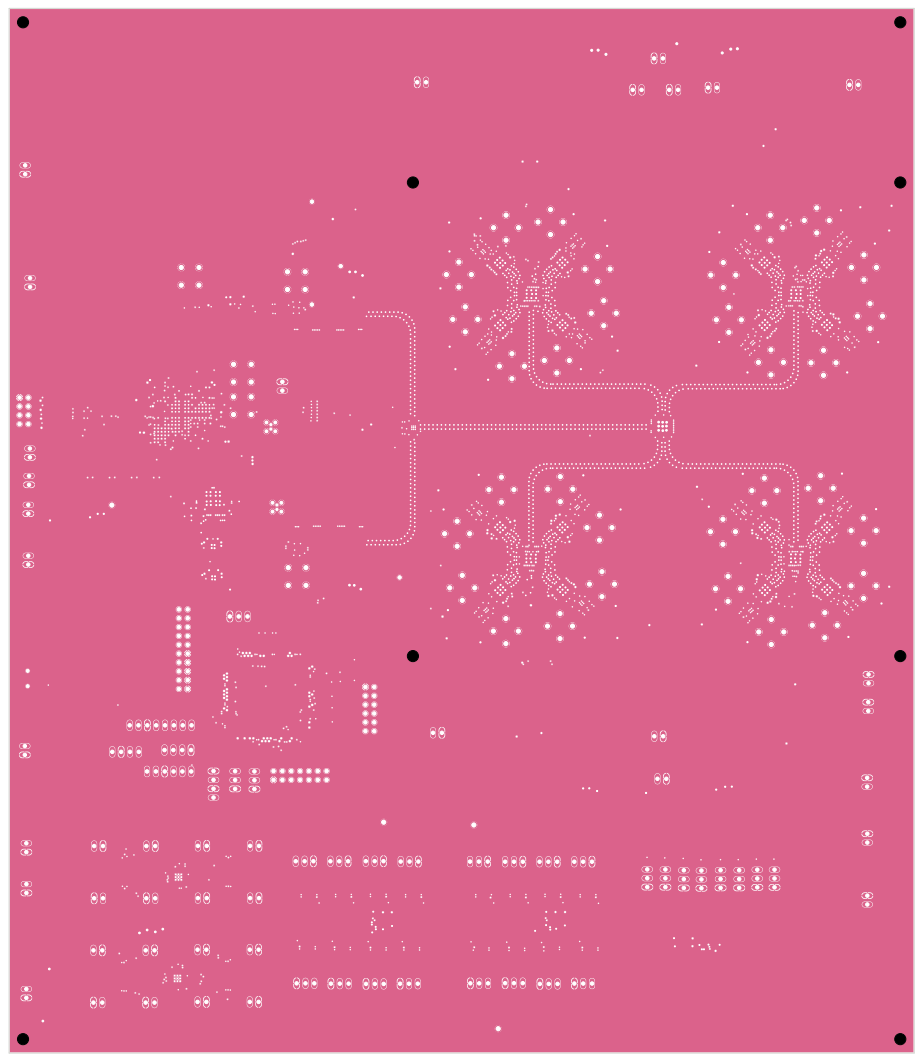
[picture p169: page 5]

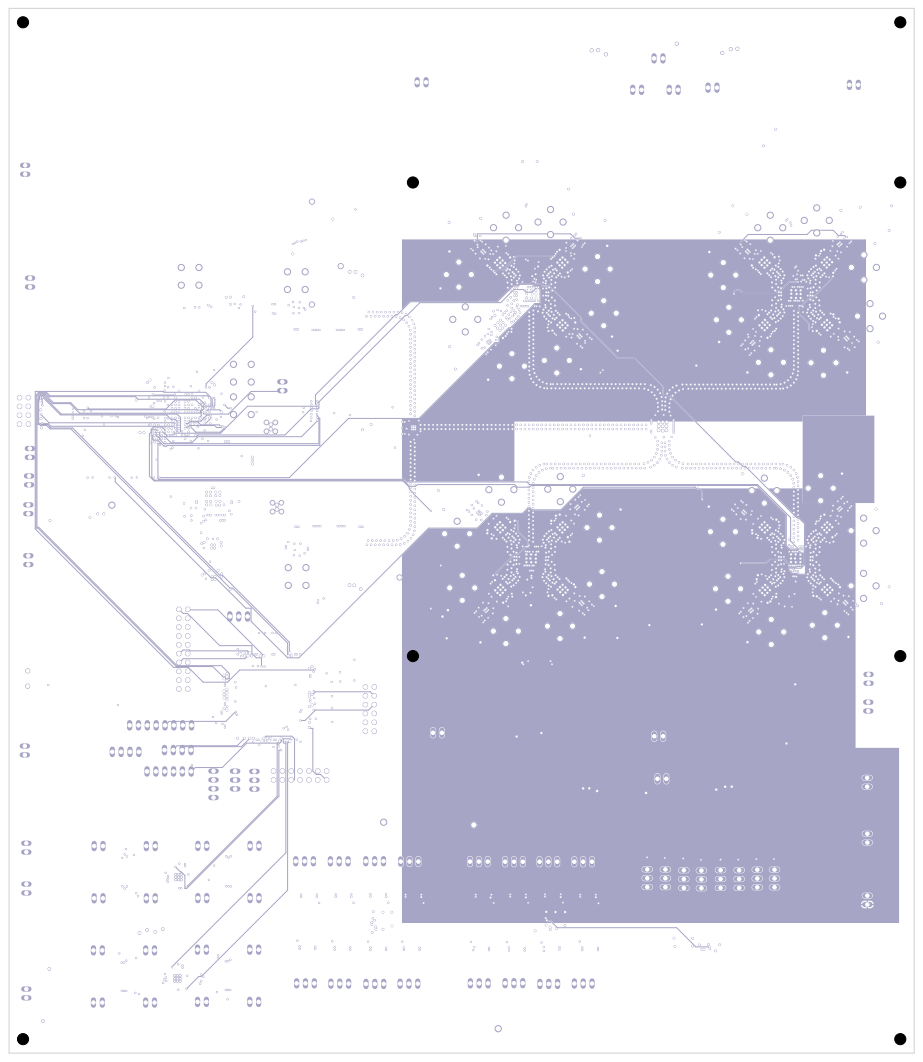
[picture p170: page 6]

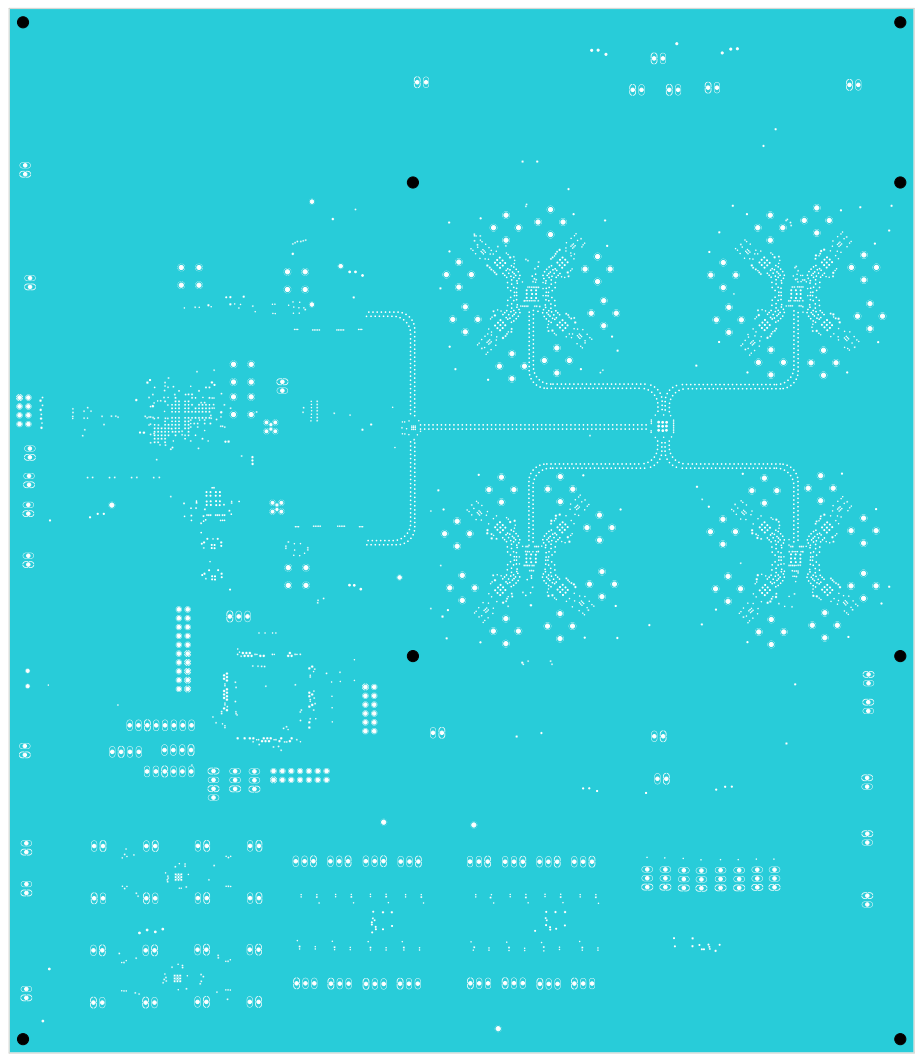
[picture p171: page 7]

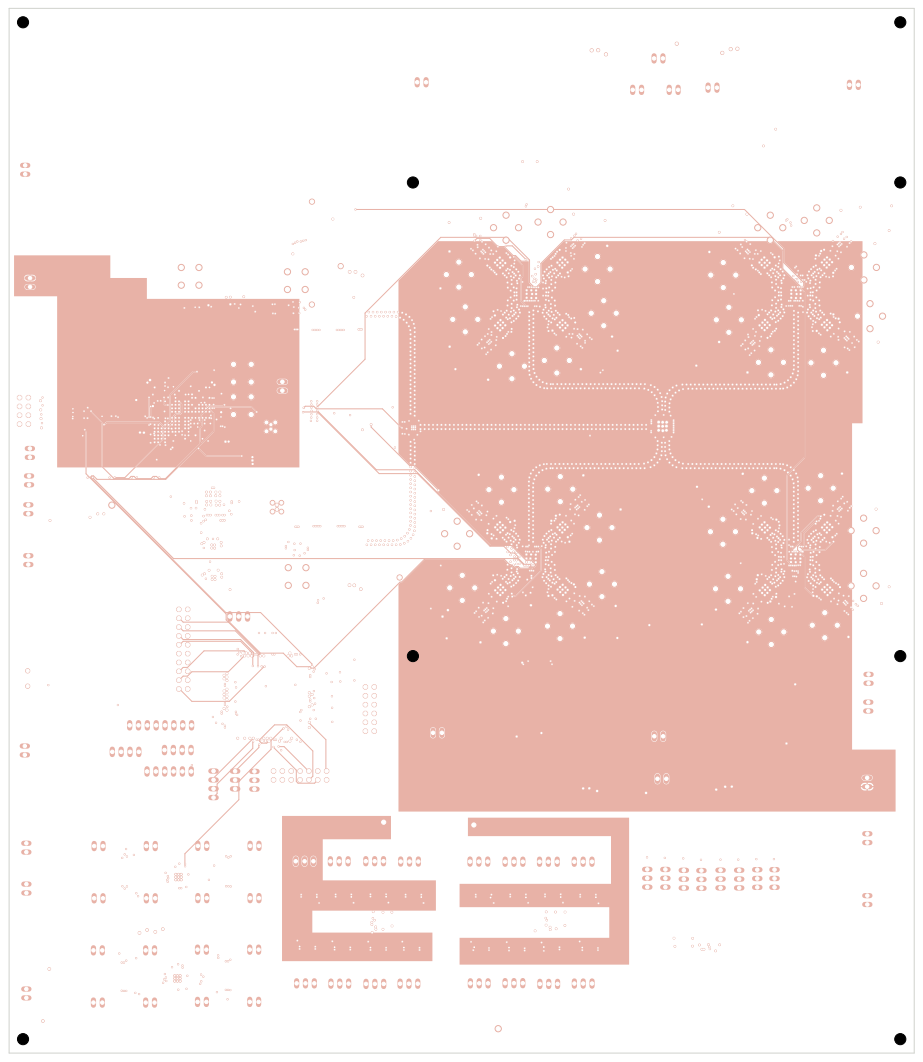
[picture p172: page 8]

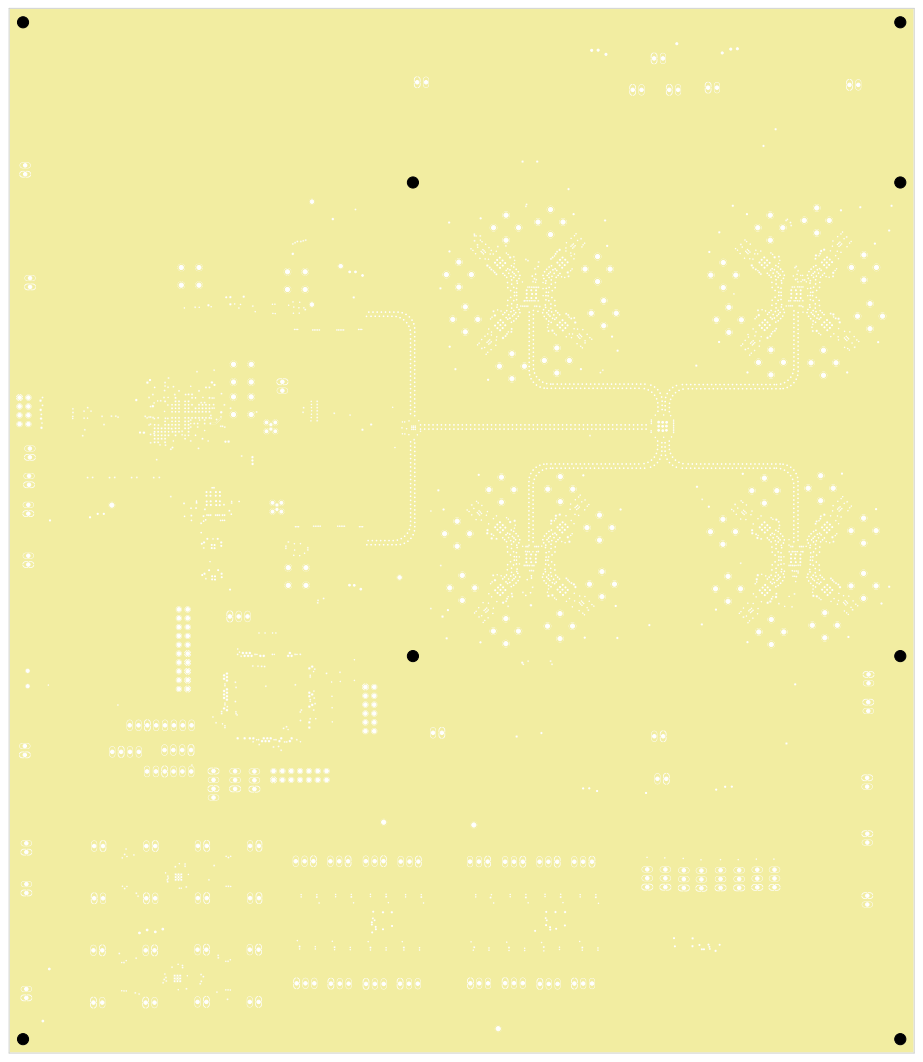
[picture p173: page 9]

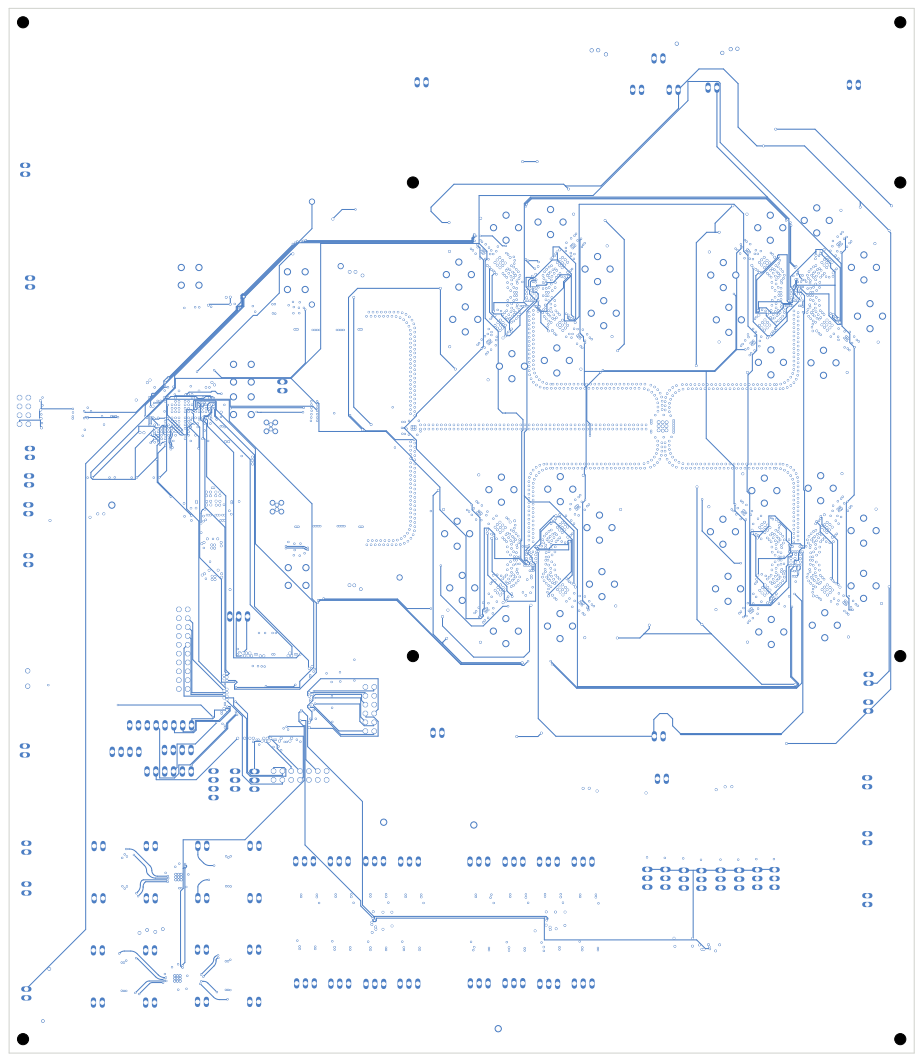
[picture p174: page 10]
