herasymyuks/PLFM_RADAR-aeris/engineering/PCB/MAIN_BOARD/drawings/MAIN_BOARD_outline.pdf

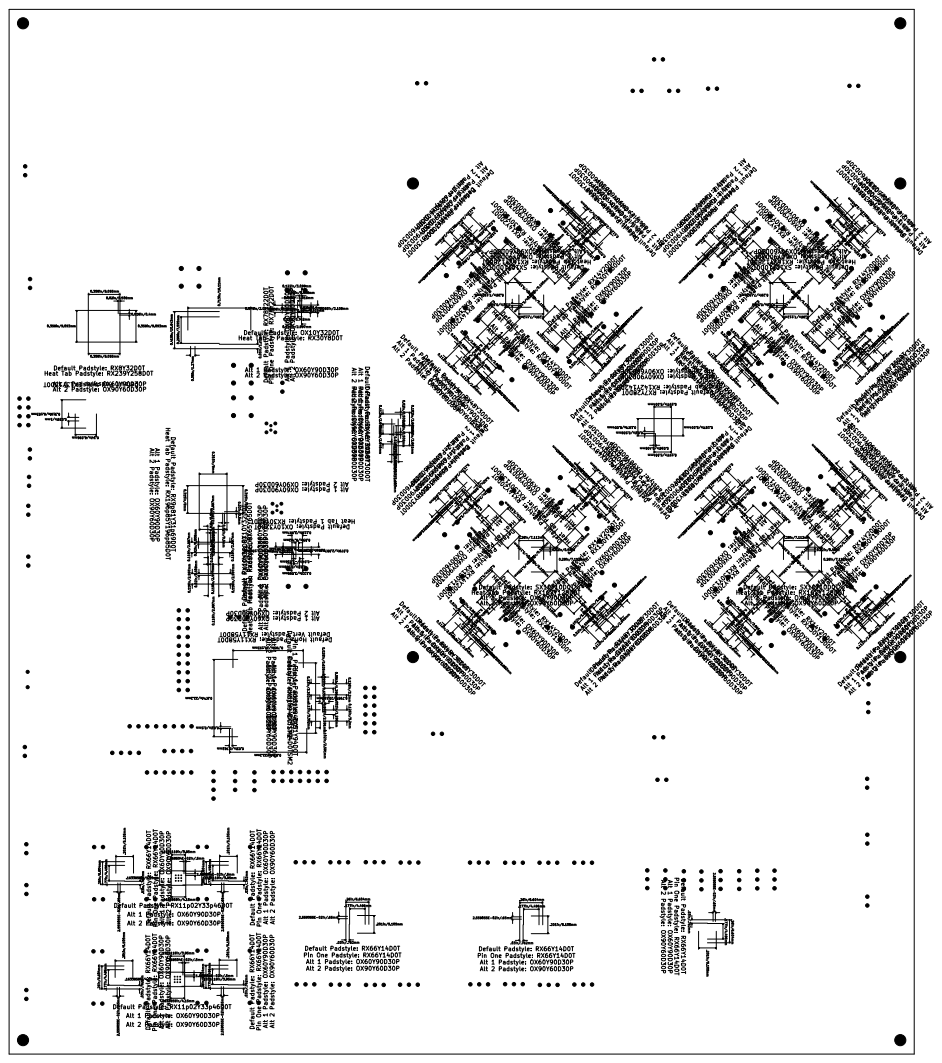
[picture p175: page 1]

2.559055E-02in/.65mm Pin One Padstyle: RX66Y14D0T Default Padstyle: RX66Y14D0T Alt 1 Padstyle: OX60Y90D30P

Size: A4 | Rev:
KiCad E.D.A. 10.0.6 | Id: 1/1
