herasymyuks/PLFM_RADAR-aeris/engineering/PCB/MAIN_BOARD/drawings/MAIN_BOARD_top_layer.pdf

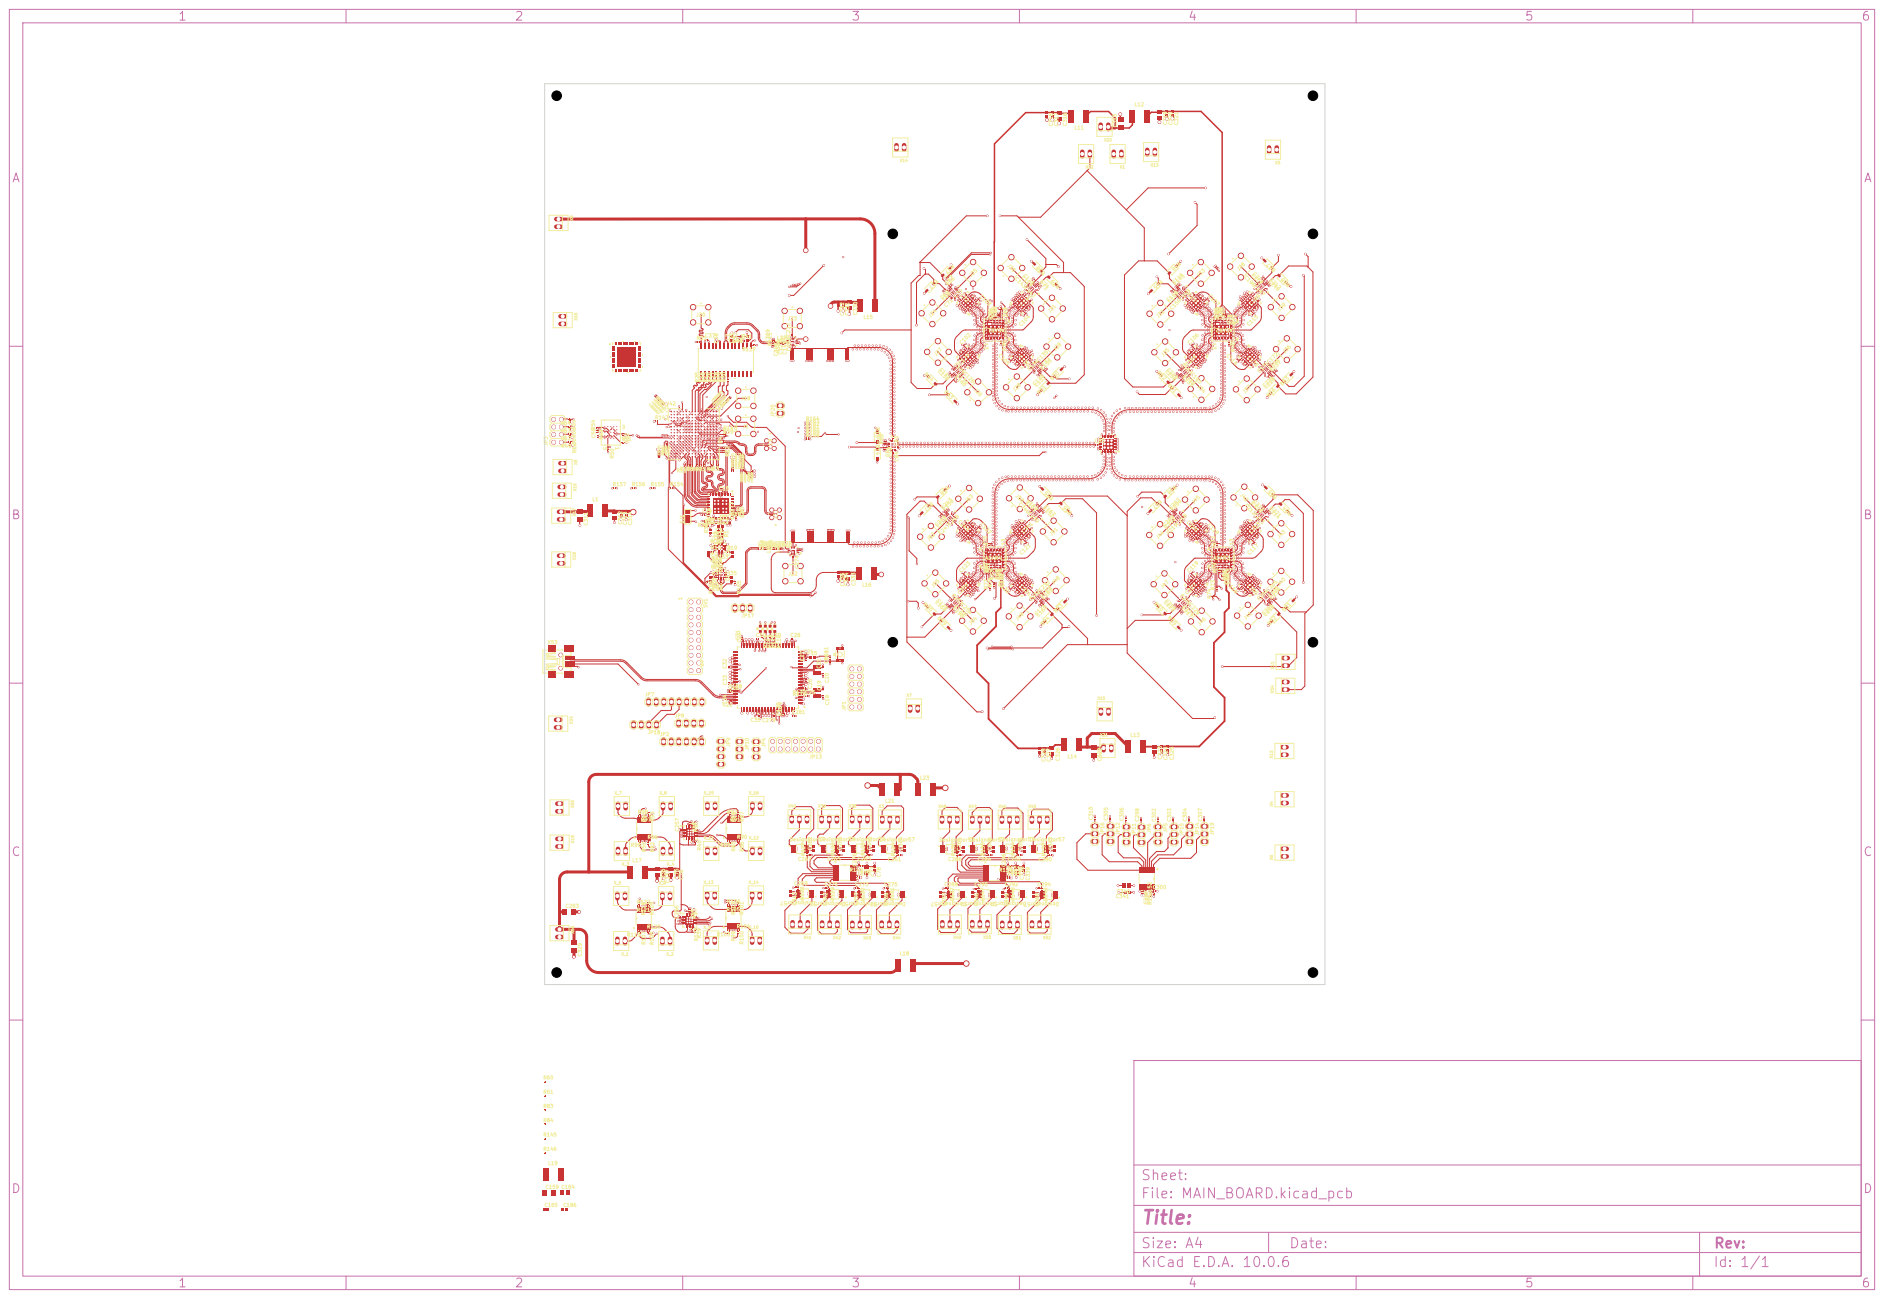
[picture p176: page 1]

Size: A4 | Rev:
KiCad E.D.A. 10.0.6 | Id: 1/1
