herasymyuks/PLFM_RADAR-aeris/engineering/PCB/POWER_SUPPLY/drawings/POWER_SUPPLY_bottom_layer_mirrored.pdf

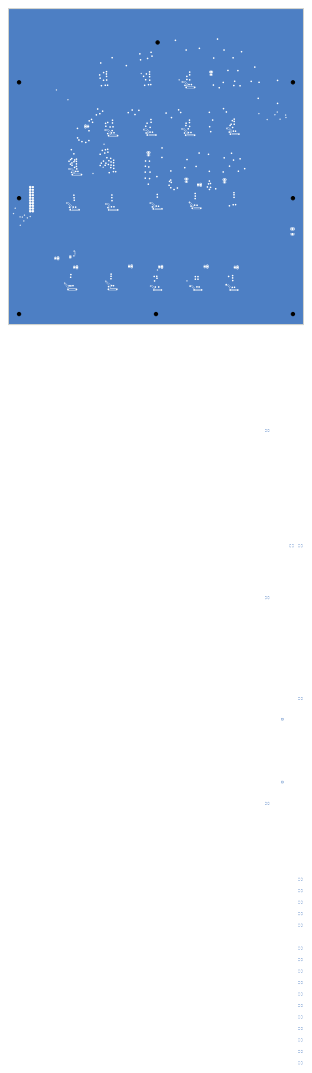
[picture p177: page 1]

Size: A4 | Rev:
KiCad E.D.A. 10.0.6 | Id: 1/1
