herasymyuks/PLFM_RADAR-aeris/engineering/PCB/POWER_SUPPLY/drawings/POWER_SUPPLY_outline.pdf

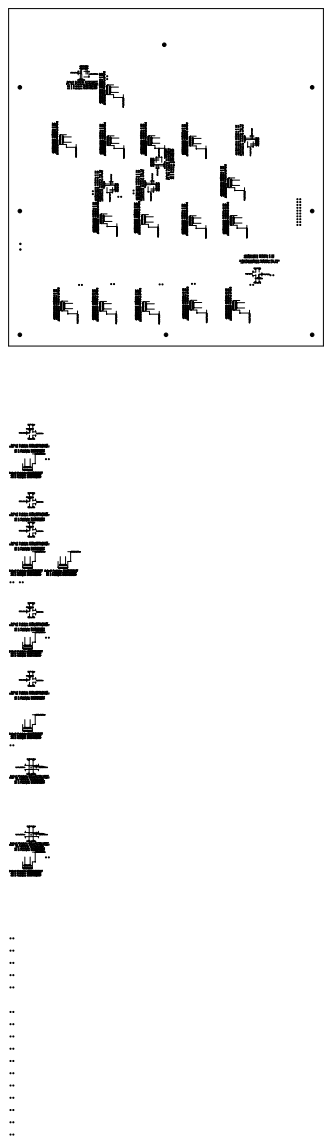
[picture p180: page 1]

0.118in/3mm Default Padstyle: RX130Y323D0T Alt 1 Padstyle: OX60Y90D30P
Alt 2 Padstyle: OX90Y60D30P

0.342in/8.687mm Default Padstyle: RX130Y323D0T Alt 1 Padstyle: OX60Y90D30P

Default Padstyle: RX130Y323D0T Alt 1 Padstyle: OX60Y90D30P

Size: A4 | Rev:
KiCad E.D.A. 10.0.6 | Id: 1/1
