herasymyuks/PLFM_RADAR-aeris/engineering/PCB/RF_PA/drawings/RF_PA_copper_layers.pdf

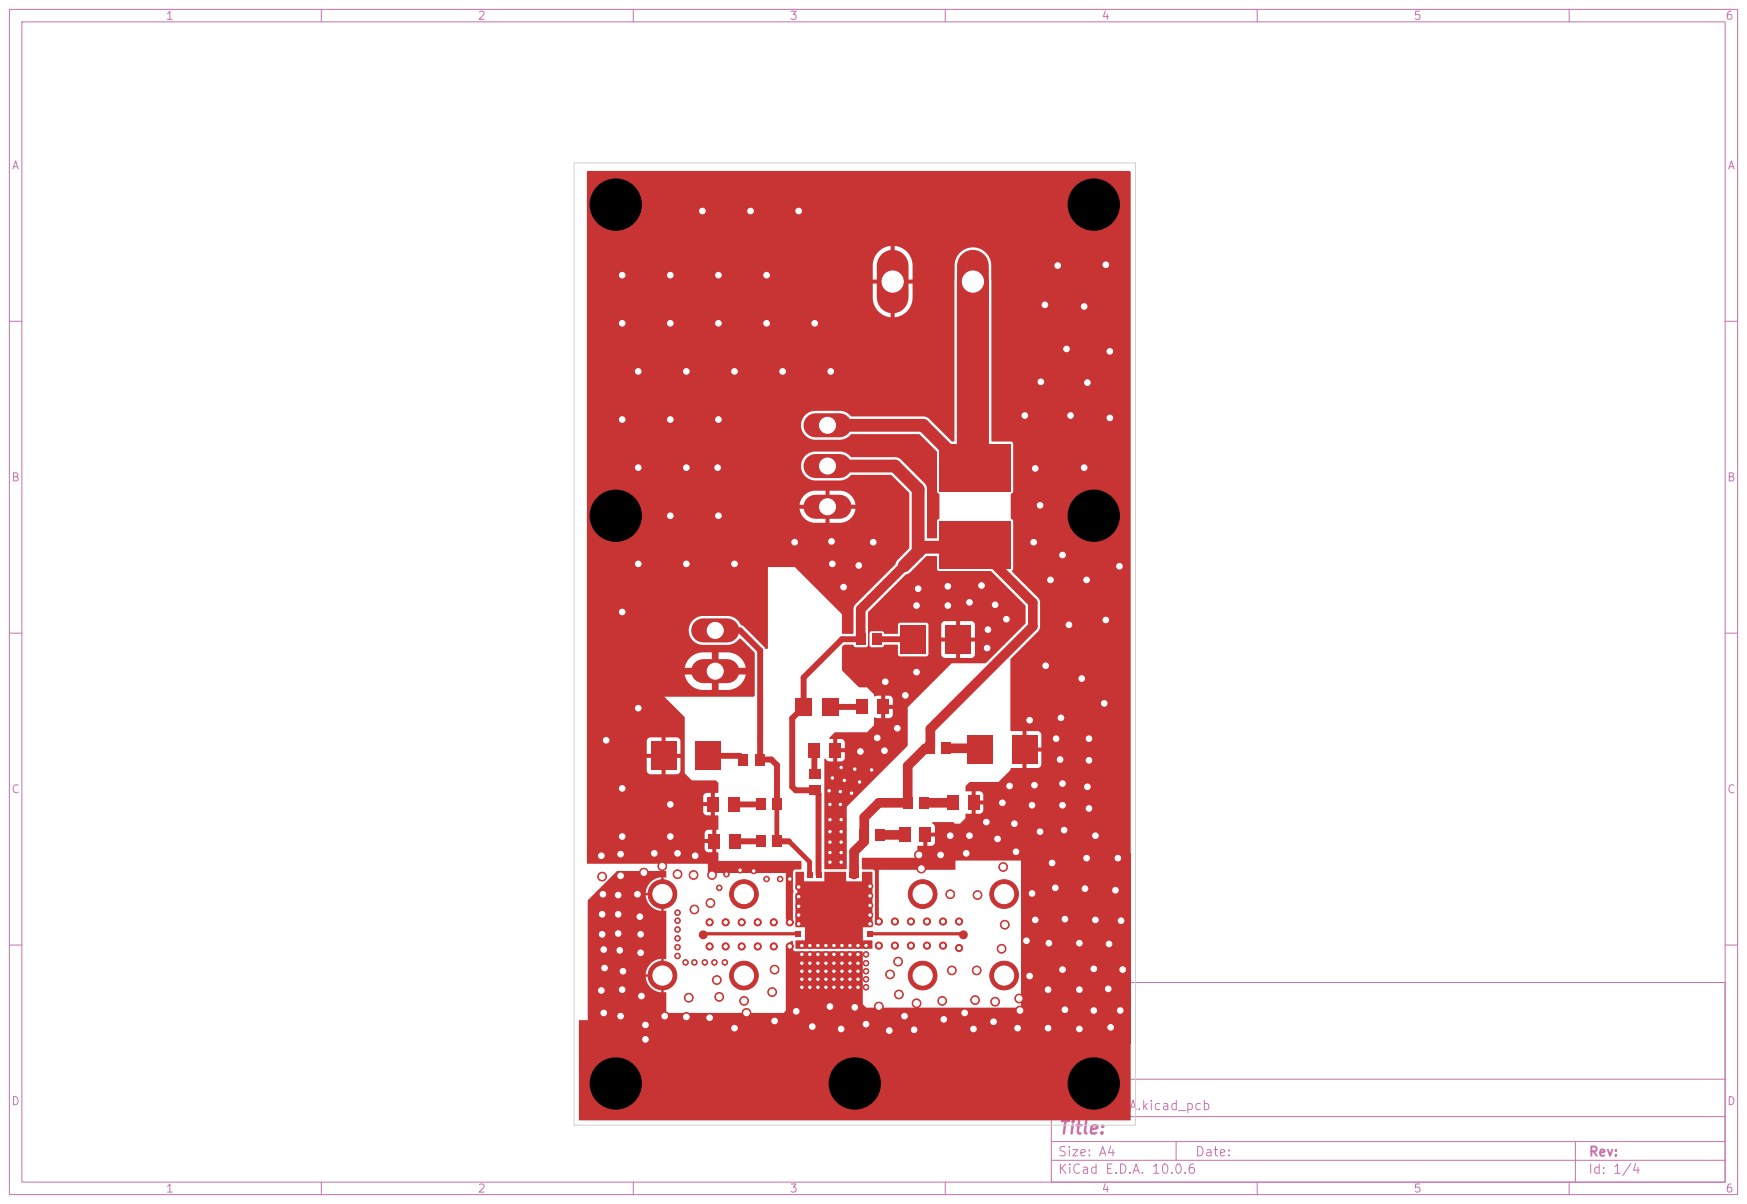
[picture p183: page 1]

Size: A4 | Rev:
KiCad E.D.A. 10.0.6 | Id: 1/4

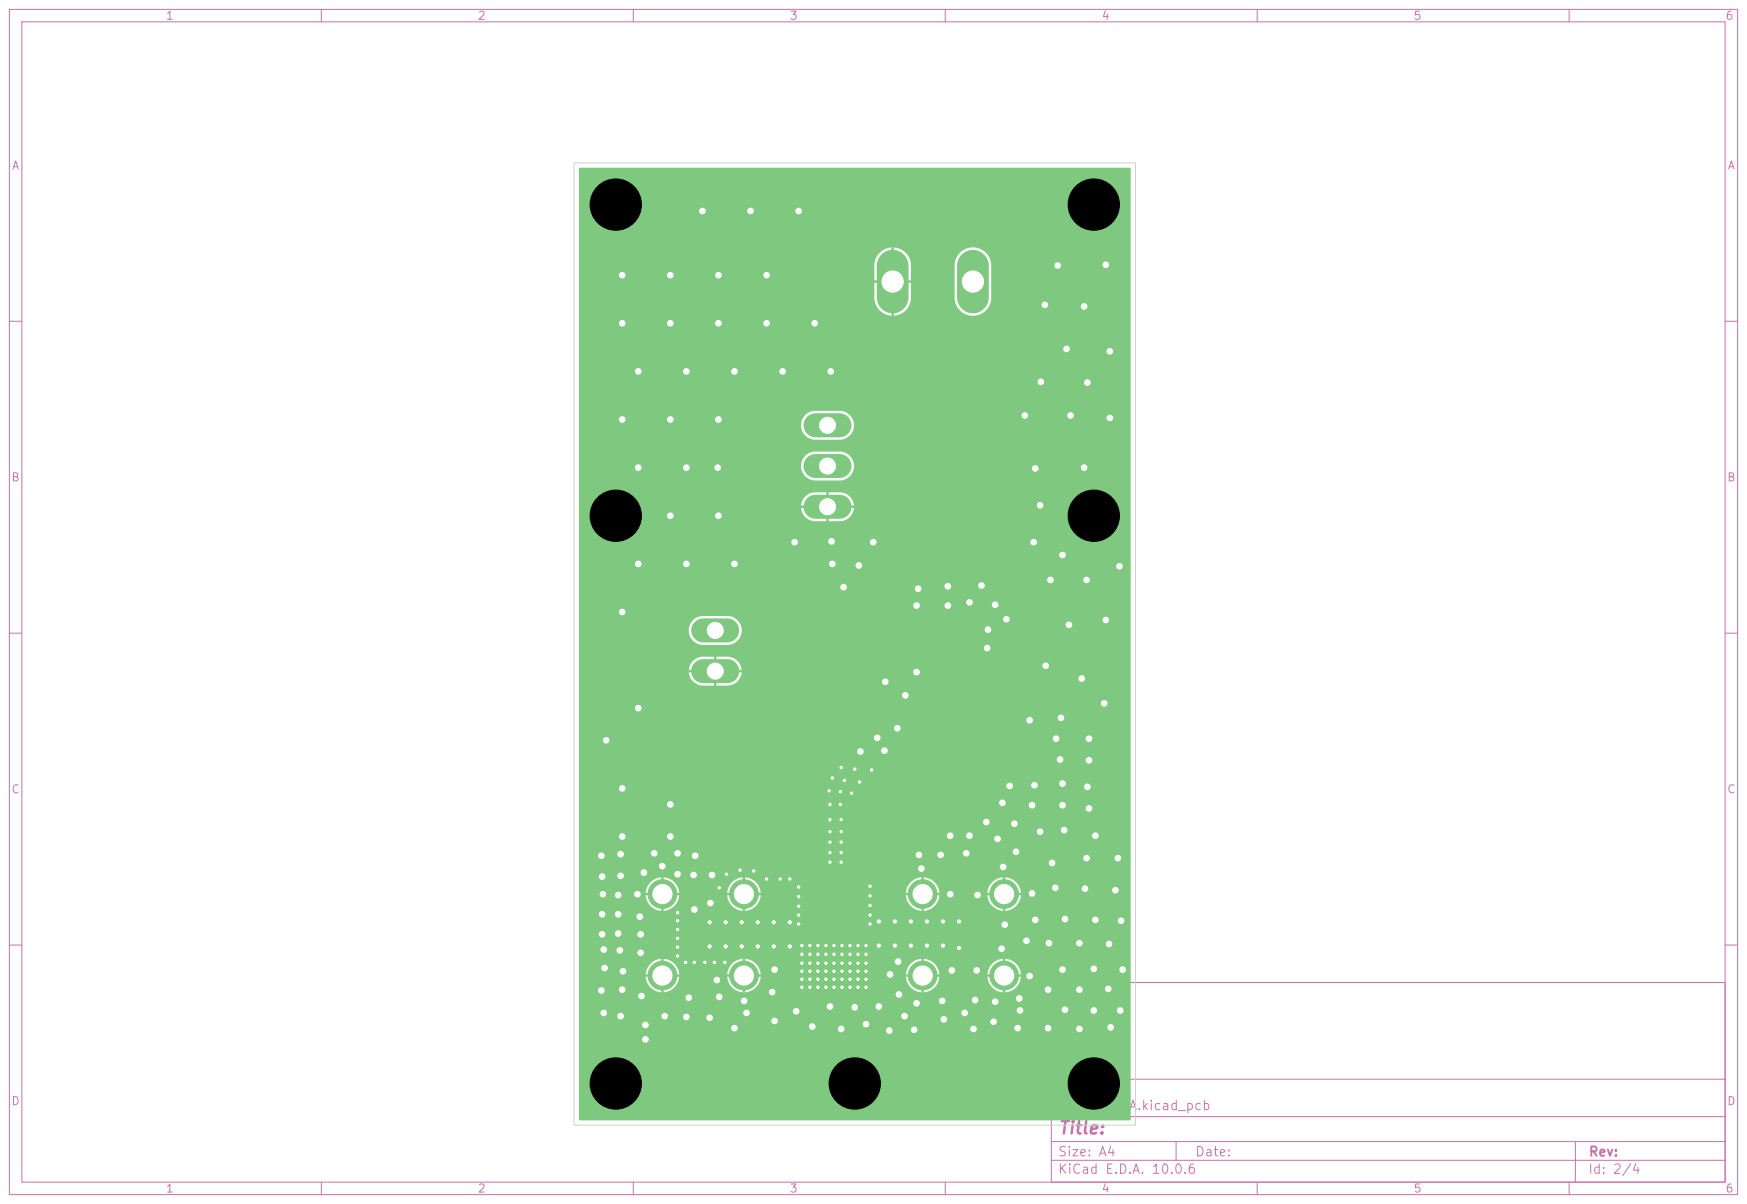
[picture p184: page 2]

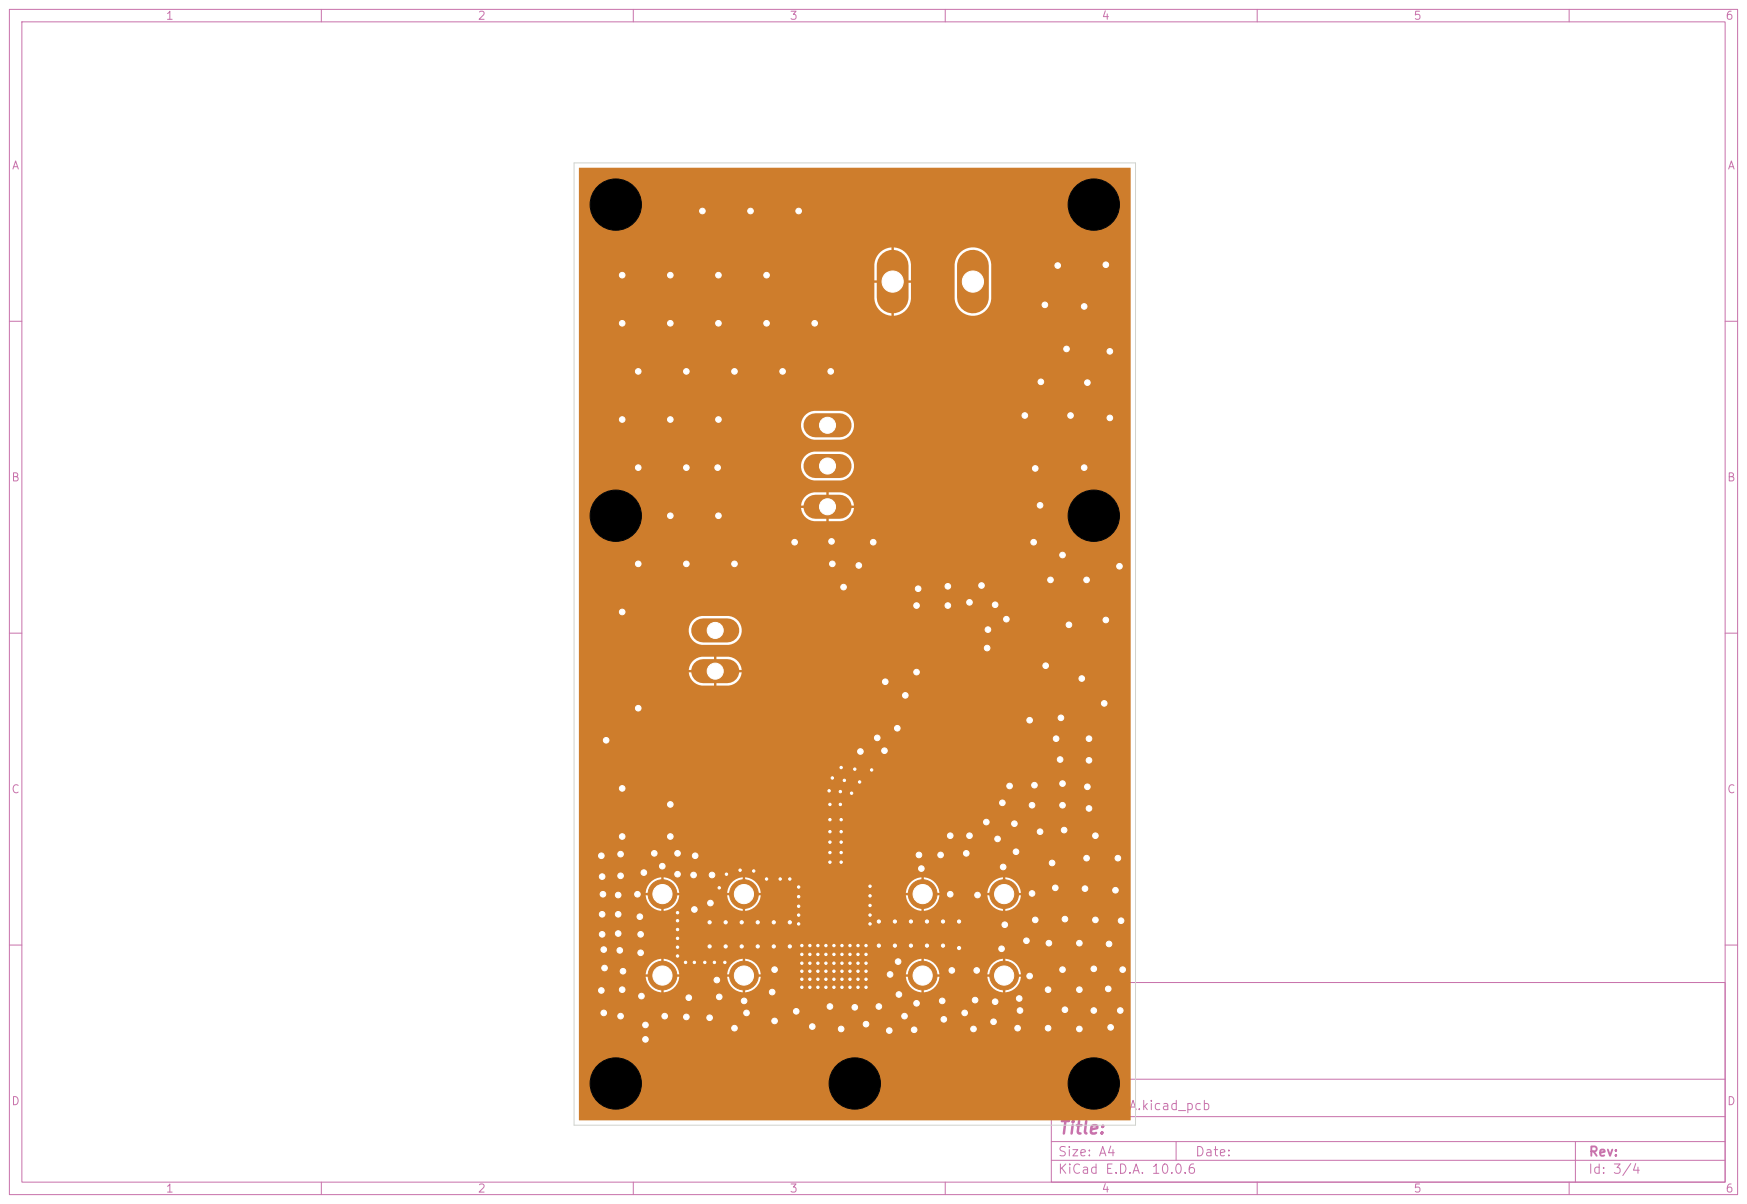
[picture p185: page 3]

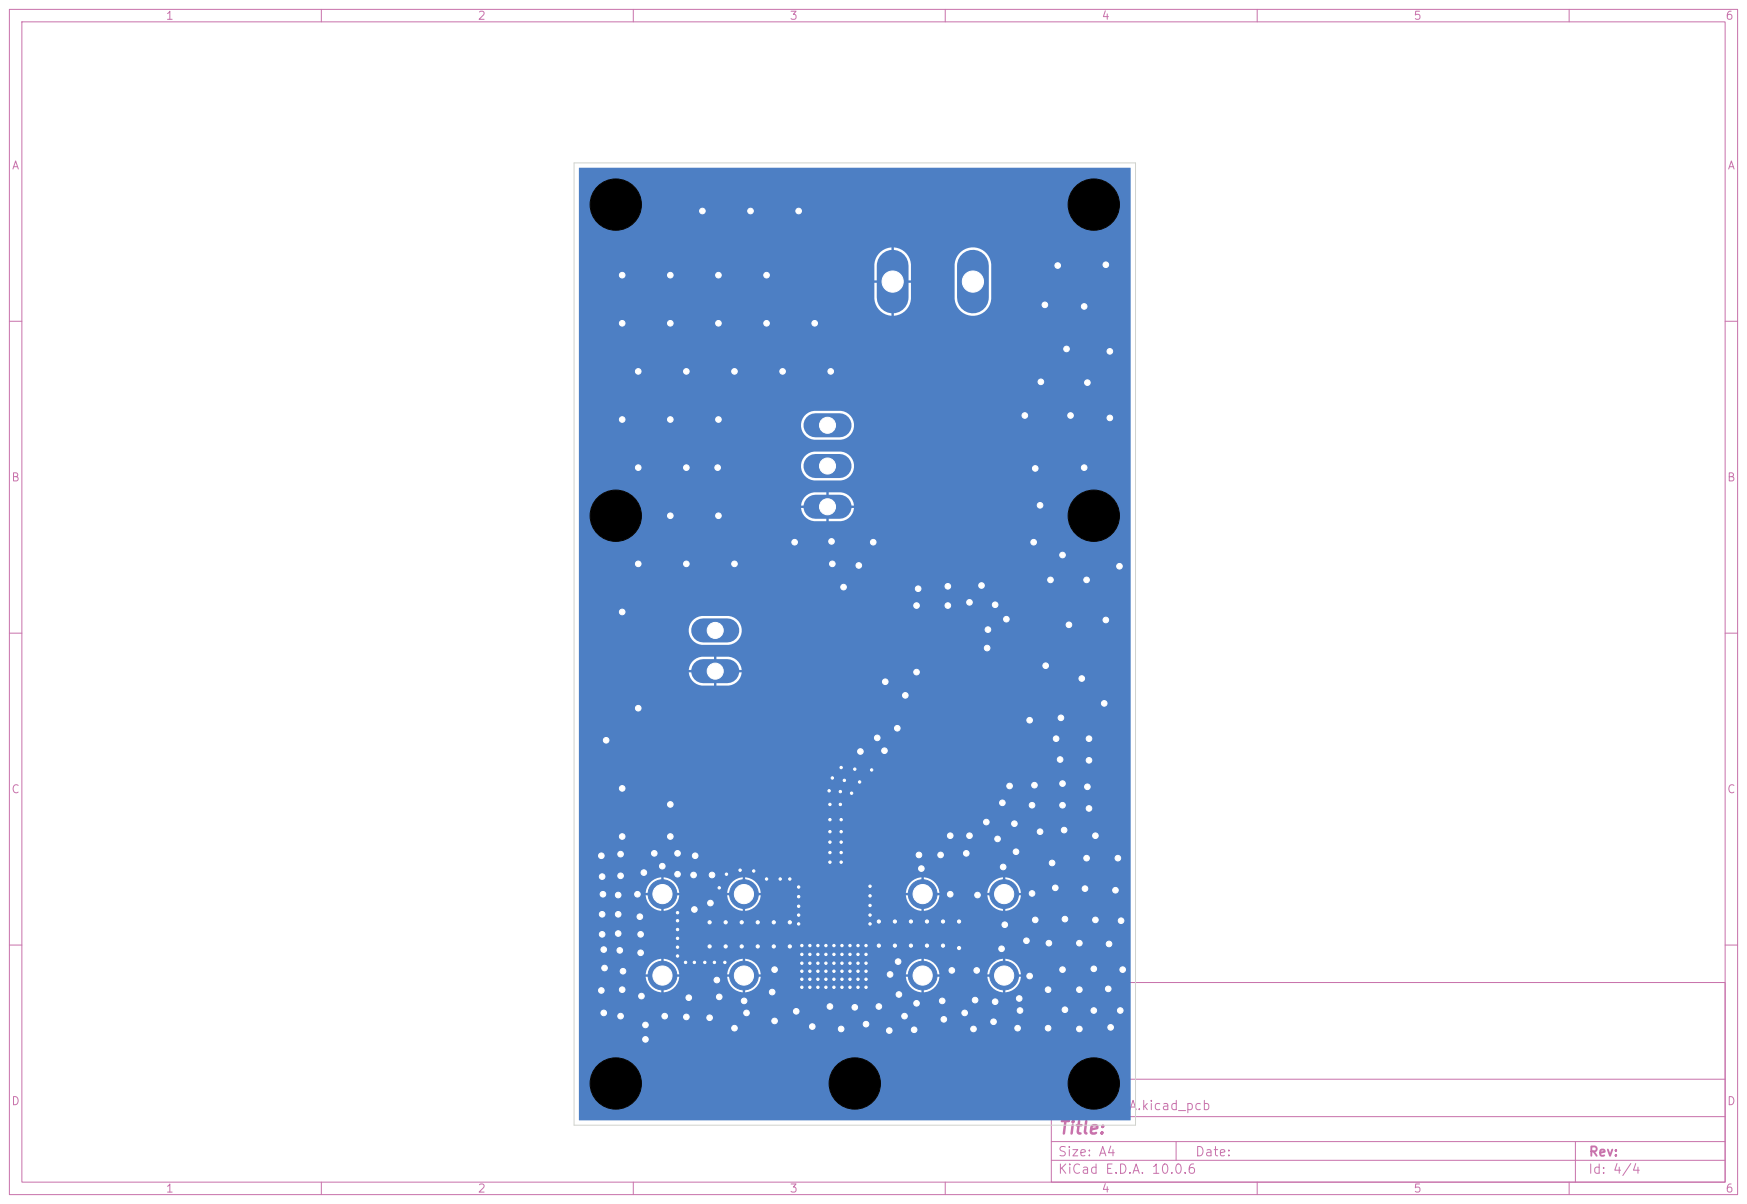
[picture p186: page 4]
