herasymyuks/PLFM_RADAR-aeris/engineering/PCB/RF_PA/drawings/RF_PA_outline.pdf

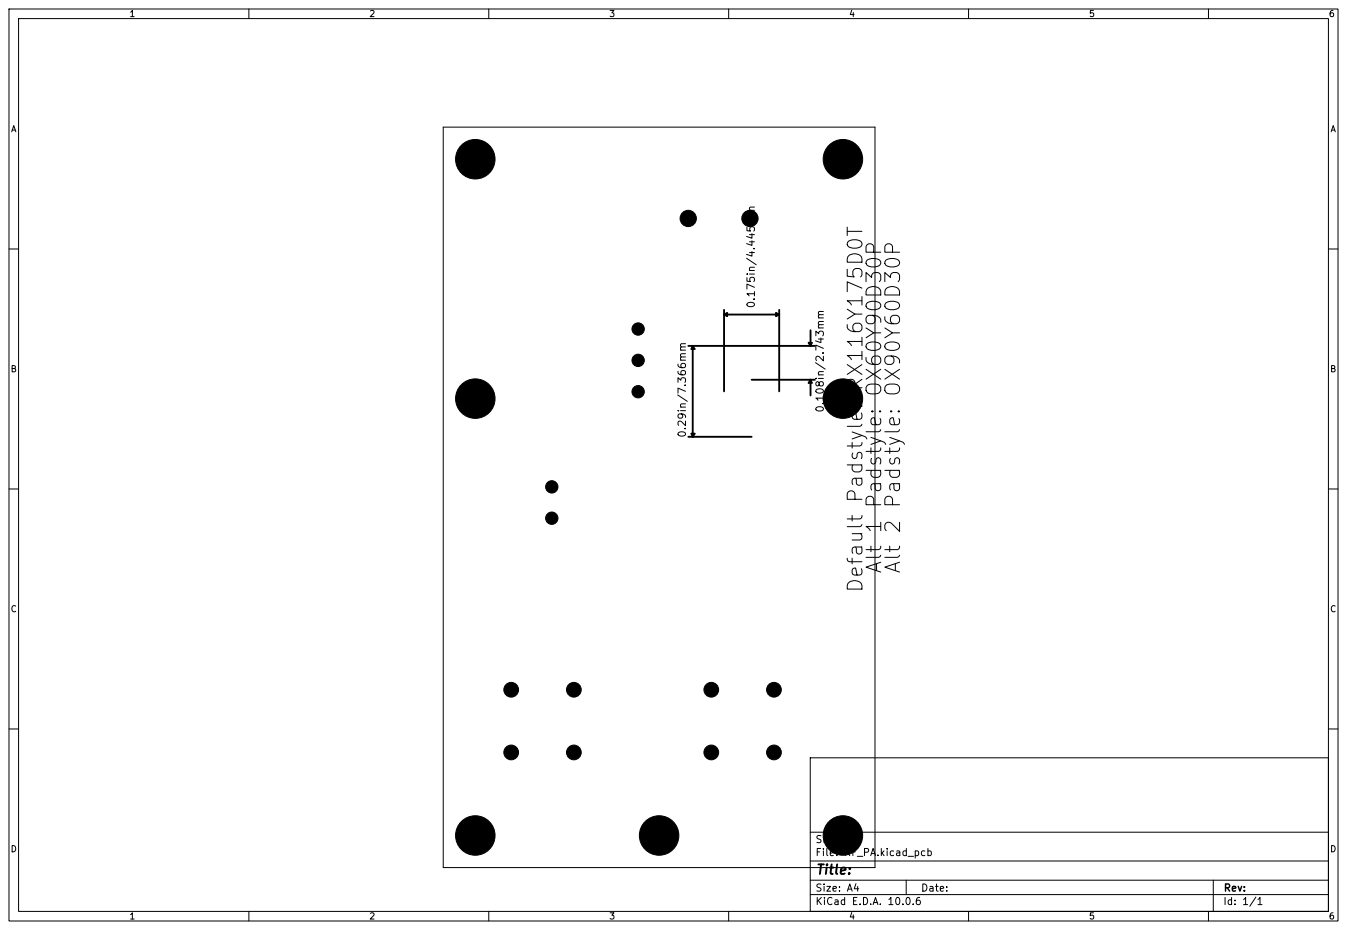
[picture p187: page 1]

Size: A4 | Rev:
KiCad E.D.A. 10.0.6 | Id: 1/1
