herasymyuks/PLFM_RADAR-aeris/beta/pcb/MAIN_BOARD_REVB/exports/drawings/MAIN_BOARD_REVB_bottom_layer_mirrored.pdf

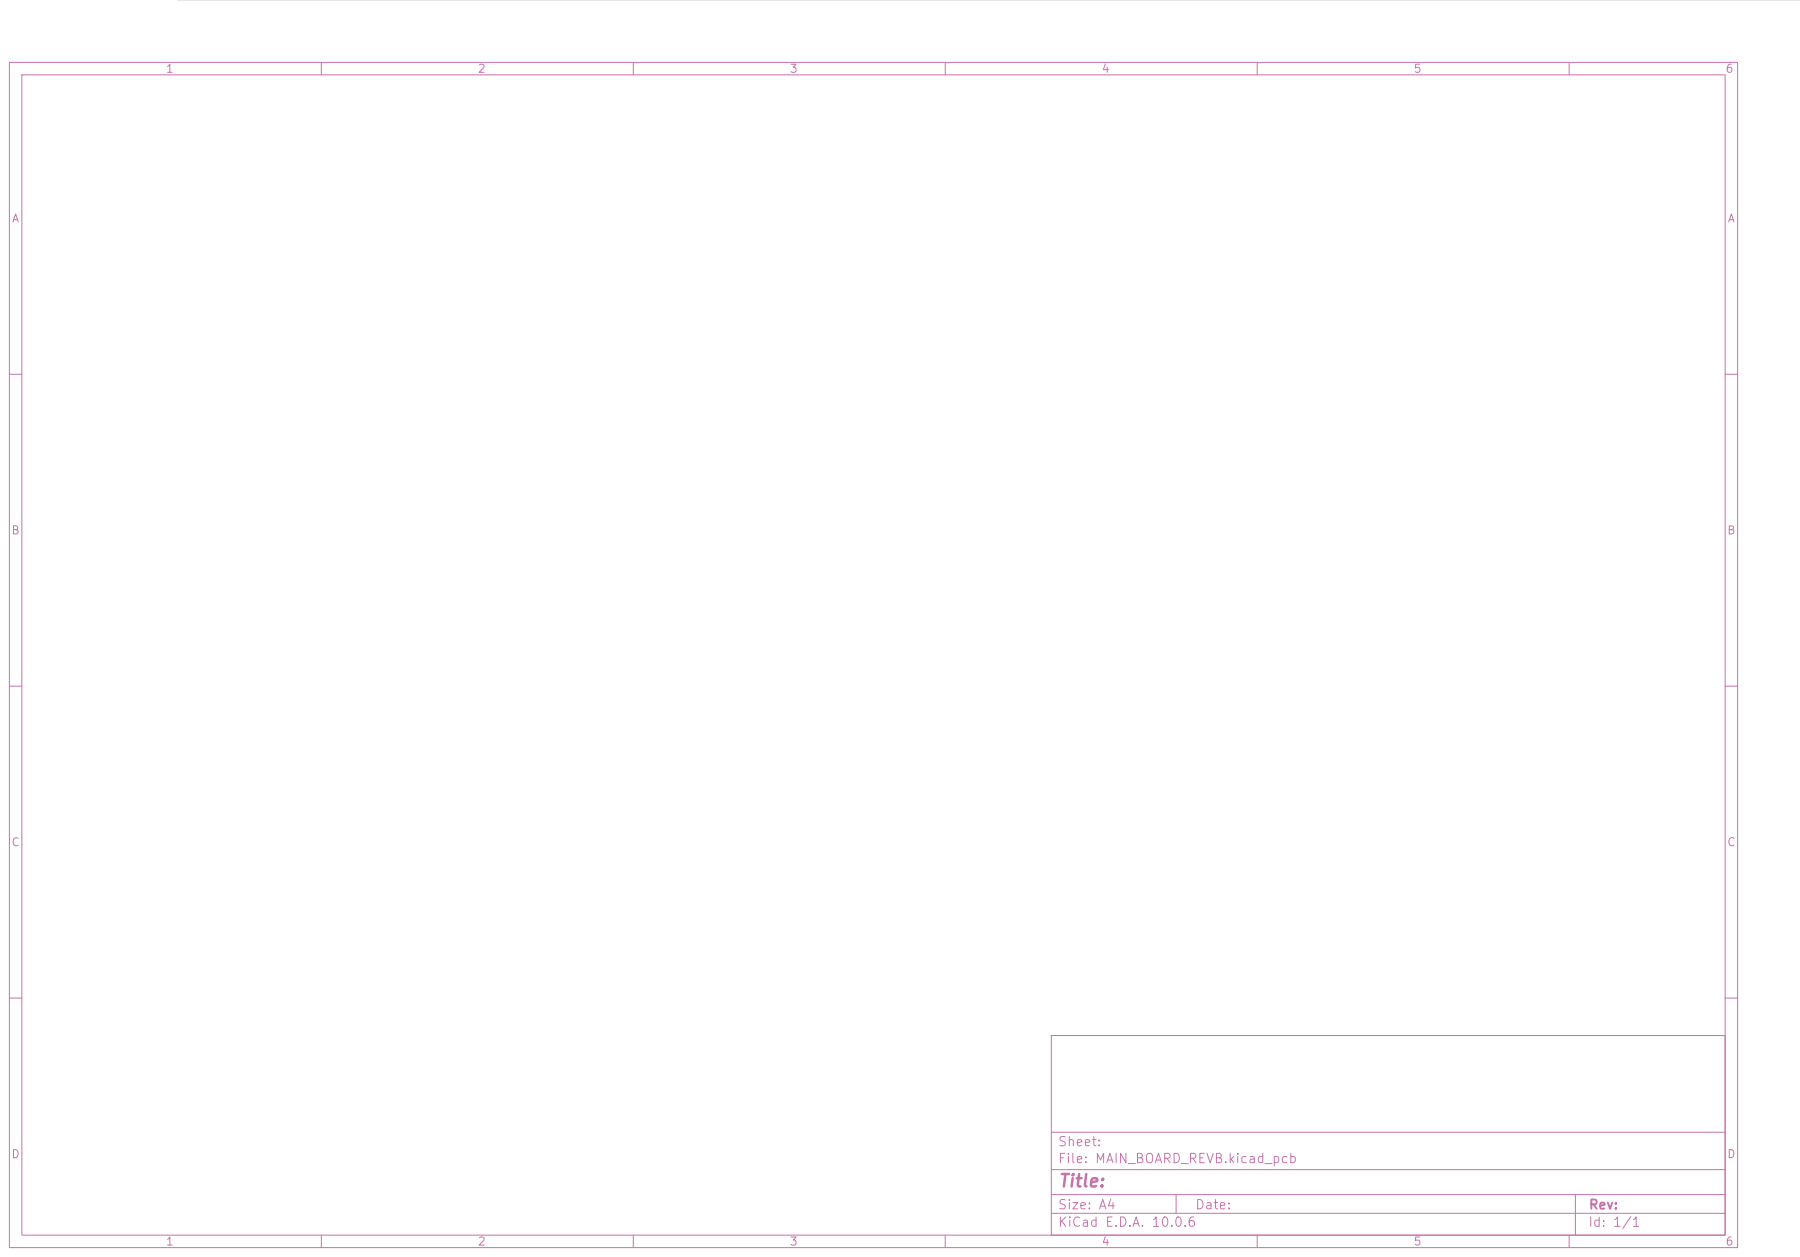
[picture p189: page 1]

Size: A4 | Rev:
KiCad E.D.A. 10.0.6 | Id: 1/1
