herasymyuks/PLFM_RADAR-aeris/beta/pcb/MAIN_BOARD_REVB/exports/drawings/MAIN_BOARD_REVB_copper_layers.pdf

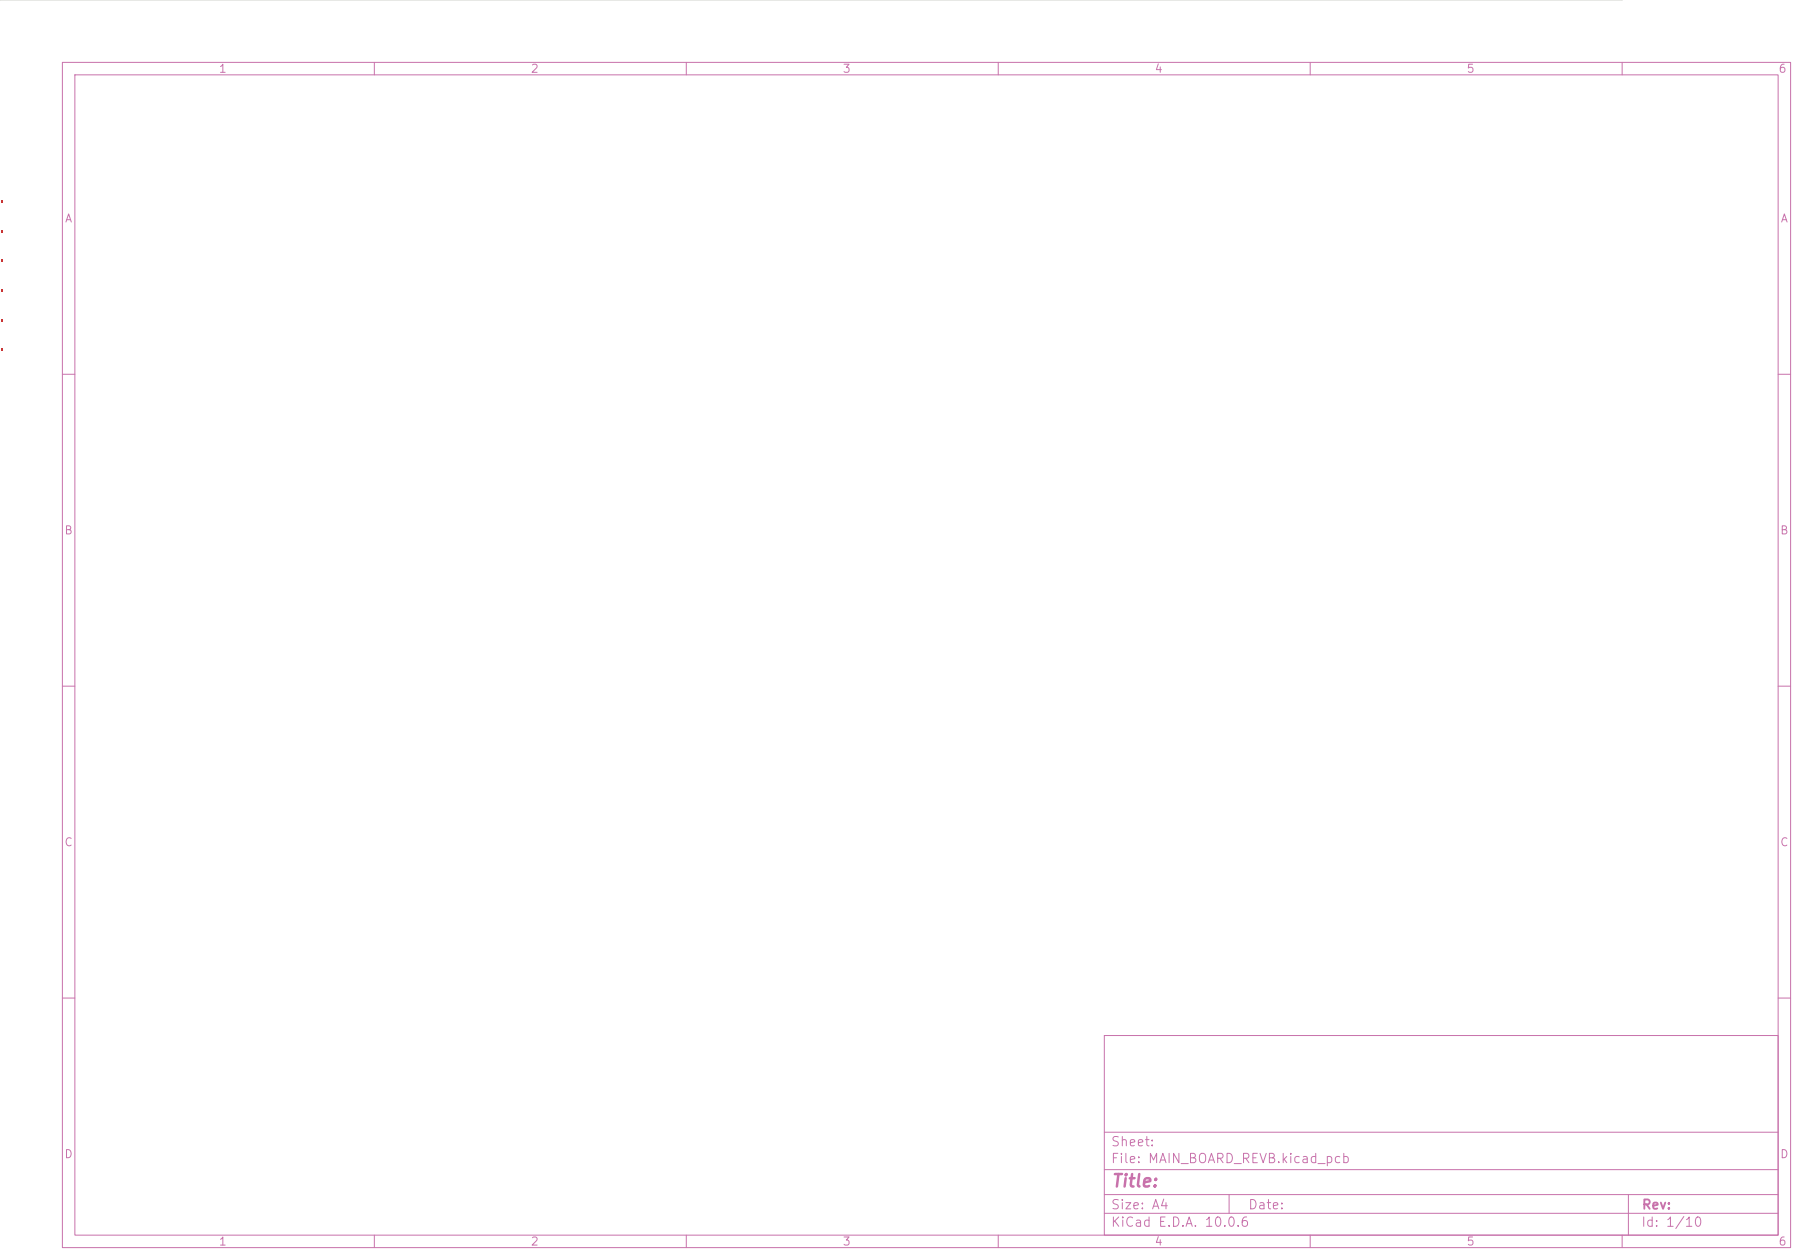
[picture p190: page 1]

Size: A4 | Rev:
KiCad E.D.A. 10.0.6 | Id: 1/10

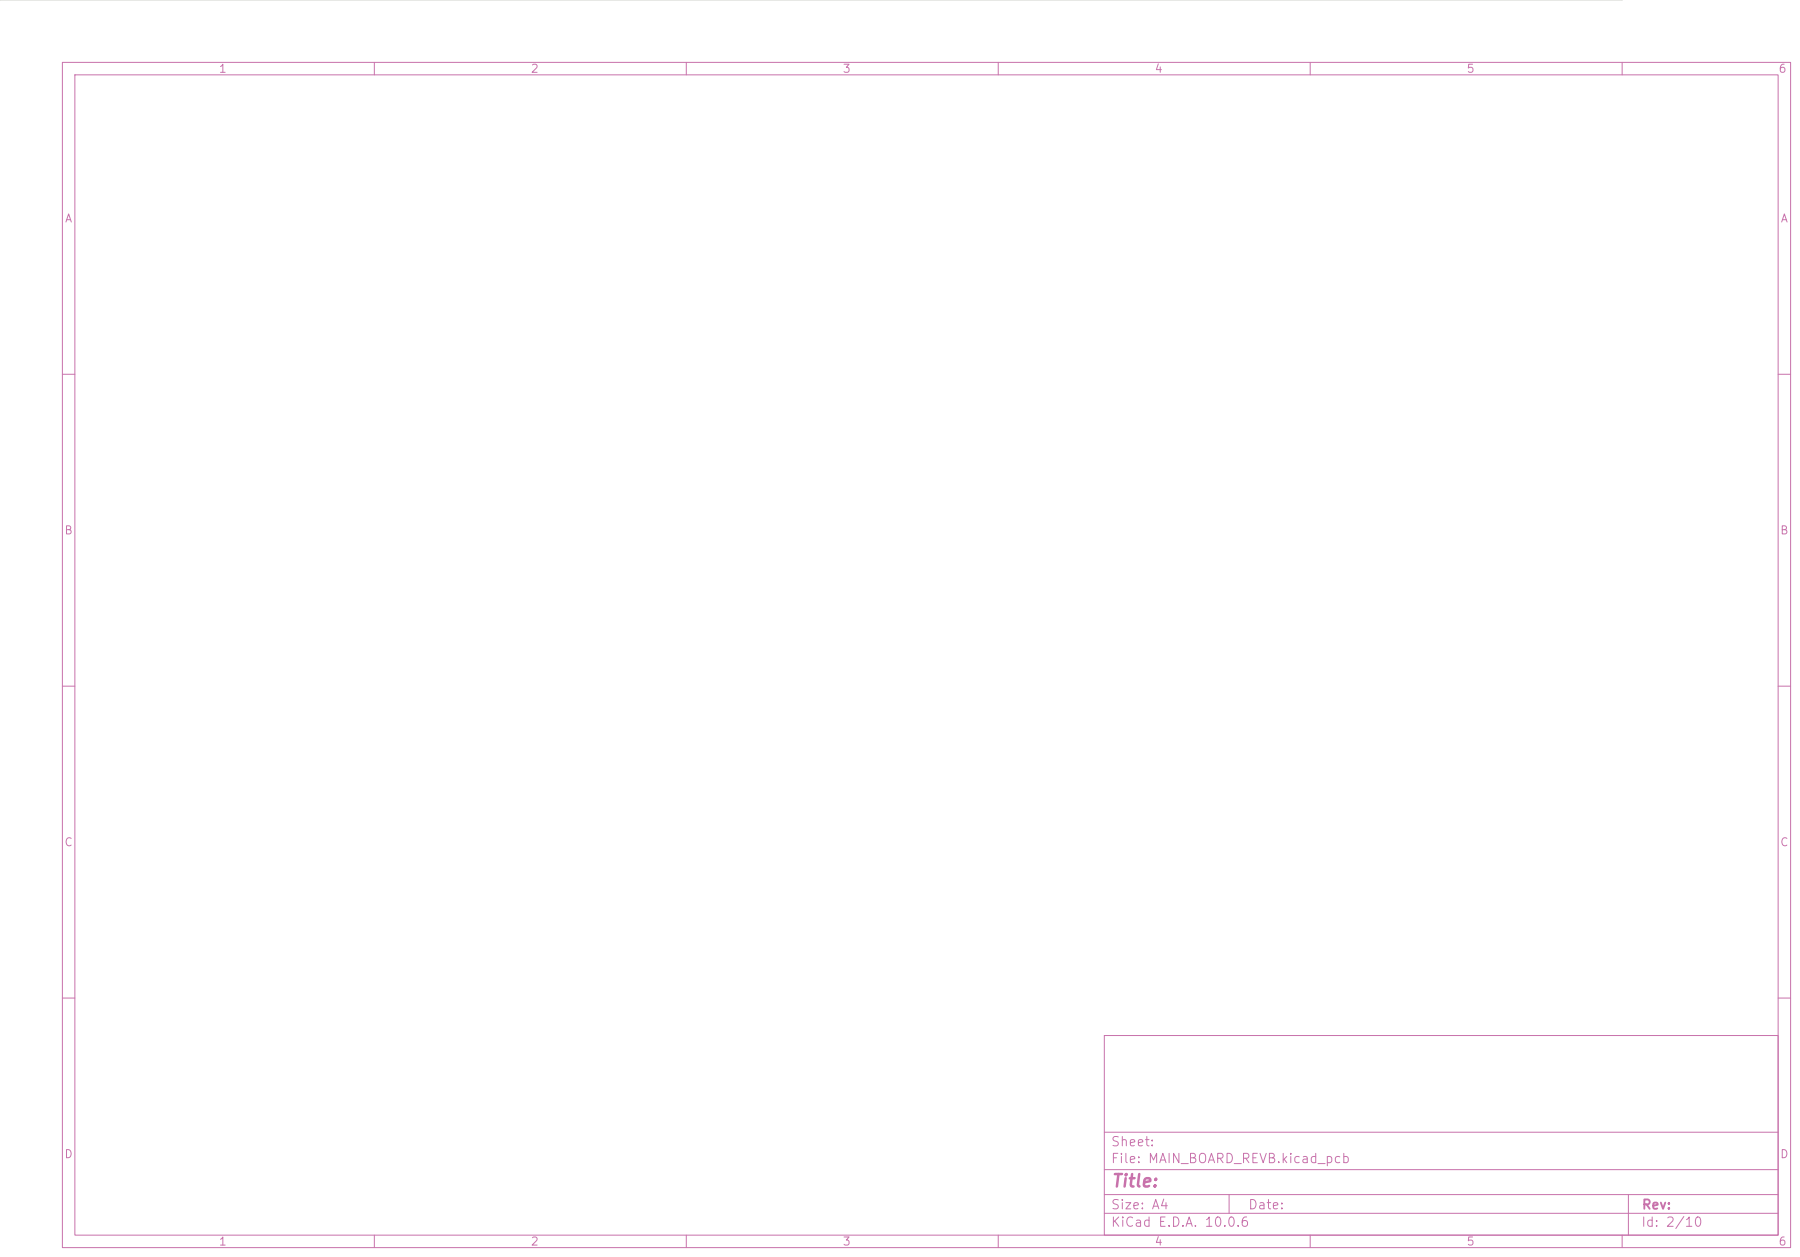
[picture p191: page 2]

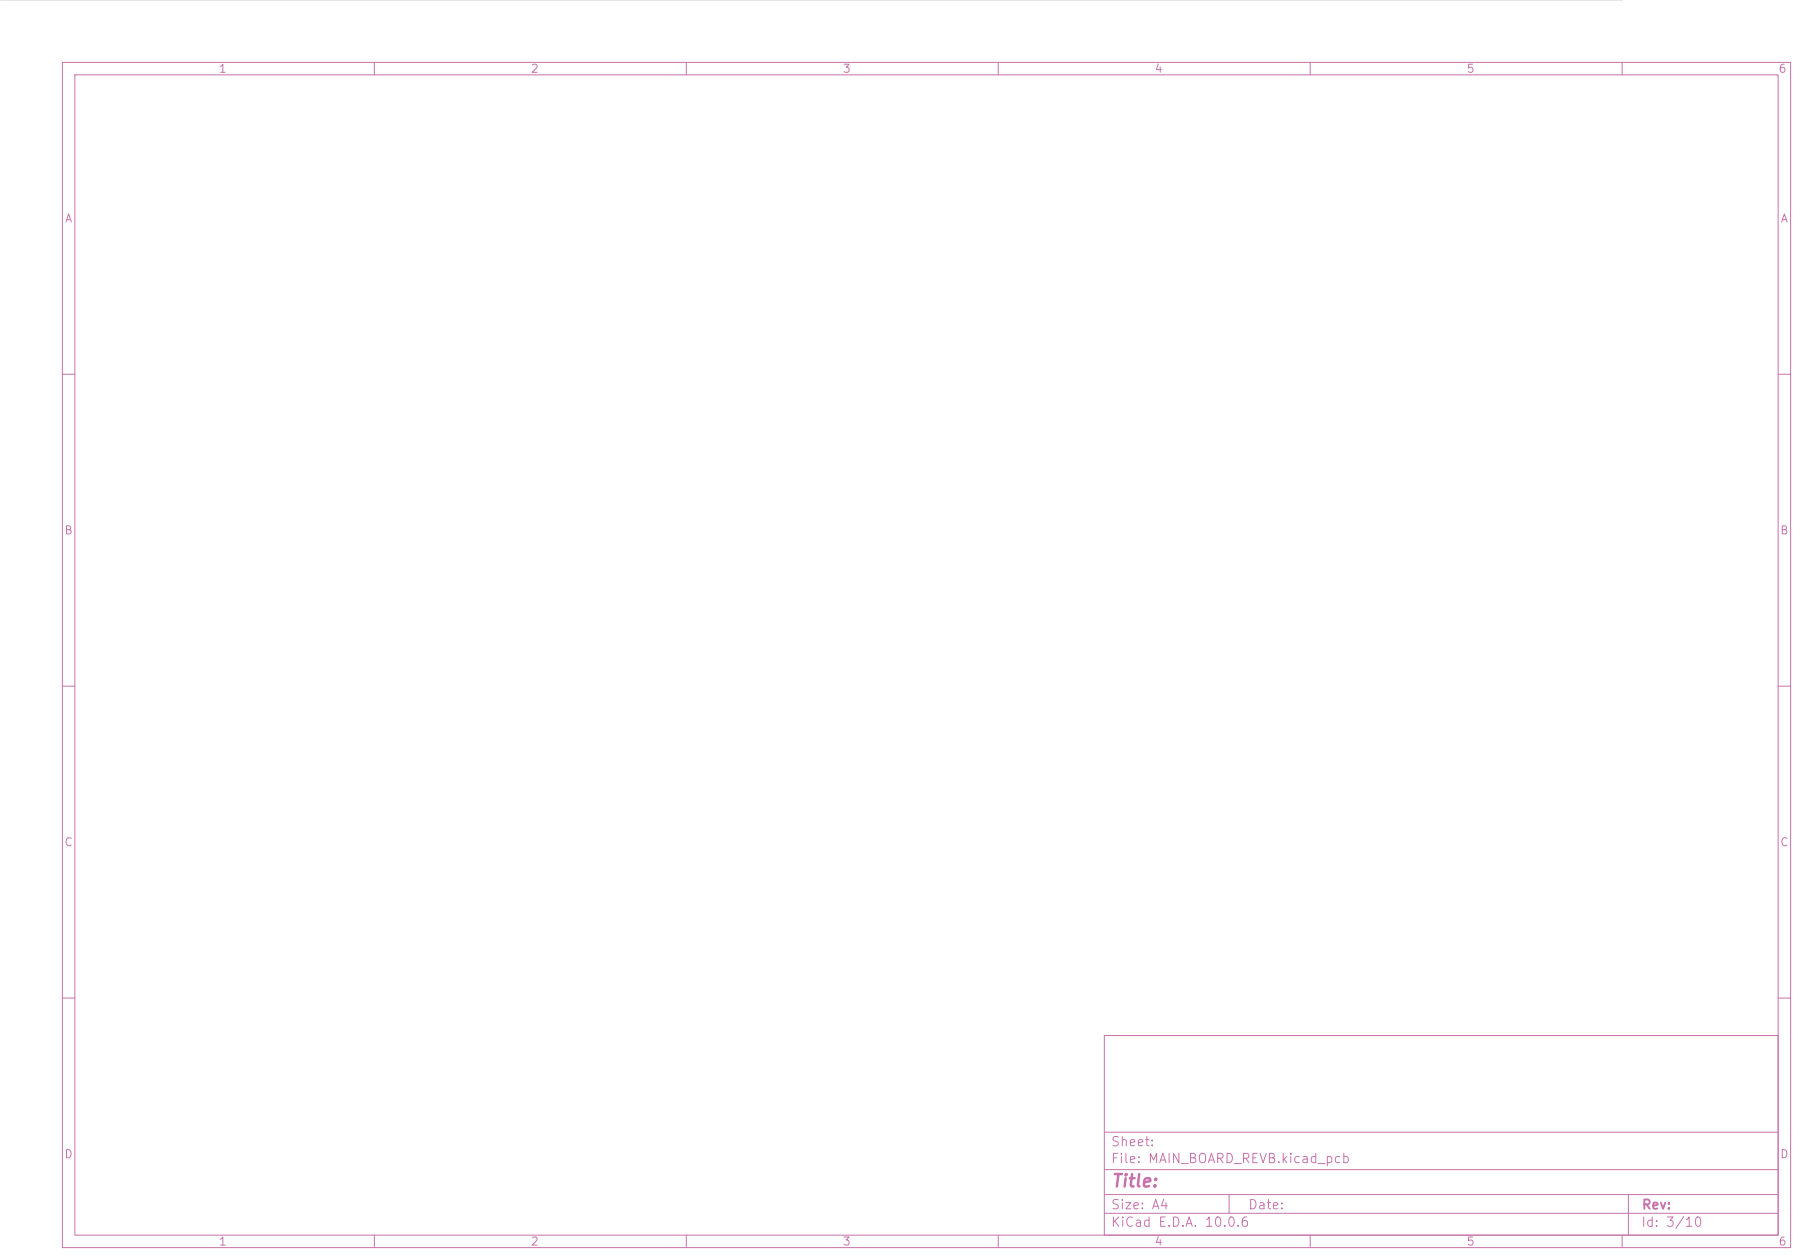
[picture p192: page 3]

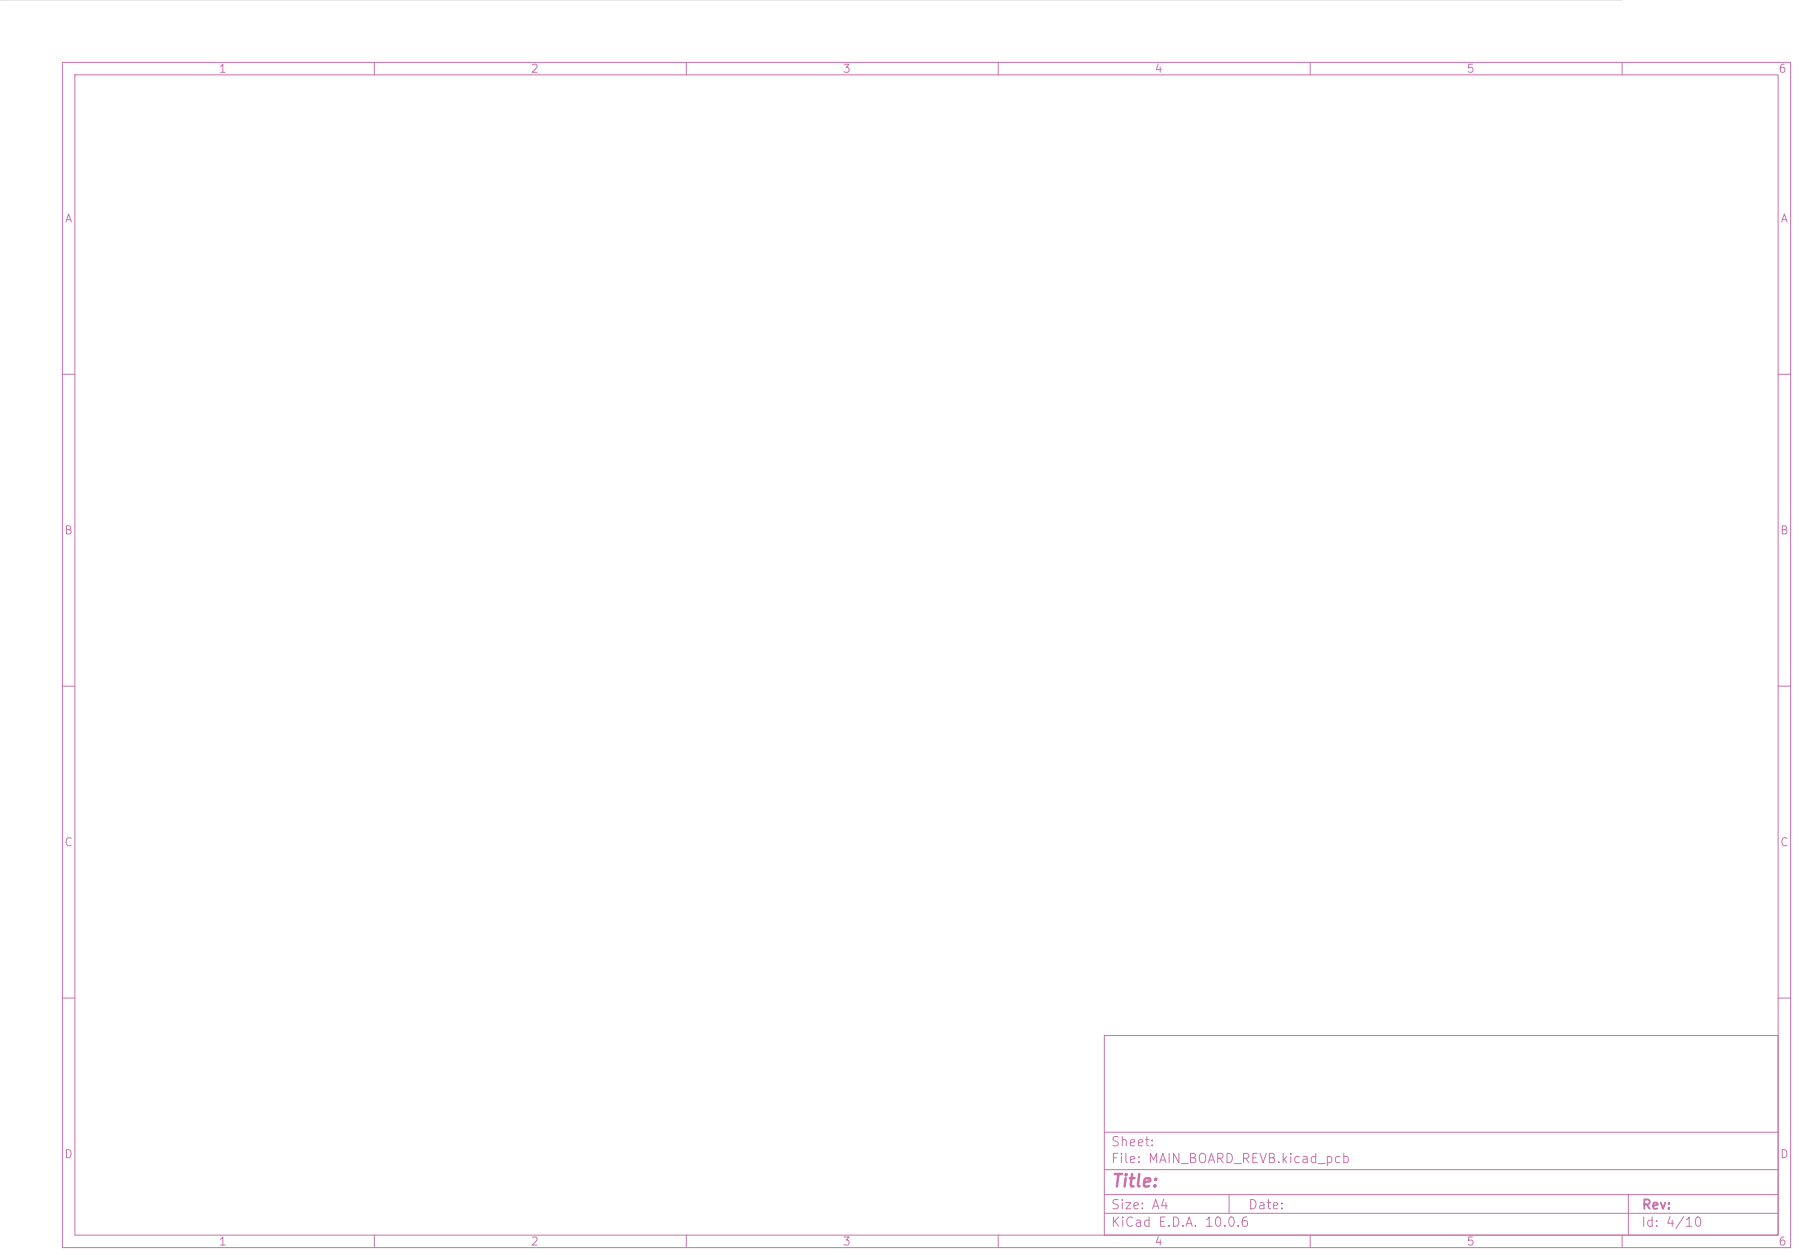
[picture p193: page 4]

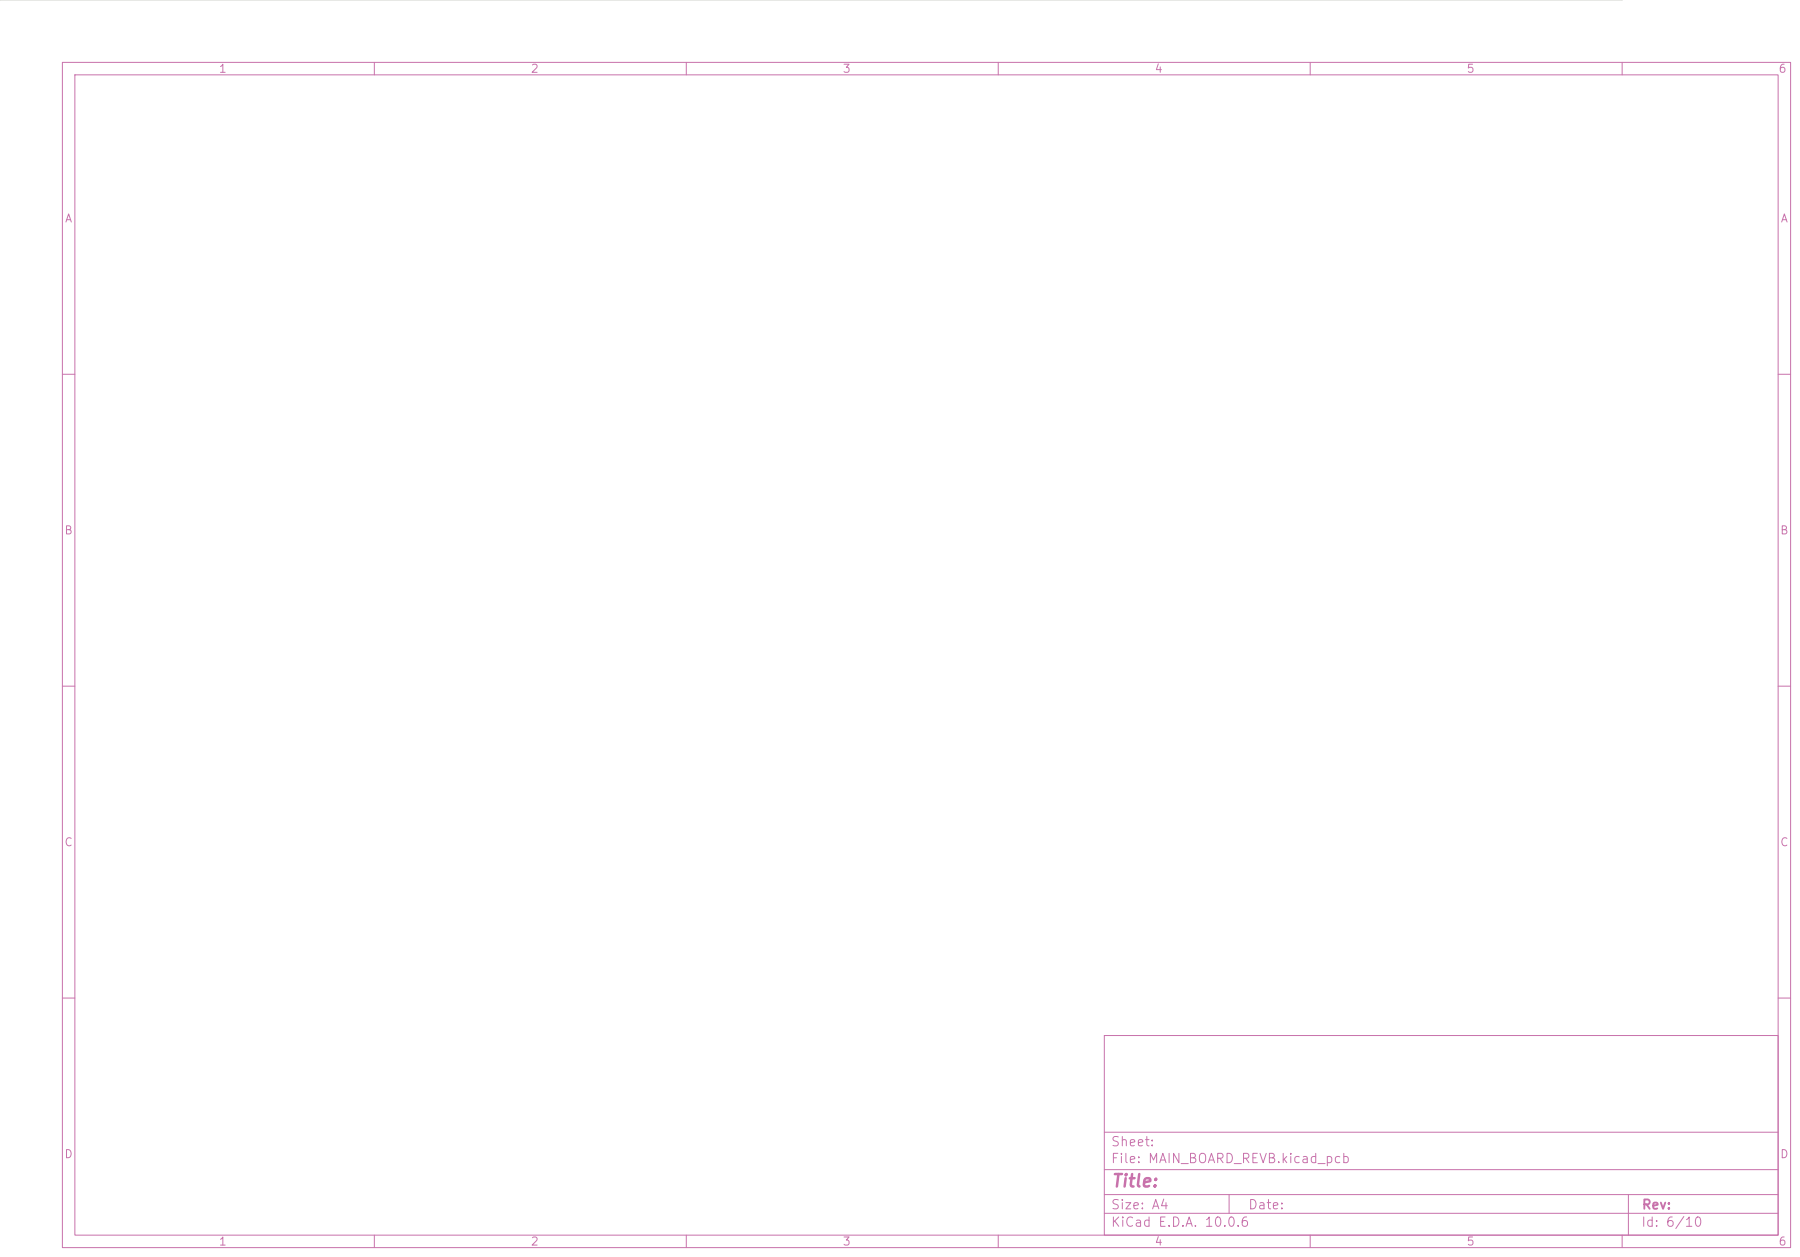
[picture p194: page 6]

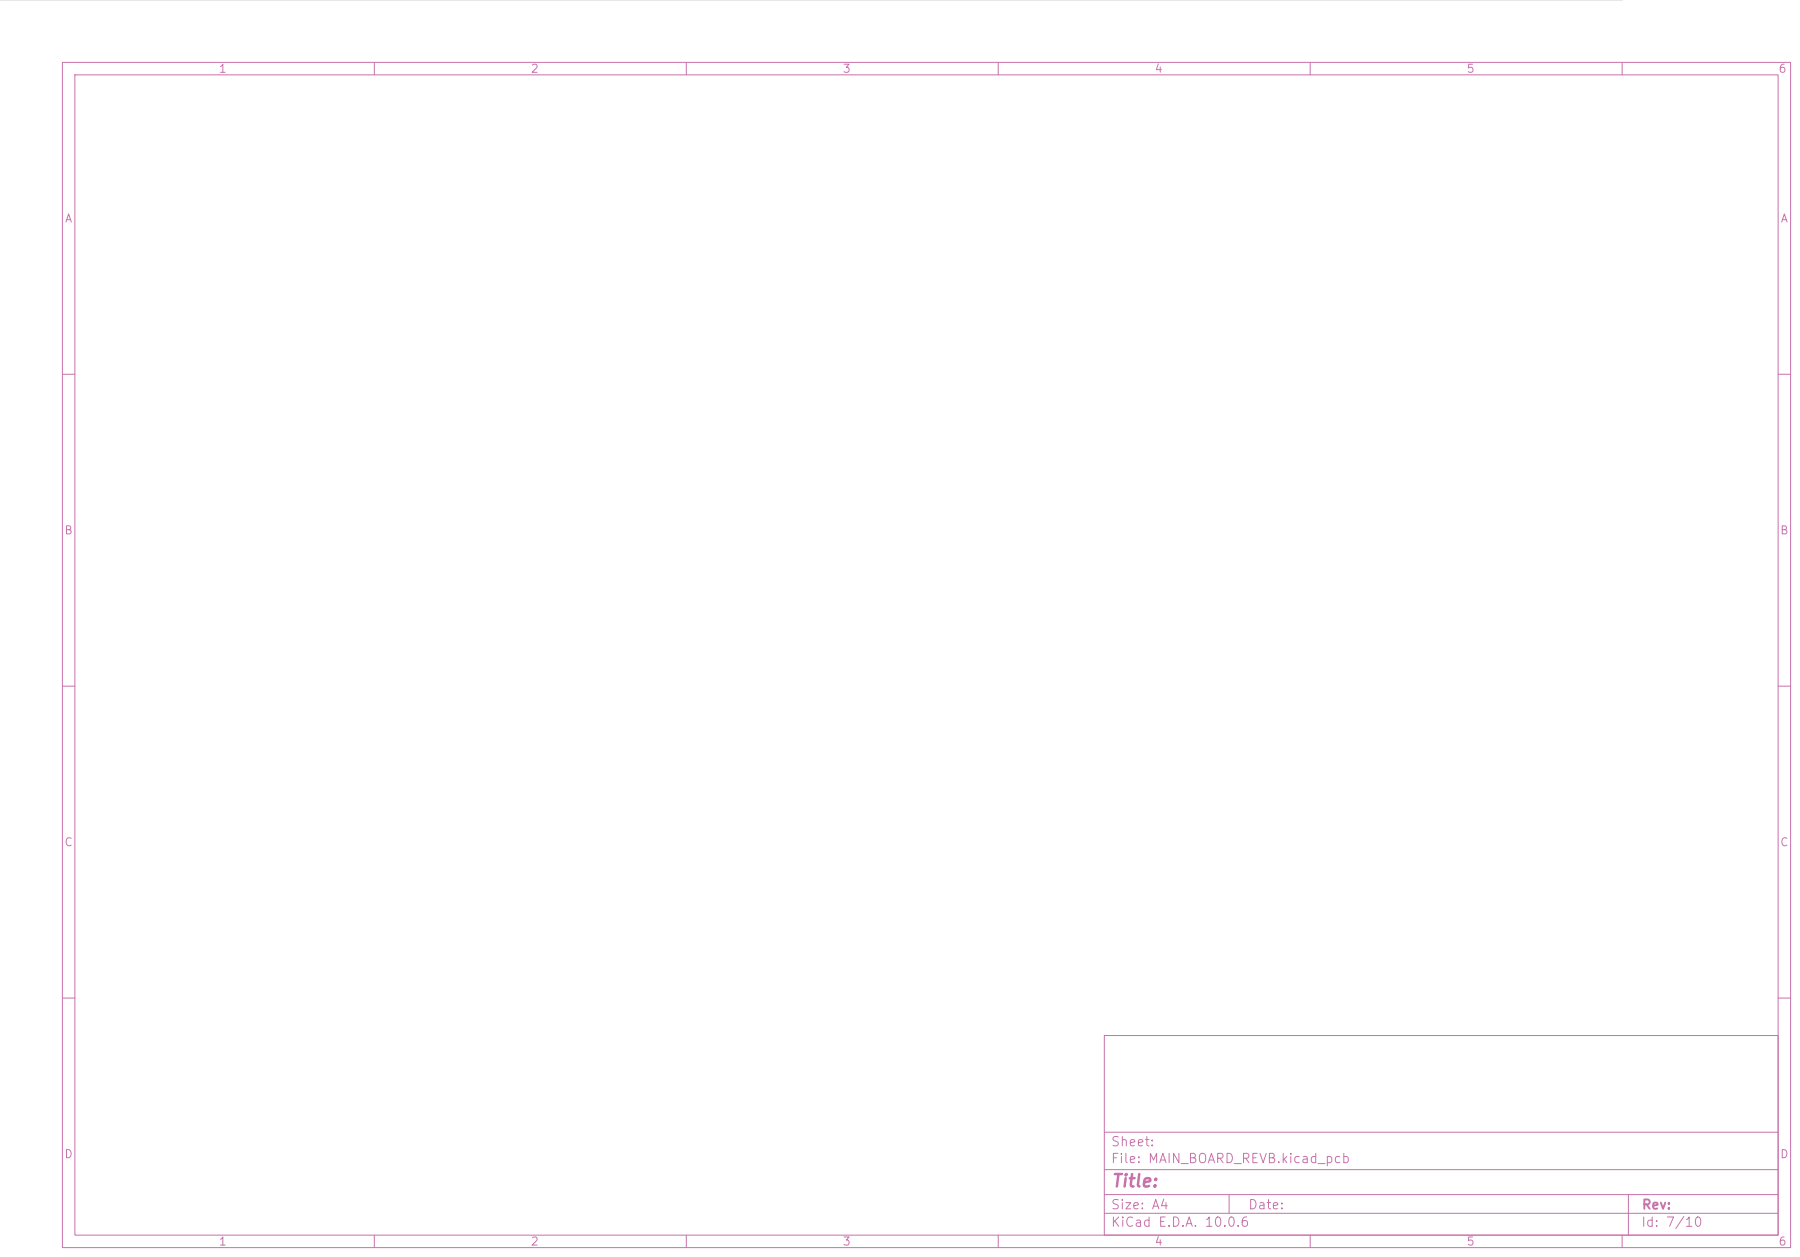
[picture p195: page 7]

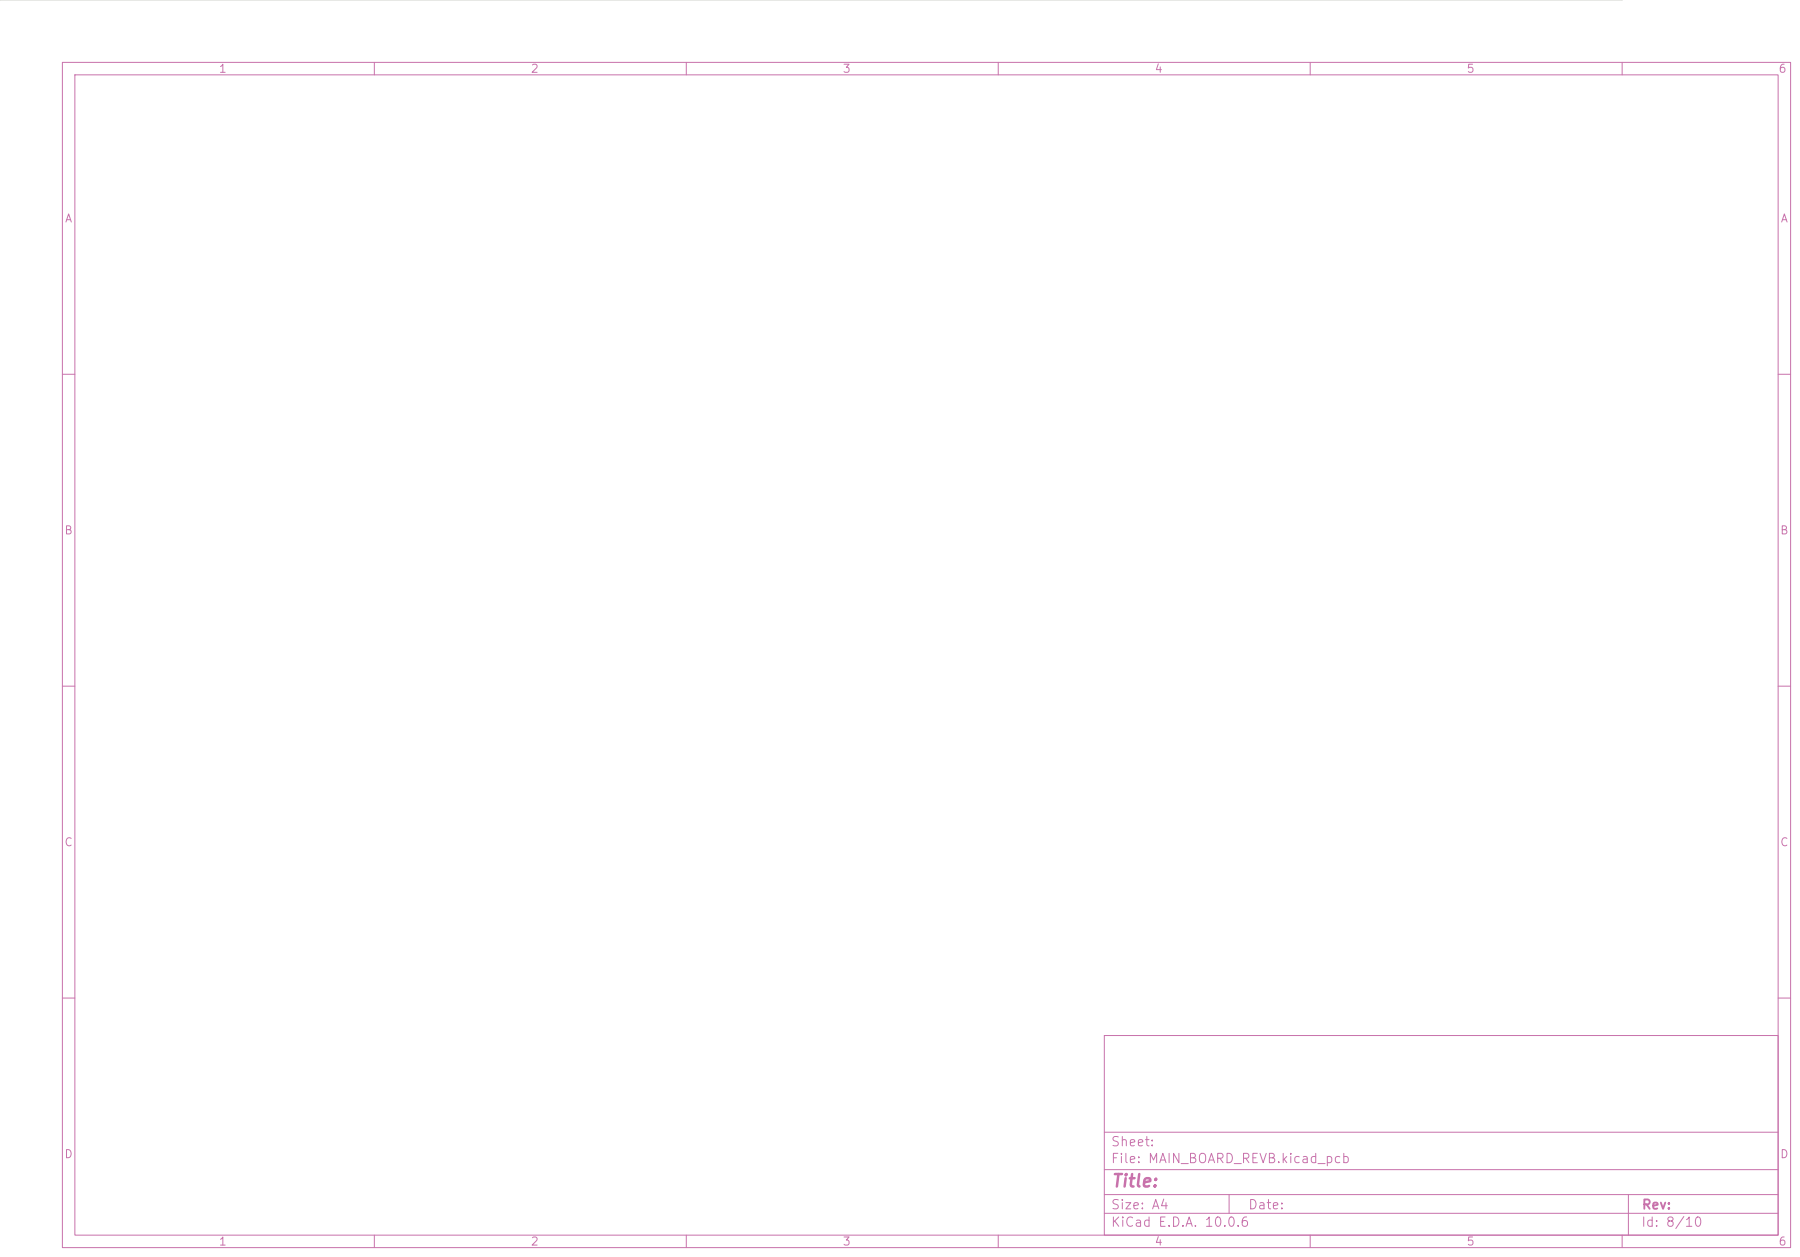
[picture p196: page 8]

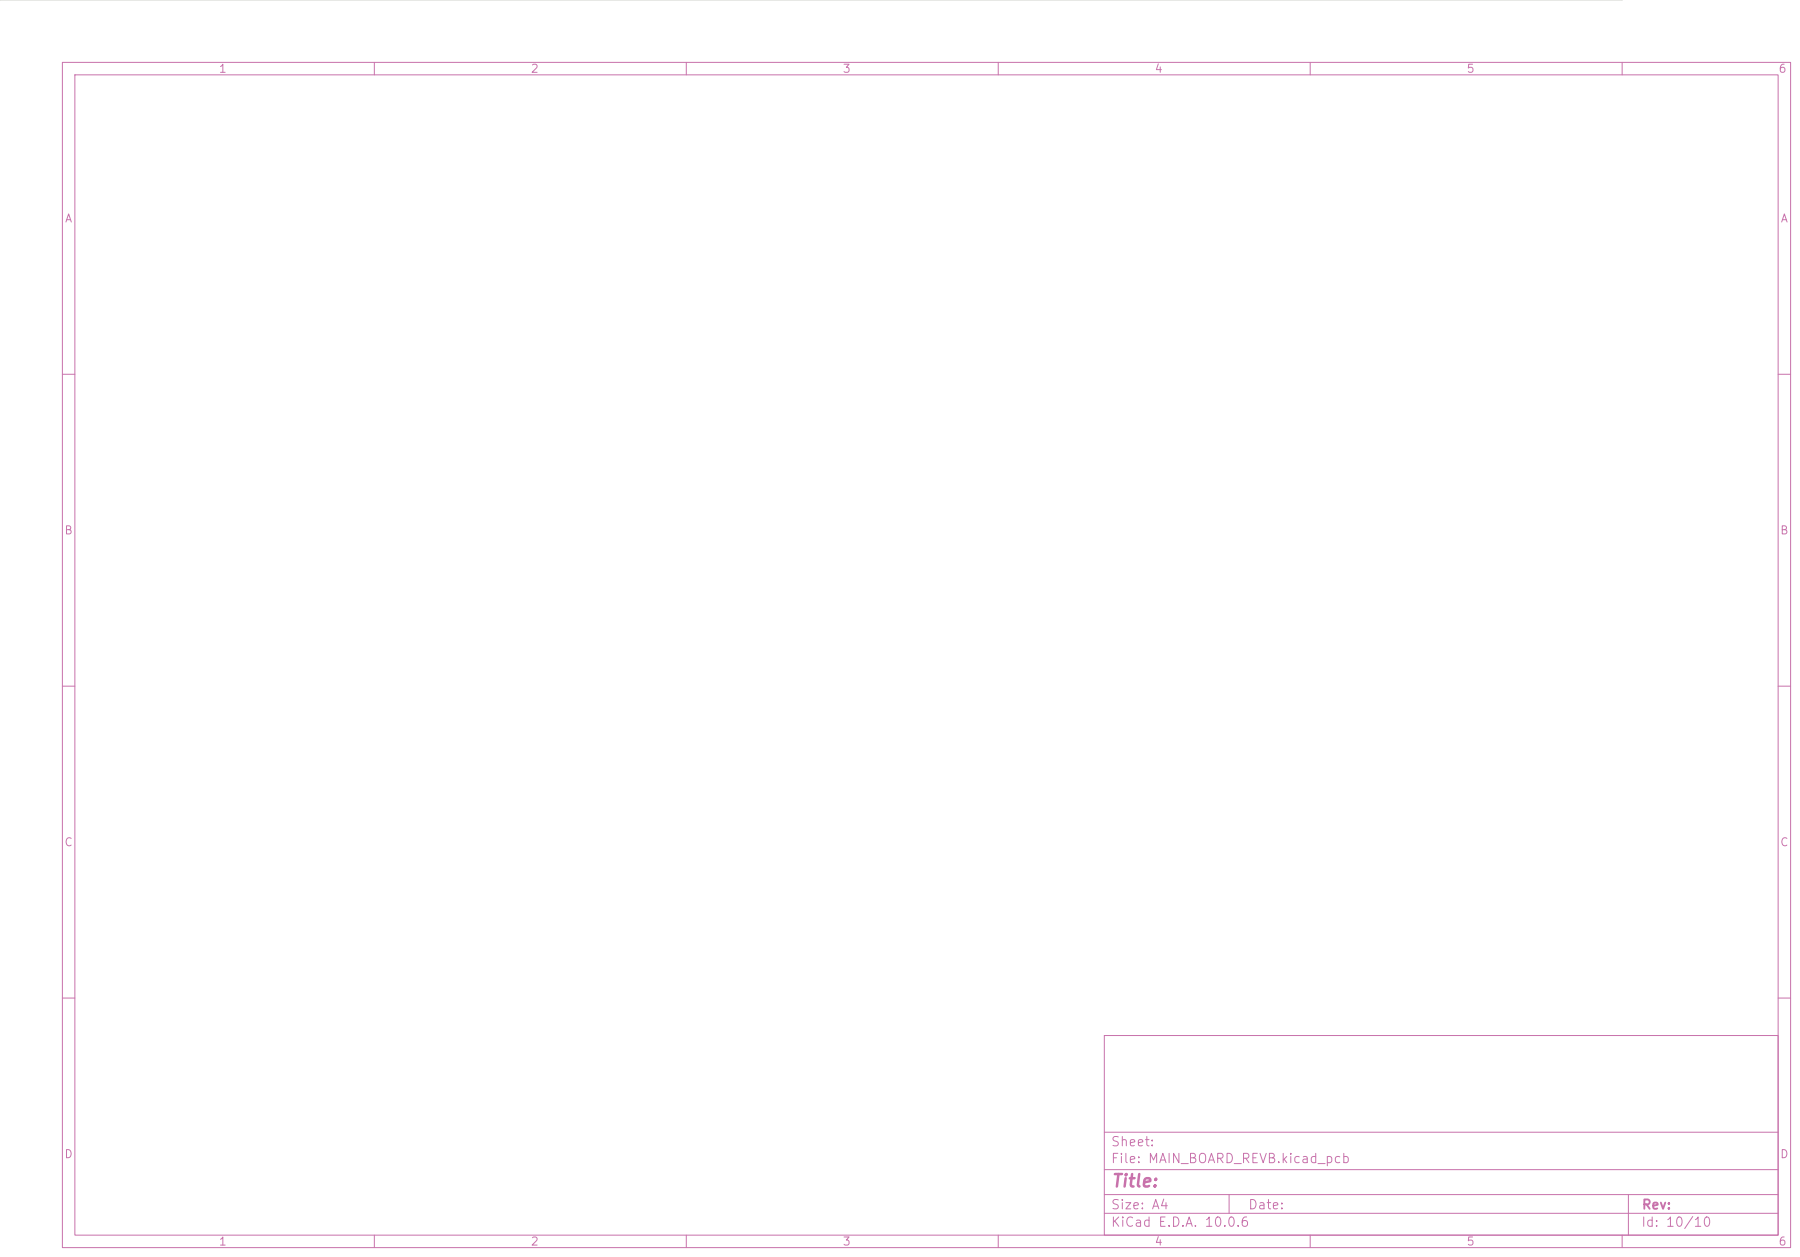
[picture p197: page 10]
