herasymyuks/PLFM_RADAR-aeris/beta/pcb/FREQUENCY_SYNTHESIZER/exports/drawings/FREQUENCY_SYNTHESIZER_bottom_layer_mirrored.pdf

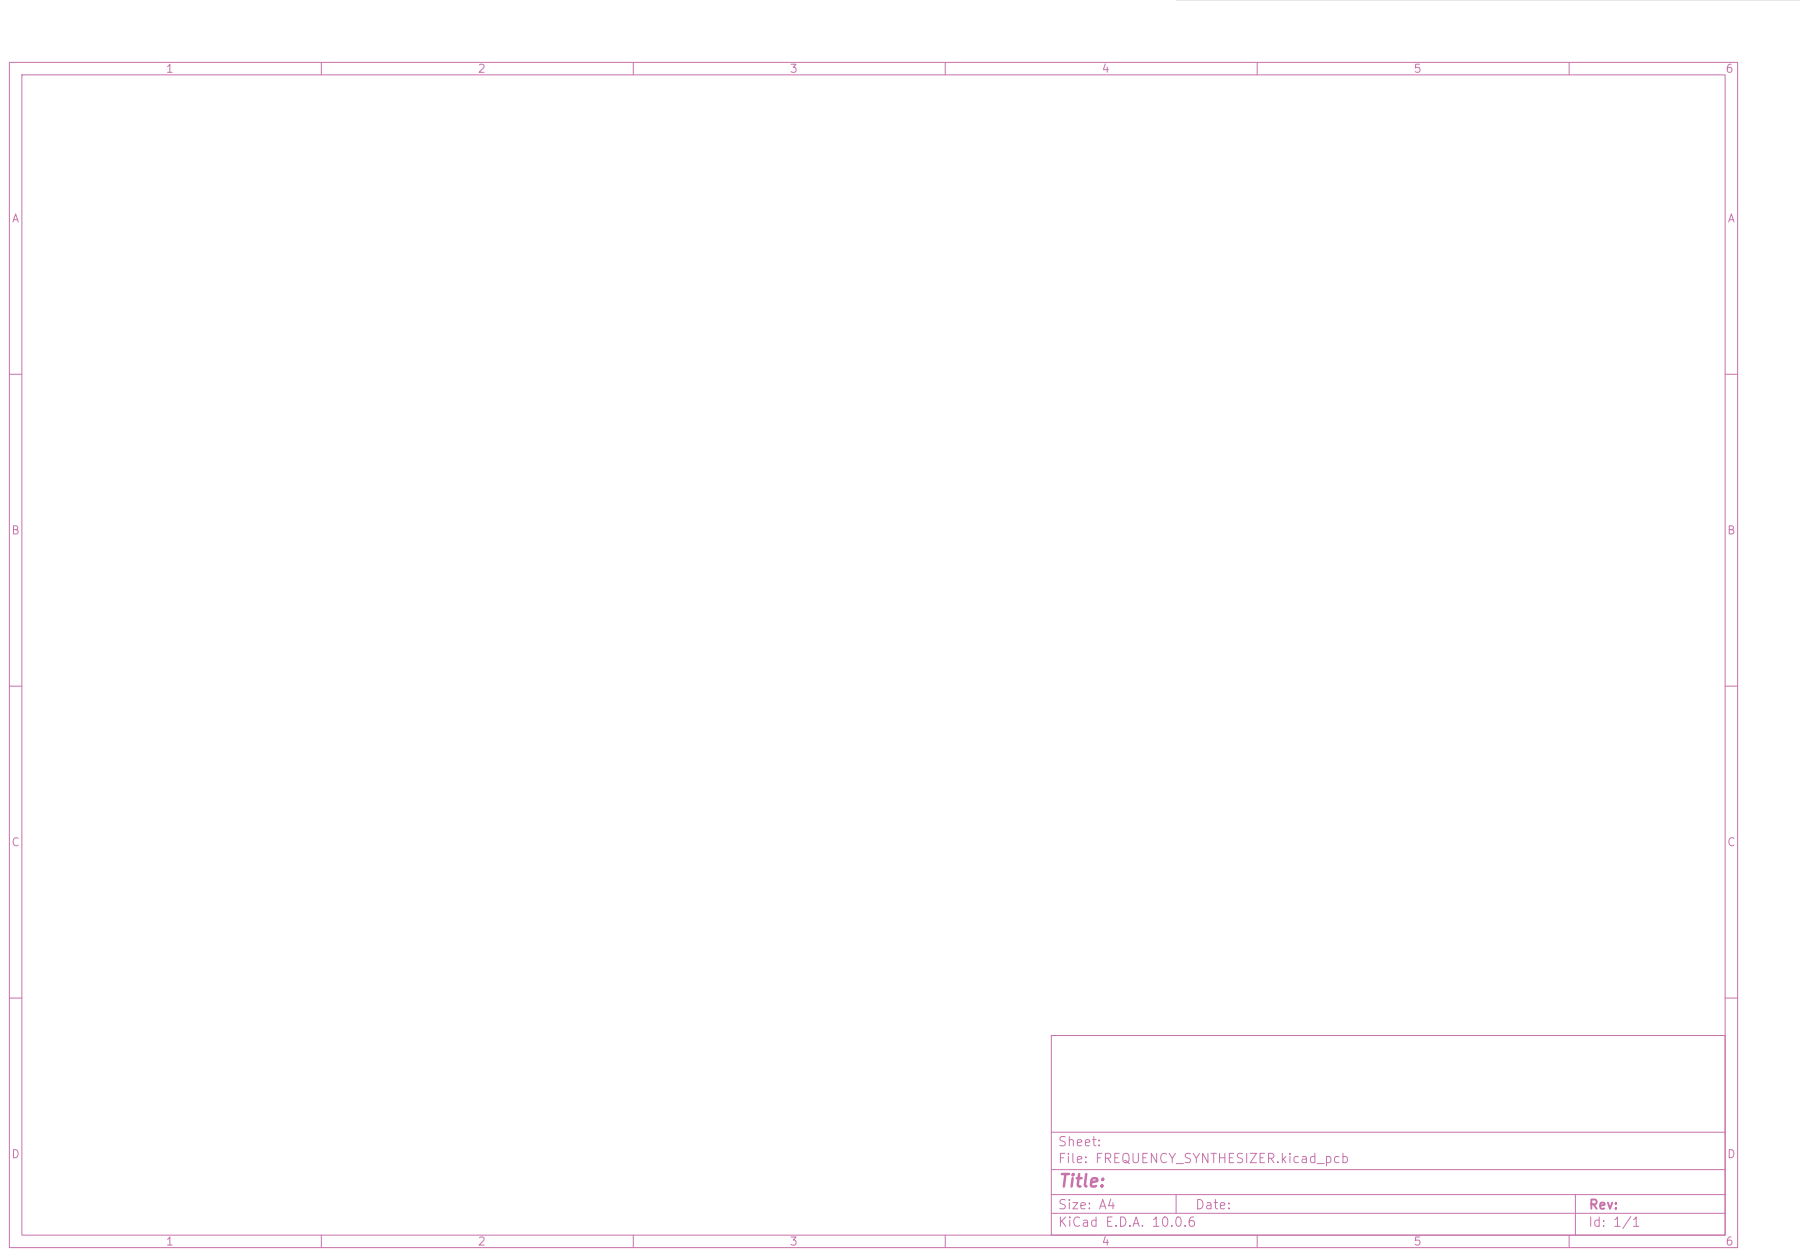
[picture p200: page 1]

Size: A4 | Rev:
KiCad E.D.A. 10.0.6 | Id: 1/1
