herasymyuks/PLFM_RADAR-aeris/beta/pcb/FREQUENCY_SYNTHESIZER/exports/drawings/FREQUENCY_SYNTHESIZER_copper_layers.pdf

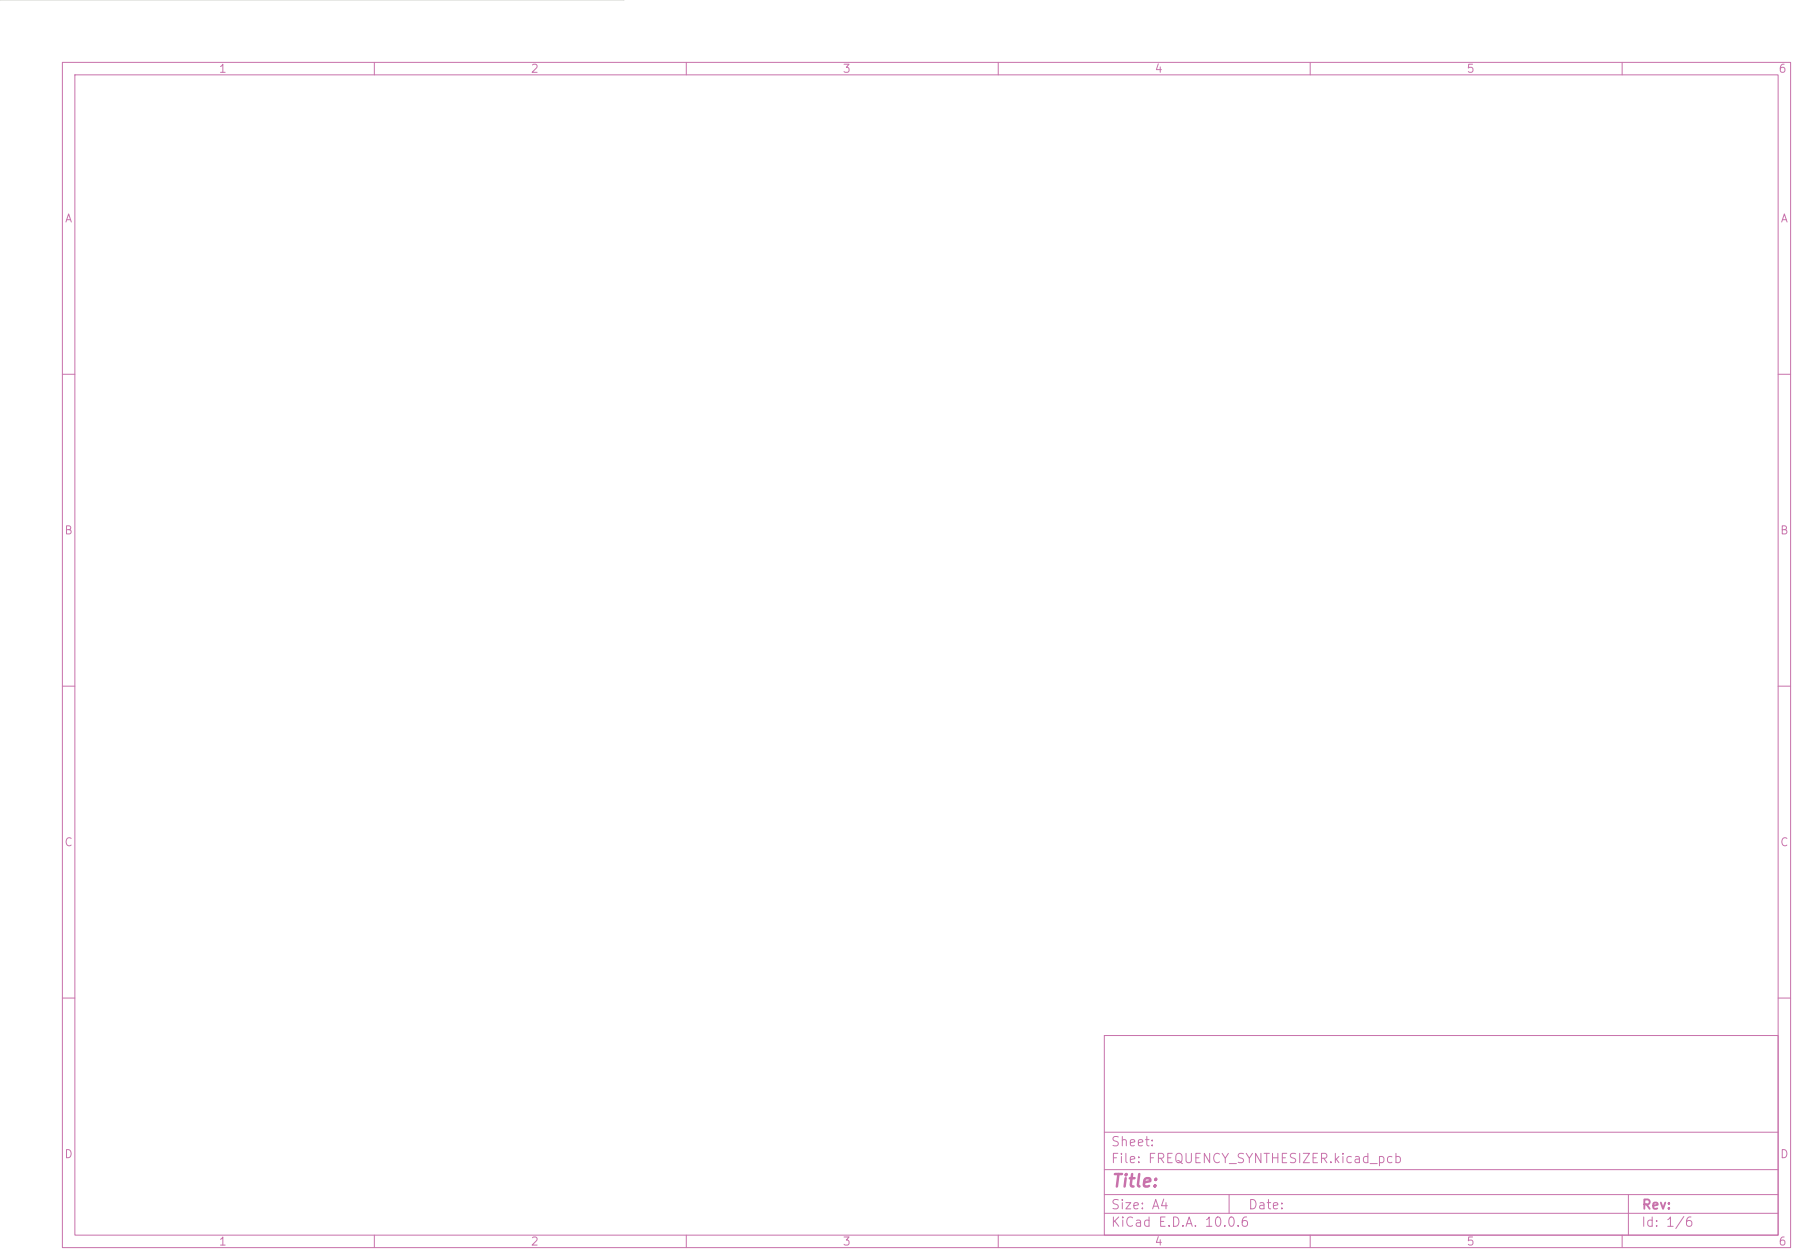
[picture p201: page 1]

Size: A4 | Rev:
KiCad E.D.A. 10.0.6 | Id: 1/6

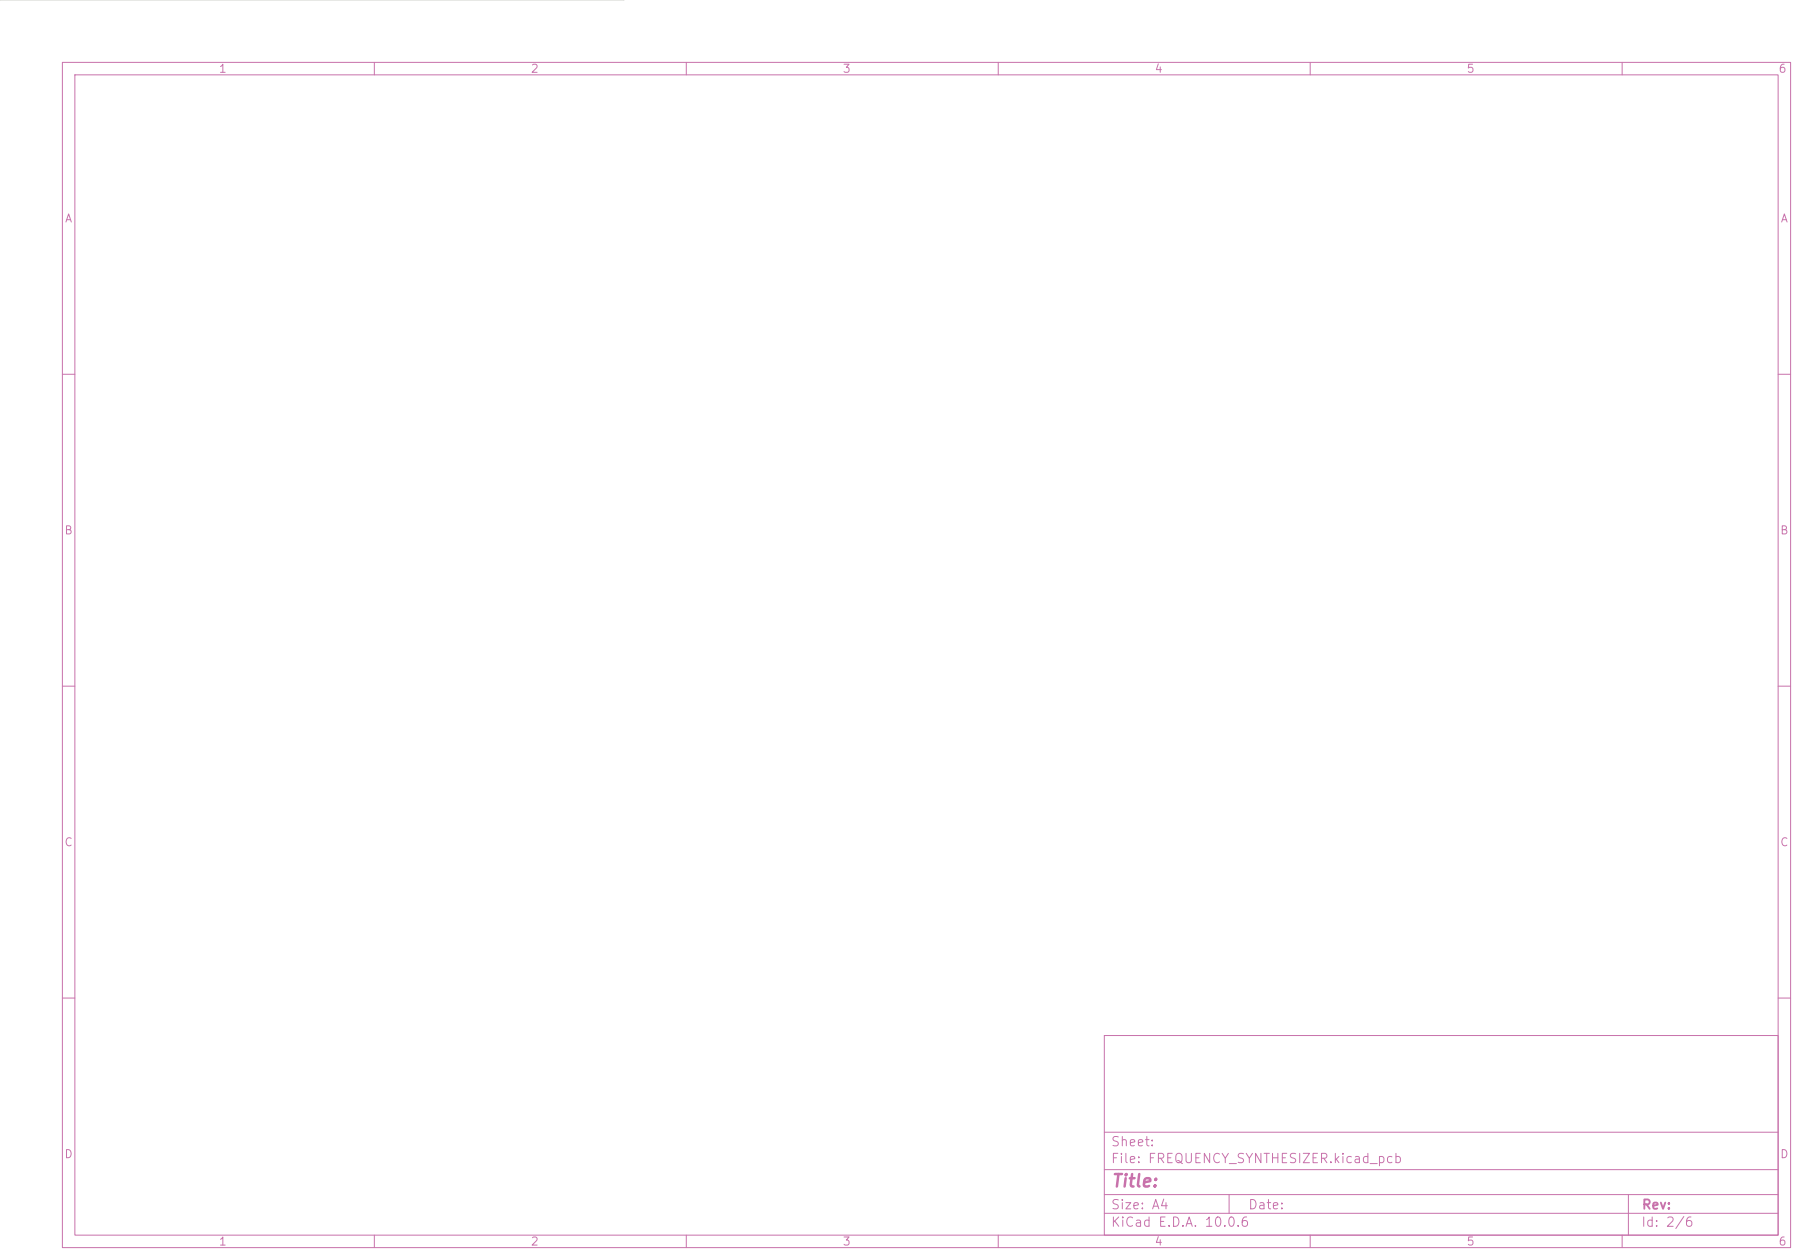
[picture p202: page 2]

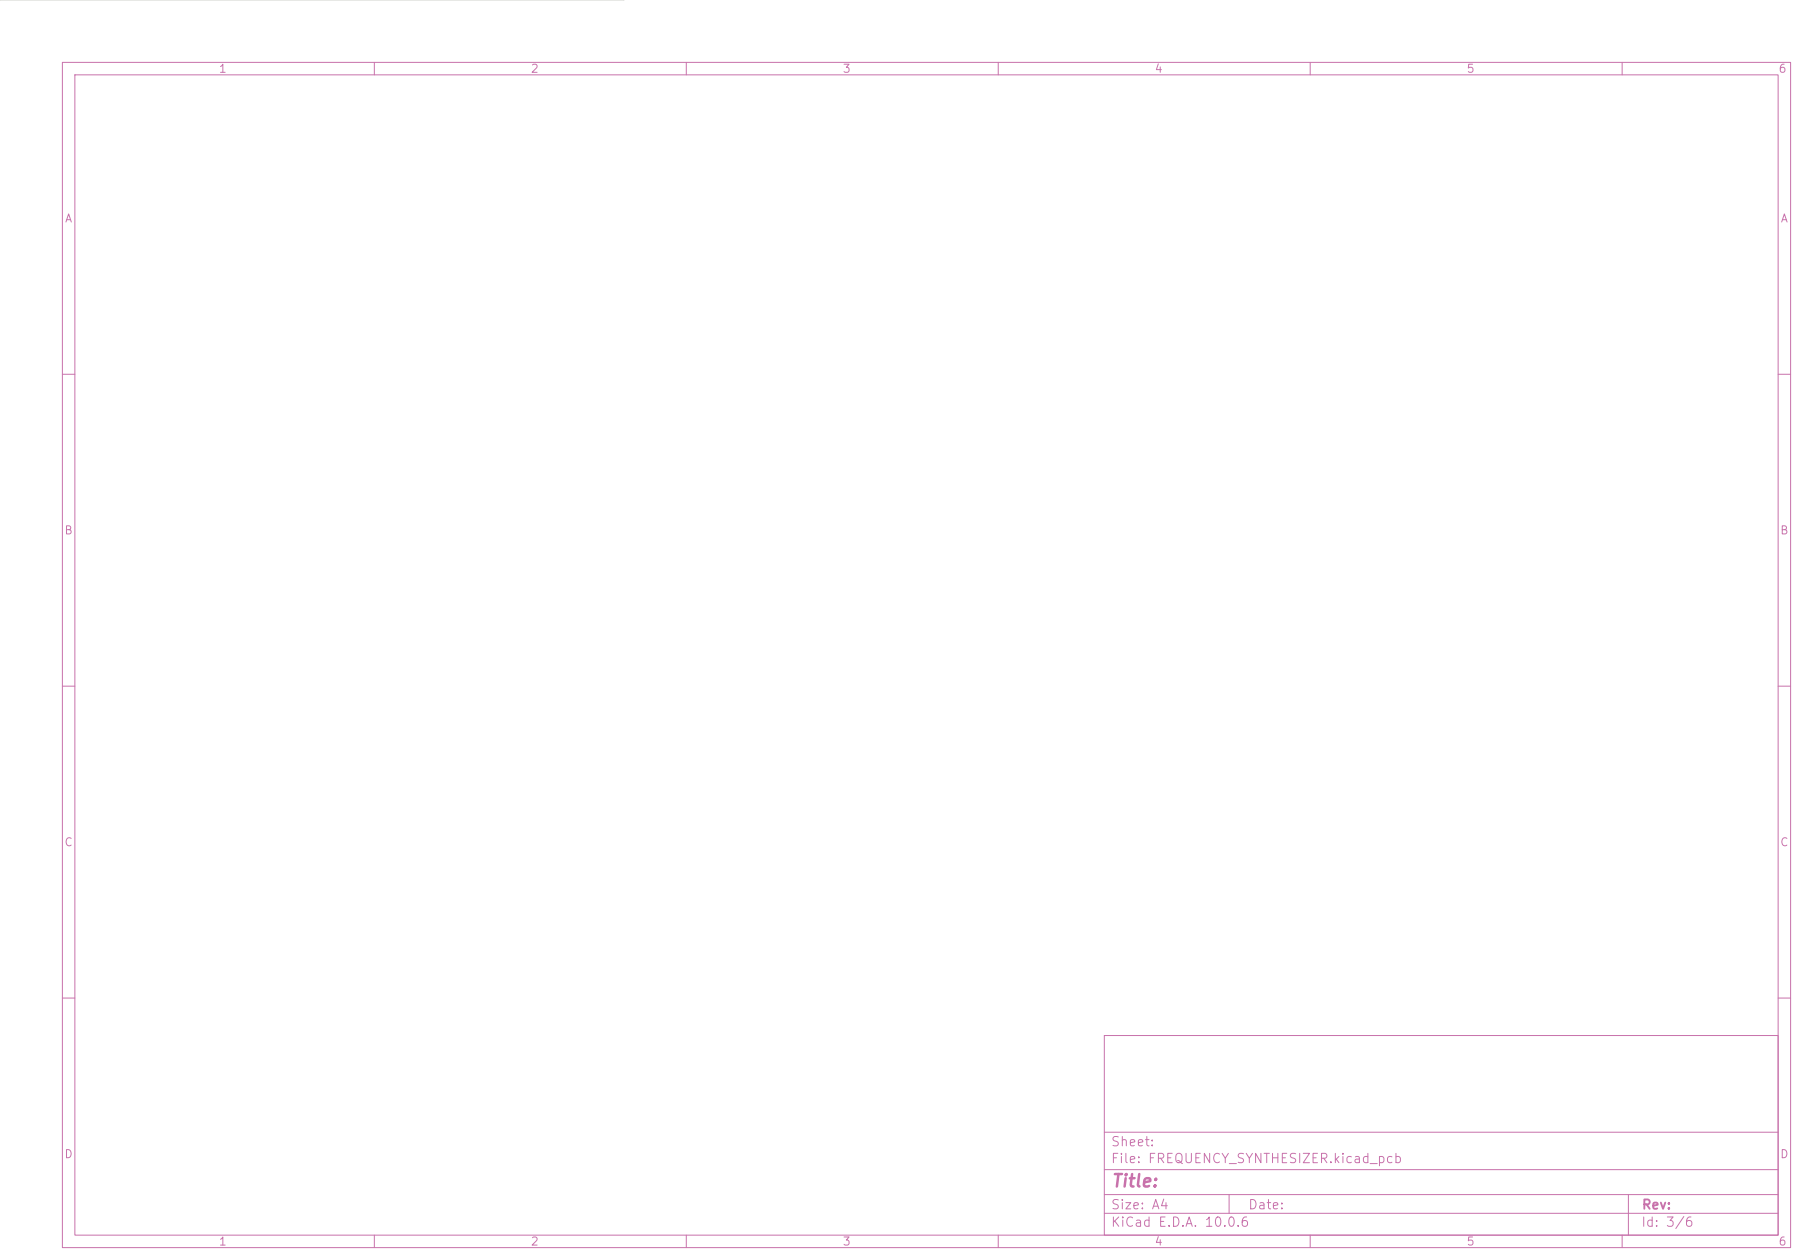
[picture p203: page 3]

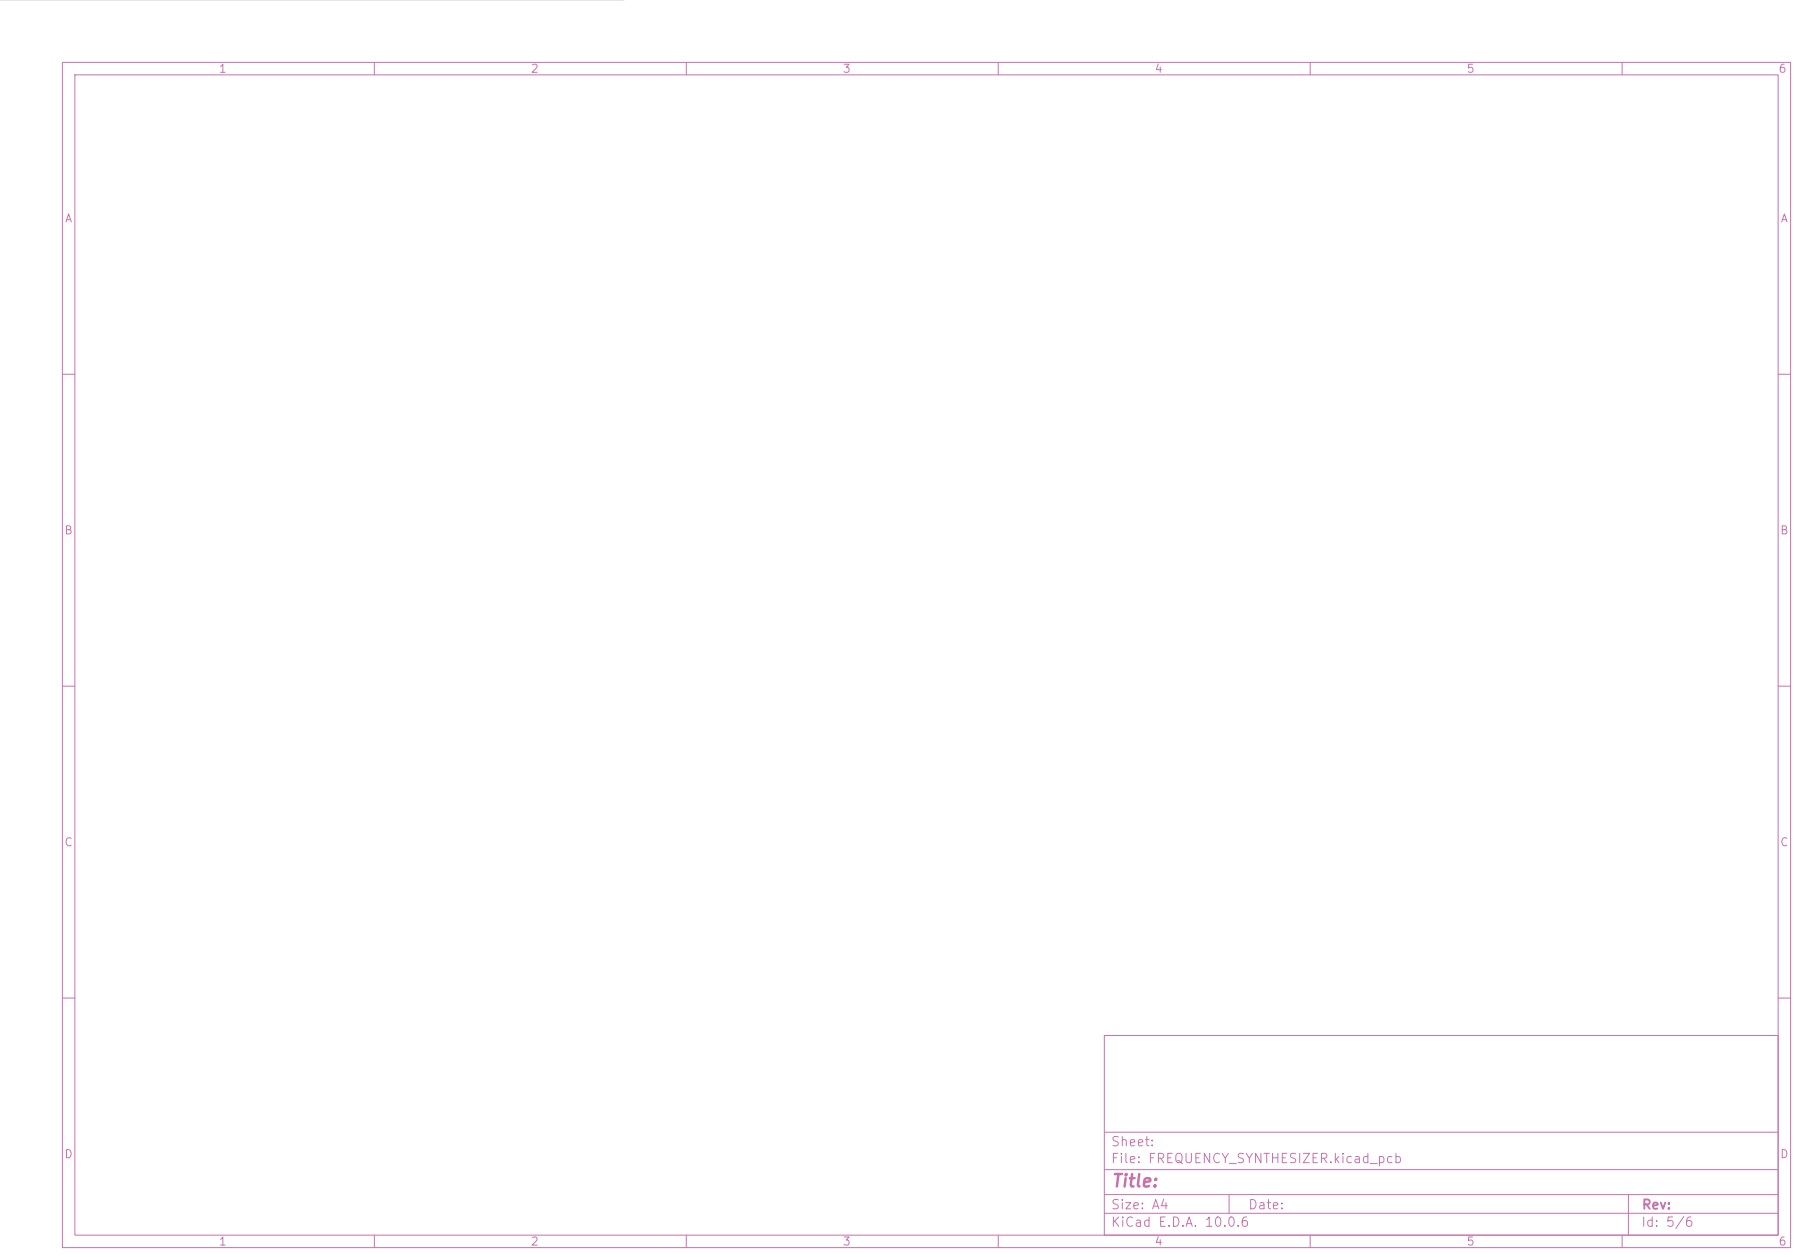
[picture p204: page 5]

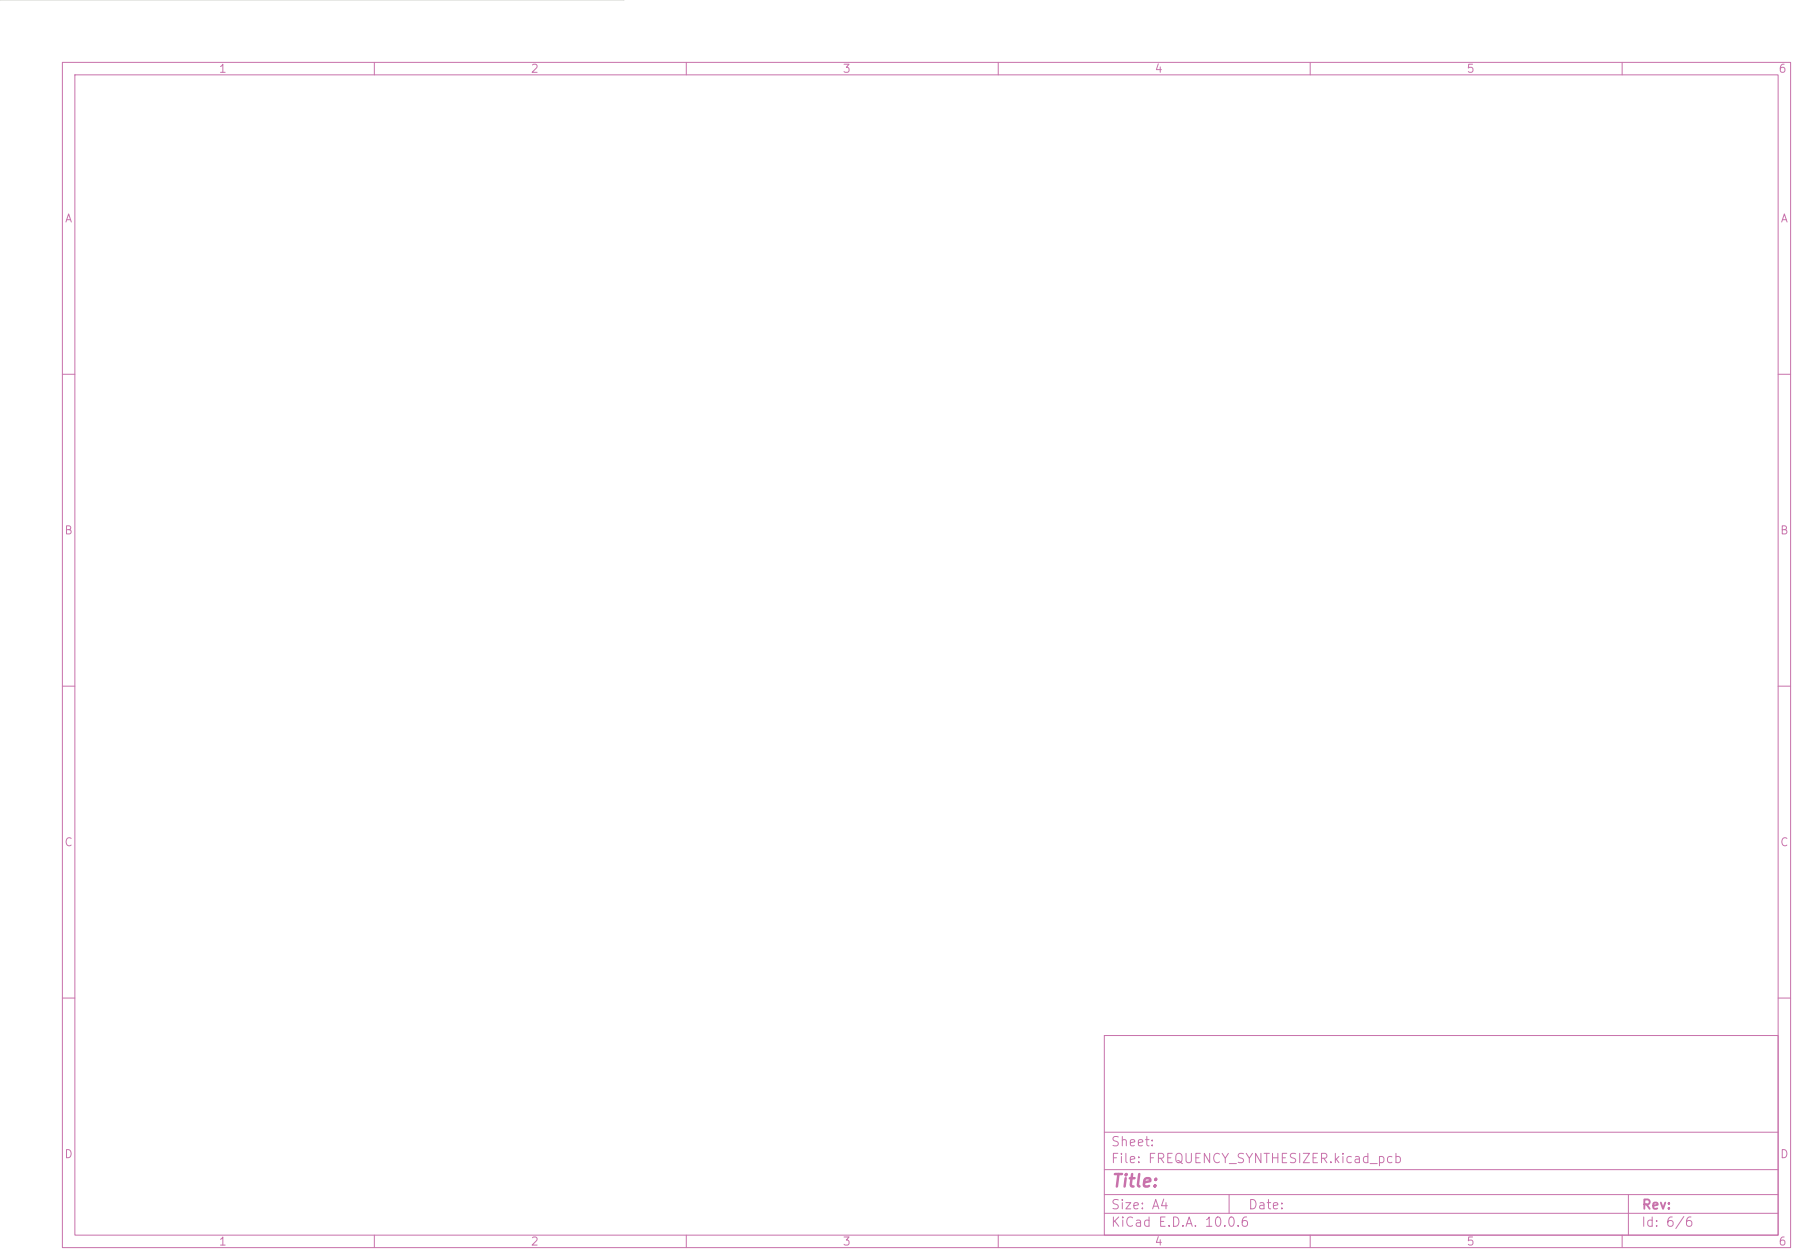
[picture p205: page 6]
