herasymyuks/PLFM_RADAR-aeris/beta/pcb/POWER_SUPPLY/exports/drawings/POWER_SUPPLY_bottom_layer_mirrored.pdf

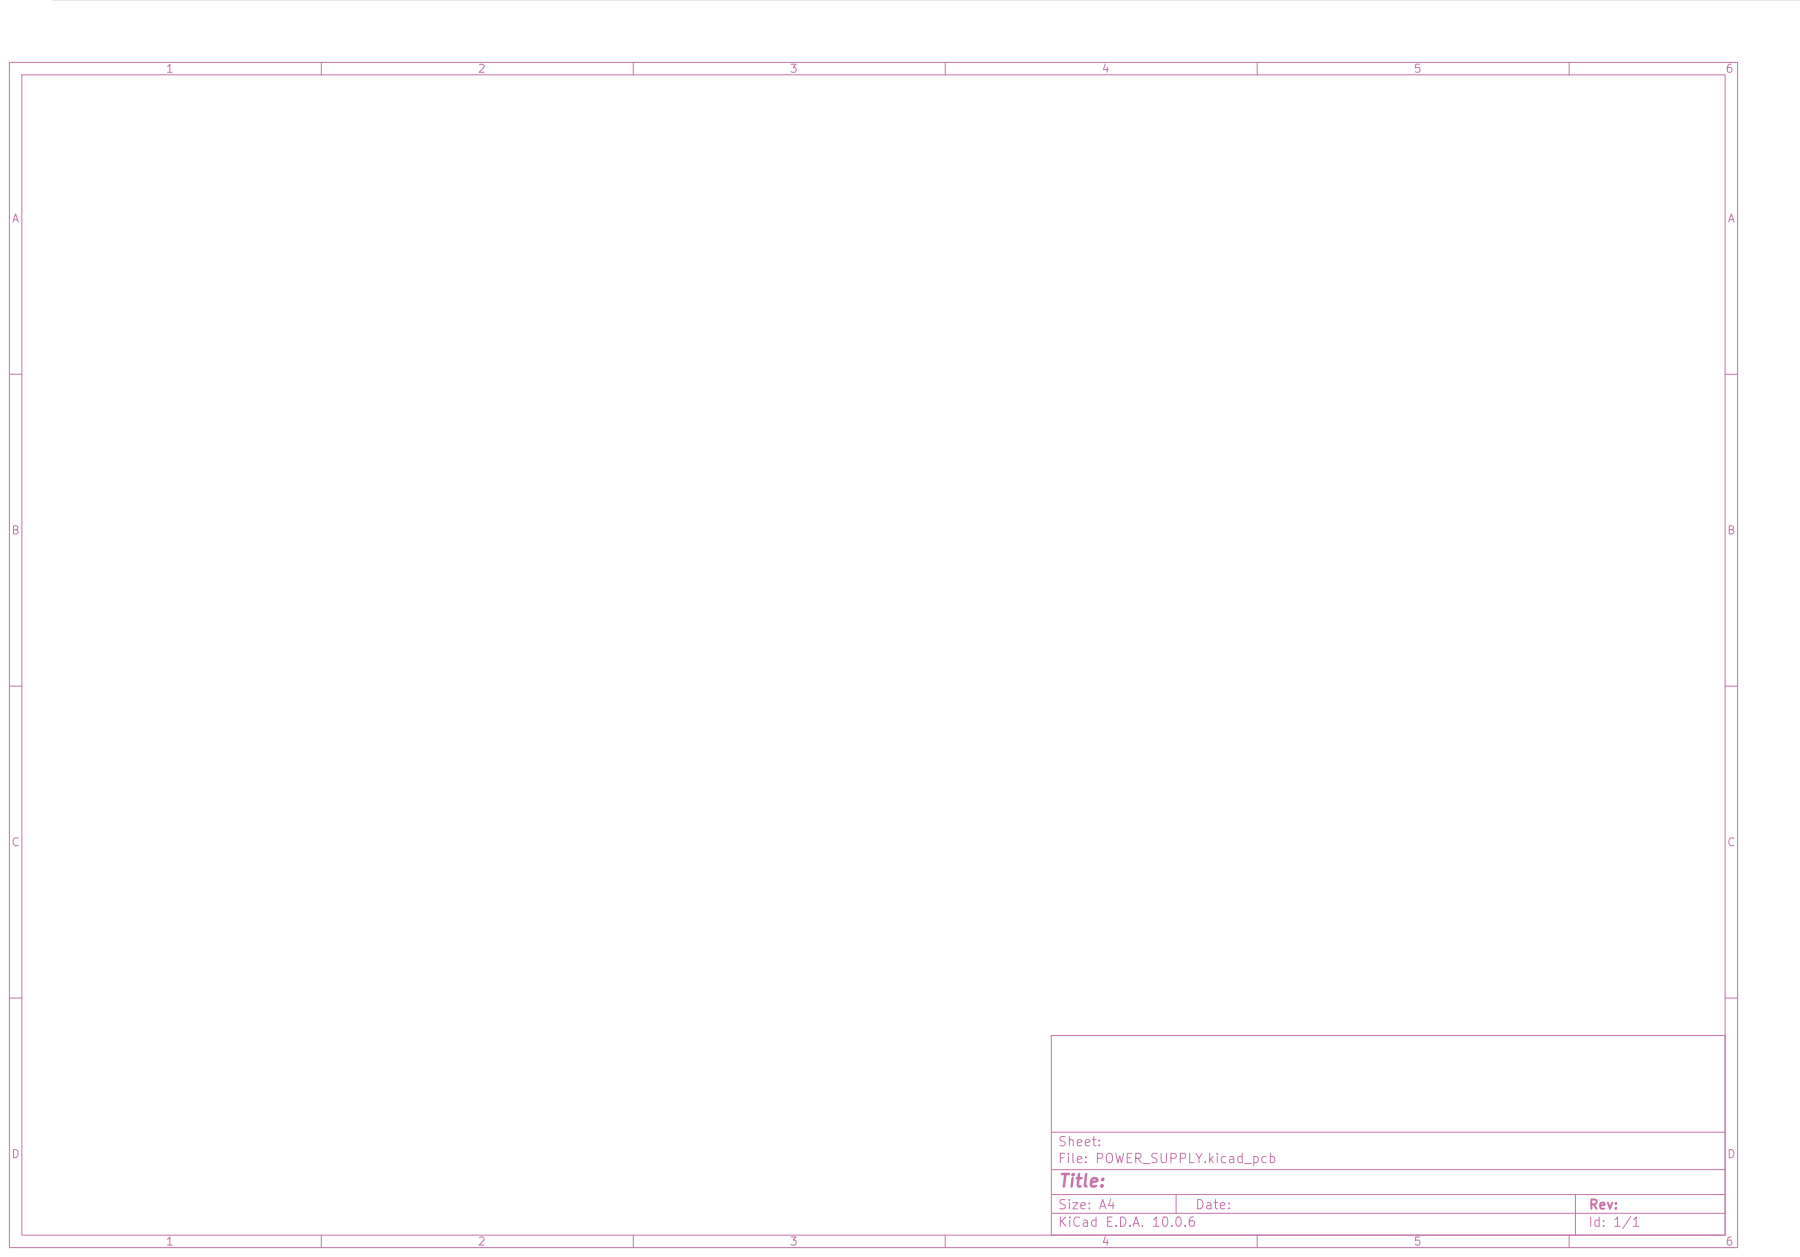
[picture p207: page 1]

Size: A4 | Rev:
KiCad E.D.A. 10.0.6 | Id: 1/1
