herasymyuks/PLFM_RADAR-aeris/beta/pcb/POWER_SUPPLY/exports/drawings/POWER_SUPPLY_copper_layers.pdf

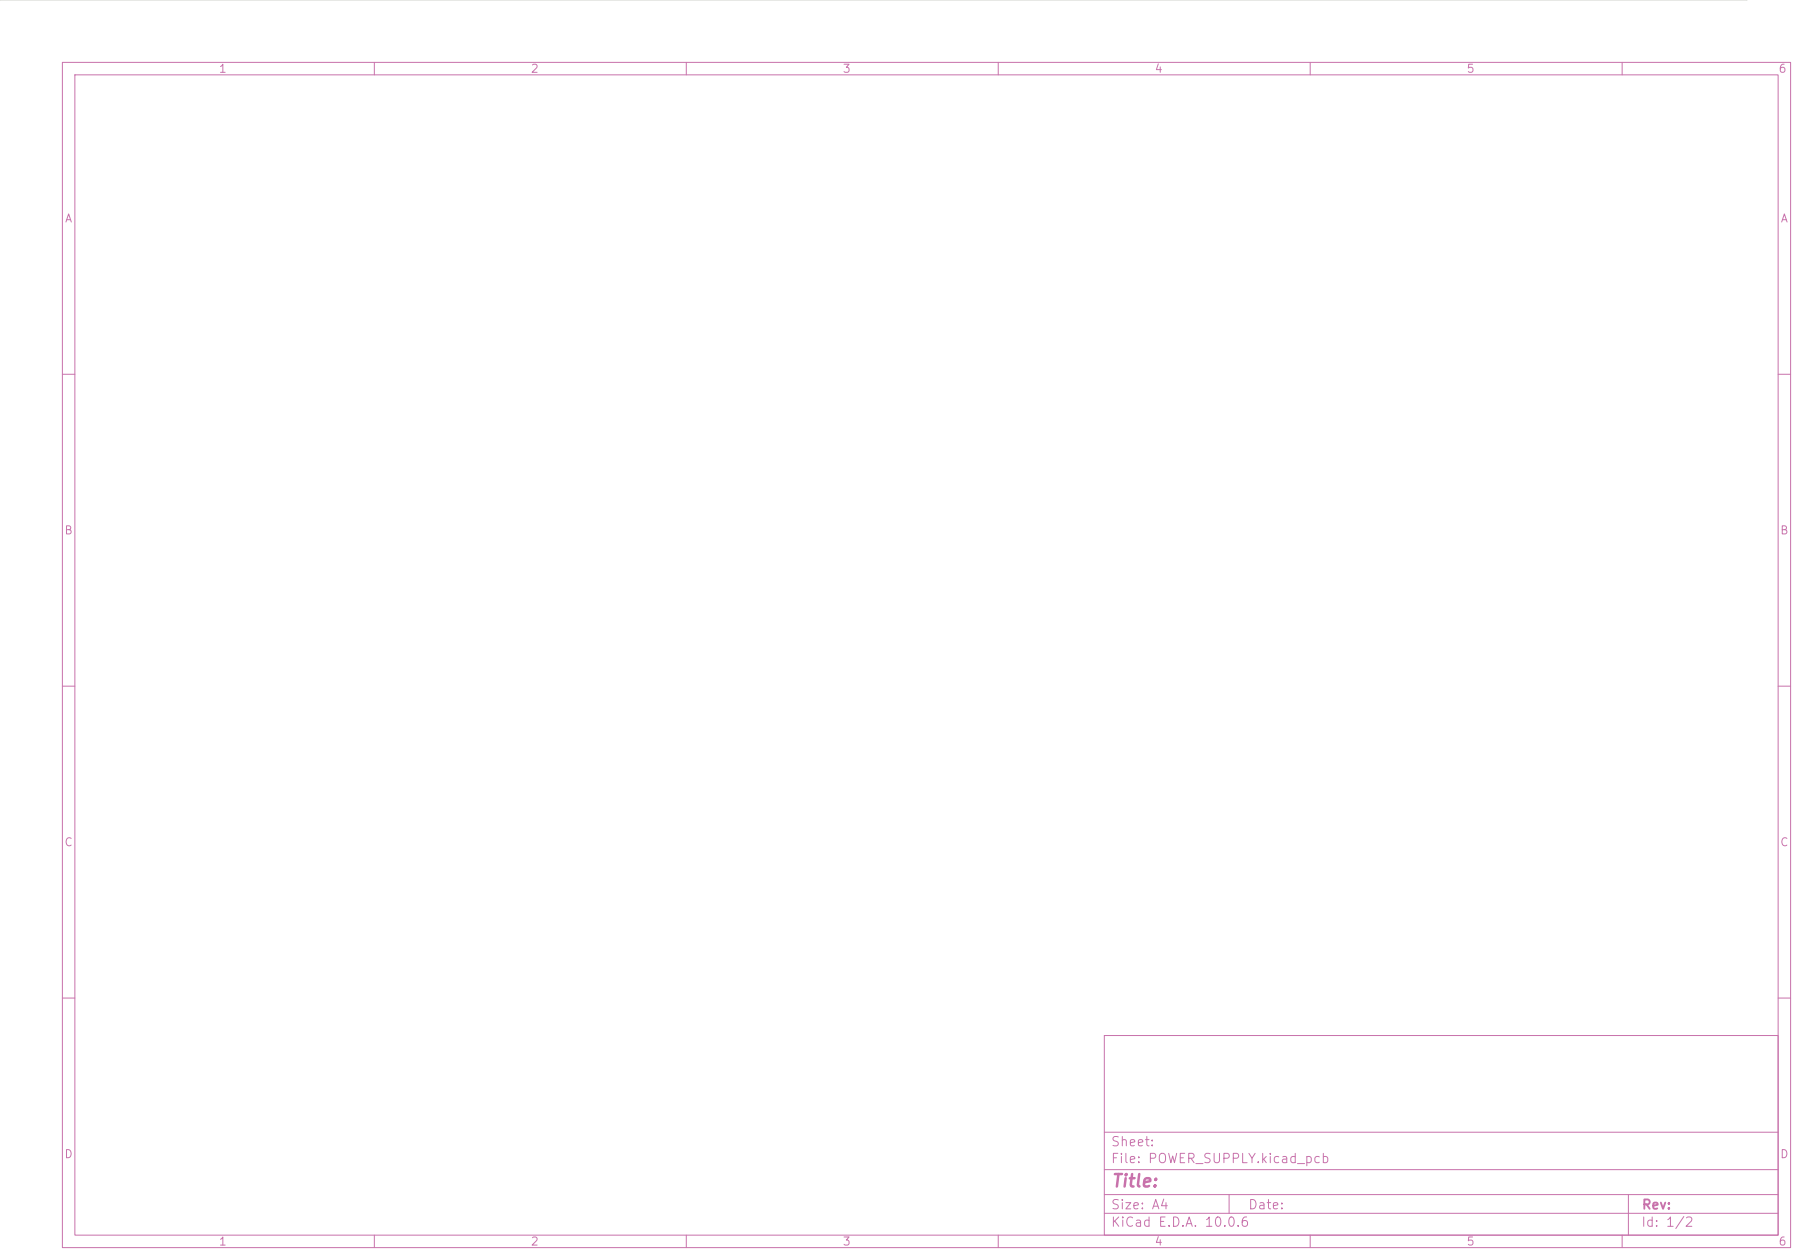
[picture p208: page 1]

Size: A4 | Rev:
KiCad E.D.A. 10.0.6 | Id: 1/2

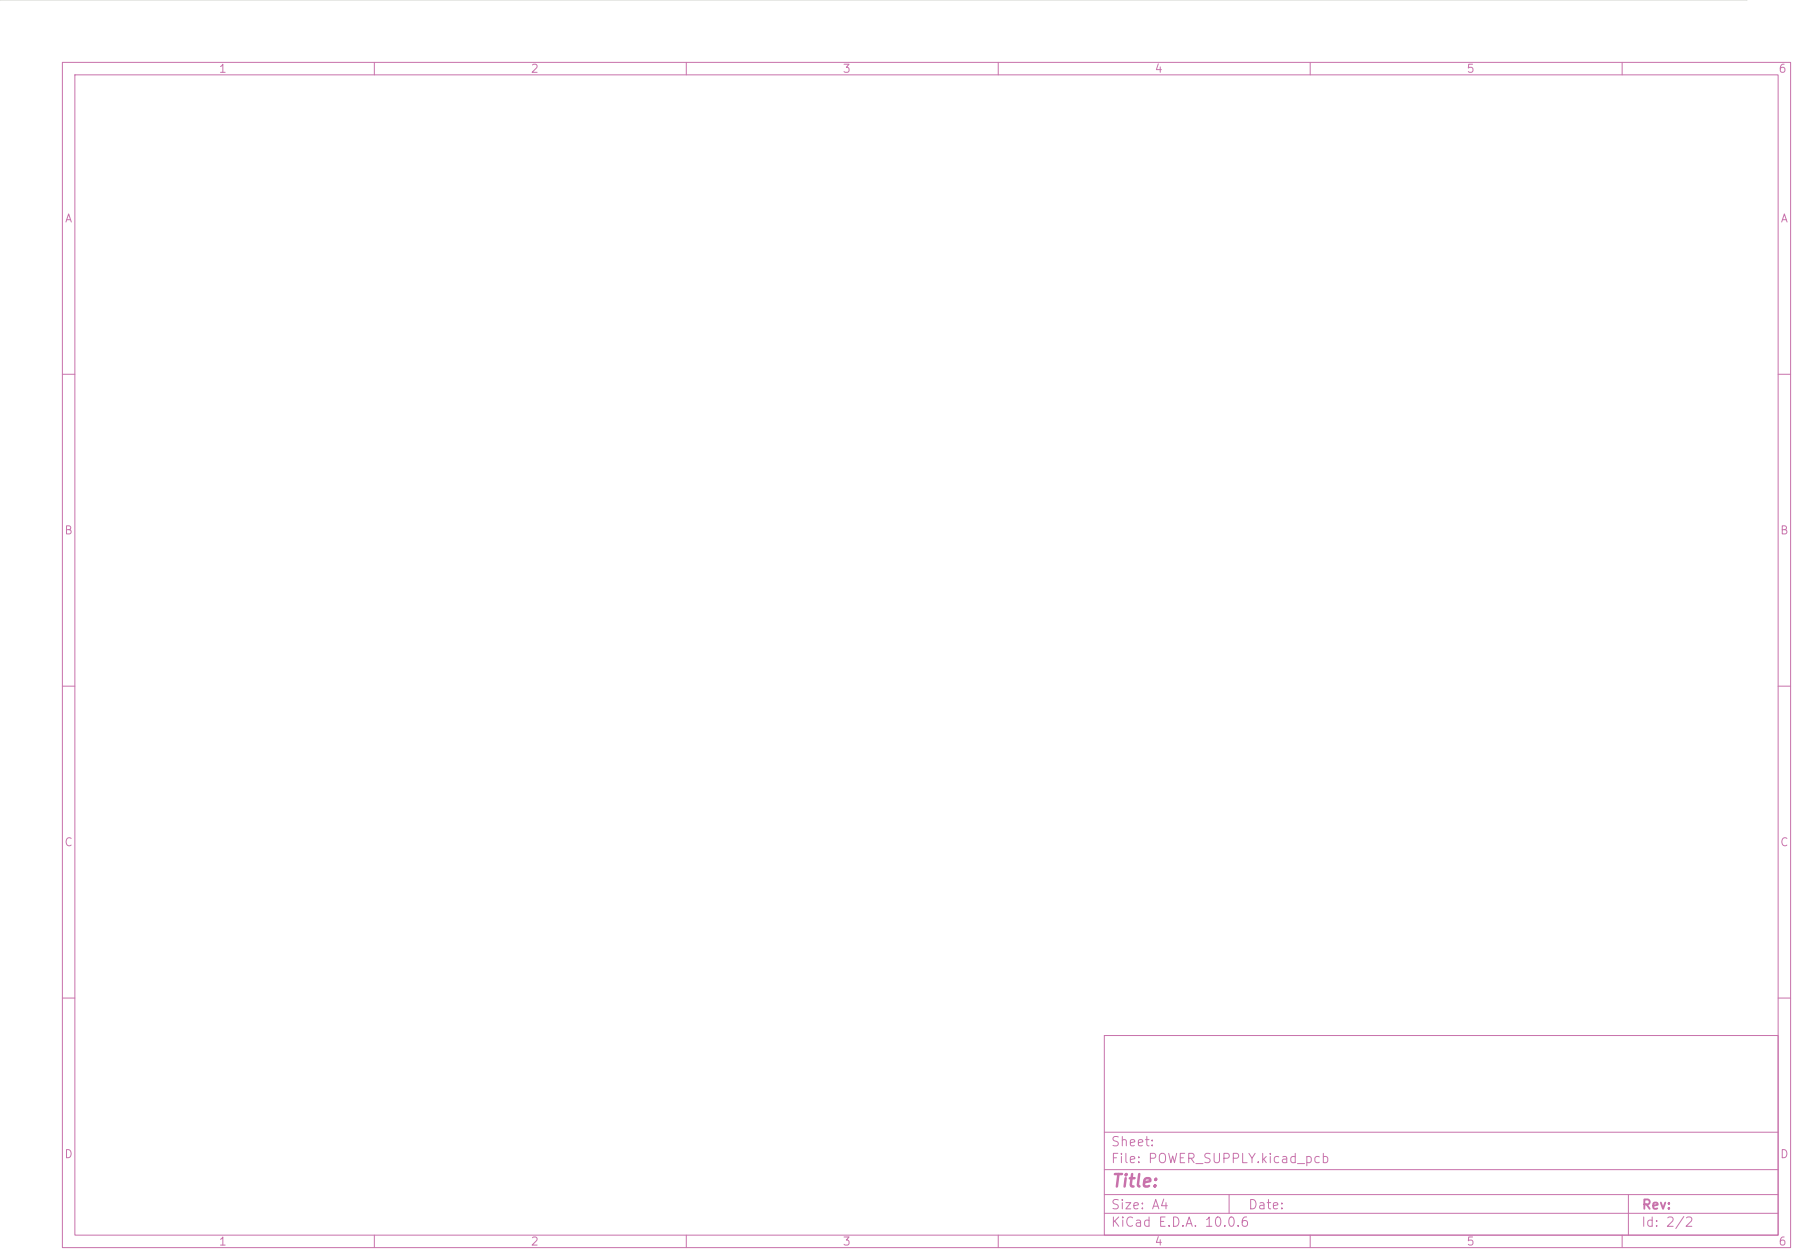
[picture p209: page 2]

Size: A4 | Rev:
KiCad E.D.A. 10.0.6 | Id: 2/2
