herasymyuks/PLFM_RADAR-aeris/beta/pcb/POWER_SUPPLY/exports/drawings/POWER_SUPPLY_top_layer.pdf

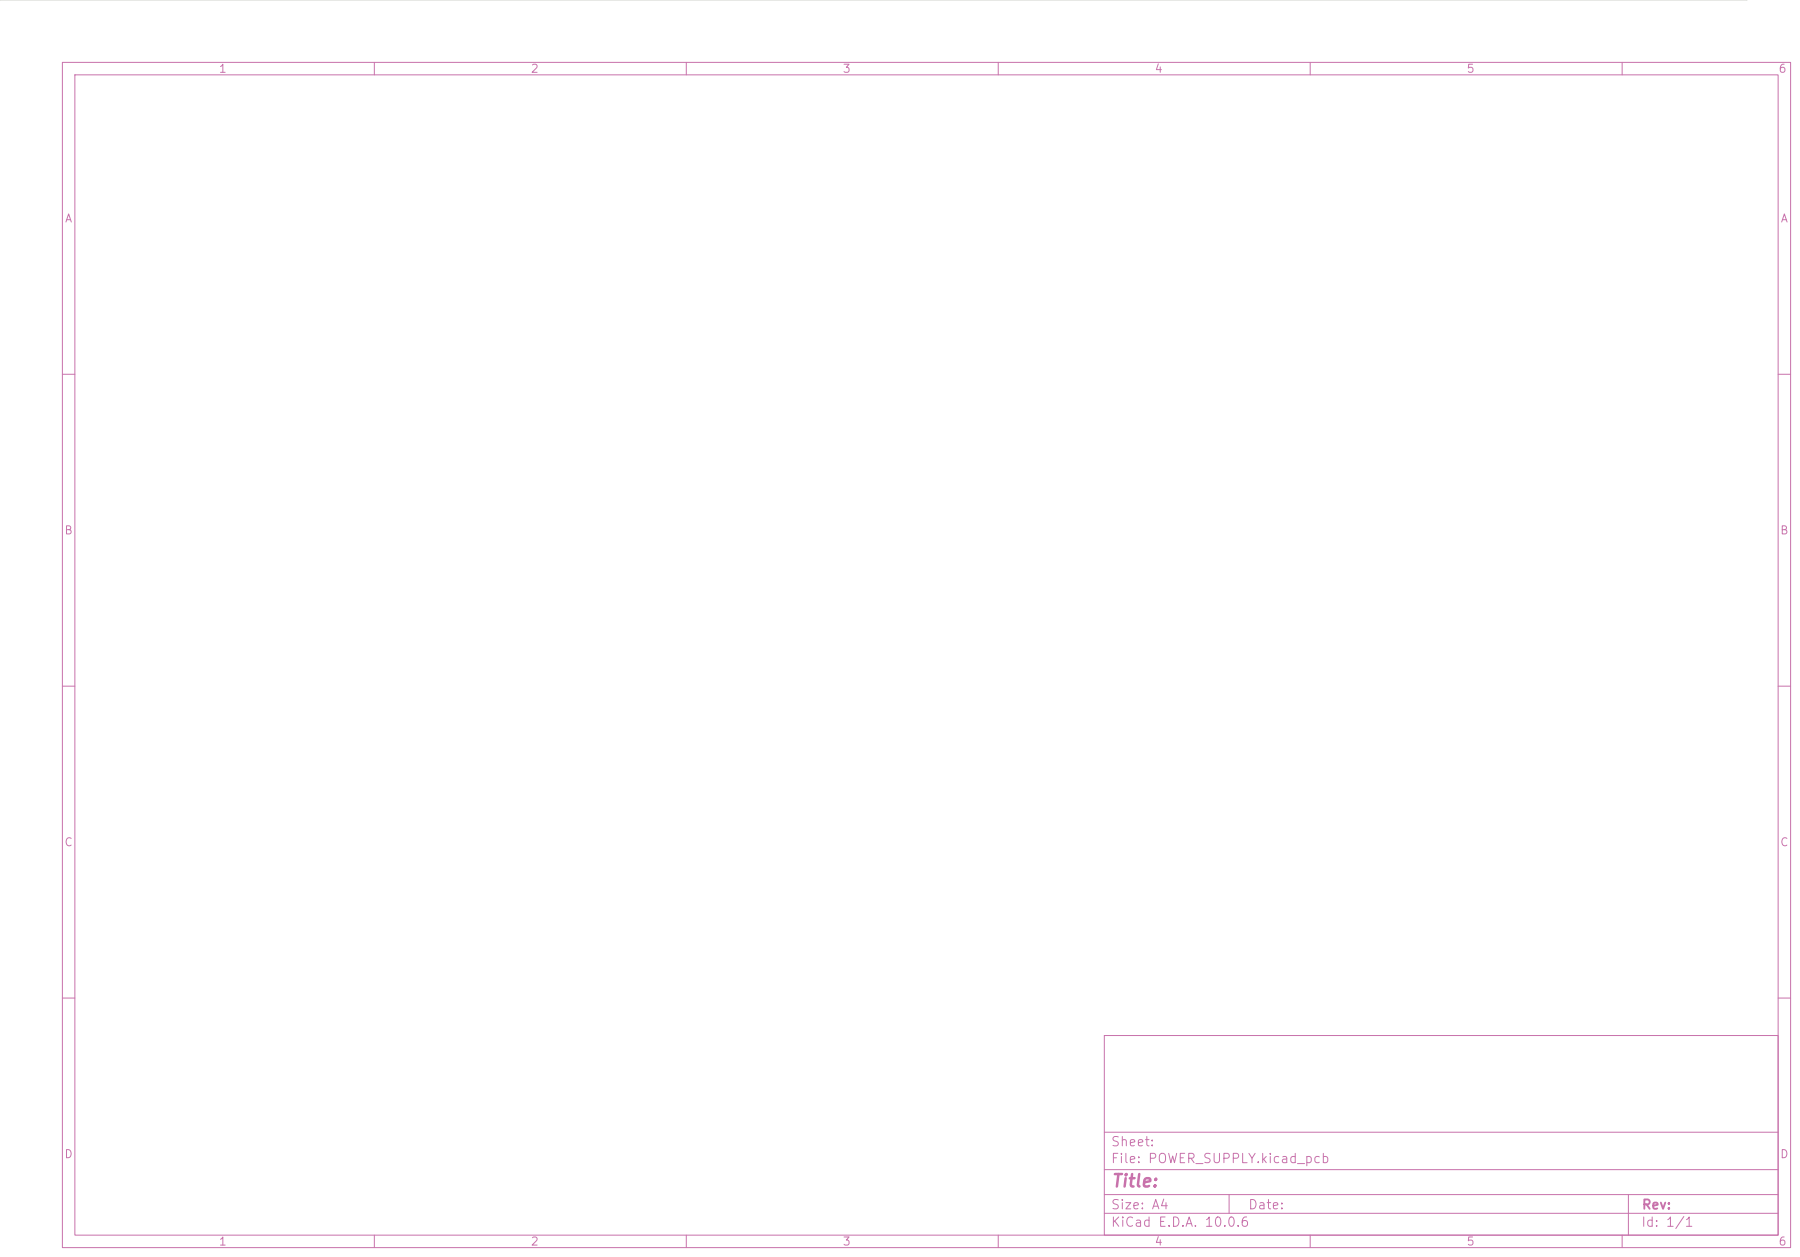
[picture p211: page 1]

Size: A4 | Rev:
KiCad E.D.A. 10.0.6 | Id: 1/1
