herasymyuks/PLFM_RADAR-aeris/beta/pcb/RF_PA/exports/drawings/RF_PA_bottom_layer_mirrored.pdf

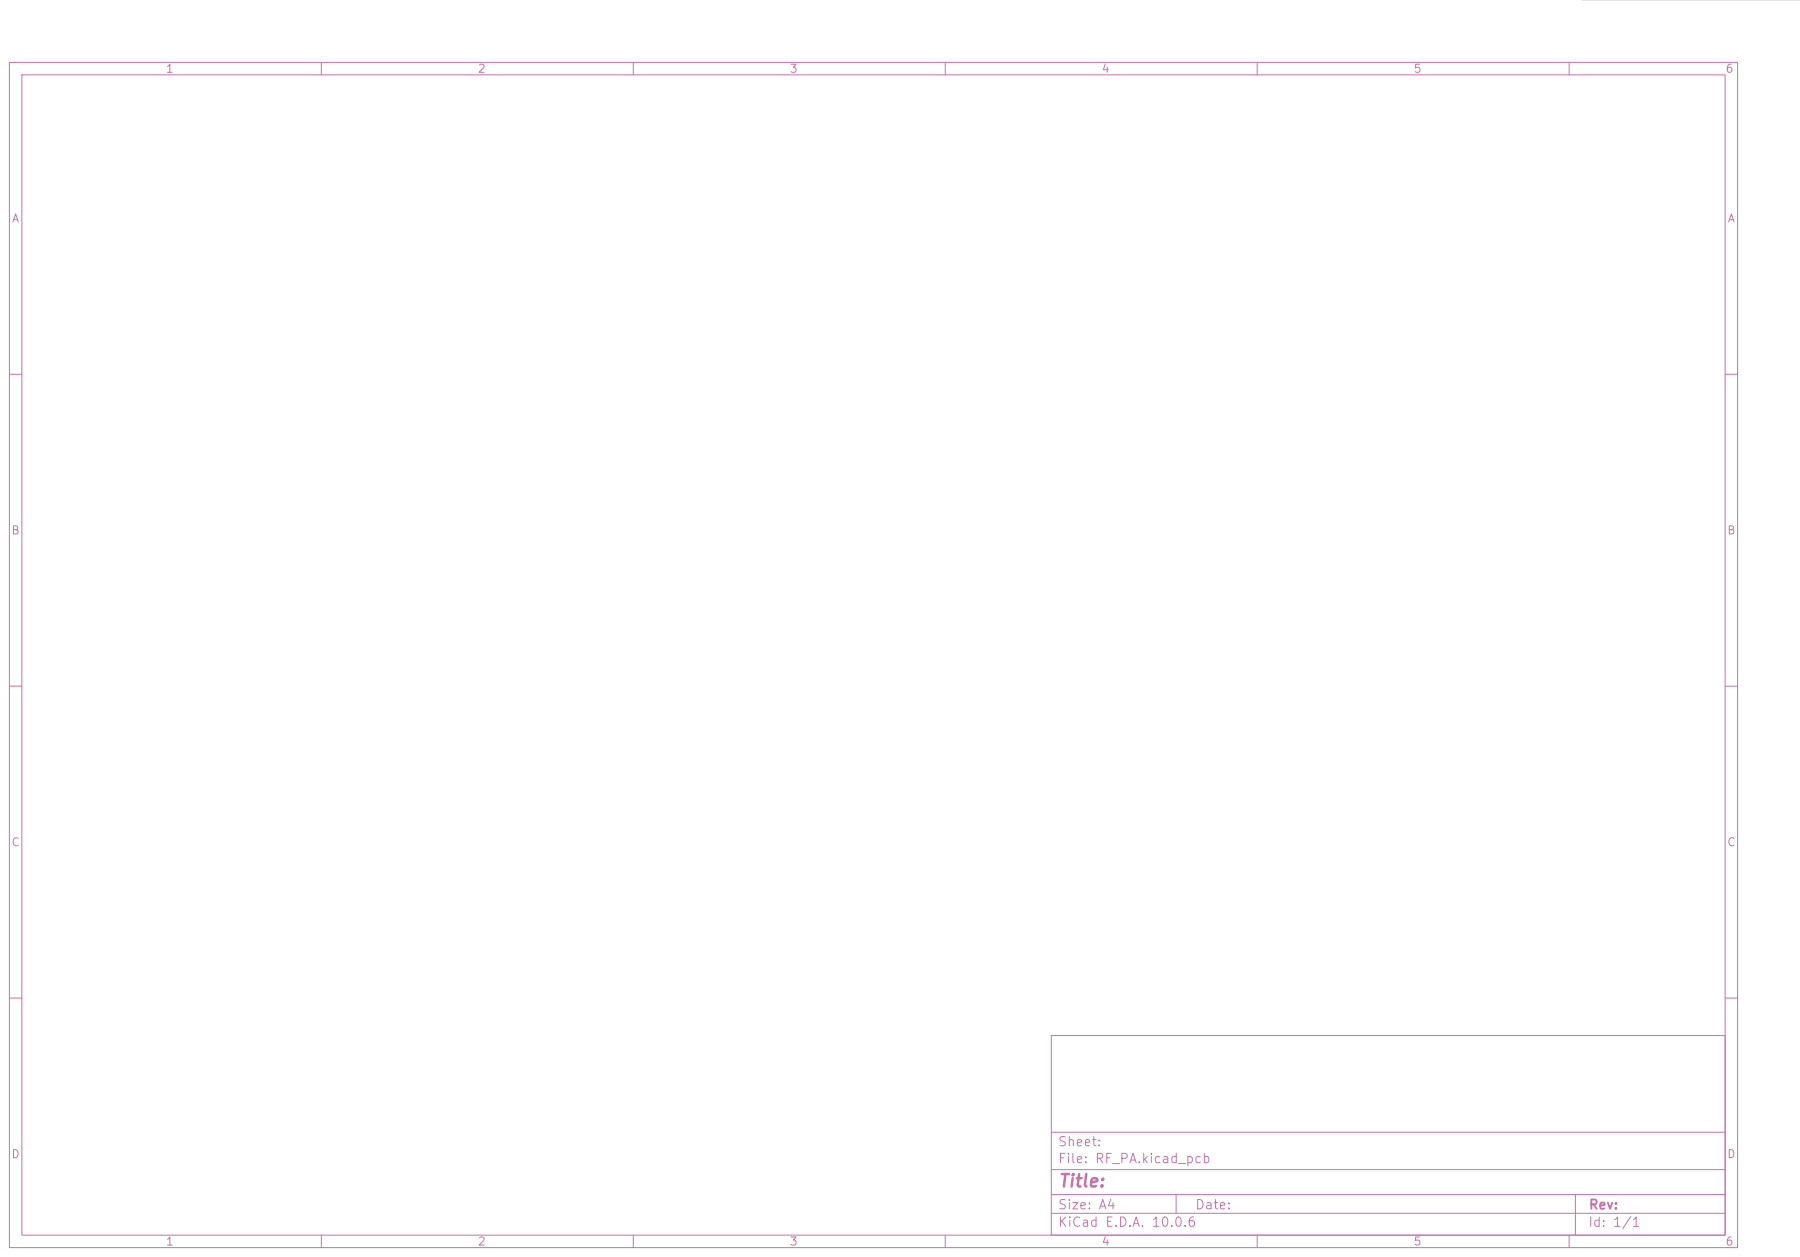
[picture p212: page 1]

Size: A4 | Rev:
KiCad E.D.A. 10.0.6 | Id: 1/1
