herasymyuks/PLFM_RADAR-aeris/beta/pcb/RF_PA/exports/drawings/RF_PA_copper_layers.pdf

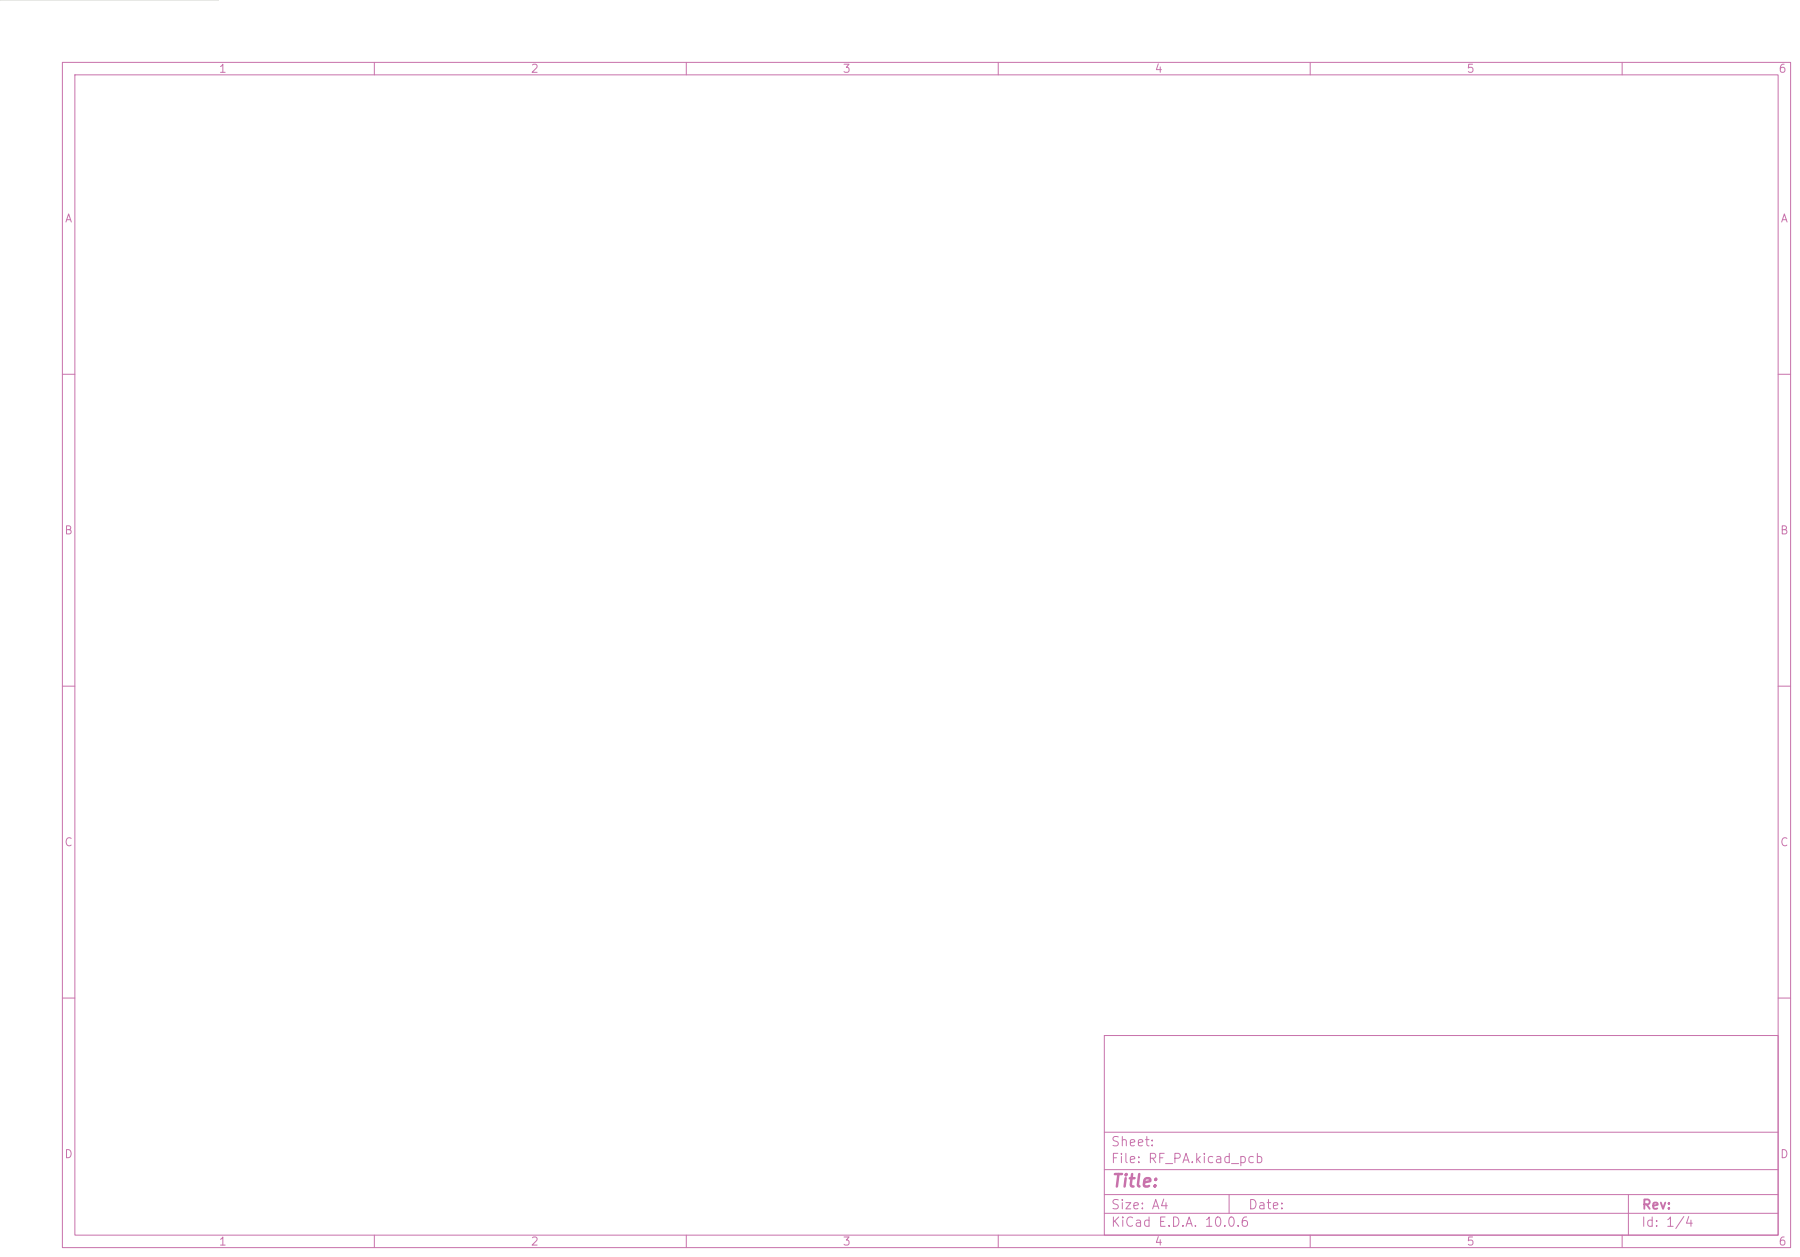
[picture p213: page 1]

Size: A4 | Rev:
KiCad E.D.A. 10.0.6 | Id: 1/4

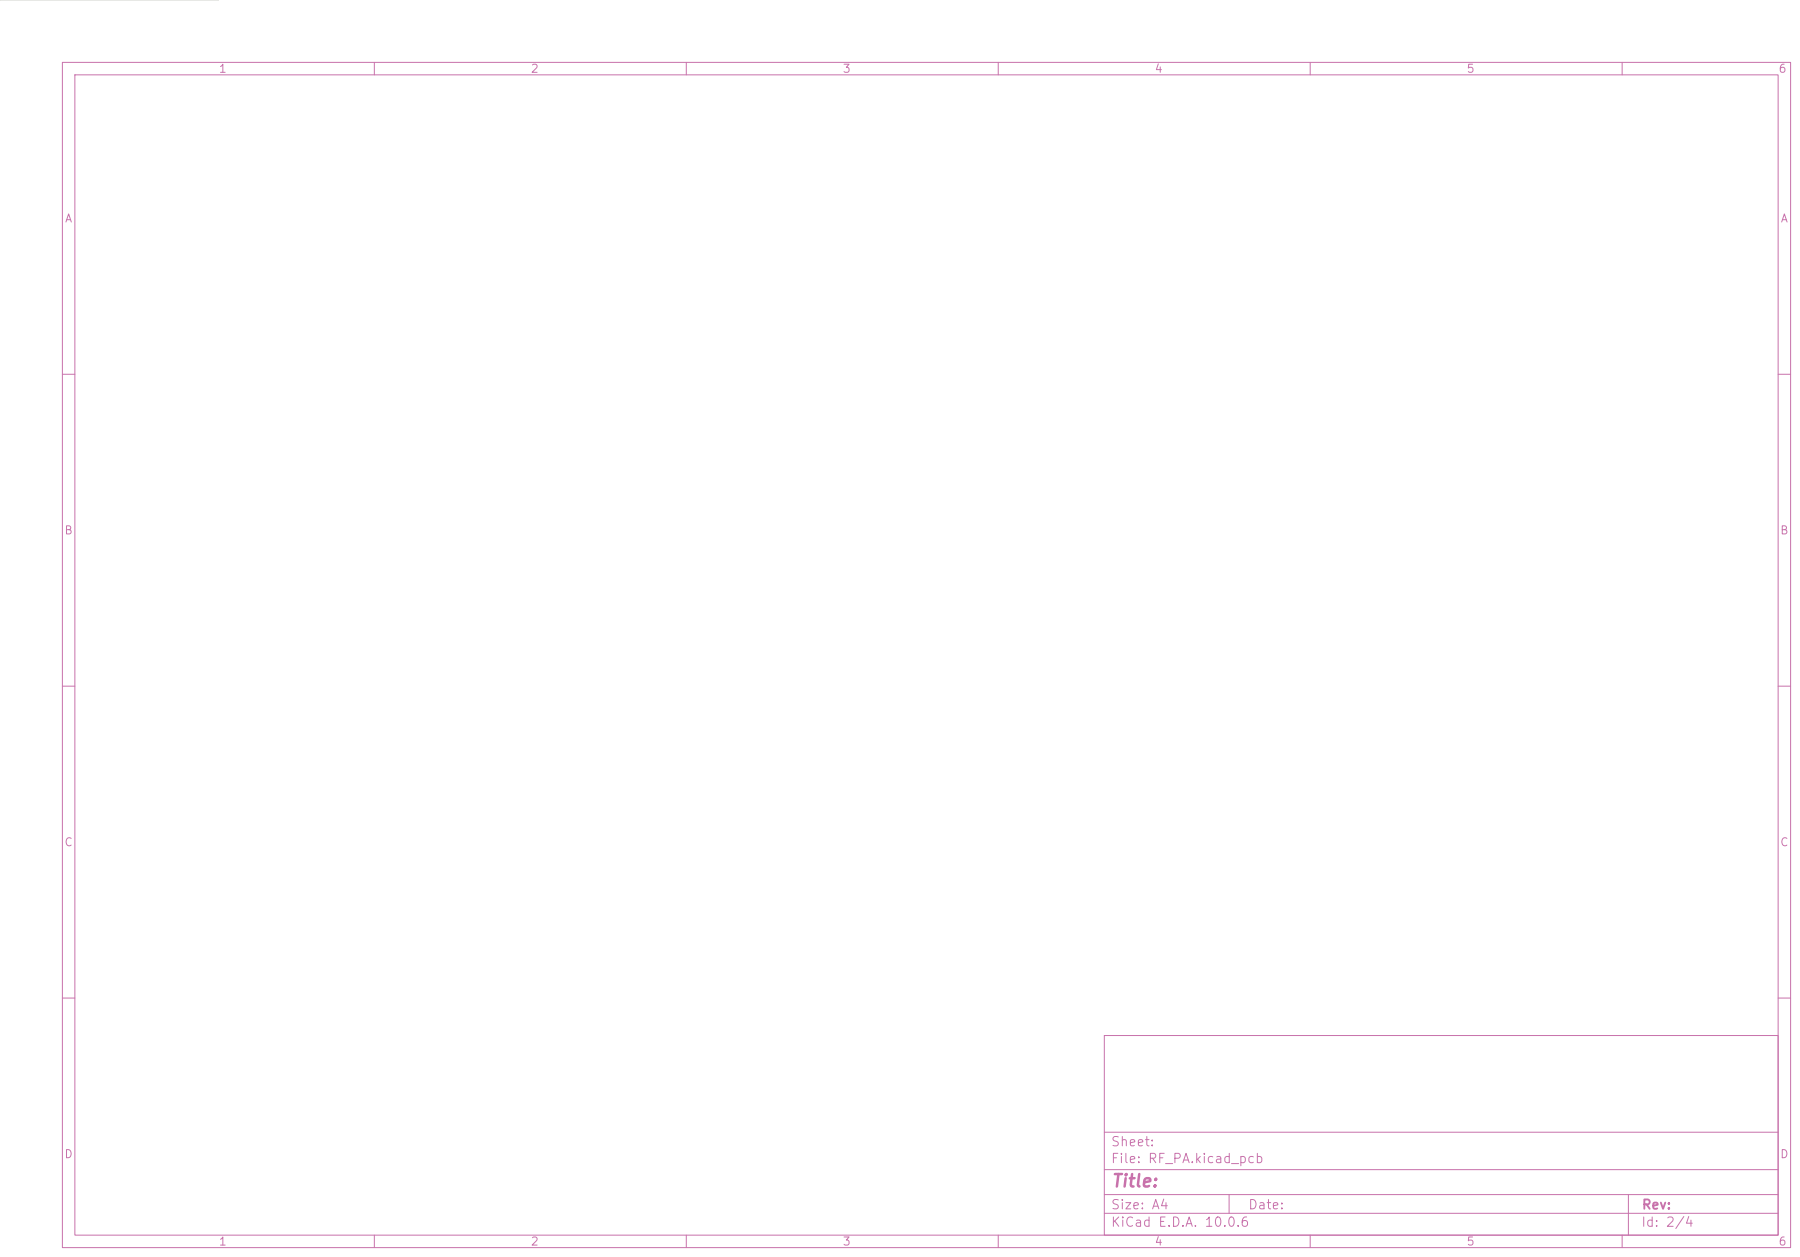
[picture p214: page 2]

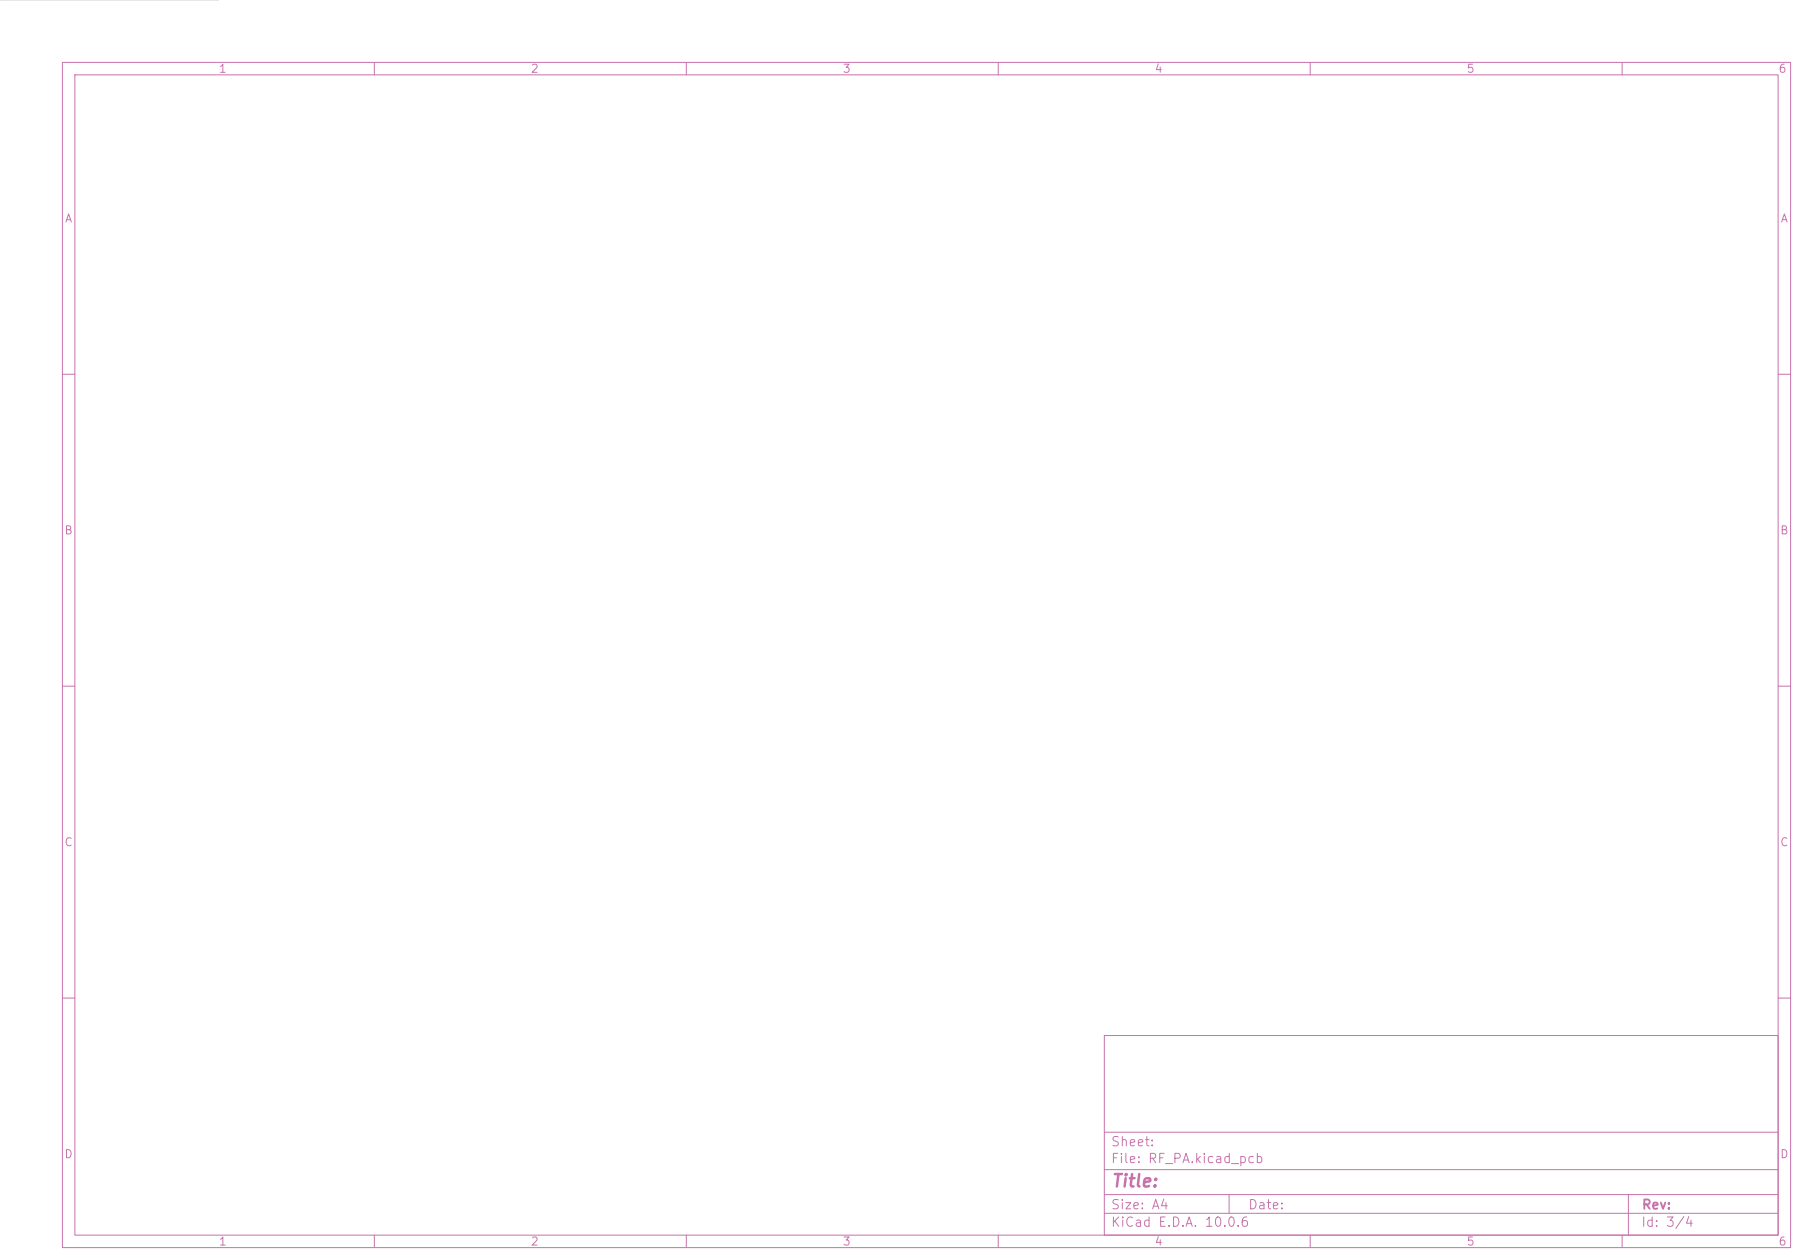
[picture p215: page 3]
