herasymyuks/PLFM_RADAR-aeris/beta/pcb/RF_PA/exports/drawings/RF_PA_top_layer.pdf

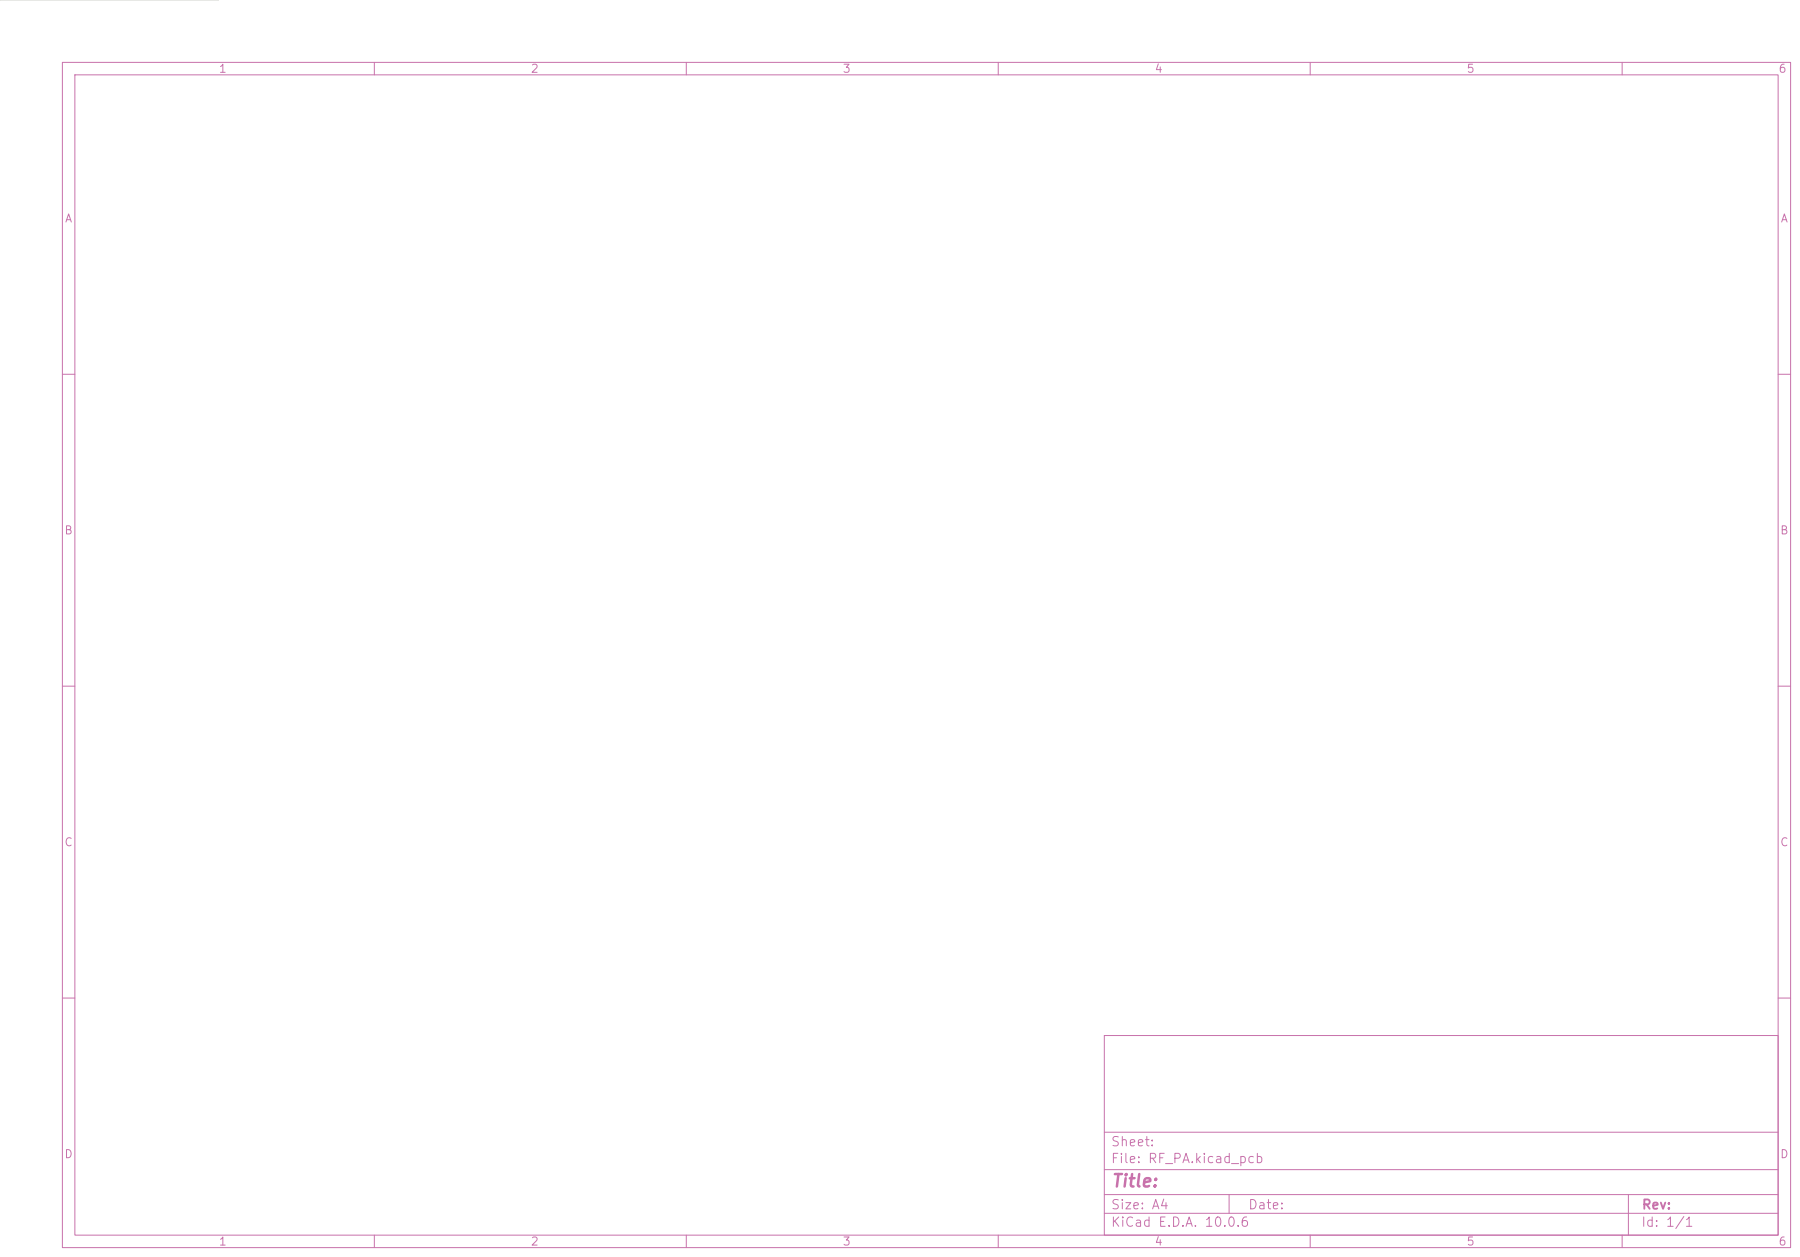
[picture p216: page 1]

Sheet: CURRENT SENSOR GND

Size: A4 | Rev:
KiCad E.D.A. 10.0.6 | Id: 1/1
