herasymyuks/PLFM_RADAR-aeris/engineering/ELECTRICAL/schematics/POWER_SUPPLY/POWER_SUPPLY_schematic.pdf

A

E

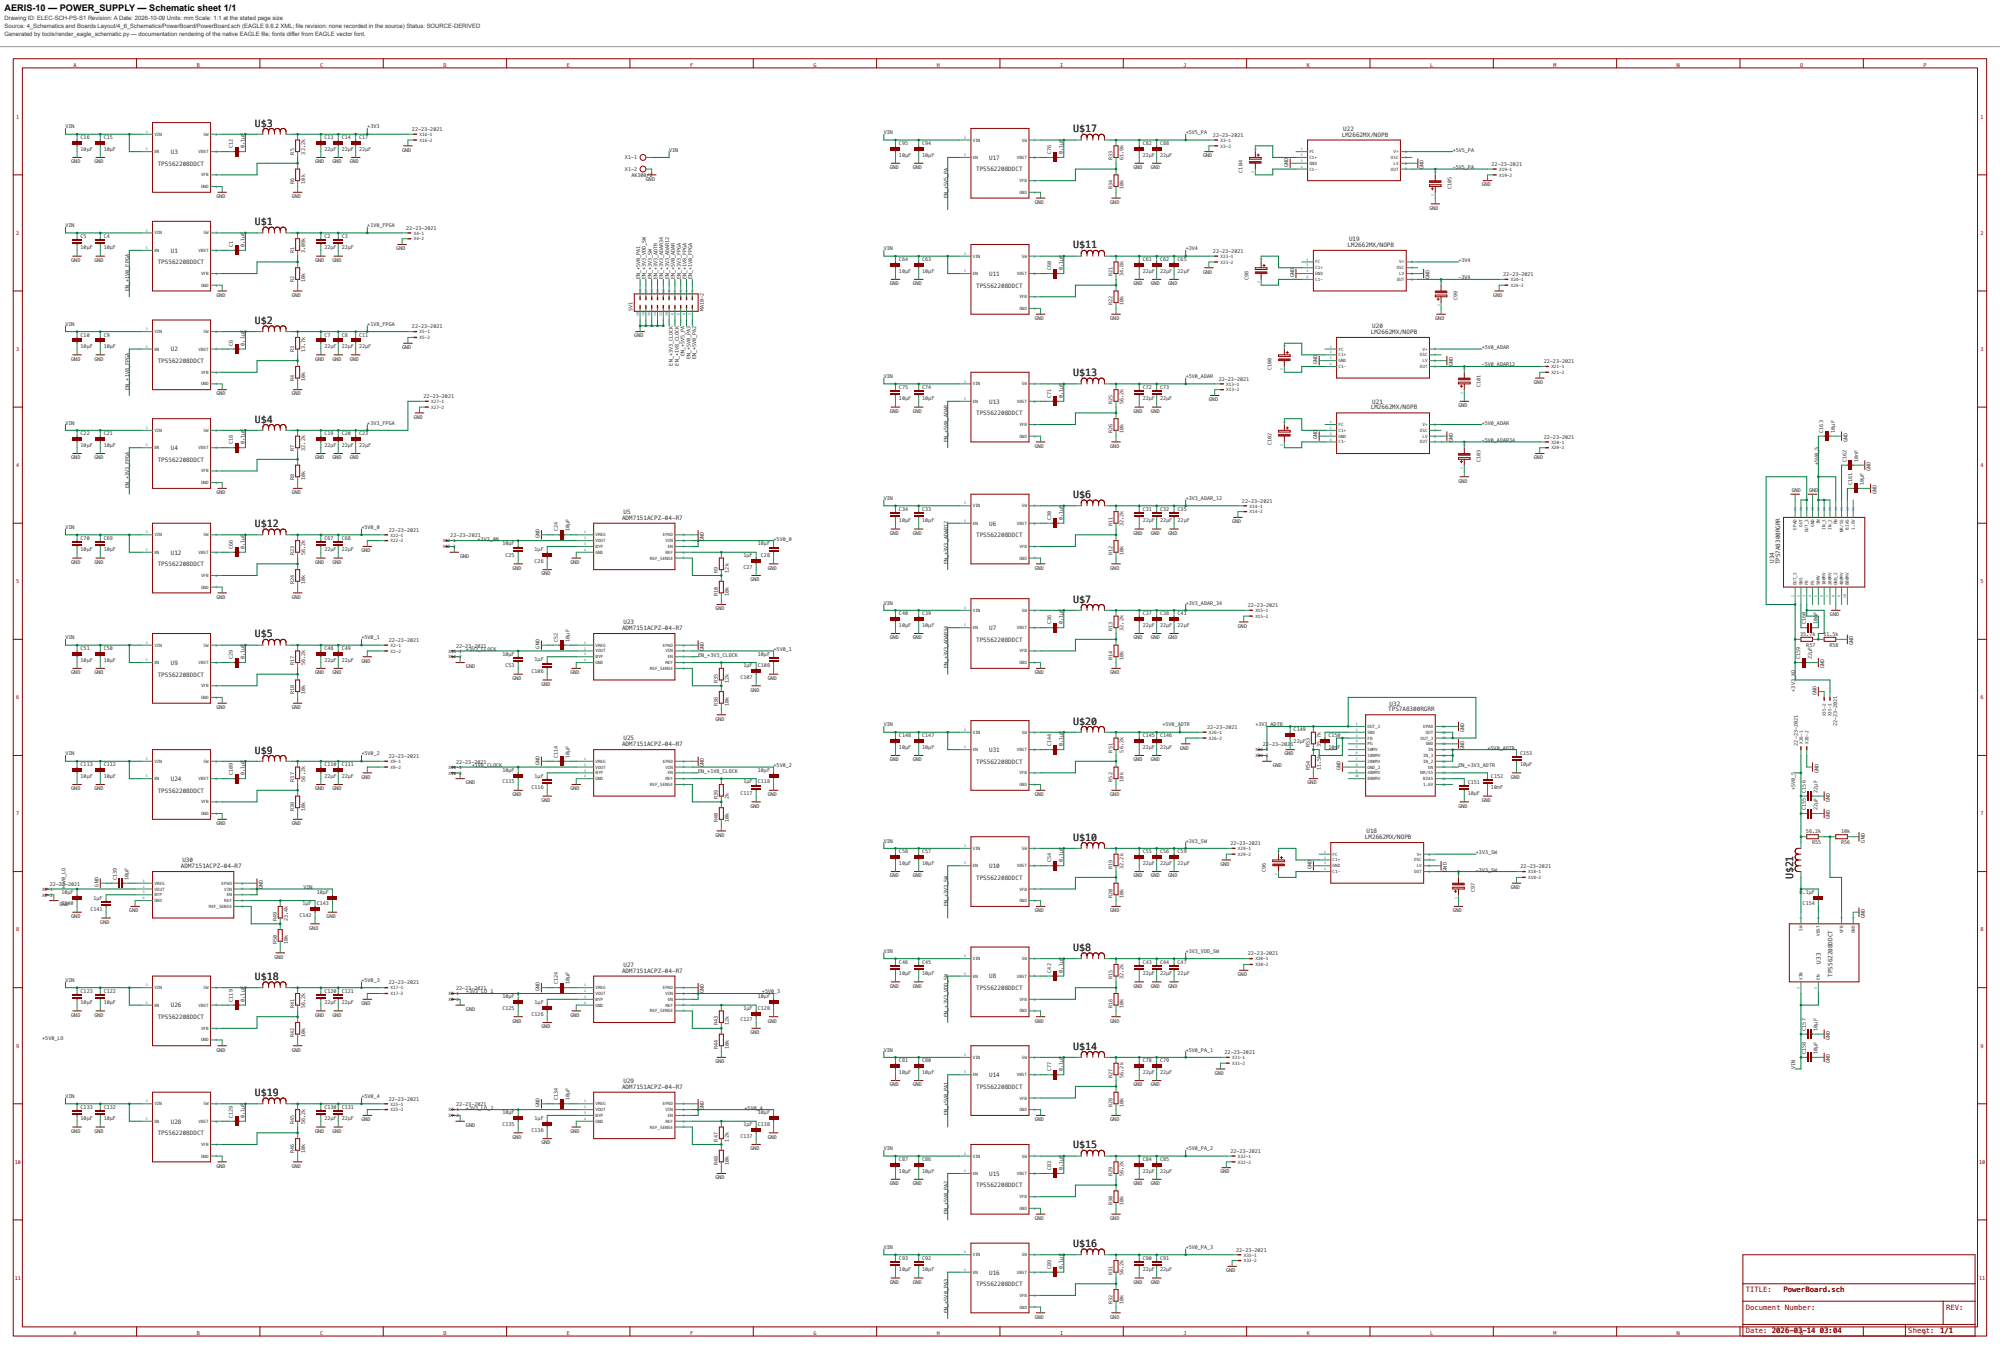
[picture p218: page 1]
