herasymyuks/PLFM_RADAR-aeris/manual/figures/FREQUENCY_SYNTHESIZER_layers.pdf

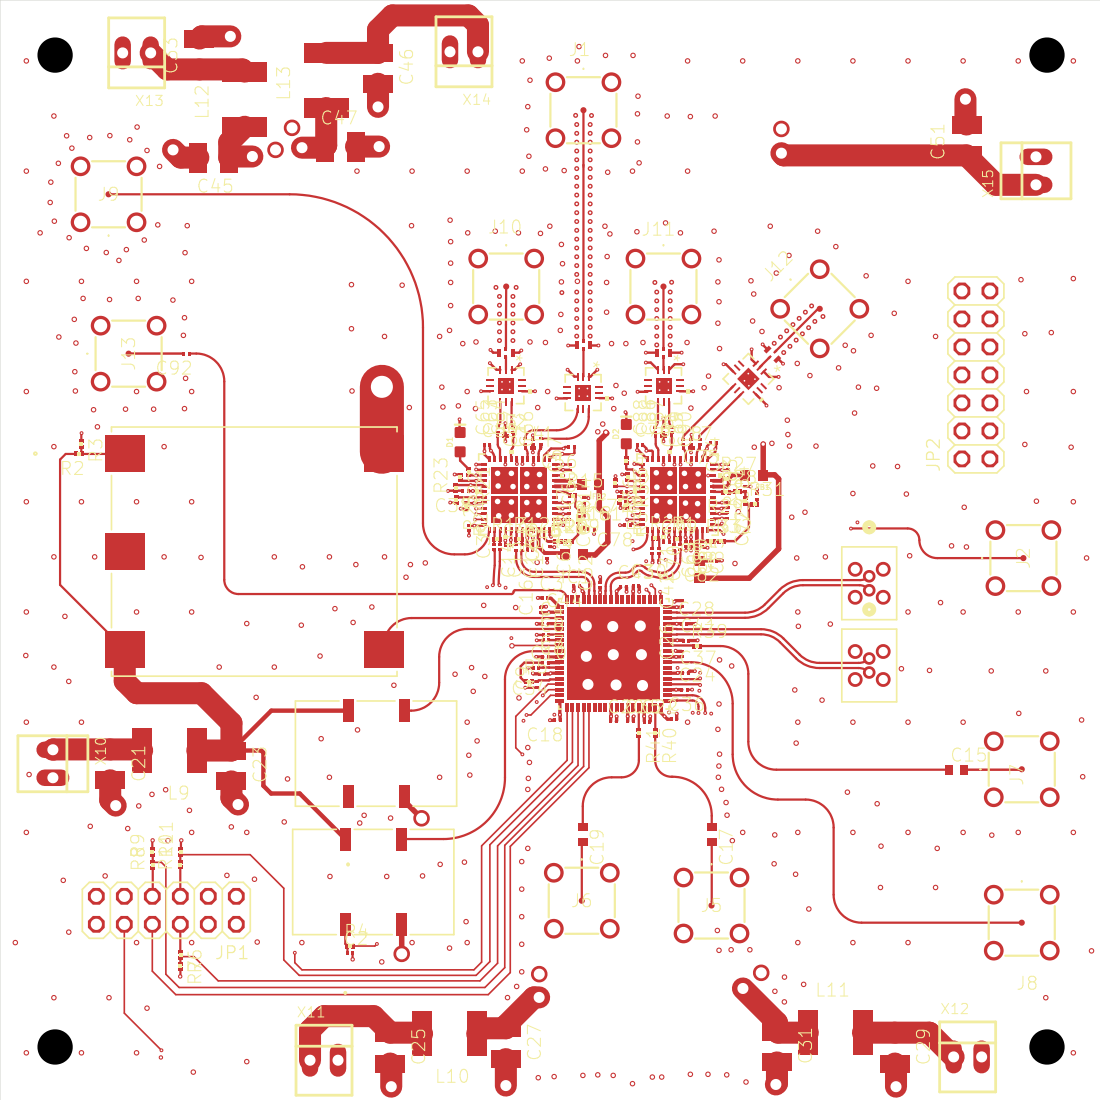
[picture p219: page 1]

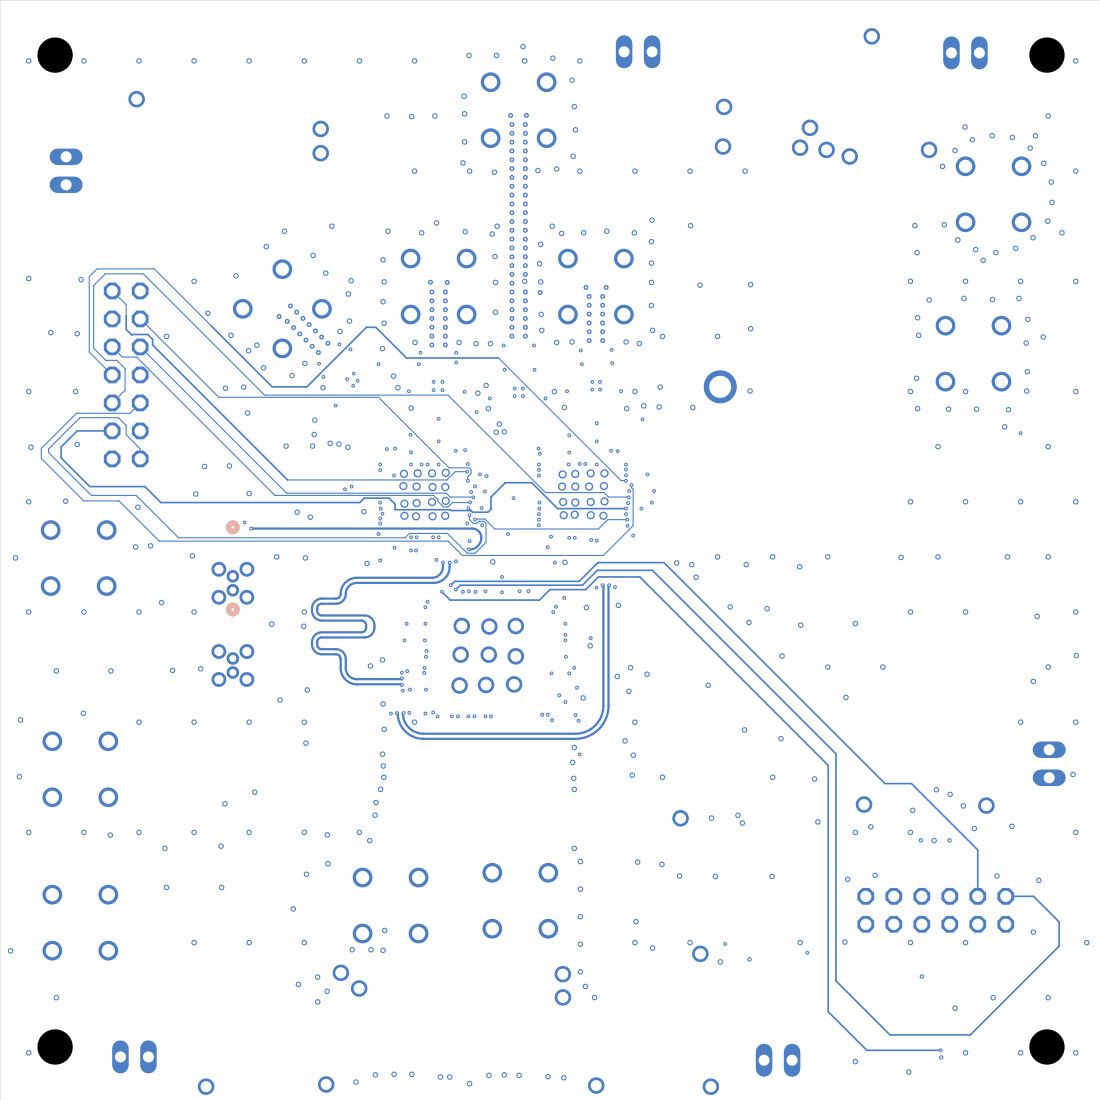
[picture p220: page 2]
