herasymyuks/PLFM_RADAR-aeris/manual/figures/MAIN_BOARD_layers.pdf

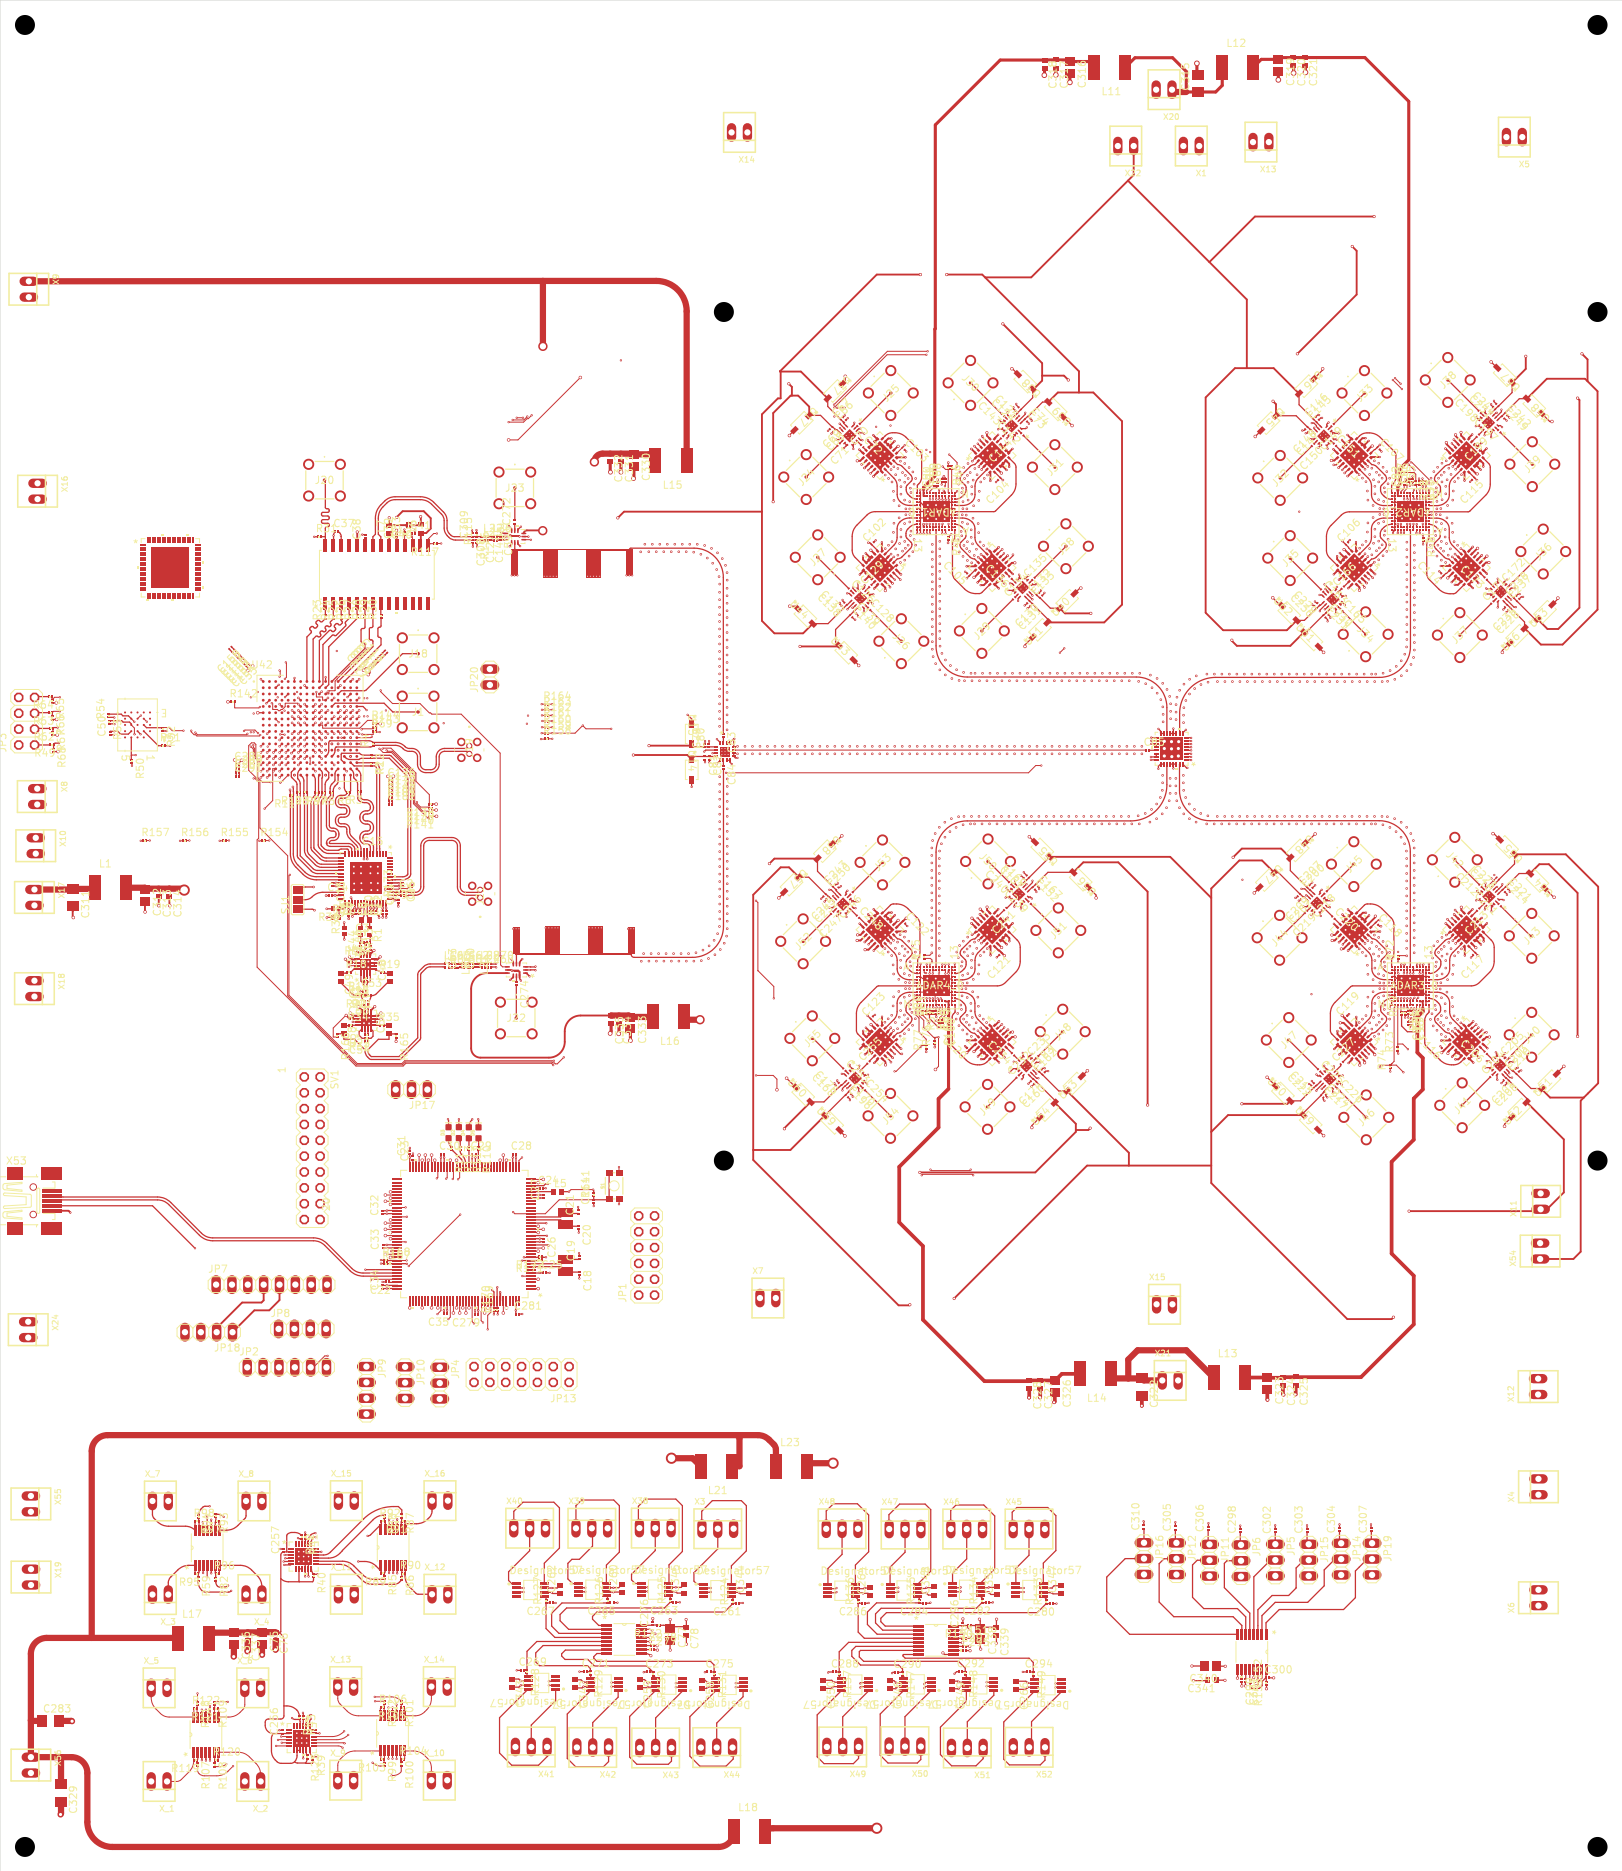
[picture p221: page 1]

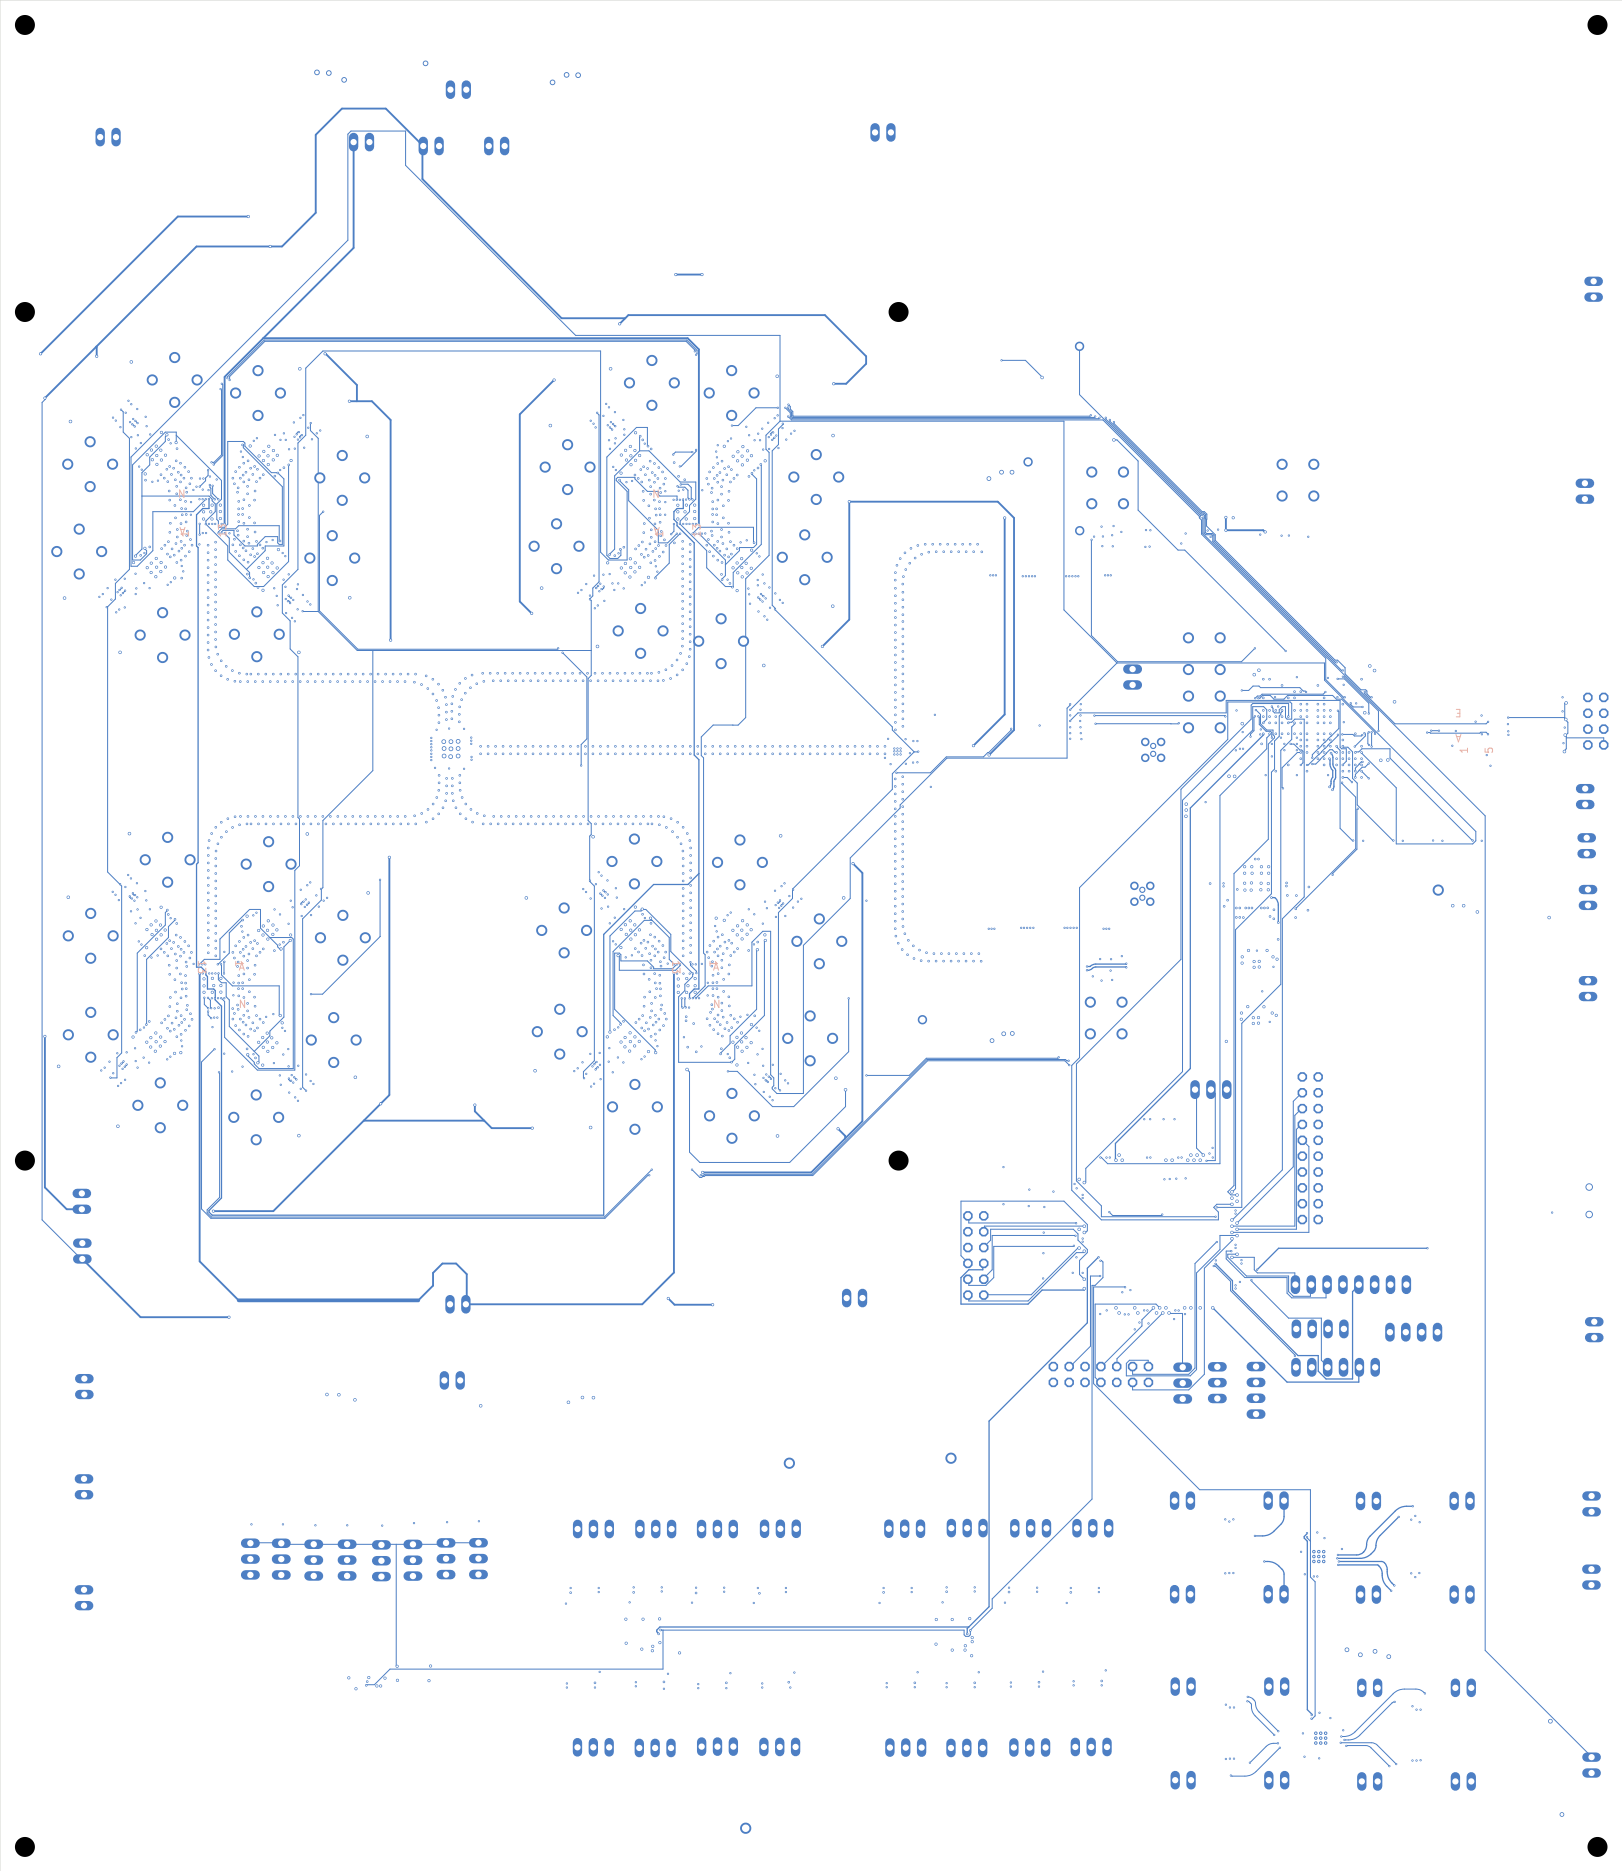
[picture p222: page 2]
