herasymyuks/PLFM_RADAR-aeris/manual/figures/POWER_SUPPLY_layers.pdf

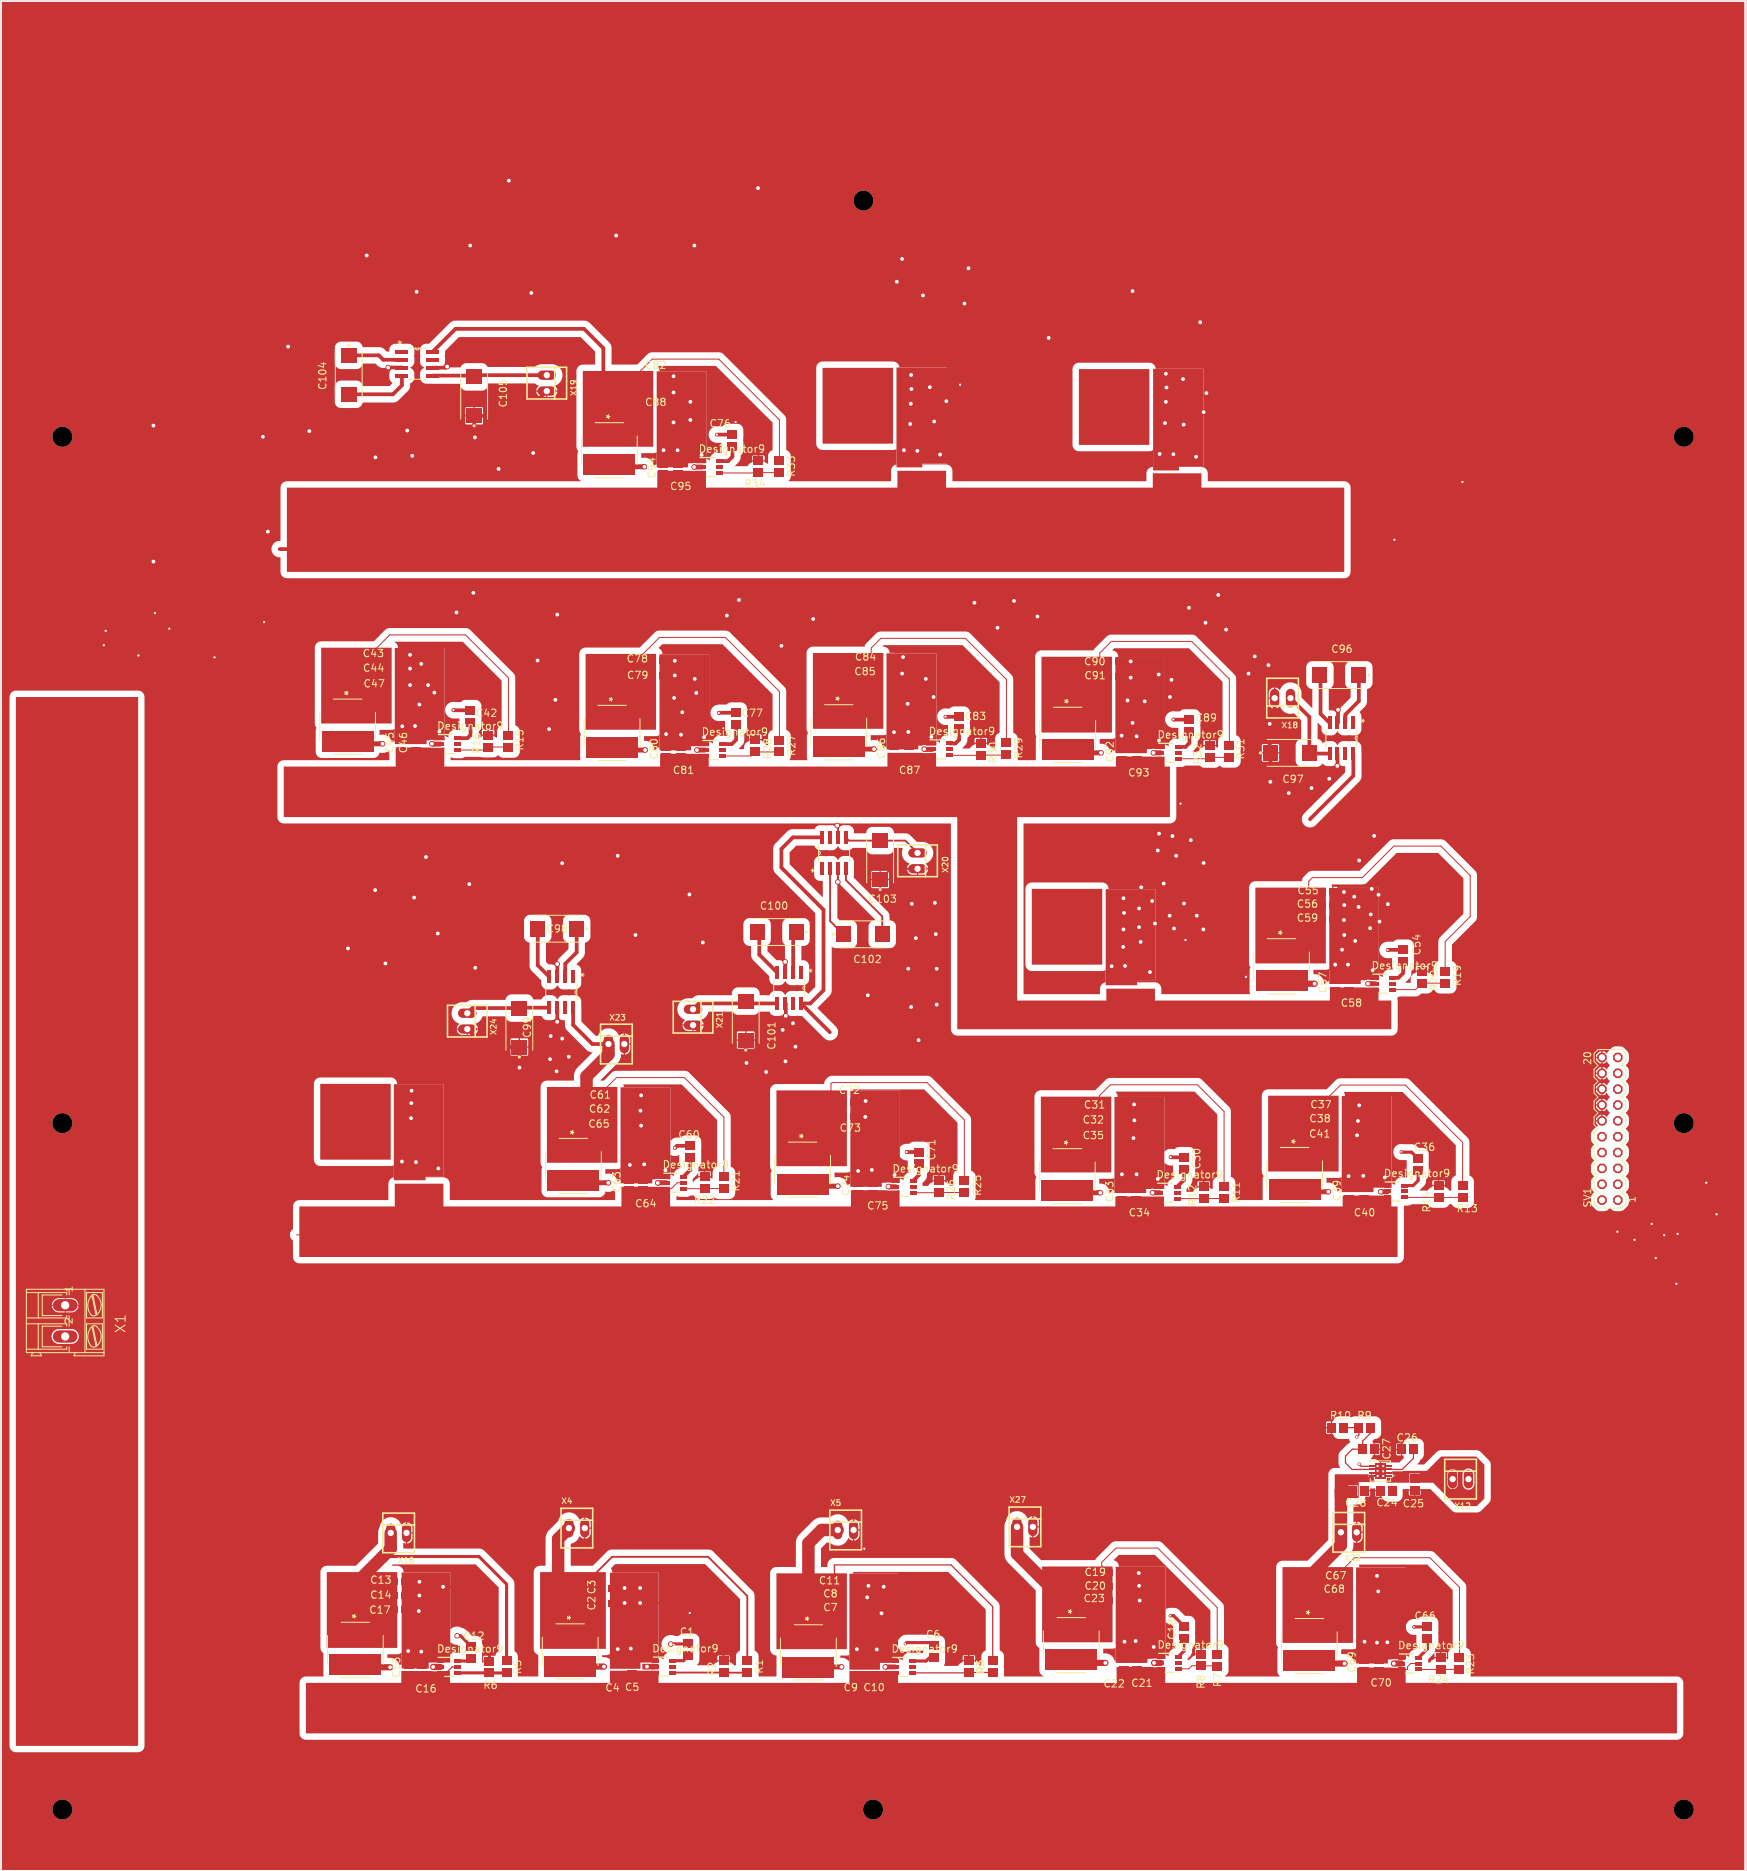
[picture p223: page 1]

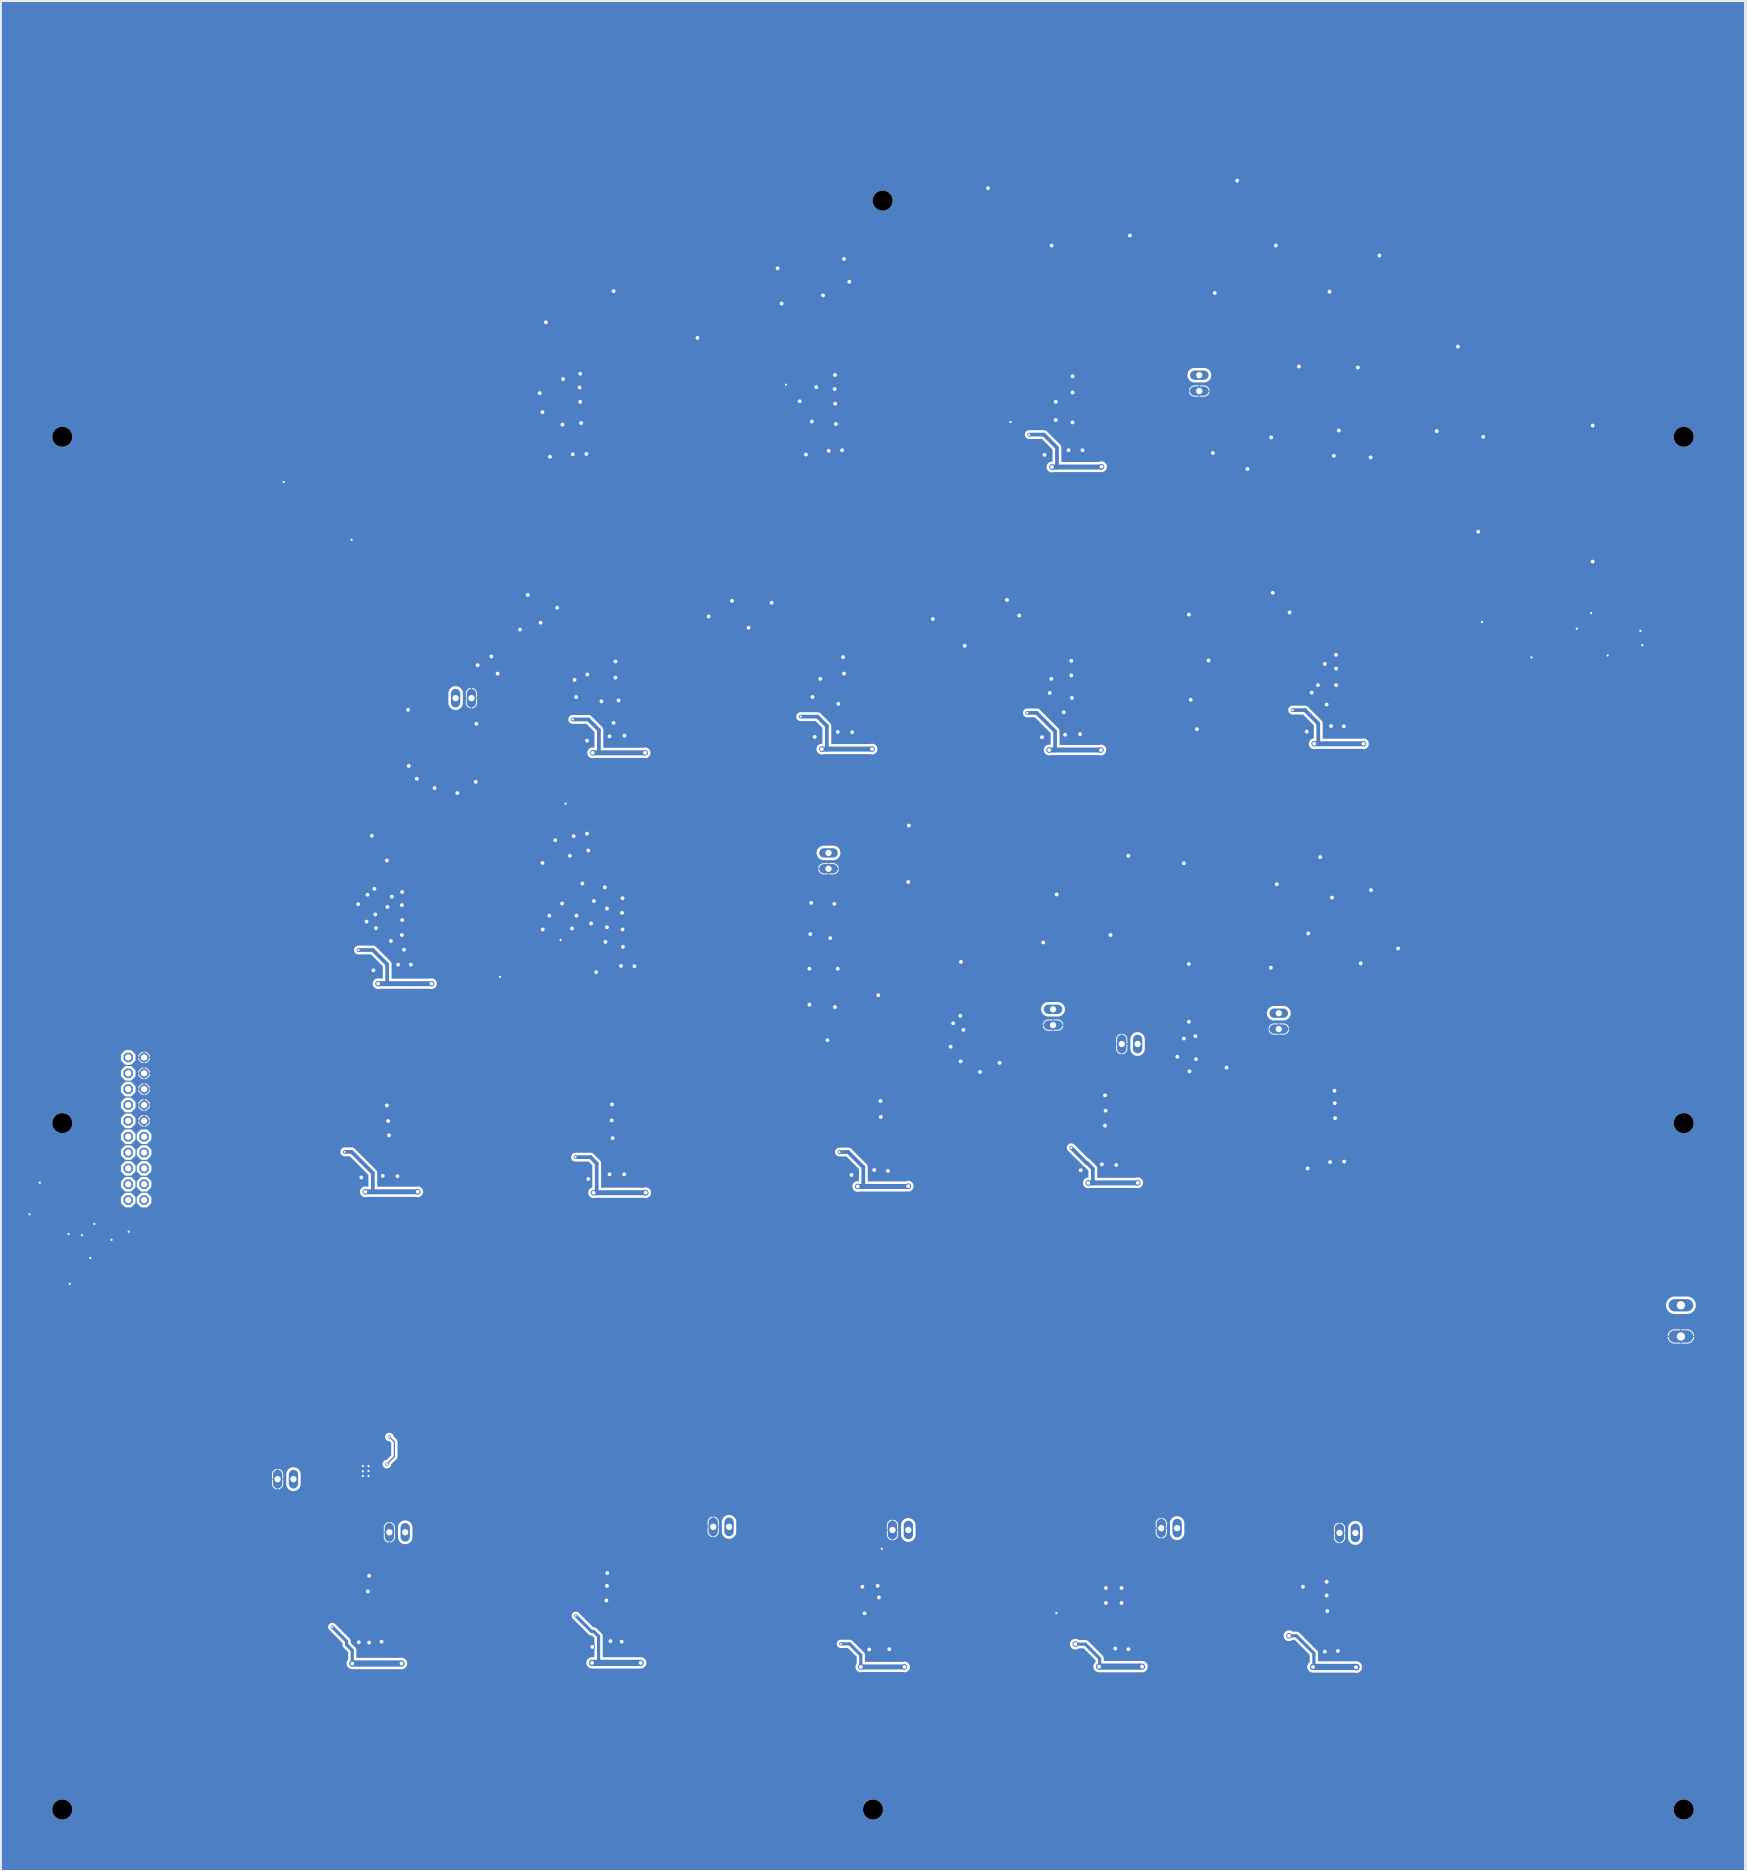
[picture p224: page 2]
