herasymyuks/PLFM_RADAR-aeris/beta/fpga/rtl/frequency_matched_filter.v

`timescale 1ns / 1ps

// frequency_matched_filter_conjugate.v
// BETA (beta/fpga/CHANGELOG.md): CONJUGATE_REF parameter added. The repository reference
// memories already hold conj(FFT(chirp)) (see gen_chirp_mem.py), so the chain must multiply
// by the stored value WITHOUT a second conjugation (CONJUGATE_REF = 0); the default 1 keeps the
// original behaviour for a memory that holds FFT(chirp).
module frequency_matched_filter #(
    parameter CONJUGATE_REF = 1
) (
    input wire clk,
    input wire reset_n,
    
    // Input from Forward FFT (16-bit Q15)
    input wire signed [15:0] fft_real_in,
    input wire signed [15:0] fft_imag_in,
    input wire fft_valid_in,
    
    // Reference Chirp (16-bit Q15) - assumed to be FFT of transmitted chirp

    input wire signed [15:0] ref_chirp_real,
    input wire signed [15:0] ref_chirp_imag,
    
    // Output (16-bit Q15) - FFT(input) ? conj(FFT(reference))
    output wire signed [15:0] filtered_real,
    output wire signed [15:0] filtered_imag,
    output wire filtered_valid,
    
    output wire [1:0] state
);

// Complex multiplication: (a + jb) ? (c - jd) = (ac + bd) + j(bc - ad)
// Note: We use CONJUGATE of reference for matched filter

// Pipeline registers
reg signed [15:0] a_reg, b_reg, c_reg, d_reg;
reg valid_p1;
reg signed [31:0] ac_reg, bd_reg, bc_reg, ad_reg;
reg valid_p2;
reg signed [31:0] real_sum, imag_sum;
reg valid_p3;
reg signed [15:0] real_out, imag_out;
reg valid_out;

// Address counter
reg [9:0] addr_counter;
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
